dataxcash/hw_ic_k2/docs/K2-BLOCKER-REPORT-aprime-a4-scope-20260929.md

# 卡点报告 · exam A⁴（原令范围）＝ **需「刚性簇平移」，非逐件推导** — #K2-397 §三

- 授权：#K2-397 §三（按原令真实范围重出 A⁴）；本窗**零 exam 跑**（重出＋实测；链跑留待 wiring 后）
- 件：`L2/EXAM_A_QUADRUPLE_PRIME_DERIVATION_v1.json` · 方案件 `…PLAN… :: exam_a4_scope`

## 一、试过什么

1. **逐件（per-part）下移推导**（新加确定性 `direction=(0,1)`；默认 `(1,1)`＝原 SE 不改）：
   `rearrange_probe(l14, rect4=[22.95,32.95,51.5,78.0], 25 成员, direction=(0,1))` ⇒ **22/25 有步**（皆 `(0, +0.5..4.0)`）；
   **U1／D2／U2 无合法步**。
   **为何**：逐件推导把 **U1 排第 1**（焊盘面积最大），此时**其余件都还没动** ⇒ U1 下移就撞进 **J9 一带**（铜/阻焊闸拒）⇒ **"整簇一起下移"永远出不来**。
   ⇒ **逐件族不是原令的真子集对应物**（#K2-397 §二）。
2. **刚性整簇平移**（同一位移给全部 25 成员）：`dy = 1.0 ／ 2.0 ／ 4.0 mm` 三次闸探针 ⇒ **NEW violations 全为 `{}`**，
   且**连基线原有的 `courtyards_overlap×2`／`pth_inside_courtyard×1`／全部 silk 类都被清掉**（移动后 raw classes = `{}`）。

## 二、缺口在哪层 / 结论

- **不是容量、不是判据、不是闸**：是**推导模型选错**——原令是**刚性簇平移**（≈ `block.move_block`／`relocate_block_chain`），
  而此前用的是**逐件独立推导**（`rearrange_probe`）。
- **A⁴ ＝ 刚性下移**：`Δ` 取**满足闸探针的最大刚性 dy**（受原令 y 带 / H1 禁区北缘 −2mm 约束）；实测 **4mm 已经 clean**。

## 三、下一步（一次有界）

1. 注册 **A⁴ 场景**（`rect4`＝x 带向下延长 ＋ 25 成员 ＋ 刚性图）并把链指向它（现链读 `L2/EXAM_A_PRIME_SCENARIO_v1.json`）；
2. wipe-resolve **全链一次跑**；判卷 **C1–C9 ＋ 几何摘要**（**C6 重述＝「新框外 diff=0」**）；
3. 若 **C1>0** ⇒ 有界证书 ＋ 偏离通道（工程层）。

> 说明：本窗**未跑**（wiring ＋ Δ 选定为剩余有界步骤）；**请裁**是否连同 wiring 一并批（一次有界窗）。
- 板面冻结 · 四源 4/4 · 判据表一毫米不改 · 禁 WORKER。
