dataxcash/hw_ic_k2/docs/K2-BLOCKER-REPORT-aprime-triple-prime-c1-7-20260929.md

# 卡点报告 · A‴ 末跑 = **C1 7**（18→7）· 停回方案层 — #K2-393 §四

- 授权：#K2-393 §四（**恰一次** `exam A --run --chain wipe_resolve`，N=1）
- 件：判卷 `L2/EDA_ENG_EXAM_A_TRIPLE_PRIME_ATTEMPT2_VERDICT_v1.json` · 记录 `…_ATTEMPT2_RECORD_v1.json` · 方案件 `L2/A_DOUBLE_PRIME_PLACEMENT_POUR_PLAN_v1.json`

## 一、判卷（九行齐 · 仍只差 C1）

| 行 | 读数 | 判 |
|---|---|---|
| C1 | **7** 未接（R1082 为 18） | ❌ |
| C2 | **133 vs 148** · **`new_classes = []`** | ✅ |
| C3／C4／C5 | 0.0788 ≤ 0.15 ／ 2989 ≥ 2637 ／ diff 1987 | ✅ |
| C6／C7／C8 | **0 ／ 0 ／ 0** | ✅ |
| C9 | 摘要已报 | ✅ |

`gate = PASS` · `run_count = 1/1` · 终板 DRC：`solder_mask_bridge = 0` · `isolated_copper = 0`。

## 二、人类口径三问

1. **信号怎么走**：器件挪位 → 清框内铜 → 框内重接 → 复敷铜 → 孤岛处置 → 板净准入 → 判九行。
2. **挡路的是什么**：**只剩 7 处端点接不上** —— **端点拥塞/无端口网**：端点格**因邻近异网铜被剪枝**（`snap=None`），`P3V3` **无框端口**。
3. **人类方案（下一次一次做 · 确定性 · 禁搜参）**：**端口可达性预检 ＋ 拥塞处确定性开端口**（给该网在框边预留一条干净通道到最近端口）；**无端口网（P3V3）** 属另一具名子案（须在框内另导）。

## 三、具名残余清单（7 · 交监理）

| # | 网 | 端点对 |
|---|---|---|
| 1 | NRST | `C73.1(F.Cu) ↔ U1.10(F.Cu)` |
| 2 | NRST | `track[F.Cu,0.1414] ↔ U1.10(F.Cu)` |
| 3 | PERSTA# | `track[F.Cu,1.9799] ↔ track[In5.Cu,0.2500]` |
| 4 | P3V3_AUX | `track[In2.Cu,0.2000] ↔ track[In5.Cu,0.0707]` |
| 5 | I2C1_SCL | `U1.47(F.Cu) ↔ track[F.Cu,0.8485]` |
| 6 | I2C1_SDA | `track[F.Cu,1.4142] ↔ track[F.Cu,0.1414]` |
| 7 | P3V3 | `C84.1(F.Cu) ↔ blind via F.Cu-In4.Cu [P3V3]` |

（末段路由账册 blocked 5 条：`no-free-goal-node` 3 · `no-free-start-node` 2；另 2 条为同岛 pad 级余项。）

## 四、缺口在哪层（承 §16）

- **已关**（本线已证）：**布局闸**（掩膜损害）· **孤岛处置**（具名 zone 去填充＋他区重铺）· **端口目标**（框切残段当目标）。
- **本层残余**：**端点拥塞／无端口网** —— 属**新一层**（异于上面三类）⇒ 按 #K2-393 §四 **FAIL ⇒ 停 ＋ 当件回方案层**；**禁同因重跑**。
- **已立缺口**（监理 §六）：**`C38`＝端点拥塞/无端口网的确定性补法**；本报告末尾给出 **edge iv** 确定性路径（端口可达性预检 ＋ 拥塞处确定性开端口 ＋ 无端口网子案），**待授权后实施（零考跑）**。

## 五、纪律 / 边界

- 本窗**链跑合计＝1**（恰一次 `1/1`）· `aprime_witness` 冻结维持 · **无新授权而跑＝违规**。
- 板面冻结（板只在 `/tmp`，终板 sha `eafdf07573367d79`）· 四源 4/4 · 判据表一毫米不改 · 禁 WORKER。
- 产物路径机器核（承 `M-ENG-EVIDENCE-PATH`）：件在 `k2/`；派生板显式 `/tmp` ＋ sha ＋ 重导配方。
- 仍待裁：`regen.exam_a_chain` 未定义名 `rp`/`blocked`（既有 · 未修 · 越窗）。
