dataxcash/hw_ic_k2/docs/K2-R922-BLOCKER-REPORT-v3-CONSOLIDATED-AND-RULE-COMPLIANT-WITNESS.md

# R922 ·《卡点报告》v3（**合并版 · 取代 R916 v1 / R920 v2**）· 附「可能免去豁免」的关键发现

日期 2026-09-28 · ENG(ARCHER) · **本回合零执行**（无链跑 · 无重出 · 无工具/参数改动）

## 〇、停止令遵办

- **已停**：本回合**无任何「改参数／改工具／改笼位 → 重跑」**；只写本报告并提交。本回合**未使用** `/tmp/opencode/k2h4`。
- **签名机制**：检测器签名 = **运行目录**（`RUN_SIG_RE=/tmp/opencode/(...)`）⇒ 该签名族**已由 #K2-354 §三.1 裁定「误报·作废」**；本席**按误报处理、照令停手**，并**只交一份合并版报告**（不重复贴 v1/v2，避免自身空转）。

## 一、① 信号怎么走（大白话）

> 右下角两条 PCIe 下行线（`PCIE_DN4_N`／`PCIE_DN5_P`）从**板中间的转接芯片**出发：**中层(In2)竖直下钻** → **底部通道带换 In5、沿板底横着往东跑约 48mm** → **在板右缘附近掉头** → **换回 In2 竖直上爬** → **落到 J2 那排焊盘（y≈59.5／60.3）**；一对两根靠**同伴线上的蛇形**补平长度。

## 二、② 挡路的是什么（大白话 · 两层）

> **第一层（几何）**：H4 安装孔周围 3mm 禁铜，而这两条线**掉头＋上爬的立柱正站在里面**（x=139.48/138.32，须 ≤137.6537）；**正西那条带子已被「上行线」占满**——J2 一排上下行交替，**上行立柱/过孔就插在下行立柱之间的每一格**（共用一张 **0.58mm** x 栅格）。
> **第二层（规则）**：图纸里有一条**在册的 L2 裁定（2026-09-10）**：**落同一排焊盘的立柱必须按通道顺序单向单调排**（当年为**防交叉**而升为准入约束）。
> ⇒ **不是「角上做不出来」，而是「在现有规矩＋现有栅格下做不出来」。**

## 三、③ 人类方案（大白话）—— **且有第三条路（可能免去豁免）**

> **A（改规矩 · 最小）**：**仅为 H4 这个角**申请豁免该单调规矩——**理由硬**：那条规矩**只为「不许交叉」**，而这组立柱**并不交叉**（立柱互相平行且间距 ≥0.55mm；车道互相平行且间距 ≥1.449mm；着陆段各在不同 y 带）。
>
> **B（改框架 · 最贵）**：承认这条带子排不下，**回去重排逃逸架构**（让这两条线根本不走右下角）。
>
> **C（不改规矩 · 本回合新发现 —— 建议先试这条）**：
> 既然**规矩是「按排焊盘族单调」**，那就**照规矩去找解**，而不是去破规矩。已量空闲段里**确实存在一组满足单调的候选**：
> **`DN4_N=135.50 · DN5_P=134.40 · DN6_N=133.00 · DN7_P=132.20`**
> —— 落 x=135.0 那排**严格递减**（`140.64>135.50>134.40>133.00>132.20` ✓）· 两两间距 ≥0.80 ✓ · 其中三根（135.50／134.40／133.00）**已在实测空闲段内**。
> **唯一未决**：`DN7_P=132.20` 落在**本席已量范围（x≥133.0）之外**——**那截条带是否空闲尚未量**（x<133.0 未查）。
> ⇒ **若那截是空的，则无需任何豁免**：照规矩出图即可。
> **本席不预判**：这是**假设 + 一个明确的待量点**，不是结论。

## 四、卡点三问

**试过什么（七法）**：① 6×6 切铜＋C17 → 未连接 3；② 放宽 9×9 → 6；③ 间隙感知挪孔 → 落异网铜皮；④ C22 精确铜皮多边形 → 4mm 内无净位；⑤ R914 **只解下行** → 撞上行（DRC 182 vs 168 · 6 新类含 3 短）；⑥ R918 **上下行联合重解** → 角清·不撞·长度闭合，但**破在册单调规矩** ⇒ 自证 FAIL ⇒ 依 #K2-354 §三.5 闸门①停手；⑦ **本回合（纸面 · 零执行）**：改按「照规矩」求单调解 ⇒ 得候选 C（上表）。

**为何不通**：①②③④ 局部手术（下游症状）；⑤ 漏耦合约束；⑥ 解开了耦合却**破了在册规矩**（本席无权松）；⑦ **差一个未量点**（132.2 处那截条带）。

**缺口在哪层**：**不在施工层**（施工层零自由度）。缺口 = **一次「照规矩的联合重解」**——其唯一未决是 `x∈[132.2,133.0]` 那截条带的占用情况（图纸层事实，非取舍题）。

## 五、请裁（建议顺序 C → A → B）

1. **C（建议先）**：批**新的一次有界窗**，用**规则合规**的候选 C 出图（`重出 → rev-62 → 链跑一次 → 判一次`）；**该窗自己的 DRC 即回答「那截条带空不空」**——空 ⇒ 收口；不空 ⇒ 再议 A/B。**不需要任何豁免。**
2. **A**：若 C 被否，则**仅为 H4 角落豁免该在册单调规矩**（本席已备见证与「不交叉」论证）。
3. **B**：若 A/C 皆否，则回到**框架层逃逸架构重排**。

**裁定前本席不做**：不重出 · 不跑链 · 不动板。

LEGAL-ESCALATION: none
OWNER-ITEMS: 0
