dataxcash/hw_ic_k2/docs/K2-R874-BLOCKER-REPORT-RUN-DRAWING-V3.md

# K2 · 《卡点报告》v3 —— H4 角「拐点前移＋竖升重布」出图（#K2-346 方案窗 · 一次实现后的如实汇报）

> **本件零运行**（一次实现已跑，结果为 FAIL；**按自设铁律停止、不重跑、不改工具再跑**）。

## 一、本轮一次实现（`/tmp/opencode/k347` · 1 次调用）

流水：**父进程镜像 → clip 子进程（pcbnew）→ route 子进程（布线器）→ 判（kicad-cli DRC）**。
**三处失败（后两处为级联）**：

| 号 | 位置 | 症状 |
|---|---|---|
| **F1** | clip 子进程 | `AttributeError: 'SwigPyObject' object has no attribute 'x'`（`t.GetPosition()`）—— `LoadBoard`/`GetTracks`/`GetClass` 皆成功，**逐项代理却是裸 SwigPyObject** |
| F2 | route 子进程 | `'NoneType' object has no attribute 'GetFootprints'` —— clip 崩了**没写出** clipped 板 ⇒ 布线器读到空 |
| F3 | 判 | `final_drc.json` 不存在 —— F2 级联 |

## 二、为何不通（诚实分级）

- **F2/F3 是纯级联**：**对几何零信息**（不能据此说任何「几何不通」）。
- **F1 未定因**：同一环境、几分钟前别的工具能正常读同一块板；此处**在全新子进程、未做任何改板、未导入布线器**的情况下，**逐项代理已是裸对象**。本席**没有**再跑实验去分辨是 (a) 调用顺序/环境 (b) 板文件某个特性 (c) 环境回归 —— **因停止令，不做**。
  ⇒ **R870 把根因归给「同进程导入布线器」是不充分的**（本件无布线器导入也复现）。

## 三、缺口在哪层

| 层 | 判定 |
|---|---|
| 几何层 | **本轮无结论**（F1 不是几何结果） |
| 方案层 | **本轮无结论**（「拐点移到 x=137.555 ＋ 竖升重布」既未证成也未证伪） |
| **工具层（真缺口）** | **本工具链用 pcbnew 的「对象 API」改板，在该环境下脆弱**。而**在册布线器本身不用它改板** —— 它是**把改动写成文本块插进已存文件**。⇒ **改板路径应当文本化**。 |
| 纪律层 | **已遵办**：一次实现 → 停 → 报（无扫参、无同目录第二跑） |

## 四、下一步（**单一新方法** · 事后仅一次跑）

**clip 相改为「文本级」**（彻底把 pcbnew 对象 API 移出改板路径）：
1. 解析板的 s-expression **文本**，定位：被困孔块（x≥137.93 且 y≥73.93）· 其挂接的 **B.Cu 横段块** · 其挂接的 **In5 竖段块**；
2. 把横段的 `(end ...)` 改写到 **x=137.555**；**删除**孔块与竖段块（纯文本）；
3. 随后**布线器（独立进程 · 不改其文件）**桥接两个开口；**DRC 判一次**。
**为何算「不同方法族」**：把 pcbnew 对象 API 从改板路径**整个移除**（与在册布线器出铜的同一手法）。
**前置**：文本解析器先在**副本**上做单元自检（**不触仓内板**），之后**仅一次**跑。

**红线不变**：一轮一目录 · 禁扫参 · FAIL 即回修不呈 · 冻结四源 4/4 · 禁 WORKER · Gerber/下单停线。

OWNER-ITEMS: 0
