dataxcash/hw_ic_k2/docs/K2-R866-BLOCKER-REPORT-H4-CORNER-AND-PLAN.md

# K2 · 《卡点报告》＋ Plan —— H4 右下角安装孔（#K2-345 W2 的第一个真卡点）

> 停止令遵办：**连续错误 3 次**（`poly_hit` arity TypeError ×2 次同因未先诊断 · 前窗 README 声称失实 1 次）⇒ 本席**自我登记、不申辩**；**停止『改参/改工具 → 重跑』**（宪法第八章第 8 条），回 Plan，一次实现。
> 本件为**只读分析件**（零运行 · 零改板）。

## 一、《卡点报告》

### 1. 试过什么（H4 右下角落角 · 四法 ＋ 两次工具错）

| # | 手法 | 机核读数 | 结果 |
|---|---|---|---|
| A | 6×6 角禁区切铜 ＋ C17 v1 重布 | 未连接 **3** · dangling +2/+2 | ✗ |
| B | 加宽 9×9 走廊 ＋ C17 v1 | 未连接 **6**（更差） | ✗ |
| C | 间隙感知挪孔（挂接段过闸 · 0.30 判据 · 4.0 mm × 8 向） | **未连接 0** ✓ 但 间隙 +1／短路 +3／走线交叉 +1 | ✗ |
| D | 同 C ＋ 铜皮入模（bbox） | 两孔皆「4.0 mm 内无净位」 | 穷尽（近似） |
| E | 同 C ＋ **C22 精确铜皮多边形** | 两孔皆「4.0 mm 内无净位」 | **穷尽（精确）** |
| 工具错① | `k2_shift_vias_out_of_keepout_v1.py` 替换静默未命中（同族前科：README 声称失实） | 声称 vs 工件不符 | 已装 post-write 重读闸 |
| 工具错② | `poly_hit()` 调用 arity 错（`x2` 缺省） | TypeError | 已修（**未先读栈即重跑**＝本次连错主因） |

### 2. 为何不通（三法各自的死因）

- **A/B（撕铜重布族）**：两条 `PCIE_DN4_N`/`PCIE_DN5_P` 是 **~48 mm 的整段内层（In5）跑线**，其**末端换层孔**就在角上。沿禁区撕开 ⇒ 剩下的 **48 mm 残段变成孤立长桩**，而「补回」的目标（表层焊盘侧）远在禁区另一侧 ⇒ 布线器只能对**整根长桩**作业，于是乱走（未连接 3→6）。
- **C（局部挪孔族）**：**挪孔必然带动挂接段旋转**。该角的内层**满铺异网铜皮**，任一转角后的段/孔都落在铜皮上 ⇒ 间隙/短路/交叉。挂接段已过闸也救不了（铜皮当时不在模型内）。
- **D/E（把铜皮纳入模型）**：一旦要求「孔与段都不碰任何异网铜皮」，**4.0 mm 包络内无净位**（精确模型亦同）⇒ 局部推挤族**穷尽**。

### 3. 缺口在哪层

| 层 | 判定 |
|---|---|
| **几何层** | **不是无解** —— 有解（下面 Plan 给出） |
| **方案层（真缺口）** | **该角的『腾让』从未在方案层被规划**：扇出把 4 条 DN 跑线 ＋ 换层孔排到右下角时，**没有把「四角安装孔 6×6 禁区」当作布局约束**（与 M-ENG-PLACEMENT-GATE-MISSING 同族：放置源未预留机械角禁区）。所以现在是**用施工层手段去补方案层的欠账**。 |
| **工具层（次缺口）** | 现有重布族是**缺口缝合器**（gap stitcher），**不会重规划整段跑线**（whole-run re-plan）⇒ 一旦切割面把整段切坏就无力。 |
| **纪律层** | 本席**未先读栈即重跑**（工具错②）＝ 本次连错主因 ⇒ 遵办：**先诊断，再动手**。 |

## 二、Plan（人类工程师路径 · 大白话）

### ① 信号怎么走
`U6（重驱芯片）出球 → 芯片扇出（逃逸）→ 下到内层 In5 → 一根 ~48mm 的长跑线一路向右下 → 在右下角用一个换层孔上到表层（F.Cu）→ 接到连接器焊盘`。**两条线（DN4_N / DN5_P）都这样走，且**「换层孔」**恰好落在右下角。**

### ② 挡路的是什么
**右下角不是空地**：那两根长跑线的**换层孔 + 一小段表层线**就住在角上，角的内层还**满铺着别的网的铜皮**（电源/地）。所以：
- 「把孔往旁边挪一点」= 孔一动，接它的线段跟着转，**转到铜皮上就短路**；
- 「把线剪掉重接」= 剪的是**48mm 长跑线**的末端，剩下的残段太远，接不回来。

### ③ 人类方案是什么（大白话）
**不要在角上硬挪这两个孔——把「换层的位置」提前。**
就是：**在长跑线还没进角之前（离角 3~5mm 的直段上）找一个干净点，在那里换层上表层，然后只把短短一段表层线（≤10mm）接到焊盘。** 这样：
- **内层长跑线几乎不动**（只把尾端缩短几毫米，直线，不转弯）；
- **要新画的是短短一截表层线**（短 ⇒ 绕得开铜皮 ⇒ 布线器做得动）；
- 角上彻底清空 ⇒ 安装孔＋6×6 禁区可以精确落角。

**这属于「改换层位置」而不是「挪孔」**——这正是施工层做不动、必须在**方案层改一个参数（换层 x 坐标）**的那种改动。

## 三、一次实现（下一窗 · 单一有界动作 · 禁参数扫）

**实现「跑线尾部重规划（run-tail re-plan）」**（新工具 `k2_reroute_run_tail_v1.py`，**一次执行**）：

1. 对 `PCIE_DN4_N` / `PCIE_DN5_P`：在**其 In5 直段上**（x ∈ [130,136]，禁区外）扫**一个**换层孔位——判据与 C22 同（精确铜皮多边形 ＋ 0.20 净距地板 ＋ 挂接段一并过闸）；
2. 找到后：**只把该点之后的 In5 尾段剪掉**（缩短，不转弯）＋ 把旧孔删除；
3. 用迷宫布线器（精确闸）**只重布那截表层尾线**（目标 = 原焊盘），**≤10 mm**；
4. 复核：DRC ≤168 新增 0 · unconnected 0 · 该两对的对内等长重算（DN 对不属于 8 对 UP_OUT，须另表登记）。

**若步骤 1 仍无净位** ⇒ 按 #K2-343 §三，**再补第二个方法族**（来源端改层/改走廊）＋ **监理独立复算**，方可入「不可行」；**否则只用「法族穷尽」措辞、不进不可行声明**。

**红线**：一次执行；禁扫参；FAIL 即回修不呈；冻结四源 4/4；禁 WORKER；Gerber/下单停线。

OWNER-ITEMS: 0
