dataxcash/hw_ic_k2/docs/K2-R594-GROUPING-GEOMETRISATION-SPEC-G1-G3.md

# K2 · R594（#K2-230 v5 续）—— **分组几何化规则（G1–G3）**：可执行规格（下一窗一次出图）

- 依据：#K2-230（v5 成品式直出）· R593 实测（2/16 通；第 3 线被他线 **2 个过孔格**阻断 ⇒ **须几何化分组**）
- 本件：**规格件**（零构造运行）；下一窗按此**一次描线**。

## G1 尾段专属列窗（互不重叠）
为 16 线指定**互不重叠**的尾段纵取列窗：西组 `[96..113]` 内**逐线一段**（每线 ≥2 列宽，用于"下不去就分段"的阶梯）；东组墙东 `[115..137]` 内**逐线一段**（F3 机核 16 列可用）⇒ **跨线列窗不相交**（构造式，非试参）。

## G2 过孔列集（构造式分离 ≥ VIA_SEP）
每线的过孔**只允许落在其 G1 列窗内**；**相邻线的列窗间距 ≥ 3 格**（3×0.435 ≈ 1.30mm ≥ `VIA_SEP` 0.7mm）⇒ **跨线过孔自动满足净距**（构造式，非试参）。
`col60` 注册换层点仍按在册槽位（其行 `H` 逐线不同 ⇒ 同行不冲突）。

## G3 落 B 端子腿（专属近端子段）
每线的 **B 端子腿**只在其 **G1 列窗**内接近（禁穿越他线列窗）⇒ 消除 R593 的"他线过孔格阻断 B 腿"。

## 验收（下一窗）
`按 G1–G3 出"专属通道表" → 一次描线 → exact_gate（真净距）/gate_vias/端点/≤2 对孔 → 入库报 hash ＋ buildability ＋ 每线"抄自成品何处"对照列`。

## 边界
冻结四源 4/4 MATCH · 在册件/判据/生成器/SPEC/原理图一字未动 · 未派 WORKER · 两仓已提交 · 树净；**P4 未归零 ⇒ 不导 Gerber/不进 P5/不碰下单**。 OWNER-ITEMS: 0

—— ENG（ARCHER）· 承 #K2-230
