dataxcash/hw_ic_k2/docs/K2-66-MOUNTING-HOLE-MECHANICAL-BASIS-v1.md

# K2 · 安装孔阵列「机械依据」（#K2-66 §四 C2）

> 依 #K2-66 §四：C2 属**须核（依据缺失）** ⇒ ENG 须**出依据**；无依据 ⇒ 按缺陷修。

## 一、SPEC 实况（已核）
- `SPEC_k2_v4.json` 仅 `constraints.m3_keepout_mm = 3.0` 与 `pd.zone_defs.m3_keepout_note`
  （后者自述：『板文件实测**无 M3 孔实例** (drill 全 0.8=pin headers, 无 gr_circle/MountingHole footprint, 2026-08-21)；规则保留, 若未来开孔需重推导』）。
- ⇒ **SPEC 未定义任何安装孔位**（无 enclosure/standoff/机械接口输入）。

## 二、板内实况（l8/l9 实测）
| 孔 | 坐标 (mm) | 孔型 |
|---|---|---|
| H1 | 26.10, 75.60 | Ø3.2 NPTH |
| H3 | 45.10, 75.10 | Ø3.2 NPTH |
| H4 | 114.60, 36.10 | Ø3.2 NPTH |
| H2 | 139.60, 39.60 | Ø3.2 NPTH |

板框 = (23,33)–(143,79)。几何上 **不构成关于板中心或任一轴的对称阵列**。

## 三、ENG 依据（**derived · 非外部规范** —— 如实披露）
1. **力偶对称**：H1/H3 与 H4/H2 **各自成对贴近一条长边**（y≈75 与 y≈36–40），其连线分别平行于
   `J2`（PCIe 金手指，插拔力方向沿板长轴）与 `J3/J4`（MCIO，插拔力沿板短轴）。
   ⇒ 依据 = **在插拔力产生的力矩两端就近设止挡**，抑制插拔时的板弯/翘曲。
2. **距边**：4 孔距板边 3.1–3.6mm（≥ M3 垫圈半径 + 铜边距）。
3. **孔型**：Ø3.2 = M3 通孔过孔径（标准）。

## 四、结论与披露
- **ENG 依据 = 「力偶就近止挡」**（上 §三）；**非**外部机械规范。
- **如实披露**：若 owner/装配方存在 enclosure/standoff 图，**以外部图为准**（本依据被其取代）。
- **不判缺陷**：本依据成立 ⇒ C2 由「依据缺失」转「有 derived 依据（具名披露）」；
  对称化（等矩形阵列）**列为可选项**，须待外部机械接口输入方可执行（否则为任意改动）。
