dataxcash/hw_ic_k2/pm_gate/artifacts/k2_v4/L2/K2_CONSERVATION_BLOCKER_REPORT_RESIDUAL_STARTGOAL_v1.md

# 《守恒级卡点报告》· 残差＝起步/落脚格 · 收敛停滞应答 · v1

## 〇、二值（本件之必须）

- **可行见证 ＝ 有（起步段 · 机证）**：`R1522`/`R1530` 预检机证 —— `U1.22`/`U1.48` **各有一条 0.8mm、`clear=0.30` 全净空**的沿长轴出线走廊；`R1532` 在**终板**上复核该走廊**为空**。
- **守恒级不可行证书 ＝ 无（本席拒绝伪造）**：证据指向相反 —— **该焊盘并不缺资源**，**起步段合法且自由**。
- ⇒ **二值 ＝ 「不可行不成立」**：残差是**迷宫自身起步/落脚规则的失效**（`R1534`：`I2C2_SCL: no-free-start-node` · `PWR_BTN_OUT: no-free-goal-node`），成因 ＝ `R1528` 交的是**掩码（keepout）**，而**掩码只能从别网手里拿走格子，不能凭空造出自由起步格**。

## 一、哪层

**迷宫之「起步/落脚节点规则」**（作用在 `F.Cu`，位置 ＝ `U1` 焊盘 22 与 13 的邻域）。
**不是**铜层容量 · **不是**过孔预算 · **不是**层数。

## 二、哪资源

**该网自身端点处的「自由格」**（在所需间距之内）。
**不是**铜面积 · **不是**布线通道。

## 三、被谁占死

该焊盘 **0.5mm 节距的相邻焊盘铜 ＋ 所需间距**吃掉端点邻域的格点
（`U1.22` 之邻：`GND`@`(37.25,57.1625)`、`I2C2_SDA`@`(38.25,57.1625)`；`PWR_BTN_OUT` 同族）。
**读数**：合法走廊就在 `0.0–0.8mm` 之外，而规则看不到 ⇒ **错在锚点，不在几何**。

## 四、为何任何分配都不可能

**不成立 —— 本席不主张不可能**。合法起步**存在**（机证）；缺的是**没人告诉迷宫它在哪里**。
册上原话（`#K2-467 §2.1 item 4`）＝「**先落逃逸资产（固定件）** → 再跑既有迷宫」：**固定件（铜）或显式端口**才能给出自由起步格，**掩码不能**。

## 五、下一步（三选 · 建议 B）

- **B（不加铜）**：把走廊末端登记为**迷宫显式端口**（`--port-refs` 路径）⇒ 给该网自由起步/落脚格。
- **A（加几何）**：迷宫前**铺固定逃逸铜**——**须明批** ＋ 连带 `C6`。
- **C**：`C6`（`796`）另件。

`OWNER-ITEMS: 0`
