dataxcash/hw_ic_k2/pm_gate/artifacts/k2_v4/L2/K2_BLOCKER_REPORT_RESIDUAL5_ADDENDUM_S_v1.md

# 《卡点报告》· 附页 S（连续错误停止令 · 连错 2 次）

> 交监理。**服从停止令**（**已即时停手** · 本轮零动作）。最小篇幅。

## 0. 认领（监理计数**成立**）
- **两次连续错误 ＝ 真实**：均为**本条回执生成脚本自身**的失败 —— 先 `IndentationError`、后 `SyntaxError`，**同一处笔误**（长字符串用「相邻字面量续行」写在**调用内部**，续行不被接受）。
- **归类**：**我的写件工具问题**，**非引擎问题** —— 两次都**没碰 k2 任何文件**、**没写板**、**没跑**；第三次重写成功，且**提交前已被 `json.load` 校验**（这正是捕获方式）。
- **影响**：**对产物零影响**，代价 ＝ 两次空调用。
- **同窗已修的规矩**：长串**改为命名变量＋引用拼装**（不再内联续行）；**凡产出件一律先 `json.load` 校验再提交**。

## 1. 试过什么（本窗实质）
**收敛令要的二值已出（只读）**：以**冻结迷宫当测量仪**（链内参数 ＋ **验收口径 `cv._req≥0.20`**）⇒ **两条残余各有 `mr.solve_edge` 产出、经 `seg_exact`/`via_exact` 放行闸验收的可行见证**（`I2C2_SCL`：F.Cu→In5.Cu→F.Cu ＋ 2 个 F↔In5 孔；`I2C1_SDA`：1 个 F↔B 孔 ＋ 短 B.Cu 段）＋ **手段内不可行证书**（同几何、同参数，域＝**旧整网硬通道带** ⇒ `no-free-goal-node`；域＝整框 ⇒ `OK`）。
**自纠**：首轮探针漏了 `--floor 0.20` ⇒ 首轮「见证」不合格 ⇒ 补齐口径后重探。

## 2. 为何不通
**`C1=2` 未变**，原因已**锁到单一残留**：`R1424` 只软化了**引导半边**，**`--channels` 的硬半边仍在当域** —— 而它就是**饿死 `I2C2_SCL` 的那道墙**；第二条残余**根本不是引擎边**（只在终板出现，由链内**图纸/缝合阶段**造出而未接合）。

## 3. 缺口在哪层
**(a) 引擎手段层**（**最后一个硬域**）· **(b) 图纸层**（`I2C1_SDA` 跨层接点）。**非资源问题**：位置**不被铜、不被面积**占死（见证在验收口径下过闸；框内 ~50× 余量）——**是被「工具自己的硬带」占死**。

## 4. Plan 复述（大白话）
- **① 信号怎么走**：框内每网从焊盘接回 ∂R 端口；**电源走内层平面、总线成组、控制短直连**。
- **② 挡路的是什么**：**没有物理阻挡**。`I2C2_SCL` 那根，工具仍被要求「只许在 **0.96mm 宽**的带里动」——**带里根本没有合法落脚点**，它只好放弃；**围栏一撤，同一根立刻布通**（见证已在手）。`I2C1_SDA` 那处**不是引擎的线**：两个短桩在**不同层**上，**图纸从来没接**。
- **③ 人类方案**：**把最后一道围栏也撤掉**（把分配好的道**当建议**，不再当围栏），然后**考一次**；另一处**在图纸上补那一个跨层接点**（待层归属裁）。

## 5. 「一次实现」清单
1. **本窗已实现** ＝ `R1440`（二值：两处**验收口径下**的可行见证 ＋ 手段内不可行证书 ＋ 附页 R）。
2. **待批（两件）**：(A) **软化最后一个硬域**（旧整网 `--channels` 改作引导或去掉）**＋ 是否附一次新 `N=1`**；(B) **`I2C1_SDA` 之 §16.2 层归属裁** ＋（若准）**一次图纸侧补件**（另出 §16.3 全套）。

LEGAL-ESCALATION: none
OWNER-ITEMS: 0
