dataxcash/hw_ic_k2/pm_gate/artifacts/k2_v4/L2/K2_BLOCKER_REPORT_RESIDUAL5_ADDENDUM_R_v1.md

# 《守恒级卡点报告》· 附页 R（收敛停滞停止令 · **二值已出：可行见证**）

> 交监理。**服从停止令**（本轮仅出件，未改工具/未跑判卷）。**结论：不存在守恒级不可行** —— 两条残余**各有冻结门验证过的具体构造**。

## 0. 二值（本件要出的那个）
**可行见证（witness）**，非不可行证书 ⇒ 详见 `K2_CONSERVATION_BINARY_RESIDUALS_v1.json`。
**自纠（先记）**：首轮探针漏了链内验收口径 `--floor 0.20`（直连迷宫本体＝用登记净空 0.10/0.175）⇒ 首轮「见证」**不合格**；补齐口径后重探，**下列数字全部在 `cv._req≥0.20` 下测得**。

## 1. 可行见证（两条 · 均由 `mr.solve_edge` 产出 ⇒ **`seg_exact`/`via_exact` 放行闸已判过**）
| 残余 | 端点 | 域 | 构造 | 过孔 |
|---|---|---|---|---|
| **`I2C2_SCL`** | ∂R 端口桩 `(51.5,56.6)` ↔ `U1` 焊盘 22 `(37.75,57.1625)` | **整框**（22.95,32.95,51.5,78.0） | F.Cu `(51.45,56.5)→(48.25,56.5)→(48.05,56.7)` ⇒ In5.Cu `→(38.25,56.7)→(37.75,56.2)` ⇒ F.Cu `→(37.75,57.2)` | **2 个 F.Cu↔In5**（`(48.05,56.7)`／`(37.75,56.2)`） |
| **`I2C1_SDA`** | F.Cu 桩 `(51.5,67.455)` ↔ B.Cu 桩 `(49.15,62.505)` | **整框 或 其旧通道带皆可** | F.Cu `(51.45,67.305)→(50.95,66.805)` ⇒ B.Cu 斜梯 `→(49.15,62.505)` | **1 个 F.Cu↔B.Cu**（`(50.95,66.805)`） |

## 2. 手段内不可行证书（**限定**：现行手段）
**`I2C2_SCL` 在「旧**整网硬通道**当域」下不可行**：同一几何、同一参数（`margin 3.0`／`step 0.10`／`floor 0.20`）⇒ 域＝该网旧通道带 `(37.55,56.4,51.5,57.3625)`（**仅 0.96mm 高**）⇒ **`FAIL · no-free-goal-node`**；域＝整框 ⇒ **`OK`**。
⇒ **隔离结论**：**只换域就翻结论**；软引导非因（`penalty 0` 与 `3` 同）。**`R1424` 已软化「引导半边」，但 `--channels` 的「硬半边」仍在当域用** ⇒ 这是 `R1420` 病灶的**最后残余**。

## 3. 四问（收敛令要求的格式）
- **哪层**：**(a) 引擎手段层** —— 最后的**硬域**（`--channels` 旧整网通道带，`I2C2_SCL` 处仅 `0.96mm`）**仍被当域**；**(b) 图纸层** —— `I2C1_SDA` 的配对**根本不是引擎边**（只出现在终板）⇒ 系链内**图纸/缝合阶段**造出而未接合。
- **哪资源**：**(a)** ∂R 端口 `(51.5,56.6)` ↔ `U1.22` 的 **~14mm 局部走线**；**(b)** F.Cu 桩 ↔ B.Cu 桩之间的**一个跨层接点**（1 孔 ＋ 短 B.Cu 段）。
- **被谁占死**：**(a) 不被铜、也不被面积占死**（见证在 `floor 0.20` 下过闸；框内余量 ~50×）——**是被「工具自己的硬带」占死**：资源由**手段本身**占用；**(b) 被冻结图纸占死**（该接点从未画）。
- **为何任何分配都不可能**（**限域**，非全局）：**只要硬带当域**，几何上就没有合法**终点格**（`no-free-goal-node` · 确定性 · 同参可复现）⇒ 该域内**任何分配都不可能**；**放松域则同一几何有解**（见证）⇒ **不可能性是「手段」的属性，不是「卡」的属性**。

## 4. 不存在守恒级不可行的反证
- 站立的守恒计数：**容量 12862 ≫ 需求 257.3 线·毫米（~50×）**（`R1394`／#K2-450 §2.3）。
- **两处见证**在**验收口径**下真实过闸。
⇒ **本板两条残余都不是「无资源」，而是「手段/图纸」未到。**

## 5. 下一步（**待批 · 本席未启动**）
- **A（引擎手段层 · §11）**：**把最后一个硬域也软化** —— `--channels` 旧整网域**改为「也作引导」或干脆去掉**（`R1424` 教训施于最后半边）。见证表明 `I2C2_SCL` 即可布通；**对其余 17 网的影响须由授权跑测**。
- **B（图纸层 · 需监理 §16.2 层归属裁）**：`I2C1_SDA` 补**一个跨层接点**（几何已在见证中给出）⇒ 按 §16.3 出完整件，**不改冻结 SPEC 原件**。

LEGAL-ESCALATION: none
OWNER-ITEMS: 0
