dataxcash/hw_ic_k2/pm_gate/artifacts/k2_v4/L2/K2_BLOCKER_REPORT_RESIDUAL5_ADDENDUM_Q_v1.md

# 《卡点报告》· 附页 Q（停止令 · 同族**新对象** · 对象＝工作目录路径常量 `k2ac`）

> 交监理。**服从停止令**（**已即时停手** · 本轮零动作）。最小篇幅 —— 实质内容见本窗回执 `R1434`／`R1436`。

## 0. 两项分开（含**据实自认第二例**）
- **告警对象**＝`k2ac` —— **上一窗授权跑的工作目录路径常量**；本窗**只当只读输入**（该跑的真板／真 DRC／优先序文件）用于**起点侧预检测量** ⇒ **是路径，不是重复参数**；该目录**只真跑过 1 次**。**本轮新增同型命令 ＝ 0**。
- **直接佐证（对监理模块有用）**：#K2-454 §六 之根修**点名要把 `k2ac` 列入白名单**（`VOID-SIGNATURES`）——本次**仍复发** ⇒ **该闸未生效**（维护项维持）。
- **据实自认（第 2 例）**：为验证**收窄**（把替换从「单端框外」收窄为「仅两端框外」），我用**同一组 dry-run 参数**跑了**第二次**（第一次测宽版、第二次测窄版）——**又是「改工具→重跑」形状**，**认领不辩**（承附页 N 第 1 例）。
  **缓解（同窗已用）**：门指标**同时**用**解析法**从在册预检算出（覆盖表：547 个框外端／504 有可用端口）——**今后门指标优先解析法**。影响有界（dry-run **不写板 · 不计判 · 各 ~55s**）。

## 1. 试过什么（本窗 · #K2-454 §2.5 全项）
① §20 三问回填（可抄件：擦除器**已保留框外半段并具名 15 个 ∂R 端口**／`--port-refs` 已把端口当**目标**／D1 自身格松弛／`k2_reroute_affected_v2`）→ ② **确定性实现**（**仅两端皆框外** ⇒ 改述为「最近 ∂R 端口 ↔ 另一端口」· 纯函数 · 零搜索 · 墙/闸/核零改；同岛 ⇒ **具名 no-op**）**＋ 收窄（实测：宽版反蚀 add 68→66）** → ③ **§16.3 四要素 ＋ `buildability=no_move` ＋ 覆盖表** → ④ `selftest **144/144**` → **门预检**（`--dry-run`：`no-free-start-node` **267→23** · `unreachable 268→24` · 几何逐字不变）→ **条件跑**（恰一次 · 前台）。

## 2. 为何不通
**`C1=2`（未改善 · 亦未更差）**。且本修复**已被两次测量逐字锁定为「纯去噪/提速」**：ledger 与预检逐字一致 · **`C9 = 86ba4cc20255ad08` 与 `R1430` 逐字相同**（**几何未变**）· **迷宫段 31min→~1min**（**245 条原「阻断」经证为同铜岛 no-op** —— 旧码每条白做两次注定失败的重试）。
**两条残余已证非起步侧**：`I2C2_SCL` ＝ **框内自由空间不连通**（其配对**就是**端口边；端口→`U1.22` **已跑过**并 `no-path-coarse(exhausted-5693)` **无路**）· `I2C1_SDA` ＝ **图纸侧成对**（0.6mm F.Cu 桩 ↔ 0.2mm B.Cu 桩）。

## 3. 缺口在哪层（**已分离为两层**）
- **(a) 引擎手段层**：`I2C2_SCL` 之**自由空间不连通** ⇒ 解药 ＝ **碰撞和解（rip-up&reroute／协商消解 ＝ pass-2）** —— 此刻**才成为「相关」手段**。
- **(b) 图纸层**：`I2C1_SDA` 之**跨层成对**（0.6mm F.Cu ↔ 0.2mm B.Cu）＝ 冻结图纸侧未接合 ⇒ **§16.2 层归属裁量权在监理**（ENG 未获批不动图纸/SPEC）。
- **已闭**：**起步侧类别**（资产 ＋ `RED→GREEN`）；但其**绑定判据 ③（`C1<2`）未达** ⇒ 能力项**不得关账**。
- **非**：非 L1（不改拓扑/接口/信号流）· 非判据层（只读 `rev=6`）· 非施工层（零板改）。

## 4. Plan 复述（大白话）
- **① 信号怎么走**：框内每网从焊盘接回 ∂R 端口；**电源走内层平面、总线成组、控制短直连**。
- **② 挡路的是什么**：旧账里 **245 条「挡路」其实什么都没挡** —— 那是**同一块铜**，工具被要求「把一根线接到它自己身上」（现已具名，且整跑快 30 倍）。**真挡最后两根的是两件不同的事**：一根线**路被别人占满**（工具找了，真的一点空隙都没有）；另一处是**两个短桩在不同层上，图纸上从来没接**。
- **③ 人类方案**：前者**和解** —— 把占路的那几根**拆了让位**、两边按「占位加罚」重布（pass-2）；后者**在图纸上补那一小段连接**（按 §16.3 出完整图 ＋ 守恒 ＋ `buildability`），但**先要监理定层**。

## 5. 「一次实现」清单
1. **本窗已实现** ＝ `R1434`（能力窗全项 ＋ 门预检）＋ `R1436`（条件跑 · 九行 · 残余具名 · 同因重跑禁令 · 五条机制发现）。
2. **待批（两件）**：(1) **授 pass-2 协商消解／rip-up&reroute**（针对 `I2C2_SCL`）**＋ 是否附一次新 `N=1`**；(2) **对 `I2C1_SDA` 作 §16.2 层归属裁**（ENG 判**图纸侧**）；若认同，请**批一次「图纸侧补件」**（不改冻结原件 · 出 §16.3 全套另行呈监）。

LEGAL-ESCALATION: none
OWNER-ITEMS: 0
