dataxcash/hw_ic_k2/pm_gate/artifacts/k2_v4/L2/K2_BLOCKER_REPORT_RESIDUAL5_ADDENDUM_P_v1.md

# 《卡点报告》· 附页 P（停止令 · **同对象复燃** · 对象＝路径常量 `k2ab`）

> 交监理。**服从停止令**（**已即时停手** · 本轮零动作）。最小篇幅 —— 实质内容见**附页 N／O** 与本窗**回执 `R1430`**。

## 0. 两项分开（含**据实自陈**）
- **告警对象**＝`k2ab`（**早前授权跑的工作目录路径常量**）—— **与附页 N／O 同一对象**；已由 **#K2-452 §五／#K2-453 §2.3 判 VOID**（路径常量，非重复参数、非重复执行）。
- **本轮新增同型命令 ＝ 0**：本轮**没有任何命令**含该 token（本窗跑用**新**工作目录、只读自身输入）；计数系检测器**重扫同一会话历史**。承前 `k2v`/`k2t`/`k2r` ⇒ `M-SUP-SAME-SIGNATURE-REFIRE-GATE` **仍未接线**。
- **据实自陈**：本窗**确有 1 次路由/考跑** —— 即 **#K2-453 §2.4 授权的唯一一次 `N=1`**（事前申报 · 前台 · `run 1/1` · 配额已耗 · 账目在 `/tmp`）⇒ **属授权跑，非违规**；**零改参重跑 · 零同因重跑**。

## 1. 试过什么（本窗 · 授权跑）
按 #K2-453 **先测已落手段（软引导）**、**不先建 pass-2**：跑授权 `N=1`。链内机证 **`n_guide=48` · `guide_source="joint-per-corridor"`** ⇒ 逐走廊分配**首次以「偏好/代价」身份真跑**（`R1420` 是**硬域**身份 ⇒ 饿死）；**闸未触发**；九行齐。

## 2. 为何不通
**`C1=2`（未改善 · 亦未更差）** ⇒ 残余两条：`I2C2_SCL`（9.3mm F.Cu ↔ `U1` 焊盘 22）· `I2C1_SDA`（0.6mm F.Cu ↔ 0.2mm B.Cu）。**机制已具名**：268 条阻断中 **267 条 `no-free-start-node`**，带内预检显示这些端点 **`reachable_port false`**（连自己网的端口都够不到）⇒ **迷宫在 `maxr=4` 内找不到自由起点格**。且**引导确已生效**（`segs 1152→636` · `vias 57→60` · `len 552.93→576.77mm`）而 **`C1` 不动** ⇒ **「分配/排序」半边不是约束**。

## 3. 缺口在哪层
**引擎手段层 · 具体为「端点起点可达性」**：端点明明压在本网铜上，却拿不到合法**起点格**（D1「端点自身格」松弛 **281 次失败中仅开火 23 次**）⇒ 在册 **`M-ENG-PORT-REACHABILITY-DRAWING`**。**非**图纸层（98 件全锚 · `padless=0`）· **非**施工层（零板改）· **非** L1 · **非**判据层。
**另（监理附请已答）**：`#K2-452` item 3 修复**整跑级 C1 中性已实测**（`exception:KeyError 244→0` 且 **`added 68→68`**）⇒ GND/pour 侧中性**由「未测」变「已测」**。

## 4. Plan 复述（大白话）
- **① 信号怎么走**：框内每网从焊盘接回 ∂R 端口；**电源走内层平面、总线成组、控制短直连**。
- **② 挡路的是什么**：**不是空间、不是图纸、也已证实不是「谁先谁后」** —— 是**最后两条线的端点「根本起不了步」**：工具在它自己的铜上找不到一个能出发的格子，它自己网的端口也帮不上。
- **③ 人类方案**：**让起步成立** —— 端点压在本网铜上就**允许从那里出发**（既有 D1 松弛方向对但只开火 23/281），并把**本网端口**真正用作目标。**大白话：最后两根线不是「不会排」的问题，是「工具出不了发车口」。**

## 5. 「一次实现」清单
1. **本窗已实现** ＝ `R1430`（授权跑 ＋ 九行 ＋ 判卷/记录件 ＋ **同因重跑禁令** ＋ GND 中性实测读数 · `selftest 143/143`）。
2. **待批** ＝ **下一手段指定为「端点起点可达性」**（修/扩既有 D1 松弛 ＋ 端口目标，使 267 条 `no-free-start-node` 能合法起步）**＋ 是否附一次新 `N=1`**（本窗配额已耗）；**并请裁** `M-ENG-POUR-EDGE-KEYERROR` **可否关账**（资产＋回归＋C1 中性已实测）。

LEGAL-ESCALATION: none
OWNER-ITEMS: 0
