dataxcash/hw_ic_k2/pm_gate/artifacts/k2_v4/L2/K2_BLOCKER_REPORT_RESIDUAL5_ADDENDUM_M_v1.md

# 《卡点报告》· 附页 M（停止令 · 对象＝工作目录**路径常量** `k2ab` · 闩锁族）

> 交监理。**服从停止令**（**已即时停手**）。最小篇幅。

## 0. 两项分开
- **告警对象**＝`k2ab` —— **本窗唯一授权跑的工作目录路径常量**；它出现在①提交链里内嵌的启动命令、②存活探针（`ls/pgrep/ps`）、③读账（`s2_ledger`/`s4_drc`）中，**均为路径字符串**，**非重复参数、非重复执行**。该工作目录**只被跑过 1 次**。
- **本族承前多度判 VOID**（`k2v`/`k2t`/`k2r`）⇒ `M-SUP-SAME-SIGNATURE-REFIRE-GATE` **仍未接线** ⇒ 闩锁复燃（维护项维持）。
- **本席认领**：**0 改参重试 · 0 重跑 · 恰 1 次授权考跑**；本窗唯一工具改动 ＝ `R1418`（**已授权**的 `(ii)` 落地）。**停止令到前工作已收官**（跑于 08:52 闭合、`R1420` 已交），此后**只做落件与提交**。

## 1. 试过什么（#K2-450 换手段全程）
`R1396` 联合分配内核 → `R1400` 接线 → `R1402` 首跑（**静默回退 ⇒ 无效**）→ `R1404` 诊断（整网包带 `239.92mm ≫` 走廊 `45.05mm`）→ `R1406` 响亮 `source` 闸 → `R1408`/`R1410` 走廊粒度（RED→GREEN）→ `R1412` 发射器 → `R1414`/`R1416` 只读钉改点 → `R1418` 采纳 `(ii)` 落地 ⇒ **授权 `N=1` 真执行**：链内 `channels_computed **source=joint · n_nets=48**`。

## 2. 为何不通（决定性负结果 · 机制级）
`C1 **2 → 47**`（`added 68 → 20` · `blocked 268 → 316` · 同 336 候选边）。机制：**通道槽 ＝ 0.40mm 高横向干线带**，被当作 `mr.WALL_RECT` —— 而它是**求解域（必须装下该边两端）**，非「偏好车道」（`R1416` 只读钉死）⇒ **0.40mm 高的域装不下 y 向几毫米外的焊盘 ⇒ 构造性无解**（`no-path-coarse(exhausted-1)=47` ＋ `no-free-start-node=22`，基线各仅 1）。
⇒ 「用干线第 k 道」**表达不出来**：迷宫唯一抓手是**域矩形**，**硬域只会禁止，不会偏好**。

## 3. 缺口在哪层
**引擎手段层**（路由器的**分配/排序**载体）。**非**图纸层（98 件全锚 · `padless=0` · DRC 零短路/交叉/净空）· **非**施工层 · **非** L1（守恒证明未被动摇）· **非**判据层（只读 `rev=6`）。
**另点名（非本手段所致 · 三跑恒为 244）**：`exception:KeyError=244`（GND 241）—— `tools/k2_p4_mroute_v1.py:722`，GND 为铺铜网被 `_ctx_no_pour` 滤掉 ⇒ **GND/pour 边整类饿死**；**另**：加宽阶梯在冻结 `margin=0.0` 下退化为 `(0,0,0)`（`R1252`）。

## 4. Plan 复述（大白话）
- **① 信号怎么走**：框内每网从焊盘接回 ∂R 端口；**电源走内层平面**、**总线成组**、**控制短直连**（98 件图纸已如此）。
- **② 挡路的是什么**：**不是空间、不是图纸**，是**路由器「谁先谁后」的分配方式**（逐边顺序服务 ⇒ 最后者饿死）。一切「预先分配答案」都只能借**求解域**表达，**硬域只会禁止**。
- **③ 人类方案**：**先全部画出来，再只拆冲突的那几根**（拆线重布 ＋ 占用惩罚 · 有界迭代）。

## 5. 「一次实现」清单（**待批 · 本窗不启动**）
1. **手段换法（目标不变 · `C1→0`）**：包装层**协商式拥塞消解 / rip-up & reroute**（`M-ENG-ROUTER-REROUTE` ＋ §2.6 教令族）。
2. **随手段同落 fail-closed 闸**：链**拒绝**再把**多槽（逐走廊）**通道喂 `WALL_RECT`（饿死已证）＋ **RED→GREEN 回归**（§22.3）。
3. 可选：修阶梯退化。4. 另案：GND/pour 边 `244×KeyError`。

LEGAL-ESCALATION: none
OWNER-ITEMS: 0
