dataxcash/hw_ic_k2/pm_gate/artifacts/k2_v4/L2/K2_BLOCKER_REPORT_RESIDUAL5_ADDENDUM_L_v1.md

# 《卡点报告》· 附页 L（#K2-451 授权窗回执 · 换手段首份真证据 ＝ 决定性负结果）

> 交监理。**服从** #K2-451 §2.5 硬门（`C1≥2` ⇒ 停 ＋ 具名 ＋ 禁同因重跑 ＋ 携新机制证据请裁）。最小篇幅。
> 本件**不是**停止令回执：若本轮另有 `k2v` 闩锁族告警 ⇒ 承前多度 **VOID**（本窗命令只用工作目录 `k2ab`，非 `k2v`）。

## 0. 两项分开
- **本窗合规**：**零改参重试 · 零自跑**；恰一次**授权** `N=1`（**前台** · `K2_NO_YIELD=1` · `run 1/1`）；板未动（`l14/rev-61` · `fb07d25ac426ff84`）；四源 4/4；`criteria/` 只读 `rev=6`。
- **本窗唯一工具改动** ＝ `R1418`（**#K2-451 §2.4 采纳的 `(ii)`** 落地：迷宫端接受重复网 ＋ 逐（网·走廊）一次调用），**仅此一件**。

## 1. 试过什么（#K2-450 换手段全程 · 据实）
`R1396` 联合分配内核（`sequential` 必饿死／`joint` 不饿死 · RED→GREEN）→ `R1400` 接线 → `R1402` 首跑（**静默回退 ⇒ 无效**）→ `R1404` 诊断（整网包带 `239.92mm ≫` 走廊 `45.05mm` ⇒ 构造性不可行 ＋ 自曝静默回退）→ `R1406` 响亮 `source` 闸 → `R1408`/`R1410` 走廊粒度（8mm 廊 · 0.40 节距 · RED→GREEN）→ `R1412` 逐走廊发射器 → `R1414` 钉改点 → `R1416` **只读更正自家**（通道＝**求解域**，非逐点检查）→ `R1418` **采纳 `(ii)` 落地**。
⇒ 授权 `N=1` 这次**真执行**：链内机证 `channels_computed **source=joint** · n_nets=48`（**非**自报 · 在 `route.chain[7]`）。

## 2. 为何不通（决定性负结果 · 机制级）
| 量 | 基线 `R1392`（18 网 · 整网带） | **本跑**（48 槽 · 逐走廊） |
|---|---|---|
| 候选边 | 336 | 336 |
| **added** | **68** | **20** |
| blocked | 268 | 316 |
| **`C1`** | **2** | **47** |
| 主要死因 | `exception:KeyError` 244 ＋ `no-free-start-node` 23 | 同上 **244** ＋ **`no-path-coarse(exhausted-1)` 47** ＋ `no-free-start-node` 22 |

**机制**：每个「通道槽」是 **0.40mm 高的横向干线带**（例 `GND:26.67,33.35,51.50,33.75` ⇒ `y∈[33.35,33.75]`），而它被当作 `mr.WALL_RECT` 喂进迷宫 —— **`WALL_RECT` 是求解域（必须同时装下该边两个端点的区域），不是「偏好车道」**（`R1416` 已只读钉死）。0.40mm 高的域**装不下 y 向几毫米外的焊盘** ⇒ **构造性无解**，与实测死因完全一致。
⇒ 「用干线第 k 道」这个**意图**，用迷宫唯一暴露的抓手（**域矩形**）**表达不出来**：硬域只会**禁止**，不会**偏好**。
**附带点名（非本手段所致 · 三次跑完全不变）**：`exception:KeyError=244`（其中 GND 241）—— `tools/k2_p4_mroute_v1.py:722`，边端点 uuid 既不在 `ctx.pads/vias/tracks` 内（GND 是**铺铜网**，被 `_ctx_no_pour` 滤掉）⇒ **GND/pour 边整类饿死**之既有引擎缺陷，另案。
**另**：加宽阶梯在本窗**退化** —— `_CH_MARGIN` 冻为 `0.0`（`R1252`）⇒ 阶梯 `(_m,2_m,4_m)` ＝ `(0,0,0)`，**三次同参尝试**（带宽从未加宽，且求解开销三倍 ⇒ 迷宫段 33 分钟）。

## 3. 缺口在哪层
**引擎手段层**（路由器的**分配/排序**载体：谁走哪、按什么次序）。
**非**图纸层（98 件全锚 · `padless=0` · 拼接场 DRC 零短路/交叉/净空）· **非**施工层 · **非** L1（无需改拓扑/接口/球映射 —— #K2-450 §2.3 守恒证明未被动摇：容量 ≫ 需求 ~50×）· **非**判据层（只读 `rev=6`）。

## 4. Plan 复述（大白话）
- **① 信号怎么走**：框内 MCU 簇；**电源走内层平面**、**总线成组**、**控制短直连** —— 98 件图纸已经这么画了。
- **② 挡路的是什么**：**不是空间、不是图纸**；是**路由器「谁先谁后」的分配方式** —— 逐边独立、顺序服务 ⇒ **最后被服务的饿死**（残余轮转）。而所有「预先分配答案」的尝试（整网带／y 分层／逐走廊槽）都只能借**求解域**这个抓手表达，**硬域只会禁止、不会偏好** ⇒ 本次把 2 条残余变成 **47** 条。
- **③ 人类方案**：**先全部画出来，再只拆冲突的那几根** —— 第一遍**不加约束**跑通（已知能到 `added=68`），第二遍**只对冲突边**做**拆线重布 ＋ 占用惩罚**，有界迭代至无冲突（**协商式拥塞消解 / rip-up & reroute**）。参照在册成品范式（成组扇出／共享廊道）。

## 5. 「一次实现」清单（**待批 · 本窗不启动**）
1. **手段换法（目标不变 · `C1→0`）**：包装层**协商式拥塞消解**（pass1 无约束 → pass2 拆冲突边重布 ＋ 拥塞代价 → 有界迭代）；即已登记 `M-ENG-ROUTER-REROUTE` ＋ §2.6 教令族。
2. **随手段同落 fail-closed 闸**：链**拒绝**再把**多槽（逐走廊）**通道喂 `WALL_RECT`（饿死已证 · 不得静默复喂）＋ **RED→GREEN 同类回归**（§22.3）。
3. **可选同窗**：修「加宽阶梯在冻结 `margin=0.0` 下退化」。
4. **另案具名**：GND/pour 边 `244×exception:KeyError` 整类饿死（本窗点名 · 未修）。

LEGAL-ESCALATION: none
OWNER-ITEMS: 0
