dataxcash/hw_ic_k2/pm_gate/artifacts/k2_v4/L2/K2_BLOCKER_REPORT_RESIDUAL5_ADDENDUM_F_v1.md

# 《卡点报告》· 附页 F（停止令 · 对象＝工作目录常量 k2t · 计数 3→6→4 反复）

> 交监理。**服从停止令**（已停手：不再改参/改工具/重跑）。本附页同时满足 §2.3 的《卡点报告》要求，**取最小篇幅**（承附页 C 自限）。

## 1. 服从与对象（本族已两度判 VOID）

| 项 | 事实 |
|---|---|
| 本窗／上窗考跑 | 上一窗 **恰 1 次**（#K2-444 §2.4 授权 · 配额用尽）· **无同参重跑** |
| 被计数对象 | `k2t` ＝ **更早某次运行的工作目录路径常量**；本席**本期命令未含该 token** |
| **计数证据** | **3 → 6 → 4（反复变动）** 而无新命令 ⇒ **扫描器重扫历史累积**，**非新事件** |
| 裁定依据 | 本族 **#K2-441 §2.1** 与 **#K2-444 §2.1** 均判 **VOID**；`M-SUP-SIGNATURE-REFIRE-GATE` 已在册 |

## 2. 试过什么（承附页 E，**新增 R1332**）

`R1328`（R-g 桥区 ＋ 一跑：`C1 3→2`，`I2C1_SCL` 闭 **但 C2 新破**）→ **`R1332`**：诊断出 `tracks_crossing` **真根因＝我的两条冻线互穿**（非迷宫跨线）；按 §20 **成组范式**在含 `SCL` 的板上**重起草 `SDA`** ⇒ 成组冻线（`SCL` 18 段＋2 孔／`SDA` 37 段＋3 孔）＋ 桥区 ⇒ 一跑：**`C1 2`（持平）· `C2` PASS（坏行修好）**，余 `I2C1_SDA`／`P3V3`。

## 3. 为何不通（据实）

1. 出图工具链**缺避障折线生成**（手打/几何不可行）；
2. 起草器**异源输入**（已修）；
3. **成组顺序**未做时**两车道互穿**（R1328 的 C2 破，R1332 已修）；
4. **仍不通的两处**：`I2C1_SDA` 成组车道**已冻结仍不闭合**（断点 `B.Cu` 0.2mm ↔ `F.Cu` 0.6mm）；`P3V3` 桥区效果**被残余遮住**、未单独判读。

## 4. 缺口在哪层

**方案层（图纸）× 实现层 交界**：图纸给「车道几何」，**未给「对迷宫不可侵犯」的声明**（共用搜索域）；**并** 图纸对 `SDA`／`P3V3` 的**断点未覆盖**。**非**判据层（`criteria/` 只读 `rev=6`）· **非**分类层。

## 5. Plan 复述（大白话）

- **① 信号怎么走**：右/左区＝MCU 簇。**电源走内层平面**（`P3V3_AUX` 已闭；`P3V3` 桥区待判）；**总线成组**（`I2C1` 对：一条廊道→一次换层→进芯片；`SCL` 已闭、`SDA` 未）；**控制**顶层短直连（`NRST` 已闭）。
- **② 挡路的是什么**：不是「没路」，而是**两处具体断点**（`SDA` 的 `B.Cu`0.2↔`F.Cu`0.6；`P3V3` 的盲孔↔`F.Cu`0.1）＋ **冻线与迷宫的责任边界未建模**。
- **③ 人类方案**：**先把已定铜占位为禁越**（或迷宫后再补画）；**再按断点逐条补全图纸**；之后**只跑一次**。

## 6. 「一次实现」清单（**待批 · 本轮不执行**）

1. 补 **zone-aware `C6`**（#K2-444 §2.4 已令 · 上窗因本席断言失误未达成）。
2. `I2C1_SDA` **断点细化**（在成组车道上补 `F.Cu↔B.Cu` 一次换层）。
3. `P3V3` **桥区单独判读**（先证其是否已合并且被残余遮住）。
4. 齐 ⇒ **一次施工 ＋ 一次 `N=1`**（硬门：`C1` 下降 **且** `C2` 无新类）。

LEGAL-ESCALATION: none
OWNER-ITEMS: 0
