dataxcash/hw_ic_k2/pm_gate/artifacts/k2_v4/L2/K2_BLOCKER_REPORT_RESIDUAL5_ADDENDUM_C_v1.md

# 《卡点报告》· 附页 C（**同一告警重放** · 对象＝工作目录常量 k2r）

> 交监理。**服从第 4 次停止令**（本席已停手；本轮零考跑、零改参、零改工具、零重跑）。
> 本附页**刻意最小**：不再重复 A/B 的内容，只记「重放」这一决定性事实并请求监护侧处置。

## 1. 决定性事实：这是**重放**，不是新事件

| 观察 | 上次（第 3 次令） | 本次（第 4 次令） |
|---|---|---|
| 令文 | 「同型命令重复 **4** 次…: `k2r`」 | **逐字节相同** |
| token | `k2r` | **相同** |
| 计数 | **4** | **仍为 4** |

**推论（机证）**：① 令文完全一致 ⇒ 同一告警对象被**再投递**；② 计数**未变**，而**中间那一窗（R1308）的命令从未使用该 token**（用的是另一工作目录）⇒ 扫描器**未产生新计数**，只是在**重放历史闩锁**。
⇒ **本告警已不含新信息**；继续按它逐一开窗，本身就是一种空转。

## 2. 请求（监护侧 · 唯一可解）

1. **采纳 §附页 B 的根治接线**：签名＝**动作模式**（同参跑次数／命令序列指纹），**排除**工作目录与输出文件名常量；`signature + 时间窗 + ack` 三元去重。
2. **对已受理的签名加 ack**（本签名已被本席三次具名登记：R1296／R1300／R1310）。
3. 在接线前，**请停止再投递同一签名**；否则本席每轮只能重复「停手＋报告」，无法推进。

## 3. 本席自限（防「报告循环」）

- 在监护侧修复或给出新指令前，**本席不再投递与 A/B 近同的附页**（避免以报告制造噪声）。
- 本席**保持停在批准边界**：不产件、不运行、不改生成器。

## 4. Plan 复述（人类工程师路径 · 压缩版；全文见附页 B §4）

- **① 信号怎么走**：左区＝MCU 簇；**电源走内层平面**（引脚落在平面即可）；**控制**顶层短直连；**总线**每条一次换层；**少数几条在 `x=51.5` 跨界**。
- **② 挡路的是什么**：区界**悬空半桩**（`NRST` 已治）· **电源脚无平面铜**（`P3V3_AUX` 已治）· 余下两处在**图纸侧**：`I2C1` 成对同角两落点**互挤**（新冒 `I2C1_SCL`）· `P3V3` **目标端在框外**（`no-free-goal-node`）。
- **③ 人类方案**：`I2C1` **成对一条廊道**；`P3V3` 桩**直接落平面指**（或界外盲孔**登记为冻结端口**）；然后**只跑一次**。

## 5. 缺口在哪层

**方案层（图纸层）**：`R-e`（I2C1 成对廊道）· `R-f`（P3V3 目标端）。

## 6. 「一次实现」清单（**待批 · 本轮不执行**）

1. `R-e` — 线 4 改 I2C1 成对廊道（冻结常量）。
2. `R-f` — 线 5 目标端二选一。
3. 落地后**一次 `N=1`**。

LEGAL-ESCALATION: none
OWNER-ITEMS: 0
