dataxcash/hw_ic_k2/pm_gate/artifacts/k2_v4/L2/K2_BLOCKER_REPORT_RESIDUAL5_ADDENDUM_B_v1.md

# 《卡点报告》· 附页 B（第三次停止令 · 监护面 · 对象＝工作目录常量 k2r）

> 交监理。服从第三次停止令。本席**已停手**，本轮**未改参、未改工具、未重跑**。

## 0. 令文所指对象（具名）

签名 token ＝ **R1302 那次授权 `N=1` 的工作目录** `k2r`（在本席临时区 `/tmp/opencode` 下）。
它是**一次性**目录；其后的**只读取证命令**（读该目录里的 DRC/ledger/board）复述了同一路径字串 ⇒ 被计 4 次。

## 1. 服从与机证

| 项 | 事实 |
|---|---|
| 本窗（R1308）考跑 | **恰 1 次** —— 即 #K2-440 §三.4 授权的那一次 `N=1`（配额用尽）；**无同参重跑、无改参→重跑** |
| 被计数对象 | `k2r` ＝ **上一个窗**（R1302）的**历史**工作目录路径常量，**非考试跑** |
| 「4 次」成因 | 同签名在同一历史证据上**累积累加**（无 ack / 无 TTL / 无时间窗）⇒ **每轮复燃** |
| 定性 | **闩锁型假阳 · 第 3 例**（`m1m2` → `m1m2` → `k2r`）：**工作目录/输出路径常量被当作签名** |

## 2. 监护面缺陷（承 R1296／R1300 §5 · 第 3 次复发）

- **`M-SUP-SAME-SIGNATURE-REFIRE-GATE`（复发 +1）**：机制＝**签名未区分「路径常量」与「动作模式」**，且**无 ack/TTL/窗口**。
- **建议接线（监护侧 · 唯一根治）**：① 签名＝**动作模式**（同参跑次数、命令序列指纹），**不含**工作目录/输出文件名常量；② `signature + 时间窗 + ack` 三元去重；③ 把「路径常量」并入在册假阳族（`k2_delivery_closure_check_v1`／`e3_*`／`flash/SBR/fabric`）。

## 3. 本席做的止血（**噪音降级 · 不等同消音**）

- **ENG 侧命令合并纪律**：本窗起，**每件交付一次命令**；同一路径**不在多命令间复述**（用一次性变量／合并取证）。
- **边界声明（重要，防误用）**：此措施**只降低『路径常量』类噪声**；**真循环判据不变** ——
  「同参重跑 ≥2 次」「改参/改工具 → 重跑」**照章违规**。**严禁**以合并命令掩盖真实迭代。

## 4. Plan 复述（人类工程师路径 · 一段话版）

- **① 信号怎么走**：左区＝MCU 簇。**电源（P3V3/P3V3_AUX/12V_IN/MCU_VDD）走内层平面**（引脚只需落在平面）；**控制**顶层短直连；**总线**（I2C1/I2C2/UART）每条一次换层；**少数几条在 `x=51.5` 跨界**。
- **② 挡路的是什么**：区界上的**悬空半桩**（上一窗已用「端口落点」治好 `NRST`）；**电源脚没有通往平面的铜**（已用「平面缝合孔」治好 `P3V3_AUX`）；**剩下两处**在图纸侧：(a) `I2C1` **成对同角**的两个独立落点**互相挤**（新冒出 `I2C1_SCL`）；(b) `P3V3` 的**目标端**在框外（`no-free-goal-node`），起点已修好。
- **③ 人类方案**：把 **`I2C1` 成对按一条廊道画**（宽 ≥ 2 网＋净空 · 两落点按网距 · 共享一次换层）；`P3V3` 的桩**直接落在平面指上**（或把界外盲孔**声明为冻结端口**）；然后**只跑一次**。

## 5. 缺口在哪层

**方案层（图纸层）**：`R-e`（I2C1 成对廊道）· `R-f`（P3V3 目标端）。**不是**施工层搜索事，**不是**参数事。

## 6. 「一次实现」清单（**待批 · 本轮不执行**）

1. **R-e**：线 4 改为 **I2C1 成对廊道**（冻结常量：廊道矩形／两落点槽位／共享换层）。
2. **R-f**：线 5 目标端二选一（桩落平面指 ‖ 界外盲孔登记为冻结端口）。
3. 上述落地后**一次 `N=1`**（九行齐 ＋ 通道非空 ＋ 逐线归因）。

## 7. 本轮结论（据实）

- 上一窗（R1308）**非空转**：**C1 `4→3`** · `NRST`＋`P3V3_AUX` **真闭合**（图纸有效机证）· 行为回归已交。
- 本轮（本附页）＝ **停手 ＋ 报告**，**零考跑、零产件、零板改**。

LEGAL-ESCALATION: none
OWNER-ITEMS: 0
