dataxcash/hw_ic_k2/pm_gate/artifacts/k2_v4/L2/b5_conflict_report.md

# B5 冲突报告（模型驱动版）— 低速域板→方案同步 22 网模型求解全量

> 更新: 2026-08-24 · 依据 `.omo/plans/k2-ls-model-gate.md` M6
> 工具: `eda_core/ls_route_model.py`（系统抽象模型: 障碍场 + 可见性图 +
>       Dijkstra + 连通分量不可行性证明，LS-MODEL-GATE）
> 求解记录: `pm_gate/artifacts/L3/model_solves/`（红队可审计，18 网 8 SOLVED + 10 INFEASIBLE）
> 本版替换 2026-08-24 早前的"20/22 成功 + 2 网无解"枚举口径（seg_ok 解包 bug 已证伪）

---

## 1. 结论速览（模型口径，替代"枚举不到"）

| 项 | 同步器枚举（B5 旧） | 模型求解（LS-MODEL-GATE） |
|---|---|---|
| 18 个 E3 冻结网 | 13/22 成功（含 9 网失败"无解"） | **8 SOLVED + 10 INFEASIBLE（全部带证明）** |
| 9 个"枚举失败"网 | 全部"无解"（无证明） | **6 SOLVED（枚举器无能）+ 2 fv 违规 + 1 真断连** |
| 13 个"同步成功"网 | 全部"成功"（障碍场不完整） | **2 真可解（PD1_U3/PD1_U7）+ 5 假成功（严格规则下 INFEASIBLE）** |
| 假象根因 | 障碍场缺板上 via/GND via/异网段；seg_ok 解包 bug | 模型全量障碍（534 via + 265 段 + 16 pad + E3 冻结 via） |

**核心发现：13/22 成功与 9 网无解双向失真**——
枚举器既漏解（6 网实际可解）又假解（5 网成功建立在忽略板上 via 的障碍场上）。
模型给出确定性证明：SOLVED 带路径证据；INFEASIBLE 带 fv 违规明细或连通分量证明。

---

## 2. 22 网模型求解全量（16 个 SPEC 内 E3 网 + 2 个 ALL_DONE_N + 4 个纯同步网）

### 2.1 SOLVED（8 网，模型路径可直接落 SPEC）

| 网 | fv → cv | 路径段数 | 备注 |
|---|---|---|---|
| PD1_U3 | (94.825,56.975)→(97.05,64.85) | 4 | 绕 U3 芯片侧障碍 |
| PD1_U7 | (92.825,49.025)→(92.83,47.65) | 1 | 直接补连 |
| STRAP_EQ0_1_U7 | (93.225,48.725)→(93.22,47.32) | 1 | 直接补连 |
| STRAP_EQ0_U7 | (94.425,40.675)→(94.42,42.35) | 1 | 直接补连 |
| STRAP_EQ1_1_U7 | (94.025,49.025)→(94.03,47.65) | 1 | 直接补连 |
| STRAP_EQ1_U7 | (94.025,38.975)→(94.03,41.26) | 1 | 直接补连 |
| STRAP_MODE_U7 | (93.625,40.675)→(93.62,42.35) | 5 | 绕 STRAP_EQ1_U7 走廊端部 |
| STRAP_READ_EN_U7 | (95.225,38.975)→(95.22,42.35) | 1 | 直接补连 |

### 2.2 INFEASIBLE fv_invalid（3 网，E3 冻结位置违规）

| 网 | fv | 违规证据 | 根因 |
|---|---|---|---|
| PD0_U7 | (92.425,48.725) | 距 GND via (92.225,49.0) 0.340 < VIA_VIA 0.45 | E3 冻结仅对 E3 网互查 min_via_via=0.5，未对板上 via 校验 |
| STRAP_EQ1_1_U3 | (93.625,56.975) | 距 STRAP_MODE_U3 B.Cu 段 (93.62,55.15)-(93.62,59.8) 0.005mm | 冻结未对板上 B.Cu 段校验（几乎骑在异网段上） |
| STRAP_EQ1_U3 | (93.625,66.725) | 距 STRAP_EQ0_1_U3 via (93.2,66.8) 0.432 < 0.45 | 冻结未对板上 via 校验 |

### 2.3 INFEASIBLE disconnected（7 网，fv 口袋被围合）

| 网 | fv 分量 bbox | 围合证据（边界障碍要点） |
|---|---|---|
| PD0_U3 | x[93.6,96.3] y[57.0,64.5]（29 节点） | STRAP_READ_EN_U3 竖段 (96.68,56.25)-(96.68,59.25)、STRAP_EQ0_U3 竖段 (94.0,54.8)-(94.0,60.1)、PD1_U3 (92.83,64.85)-(97.05,64.85) |
| STRAP_EQ0_1_U3 | x[91.1,103.0] y[44.9,68.4]（129 节点） | PD0_U3 底部 U 段、(98.3,45.7)-(98.3,66.15)、STRAP_EQ1_1_U3 (97.48,54.1)-(97.48,66.3) |
| STRAP_EQ0_U3 | x[91.1,103.0] y[44.9,68.4]（129 节点） | PD0_U3 底部 U 段、STRAP_EQ1_1_U3 竖段、(50.05,45.7)-(98.3,45.7) 走廊 |
| STRAP_MODE_U3 | x[91.1,103.0] y[45.7,68.4]（123 节点） | PD0_U3 底部 U 段、STRAP_EQ1_1_U3 竖段、STRAP_EQ0_1_U7 (90.55,46.7)-(90.55,67.65) |
| STRAP_READ_EN_U3 | x[56.3,105.0] y[45.7,69.5]（—节点） | PD0_U3 冻结 via (95.225,58.675)、STRAP_EQ1_U3 冻结 via (95.6,60.45)、NO_CONNECT via (92.825,66.5)、PD1_U3 (92.83,64.85)-(92.83,65.1) |
| ALL_DONE_N_U3 | （同 U3 区） | 同 U3 侧围合（该网不在 SPEC low_speed_nets，纯报告） |
| ALL_DONE_N_U7 | （同 U7 区） | 同 U7 侧围合（同上） |

**共性根因**：U3 侧 offset-down 冻结 via（y≈66.7-68.4）落入**底部口袋**——
PD0_U3 底部 U 段 (91.68,65.75)-(98.3,65.75) + PD1_U3 (92.83,64.85)-(97.05,64.85)
+ STRAP_EQ1_1_U3 竖段 (97.48,54.1)-(97.48,66.3) 构成封闭墙，口袋内任何 fv 无法逃逸。
U7 侧 STRAP_READ_EN_U3 fv 口袋被其他网 E3 冻结 via + NO_CONNECT via 围死。

### 2.4 纯同步网（4 网，无 E3 冻结 → 无补连 → 不需模型求解）

I2C1_SCL / I2C1_SDA / I2C2_SCL / I2C2_SDA 及 PERSTA#/PERSTB#：
板上段/via 原样搬运（board-verified），无设计段，不涉模型。

---

## 3. 与 13/9 分布对比（枚举 → 模型的真假翻转）

| 同步器结论 | 模型结论 | 网 | 说明 |
|---|---|---|---|
| FAIL（9 网） | **SOLVED（6）** | STRAP_EQ0_1_U7、STRAP_EQ0_U7、STRAP_EQ1_1_U7、STRAP_EQ1_U7、STRAP_MODE_U7、STRAP_READ_EN_U7 | 枚举器 3/4/5 段正交枚举无能；模型 1 段直线即解 |
| FAIL（9 网） | fv_invalid（2） | STRAP_EQ1_1_U3、STRAP_EQ1_U3 | 枚举器"找不到"实际是 fv 骑障碍——模型给出精确违规证明 |
| FAIL（9 网） | disconnected（1） | STRAP_READ_EN_U3 | 真不可行（fv 口袋），模型给出连通分量证明 |
| "成功"（13 网） | **INFEASIBLE（5）** | PD0_U3、PD0_U7、STRAP_EQ0_1_U3、STRAP_EQ0_U3、STRAP_MODE_U3 | 同步器障碍场缺板上 via/GND via/异网段 → 假成功；严格规则下 fv 口袋不可达 |
| "成功"（13 网） | SOLVED（2） | PD1_U3、PD1_U7 | 真可解 |
| "成功"（13 网） | 纯同步（6） | I2C×4 + PERST×2 | 无补连，无争议 |

---

## 4. 待 PM 裁决（M8 修订走输入路径，禁止施工层妥协）

| # | 网 | 裁决项 | 建议路径 |
|---|---|---|---|
| R1 | PD0_U7、STRAP_EQ1_1_U3、STRAP_EQ1_U3 | fv 位置违规（3 网） | 修订 escape_spec fv（避开 GND via/异网段/via）→ 模型重算 → SOLVED 后落 SPEC |
| R2 | PD0_U3、STRAP_EQ0_1_U3、STRAP_EQ0_U3、STRAP_MODE_U3 | U3 底部口袋不可逃逸（4 网） | 修订输入：① 移除/重排 PD0_U3 底部 U 段（板上真源，属 B5 前历史产物）或 ② 重冻结 U3 侧 fv 到可逃逸位置（y<65.75 或右通道）→ 模型重算 |
| R3 | STRAP_READ_EN_U3 | fv 口袋被异网 E3 冻结 via + NO_CONNECT via 围死 | 修订：① 清除 NO_CONNECT via（板清理项）② 重排 PD0_U3/STRAP_EQ1_U3 fv ③ 重冻结 STRAP_READ_EN_U3 fv → 模型重算 |
| R4 | 8 个 SOLVED 网 | 直接落 SPEC（model-solved + solve_ref） | M7 同步器降级后按求解记录注入 |
| R5 | ALL_DONE_N_U3/U7 | 不在 SPEC low_speed_nets，不影响 B5 | 记录留档，不落 SPEC |

**裁决后闭环**：修订输入 → `ls_route_model solve` → 求解记录落 `model_solves/` →
同步器落 SPEC（带 source/solve_ref）→ `model_gate` 全绿 → 落板 → DRC。

---

## 5. 方法学固化（防"枚举不到"类结论再生）

1. **结论带证明**：SOLVED 带路径证据；INFEASIBLE 带 fv 违规明细或连通分量
   + 边界障碍清单。本报告全部结论出自模型求解记录（`model_solves/*.json`）。
2. **检测归模型**：障碍检测（膨胀+净距）全部在 ls_route_model；施工层
   （同步器/apply）降级为确定性搬运（M7），无自建检测/求解。
3. **假成功结构性消除**：同步器无求解能力后，"20/22 成功"类假象不可能再生。
4. **修订走输入**：一切冲突由 fv/走廊/约束修订 → 模型重算解决（R1-R3 路径），
   禁止施工层妥协/Workaround。
