dataxcash/hw_ic_k2/pm_gate/artifacts/k2_v4/L2/low_speed_board_spec_diff.md

# 低速域 板↔SPEC 一致性差异报告 (B2)

- board: `strix-halo-ioconvert/revA/pcb/k2_v4.kicad_pcb`（真源=板）
- spec: `strix-halo-ioconvert/revA/pcb/pm_gate/artifacts/L3/SPEC_k2_v4.json`
- 对比网数: 22 / 有差异网: 22

## 汇总

| 维度 | 板上 | SPEC | board_only | spec_only | 层差异 |
|---|---|---|---|---|---|
| segments | 162 | 162 | 92 | 92 | 1 |
| vias | 65 | 98 | 22 | 55 | - |

## 逐网差异

### I2C1_SCL

- segments: match=4 board_only=5 spec_only=6 layer_mismatch=0
  - [board_only] B.Cu (45.250,37.450) → (45.250,60.630)
  - [board_only] B.Cu (45.250,37.450) → (55.900,37.450)
  - [board_only] B.Cu (45.250,37.450) → (133.950,37.450)
  - [board_only] B.Cu (55.900,37.450) → (55.900,64.900)
  - [board_only] B.Cu (133.950,37.450) → (133.950,56.100)
  - [spec_only] B.Cu (45.250,36.200) → (45.250,60.630)
  - [spec_only] B.Cu (51.900,36.200) → (51.900,64.900)
  - [spec_only] B.Cu (51.900,64.900) → (55.900,64.900)
  - [spec_only] B.Cu (133.950,36.200) → (133.950,56.100)
  - [spec_only] In6.Cu (45.250,36.200) → (51.900,36.200)
  - [spec_only] In6.Cu (45.250,36.200) → (133.950,36.200)
- vias: match=3 board_only=0 spec_only=3
  - [spec_only] via (45.250,36.200)
  - [spec_only] via (51.900,36.200)
  - [spec_only] via (133.950,36.200)

### I2C1_SDA

- segments: match=4 board_only=5 spec_only=6 layer_mismatch=0
  - [board_only] B.Cu (45.700,38.500) → (45.700,61.910)
  - [board_only] B.Cu (45.700,38.500) → (54.350,38.500)
  - [board_only] B.Cu (45.700,38.500) → (134.620,38.500)
  - [board_only] B.Cu (54.350,38.500) → (54.350,66.850)
  - [board_only] B.Cu (134.620,38.500) → (134.620,56.100)
  - [spec_only] B.Cu (45.700,36.550) → (45.700,61.910)
  - [spec_only] B.Cu (48.350,36.550) → (48.350,66.850)
  - [spec_only] B.Cu (48.350,66.850) → (54.350,66.850)
  - [spec_only] B.Cu (134.620,36.550) → (134.620,56.100)
  - [spec_only] In6.Cu (45.700,36.550) → (48.350,36.550)
  - [spec_only] In6.Cu (45.700,36.550) → (134.620,36.550)
- vias: match=3 board_only=0 spec_only=3
  - [spec_only] via (45.700,36.550)
  - [spec_only] via (48.350,36.550)
  - [spec_only] via (134.620,36.550)

### I2C2_SCL

- segments: match=3 board_only=3 spec_only=4 layer_mismatch=0
  - [board_only] B.Cu (35.250,54.450) → (35.250,56.000)
  - [board_only] B.Cu (35.250,54.450) → (52.150,54.450)
  - [board_only] B.Cu (52.150,54.450) → (52.150,68.350)
  - [spec_only] B.Cu (35.250,34.000) → (35.250,56.000)
  - [spec_only] B.Cu (38.150,34.000) → (38.150,68.350)
  - [spec_only] B.Cu (38.150,68.350) → (50.150,68.350)
  - [spec_only] In6.Cu (35.250,34.000) → (38.150,34.000)
- vias: match=1 board_only=1 spec_only=3
  - [board_only] via (52.150,68.350)
  - [spec_only] via (35.250,34.000)
  - [spec_only] via (38.150,34.000)
  - [spec_only] via (50.150,68.350)

### I2C2_SDA

- segments: match=3 board_only=3 spec_only=4 layer_mismatch=1
  - [board_only] B.Cu (34.750,54.700) → (34.750,55.650)
  - [board_only] B.Cu (34.750,55.650) → (53.650,55.650)
  - [board_only] B.Cu (53.650,55.650) → (53.650,69.600)
  - [spec_only] B.Cu (34.750,54.700) → (34.750,62.550)
  - [spec_only] B.Cu (54.450,69.600) → (56.450,69.600)
  - [spec_only] B.Cu (56.450,62.550) → (56.450,69.600)
  - [spec_only] In6.Cu (34.750,62.550) → (56.450,62.550)
  - [layer_mismatch] 几何 (34.750,54.700) → (34.750,55.650): 板=['B.Cu', 'F.Cu'] spec=['F.Cu']
- vias: match=1 board_only=1 spec_only=3
  - [board_only] via (53.650,69.600)
  - [spec_only] via (34.750,62.550)
  - [spec_only] via (54.450,69.600)
  - [spec_only] via (56.450,62.550)

### PD0_U3

- segments: match=3 board_only=5 spec_only=3 layer_mismatch=0
  - [board_only] B.Cu (50.050,45.700) → (98.300,45.700)
  - [board_only] B.Cu (91.680,65.750) → (91.680,66.150)
  - [board_only] B.Cu (91.680,65.750) → (98.300,65.750)
  - [board_only] B.Cu (98.300,45.700) → (98.300,66.150)
  - [board_only] F.Cu (95.225,57.200) → (95.225,59.700)
  - [spec_only] B.Cu (50.050,36.900) → (50.050,45.700)
  - [spec_only] B.Cu (92.480,36.900) → (92.480,66.150)
  - [spec_only] In6.Cu (50.050,36.900) → (92.480,36.900)
- vias: match=1 board_only=2 spec_only=3
  - [board_only] via (91.680,66.150)
  - [board_only] via (95.225,57.200)
  - [spec_only] via (50.050,36.900)
  - [spec_only] via (92.480,36.900)
  - [spec_only] via (92.480,66.150)
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
- vias: match=2 board_only=1 spec_only=2
  - [board_only] via (95.225,40.900)
  - [spec_only] via (53.800,35.850)
  - [spec_only] via (95.220,35.850)
- chip_escape: frozen=1 in_spec=0 missing=1
  - [missing] U7.57 pad (95.225,41.700) → via (95.225,38.975)
