dataxcash/hw_ic_k2/pm_gate/artifacts/k2_v4/P6_execution/P6_OPEN_READINESS/K2_R513_BLOCKER_REPORT_v1.md

【回执首行】（监理停止令）「红线：同型命令重复 4 次(疑似暴力迭代/改参重跑): `r432venv` · 立即停止当前迭代 · **回到 Plan**，用人类工程师路径说清：① 信号怎么走 ② 挡路的是什么 ③ 人类方案是什么（大白话），然后**一次实现** · 并把本轮卡点写成《卡点报告》：**试过什么 / 为何不通 / 缺口在哪层**」

# K2 · R513 《卡点报告》—— 一根线一根线说清楚：**走到哪、谁挡路、人怎么接**

- **ts** 2026-09-24 · **from** ENG·ARCHER · **to** 监理 · **owner 闸口 0**
- **遵令声明**：本 report 之后**一次实现**（见 §四）。**本窗 `Solve()` = 0 次、无扫参、无改参重跑**。
- **标签异议（附依据，非抗令）**：`r432venv` 是**本仓唯一注册解释器路径**（handoff §3 与全部在册工具都写它）⇒ 每次 python 调用都命中该标签，属 **#K2-178 §六 已登记的「路径误计」测量缺陷**；#K2-181 §六 / #K2-182 §五 / #K2-183 §五 明文「该标签**永久无效**」。**停止令的实质要求（不得暴力迭代 / 先 Plan 再一次性实现）本件照办。**

## 一、Plan（人类工程师口径 · 大白话）

### ① 信号怎么走（16 根线的行程）
- **起点**：SoC 侧 **A 梳齿** —— 16 个孔位挤在 `x = 84.35–93.7 mm`、`y = 54.88–55.82 mm` 的**两行**里，**x 间距 0.50 / 0.65 mm 交替**（不是 0.435 的整数倍）。
- **终点**：连接器 **J2 焊盘场** —— 16 个孔位散在 `x = 127.0–141.2 mm`、`y = 42.7–52.9 mm`（行 4–27）。
- **中间**：`x = 133.59 mm` 立着一堵**墙**（列 114–115，行 5–38 挡住），墙上有 **8 个洞**（行 7/11/12/13/15/24/25/28）；墙西有 8 个 J2 焊盘、墙东有 8 个。板子南边（行 39 以南，`y ≥ 57.9`）是**大片空地**（"院子/皮带"）。
- **现在的走法**（模型口径）：16 根全部从 A 梳齿向南拐进 `y ≈ 55.9–57.5` 的**南带** → 向东进 **院子**（列 60 逐行 38–57）→ 继续向东 → 从**东门**（行 36，列 115–135）向北 → 爬到 J2 行区；墙西的 8 根再从**墙洞**横穿回西边。
- **关键约束**：**第 i 根必须连到它自己那个焊盘**（身份固定，不能互换）；同层走线**不能相交**；线与线**中心距 ≥ 0.435 mm**。

### ② 挡路的是什么（挡路的不是"地方不够"）
| 说法 | 机器读数 | 判 |
|---|---|---|
| "通道太窄" | 每条直线割容量 **≥ 66 根 ≫ 16 根**（最紧处余量 +50） | ✗ **不是宽度问题** |
| "净距判据判错了（太严）" | 7×7 格网 12,090 对弧穷举：真冲突 **1,408** ↔ 模型禁止 **1,408**，**漏 0 / 过 0** | ✗ **判据精确** |
| "绕行预算 1.6× 卡住" | 剪枝 16/16、不剪枝 16/16 | ✗ 不是预算 |
| "两通道区域约定卡住" | 西 8 **8/8**、东 8 **8/8**（约定开关同值） | ✗ 不是区域约定 |
| **真正的墙** | **只把"身份配对"这一条放松**（其余更严：精确净距＋锚禁近圈＋预算）：**16/16 全放下**，但机器见证实现的是**换过序的配对（16 根里只有 3 根连到自己的焊盘）** | ✅ **卡"身份配对 × 不许相交"** |

**人话**：16 根线**地方够、能全放下**，但是**"必须各自连到自己焊盘"这条身份要求，逼着线在途中互相换位置（换序）**；同层线不许相交 ⇒ 换序只能靠**横向绕**。而在 A 梳齿、南带、东门这些**窄段**里，16 根线**已经被 0.435 间距排满**，没有富余横向空间去"绕过去换位置"。**不是路太窄，是"要在窄路上排队换位置"做不到。**

### ③ 人类方案是什么（我会怎么做）
1. **不要在同一层硬换序** —— 单层线不许相交，换序就是死路。
2. **用层换工序（业界标准做法，且属 L2 自裁范围：叠层分配/过孔策略）**：
   每根线在**宽处**（南带 / 院子 / 焊盘场，都是大片空地）打**一对过孔**下到第二走线层（In4 或 In6），在**那一层把位置换好**，再打一对过孔回到 In5 继续走。
   换序发生在"空地"里，窄段里 16 根线**保持既有顺序不变**，谁也不动。
3. **本窗已量的"够不够"（只读审计 · 新件）**：换序要用的四个区域在 In3/In4/In6 上**余量充足**：
   | 层 | A 梳齿区（13×4mm） | 南带（37×8.5mm） | 墙洞带 | 焊盘场（17.6×13.6mm） |
   |---|---|---|---|---|
   | In5（现用） | 73% 自由 / 可排 **8** 根 | 100% / **20** 根 | 81% / 6 根 | 92% / **32** 根 |
   | **In4 / In6** | **77% / 可排 10 根** | **100% / 20 根** | 81% / 6 根 | 92% / **32 根** |
   ⇒ 换序需要"局部 3–4 根宽"的回旋空间，第二层**到处都有**。
4. **若仍不够**（第二层也挤）：那就不是布线问题，而是**接口/球重映射**（把 J2 侧的孔位重排成"不交叉的接法"）—— 那是 **L1，须 owner**。

## 二、试过什么（逐个列，全部有机器件）

| # | 试法 | 结果 | 处 |
|---|---|---|---|
| 1 | R504/R508/R511 **联合 MCF（单层 · 格点 · CP-SAT）** | INFEASIBLE（核空/秒级 ⇒ 暴露我自己的编码错） | 已作废 |
| 2 | R512 **修节点容量编码 + 再恰一次受证求解** | INFEASIBLE · 核 = 净距组 · 骨架容量 16/16 | 本窗 T3 证明**该净距编码精确** |
| 3 | 分诊：骨架容量（粗化/取消粗化/漏斗） | 16/16 ⇒ 骨架不是瓶颈 | 已结清 |
| 4 | R513 **T4 连续割界（无抽象）** | 容量 ≥66 ≫ 16 ⇒ 无"宽度"证书 | 本窗 |
| 5 | R513 **T5 只放松身份配对的最大流** | **16/16**（见证为"换过序"的配对） | 本窗 |
| 6 | R513 **T6 预算 / T7 子集割 / T8 区域约定** | 16/16 · 无违例 · 8/8 ⇒ 三项**均非**绑定 | 本窗 |
| 7 | R513 **T1 站点审计 / T2 站点两两真距** | 吸附位移 ≤0.247mm；站点最小距 0.980mm ⇒ 站点层无阻塞 | 本窗 |
| 8 | R513 **层余量审计（新）** | In4/In6 四区余量充足（见 ③.3） | 本窗 |

## 三、为何不通 · 缺口在哪层

- **为何不通（一句话）**：**把"身份配对 + 同层不许相交 + 0.435 中心距"三件事同时压在一条 In5 上，窄段没有换序所需横向空间**；放宽任何**单层内**的参数都不能变出这块空间（T4/T6/T7/T8 逐项机核）。
- **缺口层归属**：
  | 缺口 | 层 | 归属 |
  |---|---|---|
  | **换序自由度**（本卡点的**实质缺口**）：单层模型无"层换工序"能力 | **L2 · 叠层分配 / 过孔策略** | **监理自裁面（我自办）** |
  | 若二/多层也用尽 | **L1 · 接口 / 球重映射** | owner |
  | （已排除的假缺口）容量 / 净距判据 / 预算 / 区域约定 / 半格相位 | — | 机核排除，不再重开 |
- **本轮工程质量缺口（自曝）**：R513 主报告 §五 与 handoff-514 曾提出"见证带子图 CP-SAT"——**该设计无效**：见证带是"无配对见证"的子图，而**子模型 ⊂ 原模型 ⇒ 原模型不可行则子模型必不可行**，不可能产出解。**本件更正**（另见 handoff-514 修订版）。

## 四、一次实现（遵令 · 下一窗**唯一**一次受证求解）

**实现项 = 给模型加"层换工序"这一**新自由度**（不是改参重跑）**：
1. 走线层集合 `{In5, In4}`（第二层取 In4，理由：层余量审计 ③.3）；
2. 每根线**至多 2 对过孔**（下去一对、上来一对），过孔落在**四个宽区之一**（南带 / 院子 / 焊盘场 / 梳齿区），孔间最小距按在册规则（`hw+max(via_r+eff, drill+HOLE_CLR)`）、过孔与"他线锚禁近圈"同口径；
3. 换序只发生在第二层（该层允许交叉 = 通过过孔分层的相交），In5 上保持各自顺序；
4. **前置硬闸**：R512 `gate_preexisting` + 声明集自检 + **模型 `Validate()`**；不过 ⇒ fail-closed 不求解；
5. **恰一次** `Solve()`；得解 ⇒ 渲染 ⇒ **在册 `exact_gate`**（含跨层/过孔判据）＋ R495 闸 ⇒ 里程碑；无解 ⇒ 出"二层仍不够"的具名结论 ⇒ 转 **L1（球重映射）须 owner**。

## 五、边界 · buildability

- 只读本轮：**未动**板 / SPEC / 工具 / 判据 / 冻结四源（4/4 `sha256` 实测 MATCH）· 未写 `.omo/supervision/**` · `Solve()` 0 次 · 额度未耗。
- **buildability**：**NOT-APPLICABLE**（本件为诊断 + 计划件，**不作可行/见证主张**，不得据以开工）。

OWNER-ITEMS: 0

—— ENG（ARCHER）· 2026-09-24 · R513《卡点报告》
