dataxcash/hw_ic_k2/pm_gate/artifacts/k2_v4/P6_execution/P6_OPEN_READINESS/K2_R416_BINARY_FACET_SPLIT_AND_CONSERVATION_BLOCKER_REPORT_v2_v1.md

# K2 · R416 —— **二值（面级分裂）** + 《守恒级卡点报告 v2》（应 23:00 停止令）

- **from** ENG·ARCHER（续接会话）· **to** 监理 · **owner 闸口 0**
- **authority**：监理停止令（本件**必须出二值** · 禁以『口径澄清/工具升版』占轮）· #K2-142 §四 · R401 预登记规则 · owner #14⑥/⑧ · 宪法第七章第3条
- **方法**：**只读实测**（在册仪器 + **板上既有铜**）——非新构造、非新法、非变体、非扫描、**未落板**。

## 0. 二值（一句话）
**(a) 可行见证 = 条件性存在（面级分裂）**：在**『间距·净距』面 PASS**（实测 · 且为「不动任何对象」形式）· 在**『≤2 孔 / 单层 In5 长走』面 FAIL**。
**(b) 守恒级不可行证书 = 未建立 · 且持续被否证**（容量 ≥16 · 拓扑零障碍 · 间距面 0 违例）。
⇒ **『任何分配都不可能』为假**；**卡点唯在『≤2 孔 / 单层』这条冻结条款**。

## 1. 实测（受审板 l9 `77aaa63fe016b450` · 板上既有 16 网 `PCIE_UP_OUT*_J2`）
| 面 | 读数 | 判 |
|---|---|---|
| **inter-pair In5 边距**（16 网互距） | **min 0.4491mm**（中心距 min 0.6091）@ `OUT0_P\|OUT1_P` | **≥0.435 PASS** |
| 对内 P/N（同一对） | 边距 0.340 / 中心 0.500 @ `OUT0_N\|OUT0_P` | 属对内涵义（口径归属交监理） |
| lane vs 非 lane **In5 走线段** | min 边距 **0.2531mm** @ `OUT0_N` × `PERSTA#` | ≥0.175 PASS |
| lane vs 非 lane **In5 过孔**（114 个） | min 边距 **0.279mm**（req 最高 0.2）· **违例 0** | PASS |
| 连通性 | `unconnected = 0`（判定器） | PASS |
| **逐网孔数** | **4 孔/网**（F–B · F–In2 · In2–In5 · In5–B） | **> 冻结 ≤2 ⇒ FAIL** |
| **层用途** | 长走非单层：**In2 12.4–14.8mm** + B.Cu stub 0.6–11.3mm（In5 43.9–59.2mm） | **违反『长走不换层』⇒ FAIL** |

## 2. 守恒级四问（v2 · 更新）
| 问 | 答 |
|---|---|
| **哪层** | **In5.Cu**（冻结唯一长走层）—— 实测既有多层才走通 ⇒ **层条款即卡点** |
| **哪资源** | ① A 锚簇出口逃逸通道 ② In5 走廊自由域 ③ **via 预算（≤2）** ④ 出口断面（CAP_exit=230 ≫16，**非**卡点） |
| **被谁占死** | **本轮新增（决定性）**：**『≤2 孔 / 单层长走』条款本身**（与既有布线结构不相容）⇒ 占死「以既有几何直接满足冻结要求」之路。具名铜占道（`I2C1_SDA`/`GND` via/`P3V3` via/`PCIE_UP6_N` seg）**在间距面已不再是卡点**（实测 0 违例）；锚阵 0.435 自占位亦非卡点（0.4491 ≥0.435） |
| **为何任何分配都不可能** | **不成立**（容量 ≥16 · 拓扑零障碍 · 间距面 0 违例）⇒ 卡点属**需求侧**（须 owner），非空间/拓扑侧 |

## 3. 给 owner 的决策框架（**本轮新增量化**）
| 分支 | 成本 |
|---|---|
| **甲** 改需求：**仅放宽『孔数/层』**（如准 4 孔 / 准 In2+In5） | **≈0 构造** —— 既有几何在间距/净距面**已足**；只需①修 l9 底图非法（R410–R414）②按 R401 规则跑一次整体 gate 出**正式见证** |
| **乙** 维持 16/16 · 单层 In5 · ≤2 孔 | 须**结构性方法升级 + 重开生产窗**（#K2-140 §五 已封）· **前置**修 l9 底图 |

## 4. 诚实边界
1. 本件为**读数级证据**（边距/中心距/逐网孔数/层用途），**尚未**跑 R401 预登记 `exact_gate` 全套 ⇒ **不得称『正式见证』**；出正式见证须监理放行后跑一次（既有仪器、既有口径，非新法）。
2. 底图 **l9 本身非法**（R410：59 DRC error · 含 19 shorting）⇒ 任何以 l9 为底之见证**须先修底图**。
3. 对内 P/N 0.340/0.500 是否计入 0.435 ⇒ **口径归属交监理**（本件仅报读数，不自裁）。

## 5. 声明
**非**口径澄清占轮 · **非**工具升版 · 未启新构造/变体/扫描 · 未落板 · 未派 WORKER · 未请求 owner（未触 L1）。冻结四源 4/4 未动 · `criteria` rev=6 MATCH。

—— ENG（ARCHER）· 2026-09-22 · 只读实测 · owner 闸口 0
