dataxcash/hw_ic_k2/pm_gate/artifacts/k2_v4/P6_execution/P6_OPEN_READINESS/K2_R362_UP_OUT_TWO_CHANNEL_ANNULUS_TOPOLOGY_AND_JOINT_SOLVE_SPEC_v1.md

# K2 · R362 · ①-UP —— 自由域 = **双通道（环形拓扑）** ⇒ **存在绕墙 winding 自由度**；联合解**可执行规格**

**件**：`K2_R362_UP_OUT_TWO_CHANNEL_ANNULUS_TOPOLOGY_AND_JOINT_SOLVE_SPEC_v1.json`（约定A **`5cc90a529a9dfd09`**）
**据**：#K2-132 §三 · #K2-133 §三 N1 · 监理自动续推（P4 在阶）· owner #14⑥ · 承 R360/R361
**锚**：冻结四源 **4/4 未动** · `criteria` **rev=6 MATCH** · 受审板 l8 `7a5c89913d6e5d0a` · **owner 闸口 0**

## 〇、结论
自由域实为**两条宽通道 + 两端枢纽**（下/走廊通道 · 上通道 · 西枢纽 x≈104 · 东枢纽 x≈134），**中间障壁 = 自由域之一孔** ⇒ **环形拓扑** ⇒ **存在绕墙 winding 自由度**。这**解释了**为何所有**单调类/巴士类/v67/M1** 构造族都死于西入口；同时说明**联合解原则上存在**（须显式建模该孔）。

## 一、读数
| # | 读数 |
|---|---|
| **F1** | **双通道**：上 `y∈[56.6,64]`（~7.4mm⇒17 lane）· 下/走廊 `y∈[40,55.2]`（~15mm）；西枢纽 x≈104（缝槽带 y=54.88）· 东枢纽 x≈134（P2 门）；障壁 `x∈[104,134]·y∈[55.2,56.6]` = 一孔 |
| **F2** | ⇒ **绕墙 winding 自由度** ⇒ **非**单连通条带/单调 switchbox ⇒ **单调/巴士/v67/M1 族全灭**之拓扑根因 |
| **F3** | A 锚 **P/N 交错**（P=54.88 **恰 = 缝槽标高** · N=55.82 · 每 k 对 x 隔 0.5–0.65mm）⇒ 「西组→P1 · 东组→P2」自然切分**在 A 侧受阻**（P1 下沉东行撞 P2 上抬竖段） |
| **F4** | 试「上通道 + R316 连接器」（`t`/`x_s` 随 a_rank 递减）⇒ `exact_gate` **不过**（互距 15 违例·最小 0.015；净距 12 违例·最小 −0.425，集中于 **A 锚群**）⇒ 直线式指派不足 |

## 二、联合解**可执行规格**（下一实现窗口）
- **决策**：每 lane 之 门户 `{P1,P2}` × 上通道标高 `t_i` × 下潜站 `x_s_i` × 连接器层 `ye_i`（**取代** R316 之独立 ye）。
- **硬约束**：cell 0.03 自由域 · 互距 ≥0.435（两两）· 端点位移 0 · **非交叉**（**须显式编码绕墙 winding：以孔两侧枢纽之穿越序**）· 长度/等长界（R320 skew 222mm 教训）。
- **建议形式**：**有序多商品流 MILP**（栅格 0.03 · 交叉禁止以枢纽穿越序变量编码）。
- **验收**：`exact_gate`（互距0 ∧ 净距0 ∧ 端点0）+ 两 seed + `buildability` ⇒ 二值。
- **可用件**：R316 候选族（已复现 16/16）· R320 门框架 · 本件 F1/F2。

## 三、边界
F1–F3 为**结构性表征**（观测+推断）⇒ **不作 (b) 证书、不作里程碑**（#K2-132 §三.4）。二值 **(a) 未得 · (b) 不成立**。

## 四、复现
```bash
python3 /tmp/opencode/k2r360/twotrack.py   # F4 ⇒ 不过闸
```

## 五、可施工性（宪法十三）
`mode = no_move`：纯只读 · 未搬任何对象 · 未烙板 ⇒ 不动证明成立。「施工队照此图能否直接连」：**不能**（图纸层缺图）。

—— ENG（ARCHER）· 2026-09-22（真实时钟 09:46+0800）· owner 闸口 **0**
