dataxcash/hw_ic_k2/pm_gate/artifacts/k2_v4/P6_execution/P6_OPEN_READINESS/K2_R358_CONSERVATION_BLOCKER_REPORT_v72.md

# K2 · R358 ·《守恒级卡点报告 **v72**》（应监理第 3 次停止令 · 四字段 + 全部刚性判定）

**件**：`K2_R358_CONSERVATION_BLOCKER_REPORT_v72.json`（约定A `2b3cbe459c089d37`）· 只读 · 冻结四源 4/4 未动 · 判据 rev=6 MATCH

## 二值
**(a) 16/16 可行见证：未得** · **(b) 守恒级不可行证书 U<16：不成立**（不新增不可行主张 + 四重反向数测）。

## ① 哪层
**算法/实现能力层** —— 缺『**双通道折返楼梯**之 16 lane 联合几何生成器』。须同时满足四刚性：
㈠ 竖序不变量 ㈡ **折返**（8/16 lane 无 x-单调通路）㈢ **非巴士**（v67 类已证不可行）㈣ **非单点直水平**（M1 类已证不可行）。
⇒ 现存三法族 + v67 类 + M1 类**皆在排除面内** —— 此即 ≈80 轮无二值之因。

## ② 哪资源
| 子资源 | 实测 |
|---|---|
| A 锚带 | 0.940mm 高 · 剃刀边 **0.4386** · 邻锚缝 **0.330<P** |
| **东下潜窗** x∈[135.9,143.05] | 宽 **7.1mm** ↔ 16 lane 需 **6.96mm** ⇒ **仅余 0.14mm** |
| **中层西返通道** y∈[53.0,56.0] | x∈[107,133] **全自由** · 槽容量 **~90** ⇒ **折返唯一走廊** |
| 过孔墙缺口 x≈134 / 南区 | y<43.07 cap 31 · 中段 0.4–1.0mm 多枚 · 南区 y∈[38,55.9] |

## ③ 被谁占死
**未占死**。自网 In5 旧铜 **237 项** no-move 全转可拆；缝合孔 **135 枚** 仅 C-w。封中场竖门/过孔墙/东端汇 ⇒ 断 **0/0/1**。

## ④ 为何任何分配都不可能
**前提不成立 ⇒ (b) 不成立。** 四重反向数测：E4 必经横线槽容量 **≥83≫16** · E3 跨缝 Σ 容量 **148≥16** · E6 封测不断开 · **E7 中层西返通道容量 ~90≫8**。

## 最小缺口（to binary）
**缺一件工程物**：双通道折返楼梯构造器（决策对象 = 下潜窗站序 × 中层西返层 × 落位楼梯站序；编码 ㈠㈡㈢㈣；过 `exact_gate` + `buildability`）。
**为何非本轮**：需 10³–10⁴ 行级几何/指派代码 + 多轮调试，在『一次实现、禁同族变体、禁半途烙板』授权内无法单轮产出。
**最小解封（监理自裁面）**：(甲) 准该构造器**拆多轮同一实现**；或 (乙) 依 #K2-133 N2 **批 C-w** 释放中层通道。

---
—— ENG（ARCHER）· 2026-09-22（真实时钟 09:44+0800）· owner 闸口 **0**
