dataxcash/hw_ic_k2/pm_gate/artifacts/k2_v4/P6_execution/P6_OPEN_READINESS/K2_R356_CONSERVATION_BLOCKER_REPORT_v71.md

# K2 · R356 ·《守恒级卡点报告 **v71**》（应监理停止令 · 四字段 + 三重刚性新证）

**件**：`K2_R356_CONSERVATION_BLOCKER_REPORT_v71.json`（约定A `07558017e5c4e163`）· 只读 · 冻结四源 4/4 未动 · 判据 rev=6 MATCH

## 二值（本件唯一终局）
- **(a) 16/16 可行见证：未得**（+ exact_gate 0 + buildability 仍缺）。
- **(b) 守恒级不可行证书（U<16）：不成立** —— 本件不新增不可行主张；下附三重反向数测。

## ① 哪层
**算法/实现能力层**：缺『**折返感知 × 互距感知**之 16 lane **联合几何生成器**』。

**本会话决定性收窄（相较 v65–v70）**：所需构造须**同时**满足
- ㈠ **竖序不变量**（在飞 lane 之 a_rank 竖序 · 由立管 x 序强制 · 不可选）；
- ㈡ **折返刚性**（**8/16 lane 无 x-单调通路**，且该集合 == B 锚在过孔墙以西之西组 ⇒ 每条西组**必须东行越过自身 B 锚再西返**）；
- ㈢ **禁巴士类**（『定阶巴士 + 单次下潜 + 直水平』**已证结构性不可行** · 反例 6P×6N）。

⇒ 现存三法族（顺序贪心/硬排除 · 最短路候选 MILP · 巴士 waypoint）**皆落在被排除之构造类内** ⇒ 此即 80 轮无二值之直接原因。

## ② 哪资源
| 子资源 | 实测 |
|---|---|
| **A 锚带** x∈[84.35,93.70] × 高 **0.940mm** | 剃刀边 **0.4386mm**（仅高出 P=0.435 **3.6µm**）· 相邻锚保留盘间仅余 **0.330mm < P** |
| **过孔场梯道** x∈[93,108] | 逐行错位 · 关键竖门 x≈104.5 宽 **0.18–0.51mm** ⇒ 直通容量 **1 lane** |
| **东端汇** x≳136.6 | 板边 143.05 内可下潜竖列 ≤ **9** 簇（作参考，**非证书**） |
| **宽区**（上带 y∈[56.5,68] · 南区 y∈[38,55.9]） | **充裕** |

## ③ 被谁占死
**未占死**。no-move 全转可拆**本 16 网自身** In5 旧铜 **237 项**；全局固定缝合孔 **135 枚**（GND 70 · GND_FIXED 32 · P3V3_FIXED 25 · P3V3 8）**仅 C-w**。
**连通性扰动实测**：封过孔场唯一竖门 ⇒ 断 **0** lane · 封过孔墙 x≈134 ⇒ 断 **0** lane · 封东端汇 ⇒ 断 **1** lane ⇒ 自由空间**高度连通**。

## ④ 为何任何分配都不可能
**该前提不成立 ⇒ (b) 不成立。** 三重反向数测：
| 测 | 读数 |
|---|---|
| **E4 横切容量** | 单 lane **必经**之横线 y=c（52.95≤c≤53.9）槽容量 **≥ 83 ≫ 16**（最小 83 @ y=53.70） |
| **E3 跨缝槽容量** | 跨缝 y=54.880 · x∈[93.4,108] **恰 11 离散槽** · **Σ 容量 148 ≥ 16** |
| **E6 连通性扰动** | 三处瓶颈封测**不断开**（0/0/1） |

⇒ 容量 / 连通 / 端点 / 面积**皆非瓶颈**；亦**无**拓扑强制交叉（R349 已自证伪）。卡点纯属 **ENG 实现能力**。

## 最小缺口（to binary）
以『**折返口槽位 × 西返水平层**』为决策对象之 MILP/CP（或等价穷举），**须**显式编码 ㈠竖序不变量 ㈡折返（含阶梯下潜）㈢互距 ≥0.435；随后坐标化 + `exact_gate`（互距0 ∧ 净距0 ∧ 端点0）+ `buildability` 验收；**禁**复用已死构造类。

---
—— ENG（ARCHER）· 2026-09-22（真实时钟 09:20+0800）· 二值 **(a) 未得 · (b) 不成立** · owner 闸口 **0**
