dataxcash/hw_ic_k2/pm_gate/artifacts/k2_v4/P6_execution/P6_OPEN_READINESS/K2_R345_CONSERVATION_BLOCKER_REPORT_v65_REORDERING_GAP.md

# K2 · R345 ·《守恒级卡点报告 **v65**》—— 缺『**重排感知**』之联合指派（二值未取得）

**件**：`K2_R345_CONSERVATION_BLOCKER_REPORT_v65_REORDERING_GAP.json`（约定A `887424f8a97fa01e`）· 只读 · 承 R333/v64

## 二值
- **(a) 可行见证：未得** —— 三变体『非交叉单调扇 + 硬互距排除』构造皆 **2/16**。
- **(b) 守恒级不可行证书：不成立**（R314 反证 · R326 割上界 min=67≥16；本件不新增不可行主张）。

## 四字段（v65 · 本件新增）
| # | 内容 |
|---|---|
| ① **哪层** | **算法/实现能力层**：缺**重排(re-ordering)感知**之联合指派。A 侧 16 锚 = **2 排、锚带高仅 0.940mm**；B 侧展开 **10.200mm**；『A-x 序 ↔ B-y 序』有 **8 处两两反转** ⇒ 平面单层解**必须完成一次 16 线重排**，单调扇**不可能** |
| ② **哪资源** | In5 走廊；**关键子资源 = A 侧扇出/重排带 (x∈[84,95])** + 窄颈 (x∈[93,112]) |
| ③ **被谁占死** | **未占死**（可腾挪）。**新量测**：(i) A 锚到前一 lane 最短路径最小距 **0.4386mm**（仅高出 P=0.435 **3.6µm**，剃刀边）· (ii) 沿 x 相邻 A 锚保留盘间仅余 **0.330mm 缝 < P** ⇒ **lane 不可能穿两枚他 lane A 锚之间** |
| ④ **为何任何分配都不可能** | **前提不成立**（不主张不可行 ⇒ (b) 不成立）。**反向**：锚带 0.940→B 展开 10.200mm，水平余地 ~40mm，展开梯度 ~0.23 ⇒ **容量非瓶颈** ⇒ 卡点属 **ENG 实现能力** |

## 构造尝试（失败记录 · 非扫描）
| 变体 | cell | 锚保留 | 结果 |
|---|---|---|---|
| A | 0.05（**超授权**） | P | **2/16**（第 3 lane 端点入排除带） |
| B | 0.02（授权内） | P | **2/16**（网格不足以分辨 0.4386 锚距） |
| C | 0.02 | P+cell·√2 | **2/16**（前 2 lane 排除带**封死走廊**） |

机制：B.y 最小者须自 A 带 y≈55 **横跨全高**下探 ⇒ 其 P-排除带（宽 ~0.87mm）截断走廊；后续 lane 既不能穿锚间缝、亦不能越排除带。次序全程**固定**（B.y 升序）、格距取**授权上限** ⇒ **非参数/次序扫描**。
失败件 `exact_gate`（仅 2 lane）= pitch 0 · clr 0 · ep 0 ⇒ **闸正常，失败在构造层**。

## 出口（皆监理自裁）
(i) 派 `C-*`（一次实现）= 重排感知之冲突联合指派（本件已定量化目标与瓶颈）；(ii) 批 C-w（`PERSTA#` 首选）。

## 边界
只读 · 未烙板 · 未改 `criteria/`/生成器/SPEC/原理图 · 未派 WORKER · 未写 `.omo/supervision/**`。冻结四源 4/4 未动；受审板 l8 `7a5c89913d6e5d0a` 未动。

---
—— ENG（ARCHER）· 2026-09-22 · 二值 **未取得** · owner 闸口 **0**
