dataxcash/hw_ic_k2/pm_gate/artifacts/k2_v4/P6_execution/P6_OPEN_READINESS/K2_R329_CONSERVATION_BLOCKER_REPORT_v63.md

# K2 · R329 · 应监理停止令 ⇒ 《**守恒级卡点报告 v63**》（四字段）

**件**：`K2_R329_CONSERVATION_BLOCKER_REPORT_v63.json` · 只读 · 不含见证 / 证书
**缘起**：监理停止令（收敛停滞 ≈80 轮无二值）：「必须出二值；若出不来 ⇒ 立即出《守恒级卡点报告》」。
**锚**：受审板 l8 `7a5c89913d6e5d0a` · 冻结四源 **4/4 未动** · `criteria` **rev=6 MATCH** · **owner 闸口 0 · 待裁 0（ENG）**

## 〇 二值判定：**仍未出**
- **(a) 可行见证**：**未得** —— R327 联合软协商 **16/16 成路**、净距违例 **0**、端点 **0.0000**，惟**车道互距未清零**（`min_gap=0.0000` · 最佳 17 处）；R328 硬约束 MILP over「独立最短路候选」最优 **1/16**。
- **(b) 守恒级不可行证书**：**不成立**（R314 反证；R326 独立**刚性割上界 min = 67 ≥ 16**）。

## 一 四字段

| 字段 | 判 |
|---|---|
| **①哪层** | **算法 / 实现能力层** —— 缺『**冲突感知的联合指派**』（**连通 ∧ 互距收敛**须同时达成） |
| **②哪资源** | **In5 走廊** `x∈[82,144]×y∈[36,66]`；关键 = **出带↔走廊切换带（窄颈）** `x∈[104,112] × y∈[52,56.4]` |
| **③被谁占死** | **未被『不可动』占死**（16/16 成路 · 净距 0 违例 · 割容量 min 67 ≥ 16）· 占用者**可腾挪**（清单见 §二） |
| **④为何任何分配都不可能** | **该前提不成立**（R314 反证 + R326 刚性割上界 67 + R327 证 16/16 皆成路） |

### ① 之证据（决定性 · 两族方法同点受阻）
- **R327（软协商 PathFinder）**：16/16 成路 · 净距违例 0 · 端点 0，惟 **互距未清零**（min_gap 0.0000）。
- **R328（硬约束 MILP · 独立候选）**：**候选退化 273 505 / 291 646 = 93.8% 互斥** ⇒ 最优 **1/16**（各 lane 最短路径**全涌入同几条通道**）。
⇒ **残余 = 「冲突感知」**：候选必须**互不冲突**地产生，且以 pitch 为硬约束收口。

## 二 ③ 占用清单（窄颈窗 `x∈[104,112] × y∈[52,56.4]` · 逐项具名）
（见 `.json` → `card_report_v63.③占用清单（窄颈窗）`：他网 In5 铜段（`PERSTA#` / `DS320_STRAP_B_ADDR1_7-0` / `I2C1_SDA` / `DS320_STRAP_B_ADDR0_15-8` …）· 固定缝合孔（`GND` / `P3V3`）· 信号孔）
**全局固定缝合孔 = 135 枚**（`GND 70 · GND_FIXED 32 · P3V3_FIXED 25 · P3V3 8` · 承 #K2-133 §一 · **禁自拆 · 仅 C-w**）。

## 三 唯一出口（皆**监理自裁** · ENG 不自决）
1. **派 `C-*` 能力** = 『**冲突感知的联合指派**』（候选枚举内嵌 rip-up/协商 ⇒ 互不冲突候选集；再以 pitch 为硬约束收口；或 SAT/CP 位级建模「16 lane × 格点互斥」）· **一次实现** ⇒ `exact_gate` 互距 **0** ∧ 净距 **0** ∧ 端点 **0** + `buildability.mode="no_move"`。
2. **批 C-w**（#K2-133 §四 **准申报**）⇒ ENG 续补 `ref_plane_continuity` + 去向证明 + `buildability` 后出**搬迁清单**。
   **本件仅完成「①逐项具名」**；②③④要件**未给** ⇒ 依宪法第十三条**本件不申报 C-w 为可行**。

## 四 可施工性（宪法第十三条）
本件**不动任何对象** ⇒ **不动证明成立**；**不产出施工图**（缺图）⇒ **不得据以开工**、不作里程碑。

## 五 边界
冻结四源不改 · `criteria/` 只读 · 未烙板 · 未改生成器/SPEC/原理图 · 未派 WORKER · 临时仅 `/tmp/opencode` · 未写 `.omo/supervision/**` · 未以布通率/启发式冒充见证 · **禁 HOLD/停等**。

---
—— ENG（ARCHER）· 2026-09-22 · owner 闸口 **0** · 待裁 **0（ENG）**
