dataxcash/hw_ic_k2/pm_gate/artifacts/k2_v4/P6_execution/P6_OPEN_READINESS/K2_R326_BINARY_NOT_OBTAINED_AND_CONSERVATION_BLOCKER_REPORT_v62.md

# K2 · R326 · 应监理停止令 → **二值仍未出**（(a) 未得 · (b) 不成立）· 《**守恒级卡点报告 v62**》

**件**：`K2_R326_BINARY_NOT_OBTAINED_AND_CONSERVATION_BLOCKER_REPORT_v62.py`（只读复算器）+ 同名 `.json`（约定A **`b68a1b86b7e131ad`**）
**缘起**：监理停止令（收敛停滞 ≈80 轮无二值）：「本件必须出二值；若出不来 ⇒ 立即出《守恒级卡点报告》」。
**本件结论**：**二值仍未出** —— **(a) 未得**（最佳合法几何 13/16，且含 `T1_N`=314.23mm 绕行 ⇒ 不作交付见证）· **(b) 不成立**（R314 反证；本件独立刚性割上界 **min=67 ≥ 16** 佐证）。⇒ 依令出**卡点报告 v62**（四字段 · 全部以精确量支撑）。
**锚**：受审板 l8 `7a5c89913d6e5d0a` · 冻结四源 **4/4 未动** · `criteria` **rev=6 MATCH** · **owner 闸口 0 · 待裁 0（ENG）**

---

## 一、《守恒级卡点报告 v62》四字段

| # | 字段 | 判 |
|---|---|---|
| **①** | **哪层** | **算法 / 实现能力层** —— 缺『**折返-绕障型联合构造器**』（**非**判据层 · **非**几何刚性层 · **非**容量层） |
| **②** | **哪资源** | **In5「出带 ↔ 走廊」切换带（窄颈）**：窗 `x∈[93,112] × y∈[44,58]` |
| **③** | **被谁占死** | **未被『不可动』占死** —— 占用者**可腾挪**（详 §二 普查）；**固定件** = 本窗内 `GND×53, P3V3×16`（全局 **135 枚** · 牵 `ref_plane_continuity` · **仅 C-w**） |
| **④** | **为何任何分配都不可能** | **该前提不成立** —— R314 已反证守恒级不可行证书；本件再以**独立刚性割上界**佐证：**上界 min = 67 ≥ 16**。故**不予主张**「任何分配都不可能」。 |

### ①之证据（本件精确读数 · 否证「单水平长走」）
最简精确联合模型（3 段直折线 `(ax,ay)→(ax,y)→(bx,y)→(bx,by)`）：**8/16** 条 lane **候选为 0**（`T0_N, T1_P, T2_N, T3_P, T4_N, T5_P, T6_N, T7_P`）。
机理：这些 lane 之**水平段与 A 竖段均可行**，唯 **B 侧竖段**（`x=bx` · `[by,y]`）须穿越走廊 `y≈55.2–56.2` 之**阻断带** ⇒ **任何单水平长走之解 ≤ 8/16** ⇒ 其余必经**层内折返（jog）** ⇒ **折返-绕障型构造器**为必要能力。

## 二、③之占用普查（窗 `x∈[93,112] × y∈[44,58]` · **逐项具名**）

**他网 In5 铜（段数）**

| net | 段数 |
|---|---|
| `PERSTA#` | 13 |
| `DS320_STRAP_B_ADDR1_7-0` | 11 |
| `I2C1_SDA` | 3 |
| `PCIE_UP7_P` | 1 |
| `PCIE_UP7_N` | 1 |

**固定缝合孔（禁自拆 · 仅 C-w）**：GND×53, P3V3×16
**信号孔（窗内）**：I2C1_SDA×1, PCIE_DN_OUT7_N_MCIO×1, PCIE_UP7_P×1, PCIE_UP7_N×1, DS320_STRAP_B_ADDR1_7-0×2, DS320_STRAP_B_ADDR0_15-8×1
**本网旧铜**：`PCIE_UP_OUT*_J2` 之 In5 旧铜在 **no-move 全转**口径下**可拆**（#K2-133 §三 N1）。

## 三、可选通路（**均需监理动作** · ENG 不自裁）

| 通路 | 状态 | 须补 |
|---|---|---|
| **C-w 搬迁清单**（#K2-133 §四 · **准申报 · 执行待批**） | 本件**仅完成①占用普查**（上表已逐项具名） | ②`ref_plane_continuity` 证明 ③端点/球位不动 ④`buildability` ⑤不动冻结四源 ⇒ **缺则不作数**（宪法第十三条），**本件不申报 C-w 为可行** |
| **`C-*` 能力**（承 #K2-133 (甲)） | **未派** | 派『折返-绕障型联合构造器』**一次实现**（非序贯 · 非参数扫描）⇒ 过 `exact_gate` 之 16/16 + `buildability.mode="no_move"` |

> **为何 80 轮无二值（直答停止令）**：残余卡点 = **实现能力层**，其唯一出口有二 —— **派 `C-*`** 或 **批 C-w**；二者均属监理自裁而非 ENG 可自决。**既有 `13/16 + EX-3`** 之路**不可交付**（其 13 条构造解含 `T1_N`=314.23mm vs `T1_P`=92.20mm ⇒ 等长/SI 不达标）。

## 四、可施工性（宪法第十三条）

本件**不动任何对象**（未烙板 · 未改生成器/SPEC/原理图 · 未改任何网几何）⇒ **不动证明成立**；本件**不产出施工图** ⇒ 全板**图纸层缺图**，**不得据以开工**、不作里程碑。

## 五、边界

冻结四源不改 · `criteria/` 只读 · 未重建/覆盖旧包 · 未派 WORKER · 临时仅 `/tmp/opencode` · 未写 `.omo/supervision/**` · 未以布通率/有界搜索/启发式冒充见证或证书 · **禁 HOLD/停等**。

---
—— ENG（ARCHER）· 2026-09-22 · owner 闸口 **0** · 待裁 **0（ENG）**
