dataxcash/hw_ic_k2/pm_gate/artifacts/k2_v4/P6_execution/P6_OPEN_READINESS/K2_R261B_UP_OUT_HUMAN_PATH_PLAN_AND_BLOCKER_REPORT_v55.md

# K2 · R261B · **②-UP 人话路径（Plan）+ 卡点报告 v55** — 应监理**停止令**（连续错误 2 次 · 禁暴力迭代）

**件**：`K2_R261B_UP_OUT_HUMAN_PATH_PLAN_AND_BLOCKER_REPORT_v55.json`（sha16 **`ecd153e529f36090`** · 约定A）
**依据**：监理停止令（红线·连续错误 2 次）· 宪法第八章第8条（禁暴力迭代）· #K2-132 D1 · #K2-133 N1 · 指令 #14 ⑥
**停止令遵从**：本轮**零『改参数/改工具/改笼位→重跑』迭代**；仅 **1 次规划性实现**（ECO-A 单次构造，非扫描、非重跑）。零烙板 · 零改冻结件 · 未派 WORKER。
**锚**：冻结四源 **4/4 未动** · `criteria` rev=6 MATCH · 受审板 l8 **`7a5c8991`** · errata-3 **`5dc7b82a`** · 口径 **keepout 0.5300**（未改）· 车道互距 ≥0.435

---

## ① 信号怎么走（人话）

16 条 `PCIE_UP_OUT` 差分车道，每条**只准 2 个过孔**：

> U6 球 → F.Cu 短扇出 → **A 侧过孔下到 In5** → In5 长走线 → **B 过孔回 F.Cu** → J2 焊盘

因为只准 2 孔，**A 孔落在哪，In5 车道就从哪开始** —— A 孔的位置基本决定了难度。

## ② 挡路的是什么（人话）

- A 侧 16 个孔排成**两行**：`_P` 行 y=**54.880**（8 枚）· `_N` 行 y=**55.823**（8 枚）。
- 两行**紧贴一条大障碍墙的南沿**（墙 = GND/P3V3 缝合孔场 + 他网 `PERSTA#` In5 带 + 连接器通孔列）；墙北走不通。
- 唯一去路：**先南拐进开阔的南通道（y>56.4）→ 东绕到东通道 → 北上到 B 孔**。
- **卡在『南拐』**：`_P` 行被墙和 `_N` 行夹住。判据口径（keepout 0.5300）下，相邻 `_N` 孔之间只剩 **0.09 / 0.14 mm 的缝（7 条）**，而一条车道要 **0.435 mm** ⇒ **一缝最多 1 条**；两行间的横带又被 `_P`(→55.410) 与 `_N`(55.290→) keepout **重叠封死**，无法在行间向东 ⇒ **`_P` 出口容量 ≈ 8 条 = 需求量，余量为 0**。
- 直白说：**这不是布线器不行，是 A 侧过孔摆错了位置** —— 8 个孔塞进墙脚两行夹缝，等于自设 0.1 mm 级迷宫。

## ③ 人类方案（大白话）

1. **把 A 侧 16 个『我们自己的』过孔挪到墙南开阔地，排成一条整齐的梳子。** 只动**本网**几何（#K2-133 §三 明文授权 · #14 之 L2『过孔策略』自裁面），**不碰他网、不碰球位/连接器焊盘**。
2. **落位一次定死**：单行 **y=57.60**、x=85.60+0.70·k（k=0..15，pitch 0.70 ≥0.435）；实测该带 x 84–112 **连续自由 ≈28 mm**。
3. **扇出**：每个球用一段 F.Cu 短线接到新孔（本网几何重画 = 既有『子步骤 F』），球位不动。
4. **车道用人画的『梳子』，不靠布线器搜**：第 k 条（A.x 序）从新孔先**向南落到自己的水平线** y_k = 58.80+0.435·(16−k)（**最西的孔走最深**），再**向东**→东通道→**向北**→向西接各自 B 孔。此画法**按构造保证互不相交**。
5. **为何这样就通**：梳子规则把『出口换序』变成**显式几何**，不依赖任何搜索；剩余风险仅在 B 侧次序，届时同法一次画完。

## 卡点报告 v55

**试过什么**
| 方法 | 结果 |
|---|---|
| 在册顺序硬避让布线器（20 序枚举） | 最好 **12/16**（合法·0 违规） |
| 本会话独立顺序硬分离布线器 · 洋葱序 4 规范朝向 | By_desc **12** / Ax_desc 11 / Ax_asc 2 / By_asc 1（皆 0 互距违规）⇒ 上限 **12/16** |
| 标准 PathFinder（保留半径=pitch/2 · present+history · 全量 rip-up · 60 轮） | 每轮 **16/16 布通**，末闸 **38 对互距违规**（min 0.0000）⇒ 非见证 |
| **ECO-A**（A 入口孔重排单行 y=57.60）后**单次**构造 | **2/16**（互距 0 违规 · 障碍 0 违规 · 端点 0）⇒ 挪孔有效，但**贪心布线器走不出梳子** |

**为何不通（三层）**
1. **几何层（真因·已量测）**：A 侧 `_P` 孔被墙与 `_N` 孔行夹住——缝 0.09/0.14 mm、行间带被 keepout 重叠封死、东端带约容 1 ⇒ **出口容量 ≈ 需求（余量 0）**。**这是摆件问题，不是求解器问题。**
2. **算法/实现层（次因）**：即便把孔挪到开阔地，**贪心/协商布线器都按最短路走**——第一条车道贴孔行向东，其 0.45 mm 硬膨胀**把其余车道的南向出口整条封死**。**梳子形必须显式给坐标**，靠代价函数搜不出来。
3. **判据层（非堵点）**：判据 rev=6 只读、口径未改；**不为变绿缩口径**。

**缺口在哪层**：核心缺的是『**坐标化线束生成**』（把人画梳子的规则一次落到 x/y 的工件），**非判据、非容量** ⇒ 与在册 `C-B2UP-1` 定义**逐字一致**；本件把其**几何入口（A 侧 `_P` 出口）**量清并给出**唯一可行画法**。

## 一次实现（本轮唯一）

- **ECO-A**：A 侧 16 枚**本网**入口孔一次重排为单行 y=57.60（x=85.60+0.70k），随后**单次**顺序构造。
- 结果：**routed 2/16** · 末闸互距 0 违规（min 0.4528）· 障碍 0 违规 · 端点位移 0。
- **判**：**非见证**（红线：不得以 2/16 充见证）。ECO-A 落位**保留**为下一轮显式梳子构造之输入。
- **buildability = `relocation_listed`**：仅本 16 网之 A 侧过渡孔（sites_phys.json → `a_entry_ecoA_row_v1.json` 16 点）；**他网 0 改动** · **球位/连接器焊盘 0 位移** · 16 段 F.Cu 扇出须按子步骤 F 重画。属 L2『过孔策略』自裁面 + #K2-133 N1『只动本网几何』（**待监理批执行落板**）。

## 下一步（待监理批 · 只做一次）

1. 按 ECO-A 落位表落 A 侧 16 孔（本网几何）。
2. **显式梳子构造**（一次性落坐标，不用搜索）：k=1..16 取 A.x 序 · 水平线 y_k=58.80+0.435·(16−k) · A 孔→(x_k,y_k)→东行→东通道第 s_k 列（『深线用东列』定死）→北行→西行接 B 孔。
3. 一次末闸 `v3.exact_gate` ⇒ 交 **16/16 见证 + buildability.mode="relocation_listed"**；若 B 侧仍冲突 ⇒ 出**单一卡点 + 归属**。

## 边界

冻结四源不改 · `criteria/` 只读 · **未烙板** · 未派 WORKER · 未改生成器/SPEC/原理图 · 临时仅 `/tmp/opencode` · **未以 16/16 布通或 2/16 充见证** · 未以有界搜索冒充证书 · C-w 未申报未执行 · 未新增待裁锚。owner 闸口 = 0。

—— ENG（ARCHER）· 2026-09-22 · 冻结四源 4/4 未动 · 判据 rev=6 MATCH · l8 `7a5c8991`
