dataxcash/hw_ic_k2/pm_gate/artifacts/k2_v4/L4/E3-standard-call-l8-20260922-pf/README.md

# K2 R260 · ②-UP **独立方法实测（协商拥塞束布线器）** · 2026-09-22

**方法**（`k2/tools/k2_p4_b2_in5_pf_lane_router_v1.py`）：PathFinder 型**协商拥塞**——
每轮对 16 网**全部**各求一条最短路（拥塞以费用 present+history 表达）· **本轮内已布道按硬半径硬禁** ·
**固定几何序**（B 锚 y 降序 = 南锚先布之洋葱层序 · **非扫描**）。
与既有 `construct_router.py`（**次序枚举 + 硬避让**，20 序旋扫 · 最好 12/16）**方法不同**。

| 件 | 口径 | routed | 端点位移 | 障碍净距 | **车道互距 (要求 ≥0.435)** |
|---|---|---|---|---|---|
| `wo_pf_sep022_c05_n40.json` | cell 0.05 · 硬禁半径 0.2175 · 40 轮 | **16/16** | 0.0 | 0 viol (min 0.1003) | **18 viol · min 0.0354** |
| `wo_pf_sep044_c05_n40.json` | cell 0.05 · 硬禁半径 0.44 · 40 轮 | **16/16** | 0.0 | 0 viol (min 0.1000) | **31 viol · min 0.0000** |

**判决（如实）**：
- **非见证**：两件**均不满足** ②-UP 之「车道互距 ≥0.435」⇒ **不得**作 (a) 见证或里程碑。
- **决定性事实**：**16/16 全部同时布通**（连接层/拓扑层可达；端点位移 0；对障碍 0 违规）⇒
  **几何上不存在「任何分配都不可能」**（与 `K2_R260_..._CENSUS` 之 F-3/F-4 一致）。
- **残余缺口精确定位**：硬禁半径 0.44（**cell 级**分离已达标）仍出 **0.0000 连续隙** ⇒
  缺口 = **「cell 级分离 ≠ 段级（连续）分离」之收敛实现**（需 cell ≤0.03 或**连续推挤**）。
- **禁**：不得据本件作里程碑；不得据此开工；本件仅为**卡点归因证据**。

---

## 追加（**真硬分离** · 0 违规 · 本轮关键指纹）

把「轮内已布道」由费用罚（1e9）改为**真硬（∞）**后，得到**自证合法**之解（`v3.exact_gate` 复核）：

| 件 | routed | 车道互距 (要求 ≥0.435) | 对障碍 | 端点位移 |
|---|---|---|---|---|
| `wo_pf_hardsep045_c05_n30_legal12of16.json` | **12/16** | **0 viol · min 0.4528 ✅** | 0 viol (0.1003) | 0.0 |
| `wo_pf_hardsep045_adaptivepri_c05_n40_legal12of16.json`（失败网优先重排） | 12/16（或 4/16 交替） | **0 viol · min 0.4528 ✅** | 0 viol | 0.0 |

**合法 12 集 = `{1_N,2_N,3_N,3_P,4_N,4_P,5_N,5_P,6_N,6_P,7_N,7_P}`**；
**被排除 4 集 = `{0_N,0_P,1_P,2_P}`** —— 与既有（次序枚举）顺序布线器 12/16 之**成功集/失败集逐条相同**。

**指纹（决定性）**：
- 两轮「失败网优先」时，**只布通 4**（即 4 集），其余 12 全失败；否则布通 12。⇒ **12 集 ⊻ 4 集**（从不同时），两向皆 **0 违规**。
- ⇒ **两独立方法（顺序硬避让 / 协商拥塞真硬分离）落在同一堵墙上、且墙的位置逐条相同** ⇒ 与 **F-6（A/B 嵌套序 4 组相邻互换）**一致 ⇒ **强候选「守恒级不可行」结构性机制**。
- **但**：本指纹为**启发式实证**，**非严格证书**（自由域为绕墙环带 ⇒ 理论上可借绕行换序）；严格证书需「**束序不变量**」之数学证明或**精确 MILP**。
