dataxcash/hw_ic_k2/pm_gate/artifacts/k2_v4/L6/DELIVERY/README.md

# K2 P5 交付封装 — `k2_v4_8L.l7`（受审板 `c5a7df90aadb66e0`）

| 件 | 说明 |
|---|---|
| `k2_v4_8L.l7_gerber_package.tar.gz` | 完整交付包（= `../jlc_package/`，49 件） |
| `SHA256SUMS.txt` | 逐件 sha256（相对 `L6/`） |
| `../jlc_package/MANIFEST.json` | 机读 MANIFEST（board/pro sha · 命令 · 件表 · DFM 汇总） |
| `../jlc_package/ORDER_NOTES.md` | 制造备注（JLC HDI 通道） |
| `../jlc_package/DISCLOSURE.md` | 具名披露（167 warning / OUT #5 / F-9 / L-1 / P5 新项） |

- DFM 对 JLC HDI 通道：**16 PASS / 1 ACCEPT / 0 FAIL**；N-01：平面层 4/4 `G36>0`；钻孔 749 孔。
- 判据锚 rev=3 · 冻结四源未动 · 打包确定性（固定 mtime/uid/gid ⇒ tar sha 可复现）。
- 下单/报价/交期 = 商务，不在 ENG 范围（#15）。
