dataxcash/hw_ic_k2/docs/K2-BLOCKER-REPORT-aprime-a4-retraction-20260929.md

# 卡点报告（**自我更正 / 撤回**）· A⁴ 刚性下移"过闸"结论**作废** — 承 #K2-398 §二

> **本件为 ENG 主动更正**：`#K2-397/#K2-398` 所依据的「**刚性整簇下移 1/2/4mm 过闸零新增**」= **假结论**。**A⁴ 未跑**。

## 一、错在哪（机理）

- `regen.mech_probe_moves` 在 **gen_v5 失败**时走**早退分支**：`{"gen_exit": rc, "mechanical_violations": {}, "gen_failed": True}`。
- 我上一窗的 dy 扫描**只看了 violations 字典为空**、**没查 `gen_exit`** ⇒ **把「生成失败」读成了「干净通过」**。
- **真值（加 `gen_exit == 0` 门槛后重扫）**：**dy = 0.5…11.0 mm 全部 `GEN_FAIL`** ⇒ **没有任何刚性 dy 合法**。
- **根因机证**：shadow ＋ `edit_placement_at(全部 25 件, [0,+4])` ＋ `gen_v5` ⇒ `rc=1`：
  `❌ 写盘阻断 (fail-fast): [S1 PAD_OVERLAP] C88/1 … 与 J13/2 … 重叠 dx=0.600 dy=0.060 (容差 0.01)`（**真铜重叠**）。

## 二、为什么这很重要（**基座分歧**）

- **闸探的是 shadow/gen 板；考题链跑的是 l14** —— 两块板**布局不一致**（在册：`ECO-K2-0004 §6c`）⇒ **一板的合法动作会被另一板拒**。
- ⇒ **A⁴ 的「可行动作」必须先把基座（gen 板 vs l14）钉死**，否则任何 dy 结论都不成立。

## 三、撤回与保留

| 项 | 处置 |
|---|---|
| R1094「刚性下移过闸」 | **撤回**（作废） |
| R1094 逐件结论（22/25 下移 · U1/D2/U2 无步 · **因 U1 先行试探撞 J9**） | **保留**（该条独立成立） |
| 「逐件族出不了整簇解」诊断 | **保留** |
| **A⁴ 链跑** | **不跑**（#K2-398 §二前提不成立） |

## 四、请裁（三条诚实路线）

- **A**：先钉**评估基座**（闸跑 gen 板 vs 考题跑 l14），给出**基座一致性**结论；
- **B**：若以 **l14** 为基座 ⇒ 需**新的具名仪器**（在 **l14＋位移**上过闸），而非 shadow；
- **C**：原令是「簇**及围邻**下移」而**非必然同一位移** ⇒ 可用**逐件推导 ＋ 连贯播种次序**（先动连接器、后动簇）作在册替代。

- 本窗**零考跑 · 零板改**；板面冻结 · 四源 4/4 · 判据表一毫米不改 · 禁 WORKER。
