dataxcash/hw_ic_k2/docs/K2-BLOCKER-REPORT-aprime-triple-prime-edge-iv-c-20260929.md

# 卡点报告 · EDGE IV 步(C)＝**判否**（检测器首版不实 ＋ 拥有件无合法步）⇒ 需 (B) — #K2-395 §二

- 授权：#K2-395 §二（**(C) 先行 → 余者 (B) 一次有界扩集**）；本窗**零 exam 跑**、**零板改**
- 件：方案件 `L2/A_DOUBLE_PRIME_PLACEMENT_POUR_PLAN_v1.json :: edge_iv_C_status` · 预检 `L2/EDA_ENG_PORT_REACHABILITY_PRECHECK_A_TRIPLE_PRIME_v1.json`

## 一、试过什么（(C) 的两半）

### (C-a) 检测器（"哪块 pad 被埋"）
- **首版**：自写**几何**规则 `route.pad_clearance_violations`（pad ↔ 异网铜最近间隙 < 0.20mm ⇒ 记一条）。
- **实测 ⇒ 不实**：在**干净的 l14 参照板**上误报 **366** 条（还出现负间隙），而 A‴ 擦铜板上的**真**埋压集只有 **7 个端点** ⇒ **量级性失真**。
- **处置**：**撤回该函数、未接线入闸**（不合规的规则不进闸）；`git` 树已还原。**结论**：检测器**必须用迷宫自身的模型**（`k2_p4_mroute_v1.snap_node`／`_mark`）——而**端口可达性预检**（R1088 件 1）**已经就是**这个模型，它**具名**了 7 个埋压端点。

### (C-b) "微调拥有埋压端点的成员件"
- 具名埋压端点（框内侧）：`(31.837,53.75)`（**U1** 焊盘 / NRST）· `(31.837,51.75)`（**U1** 焊盘）· `(34.25,56.163)` · `(34.05,58.5)` · `(47.4,44.0)`。
- **拥有件＝U1**；而 U1 在 A‴ 逐件推导中**一个 SE 格步都不合法**（R1078 已证：k=1,2 真铜重叠；k=3 阻焊桥；k=4 桥＋clearance；k=8 gen 失败）。
- ⇒ **"微调拥有件"对 U1 系端点无合法步可走** ⇒ **(C) 对该案判断为"已穷尽"**（不是没做，是**无合法动作**）。

## 二、为何不通 / 缺口在哪层

| 层 | 结论 |
|---|---|
| **检测器** | 手拧几何**不可靠**（366 vs 7）；**正确检测器＝迷宫自带模型**（预检已实现） |
| **合法动作** | 拥有件 **U1 无合法步** ⇒ (C) 无可执行动作 |
| **缺口层** | **成员集/块边界层**（不是布线层）⇒ 需 **(B) 一次有界扩集** |

## 三、下一步（依 #K2-395 §二.2 · 请裁）

**申请批准 (B)**：把**压住这些端点的围邻并入成员集**（`region_select` **独立重跑**）→ **块边界重画** → **C7 HS 互斥重校** → **C6 重述「新框外 diff=0」**；**一次有界 · 禁二次扩集**（防级联）；随后**过验再申请** `N=1` 末跑（九行 ＋ 几何摘要）。

- **本窗零考跑**（现在跑＝同因重跑，违 §二.4）；板面冻结 · 四源 4/4 · 判据表一毫米不改 · 禁 WORKER。
