dataxcash/hw_ic_k2/docs/K2-BLOCKER-REPORT-aprime-doubleprime-attempt3-20260929.md

# 卡点报告 · exam A″（清空重解）attempt 3 — 授权窗结果 ＋ 归因

- 授权：#K2-387（run 1/1）；链条：`wipe_resolve`；产物目录 `/tmp/opencode/aprime_final_v2`
- 判卷：`L2/EDA_ENG_EXAM_A_DOUBLEPRIME_ATTEMPT3_VERDICT_v1.json` · 记录：`..._ATTEMPT3_RECORD_v1.json`
- 证书：`L2/EDA_ENG_EXAM_A_DOUBLEPRIME_CONSERVATION_CERTIFICATE_v2.json`
- 板面：**零改动**（板只在 `/tmp`）· 冻结四源 **4/4** · 无 Gerber／下单／WORKER

## 一、人类口径三问

1. **信号怎么走**：把这小片器件挪几毫米后，先把它压到的铜**整块清掉**（615 段 ＋ 95 孔），
   再在**划定框内**用标准流程（迷宫 §20 成品）把 22 条网重连，然后复敷铜、判分。
2. **挡路的是什么**：两件事——
   （i）**22 处线头接不上**：迷宫说这些点**找不到空起点／空终点**（`no-free-start-node` 16 · `no-free-goal-node` 6）；
   （ii）**两类违规是「重连的副产物」**：`isolated_copper ×3`（12V_IN 敷铜成了孤岛）＋
   `solder_mask_bridge ×2`（挪位后的 **U1 焊盘 11/12 ↔ J9 焊盘 1 彼此太近，阻焊开窗粘在一起**——**焊盘对焊盘**，不是铜对焊盘）。
3. **人类方案（下次该怎么做，确定性、非搜参）**：
   - **放置层**：挪位时必须保证「被挪的焊盘不落进任何异网焊盘的阻焊间距内」——这条是**几何约束**，排除 `solder_mask_bridge`，任何布线器都办不到；
   - **端口层**：把框边被切开的线头**当「合法端口」直接交给迷宫**（起点／终点就用这些 stub），不要跨块去**重新猜目标点**——排除 `no-free-start/goal-node` 这一类。

## 二、本窗试过什么 / 为何不通 / 缺口在哪层

| 项 | 动作 | 结果 |
|---|---|---|
| (a) 敷铜孤岛重连 | 复铜后检孤岛，每岛就近连回同网最近焊盘（同一迷宫 · 一次） | **检出 3 · 规划 2 · 已应用**，但**终板 DRC 仍报 3 × `isolated_copper`** ⇒ 该类**未动** |
| (b) 阻焊桥预检 | 落板前比「**新铜** vs **异网焊盘**」间距，不足即 `REFUSED` | **未触发**（apply 成功）；终板**仍报 2 × `solder_mask_bridge`**，且实测是**焊盘对焊盘** ⇒ 该守卫**看不见这类几何**（比错了对象） |
| 净效果 | — | C1 **22→22** · C2 类别**不变** · 几何 **141→143** |

**缺口在哪层**：**不在容量**（域内 **93.5%** 空闲，`L2/C1_CAPACITY_READING_v1.json`）、**不在判据**；
在 **① 工具策略层（端口／缝合策略）＋ ② 放置层（挪位后焊盘间距）**。**与 attempt 2 同因** ⇒ 依 **§17.4 换手段（不换目标）**。

## 三、两件自登（本窗、加法式、未占跑次）

1. **实现缺陷（本窗阻塞、已同窗修死）**：孤岛重连分支**从未真正执行过**——首次实跑即
   `NameError: _pcbnew`（同分支 `collections` 亦未导入）。源于旧回归**只做源码字符串检查**、不跑分支。
   ⇒ 已改（模块 import ＋ 内联 `import pcbnew`，**不改方法**），并**新增作用域感知 AST 回归**
   `test_C385_the_island_branch_reads_no_undefined_names`（**改前必红 · 改后绿**）；套件 **75/75**。
   崩溃那次**无产物**（stdout 0 字节）⇒ 依 #K2-377 §四.2 **不计跑次**。
2. **判卷漏行（C36 复发 · fail-closed）**：A″ 链只出 **8 行**（C1–C7／C9），**缺 C8**（成员零越框）。
   因 `C8_members_inside_frame` 只在 **`relocate_block_chain`** 里算，**A″ 链（`wipe_resolve_chain`）没有**；
   C36 的源码字符串测试是在**整份 regen.py** 里找字符串，故在**别的函数**里找到就绿了 ⇒ **同一盲区**。
   ⇒ 依 #K2-383 §三.3／#K2-385 §五.4：**缺行 = 不受理**；本窗 FAIL 即停，**不在窗内再改**，交监理裁。

## 四、独立审计发现（本窗发现，未修，属越窗）

- `tools/eda_eng/regen.py :: exam_a_chain` 读取**未定义名** `rp`(491/494) 与 `blocked`(493/507)——与本窗修掉的是**同一类缺陷**，**既有、非本窗引入**。
- 可达性：考题 A 现走 `relocate_block_chain`，`exam_a_chain` 未被命中；它是考题 B 产品链的回退路径。
- 处置：**本窗不修**（越授权范围 · fail-closed 只报不裁）；建议最小修＝ `blocked = []` ＋ 落板前定义 `rp`（照 `relocate_block_chain` 写法）。

## 五、入口闸事实（非违规，供监理）

CLI 的 `wipe_resolve` 分支**不调用** C34 §20 闸（只有 `c17v1` 分支调用）。#K2-387 未对本链要求闸，
但按 C30 判据「闸须守**实际开跑的那道门**」——**本入口是一道未上闸的门**，如实登记。

## 六、结论（二值）

- **本窗授权跑 = 1/1（有效跑）· 判 **FAIL**；且判卷**缺 C8** ⇒ 依 fail-closed 该收执**不受理**（C36 复发）。
- **同因再 FAIL**（工具策略／放置层）⇒ 触发 **§17.4 换手段**；**无新手段即不再跑**。
