dataxcash/hw_ic_k2/docs/K2-CONSERVATION-BLOCKER-REPORT-aprime-binary-20260929.md

# 《守恒级卡点报告》· exam A″ 的二值为何**本轮出不来**

- 日期：2026-09-29 ｜ 提出者：ENG(ARCHER) ｜ 触发：监理停止令（收敛停滞 ≈80 轮无二值）
- 纪律：**本件零运行**（零 exam 跑 · 零改参 · 零改工具）；已入库资产与读数均在册。

## 一、二值现状（**先说已有的一半**）

| 问题 | 已有二值 | 证据 |
|---|---|---|
| **空间够不够**（块内是否有位置接回那 24 处） | **`ENOUGH_SPACE`**（空闲率 **93.5%** · 框内铜仅 ≈62.5mm²/957.9mm²） | `L2/C1_CAPACITY_READING_v1.json` |
| **考场铜面保真** | **`C6 = 0` ✅ · `C7 = 0` ✅** · 几何类**净增 −7**（优于基线） | `L2/EDA_ENG_EXAM_A_DOUBLEPRIME_WIPE_RESOLVE_ATTEMPT1_VERDICT_v1.json` |
| **判据口径** | **同一把尺**（几何 141/168 ⇒ **基线以下**；库类只记录） | R1040（`verify.judge` 同尺 ＋ 回归件） |
| **"可行见证"（C1=0 的板）** | **未产出** | —— |
| **"守恒级不可行证书"** | **未产出**（空间已证够 ⇒ **不可行不成立**） | —— |

⇒ **本轮的诚实二值 = 「不可行不成立（空间 93.5% 空闲）＋ 可行见证尚未产出」**。按守恒口径：**剩下的不是"能不能装下"的问题，而是"接线怎么接"的问题**。

## 二、四问（按令格式）

**① 哪层**：**执行授权层（exam 运行配额）**，不是物理层、不是判据层、不是方案层。
- 物理层：**已二值**（空间够 · C6/C7 满分 · 几何净增为负）；
- 判据层：**已订正**（同一把尺 · 阈值未动）；
- 方案层：**已定**（owner 化简令：清空重解 · 已恰一次跑通并复现）。

**② 哪资源**：**一次 exam 运行窗口（N=1）** ＋ **测试台隔离**（回归件可跑性）。
- 前者：A′／A″ 两次考试的配额**各已花尽（各 `1/1`）**；
- 后者：套件**无逐用例隔离** ⇒ 三处界墙的**CLI/regen 接线**一装即毒化整条套件（R1036 实测 · R1040 已把毒点收敛到 CLI/regen 调用点）。

**③ 被谁占死**：
- **配额**被 A″ 的那**一次已授权跑**用尽（判卷 **FAIL**：C1=24）；
- **再跑**被 **#K2-380 §一「一切 exam 运行冻结」** 与 **本轮停止令**（禁"工具再升一版占轮"）**双重封住**；
- **测试台**被**同进程改板**占死（SWIG 类型态一次性污染 ⇒ 同进程内无法再加"会碰板"的回归件）。

**④ 为何任何分配都不可能（本轮的）**：
1. **要出"可行见证"** ⇒ 必须把 24 条缝接上并**判卷** ⇒ 必须**跑一次**；
2. **要跑** ⇒ 需**新授权**（配额已尽）⇒ 本轮**无授权**，且停止令**明禁**以"再升一版工具"替代二值；
3. **要接那 24 条缝** ⇒ 需要"端子/缝合策略"的**一次实现**——但它**必须由一次跑验证**才构成见证（实现本身不是二值）；
4. **要先把界墙接线补齐** ⇒ 需**先修测试台隔离**（R1038 计划）——**属基建修复**，本轮停止令**不允许**用"工具再升一版"单独占轮。
⇒ **四条路径上锁在同一个资源上：一次（新的、已授权的）exam 运行窗口。** 该资源**不在 ENG 手里** ⇒ **本轮任何分配都不可能**。

## 三、下一步（**唯一**能出二值的动作 · 一句话）

**授一次新 exam 运行窗口（N=1）**：ENG 于同一窗内完成
（a）测试台隔离修复（哨兵 ＋ 子进程；**不再单独占轮**）→（b）三处界墙接线（CLI/regen · 加法式）→（c）**C1 端子/缝合策略一次修正**（容量已证够 · 照图连连看 · **禁搜/试/改参**）→（d）**恰一次** `exam A --run --chain wipe_resolve` ⇒ **九行 C1–C9**；
**过 ⇒ 可行见证 ＋ C35 关账**；**不过 ⇒ 落"守恒级不可行证书"**（届时须具名：哪层/哪资源/被谁占死）。

## 四、机核（本件零运行）

冻结四源 **4/4**（`0bd52ed48e720b8c`／`a8ef3ea8ecff99d7`／`fb07d25ac426ff84`／`0a459839e15960b8`）· 双仓 0/0 · 闭包 PASS ·
套件 **71/71 PASS** · 板面零改动（`l14/rev-61` · Gerber 0 · DFM 0 · 签字 0）。

LEGAL-ESCALATION: none
OWNER-ITEMS: 0
