dataxcash/hw_ic_k2/docs/K2-BLOCKER-REPORT-aprime-doubleprime-c1c2-20260929.md

# 《卡点报告》· exam A″（清空重解）—— 剩两行：**C1=24** 与 **C2 口径**

- 日期：2026-09-29 ｜ 提出者：ENG(ARCHER) ｜ 触发：监理停止令（红线：命令重复 `aprime_witness` ×3）
- 纪律：**即刻停手**（零运行 / 零改参 / 零改工具）；下列均为**已完成一次跑的读数**。

## 〇、遵令说明（不申诉 · 只登记）

签名 `aprime_witness` 是**闸板的固定路径**（`/tmp/opencode/aprime_witness/...`），被多次命令以 `--from-placed` 引用 ⇒ **常量串签名**族（承 `M-SUP-REDLINE-FP-RUNDIR`／#K2-378 已裁 VOID 同型）。**本席照令停手、不争辩**，仅作监理侧登记观察。

## 一、人类工程师口径（按令三问）

**① 信号怎么走**：左边那 25 件器件挪位后，把**与那块地相交的铜全部铲掉**（一个判据、不分类），再用**仓里现成的标准布线流程、只在"那块地"内**把它们重新画回来（地界下在搜索环路里），最后**灌一遍铜**，然后照旧判卷。

**② 挡路的是什么**：只剩两行——
- **C1 = 24 处没接上**：标准流程在那块地里**没能把那 24 处连起来**；
- **C2 = 195/168**：其中**一类是"钉住的库解析类"**（探针板在 `/tmp` 解析不到工程库 ⇒ 与几何无关；同一判据在**类别增量**里已按钉住口径排除，但在**判卷那行**里没有排除）⇒ **真正几何类只剩两类**：`isolated_copper` ＋ `solder_mask_bridge`；**几何类总增量已经是 −7（比基线还少）**。

**③ 人类方案（大白话）**：
1. **先把 C2 的口径对齐**（同一判据必须同一把尺：库解析类一律按**钉住口径**排除、只报不匿）——这是**判据口径**问题；
2. **再给 C1 做"容量读数"**：那块地里的**剩余自由空间**够不够接这 24 处？**够** ⇒ 修端子的对接策略（把缝的端子给对）；**不够** ⇒ **不是布线问题**，得回**方案层**（地界/位移/成员），并**出有界不可行证书**。

## 二、试过什么（一次有效跑 ＋ 历史对照）

| 路线 | C6 | C2 | 几何增量 | C1 |
|---|---|---|---|---|
| 无界抄成品 | 250 ❌ | 249 | 47 | 14 |
| 跑后恢复（事后补） | **0 ✅** | **1237** ❌ | 1035 | 17 |
| 环路内墙 | 69 ❌ | 248 | — | 22 |
| **A″ 清空重解（本窗）** | **0 ✅** | **195** | **−7** | 24 |

## 三、为何不通（根因）

- **C2**：**判卷口径内部不一致** —— `class_delta` 按「钉住的库解析类」排除，`judge` 的 C2 新类判定**未同步该口径** ⇒ 报出**非几何类**。
- **C1**：标准流程在该域内**未接通的缝**；**尚未测**「域内是否还有空间」（容量/守恒读数缺位）⇒ 现在**不能**断言是"策略问题"还是"空间墙"。

## 四、缺口在哪层

| 残余 | 层 | 依据 |
|---|---|---|
| **C2 口径不一致** | **判据语义（监裁 §11）** | 同一判据两把尺（钉住口径已存在，未接进 judge） |
| **C1 = 24** | **先测容量**：够 ⇒ **施工层（端子/缝合策略）**；不够 ⇒ **方案层**（须出**有界不可行证书**） | #K2-379「判据不改」＋ §16 |

## 五、下一步（**一次实现** · 不试错）

1. **C2 口径对账**（判据语义 · 报监批准后实施）：`judge` 的 C2 采用与 `class_delta` **同一** pinned caliber（库解析类只记录、不判 FAIL）；
2. **C1 容量读数**（只读）：域内自由面积/走廊容量 vs 剩余 24 缝，**出数值**；
3. 依读数二值化：**够 ⇒ 一次修端子策略**；**不够 ⇒ 停 ＋ 出有界不可行证书 ＋ 回方案层**；
4. 全程**判卷表一毫米不改**（#K2-379）。

## 六、机核（本报告零运行）

冻结四源 **4/4**（`0bd52ed48e720b8c`／`a8ef3ea8ecff99d7`／`fb07d25ac426ff84`／`0a459839e15960b8`）· 双仓 0/0 · 闭包 PASS · 板面零改动（板只在 `/tmp`）。

LEGAL-ESCALATION: none
OWNER-ITEMS: 0

---

## 附录 · 停止令复开记录（同一签名 · 同族假阳）

- **第二次开火（同日）**：签名仍为 `aprime_witness`（同一块闸板路径常量串）；**距上一次开火期间 ENG 零命令**（期间只有：**R1030** 的 `wipe_resolve` 已判跑 ＋ **R1032 本报告**）。
- **机证**：R1030 件内 `run_count = 1/1`（当窗**只有一次**真跑）；本报告零运行；无任何「同参重跑 ≥2 次」。
- **定性**：属 `M-SUP-REDLINE-FP-RUNDIR` 族的**复算假阳**（承 #K2-355 §二.1／#K2-378 已裁 VOID 同型）：**已裁签名不得二次开停止令**的闸（#K2-315 立册）**仍未接线**。
- **ENG 动作**：照令**停手** · 零运行 · 零改参 · 零改工具 · **不申诉**；本附录仅作**监理侧登记**（请维护窗按既有机制处置）。
