dataxcash/hw_ic_k2/docs/K2-BLOCKER-REPORT-aprime-c35-inloop-20260929.md

# 《卡点报告》· 考题 A′（框界）—— 卡在**「框界下晚了」**（方法层）

- 日期：2026-09-29 ｜ 提出者：ENG(ARCHER) ｜ 触发：监理停止令（红线：命令重复 `aprime_c17v1c` ×5）
- 纪律：**即刻停手**（零运行 / 零改参 / 零改工具）；下列事实均为**已完成运行的读数**，不含新跑。

## 〇、遵令说明（不申诉 · 只登记）

签名 `aprime_c17v1c` 是**同一份工作目录路径**（产品跑 / 框界 / DRC / 判卷四次命令都指向它）⇒ 属**常量串签名**族（承 #K2-355 §二.1 · `M-SUP-REDLINE-FP-RUNDIR`）。
**本席照令停手、不争辩**；此条仅作**监理侧登记观察**。

## 一、人类工程师口径（按令三问）

**① 信号怎么走**：主芯片左边那一小片器件（25 件）要整体挪几毫米，它们身上的**若干根线必须重新接**——一部分接到**框边**（那儿不动），一部分在**框内**接到挪过位的焊盘。

**② 挡路的是什么**：照抄仓里现成的重布工具，**接得好得多**（断线 40→14），但那件工具**没有"块"的概念**：它把受影响的那几根线**整根**重画，**连框外老远（最远 84mm）也一起改**。而考卷要求「**框外的铜一点不能动**」。
本席先试了**跑完再把框外恢复原样**：**框外确实零改动了（C6 250→0 ✅）**，但代价是——**它把产品靠"出框"才接通的那几根线又撕开了（断线 14→17）**，而且**恢复回来的旧铜与产品在框内新铺的铜打架**（违例 **249→1237**）。⇒ **事后恢复不是"框界"，是"先让它乱跑再擦屁股"。**

**③ 人类方案是什么（一次实现）**：**把框界下到"画线的那个环路里面"** —— 在工具的**迷宫布线**处**直接告诉它：不许越过板框 ∂R**（越界即不选那条路），**而不是**等它画完再裁。
这样：**框外的铜从头到尾没被碰过（C6=0）**，**框内的线**也**不必**再被我"恢复"动作撕开（C1 不再反升）——**同一道界、下在源头**。

## 二、试过什么（逐条 · 均为在册读数）

| # | 做法 | 读数 | 结论 |
|---|---|---|---|
| 1 | 抄成品（无界） | C1 **14** · C2 **249** · 几何增量 **47** · **C6 250 ❌** | 方法对；**范围出框** |
| 2 | 收 `--margin`（既有参数） | 机证：241 件框外新铜中 **181 件离框 >3mm**（最远 **84mm**） | **不可达 C6=0**（已否决） |
| 3 | **事后恢复框外铜**（C35 v1 · 薄封装） | **C6 250→0 ✅**，但 **C1 14→17** · **C2 249→1237** | **得保真、坏连通** ⇒ 界下晚了 |

## 三、为何不通（根因）

**"恢复"与"重布"在语义上互相打架**：
- 产品**靠出框**把那几根线接通 ⇒ 恢复框外 = **把它的解法撤掉**；
- 恢复回来的旧铜**与新铺铜共处**同一空间 ⇒ **净距冲突**（1237 违例）。
⇒ **框界是"路由约束"，不是"事后修补"**；修补式界的代价是**把连通性当成牺牲品**。

## 四、缺口在哪层（层判定）

**方法层（ENG 工件层 · C35 的具体补法）**：缺的是**把作业域作为硬约束传进迷宫**的能力 ——
补法＝在 `tools/k2_p4_mroute_v1.py`（仓内精确放行闸迷宫）**加"框界墙"**：越 ∂R 的格/缝**一律不选**；`k2_reroute_affected_v2.py` 侧只传框，**不改方法**。
**不属**方案层（框/位移已定且合法）、**不属**判据层（#K2-377 §二 已明令 C6 **不放宽**）。

## 五、下一步（**一次实现** · 不做试错）

1. **迷宫加框界墙**（`k2_p4_mroute_v1.py`）：搜索格 / via 站点 / 修补贴片**一律夹在 ∂R 内**；
2. **产品侧只传框**（薄封装改为"传参"而非"事后恢复"）；**保留原方法**（§20§4）；
3. **前置**：preflight P1/P1b PASS ＋ **框内容量/守恒读数**（答不出 ⇒ 停手不跑）；
4. **恰一次** ⇒ **九行 C1–C9**（含 C6=0 · C8）；**FAIL ⇒ 停 ＋ 回方案层**；
   同因再 FAIL ⇒ §17§4 **换手段**。

## 六、机核（本报告零运行）

冻结四源 **4/4**（`0bd52ed48e720b8c`／`a8ef3ea8ecff99d7`／`fb07d25ac426ff84`／`0a459839e15960b8`）· 双仓 0/0 · 闭包 PASS · **板面零改动**（板只在 `/tmp`）。

LEGAL-ESCALATION: none
OWNER-ITEMS: 0
