dataxcash/hw_ic_k2/docs/K2-BLOCKER-REPORT-aprime-method-layer-20260929.md

# 《卡点报告》· 考题 A′（左区域块内重排）—— 卡在**方法层**

- 日期：2026-09-29 ｜ 提出者：ENG(ARCHER) ｜ 触发：监理停止令（红线：命令重复 `aprime_cmd.sh` ×3）
- 纪律：**本报告即刻停手**（零运行 / 零改参 / 零改工具）；下列事实均为**已完成运行的读数**，不含新跑。
- 对象：`EDA_ENG_EXAM_A_PRIME_ATTEMPT{1,2,3}_VERDICT_v1.json` · `ECO-K2-0004`

---

## 〇、遵令说明（不申诉、只登记）

停止令签名为 `aprime_cmd.sh`。该串是**同一份环境变量文件**（`MVS`＝逐件位移表／`MEM`＝成员表）被 3 次链跑命令以 `. /tmp/opencode/aprime_cmd.sh` 形式引用所致 ——
**不是** 3 组不同参数、**不是** 改参重跑（三次运行的差别是：attempt1 首跑 · attempt2 **具名缺陷修正**（端口判据／IU 切分）· attempt3 **新增能力**（有界修复））。
按 **#K2-355 §二.1 / #K2-364** 同族，运行目录/常量串签名属**假阳性族**（`M-SUP-REDLINE-FP-RUNDIR`）。
**但本席照令停手，不作争辩**；此条仅作**监理侧登记观察**，请维护窗按既有 `VOID_ALERT_TAGS` 机制处理。

---

## 一、人类工程师口径（大白话 · 按令三问）

**① 信号怎么走**：左下角那一小片器件（20 件，加框内 5 个邻居＝25 件）要朝东南挪一点（N5 方向）。它们身上的铜（走线/过孔）原来连在板上别处；挪完之后，**这些铜必须重新接起来** —— 一部分连到框边（那里是"固定端口"，不动），一部分在框内重新连到挪过位的焊盘。

**② 挡路的是什么**：挪完之后，**框内的自由空间不够**。具体卡在 4 条网：**GND · NRST · SWCLK_BOOT0 · SWDIO**。
- 3 条是**间隙不够**：真形净距判卷器（正确、保守）算出任何走法都会比 0.175mm 更贴近别的网的铜 ⇒ 拒；
- 1 条是**落点被埋**：要接的那个点本身落在别人的铜里。
- **不是拓扑问题**：把这条边换成"另一对端子"再试（有界修复）**8 次全不中**。

**③ 人类方案是什么（一次实现）**：**别把整块的铜全铲掉重铺**。
人类工程师的做法是：**只剪断"被挪位的器件碰坏的那几段线"**（剪），**没坏的线原封不动**；然后把剪断处的线头**当成孤岛**，用**最短生成树把孤岛接起来**（接），接不上的地方**只在那一小块做有限修补**（补），最后把线**规整化**（规范化）。
—— 这正是**本仓已有的成品**：`tools/k2_reroute_affected_v2.py`（**C17 v1**：`clip → islands → MST stitch → snap → bounded repair → normalise`）。

---

## 二、试过什么（三轮 · 每轮一处**具名**改动）

| 轮 | 改动（具名） | 读数 | 结论 |
|---|---|---|---|
| **A′ attempt 1** | 逐件位移 ＋ **整块铜删除重铺**（C33 首版）· 域＝冻结框 | 18/22 网布通 · C1 断 40 · **C6 diff 1** | 方法可用；保真差 1 件 |
| **A′ attempt 2** | ①**端口判据**改为「∂R **实际线段**上」（原只查无限直线 ⇒ 角外远端被误当端口 ⇒ 布线出框）②切分改 **IU 整数域**（`clip_iu`） | **C6 1 → 0 ✅**；C1 仍 40 | 两处**真缺陷**已修死 |
| **A′ attempt 3** | 新增 **有界修复**（同连通块间取次优端子对，≤8 次） | **repairs = 0**；读数与 attempt 2 逐项相同 | **空结果 = 信息**：堵点不是拓扑 |

## 三、为何不通（根因 · 层判定）

**卡的既不是"方案"（框/位移已定且合法），也不是"参数"（pitch/间隙已按实测取定），而是"M3 的作业方法"**：

1. **方法错配**：现链走的是「**整块铜删除 + 全量重铺**」——attempt 3 一次就删了 **615 段 + 95 孔**，再在框内**从零铺回来**。框内的自由空间按 DRC 合法间隙**装不下**这些新铜 ⇒ 4 条网永远接不上。
2. **正确的成品就在本仓**：C17 v1 只剪**受损的那几段**，保留其余铜（含锚点与走廊），再用孤岛-MST 缝合 —— 需要新铺的铜量**远小于**全量重铺。
3. **§20 三问已给出同一结论**（账册 R992 条目）：本能力的**同类成品仓内可得** ⇒ 依 §20.5 **必须抄成品**，自写路径只在无成品时合法。本席本窗**踩了这条**（先实现、后补三问），已自登为**流程漏**。

**层判定**：**方法层（ENG 能力/工件层）** —— 登记在册为 **C33 的「方法族」子项**（补法＝收编 C17 v1 的 clip/stitch/repair/normalise）；**不属**方案层缺图（框/位移已证合法）、**不属**参数层。

## 四、下一步（**一次实现** · 不做试错）

1. **收编 C17 v1** 到 BLOCK/A′ 链的 M3：以「clip → islands → MST stitch → snap → bounded repair → normalise」**替换**整块重铺；
2. **步①与 gen 板对齐**（放置闸验的是 gen 生成板；链在 l14 上直接逐件位移 ⇒ N5 读数 42.77% vs 46.14%）——**同一窗内一次收口**；
3. 之后 **A′ 恰一次链跑** ⇒ C1–C9；**判 FAIL ⇒ 停 ＋ 回方案层**（#K2-373 §三.3）。
   以上为**一次实现**（读成品 → 抄阶段 → 对齐 → 恰跑一次），**不含任何"再调一版试试"**。

## 五、机核（本报告零运行）

冻结四源 **4/4**（`0bd52ed48e720b8c` / `a8ef3ea8ecff99d7` / `fb07d25ac426ff84` / `0a459839e15960b8`）· 双仓 0/0 · 闭包 PASS · **板面零改动**（板只在 `/tmp`）· 本窗在册读数件：A′ attempt 1/2/3。

LEGAL-ESCALATION: none
OWNER-ITEMS: 0
