dataxcash/hw_ic_k2/docs/K2-R920-BLOCKER-REPORT-v2-PLAIN-LANGUAGE-AND-RULE-WAIVER-ASK.md

# R920 ·《卡点报告》v2 · H4 右下角（大白话 · 更新版）＋ 停止令遵办

日期 2026-09-28 · ENG(ARCHER) · **本回合零执行**（无链跑 · 无重出 · 无工具/参数改动）

## 〇、停止令遵办（先认账）

- **已停**：本回合**无任何「改参数／改工具／改笼位 → 重跑」**；只写本《卡点报告》并提交。
- **签名如实自报**：本回合**完全未使用** `/tmp/opencode/k2h4` 路径（自 R918 起已改用 `/home/fila` 与 `k2/` 内部路径）。
  检测器签名为**运行目录**（`RUN_SIG_RE = /tmp/opencode/(...)`）⇒ 计数呈**跨回合累积**特征。
  **同一签名 #K2-354 §三.1 已裁定「误报 · 作废」**（承 `M-SUP-REDLINE-FP-RUNDIR` 族）⇒ 本席**按误报处理但照令停手**。

## 一、① 信号怎么走（大白话）

> 右下角那两条 PCIe 下行线（`PCIE_DN4_N`／`PCIE_DN5_P`）**从板中间那颗转接芯片出发**：
> **在中层（In2）竖直往下钻** → **到底部通道带换到 In5、沿板底横着往东跑约 48mm** → **在板右缘附近掉头** →
> **再换回 In2 竖直往上爬** → **落到 J2 那一排焊盘（y≈59.5／60.3）**。一对两根天生不等长，靠**同伴线上的一段蛇形**补平。

## 二、② 挡路的是什么（大白话 · **两层**）

**第一层（几何）**：右下角那颗安装孔（H4）周围 3mm 不得有铜；这两条线**掉头＋上爬的那根立柱正站在里面**（x=139.48/138.32，须 ≤137.6537）。
想挪出去，**正西边那条带子已被「上行线」占满**——J2 一排是**上下行交替**的，**上行着陆立柱/过孔就插在下行立柱之间的每一格**（全板共用一张 **0.58mm** 的 x 栅格）。

**第二层（规则 —— 本回合新查实）**：**图纸里还有一条「不许乱走」的规矩**：
落**同一排焊盘**的立柱，**必须按通道顺序一个方向单调排**（落 x=135.0 那排要**从大到小**，落 x=132.65 那排要**从小到大**）。
这条规矩**不是本席自定，也不是业主临时加的**，而是**在册的 L2 裁定（2026-09-10）**——当年为了**防止走线交叉**而把它升成准入约束。
**后果**：本席算出来的唯一一组能同时满足「角上无铜 ＋ 不撞上行 ＋ 长度闭合」的立柱位置，**恰好破坏了这条单调规矩**（在 lane 4→5 处由 134.40 回升到 135.50）。
⇒ **不是「角上做不出来」，而是「在现有这条在册规矩下做不出来」。**

## 三、③ 人类方案是什么（大白话）

> **老工程师看到这种事，不会继续抠坐标**——他会**拍两种板之一**：
>
> **A（改规矩 · 最小动作）**：**只为 H4 这个角、只对着陆立柱**申请**豁免那条单调规矩**。
> 理由很硬：**那条规矩的目的只是「不许交叉」**，而本席这组立柱**并不交叉**（立柱互相平行且间距 ≥0.55mm；车道互相平行且间距 ≥1.449mm；着陆段各自在不同 y 带）——**它是「不交叉」的充分代理条件，本席满足的是真目标**。
>
> **B（改框架 · 大动作）**：**承认这条带子排不下**，回去**重排逃逸架构**（让这两条下行线根本不走右下角；或换层/换边），即 #K2-347「框架先行重放置」的完整版。
>
> **一句话**：**A = 求一次豁免（有据）；B = 重做框架（贵）。先问 A。**

**具体数字（已算 · 未落图 · 未跑链）**：`DN4_N→134.40 · DN5_P→135.50 · DN6_N→133.40 · DN7_P→134.95`；全部 ≤137.6537（孔边净距 **2.2537**）· 间距 **0.55 ≥0.525** · **逐对长度预算精确闭合** · 四角构造性无铜 · 端点不动。

## 四、卡点三问

**试过什么（六法）**：① 6×6 切铜＋C17 → 未连接 3；② 放宽 9×9 → 6；③ 间隙感知挪孔 → 落异网铜皮；④ C22 精确铜皮多边形 → 4mm 内无净位；⑤ R914 **只解下行** → 撞上行立柱（DRC 182 vs 168 · 6 新类含 3 短）；⑥ R918 **上下行联合重解** → **角上清了、不撞了、长度闭合了，但破了在册单调规矩** ⇒ 自证 FAIL ⇒ 依闸门停手。

**为何不通**：①②③④ 是**在既有铜上做局部手术**（角上冲突是**放置/框架**的下游症状）；⑤ 漏了耦合约束；⑥ **耦合约束解开了，卡在「在册规矩」**——这条规矩**本席无权松**（#K2-354 §三.5 闸门①明文：在册 ⇒ 停手报监）。

**缺口在哪层**：**不在施工层**（施工层零自由度）。缺口 = **一条在册的图纸层序规则的适用范围**（是否对「本角着陆立柱」这一处豁免），或 **框架层的逃逸架构重排**。**两者都只能由监理/业主裁。**

## 五、请裁 · 本席不做什么

- 请裁：**A**（只为 H4 角落豁免该在册单调规矩）**或** **B**（重排逃逸架构）；任一定夺后**仍需新的一次有界窗**（本窗重出额度已耗）。
- 在裁定前：**本席不重出 · 不跑链 · 不动板**；两仓维持闭合（`k2` `759f62f` / 父仓 `f4570357` · 冻结四源 4/4 · 仓四闸 PASS）。

LEGAL-ESCALATION: none
OWNER-ITEMS: 0
