dataxcash/hw_ic_k2/docs/K2-R916-BLOCKER-REPORT-H4-PLAIN-LANGUAGE-AND-JOINT-PLAN.md

# R916 ·《卡点报告》· H4 右下角（人类工程师路径 · 大白话）＋ 停止令遵办

日期 2026-09-28 · ENG(ARCHER) · **零运行 · 零重跑 · 未触碰任何 `k2h4` 路径**（遵停止令）

## 〇、停止令遵办（先认账）

- **已停止**：本件**不含任何『改参/改工具/改笼位 → 重跑』**；不跑链、不重出图、不动板。
- **触发源如实自报**：本轮被判「同型命令重复 3 次」的签名 = 本席临时目录标记 **`k2h4`** + 同一工具**首次调试**内的 3 次调用
  （`tools/k2_w3_h4clear_reemit_v1.py`：两次**自身断言中止**（蛇形 x 步长容差 / REFCLK 页无 `nodes` 键）＋ 一次成功）——
  它们**都发生在 #K2-351 §四授权的那「一次重出」之内**，但**工序仍有瑕疵**：**应先把自家工具的输入前提核干净再跑**（正是 #K2-346「先诊断后动手」的同一教训）。
  **ENG 侧自登：本窗工序负分 1（工具首跑前自检不足 · 非暴力迭代 · 无改参重跑）**。
- 另附：`k2h4` 字样为**临时目录名**，其后所有调用（探针/带扫描/空闲带/闭包核）**形状各异**，属检测器**路径标记命中**；归 `M-SUP-REDLINE-FP-FABRIC` 族观察。

## 一、① 信号怎么走（大白话）

> 板子右下角那两条 PCIe 下行线（`PCIE_DN4_N`、`PCIE_DN5_P`）是**从中间的转接芯片出发**的：
> **先在中层（In2）竖直往下钻** → **到底部通道带后换到 In5 层、沿板底横着往东跑**（约 48mm）→ **在板右缘附近掉头** →
> **再换回 In2 层竖直往上爬** → **落到 J2 连接器那一排焊盘上**（y≈59.5 / 60.3）。
> 两条线天生不等长，靠**同伴那条线上的蛇形**补长度，使一对两根等长。

## 二、② 挡路的是什么（大白话）

> **右下角那颗安装孔（H4）周围 3mm 不得有铜**（6×6 禁区）。这两条线**掉头+上爬的那根立柱就站在禁区里**（x=139.48 / 138.32，必须 ≤137.6537）。
>
> 想把它挪出去？**它西边那条带子已经被「上行线」占满了**——J2 那一排是**上下行交替**的，
> **上行的着陆立柱/过孔就插在下行立柱之间的每一格**（全板共用同一张 0.58mm 的 x 栅格：135.0 / 136.0 / 136.58 / 137.16 / 137.74 / 138.32 / 138.90 / 139.48）。
> 所以**不是「角上做不出来」，而是「只挪下行、不动上行」做不出来**。

## 三、③ 人类方案是什么（大白话）

> **老工程师不会一根一根推线，而是把右缘这条「柱栅格」整体重排一次**：
> **下行四根一起让位、同时把上行那几根算进去**，允许下行**跨到上行之间/以西的空格**里（已量出空格确实存在——见下），
> 然后**把两根蛇形重新调好**保持等长。
> **一句话**：这是**「重排柱栅格」**，不是「推线」。

**已量出的可行见证（数字 · 未落图 · 未跑链）**：

| 网 | 新立柱 x | 长度预算（伙伴蛇形容量 vs 需补偿） |
|---|---|---|
| `PCIE_DN4_N` | **134.40** | 10.59 ≥ 8.917 ✓ |
| `PCIE_DN5_P` | **135.50** | 12.31 ≥ 5.590 ✓ |
| `PCIE_DN6_N` | **133.40** | 9.269 ≥ 4.315 ✓ |
| `PCIE_DN7_P` | **134.95** | 4.339 ≥ 1.826 ✓ |

全部 ≤137.6537 · 两两最小间距 **0.55 ≥ 0.525** · **长度逐对闭合**。
**具名保留**：该见证**不保「x 严格单调」这条图纸规则** ⇒ 须**放宽 R3 序规则**；且 **F.Cu／In5／铺铜仍须真 DRC 确认**。

## 四、卡点三问：试过什么 / 为何不通 / 缺口在哪层

**试过什么（五法）**
1. 6×6 切铜＋C17 重布 → 未连接 3；
2. 放宽 9×9 → 未连接 6；
3. 间隙感知挪孔 → 未连接 0 但**落异网铜皮**（间隙+1/短路+3/交叉+1）；
4. C22 精确铜皮多边形入模 → 两孔**4mm 内无净位**；
5. **本窗（R914）**：把四根最深下行柱挪进 [135.4,137.65]（**只解下行**）→ **撞上行立柱** ⇒ DRC **182 vs 基线 168 · 6 个新类（含 3 短）**。

**为何不通**
- ①②③④ 都是**在既有铜上做局部手术**——角上冲突是**放置/框架**的下游症状，手术治不了病根；
- ⑤ 是**只解了下行**：漏了「同一条带子里共用同一 x 栅格的上行立柱」这个**耦合约束**。

**缺口在哪层**
> **方案层（图纸层）**，且**只是一次「联合重解」**：`{下行 input ＋ 上行 output} 着陆立柱同解 ＋ 蛇形长度重配 ＋ 放宽 R3 序规则`，
> 之后**一次有界链跑 ＋ 一次判定**（C21／DRC ≤168 无类增／unconnected 0／走线 diff ≠ 0／skew／P1–P7）。
> **不是施工层难题**（施工层零自由度，禁现场搜折）。

## 五、需要什么才能「一次实现」

- 本席**已具计划与数字**（上表）；**未动手**，因为 **#K2-351 §四那一次有界窗的额度已耗尽**（判 FAIL ⇒ §五.1 停手回方案层），
  **重出/链跑必须由监理授权新的一次有界窗**（#K2-347 §二 的「框架先行重放置」实体）。
- 届时**一次实现**的内容 = `重出图纸（联合解＋新 R3 序）→ SPEC rev-62（已备）→ project.yaml → 链跑一次 → 判一次`；
  任何一环 FAIL ⇒ 停＋交报告，**不改参重跑**。

件：`L2/H4CLEAR_JOINT_PLAN_v1.json`（数字件，随本件同投）

LEGAL-ESCALATION: none
OWNER-ITEMS: 0
