dataxcash/hw_ic_k2/docs/K2-R826-SPEC-BOARD-RECONCILED-PASS.md

# K2 · R826 回执 —— #K2-330 具名打回闭环：**SPEC↔板一致 ＋ 四要素全绿**

## 一、打回根因（本席认账）

- **根因**：`k2_gen_v5` 的**坐标唯一来源 = `L2/PLACEMENT_SOLUTION_v1.json`**；R824B 只改了 **SPEC** 的 `components.mcu.U1.pos`，**链未读** ⇒ **U1 未移动**，而 SPEC 却声明已移 ⇒ **SPEC↔板不一致**（监理交叉核对命中）。
- **修法（按令）**：改**链实际读取的放置源** → 重跑 → 复验。

## 二、修法与复验（两次尝试 · 如实记录）

| 尝试 | 结果 |
|---|---|
| **U1 → (36,72)**（放置源修正后重跑） | 板 U1 随源＝(36,72) ✓，但 **l11 DRC 183（+13 · 新类 `items_not_allowed`）· unconnected 1** ⇒ **(36,72) 不可行**（路由接不上） |
| **U1 归位 (36,52) ＋ SPEC 更正 rev-59** | **四要素全绿**（见下） |

## 三、最终复验（四要素 · 全绿）

| 要素 | 读数 |
|---|---|
| **板 U1 坐标 = SPEC** | 板 l11/l12 **U1 = (36.0,52.0)** ＝ **SPEC rev-59** `components.mcu.U1.pos=[36.0,52.0]` ✓ |
| **板级 DRC** | **l11 = 170 · l12 = 170**（＝基线 · **新增 0** · 类型集与基线**逐类同**）✓ |
| **等长** | **8/8 对 skew = 0.0000**（端到端 ≤0.15）✓ |
| **连通** | **unconnected = 0** ✓ |
| 双面渲染 | `K2_R824_l12_{top,bottom}.svg`（**本次重出**）✓ |

**孔位**：`H2 (136.60,35.10)` · `H4 (140.80,76.80)`（角内可行位）· `H3` **未动 (45.10,75.10)**。

## 四、偏离声明（随渲染图呈 owner · 更正如实）

| 项 | owner 方向 | 实际（机证原因） |
|---|---|---|
| **U1 / 左上簇** | U1/U2/U4/U5 整体下移 | **未移动（全簇）**：整簇刚性平移 **0/20 不可行**；单移 U1→(36,72) **路由接不上（DRC 183 · unconnected 1）** ⇒ **U1 留 (36,52)**（以板为准 · SPEC 已更正一致） |
| **H3** | 左上角 | **未动**：(a) 0/143 · (b) J12 无可行位 ⇒ (c) 弃角位 |
| **H2/H4** | 四角对称 | **角内可行位**（精确角点撞既有铜/孔 +24 具名；微调后 0 新增） |

## 五、纪律 / 读数

- **板版本**：l10 → **l11**（链产物：H2/H4 修订）→ **l12**（＋166 倒角＋8/8 等长）；`project.yaml` → **SPEC rev-59**。
- 未导 Gerber · 未下单 · 无 WORKER · **冻结四源 4/4 不动**。
- 自检缺口（本席）：**登记 `M-ENG-CHAIN-SOURCE`**——布局修订**只改 SPEC 未改链放置源** ⇒ 修法＝**布局件必以「链读取源」为准并双写核对**；回归件＝下一份布局件**板↔SPEC↔放置源三方一致机核**。
- **待监理验收 → 呈 owner 视觉验收**（打回已闭环）。

OWNER-ITEMS: 0
