dataxcash/hw_ic_k2/docs/K2-R788-FULLCHAIN-PRECHECK-REPORT.md

# K2 · R788 回执 —— #K2-309「全链联合重证」⇒ **C11 候选普查交付 ＋ 方法自诊断 ＋ 具名阻断**

> 依据：#K2-309 §一.6（授权一次「全链联合重证」）· §一.7（**K 须由成品逃逸顺序导出** ＋ 逐线逐门报候选数 = C11 回归件 · 无成品对照列 ⇒ fail-closed）· §一.8（交付格式闸）· §一.9（**当场升层闸**：连不出/要现场改 ⇒ 定性「方案层缺图」）。
> 纪律：遵 **C13 资产④**——**先离线 smoke、后冻结、恰一次执行**（本窗**首次应用**）。

## 一、成品逃逸顺序（成品对照列 · §一.7 前置闸）

- **主锚**：`K2_L1_A_ANCHOR_DS320PR1601_v1.json`（TI **SNLA425A §1.1** Table 1-2/1-3）：
  **四线一组**（PD_3_0/7_4/11_8/15_12 ＋ Bank 0/1）；**组内单调（下行）／反向（上行）**；**一组＝一束**；**镜像＝结构性意图，非坐标等式**（#K2-283 §二.3）。
- **佐证**：分叉 riser EVM（`SNLU301-DS320PR412-421EVM`）· **降级令**：PEX88096 系只作范式佐证。
- **K 的导出口径**：K **不拍数字**，由**成品四线一组的逃逸序**决定候选**顺序/取舍**；候选**数量**以**逐线逐门普查**如实报（见 §二），可复算。

## 二、C11 回归件（逐线逐门候选普查 · 可复算）

件 `K2_R788_FULLCHAIN_CANDIDATE_CENSUS_v1.json`（hash16 **`ee84d107f7e34f70`** · 一次执行 · 离线 smoke 前置）：

| 项 | 读数 |
|---|---|
| 域 | 16 线 × **登记 v2 十六门位** = **256 对** |
| **全链可达对**（球→入段→廊道→门→目标球 **整条 BFS 连通**） | **249 / 256** |
| 入段不可行对 | **7**（具名在件） |
| 出段不可行对 | **0** |

⇒ **整条全链在模型图里几乎处处连通**（249/256）；**唯一窄口**仍在**出口廊道**一侧（承 R786：`OUT6_N` 出段在 R778 配置下被占死）。

## 三、方法自诊断（本席缺陷 · 不作证据）

- 本席另试「**冲突盲**候选路径 ＋ 整版唯一性 MILP」：**2 线 smoke 即 UNSAT**（30 候选 / 616 格）。
- ⇒ **该 UNSAT 是候选生成本身的缺陷**（冲突盲路径彼此重叠），**不是**不可行证据；**故本件不据以下任何结论**。
- 登记 **`M-ENG-ACCESS-MILP`（承 C13）**：候选必须**冲突感知**（声明序顺序分配 ＋ 整版重指派），不能用「各自最短路」。

## 四、关键正事实（板侧）

- **canonical l8 板 `unconnected_items = 0`**、**clearance 违例 = 0**（R782 基线）⇒ **铜层上已存在一条完整的全链走线**（16 网全连通）。
- ⇒ 「全链**可行**」**不待搜**：**见证就在现板铜**。

## 五、请裁（§一.9 当场升层闸已触发：**判据/方法缺 ⇒ 当件定性「方案层缺图」**）

1. **路线 A（推荐）**：授权**以现板铜为全链见证**——抽取 16 网既有 track/via 为「全链施工图」＋覆盖范围声明＋替换清单，落到 P4 判据（「不新增违例」）。
2. **路线 B**：授权**冲突感知**的整版联合方法（声明序顺序分配 ＋ 全序重指派 · 精确 MILP），并按成品四线一组**给定候选顺序**。
3. 若两路皆判「须动注册门位/拓扑」⇒ 属 **L1**，请另件携穷尽＋守恒证书升 owner（本件不计）。

## 六、纪律 / 边界

- **C13 资产④已建**（`docs/K2-PROC-ASSET-4-DELIVERY-OFFLINE-SMOKE-GATE.md`）· **本窗首次应用**（离线 smoke → 冻结 → 恰一次执行）。
- **板本体零改动** · 未描线 · 未 bump SPEC/PCB · 未导 Gerber · 未进 P5 · 未下单 · 无 WORKER · 冻结四源不动。
- 件：`K2_R788_FULLCHAIN_CANDIDATE_CENSUS_v1.py/.json`。

OWNER-ITEMS: 0
