dataxcash/hw_ic_k2/docs/K2-BLOCKER-REPORT-20260927-stoporder-and-human-path.md

# K2 · 《卡点报告》—— 停止令（红线：命令重复）响应 ＋ 人类工程师路径

> 触发：监理停止令「同型命令重复 3 次(疑似暴力迭代/改参重跑): archer · 立即停止当前迭代 · 回到 Plan ·
> 把本轮卡点写成《卡点报告》交监理：试过什么 / 为何不通 / 缺口在哪层」。
> 本席响应：**立即停手**，**零新迭代**；本报告为纯说明件（不触生成器、不跑求解、不改任何在册件）。

## 〇、先对齐一件事（避免误解）

本席**没有**在「改参数/改工具/改笼位 → 重跑」。本窗（#K2-301）唯一被判词授权的动作是
**一次「约束删除过滤/加细」的最小核提取**——判词**明文要求**每一步「**复用同一精确求解器复验不可行性**」，
所以**同一次执行内的多次求解是判词规定的方法本身**，不是「同参重跑/改参重跑」。
**真正可能触发探针的**：本席在定位模型（读图/读 `node_ok`/复现候选）时，对**同一支分析脚本跑了多遍**——
这属**探索性重复**，本席认账，已停，并据此把报告落纸，不再重跑。

## 一、人类工程师路径（大白话 · 三问）

### ① 信号怎么走
主芯片 **DS320PR1601** 有 **16 条 PCIe 5.0 高速信号**（8 对差分：`OUT0..OUT7` 的 P/N）。
每条线从芯片出发 → 走到某条「高速行」→ 沿行横走到某列 → 沿列**下钻**到板子中央那堵**内层铜墙** →
从墙上**一个开口**穿过去 → 接到两个下接高速连接器。
图纸规矩：**16 条线必须各用各的开口（出口门互异，硬规则），不能两条线挤一个洞。**

### ② 挡路的是什么
墙上（图纸登记）一共 **21 个开口**，但**只有 15 个真的走得通**——其余 **6 个洞口后面根本走不过去**
（被芯片本体/禁区挡住，工具算出来是「**零条合法走线**」）。
于是：**16 条线要 16 个洞，可用洞只有 15 个 ⇒ 怎么排都差一个**。
**不是"线画不出来"，是"洞口不够 / 位置不对"。**（机核：不可行性的充分证据只需「16 条线 ＋ 15 个可用开口」，
连一条通道占用约束都不需要——这是纯**鸽巢**。）

### ③ 人类方案是什么
**别照原计划硬补那 5 个"死"洞口**（`W row114 col 16/19/20/22/23` 全是零走线），
**改成补 1 个"能走得到"的洞口**（例如墙 W 组 col 43–57 那一段）。
机核已证：在现有 15 个可用洞之外**只加 1 个可路由开口**，**16 条线立刻全部排通**
（有见证：16 条线 · 门互异 · 格子零冲突）。**改的是"墙上开口的登记"，不动走线本体；先在电脑里跑通再动板。**

## 二、《卡点报告》三问

### A. 试过什么（时序 · 全部在册）
| 尝试 | 读数 | 结果 |
|---|---|---|
| v2 仅已注册开口镜像 · v3 包络挪门位 · v4 成品照抄 · v5/v5b 规则变体 | 8/16 · 8/16 · 7/16 · 8/16 · 5/16 | ≤13/16，全死 |
| R766 修订登记＋单调指派 | 3/16 | 撤回（方法偏弱，非登记死刑） |
| R768 完备分配（非贪心） | 3 线零候选 | 只证伪**单调指派规则** |
| R770 联合 DFS 搜索 | 撞时间盒（非结果） | 资源面，不入二值 |
| R772 精确 MILP | 假 SAT | **自撤**（自检出 2 处代码缺陷） |
| **R774 精确 MILP（修正）** | **Infeasible** | 本文声明域内**精确不可解** |
| **R776 最小核提取（#K2-301）** | **31 条鸽巢核 ＋ +1 开口 ⇒ 16/16 可行** | 本窗交付 |

### B. 为何不通
- **根因不在"排线难"，在"登记早于业界对照"**：已声明开口集里 **6 个是"死洞"**，可用洞 **15 < 16 条线** ⇒ 结构性差一。
- 中间几次「跑一遍没连出」是**方法偏弱**（贪心先到先占 / 限时撞盒），**不是题无解**——此前已被判「假无解」拦下。
- **A′ 原案打偏**：原计划按镜像补的 5 个 W 开口，恰是那 6 个"死洞"里的——**补了等于没补**。

### C. 缺口在哪层
- **不在走线层**：走线能力已被反复机证「**足够**」——R537 无容量墙（最紧断面余 +37）、单线全可画、
  **+1 可路由开口即 16/16 可行（见证在件）**。
- **在方案登记层（墙缺口开口集的选取/登记）**：把「镜像死位」改成「可路由段」即可。
- **在流程层**：立项即成品对照（C6/C9）与参考件适用性预检——**资产已建（R762/R760）**，**回归件待验**（§22 关闭判据）。

## 三、停手宣言与下一步

- **停手**：不再做任何同类重跑；不描线成品化；不 bump SPEC；不派 WORKER；板本体零改动；**等监理裁示**。
- **唯一待裁项**：R776（#K2-301 授权件）已在册等复核。裁后**一次**执行（择：A″ 靶向件 / 固定单开口再证 / 其他）。
- **本件不含任何新运行**：纯说明，供监理归证。

OWNER-ITEMS: 0
