dataxcash/hw_ic_k2/docs/K2-CLOSURE-B-frozen-set-proposal.md

# K2 · B 支结题件 —— 「现注册／在册包络／已试参考范式族下，16/16 设计级不可达」（#K2-294 §二 规格 · 零运行）

> 依据：#K2-294 §二「确认。即出结题件。」规格五条（结论定格／证书汇总／改冻结集提案骨架／owner 选项页／停等复核）；#K2-280 §三.B（结题件规格）；#K2-282 §一 owner 直令（设计权威=成功案例）。

## 1. 结论定格

**在「现行冻结的出口注册 ／ 在册 ≤21 列·≤29 行包络 ／ 已试参考范式族（直通式线卡 · 分叉 riser）」之下，K2 的 16/16 施工图 = 设计级不可达。**

## 2. 证书与证据汇总（全部机器可复算 · 按时间序）

| # | 证据 | 读数 | 件／hash16 |
|---|---|---|---|
| 1 | 守恒侧**无容量墙**（156 断面全量） | 最紧断面**容 40 vs 需 3（余 +37）**；`hard_wall_certificate_found=false` | `K2_R537_…` |
| 2 | 单线级 16/16 均可独立画通 | — | `K2_R545_…` / `K2_R533_…` |
| 3 | 六族构造上限 | **13/16**（四硬键绿） | `K2_R652_…` |
| 4 | **相对 13 线基座 UNSAT**（修过滤器后） | `13 固定 + 3 自由` ⇒ `OUT4_N`/`OUT7_P` 存活 **0** | `K2_R708_…` |
| 5 | 单行/±1 修补（49 声明候选） | **49/49 全拒**（被他行在册走廊围死） | `K2_R730_…` `408bd4c0faa1ecb1` |
| 6 | 只用已注册开口（成组镜像 v2） | **8/16** | `K2_R750_…` `d8f4c5cdaa254075` |
| 7 | 注册网格包络内重定（v3 · **包络吃满** max dcol21/drow29） | **8/16** | `K2_R752_…` `de09d89ed32b42cd` |
| 8 | 厂商 A 单调/B 反向（v4） | **7/16** | `K2_R754_…` `2ccd2ca9b9e7a6b3` |
| 9 | flow-through 单调（v5 · 行 H 序） | **8/16** | `K2_R756_…` `19bd51883ac33d8c` |
| 10 | flow-through 单调（v5b · 入口列 d 序） | **5/16** | `K2_R758_…` `942a0cc1a5216d64` |
| 11 | 参考件①**直通式线卡**（DS320PR1601 EVM） | **板型不匹配**（平面内对称扇出 vs 本板跨区下钻） | `K2_L1_A_FANOUT_PARADIGM_RULE_v1.json` · `K2_R758_…` |
| 12 | 参考件②**分叉 riser**（DS320PR412-421 EVM） | 类匹配 ✅ 但**区分性机制（拐角多段换层）被在册孔对预算封死**；扣机制后退化为已试单调序 | `K2_R760_REFERENCE_APPLICABILITY_PRECHECK_v1.json` |

**证据强度分层（必须随件声明）**：
- **已机证**：上述 12 项，含「**无容量级切**」（R537）与「**任何单行/包络内/两件参考范式均不足**」；
- **未证**：**不存在**「现注册下 16/16 不可达」的**守恒级/UNSAT 硬核**——**因为 R537 机证不存在容量级切**，故该硬核在此问题上**不可构造**；
- ⇒ 本结题的强度 = **「声明构型／包络／参考范式族穷尽」＋「无容量级切」**，**不是**「守恒级已证不可行」。**禁止**把本结题表述为守恒级证明。

## 3. 改冻结集提案骨架（**先证后动**）

**提案**：**墙缺口开口集修订**——按分叉范式**成组有序重排**（对称门对：W `7↔28 · 11↔24`；E `115↔135 · 117↔133 · 119↔131 · 125↔125`），**新增 5 处**缺位开口（W rows **23/22/20/16**、E col **123**）以补全镜像对；**物理开口本体变更 = 待 owner 批**。
**守恒核算（复用 R537 方法）**：对修订后开口集重跑 156 断面全量计数，出具 `capacity_upper_bound ≥ demand` 对照表（证明不改出容量墙）。
**预检验证计划（PRECONDITION · 证不过就不动）**：
1. **P-a** 以「修订后注册」为输入，跑 **一次**认证表（域=1 · 零搜索）；
2. **P-b** 全通（附可行见证）⇒ 方**申请落开口修订**；仍阻断 ⇒ **修订不成立、本提案撤回**；
3. **P-c** 全程**不动物理开口**（P-a/P-b 在模型内完成），落开口仅发生在 P-b 通过**并经 owner 批准**之后。

## 4. owner 选项页（一页 · 人话）

| 选项 | 做什么 | 代价／风险 |
|---|---|---|
| **A′ 批墙缺口集修订** | 允许在**已注册网格**上把「每根线从哪个门过墙」重排成**镜像成对**（并补 5 处缺位开口）；我们**先在模型里跑通**才动板 | 动的是**门的登记与开口集**（不改 16/16 需求、接口、连接器、球映射）；可能引入制造/DFM 复检 |
| **B′ 接受不可达结论** | 认定**按现行注册 16/16 画不出**，K2 本阶段结题，转向**改需求／改接口** | 不改板；K2 的「16/16 施工图」目标**不达成**（13/16 可施工图 + 3 条具名缺口） |

**我们的建议**：**A′**（先在模型里证明「补 5 处开口后 16/16 可行」，再动板；若证明不了则撤回，不动板）——因为**地方够（余 +37）**、**单线都画得通**，瓶颈只在**门的登记排布**。

## 5. 停等 ＋ 纪律

**停等监理复核**（复核过 ⇒ 监理另件携证升级 owner · `LEGAL-ESCALATION: frozen-set`）· **禁描线** · **禁 SPEC bump** · **禁 WORKER** · 停线维持（不导 Gerber／不进 P5／不碰下单）· 冻结四源 **4/4 MATCH** · 物理本体**零改动** · 在册件一字未改（本窗仅新增本结题件）。

OWNER-ITEMS: 0
