dataxcash/hw_ic_k2/docs/K2-CONSERVATION-LEVEL-BLOCKER-REPORT.md

# K2 · 《守恒级卡点报告》 —— 承「收敛停滞 ≈80 轮无二值」停止令

> 令：**本件必须出二值（可行见证 ‖ 守恒级不可行证书）；禁再以「口径澄清／工具再升一版」单独占轮；若出不来 ⇒ 立即出《守恒级卡点报告》：哪层 / 哪资源 / 被谁占死 / 为何任何分配都不可能。**

## 〇、二值可得性判定（先答"出得来吗"）

| 二值 | 可得性 | 机核依据 |
|---|---|---|
| **可行见证（SAT）** | **现注册下：不可得** | R732 整版束道（出口门列严格不动 · 成品全序）= **7/16**；R730 声明式整行重定 **49/49 全拒**；R652 六族构造上限 **13/16** ⇒ 现注册下**已穷尽声明构型**，无见证 |
| **守恒级不可行证书（UNSAT）** | **机证不可得（本问题）** | **R537 机证：`hard_wall_certificate_found = false`；全部 156 个格点切 `capacity_upper_bound ≥ demand`** ⇒ **不存在「单切容量墙」** ⇒ **守恒级（切型）证书在本问题上无法由切论证产出**；在册唯一"核"**R668 是单级**（`(L1,113,19)` 鸽笼，905/905 候选对），**非 16 线联合** |
| 结论 | — | **两条都不出得来** ⇒ 按令：**立即出本《守恒级卡点报告》**。**并如实标注：任何"守恒级已证不可行"的声称，与 R537 的机核读数不符。** |

## 一、哪层（Which layer）

- **L1**：出口逃逸带 **row 36, cols 115–135**（row-36 族 8 门所在带） ＋ 各线在该层的**下钻走廊**（cols 114–137）。
- **L0**：**墙缺口接近行**（col-114 族 8 门的接近行 rows 7–28，尤 rows 7/11/12/13/15/19/24/28） ＋ 在 L0 下钻的 8 线的逃逸带（row 36）。
- **跨层**：**孔对格**（换层必须同一格上下两层皆空）——把两层的可用性**耦合**在一起。

## 二、哪资源（Which resource）

**不是面积／不是容量。** R537 对 156 个格点切全量计数：**最紧断面容 40 vs 需 3（余 +37）** ⇒ **若按"格子数"看，地方绰绰有余**。
真正的约束资源是两条**在册硬约束的乘积**：

1. **「注册出口门的可有序到达」**——16 个注册门在 2 层格上的**无交叉可达性**（几何序约束，非容量约束）；
2. **在册孔对预算**——13 线 **≤2 对孔**、3 条放宽线 **≤3 对孔**（#K2-267 γ-1）。⇒ **每线只有 1–2 次换层机会**，**无法用"多换层绕行"来化解交叉**（这正是 R716 实测：`OUT7_P` 需 ≤4 对孔才有路 ⇒ 撞 SI 上限被在册规则否决）。

## 三、被谁占死（Who occupies it · 具名到行到格 · 全部来自在册机核）

| 占用 | 被谁 | 后果 |
|---|---|---|
| **L1 row 36, cols 117–127** | `OUT0_P`（其在册接近段） | 卡死 row-36 族的东向逃逸带 |
| **L1 row 36, cols 128–131** | `OUT7_P` / `OUT6_N` / `OUT2_N` / `OUT3_P` | 同上（逐格） |
| **L0 col 120, rows 29–43** | `OUT0_N`（在册下钻） | **东侧接近的必经列被占** ⇒ `OUT4_P`（门 `119,36`）东侧全堵 |
| **L0 col 117, rows 36–40** | `OUT5_N` | `OUT4_P` 西侧堵 |
| **L0 (118,43)** | `OUT0_N` | 西侧下钻路线堵 |
| **L0 col 122 / col 123** | `OUT5_P` / `OUT2_P` | 更东的下钻列堵 |
| ⇒ 具体两例（R730 49/49 逐候选死因） | — | **`OUT4_P`**：东跨 `(0,(120,36))`、西被 `OUT0_N`/`OUT5_N` 占；**其 `t=eL=0` ⇒ 无第二接近层**；`(1,(119,36))` 属 `OUT0_P`。<br>**`OUT6_P`**：在册下钻列 132 是 cols 112–132 唯一畅通 L1 走廊，但到门 `(115,36)` 的接近段**两层皆堵**；更西的 112–119 在 rows 37–52 被 `OUT0_P/OUT7_P/OUT6_N` 占死。 |

## 四、为何任何分配都不可能（**如实分强度 —— 这是本报告最要紧的一节**）

### 4.1 已**机证**（可复算）
1. **六族构造**上限 **13/16**（R652；四硬键全绿）；
2. **相对 13 线基座 UNSAT**（R708：13 固定 + 3 自由，`OUT4_N`/`OUT7_P` 存活 0）；
3. **整版束道重排（出口门列严格不动 · 成品全序）＝ 7/16**（R732）；
4. **任何"单行重定 / ±1 挪位"的修补在 49 个声明候选中全拒**（R730）；
5. **（关键）守恒级切证书不存在**：R537 `hard_wall_certificate_found=false`（156/156）。

### 4.2 **未证**（必须写明）
**「按现注册，16 线联合分配全域不可行」的守恒级/UNSAT 硬核尚未产出。** 现有最强为 4.1 的"**声明构型穷尽 + 无守恒级切**"。
⇒ 因此本报告**不写「已证不可行」**；**凡把"未证"写成"已证"，与 R537/R732 的在册读数不符。**

### 4.3 结构性解释（为何"穷尽"是可信的直觉，但不等于证明）
16 个注册门在几何上**彼此太近**（row-36 族门间距仅 1–6 列；col-114 族门在相邻行 7/11/12/13/15），而各线的**入口次序**与**门的次序不一致** ⇒ 逃逸段/下钻段**必须互相穿越**；而穿越只能靠换层化解，**换层预算被在册 SI 上限锁死**（4.1-1/3 实测即为该锁死的表现）。**这正是同芯片成品改用「成组镜像出口注册」（按组注册、一组一几何）的原因**——成品从注册层面消除了这种穿越。

## 五、唯一两个出口（与 #K2-280 一致 · 均需 owner）

- **A（推荐）**：**批准东组出口注册成组镜像修订**（L1）⇒ 穿越从注册层面消除 ⇒ 现注册下的"卡点"整体消失 ⇒ 有望出**可行见证**（预计 2~3 窗）。
- **B**：**维持现注册并结题**（设计级不可行）——**结题前须先补硬核**（见 `K2_L1_B_HARDCORE_SPEC_v1.json`：证书优先找切；**若找得到切 ⇒ 硬核到手、本报告即可升级为"守恒级已证"**；若找不到 ⇒ 结题只能按"声明构型穷尽"强度，**须 owner 明确接受该措辞**）。

## 六、本席纪律

未获批**不改注册/SPEC**（L1）· **未描线** · **未导 Gerber／未进 P5／未碰下单** · **未派 WORKER** · 在册件一字未动 · 冻结四源 **4/4 MATCH** · 未触冻结本体。

OWNER-ITEMS: 1
