dataxcash/hw_ic_k2/docs/K2-R734-BUNDLE-V2-REPORT.md

# K2 · R734 回执 —— 批准的「整版束道重排件」（换手段后首窗）⇒ **仅 6/16 成表（0 冲突）** ⇒ 依 #K2-278 §三.3/§五属**第二次手段空转**

> 首行原文复述（#K2-278）：**M2 · 任务 M2-T4′（合图收口）· 进度变化＝合并冲突 5（未清零，承 R728）／可连续成线 15/16（未变）／实物画通 13/16（不变）／Gerber 0** ⇒ 净位移 0，但**路径判定前进**：把「单行微调」整支走死，逼出正确的换手段。…**§三.3 防空转闸触发（第 5 窗）⇒ 强制换手段＝§20 成品整版对照（束道整版复刻）· 不再批同型补丁窗 · 授权下一窗一次「整版束道重排件」**…**§五 下一窗仍不过 ⇒ 第二次手段空转 ⇒ 升 owner 议题「ENG 生产方式不达标」**。

## 一、本窗做了什么（**一次运行 · 域=1 · 成品全序 · 零搜索/零试参/零兜底**）

按 #K2-278 §三.2 的层级改判（**出口门列重指派 = L2**）与 §三.4 六项交付，落**整版束道重排件 v2**：

- **成品全序**：**束道分组 → 出口分配 → 逃逸带分配**（`REF-CASE-LIBRARY §A.1` ＋ R633 三规矩）。
- **分组**：`W` = 经 **col-114 墙缺口**出线的 8 条；`E` = 经 **row-36** 出线的 8 条。
- **出口分配（本窗新授权）**：**只在同组、已注册墙缺口之间重指派**——组内闸门按坐标排序，束内按注册行升序配对（**有序逃逸**）。
- **层分离**：`W` 走线/下钻在 **L1**；`E` 在 **L0**；逃逸段落在**闸门注册的出口层**（层不同处用一个拐点孔对）。
- **逃逸带**：`E` 在**闸门列+1** 下钻（逃逸 1 格）；`W` 在墙东偶数列下钻，沿闸门行西行至 col 114。
- **单调约束**：组内 **H 与下钻列随束序同时递增** ⇒ 束内不交叉。
- **硬声明**：**墙缺口物理开口 0 改动**（禁搬动/新增/删除开口；禁跨墙/跨组/跨侧）。

件 `K2_R734_BUNDLE_V2_v1.json` · hash16 **`bc6b912c4fc0fd9a`** · `construction_runs=1` · 产物落 `k2/`。

## 二、机核读数

| 项 | 读数 |
|---|---|
| **成表** | **6/16**（`OUT7_P · OUT7_N · OUT4_P · OUT6_P · OUT3_N · OUT2_P`） |
| **已表内冲突** | **0** |
| **连续性** | ✅ 已表 6 行逐格相邻 |
| **闸门** | ✅ 全部为**在册墙缺口** · 互异 · **物理开口 0 改动** |
| **未成表** | **10 行**（`OUT1_P · OUT2_N · OUT0_N · OUT6_N · OUT5_P · OUT4_N · OUT3_P · OUT5_N · OUT0_P · OUT1_N`）——在**声明单调束序**下无法同时满足「在册合法格 ＋ 与他线不共格 ＋ 单调性」 |
| 冻结四源 | **4/4 MATCH**（触碰 = 0） |

## 三、如实标注的能力边界（防过度声称）

- 本件是**声明式单调束序**下的机核结果（**不是**全域不可行性证明）——「10 行无路」限于**本件候选规则**；
- 但**就方法而言**：**换手段后的首个整版窗仍未达 16/16** ⇒ 依 #K2-278 §三.3/§五，**第二次手段空转成立**。

## 四、依 #K2-278 §五：**owner 议题「ENG 生产方式不达标」现已到期**

- **连续**：R720→R722→R724→R728→R730（同型补丁 5 窗）→ **R732（整版 v1 · 7/16）** → **R734（整版 v2 · 6/16）** ＝ **换手段后第二窗亦未过**；
- ⇒ 按预裁定，**「ENG 生产方式不达标」议题应由监理开启（owner 项）**。**本席不自开 owner 项、不自行扩权**，仅**声明其已到期**并**备齐证据包**：
  1) 五窗同型补丁史（R720/722/724/728/730）＋ 两窗整版（R732 7/16 · R734 6/16）；
  2) 具名结构死因：**`row-36` 逃逸带被多束共用** ＋ **`OUT4_P`/`OUT6_P` 被他行在册走廊围死**（R730 49/49 逐条死因）；
  3) §20 成品对照（`REF-CASE-LIBRARY §A.1`）与逐线对照列（本件 `product_comparison_column`）；
  4) 层级已由监理改判为 **L2**（#K2-278 §三.2），**本窗仍未触任何冻结源/物理墙缺口**（硬声明：开口 0 改动）。
- **若监理认为"手段"仍可再换**（例如**放宽单调性**为"束内有序但允许列序与行序解耦"、或**束内分片**），本席**一次即可执行**——但**须由监理明确"这是换手段后的第 2 次机会"**，否则按 §三.3 与 §五，本席**停手待裁**。

## 五、边界 / 账目

停线维持（未导 Gerber／未进 P5／未碰下单）· 未派 WORKER · 在册件一字未动 · **冻结四源 4/4 MATCH** · `sup.py verify` 5/5 PASS · criteria 只读 · **墙缺口物理开口 0 改动** · 报告 `k2/docs/K2-R734-BUNDLE-V2-REPORT.md`。
两仓：`k2` HEAD `bdf71bf`→本件（push rc=0，0/0）· 父仓 push rc=0，0/0。

OWNER-ITEMS: 1
