dataxcash/hw_ic_k2/docs/K2-R732-BUNDLE-REASSIGNMENT-REPORT.md

# K2 · R732 回执 —— 批准的 (b)「成组束道整版重排」⇒ **仅 7/16 成表（0 冲突）** ⇒ 属 #K2-277 §三.2 的 **(b) 认证失败**触发条件；本席停手报监

> 首行原文复述（#K2-277）：**M2 · 任务 M2-T4′（整版束道重排）· 进度变化 = 方法换血批准（§三.6 触发）——OUT4_P/OUT6_P 在出口门列不动下 49/49 全拒（机证画不出）· 合并板冲突连 5 窗·同型补丁机证不可达 ⇒ 零散补丁路线证伪，批准 (b) 成组束道整版重排（L2 新窗 · 成品整版对照 · 出口门列不动）；(a) 改出口门列 = 真 L1 · 定性"条件触发未熟"（(b) 失败前不扰 owner）。**

## 一、本窗做了什么（**一次运行 · 域=1 · 束道内有序指派 · 零回溯/零试参/零兜底**）

按成品范式（`REF-CASE-LIBRARY §A.1` ＋ R633 三规矩 ＋ SBR 分组）做**整版束道模板件**并**一次成表**：

- **束道序（声明）**：**最受约束优先** = 按 **(出口行, 出口列)** 排序（先 `col-114` 墙缺口族、后 `row-36` 族）。
- **束道模板（声明）**：`槽位 (cl,(60,H)) → [槽位孔对] → 行 H 走线（层 t，cols 61..Xt）→ 沿列 Xt 下钻（层 t，rows H−1..出口行+1）→ 拐点孔对 (Xt,出口行) → 出口层逃逸段（Xt−1..出口列）→ 在册出口门`；换层**只在扇出处一次**。
- **候选（声明有序）**：层对 (t,cl) ∈ {(0,0),(1,1),(0,1),(1,0)} × 下钻列 Xt（全列扫描） × 行 H（注册行 ±1..21 全扫）；**首个合法者即取**。
- **在册闸**：每格须为该线在该层的**在册合法格**；**每个孔对格须「过孔合法 且 上下两层皆空」**（层对规则）；**不得与他线共格**。
- **硬约束**：**出口门列/层一字不动**。

件 `K2_R732_BUNDLE_REASSIGNMENT_v1.json` · hash16 **`3c68e1ad5ac7d5fe`** · `construction_runs=1` · 产物落 `k2/`。

## 二、机核结果

| 项 | 读数 |
|---|---|
| 成表行数 | **7/16**（`OUT1_P · OUT0_N · OUT6_P · OUT2_P · OUT0_P · OUT3_N · OUT1_N`） |
| 已表内冲突 | **0**（四键 ＋ 层对键在已定集上全绿） |
| 出口门列 | ✅ **一字不动**（16 行均以注册出口门收尾） |
| 连续走法 | ✅ 已表 7 行均逐格相邻（本件加了连续性自检） |
| **未成表** | **9 行**：`OUT3_P · OUT6_N · OUT2_N · OUT5_P · OUT7_P · OUT4_N · OUT5_N · OUT4_P · OUT7_N` —— **在声明候选空间内无任何合法路线**（含最受约束优先时**首位**尝试的 `OUT3_P`） |
| 冻结四源 | **4/4 MATCH**（触碰 = 0） |

## 三、**如实标注的能力边界（重要 · 防过度声称）**

9 行「无路」是**在本次声明的束道候选空间内**的机核结论（层对 4 种 × 全列下钻扫描 × 注册行 ±21 全扫）——**不是全域不可行性证明**。故本件：
- **可确证**：**「声明式整版束道模板（出口门列不动）→ 16/16」在本件候选空间下未达成**（属 #K2-277 §三.2 的「(b) 认证失败 ⇒ 仍 <16/16」）；
- **不可确证**：「整版束道在该出口门列集合下绝对无解」——那需要**更大的候选空间**或**UNSAT 核**。**本席不越权声称不可行**。

## 四、请监理裁

1. **(b) 失败后的两条正路**（依 #K2-277 §三.1/§三.2 结构）：
   - **(b′) 扩束道模板再一窗**：例如**分组子束**（west 组 / east 组各自成束、束内再分片）、或**放宽层对组合**（允许 t 在走线中途再换一次但总额度仍守 SI）——**仍是 L2**；
   - **(a) L1 呈 owner**：按 §三.2 格式（**L1 前提变更请示** ＋ 全套证据：R720→R730 五窗补丁史 ＋ 本件 7/16 ＋ 成品对照），**由监理另件呈报**——但请注意 §三 的**能力边界标注**：本件尚**未**给出"整版无解"的硬核。
2. **本席建议**：先走 **(b′) 分组成束**一窗（成本低、且与成品"**一分组一束道**"更贴合），**再**决定是否 L1 呈 owner——以免用"未证不可行"去惊动 owner。

## 五、边界 / 账目

停线维持（未导 Gerber／未进 P5／未碰下单）· 未派 WORKER · 在册件一字未动 · **冻结四源 4/4 MATCH** · `sup.py verify` 5/5 PASS · criteria 只读 · **无同型补丁回潮**（本件为整版，非逐线）。

OWNER-ITEMS: 0
