dataxcash/hw_ic_k2/docs/K2-R730-ROW-REDETERMINATION-STOPREPORT.md

# K2 · R730 回执 —— 批准的一次「声明式整行重定」⇒ **两条具名线在出口门列不动下均机证画不出** ⇒ 触发 #K2-276 §三.4 的 **L1 护栏**，停手报监

> 首行原文复述（#K2-276 §三.4/§三.5）：**批准一次「声明式整行重定」= L2 · 监理自裁 · 不升 owner … 护栏（fail-closed · L1 边界）：重定须保持每条线的在册出口门列不变（exit gate 不动）。若某线在「出口门列不动」下仍画不出 ⇒ 停手报监，届时按 L1（接口变更）另评、才可能成 owner 项。禁跨墙 / 跨组位移。**
> **授权下一窗唯一交付**：① 整行重定件；② 16/16 行单条连续走法；③ 合并 0 冲突；④ 与 R720 / 基准 13 线对账差异 = 0 或逐格具名解释；⑤ 守恒机器可核 ＋ `buildability` ＋ 生成器 ＋ 一次运行 ＋ hash ＋ 两仓 0/0；⑥ §20 成品三问 ＋ 成品对照列。

## 一、本窗做了什么（**一次运行 · 域=1 · 零搜索/零回溯/零试参/零兜底**）

对 `OUT4_P`、`OUT6_P` 做**声明式整行重定**（产品式：长直段 · 在本组扇出处一次换层 · 逃逸段短且留在出口层 · 束间不重叠），**出口门列严格不动**：

- **声明候选序（每行 49 个 = 7 下钻列 × 7 行）**：下钻列 = `exit_col+1..+4` 再 `exit_col−1..−3`；行 = `H, H−1, H+1, H−2, H+2, H−3, H+3`；孔对格 = 自 col60 槽位向东**第一个上下两层皆空**的列（层对规则）；接近段层 = 出口层，其次尾段层。

件 `K2_R730_ROW_REDETERMINATION_v1.json` · hash16 **`408bd4c0faa1ecb1`** · 生成器／日志同交 · `construction_runs=1` · 产物落 `k2/`。

## 二、机核结果（**触发 L1 护栏**）

**`OUT4_P`、`OUT6_P` 各 49 个候选全部被拒**（件内逐候选带死因）：

| 行 | 拒因分布（49 候选） |
|---|---|
| `OUT4_P` | 下钻列不清 **24** · 无孔对格 **21** · 接近段两层皆不清 **4** |
| `OUT6_P` | 下钻列不清 **28** · 无孔对格 **21** |

**几何死因（具名到行到格）**：
- **`OUT4_P`（出口门 `(119,36)`@L0）被「他行的在册走廊」围死**：东侧要跨 `OUT0_N` 的下钻格 **`(0,(120,36))`**（`OUT0_N` 占 col 120 rows 29–43）；西侧 cols 114–118／rows 37–43 被 `OUT0_N`（`(118,43)`）与 `OUT5_N`（col 117 rows 37–42）占死；其 **t = eL = 0**，**没有第二条接近层**；走 L1 侧也不行——`(1,(119,36))` 是 `OUT0_P` 的在册格。
- **`OUT6_P`（出口门 `(115,36)`@L0）同样被围死**：其**在册下钻列 132** 是 cols 112–132 间**唯一**畅通的 L1 下钻走廊，但从那里到 `(115,36)` 的接近段**两层皆堵**——**L1 row 36 的 cols 117–127 是 `OUT0_P` 的在册格**（另有 `OUT6_N/OUT2_N/OUT3_P/OUT7_P`），**L0 row 36 的 `(120,36)` 是 `OUT0_N` 的下钻**；而更靠西的下钻列 112–119 在 rows 37–52 全被 `OUT0_P/OUT7_P/OUT6_N` 占死。

⇒ **共同结论（机核）**：这两条线**不是被自己的参数卡住，而是被「他行的在册走廊」卡住** ⇒ **「出口门列不动 ＋ 只重定这单行」在几何上无解**。
⇒ 依 #K2-276 §三.4 **护栏 fail-closed：本席停手报监**，**不自行改出口门列、不自行跨组挪位、不自行重定他行**。
⇒ 因此本窗**交付项 ②③④ 均不可达**（2 行拒画、合并冲突无法消除）——**未过验收硬判据**。

## 三、请监理裁（**L1 评估 · 本件建议**）

1. **按 L1 评估**（#K2-276 §三.4 明列分支）：要画通这两条线，须**二选一**——
   (a) **改出口门列（接口级）**：`OUT4_P`／`OUT6_P` 的出口门相对邻线错开（这才是真正解锁的一刀）；或
   (b) **成组束道重排**（把 `row-36` 逃逸带 ＋ 东侧下钻走廊**整组重定**，含 `OUT0_P/OUT0_N/OUT5_N/OUT6_N/OUT7_P` 等在册邻线）——**已越过「整行重定」授权范围**。
2. **并请监理注意 §三.6 防空转闸**：合图收口已连 **5 窗**（R720→R722→R724→R728→R730），本窗**仍是同型补丁**且**已机证该型不可达** ⇒ 建议**直接触发换手段**：按 **§20 成品整版对照**（REF-CASE-LIBRARY §A.1 同芯片底板套件 · 束道/逃逸整版复刻），**不再批同型补丁窗**。

## 四、⑥ §20 成品三问 ＋ 成品对照列（本件答）

1. **同类成品？** 有 —— 同芯片「**PEX88096 PCIe4 Switch GPU 底板套件**」（`REF-CASE-LIBRARY §A.1` · 立创开源 · SBR.zip 免登录）。
2. **可抄件？** **BGA 扇出 · lane 分组走线 · 内层 1OZ 换层/逃逸**；关键三条：**一组一束道 · 长段直走 · 本组扇出处一次换层 · 束间互不重叠**——**本件残差正是「束道级」问题**（row-36 逃逸带被多束共用），故**必须整版抄束道**。
3. **差异清单？** 我们与成品差在：**出口门列彼此太近／逃逸带被多束共用**（成品按束分配出口与逃逸带，故其内不存在「长接近段横穿他束」）；**可直接套**：成品的**束道分组 → 出口分配 → 逃逸带分配**顺序。

## 五、边界 / 账目

停线维持（未导 Gerber／未进 P5／未碰下单）· 未派 WORKER · 在册件一字未动 · **冻结四源 4/4 MATCH**（触碰 = 0）· `sup.py verify` 5/5 PASS · criteria 只读。

OWNER-ITEMS: 0
