dataxcash/hw_ic_k2/docs/K2-R728-DRAWING-COMPLETION-STOPREPORT.md

# K2 · R728 回执 —— 补图三笔已按令实现，**但两项机核事实须如实上报（含判词前提被证伪）** ⇒ 依 #K2-275 §三.3 fail-closed **停手报监**

> 首行原文复述（#K2-275 §三.1）：**补图三笔（一次确定性重发 · 域=1 · 无搜索）：(i) 槽位键改层对感知…（附对照读数：修正前后冲突数变化 21 → N）；(ii) 真冲突修法：OUT3_P/OUT4_P 之一换层点错开 ≥2 格（承 R609 先例）或前后移…二选一以四键全绿者为准；(iii) 每行补两列约定：孔对格 ＋ 接近段层/列——约定来源 = 成品对照（R633 三规矩＋渲染/SBR），禁自造。** §三.3 **fail-closed：重发后仍有真冲突/约定行缺 ⇒ 回图纸层具名补图，禁描线。**

## 一、如实上报的两项机核事实

### 事实 A（**判词 §二.1 的前提被证伪**）：R724 的 21 格**不是**「槽位键不分层对」造成的假阳性

本件按判词要求做了**键对照读数**（件内 `conservation.key_census`）：

| 键口径 | 冲突格数 |
|---|---|
| **(a) 只按格（忽略层）** | **203** |
| **(b) (格, 层) —— 即第四硬键（本席一直用的口径）** | **5** |

⇒ 若真是「键没分层对」，读数应是「粗键多、正确键少」且**21 落在粗键一侧**；实测 **203（粗）→ 5（正确）**，而 **R724 的 21 本来就是在正确键 (b) 之下数出来的**。
**结论**：R724 那 19 格是 **真·同层同格重叠**（`OUT6_P` 的接近段横穿他行 row-36 格），**不是键口径假阳性**。**「修键即可消掉 19 格」的前提不成立**（本席按令仍实现了层对键，并给出对照读数）。

### 事实 B：批准的两种分离手段**都不足以**分离 `OUT3_P`/`OUT4_P` 槽位对

件内 `completions.(ii)_pair_separation.declared_bounded_candidates`（**声明式**有界候选，非试参）：

| 候选 | 结果 |
|---|---|
| `OUT4_P` 换层点沿行**错开**（K2 扫描，含槽位层引线可行性） | **拒**：无「上下两层皆空」的孔对格 |
| `OUT4_P` 行 **H−1** | **拒**：同上 |
| `OUT4_P` 行 **H+1** | **拒**：接近段两层皆不清 |
| `OUT3_P` 换层点沿行错开 | **拒**：同上 |
| `OUT3_P` 行 **H−1** | **拒**：同上 |
| **`OUT3_P` 行 H+1（H 47→48）** | **可行（选中）** |

⇒ **`OUT4_P` 在全部候选下都无法取得孔对格**；即便把 `OUT3_P` 挪到 H=48，`OUT4_P` 仍拒。
**结论**：这对槽位**不能用「错开 ≥2 格 或 前后移」解决**，必须**整行重定**其中一条（其走廊/换层结构变了，已不是「补约定」）。**据令 §三.3，本席停手报监、不自行整行重定。**

## 二、已实现的三笔（本件 · 一次运行 · 域=1）

- **件** `K2_R728_DRAWING_COMPLETION_v1.json` · hash16 **`f645a472eb3d24c2`** · 生成器/日志同交 · `construction_runs=1` · `gerber/p5/order=false` · 产物落 `k2/`。
- **(i) 层对键**：已实现，并给出上述 203 / 5 对照。
- **(ii) 分离**：已按 6 候选声明式扫描（表见上），选中 `OUT3_P H 47→48`。
- **(iii) 两列入表**：每行已带 **`via_cells`（孔对格：同一格上下两层）** ＋ **`approach_layer` / `approach_columns`（接近段层/列）**；接近段层规则 K3（先尾段层、再出口层、皆不清则拒）；另设 **K4 接近段列规则**（**下钻列向出口列方向按声明式有界扫描 ≤24 列**，取首个可行）。**来源 = 成品对照（REF-CASE-LIBRARY §A.1 · PEX88096 底板套件的束道/换层逃逸范式），未自造。**

## 三、残差（fail-closed · 具名）

| 行 | 状态 | 具名原因 |
|---|---|---|
| `OUT4_P` | **拒画** | 见**事实 B**：全部候选下**无孔对格** ⇒ 需**整行重定** |
| `OUT6_P` | **仅靠 K4「下钻列西移」才画得出**，而这会**替换其在册 33 格**（row 53 的 L1 横段 ＋ 132 列下钻）⇒ 属**整行重定**，非「补约定」 | 其下钻列 **Xt=132** 距出口列 **115** 太远，接近段被迫横穿已饱和的 row-36 带 |

⇒ 合并仍 **5 格冲突**、**1 行拒画** ⇒ **未过验收硬判据**。
**本席未自行整行重定这两条线**（§三.3：回图纸层具名补图，禁描线）。

## 四、请监理裁（建议）

1. **扩窗（仍 L2）**：批**一次**「**声明式整行重定**：`OUT4_P`（槽位/换层结构）＋ `OUT6_P`（下钻列西移至出口列附近，使其接近段落进空档）」的确定性重发；判据同 #K2-275 §三.4；
2. **或**：若监理认为「整行重定」已触**在册出口/墙缺口**语义边界 ⇒ 按 **L1** 评估（届时才升 owner）；
3. **或**：另定口径。
> 同时请监理**更正 §二.1 的口径**（19 格非键假阳性，见事实 A），以免后续判词继续按「修键即可」推进。

## 五、边界

停线维持（未导 Gerber／未进 P5／未碰下单）· 未派 WORKER · 在册件一字未动 · **冻结四源 4/4 MATCH**（`0bd52ed48e720b8c` / `a8ef3ea8ecff99d7` / `fb07d25ac426ff84` / `0a459839e15960b8`，触碰 = 0）· `sup.py verify` 5/5 PASS · criteria 只读。

OWNER-ITEMS: 0
