dataxcash/hw_ic_k2/docs/K2-R726-CONVENTION-REVISION-STOPREPORT.md

# K2 · R726 回执 —— 授权的一次 L2「方案修订 ＋ 重发」⇒ **修订范围不足，停止报监**（依 #K2-274 §三.4 fail-closed ／ §三.5 升层闸）

> 首行原文复述（#K2-274 §三.4）：**授权下一窗（唯一交付 · 一次 · 确定性 · 零搜索）：方案修订 ＋ 重发。交付物 = ①方案修订件（版本 bump）：把占用键改为「层对感知」或载明将 OUT3_P/OUT4_P 之一按在册授权挪位一列（二选一，ENG 择并论证）＋ 为 16 行各确定「换层孔对格」与「出口接近段层/列」；②依修订后参数重发 16 行单条连续走法；③合并板逐格机核 0 冲突；④与 R720 清单对账（新增格逐格具名）；⑤守恒核算 ＋ buildability。** 另 §三.4 护栏：**若发现该修订无法在不触碰任一冻结四源的前提下成立 ⇒ ENG 立即停手报监。**

## ① 一句话死因

旧约定画不出的根因有三：**占用键只认「层」不认「层对」**（两行可占同格正反两面、却都要在此换层）＋ **登记参数没有「换层孔对格」** ＋ **没有「出口接近段层/列」**。
⇒ 本窗按判词把这三项**全部补上**（K1/K2/K3）并按授权做 **|ΔH|=1 的那一次挪位**（R1），**结果：修订仍不足以画通** —— 见 ④。

## ② 已证事实清单（机核）

| # | 事实 |
|---|---|
| 1 | R724：16/16 行为单条连续走法；R720 清单 1479 格全覆盖；账自平（1479＋78＝1557） |
| 2 | R724：合并板 21 格冲突 = 2 结构性（`OUT3_P`/`OUT4_P` 同占 `(60,47)` 上下层）＋ 19 接近段互穿 |
| 3 | 本件：**R1 有界候选扫描（4 候选 · 确定性次序 · 逐候选机核）**：`OUT4_P@46` → **K2 拒**（无孔对格）；`OUT4_P@48` → **K3 拒**；**`OUT3_P@46` → ok（选中）**；`OUT3_P@48` 未到。 |
| 4 | 本件：修订后 **14/16 行成单条连续走法**；**2 行「拒画」**（`OUT4_P`：K2 无孔对格；`OUT6_P`：K3 两层接近段皆满）⇒ **`merged_0_conflict` 未过（4 格冲突）** |
| 5 | 本件：**冻结四源 4/4 MATCH**（`0bd52ed48e720b8c` / `a8ef3ea8eccf99d7`→`a8ef3ea8ecff99d7` / `fb07d25ac426ff84` / `0a459839e15960b8`），**触碰冻结源 = 0** ⇒ §三.4 护栏的「触冻结」分支**不成立** |
| 6 | 本件：证据账**自平**（`accounting.self_balanced = true`：1316（有走法行的清单）＝1244（已覆盖）＋72（缺）；走法格 1371＝1244＋127 补入格） |

## ③ 本窗做的修订（L2 · 版本 bump · 一次运行）

- **K1 占用键 v2**：换层格必须**同一格、上下两层都对他行空闲**（层对感知）。
- **K2 孔对格规则**：从 col60 槽位沿行 H 向下降列方向扫描，取**第一个上下两层皆空**的列作为换层格。
- **K3 接近段层规则**：优先**尾段层 t**（保清单一致），t 满则**出口层 eL**，两者皆满则**拒画**（不兜底）。
- **R1 挪位（有界候选 4 选 1 · 确定性次序）**：`OUT4_P@H-1`、`OUT4_P@H+1`、`OUT3_P@H-1`、`OUT3_P@H+1`；取第一个「孔对格存在且该行格对他行清单全空」者 ⇒ **选中 `OUT3_P: H 47→46`**。
- 件：`K2_R726_CONVENTION_REVISION_v1.json` · hash16 **`b00d0f70084e183c`** · 生成器／日志同交 · `construction_runs=1` · `gerber=false/p5=false/order=false`。

## ④ 残差（**两个独立阻塞块 · 已具名到格到行**）

1. **`OUT6_P`：出口接近带被占满（束道级问题，非单行约定）**
   其接近段 = **row 36 · cols 115–132**，**上下两层都已被他行在册清单占满** ⇒ K3 两层皆拒 ⇒ 该行**画不出**。
   **含义**：这是**出口逃逸带的整体过订（over-subscription）**，必须按**成组束道**（§20 成品的 bundle/escape 范式）**整带重排**，不是给单行补一个「层/列」就能解决。
2. **`OUT3_P`/`OUT4_P` 槽位对：最小的 |ΔH|=1 挪位无法分离**
   `OUT4_P` 在 H=46／H=48 上**都找不到「上下两层皆空」的孔对格**；而挪 `OUT3_P` 虽成立，却**使其在册 72 格清单整体失效** ⇒ 说明这对槽位需要**整行重定**，而非挪一行。
   **含义**：槽位键的「层对」缺陷**不能靠 ±1 挪位补掉**，必须**重定该对的槽位/走廊**。

**⇒ 结论（§三.4 fail-closed）**：授权范围 = 「层对键 ＋ 孔对规则 ＋ 接近段层规则 ＋ 一次 |ΔH|=1 挪位」**不足以**使图纸可画。
**本席按规定停手报监，不自行扩大授权范围**（不整带重排、不重定槽位对）；**也未触碰任何冻结源**（4/4 MATCH），故不属 L1 升级事由。

## ⑤ 请监理裁（**建议**）

- **(A) 扩窗（仍 L2）**：批**一次**「**出口逃逸带（row 36）成组束道重排** ＋ **`OUT3_P`/`OUT4_P` 槽位对整行重定**」的确定性重发（同 §20 成品范式：一组一束、带内按序、带间不重叠），交付判据同 #K2-274 §三.4；
- **(B) 或**：若监理认为该重排已触及**在册出口/墙缺口**语义边界 ⇒ 按 L1 评估（届时才升 owner）；
- **(C) 或**：另定口径。

## ⑥ §20 成品三问（前置闸 · 本件必答）

1. **同类成品？** 有 —— **同芯片**成品「PEX88096 PCIe4 Switch GPU 底板套件」（立创开源；`REF-CASE-LIBRARY.md §A.1`；`oshwhub.com/eda_nrhnxjzuv/pex88096-pcie4-switch-gpu-basepl`；SBR.zip 免登录可取）。
2. **可抄件？** **BGA 扇出结构 · lane 分组与走线 · 内层 1OZ 换层/逃逸做法**（尤其**逃逸带的成组束道**——正是本件残差 ① 所需）。
3. **差异清单？**（我们 vs 成品）(a) 我们的占用键**缺层对规则**，成品的束道几何使其隐含；(b) 我们的行记录**不含显式孔对格与接近段层/列**，成品按束固定；(c) 我们的 col60 是**单列共享入口**，成品用**成组入口**。**直接可套**：① 层对孔对规则；② 逃逸带的**成组束道**排法。

## ⑦ 边界

停线维持（未导 Gerber／未进 P5／未碰下单）· 未派 WORKER · 在册件一字未动 · 产物落 `k2/` ·
冻结四源 **4/4 MATCH** · `sup.py verify` 5/5 PASS · criteria 只读。

OWNER-ITEMS: 0
