dataxcash/hw_ic_k2/docs/K2-R724-WALK-REEMISSION-BOUNCE-REPORT.md

# K2 · R724 回执 —— 授权的一次「确定性重发走法」⇒ **16/16 行已能连成单条线，但合并板出 21 格冲突** ⇒ 依第 #K2-273 §三.6 再打回图纸层

> 首行原文复述（#K2-273 §三.5）：**授权下一窗（唯一交付 · 一次 · 确定性 · 零搜索）：重发走法（re-emit single walk）——
> 按 R714 已逐行登记的「在册结构参数」（col60_slot / H / tail_layer / descent_column / Y / east_strip / exit），
> 为 16 行各重发一条「从槽位到出口的单条连续走法」（含槽位过孔配对格与出口接近段），并与 R720 的 16 行占用清单
> 逐格对账；差异逐格具名、收敛至 0。**

## ① 一句话死因（旧图为何不能照画）

登记件把「线」退化成了「**占用格集**」：**① 槽位处缺层配对格**（换层要求同一格上、下两层都在，清单只留一侧）；
**② 连廊道/接近段的层与位置都没定**（接近段本可走层 t 或走出口层 eL，登记参数不含此约定）；
**③ 槽位键 `col60_slots_distinct` 只按 (层,H) 去重、不按「同格层对」去重** ⇒ 两行可声称同一 `(60,H)` 格的**上下两侧**。

## ② 已证事实清单（机核）

| # | 事实 |
|---|---|
| 1 | R722：合并板 **0 冲突**（1479 唯一格）· 与 R720 **逐格一致 16/16** · 端点齐 · 账自平（1479+4=1483） |
| 2 | R722：仅 **5/16** 行可从清单缝成一条线；11 行缺连接格、共 **80** 格（已具名） |
| 3 | **R724（本件）**：模板两处缺陷已定位并修好——**下钻段被写成自下而上**、**接近段 `range(Xt, ee[0]+1)` 漏掉出口列** |
| 4 | **R724**：按 R714 在册参数重发后，**16/16 行均为「槽位→出口」的单条连续走法**（逐格相邻/同格换层，无跳步、无重格） |
| 5 | **R724**：**R720 占用清单 1479 格全部被走法覆盖**（`missing_from_walk = 0`，逐行） |
| 6 | **R724**：为连通必须补入 **78 个连接格**（槽位层配对格 ＋ 出口接近段；**逐格具名**），**未加入交付件**——只入账 |
| 7 | **R724**：补入后合并板出现 **21 格冲突**：**2 格为结构性**（`OUT3_P`/`OUT4_P` 同占 `(60,47)` 的上下两层、而两者都必须在此换层）＋ **19 格为接近段互穿**（`OUT6_P` 的 L1 row-36 接近段横穿 `OUT0_P`/`OUT6_N`/`OUT2_N`/`OUT3_P`/`OUT7_P` 已在册的 row-36 格；`OUT4_P` 的接近段与 `OUT0_N` 的 col-120 下钻相撞；等） |

## ③ 修正后的施工图（本件）

- 件内 `routes` = **16 行单条连续走法**（每行：源、槽位、出口、层、逐格序列）＋ `continuity`（16/16 连续）＋ `conservation`（容量 ≥ 需求）。
- **但合并板未过**：`merged_0_conflict = false`，冲突 21 格已具名到格到行对 ⇒ **不计 PASS**。

## ④ buildability

`relocation_listed`（R720 已挪 `OUT0_P`/`OUT6_N`；**本件不新增挪位**，只把登记路线画出来并补入它们隐去的连接格）。
**若要消掉本件 21 格冲突 ⇒ 必须新增挪位/改槽位 ⇒ 属图纸层修订，非本件可自决。**

## ⑤ 交付件五要件

生成器 `K2_R724_WALKS_16OF16_v1.py` · **一次运行**（`construction_runs=1` · 零搜索/零试参/零兜底）·
`artifact_hash16 = c45f53fff420de2a` · **证据账自平**：`1479（R720 清单去重）＋ 78（清单隐去的连接/接近格）＝ 1557（走法格数，去重前）`
（件内 `accounting` 可复算）· 两仓 push 读数 **0/0**。

## 依 §三.6 的处置（本席不自行补图/改槽位）

- **当件定性：方案层缺图**（本次 = **缺「孔对（换层格）」＋「接近段层/位置」约定**；并命中 **槽位键非层对感知** 的结构缺陷）；
- **打回图纸层**；**禁**在施工层滞留、**禁**现场兜底、**禁**搜索/试参。

## 建议的下一步（需监理另批 · 确定性 · 零搜索）

1. **槽位键改「层对感知」**（或把 `OUT3_P`/`OUT4_P` 之一挪开一列），消掉 2 格结构冲突；
2. **为每行确定「孔对格」与「接近段层/列」**（在册参数现无此两项），消掉 19 格接近段互穿；
3. 重发走法 → 合并 0 冲突 → 与 R720 清单对账（新增格逐格具名）⇒ 方可交 M2 收口。

## 边界

停线维持（未导 Gerber／未进 P5／未碰下单）· 未派 WORKER · 在册件一字未动 · 产物落 `k2/` ·
冻结四源 4/4 MATCH · `sup.py verify` 5/5 PASS · criteria 只读。

OWNER-ITEMS: 0
