dataxcash/hw_ic_k2/docs/K2-R722-REDRAW-BOUNCE-REPORT.md

# K2 · R722 回执 —— 授权的一次 16 线重描 ⇒ **不能完成**（方案层缺图 · 依 #K2-271 §三.6 打回）

> 首行原文复述（#K2-271 §三.6/§六.4）：**授权下一窗（唯一）：一次 16 线重描 ＋ 合并全图碰撞核对（须 0 冲突）
> ——照图连连看，零搜索／零试参／零归因；当场升层闸：重描中任一"连不出／要搜才能定／判据缺"⇒ 当件定性
> 「方案层缺图」立即打回图纸层，禁在施工层滞留半窗。**

## 一、本窗做了什么（零求解／零试参）

读已受审的 **R720** 16 行（层/槽位/孔对/廊道 → 逐线格清单），**照图落线到合并双层板**，只跑在册闸。
件：`K2_R722_REDRAW_MERGED_16OF16_v1.json` · hash16 **`55272009d12dc985`** · 生成器/日志同交 ·
`construction_runs=1` · `gerber_exported=false` · `p5=false` · `order=false`。

## 二、机核读数

| 闸 | 读数 |
|---|---|
| （1）合并全图 **0 冲突** | ✅ 逐格机核：`cells_distinct=1479`，`conflicts=[]`（第四硬键在合并图上成立） |
| （2）与 R720 **逐格一致** | ✅ 16/16 行逐格一致（含分行内无重复） |
| （3）证据账**自平**（#K2-271 §三.5） | ✅ **1479（去重清单）＋ 4（源冻结清单仍携带的自重格，已具名）= 1483 = R720 `cells_raw`** ⇒ 该字段**可由件内数据复算**。4 格：`OUT1_N(0,133,36) · OUT2_P(0,125,36) · OUT3_N(0,131,36) · OUT5_N(0,117,36)` |
| （4）端点齐 | ✅ 每行的 col60 槽位格与出口格（在自身出口层）都在清单内 |
| **（5）连成一条线（连连看）** | ❌ **仅 5/16 行**（`OUT0_P · OUT1_N · OUT4_N · OUT6_N · OUT7_P`）可缝合为从槽位到出口的单条走法 |

## 三、卡点（定性命中 §三.6「连不出」）

**11/16 行无法从自身清单连成一条线**，共缺 **80 格连接格**（本件按确定性 Manhattan 给出**候选补格清单**，
**未加入、未求解、未兜底**；数值为确定性上界，非唯一最小集）：

| 行 | 缺格数 | 系统性缺失（具名样例） |
|---|---|---|
| `OUT2_P` / `OUT3_N` / `OUT5_N` | 1 | **槽位层的"过孔配对格"缺 1**（如 `OUT2_P` 缺 `(0,(60,57))`） |
| `OUT7_N` / `OUT1_P` / `OUT4_P` | 2–3 | 同上（槽位配对格）＋ 出口侧 1–2 格 |
| `OUT0_N` / `OUT5_P` | 6–8 | 槽位配对格 ＋ **出口接近段成排缺格**（如 `OUT0_N` 缺 row-29 的 `(119..114,29)`） |
| `OUT2_N` / `OUT3_P` / `OUT6_P` | 18–19 | 槽位配对格 ＋ 出口接近段 |

**根因（业务口径）**：R652→R714 的"逐格清单"是**分段拼接的占用格集**，**不是一条连续走法**——
**槽位处缺过孔配对格**（层 n 与层 1−n 的同一格要成对才能换层），部分行还缺**出口接近段**。
⇒ 它作为**占用/互斥证据**（0 冲突、四键）成立，**作为"已画通的线"不成立**（与 R714 名"逐格走法"不符）。
登记：**M-ENG-BASE-PROVENANCE-QUALITY（升级：从"复核通过率 10/13"升为"11/16 行不可连"）**。

## 四、依 §三.6 的处置（本席不自行补图）

- **当件定性**：**方案层缺图**（11 行 × 共 80 候选连接格，**已具名到格**）；
- **打回图纸层**；**禁**在施工层滞留、**禁**现场兜底补格、**禁**搜索/试参；
- **建议的下一步（需监理另批一次、确定性、零搜索）**：按**在册结构参数**（`col60_slot / H / tail_layer / descent_column / Y / east_strip / exit`，R714 已逐行登记）**重发每行的单条走法**（含槽位过孔配对格与出口接近段），再与 R720 的 16 行占用清单**逐格对账**；对账差异逐格具名后重交监理。

## 五、边界

停线维持（**未导 Gerber · 未进 P5 · 未碰下单**）· 未派 WORKER · 在册件一字未动 · 冻结四源 4/4 MATCH ·
`sup.py verify` 5/5 PASS · criteria 只读。
两仓：`k2` HEAD 见账目（push 读数 0/0）· 父仓 push 读数 0/0。

OWNER-ITEMS: 0
