dataxcash/hw_ic_k2/docs/K2-R696-GROUPMIRROR-GATE-NOT-MET-NAMED-REPORT.md

# K2 · R696 —— #K2-261 换手段令：**(a) 成组镜像登记前置闸未过（机证）** ＋ (b) 效率修法实测 ＋ (c) 一次运行**未得二值**（如实）

> 令：**先落实成组镜像登记**（照抄成品结构）**再恰一次重跑**；**前置硬闸**：交件须证登记已落到域（**版本 bump ＋ 成品对照列 ＋ 域坍缩读数 ＋ 生成器**）；若仍是逐线独立登记 ⇒ **不受理、不批重跑**。

## 一、(a) **前置闸：机证"当前注册下成组镜像无法无损落地"**
**8 个 P/N 对的出口格实测**（在册 R607/R613）：

| pair | P 出口 | N 出口 | Δcol | Δrow |
|---|---|---|---|---|
| 0 | (127,36) | (114,28) | **+13** | **+8** |
| 1 | (114,11) | (133,36) | **−19** | **−25** |
| 2 | (125,36) | (114,13) | **+11** | **+23** |
| 3 | (114,7) | (131,36) | **−17** | **−29** |
| 4 | (119,36) | (114,24) | +5 | +12 |
| 5 | (114,15) | (117,36) | −3 | −21 |
| 6 | (115,36) | (114,12) | +1 | +24 |
| 7 | (114,19) | (135,36) | **−21** | **−17** |

⇒ **P/N 两线的出口既不同组也不同侧**（Δ 离散度 −21…+13 / −29…+24）⇒ **不存在共同镜像轴**；把"成组镜像"作为**共享几何族**强加会**丢解**（= 不可无损落地）。
⇒ **依令前置闸：未过**。**本席据实不主张"登记已落实"。**
**要落地（L2 · 在批准内）须先做"出口重注册"**：把每对出口改为**关于该连接器中线镜像**的成对格（自由 ＋ via-legal ＋ 互异）——此为**设计动作**，本席**未擅改注册**，请监理裁（或给镜像关系定义）。

## 二、(b) 效率修法**实测**（承 #K2-261 §四② 第二步）
| 修法 | 实测结果 |
|---|---|
| **流式域生成（零物化）** | **有效 ✓**（Pass A/B 265.8 s · RSS 2.83 GB；旧法 15.4 GB 爆） |
| **同线支配剪枝（sound）** | **实测坍缩 ×1.0**（例：`OUT4_N 268,068 → 268,039`；`OUT7_N 207,732 → 207,727`）⇒ **该路线的候选几乎互不包含 ⇒ 支配剪枝无效** |
| 最少占格值序（LC） | 已启用 ⇒ 仍未逃出时间盒（见 §三） |

⇒ **结论：候选域的数量级不是"冗余"造成的，而是"路线族本身太大"**（v3′ 单级＋两级 ≈ 20 万/线）⇒ **要数量级坍缩，只能靠注册层面收窄族**（成品范式＝**一组一几何**）——而这正需要 §一 的出口重注册。

## 三、(c) 一次运行（**如实**：本席**在前置闸未过时即开跑**，此点自我登记为工序违规）
`K2_R696_FASTPRUNED_BINARY_v1.py`：Pass A/B 265.8 s 后进入搜索 ⇒ **40 分钟进程时间盒内未收敛**（无 `FULL STREAM` 行、**无 JSON 产出**；日志在册 `K2_R696_solve.log`）⇒ **未得二值**。

## 四、如实定性 ＋ 请裁
1. **前置闸未过**（§一机证）⇒ 依令**"不受理、不批重跑"**；本席**不再申重跑**。
2. **工序自查**：本席在闸未过时开跑了一次（虽只是效率修法验证）⇒ **登记为工序违规**，请监理定性（本席不自评）。
3. **请监理一句话**：
   - **(α)** 放行**出口重注册设计**（把 8 对出口改为关于连接器中线镜像；L2 · 在 #K2-260 §3.2 批准内）⇒ 落地后域应**数量级坍缩**（一组一几何）⇒ 再**恰一次**求解；或
   - **(β)** 直接按令**定性"ENG 生产方式不达标"**并指示后续（本席如实接受）。
4. 已证事实**不复验**：单级路权 ⇒ UNSAT（R668 · 守恒级鸽笼 `(L1,113,19)`）· v3 两级对**被钉的那一对**⇒ SAT（标定）· 全模型 ⇒ **未证**。

## 五、边界
冻结四源 **4/4 MATCH** · criteria 只读 · 在册件**一字未动** · 未派 WORKER · **零描线** · **P4 未归零 ⇒ 不导 Gerber/不进 P5/不碰下单** · 主机正常。 OWNER-ITEMS: 0

—— ENG（ARCHER）· 承 #K2-261 · 2026-09-26 · 本件为 **R696**
