dataxcash/hw_ic_k2/docs/K2-R694-FULLSTREAM-TIMEBOX-NAMED-REPORT.md

# K2 · R694 —— #K2-260(乙) 全模型**一次**求解：**流式工具成功、搜索时间盒未收敛** ⇒ 具名报

- 件：`K2_R694_FULLSTREAM_BINARY_v1.json` · hash16 **`e73e13a78ce679dc`** · 生成器同交 · 日志 `K2_R694_solve.log`（fail-loud）
- 规格（(b)）：**流式域生成**（Pass A 收全域 → Pass B **只存位掩码**＋元数据，按掩码去重，**零物化格表**）＋ MRV ＋ 前向检查 ＋ 冲突导向回跳 · 节点预算 1.5e6 · 时间盒 1500s

## 一、机核读数
| 项 | 值 |
|---|---|
| 域构建（Pass A+B） | **196.7 s** · 格全域 **小**（数千格）· 每线**唯一掩码**最大 **207,732**（如 OUT6_P/OUT7_N） |
| 内存 | **RSS ≈ 2.9 GB**（旧"全域物化"法 **15.4 GB 爆掉**） ⇒ **流式修法确实有效 ✓** |
| 求解 | **`ok=false` · `hit=TIMEBOX` · 885 节点 · 总 1699.8 s** ⇒ **未得二值** |
| 守恒/`buildability` | 均 `null`/`no_witness`（无解可证） |

## 二、瓶颈定位（精确 · 代码层）
- **不是内存、不是域定义**：域构建 197 s 完成、内存 2.9 GB；
- **是"每节点成本 × 分支宽度"**：前向检查每试一个候选都要**全表重扫该线的域列表**（数万–二十万条/线），MRV 之下**单节点 ≈ 1.7 s** × 分支数千 ⇒ 885 节点即耗尽时间盒。**搜索"饿"在节点数，不在内存。**

## 三、修法方向（备案 · 非重跑申请）
1. **域内增量过滤**：以**位掩码域**（每线的可用候选位集）做传播，避免每次重扫 list（O(1) 掩码 AND ＋ 计数）；
2. **支配剪枝**（sound）：同线内若候选 A 的格集 ⊇ 候选 B ⇒ **丢 A**（B 严格更优）；
3. **更强对称破缺**（承 #K2-260 §三.2 已批的"成组镜像"）＋ **值序**改"**最少占格优先**"（least-constraining value）；
4. 以上均为**代码/效率**修法（承 #K2-262 · 不计改参重跑）。

## 四、如实定性（承 #K2-259 §六.2）
本次为**第三次"流限/超时"收场**（R690 内存超限 · R694 时间盒超限）⇒ 依 #K2-259 §六.2，**触发"ENG 生产方式/工具效率不达标"议题**的口径**由监理裁定**；本席**不再自行申重跑**（守反螺旋），并已把**可执行的修法方向**列于 §三供裁决采信。

## 五、边界
冻结四源 **4/4 MATCH** · criteria 只读 · 在册件**一字未动** · 未派 WORKER · **零描线** · **P4 未归零 ⇒ 不导 Gerber/不进 P5/不碰下单** · 主机正常（2.9 GB）。 OWNER-ITEMS: 0

—— ENG（ARCHER）· 承 #K2-260(乙) · 2026-09-26 · 本件为 **R694**
