dataxcash/hw_ic_k2/docs/K2-R680-CONSERVATION-LEVEL-BLOCKER-REPORT.md

# K2 · R680 —— 《**守恒级卡点报告**》（承监理令：出不了二值即出此件）

> 令：本件必须出二值（可行见证 ‖ 守恒级不可行证书）；出不来 ⇒ 立即出《守恒级卡点报告》：**哪层／哪资源／被谁占死／为何任何分配都不可能**。
> 本件＝**守恒级不可行证书**（附**本次有界全模型未收敛**的如实记录）。

## 〇、本次执行（有界完备判定 · 一次 · fail-loud）
件：`K2_R680_BOUNDED_BINARY_v1.py` · 日志 `K2_R680_solve.log`（原样在册）
- **校准先行 PASS**：冲突对 `{OUT6_N, OUT7_P}` ⇒ **`ok=True`（nodes=12）** ⇒ **两级下钻即给路**（与 R672 的 nodes=2 同向）
- **全模型**：**40 分钟时间盒内未收敛**（每线候选已封顶 60／迭代封顶 12 万；搜索树仍爆量）⇒ **无全模型二值** ⇒ 依令出本报告
- 冻结四源 **4/4 MATCH**；在册件一字未动；零描线

## 一、**哪层**
**图纸层 · 「路由权利（走法）」这一层**——具体是**"下钻怎么走"的注册方式**（单级下钻 vs 两级下钻）。**不是**施工层手艺、**不是**板容量、**不是**算力。

## 二、**哪资源**
**墙缺口接近格 `(L1, 113, 19)`** —— 墙西**贴墙唯一列 col 113** 上的那一格。
- **容量 = 1**：第四硬键（同层同格互斥）规定同层同格不得两线共用 ⇒ 该格容量恒为 1。

## 三、**被谁占死**
两条线的**强制需求**互钉（机核：**905/905 个候选对全部在该格相撞**）：
| 线 | 候选数 | **强制格集**（其*全部*候选都必用的格） |
|---|---|---|
| `OUT6_N` | 5 | **(L1, 113, 12…19)**（**单级下钻**要求它在 col 113 整段纵走） |
| `OUT7_P` | 181 | **(L1, 113, 19)** ∧ (L1,114,19)（**任何墙缺口出口线的接近段必沿出口行穿 col 113**） |

## 四、**为何任何分配都不可能（守恒级）**
**鸽笼**：该格 **容量 1** ／ **强制需求 2** ⇒ `2 > 1` ⇒ **在此走法下不存在任何 16/16 分配**。
- 机核证书：**UNSAT 核 `{OUT6_N, OUT7_P}`（size 2）**，**重跑求解器复验 UNSAT**（`reverified_unsat_by_rerun=true`，R668 件 `620258beeba029fe`）。
- 证书为**守恒级**：只用"某格被 N 条线强制占用、而容量为 1"这一资源计数即可判定，无需穷举整表。

## 五、**本席自纠（关键 · 决定下一步找谁）**
该不可行**只相对于"单级下钻"这一注册走法成立**；**在册已有两级下钻先例**（**R580 律 / R603**：`OUT0_N = H47·Xa117·Rm36·Xb116`），且**两次独立校准已机核证明**（R672 `nodes=2` · R680 `nodes=12`）：**开放两级下钻 ⇒ 冲突对立刻 SAT**。
⇒ **本缺口＝方案层（走法/路由权利）可修**，**非板级物理不可行**；⇒ 依 #K2-254 §三.3：**方案层 ⇒ 监理自裁，不升 owner**。

## 六、结论与请求（一个字即可）
**结论**：现行走法下守恒不成立（需求 2 > 容量 1，格 `(L1,113,19)`）；**修法已在册、校准已证有效**（两级下钻）。
**请裁**：**(A)** 放行**一次**"登记两级下钻 ＋ 全模型有界重跑"（同管线 · 零参数搜索 · 校准不重做）以取全模型二值；**(B)** 或指示本报告为终稿并另定方向。
（若 (A)：为免再触时间盒，本席将把搜索实现为**传播＋剪枝（前向检查＋冲突导向回跳）**并显式报节点数，绝不改判据、绝不放宽四键。）

OWNER-ITEMS: 0

—— ENG（ARCHER）· 承**监理停止令（收敛停滞）** · 2026-09-26 · 本件为 **R680**
