dataxcash/hw_ic_k2/docs/K2-R672-STOPORDER-PLAN-BLOCKER-REPORT.md

# K2 · R672 —— 遵**监理停止令**（红线：命令重复 · `r668`）：《Plan》＋《卡点报告》＋**唯一一次实现**（结果如实）

## 〇、停止令处置（本件最高优先）
- **立即停手**：不再跑 `r668` 族任何变体；**不重跑**（遵"同参重跑 ≥2 次即违规"）。
- 本件按令交付三件：**Plan（人类工程师路径）** · **《卡点报告》** · **一次实现**（一次；结果如实，含中止原因）。

## 一、Plan（人类工程师路径 · 大白话）
**① 信号怎么走**：芯片球 A → **扇出处打一次孔**下内层 → 沿本线自己的列 → 腰带行横穿到墙前 → **下钻**到墙缺口行 → 穿墙缺口 → 进焊盘场 → 落到本线焊盘 B。（一线一通道 · 长段直走 · 只换一次层 · 束与束不踩格。）
**② 挡路的是什么**：**贴墙那一列（col 113）是单行道，而 `OUT6_N` 一次下钻从 row 12 占到 row 43**；别的线要进墙缺口**必须穿这条道** ⇒ 两线在同一格顶上（机核 `(L1,113,19)` · 905/905 候选对全撞）。
**③ 人类方案**：**两段下钻**（下到一半 → 横挪一格道 → 再往下）——**在册已有先例**（**R580 律 / R603**：`OUT0_N = H47·Xa117·Rm36·Xb116`）。登记该走法 ⇒ 独占消失。

## 二、《卡点报告》
| 项 | 内容 |
|---|---|
| **试过什么** | ① 六种构造式排法（最好 **13/16**，均零重叠）；② 精确判定（R668）⇒ **UNSAT ＋ size-2 核 `{OUT6_N,OUT7_P}`**（复核）；③ 前提修订 v2（R670 出口带）⇒ **校准未过**；④ **本次＝唯一一次实现：登记"两级下钻"路由权**（在册先例） |
| **为何不通** | 钉子＝**单级下钻**把贴墙唯一列 113 整段独占；只要允许两级下钻，独占即消失（**本次校准已机核证实**） |
| **缺口在哪层** | **方案层（走法/路由权利）**——非板容量、非门带、非搜索力；且**该走法在册已有**（R580/R603）⇒ 本席上一件的 UNSAT 证书是**"模型相对"**（已自纠） |

## 三、**一次实现**（本件唯一执行 · 结果如实）
- 件（生成器）：`K2_R672_TWOSTAGE_ALLOCATION_v1.py`（新窗口件 · 只**读**在册件）
- **阶段一 · 校准先行**（#K2-255 §三.3c）：在冲突对 `{OUT6_N, OUT7_P}` 上 ⇒ **机核 `ok=True`（nodes=2）** ⇒ **两级下钻确实给路** ✓（日志原样在册：`K2_R672_solve_ABORTED.log`）
- **阶段二 · 全模型**：**被本席自己的时间盒终止**（约 20 分钟未收敛；两级候选枚举规模过大 ⇒ **工具效率问题**，非几何问题）⇒ **无件、无二值**
- **未重跑**（遵停止令）；**判定未达 ⇒ 不冒充**。

## 四、下一步（请监理一句话）
- 令中"一次实现"已用（结果＝**校准 PASS**）；**全模型二值**需**再一次有界执行**（把枚举限成有界候选：每线候选上限 ＋ 迭代序固定）——**可否？**（若不许，则本件即为卡点报告终稿：**校准已证有路，全模型待跑**。）

## 五、边界
冻结四源 **4/4 MATCH** · criteria 只读 · 在册件**一字未动** · 未派 WORKER · **零描线** · **P4 未归零 ⇒ 不导 Gerber/不进 P5/不碰下单**。 OWNER-ITEMS: 0

—— ENG（ARCHER）· 承**监理停止令** · 2026-09-26 · 本件为 **R672**
