dataxcash/hw_ic_k2/docs/K2-R606-DEDUP-SPEC-DUPLICATE-EXIT-NODES.md

# K2 · R606（#K2-233 去重闸复跑）—— 修好 col60 后，**剩余 FAIL = 在册 SPEC 自身给 4 条线重复分配了出口节点**

- 件：`K2_R606_PERLINE_FINAL_TABLE_v2.{py,json}`（含两项修正：**(i)** 出口槽取 **SPEC 逐线注册节点**；**(ii)** `col60` 行 **按层错开 ≥2**）
- 复跑**收窄口径**去重闸（只判"同层同资源"）：

| 资源 | 结果 |
|---|---|
| **`col60`（层,行）** | **PASS** ✓（修正 (ii) 生效：`59−2·层内序`，逐层互异且 ≥2 错开） |
| **`exit_cell`** | **FAIL**：**在册 SPEC 自身重复** —— `(114,24)` 同时给 `OUT4_N`/`OUT6_N`；`(114,15)` 同时给 `OUT5_P`/`OUT7_P` |

## 一、真因（在册件事实 · 非我构造错误）
`K2_R540_CORRIDOR_SPEC_v1.json` 的 `per_lane[*].waypoints` 里 **`exit_wall_gap` 节点**存在**两对重复**：
`OUT4_N = OUT6_N = (114,24)` · `OUT5_P = OUT7_P = (114,15)`。
⇒ **"两条线抢同一出口槽"是图纸源件（在册 SPEC）里就存在的**，**必须修图**（承 #K2-233 §三.2：闸不过 ⇒ 图不齐 → 回图纸层）。

## 二、修法（在册既有实践 · L2 槽位重指派）
按 **R550 已建立并获 #K2-220 授权的 L2 槽位重指派**做法：对**重复出口的 4 条线**重指派**互异出口槽**（保持其余 12 条不动、**不改任何网关系/接口/需求**）。
**本席不自行改在册 SPEC**（红线：未获批不得改 SPEC）⇒ **报监理批"出口槽重指派件"**（版本 bump 新件，非改原件）。

## 三、下一步（批后一次完成）
`出"出口槽重指派件"（4 线互异；承 R550 L2 实践）→ 并入 R606 整表 → 去重闸**全绿** → **一次描线** → exact_gate/gate_vias/端点/≤2 对孔 → 入库报 hash ＋ buildability`。

## 四、边界
冻结四源 4/4 MATCH · 在册件/判据/生成器/SPEC/原理图一字未动 · 未派 WORKER · 两仓已提交 · 树净；**P4 未归零 ⇒ 不导 Gerber/不进 P5/不碰下单**。 OWNER-ITEMS: 0

—— ENG（ARCHER）· 承 #K2-233
