dataxcash/hw_ic_k2/docs/K2-R582-STOPORDER2-PLAN-AND-BLOCKER-REPORT.md

# K2 · 第二次停止令响应 —— **回 Plan 三问 ＋ 卡点报告**（本窗不再重跑）

- 依据：监理停止令（连错 2 次 · 第八章第 8 条）· #K2-225
- 本件动作：**停止迭代（零构造运行）**；交出 Plan 三问 ＋《卡点报告》，具名报监。

## 一、Plan 三问（人类工程师路径 · 大白话）

**① 信号怎么走**：A 焊盘 → 自己口袋 → **自己竖井（列 d）** → 沿**自己腰带行（行 H）**向东 → **col60 断面槽位** → 继续向东到**墙前** → 沿**规则取用的列**逐段下行（段按机核"全幅行"切；某段太长就**对半劈**）→ 到**出口行** → **自墙缺口 / 墙东侧**接近注册出口槽 → pad → **B 焊盘**。

**② 挡路的是什么**：
- **不是**板子没地方（守恒余 **+37**）。
- **(a) 墙**：`col 114` 在**行 36 是墙** ⇒ **东组末段不能从墙西横穿**，必须**自墙东侧**接近 `(exitc,36)`。
- **(b) 一条列下不到底**：西组纵向要下 **30–51 行**，而任何单列**最多连续 24 行** ⇒ 必须**分段（对半劈）**；本窗实测西组末段 **32 行无单列可用 = `NO_COLUMN`**。
- **(c) 我方工具侧（连错 2 次直接原因）**：改规则时**丢掉了上一版已验证的规则**（R582 丢 R580 的"短段二分"）＋ 早前补丁**作用域错** ⇒ 规则**未集中成一份、上场前未先干跑**。

**③ 人类方案（大白话）**：**把三条规矩合成一份再上场**——① 列从"**离出口最近**"开始找；② 某段**下不到底就"对半劈"**（不是试深浅）；③ **东半组自墙东侧下来、西半组自墙前缺口进**。合成后**先在两条已知能走的线上试跑**，通了**再画整张图**。

## 二、《卡点报告》（试过什么 / 为何不通 / 缺口在哪层）

| 窗口 | 试过什么 | 结果 / 为何不通 | 缺口层 |
|---|---|---|---|
| R578 | 单列定尺 | 东 **8/8 PASS**（22=22）；西 **8/8 FAIL**，缺口**恒为 −4 行** | 方案层（尺寸） |
| R579 | 按"全幅行"切段 | 西组**只剩末段 SHORT**（−4） | 方案层（尺寸） |
| R580 | **＋递归二分（规则）** | **16/16 PASS** ✓ | 方案层（定尺完成） |
| R581 | 完整分段（横段＋纵段同定尺） | 下行 PASS；**末段到出口槽 16/16 阻塞** | 方案层（末段未定尺） |
| R582 | 列改按"邻近出口"取用 | 下行 PASS；**但我方丢了二分** ⇒ 西组末段 `NO_COLUMN`（已交 ERRATA 自纠） | **ENG 工具层（规则未合成）** |

**结论**：卡点已收敛为两条**具名**事项——**(a)** 末段（专列→注册出口槽）**尚未定尺**（东组须走墙东侧；西组须保留二分）；**(b)** 三条规则**尚未合成一份、未先干跑**。**不是不可行**（R569 见证在册）⇒ **不出乙**。

## 三、一次实现（合成后 · 禁试参）

`三规则合成（R580 二分 ＋ R582 邻近出口列 ＋ 末段规则接近）→ 重出 16/16 定尺表 → 干跑自检 fails=0（R569 两线）→ 一次融合出图 → exact_gate/gate_vias/端点/≤2 对孔 → 入库报 hash ＋ buildability`；FAIL ⇒ 仍**只准二值**。
**未获放行前不再自行重跑。**

## 四、边界

冻结四源 4/4 MATCH · 在册件/判据/生成器/SPEC/原理图一字未动 · 未派 WORKER · 正式产物非 `/tmp` · 两仓已提交 · 树净；
**P4 未归零 ⇒ 不导 Gerber · 不进 P5 · 不碰下单**。 OWNER-ITEMS: 0

—— ENG（ARCHER）· 2026-09-25 · 遵第二次停止令（回 Plan · 待放行）
