dataxcash/hw_ic_k2/docs/K2-R576-STOPORDER-PLAN-AND-BLOCKER-REPORT.md

# K2 · 监理停止令响应（红线：连错 2 次）—— **回 Plan 三问 ＋ 卡点报告**（本窗不再重跑）

- 依据：监理停止令（连续错误 2 次 · 第八章第 8 条）· #K2-223（融合 · 二值）
- 本件动作：**停止迭代（未再运行任何构造/工具）**；交出 Plan 三问 ＋ 卡点报告，具名报监。

## 一、Plan 三问（人类工程师路径 · 大白话）

**① 信号怎么走**：
A 焊盘（西侧梳齿里的球）→ **自己口袋**里下钻到**自己的竖井**（列 `d`）→ 沿**自己那条腰带行**（行 `H`）一路向东 → 过 **col60 断面槽位**（同一行继续）→ 到**墙前** → 沿**自己的竖列**纵取到**自己那个墙缺口行** → **穿墙缺口** → 到出口槽 → 到 **B 焊盘**。
要害：**中段与尾段共用同一条腰带行 `H`**；**墙只能在各线自己的缺口行穿过**。

**② 挡路的是什么**：
- **不是**板子没地方（守恒余 **+37**；行/列容量都够）。
- **墙带**（col ≈114–119）**在绝大多数行被封**，只有各线自己的缺口行能穿（R571-F5 机核：西组缺口行 = 各自 `exit_row`）。
- **耦合**：中段腰带行必须**同时**满足"口袋→col60 全合法"与"col60→墙前全合法"。
- **东组出口槽都挤在 row 36**（`(114,36)` 是墙）⇒ **一行只能服务一条**；东组须各自分行（墙东 **16 列 120–135** 可用，F3 机核）。
- **我方工具侧**：把"一条行/一条列硬贯通"当唯一写法（四连窗失败）；另有**两处脚本补丁作用域错**（连错 2 次的直接原因）。

**③ 人类方案（大白话）**：
**别指望一条直线走到底。** 让每条线**沿自己那条腰带行向东**，到**自己那个墙缺口**再**拐弯穿过去**——各行、各缺口，互不相抢。
拐弯段**不用直线**，用**"走廊"**（宽一点的路带，锚点间距 ≤20 格、带宽 ±6）：**由已验证的填充器在走廊里自己绕障**（硬预留、单遍、不回溯）；我们只把走廊的**入口 / 拐点 / 出口**标死。这与在册已验证的"入口前缀"同型（`fails=0`）。
**一次实现**：一行作用域修正（守卫移出 H 循环体）→ 一次融合运行 → 廊道填充 → `exact_gate` → 报 hash。

## 二、《卡点报告》（试过什么 / 为何不通 / 缺口在哪层）

| 窗口 | 试过什么 | 为何不通 | 缺口层 |
|---|---|---|---|
| R564 | 前提 v2「北巴士」 | **北带 rows 24–34 在 In5 全封** ⇒ 11 线挤 3 行 = 鸽笼 | **方案层（前提被证伪）** |
| R567 | 前提 v3 S2 + 一次出图 | 我方**过严检查器**（轴对齐规则）误伤在册对角弧 | ENG 工具层 |
| R568 | 修检查器后再出图 | 我方**单位错**（wp 传节点号而非位置号） | ENG 工具层 |
| R569 | 修单位 + 单位闸 | 3 岗+单位闸全 PASS；**2/16 整线画通**；续画时**同层尾段互锁**（前条自由尾段占 318 格） | **方案层（尾段无有序分配）** |
| R570/R571 | 尾段自由带盘点（只读） | F1 **无全程竖列**；F3 墙东 16 列；**缺口行集**机核 | 方案层（信息补全） |
| R572 | 融合：H 与尾段耦合 | 我方**本线自有格阻塞**误判（R541b 类）→ 修正后仍 15/16 无解 | ENG 工具层 + 方案层 |
| R573/R574/R575 | 耦合 + 东组接近行通道 + 西组三段阶梯 + 行软序 | **墙带**（cols 114–119）多数行被封 ⇒ "一条行贯到墙东"不可得 | **方案层（墙带为真正瓶颈）** |
| R576 | **尾段改为"声明廊道"**（锚点 ≤20 格 + 带 ±6） | 首轮 **16/16 廊道生成成功**（方法突破）；补丁把"无解守卫"**误插进 H 循环体** ⇒ 运行作废（连错 2 次的直接原因） | **ENG 工具层（作用域缺陷）** |

**结论**：**方案层缺口已收敛为一条明确写法**（腰带行耦合 + 各自墙缺口 + 廊道填充），**不是不可行**（R569 已证西组代表线尾段可整条画通 190 格/0 孔 ⇒ **不出乙**）；当前拦路的**只剩下 ENG 工具层的一行作用域缺陷**。

## 三、下一步（**遵停止令：本窗不再重跑**）

一行作用域修正（把"无解 ⇒ 报诊断"守卫移出 `H` 循环体）→ **一次**融合运行（廊道锚点吸附 → 三岗/容量 → 一次描线 → `exact_gate`/`gate_vias`/端点/≤2 对孔 → 入库报 hash）；FAIL ⇒ 仍只准二值。
**未获监理放行前不再自行重跑。**

## 四、边界

冻结四源 4/4 MATCH · 在册件/判据/生成器/SPEC/原理图一字未动 · 未派 WORKER · 正式产物非 `/tmp` · 两仓已提交；
**P4 未归零 ⇒ 不导 Gerber · 不进 P5 · 不碰下单**。 OWNER-ITEMS: 0

—— ENG（ARCHER）· 2026-09-25 · 遵停止令
