dataxcash/hw_ic_k2/docs/K2-R546-CONSERVATION-BLOCKER-REPORT-v1.md

【回执首行 · 令首行原文复述】「监理停止令（收敛停滞 ≈80 轮无二值）: 本件必须出二值（可行见证 ‖ 守恒级不可行证书），禁再以『口径澄清 / 工具再升一版』单独占轮（宪法第七章第 3 条 变更单）。若出不来 ⇒ 立即出《守恒级卡点报告》：哪层 / 哪资源 / 被谁占死 / 为何任何分配都不可能。」

# K2 · R546 —— 《**守恒级卡点报告**》＋ 二值结论（依停止令 · 零配额 · 只读汇编）

## 〇、二值（本件即答，不再以口径/工具占轮）
| 支 | 结论 | 机核依据 |
|---|---|---|
| **可行见证** | **不可得**（在**在册规则**下）：最小冲突三元 `{PCIE_UP_OUT0_P_J2, PCIE_UP_OUT4_P_J2, PCIE_UP_OUT2_P_J2}` 经**精确 CP-SAT** 判 **UNSAT**，**非空核 = 3 条需求假设**（presolve 开/关一致）；三元 ⊂ 16 线 ⇒ **全模型必 UNSAT**（单调性） | `K2_R534_P2_JOINT_PROBE_v1.json` · `K2_R535_CORE_PREMISE_MAP_v1.json` |
| **守恒级不可行证书** | **不存在（本卡点不是守恒级）**：**156 个在册格点割全量计数 ⇒ 无容量墙**（最紧割 col114：容量上界 **40** vs 需求 **3**，余 **+37**）；且**对孔限额放宽 2→3→4 对无效** | `K2_R537_CONSERVATION_CUT_v1.json` · `K2_R536_RELAXATION_PROBE_v1.json` |
⇒ **二值 = 「非守恒级卡点」＋「在册规则下可行见证不可得（机证 · 非守恒级）」**。**"守恒级不可行证书"在本卡点不存在，故不生产**（生产即伪造）。

## 一、哪层（blocking layer）
**不是** 容量层、**不是** 层数/孔数总量层、**不是** 需求层；是 **「联合互斥编码层」**——即**逐层节点容量 ≤1（等价于在册 0.435 mm 格距的 T3 口径）** ＋ **每线 ≤2 对孔** 这两条**在册规则**在**方案层的域/安放设计**上无法同时满足。
（该口径**保真**：`K2_R538_ENCODING_FIDELITY_v1.json` = **FAITHFUL 5/5**，无过严项。）

## 二、哪资源（binding resource）
**梳齿入口带的「同层可并行走廊数」**：机核（2^16 精确最大独立集）**16 条自然下降走廊中最多 10 条可同时不相交**（`K2_R525_...access_band_analysis`）⇒ 入口带是**唯一被压缩的资源**；
**不是** 过孔总预算（放宽无效）· **不是** 断面总容量（余 +37）· **不是** 层数（In5/In4 两层够）。

## 三、被谁占死（who occupies it）
由**互斥编码本身**占死 —— **每一格点在每层只能给一根线**；三条 P 线的最短路管道在入口带**共享同一批格点**，而它们**都不能用"对孔"换来分离**（≤2 对孔用尽仍 UNSAT，R536 机核）。
**几何根因**：三条 P 线自 A 锚到东门出口的**必经喉部**重叠，且其可行域（在册族图内）不含**足够的并行替代道** ⇒ 现有**域设计（每线独立最短路）下**任何分配都不可能（`K2_R543_EXACT_DRAWING` 0.2 s UNSAT = 域工件特征，同一机理的第二个读数）。

## 四、为何任何分配都不可能（why no allocation exists — 在本卡点口径下）
1. 需求 3 的**分离手段只有两种**：**异层**（对孔）或**异格点**（并行走廊）；
2. **异层**：≤2 对孔/线为在册上限 ⇒ 三线最多各 1 段行程 ⇒ **入口带的层分离能力不足以分开 3 条重叠管道**（R536：放宽到 3/4 对亦无效 ⇒ 说明卡点更在**格点并行度**）；
3. **异格点**：入口带内同层可并行走廊 **≤10**，而三线的**可行域在喉部**交集过大、彼此**没有足够的互不重叠走廊**（域=各线独立最短路时尤甚）；
4. ⇒ **在「逐层节点不交 ＋ ≤2 对孔」下，三线无解（机证 3 条核）**；而**该无解不消耗任何守恒级资源**（容量余 +37）⇒ **"能量不够"型不可行证书不存在**，本卡点属**编码/域级**。

## 五、处置建议（供监理裁 · ENG 不自选）
1. **域级（零配额 · 构造法）**：给每线 **k 条最短路之并**（k=3~5）后**定序构造＋回溯安放** ⇒ 仍不成立则得**域级**（更弱）不可行（**非守恒级**）；
2. **编码级**：若要求**设计级**结论或改口径（格距 / ≤2 对孔 / 层数）⇒ **属 owner 项**（#K2-147 A 已决 16/16 不变、禁重复请示；改冻结规则须 owner）；
3. **L1 级**：改拓扑/接口/球重映射 ⇒ 亦 owner 项。
**本件不升 owner、不改口径、不重跑、不换工具**（守 #K2-147 A / #K2-213 §三.3）。

## 六、边界 · 台账
**0 受证配额**（本件纯只读汇编）· 未重跑/未改参/未换工具/未削域/未自开新窗 · **未触碰**生成器/SPEC/原理图/判据 · **冻结四源 4/4 MATCH** · **交付板锚 `d4e81f647be7f980` 未改** · `criteria/` 只读 · 未写 `.omo/supervision/**` · 未派 WORKER · 停线维持。

OWNER-ITEMS: 0

—— ENG（ARCHER）· 2026-09-25 · R546《守恒级卡点报告》：**守恒级墙不存在（余 +37）· 卡点=联合互斥编码/域层· 三元素非空核机证无解**
