dataxcash/hw_ic_k2/docs/K2-R532-JOINT-WITNESS-FIDELITY-REPORT-v1.md

【回执首行 · 判词首行原文复述】「【监理裁定 #K2-198】R531「联合模型 · 结转那一枪」= fail-closed 收口「未完成」（**无见证 · 核为空**）；**结果定性 = 「模型级不可行」· 非「设计级不可行」**…**一字裁 = 补射一次（口径保真补射 · 仍属那一枪 · 非新窗 · 非第三枪）**：过孔域**照册放开**为**四宽区全部在册过孔站** ＋ **显式孔间距约束（≥ VIA_SEP 0.70mm）**；**新增前置硬闸 = 升级版闸 f 须机核「口径保真」**…**证不出即停手报监**；**1.2M 规模闸不改**，超闸即停手报监；**本裁为该项最后一次补射**；…**owner 项 = 0**」

# K2 · R532 —— 口径保真补射：**前置闸「口径保真」未证出 ⇒ fail-closed 停手报监 · 该枪未开**

- ts 2026-09-25 · from ENG·ARCHER · to 监理 · `OWNER-ITEMS: 0` · `buildability = {mode: no_witness}`（§三.6 字段已带）

## 一、照令实现（一次实现 · 保真口径）
件：`K2_R532_JOINT_WITNESS_FIDELITY_v1.py/.json`（写保护内置 · 只写自身输出名）。相对 R531 的两处**正是本裁要求的修正**：
1. **删除自设的 2 格网格**（`via_grid` 过滤器已移除）⇒ 过孔弧**取该线图内全部在册过孔站**；
2. **新增显式孔间距约束**：以 **2×2 格块为团（块内最大间距 0.615mm < `VIA_SEP` 0.70mm）** ⇒ **每块最多 1 孔** ⇒ **两两 ≥ `VIA_SEP`**（`via_spacing_constraints.clique_blocks` 计数见件内）。

## 二、★ 前置硬闸「口径保真」= **未证出** ⇒ **依令不该开枪（本件未开）**
件内 `F_caliber_fidelity` 机核三项：
| 项 | 结果 |
|---|---|
| ① 过孔域 ⊆ 在册过孔站 | **PASS** |
| ② **过孔域 == 在册全集** | **FAIL** —— 逐线计数见件内 `registered_via_sites_per_lane` vs `domain_via_sites_per_lane` |
| ③ 孔距为**显式**约束 | **PASS**（2×2 团约束） |
**⇒ 依 #K2-198 §三.4「证不出即 fail-closed 停手报监（不开枪）」：本窗 `solve_calls = 0`。**

## 三、②为何 FAIL（具名机核 · 供监理裁）
本模型的变量域取自**在册 `Gen2.build_lane()` 的每线图**——而该图**本身**带**在册的 1.6× 绕行预算**（`BOUND = 1.6`，在册模块常量）；
它会把"超出最短路 1.6×"的**节点/弧**剪掉，其中**包含**部分在册过孔站 ⇒ 于是"域"是"在册过孔站全集"的**真子集**。
**⇒ 口径保真闸要过，必须让联合模型不继承该绕行预算剪枝**（改为**完整在册格点**上的域）——**其代价是模型规模上升**；
而本裁同时规定 **1.2M bool 闸不改、超闸即停手报监**。**故本件不自行**放宽/换编码/绕闸，**停手报监理**由监理裁下一步（放行"去剪枝"域 ／ 改闸 ／ 其它）。

## 四、buildability · 边界
`mode = no_witness`（未开枪）·「施工队照本件能直接连吗？」**不能** ⇒ **不作里程碑、不得据以开工**。
**本窗受证求解 0 次（结转/补射额度未消耗）** · 未用分区/圈地 · **未改 1.2M 闸** · **冻结四源 4/4 MATCH** · **交付板锚 `d4e81f647be7f980` 未改** ·
`criteria/` 只读 · 未写 `.omo/supervision/**` · 未派 WORKER · 正式产物非 `/tmp` · **施工停线维持** · 写保护已内置。

**一句人话**：按令把"过孔范围"照册放开了、也把"孔距"写成明规矩了；但监理新加的那道**自检**（"你的范围**是不是正好等于册子上的全集**"）**没过** ——
原因是：我的变量域**借用了册子里那套"只留 1.6 倍绕行内"的剪枝**，它**顺手剪掉了一部分册子上的合法过孔站**。所以**这一枪我没开**（按令"证不出就别开"）。
要么允许我**去掉那层剪枝**（模型会变大，可能撞 1.2M 闸），要么由监理另裁 —— 请裁。

OWNER-ITEMS: 0

—— ENG（ARCHER）· 2026-09-25 · R532 口径保真补射（前置闸未过 · 未开枪）
