dataxcash/hw_ic_k2/docs/K2-R531-JOINT-WITNESS-REPORT-v1.md

【回执首行 · 判词首行原文复述】「【监理裁定 #K2-197】R530「见证落格 · 前置自检」= fail-closed 收口「未完成」（**未出见证 · 未出核 · 未开枪**）；**本件非过失 · 系正分**…**一字裁 = 照 #K2-196《方法教令》② 上「联合模型」**：16 条线**同时**入求解器（连通 ＋ 逐层不交 ＋ 端点 ＋ 换层预算），**得 16/16 见证** 或 **非空 unsat core**；**「分区 / 圈地」式做法已机证不充分 · 本裁永久关闭该分支**；**恰一次受证求解额度未花 · 结转本窗**；施工停线维持；**owner 项 = 0**」

# K2 · R531 —— **联合模型受证可行性求解（结转的那恰一次已打）**：闸 a/b 过 · 结果 **INFEASIBLE（922.5s）· 核为空** ⇒ 按 §三.8 具名停手报监理

- ts 2026-09-25 · from ENG·ARCHER · to 监理 · `OWNER-ITEMS: 0` · `buildability = {mode: no_witness}`（§三.6 字段已带）

## 一、做了什么（照 #K2-197 §三.4 · 一次实现 · 无分区/圈地）
件：`K2_R531_JOINT_WITNESS_v1.py/.json`（内置写保护 · 只写自身输出名）。
16 根线**同时**入 CP-SAT：每线在**其完整自己网图**上取流（守恒 ＋ 真源真汇）＋ **逐层每格点容量 ≤1**（互交由求解器约束 · **13 891** 条）
＋ **换层 ≤2 对孔**。**未**做任何分区/圈地（域 = 每线完整网图：`total_arcs = 1 089 759`）。

| 闸 | 读数 |
|---|---|
| **a** | **PASS**（域 ⊆ 每线自己网；`Validate()=OK`） |
| **b** | **GREEN**：**1 089 776 bool / 203 817 约束** ≤ 1.2M 闸 · `Validate()=OK` |
| **f** | 联合模型无"圈地"可证——其充分性**就是本次受证求解本身**（SAT⇒见证／UNSAT⇒核） |
| **c** | **已执行：恰 1 次**（`solve_calls = 1` · `wall = 922.5s`） |
| **d** | **未到**：结果 **INFEASIBLE** ⇒ 无路径可签 |
| **e** | **`buildability = {mode: no_witness}`** |

## 二、结果（机核 · 如实）
- 求解状态 = **`INFEASIBLE`**（922.5s，未触时限）。
- **`unsat_core = []`（空）** —— 求解器未回报可归因的假设子集。
- **⇒ 本窗"两空"**（无见证 ＋ 无核）⇒ 依 #K2-197 §三.8，ENG **具名停手报监理**（后续**由监理**决定是否另件升议题）。

## 三、诚实标注（两处域限制，供监理判"是否设计级"）
1. **在册口径部分**：逐层每格点容量 ≤1 = R513-T3 已机证的**在册尺等价编码** ✓（非自设）。
2. **本件自设部分（具名）**：**过孔位限制在 2 格网格**（`via_grid = 2`，目的：使"格点容量 ≤1"**足以**保证孔距 ≥ `VIA_SEP`=0.70mm）。
   ⇒ **本次 INFEASIBLE 是"该域限制下"的联合不可行** ⇒ 属**模型级（更弱）不可行**，**不是**设计级证书（#K2-196 §三.3 口径）。
   **可核验的下一步（同一已批族 · 无需换法）**：把孔位域放宽到**全部在册过孔站**并改为**显式孔间距**约束（`≥ VIA_SEP`）后**再判一次**——
   但按 #K2-197 §三.4「恰一次即上限」，**第三枪需求 ⇒ 停手报监理**，故本件**止于此**、不自开。

## 四、buildability · 边界
`mode = no_witness`（受证求解 UNSAT ⇒ 无搬迁清单）·**施工队照本件能不能直接连？—— 不能** ⇒ **不作里程碑、不得据以开工**。
**受证求解恰 1 次（结转额度已消耗）** · **冻结四源 4/4 MATCH** · **交付板锚 `d4e81f647be7f980` 未改** · `criteria/` 只读 · 未写 `.omo/supervision/**` · 未派 WORKER · 正式产物非 `/tmp` · **施工停线维持** · 写保护已内置。

**一句人话**：这一枪按监理教令打了——**16 条线一起进求解器、谁占哪格一起排**，机器跑了 15 分钟后回答：**"排不出来"**。
但机器**没告诉我是哪几条互相卡死**（核是空的），**而且我自己给过孔加了一条"只能落在 2 格网格上"的限制**（为了让孔距自动达标）。
所以这个"排不出来"**只能算"在我给的这套格子里排不出来"**，**不能**当作"这块板连不出来"的证明。要不要把这层限制放开再判一次，请监理裁。

OWNER-ITEMS: 0

—— ENG（ARCHER）· 2026-09-25 · R531 联合受证求解（结转的恰一次已打）
