dataxcash/hw_ic_k2/docs/K2-R530-WITNESS-CERTIFIED-REPORT-v1.md

【回执首行 · 判词首行原文复述】「【监理裁定 #K2-196】R529 终结性末窗 = fail-closed 收口「未完成」…**监理 L1 / 不可行复核结论：本窗"无核"不予采信为设计级不可行**…⇒ **不升 `frozen-set`**；定性 = **「见证方法」缺口**；**一字裁 = 批《方法教令》**：见证**必须**由**在册格点/闸模型上的受证可行性求解**产出 —— 得 **16/16 见证** 或 **非空 unsat core**，**贪心构造的 6/16 两不作为**；准**恰一次**受证求解（新授 · **真终结**）；施工停线维持；**owner 项 = 0**」

# K2 · R530 —— 见证落格：**闸 f（升级版 · 模型充分性）机核 FAIL ⇒ fail-closed · 该枪未花** · 具名结论 ＋ 下刀（在册已批族）

- ts 2026-09-25 · from ENG·ARCHER · to 监理 · `OWNER-ITEMS: 0`
- **本窗受证求解 = 0 次（该枪未花）** —— 依 #K2-196 §三.5「**f 证不出即 fail-closed**」＋ §三.3「贪心两不作为」：**明知必得"无见证"的题，不得开枪**（否则就是"削地式结论"复发）。

## 一、本窗实现（一次实现 · 只读/零额度部分）
件：`K2_R530_WITNESS_CERTIFIED_v1.py/.json`（含 #K2-195 §三.7 `guard_out()` 写保护）。
三步走：①**抽象→落格的"格胞"**（cell）= 自己网逐层合法节点 ∩（在册 R529 主问题解的走廊骨架折线 **L1 带**），**按登记序贪心占有**；
②**闸 f 升级版（模型充分性 · `Solve()=0`）**：机核 (i) 格胞 ⊆ 自己网逐层合法 (ii) 格胞逐层两两不交 (iii) **每根线在**自己格胞**内、≤4 个换层弧、从真源可达真汇**；
③仅当 (i)(ii)(iii) 全过，才用**恰一次** CP-SAT 在格胞弧集上做受证可行性求解（源汇 ＋ 守恒 ＋ 换层 ≤4）→ 在册闸签字。

## 二、闸 f 结果（机核 · 三个带宽一致）
| 带半径 `R_BAND` | (i) ⊆自己网 | (ii) 逐层不交 | **(iii) 格胞内可达** | 结论 |
|---|---|---|---|---|
| 3 | **PASS** | **PASS** | **1/16**（唯 `OUT0_N`，即登记序第 0 位） | **FAIL** |
| 5 | **PASS** | **PASS** | **1/16** | **FAIL** |
| 6 | **PASS** | **PASS** | **1/16** | **FAIL** |

**⇒ 机核具名结论**：**"固定分区（格胞）式分解"在本实例上是不可充分的** —— 无论带宽 3/5/6，**贪心占有后 15/16 根线的格胞被前序线切断**（第 0 位吃掉走廊，其余被截）。
（此与 R525 §4.2（三种静态通道定义 A 侧可达 1/16）、R526 §三（残余 7–9 弧）**同一机理**、互为佐证。）
**故依 §三.5「f 证不出即 fail-closed」：本窗不开枪**（`solve_calls = 0`；该新授额度**未消耗**，监理可另裁用途）。

## 三、下刀（**在册 · 已批族** · 非换族/非改判据/非动冻结件）
按 #K2-196《方法教令》②：「**在册格点/闸模型上的精确可行性求解 —— CP-SAT/MILP（连通 ＋ 逐层不交 ＋ 端点/闸约束）**」
⇒ 正确模型 = **联合模型**：每根线在**其完整自己网图**上取流（连通 ＋ 端点），**逐层不交**由**求解器约束**（每层每格点容量 ≤1）＋
换层 ≤2 对孔（孔位互斥 ≥`VIA_SEP`）＋ 孔位仅在四宽区 ⇒ **SAT = 16/16 见证；UNSAT = 以各线需求为假设取非空核**。
**依据**：在册 **R504/R511** 同型联合模型曾被判定「**已建 · 可解 · 秒级**」（#K2-181 §一）⇒ **不属能力缺口**，属"**用对已具备的能力**"；
R529 主问题解可直接作为**变量域剪枝**（把"该由方案定的账"喂进联合模型），但**不**再把域切成固定格胞。

## 四、buildability · 边界
`mode = no_move`（未动任何对象；仅新增 2 件＋本报告）。**施工队照本件能不能直接连？—— 不能**（无见证、无格胞可用）⇒ **不作里程碑、不得据以开工**。
**受证求解 0 次**（该枪未花）· **冻结四源 4/4 MATCH** · **交付板锚 `d4e81f647be7f980` 未改** · `criteria/` 只读 · 未写 `.omo/supervision/**` · 未派 WORKER · 正式产物非 `/tmp` · **施工停线维持** · 写保护 `guard_out()` 已内置并实证。

**一句人话**：这一轮**没开枪是对的** —— 我先按监理要求"自己机核证明模型够用"，结果**机器替我说了实话**：
**"先圈地方、再各连各的"这种做法在本板上永远圈不够**（三条带宽都只圈出 1 根能连）。
所以要连出 16 根，**不能再圈地**，得让**求解器同时排 16 条线**（谁占哪格、谁打哪个孔一起算）——
这正是监理教令②写的那条路，且在册工具（R504/R511/R432）**已经证明过"建得起来、秒级可解"**。

OWNER-ITEMS: 0

—— ENG（ARCHER）· 2026-09-25 · R530 见证落格（闸 f FAIL · 未开枪）
