dataxcash/hw_ic_k2/docs/K2-R529-WOVEN-COMPLETE-REPORT-v1.md

【回执首行 · 判词首行原文复述】「【监理裁定 #K2-195】R528 精化窗 = fail-closed **收口「未完成」**（受证求解恰一次 · `OPTIMAL` 但**无见证：8/16** · 额度已耗 · 非证书非里程碑）；**触发 #K2-194 §三.6 终结条款 ⇒ 监理「生产方式复核」**：定性 = **「一窗只显式化一层决策」的逐层挤牙膏式生产法 = 方案完备性缺口**；**一字裁 = 批** —— 但**不是**再批"再剥一层"，而是**要求「完整内生」**…**＋ 附「决策完备性」机核自检**（证主问题变量集**闭合**）；**准一次（终结性）窗口**…**本窗为 P4 该项最后窗口**；…**owner 项 = 0**」

# K2 · R529 —— **完整内生主问题 ＋ 闸 f 决策完备性自检 ＋ 新授的恰一次受证求解**：闸 a/b/f 全过 · 主问题 **OPTIMAL/SAT** · 仍**无见证（6/16）** ⇒ 按 §三.6 **具名停手报监理**

- ts 2026-09-25 · from ENG·ARCHER · to 监理 · `OWNER-ITEMS: 0`

## 一、闸（含本窗新增 **f**）
| 闸 | 内容 | 结果 |
|---|---|---|
| **a** | 前置只读保真自检（`Solve()=0`）：入口动作/断面槽位均取自在册合法位置 | **PASS** |
| **b** | build-only **0 求解** | **GREEN**：**4 824 bool / 15 811 约束** · `Validate()=OK` · ≤1.2M 闸 |
| **f** | **「决策完备性」自检**（只读 · `Solve()=0` · **主问题变量集闭合**） | **PASS (closed)** |
| **c** | **恰一次**受证求解（新授一次） | **OPTIMAL**（`wall=152.0s`） |
| **d** | 在册闸签字 | **未到**：路由 **6/16** |
| **e** | `buildability` | **`no_move`** |

**闸 f 内容**（件内 `F_decision_completeness`）：①**绑定决策族逐条对表**（时刻表 · 入口动作 · `col33`/`col60`/出口三断面槽位 · 同轴相邻断面 **form C 序关系** · 58 反序层分离 · 焊盘序=几何事实非决策）⇒ **无任何绑定决策留给实施阶段**；
②**位置集机核 ≥2P 间距**（`col33`15 · `col60`10 · 出口西 6/东 11 个位）⇒ 同层同断面必然 claim 相容；③**预解校准**：把**在册 R528 解**投影到本模型 ⇒ **两两 claim 冲突 = 0**。

## 二、主问题解（`OPTIMAL`）：**决策侧已闭合且 SAT**
打捆 `COMB 5 / BELT 6 / WALL 3 / FIELD 1` 根下 In4 · 入口 **5 DIVE ＋ 11 In5** · **三断面槽位全部由方案算出**（例：`OUT3_N: col33→33, col60→54, exit→131`）· form C 约束 296 条全满足。

## 三、★ 终结读数：**堵的不是"少一个变量"，而是"抽象走廊到格点层的可实现性"**
- 路由（**硬执行方案选定的断面槽位链** ＋ 硬声明集预留 ＋ 确定性两遍修复 · **0 次受证求解**）最好 **6/16**。
- **对照**：R528（只内生化入口、其余自由搜索）= **8/16** ⇒ **把槽位也钉死后反而更差**（6 < 8）。
- **⇒ 具名结论（非证书）**：决策完备性缺口**已补**（闸 f PASS）；剩下的绑定是**抽象断面走廊模型 ↔ 在册格点/闸模型的保真落差**——
  断面级的"≥2P 间距 + 序不翻转"**只是必要**，**不蕴含**该 16 条走廊能在**在册格点**上**同时**claim-可实现（≤2 对孔、逐层不交）。
  即：**卡点是"抽象→实现的保真"，不是"再少一个决策变量"**。本窗**无核**。
- **依 §三.6**：**再「无见证」⇒ 具名结论 + 停手报监理；由监理做 L1 / 不可行复核**（无核 ⇒ 监理另件升级议题）。

## 四、§三.7 **写保护**（本窗已落 + 已实证）
两个新件均内置 `guard_out()`：**产出件只允许写自己的声明的输出名**，写向在册件路径**即拒写**。
实证：`--out K2_R526_WOVEN_WITNESS_v1.json` ⇒ `REFUSED (write-protection #K2-195 sec.3.7)`（exit 非零）；写自身输出名正常。

## 五、buildability · 边界
`mode = no_move`（未动任何对象；仅新增 4 件 ＋ 本报告。**施工队照本件能不能直接连？—— 不能**（6/16，无见证）⇒ **不作里程碑、不得据以开工**）。
**受证求解恰 1 次（新授 · 已消耗 `OPTIMAL`）** · 路由件 **0 次受证求解** · **冻结四源 4/4 MATCH** · **交付板锚 `d4e81f647be7f980` 未改** · `criteria/` 只读 · 未写 `.omo/supervision/**` · 未派 WORKER · 正式产物非 `/tmp` · **施工停线维持**。

**一句人话**：这一枪把"该由方案定的账**一次列全**"做到了（并自己机核证明**列全了**：**闸 f PASS**），机器也给出**最优解**；
但**照这张账去连**，**六根通、十根不通**，而**放开让它自由连**反而能连上八根 —— 说明**账本身没漏项，是"账"和"实际格子"之间还差一层保真**（同一层里两条走廊"账上不碰、格子上碰"）。这已不是"再补一个变量"能解的，请监理按 §三.6 做 L1 / 不可行复核。

OWNER-ITEMS: 0

—— ENG（ARCHER）· 2026-09-25 · R529 完整内生（末窗）
