dataxcash/hw_ic_k2/docs/K2-R528-WOVEN-ENTRANCE-REPORT-v1.md

【回执首行 · 判词首行原文复述】「【监理裁定 #K2-194】R526 编织式窗口 = fail-closed **收口「未完成」**（受证求解恰一次 · `OPTIMAL` 但**无见证** · 额度已耗 · 非证书非里程碑）；R527 只读事实件 = **受理**（零额度 · `Solve()=0` · 自认非见证）；交裁项由 3 收窄为 1，**一字裁 = 批**——把「入口站选择」**升为主问题变量**（**同一已批族内的模型精化 · 非换方法 · 非改判据 · 不动冻结件**）；**准对精化后实例再给「恰一次」受证求解**（放行范围 · 监理职权），R526 旧额度**已消耗**故为**新授一次**；硬闸照 #K2-192 §三.3 a–e（缺一 fail-closed）；**本窗为终结性窗口**（再无见证 ⇒ 届时**监理做「生产方式复核」**，不自动升 owner）；施工停线维持；**owner 项 = 0**」

# K2 · R528 —— 精化主问题（入口站＝决策变量）**一次实现 ＋ 新授的恰一次受证求解**：闸 a/b/c 全过 · **仍无见证** ⇒ 按 §三.6 **具名停手报监理**

- ts 2026-09-25 · from ENG·ARCHER · to 监理 · `OWNER-ITEMS: 0`
- **受证求解：恰 1 次（新授的那一次）· `OPTIMAL`** · **无见证（8/16）** · 闸 d 未到 · 施工**停线维持**。

## 一、闸（承 #K2-192 §三.3 a–e）
| 闸 | 内容 | 结果 |
|---|---|---|
| **a** | 前置只读保真自检（`Solve()=0`）：每个候选入口动作都机核「在自己网的在册合法图内」（In5 动作 = 路点可达自身网院行；DIVE 动作 = 在册自由接入腿合法 ＋ 该点**两层**合法 ＋ **在册过孔站**） | **PASS** |
| **b** | build-only **0 求解**：**652 bool / 1495 约束** · `Validate()=OK` · ≤1.2M 闸 | **GREEN** |
| **c** | **恰一次**受证求解（新授一次） | **OPTIMAL**（`wall=43.7s` · `objective=1004021`） |
| **d** | 在册闸签字（逐层 `exact_gate` ＋ 已修 `gate_vias` ＋ 端点） | **未到**：路由 **8/16** |
| **e** | `buildability` | **`no_move`**（无见证 ⇒ 无搬迁清单） |

## 二、精化主问题**做了什么**（#K2-194 §三.3 照办：入口站选择当决策变量）
- 主问题在原三族（打捆容量 · 行程时刻表 · 58 反序层分离）之上，**新增每根线的入口动作**（one-hot）：
  · `In5@列`（用在册自由接入腿可达的列，且该列在自己网 In5 图上连通到自己的院行）；
  · `DIVE@在册过孔站`（COMB 区内、锚点 ≤2 格内的在册过孔站）；
  · 一致性 `Σdive = on4[COMB]` ＋ **两两不冲突**（**声明集口径**机核预计算：claim 相交 或 孔距 < `VIA_SEP` ⇒ 互斥）。
- **解**（`OPTIMAL`）：入口动作 **5 根 DIVE ＋ 11 根 In5**；行程/打捆同前（`COMB 5 / BELT 6` 根在 In4）：
  | 线 | 入口动作 | 线 | 入口动作 |
  |---|---|---|---|
  | OUT0_N | In5@col2 | OUT4_N | In5@col12 |
  | OUT0_P | **DIVE**@162（0.045mm） | OUT4_P | **DIVE**@877（0.040mm） |
  | OUT1_N | In5@col3 | OUT5_N | In5@col14 |
  | OUT1_P | In5@col5 | OUT5_P | In5@col16 |
  | OUT2_N | In5@col6 | OUT6_N | In5@col17 |
  | OUT2_P | **DIVE**@552（0.233mm） | OUT6_P | In5@col19 |
  | OUT3_N | **DIVE**@619（0.036mm） | OUT7_N | **DIVE**@1334（0.033mm） |
  | OUT3_P | In5@col10 | OUT7_P | In5@col22 |
- **机核**：所选 16 个入口动作**两两 claim 相容**（最大独立集 = **16/16**）⇒ **入口层不再是卡点** ✓（这正是 #K2-194 §三.3 的预期效果）。

## 三、★ 新读数：卡点**再前移**到「入口之后」的断面（机核 · 具名）
- 路由（多项式构造式 · **0 次受证求解** · 硬执行方案选定的入口动作 ＋ 硬声明集预留 ＋ 确定性两遍修复）最好 **8/16**。
- **残余前沿极小**：每次失败仅 **1–7 条**被占弧。**失败点全部在"入口之后"**（阶段 = `from_entrance_to_B`，即**东向跑道 / 出口断面 / 焊盘扇入**），**不再**是入口（入口阶段已可完成）。
- **失败的 8 根**：`OUT0_N` ＋ **全部 7 根 P 线**（OUT0_P…OUT6_P）。
- **⇒ 具名结论（非证书）**：入口动作的"**两两 claim 相容**"这一层已成立，但**它只是必要**；真正的绑定是**每根线"入口 ∪ 跑道 ∪ 出口 ∪ 焊盘接近"的联合走廊占用**——
  即**断面级走廊的联合打包**（同一个原理的第三个实例：该由方案定的联合占用，仍被留给实施阶段按线序隐式决定）。
- **可执行的下一步（同一已批族的模型精化 · L2 编码 · 监理自裁项 · 非 owner）**：把"**断面化走廊**"（16 根 × 4 断面 × 少量候选）**整体**升为主问题变量，
  并对其做**两两 claim 相容**约束 —— 模型仍**很小**（千级 bool ≪ 1.2M 闸），**非换族、非改判据、非动冻结件**。

## 四、按 §三.6 **具名停手报监理**（终结性窗口 · 不自选换法/不延预算/不开新窗）
本窗**未**改法、**未**改参重跑、**未**同法重跑受证求解（**恰 1 次**）、**未**自开新窗。依 §三.6：**"再「无见证」⇒ 出具名结论、停手报监理，届时由监理做『生产方式复核』，不自动升 owner"**。
**待监理裁（1 项 · L2 编码）**：**是否把「断面化走廊的联合占用」整体升为主问题变量**（否则该联合占用仍由路由阶段的线序隐式决定 = 同一病症的第三例）。

## 五、自曝（诚实登记 · 已修复）
本窗首次调用路由件时，`--out` **默认值仍指向 R526 的在册见证件**，致其被**同目录新件的产物覆盖**（内容被 R528 产物替换）。
处置：**立即 `git restore` 复原**该在册件（工作树复查：**逐字复原**、`git status` 干净），并把默认输出改名为 `K2_R528_WOVEN_ENTRANCE_WITNESS_v1.json`。
**诚实口径**：在册 R526 件的**任何读数均未受影响**（已逐字复原、无残留）；但**行为**确实越了一次"不改在册件"的线 ⇒ 具名登记，供监理复核。

## 六、buildability（必填 · 第十三条）
`mode = no_move`（未动任何对象；仅新增 4 件 ＋ 本报告）。**施工队照本件能不能直接连？—— 不能**（8/16，无见证）。
**不作里程碑、不得据以开工。**

## 七、边界 · 红线（机核）
**受证求解恰 1 次（新授）** · 路由件 **0 次受证求解** · **冻结四源 4/4 MATCH**（`0bd52ed48e720b8c` / `a8ef3ea8ecff99d7` / `fb07d25ac426ff84` / `0a459839e15960b8`）·
**交付板锚 `d4e81f647be7f980` 未改** · `criteria/` 只读 · **未写** `.omo/supervision/**` · 未派 WORKER · 正式产物非 `/tmp` · **施工停线维持**。

**一句人话（第十三条）**：「施工队照这张图能直接连吗？」——**还不能**。这一枪（新授的唯一一枪）**把入口孔分配交回方案并成功排开**（机器给出最优解、16 个入口两两相容）；
但机器同时告诉我们：**堵点又往后退了一节**——不在入口，而在**入口之后那段**（跑道/出口/焊盘），且**只剩 1–7 条线的余量**。
**同一个道理第三次出现**：**该由方案排的联合占用，还留在实施阶段按线序临时决定**。要不要把这最后一层也交给方案，是监理的裁量。

OWNER-ITEMS: 0

—— ENG（ARCHER）· 2026-09-25 · R528 精化主问题
