dataxcash/hw_ic_k2/docs/K2-R526-WOVEN-WITNESS-REPORT-v1.md

【回执首行 · 判词首行原文复述】「【监理裁定 #K2-193】R525 等裁窗准备件 = **受理**（纯只读 · 零计算 · 额度未耗 · 自认非见证非里程碑）；一字裁 = **批「编织式丙′」开工**（**不改向**）；定性 = **同窗内的实例修正，不是换方法** ⇒ **不新开窗、不新增额度**（已批"恰一次"额度仍未消耗）；另裁两项**口径**（粒度 = 一次实现不得变两次计算；次序 = 由方案算出，写死次序的病实例准予废除）——该口径**不在冻结件内**（本机实证）⇒ 属**口径澄清（监理职权）**，**不改冻结集、不升 owner**；硬闸照 #K2-192 §三.3 a–e（缺一 fail-closed）；**终结条款**（再算不出结论 ⇒ 具名停手报监理，禁自选换法/延预算/自开窗）；施工停线维持；**owner 项 = 0**」

# K2 · R526 —— 编织式丙′ **一次实现 ＋ 恰一次受证求解**：闸 a/b/c 全过 · **未取得见证** ⇒ 按 §三.6 **具名停手报监理**

- ts 2026-09-25 · from ENG·ARCHER · to 监理 · `OWNER-ITEMS: 0`
- **受证额度：本窗已消耗（恰一次 · `OPTIMAL`）** · **无见证** · **未到闸 d/e** · 施工**停线维持**。

## 一、闸逐条（承 #K2-192 §三.3 a–e）
| 闸 | 内容 | 结果 |
|---|---|---|
| **a** | 前置**只读**保真自检（`Solve()=0`）：路由只用**自己网**的在册逐层合法图（逐线逐层机核 ⊆ `_nok`，**PASS**）；节点不交由**硬预留**构造保证 | **PASS** |
| **b** | **build-only = 0 求解**：规模闸 **538 bool ≤ 1.2M** · `Validate() = OK` | **GREEN** |
| **c** | **恰一次**受证求解（主问题） | **OPTIMAL**（`wall=217.3s` · `objective=1004`） |
| **d** | 在册闸签字（逐层 `exact_gate` ＋ `gate_vias` ＋ 端点） | **未到**（无 16/16 布线） |
| **e** | 交件必含 `buildability` | **已给**：`no_move`（无见证 ⇒ 无搬迁清单） |

## 二、做了**一次实现**（#K2-193 §三.3：一次实现不得变两次计算）
| 件（在册目录 `P6_OPEN_READINESS/`） | 性质 |
|---|---|
| `K2_R526_WOVEN_SCHEDULE_v1.py/.json` | **主问题**：打捆（逐站逐层容量）＋ **行程时刻表**（≤1 段 In4）＋ **反序层分离**；build-only → **恰一次**求解 |
| `K2_R526_WOVEN_ROUTE_v1.py/.json` | **子问题**：逐根**段式骨架**布线（多项式 · 构造式 · **0 次受证求解**）＋ 在册闸签字 ＋ 具名诊断 |

**次序内生化（#K2-193 §三.4）**：本窗**未**使用任何"写死次序"规矩；次序由方案**算出** ——
① 主问题按**打捆容量**把 16 根线分配到 GA（In5 下降）/ GB（In4 下降）；
② 路由阶段按**几何间距规则**（同层平行走廊轴线 ≥ **2 格 = 2P = 0.87mm**）与**焊盘序**定槽位；
③ 线序由**方案派生**的确定性族（`sched_in4_first_*` / `ax_*` / `pad_*`，共 6 条）枚举取最优。
（**已废除**旧实例的"声明序 ⇒ 院行单调递增"写死规矩 ✓ 裁②照办。）

## 三、★ 本窗**新读数**：卡点从"时刻表"**移到了"入口带"**（机核 · 具名）
**主问题解 = SAT/OPTIMAL** ⇒ **调度/打包这一层不再是卡点**：
- 打捆：`Σon4[BELT]=6`、`Σon4[COMB]=5`（= 机核容量下界）· 58 对反序**全部层分离** · 10 根线各用 **1 段**行程（≤2 对孔 ✓）。
- 路由（构造式）最好 **5/16**；**残余前沿极小**：仅 **7–9 条**被占用弧（全部 `claim_0`，位置全在 **COMB 区 y≈54.5–55.8 的"入口带"**）。

**机核具名诊断（`access_band_analysis`）**：
| 项 | 读数 |
|---|---|
| 16 根"自然下降走廊"（A 锚 → 院行，沿 A.x）的**声明集冲突边** | **8** |
| **可同时在 In5 离开梳齿口的走廊数（精确最大独立集 · 2^16 暴力）** | **10**（⇒ **≥6 根必须"在入口带内"就下沉到 In4**） |
| 机理 | 同层平行走廊的**节点声明**要求轴线 ≥ **2 格**；而**在册 A 锚 x 间距仅 0.5–1.5 格**；把 16 根重排到 2 格距需 ~32 列，**锚跨只有 ~21.5 列** ⇒ 上界 ~10–11 |
| 附加约束 | 在册**自由接入腿固定在 In5**（锚点处无过孔）⇒ 那 ≥6 根必须"在带内"找到**合法过孔站**下沉，且路径不得穿过已被声明的带内节点 |

**⇒ 具名结论（第十三条口径 · 非设计级证书）**：本板的绑定资源**不是**层/孔计数、**也不是**时刻表，
而是 **梳齿口前 1–2mm 的"入口带"**：**同层只能放下 ~10 条入口走廊**，其余 ~6 条必须在**带内**换到 In4。
主问题已按此分配（COMB 5 根下 In4），但**构造式路由仍做不到**"这 6 根在带内找到合法过孔并穿过"，
残余只差 **7–9 条弧**。

## 四、按 §三.6 **停手报监理**（不自选换法 / 不延预算 / 不开新窗）
- 本窗**未**改法、**未**改参重跑、**未**同法重跑受证求解（**受证求解恰 1 次**）、**未**自开新窗。
- 依 §三.6：**"算不出结论/无见证" ⇒ 出具名结论、停手报监理**；本件即该具名结论。
- **交监理裁决的事项**（皆 **L2/口径** · 监理自裁 · 非 owner 项）：
  1. **入口带作为"打包主问题"的一部分**：是否把**入口过孔的位置**（哪 6 根、各自在带内的哪个合法过孔站）**升为主问题变量**
     （现在它由路由阶段隐式决定 ⇒ 与时刻表解耦 ⇒ 出现 7–9 弧的残余冲突）；
  2. **入口带入 In4 的合法途径口径**：在册 `via_positions` 在 COMB 区内是否存在**每根线可达**的合法过孔站
     （若不达 ⇒ 属**在册模型口径**问题，需监理裁是否放宽"入口腿仅 In5"这一编码）；
  3. **是否要 L1**：若上述两项在册口径下都不可行 ⇒ 才谈设计级约束；本窗**无**非空核，**不**主张设计级不可行。

## 五、buildability（必填 · 第十三条）
`mode = no_move` —— 本窗**未动任何对象**（仅新增 4 件 ＋ 本报告）。**施工队照本件能不能直接连？—— 不能**（无见证）。
**故本件不作里程碑、不得据以开工。** 交付物形态已达"**每线通道图**"的一步（`descent_slots_from_scheme` ＋ 逐线时刻表 ＋ 分段骨架），
但**缺 16/16 的合法连线**，故**不是**可施工通道图。

## 六、边界 · 红线（机核）
**受证求解恰 1 次**（`OPTIMAL`）· 路由件 **0 次受证求解** · **冻结四源 4/4 MATCH**（SPEC `0bd52ed48e720b8c` ·
manifest `a8ef3ea8ecff99d7` · PCB `fb07d25ac426ff84` · rules `0a459839e15960b8`）· **交付板锚 `d4e81f647be7f980` 未改** ·
`criteria/` 只读 · **未写** `.omo/supervision/**` · 未派 WORKER · 未 import 无 `__main__` 保护在册件 · 正式产物非 `/tmp` ·
**施工停线维持**（不导 Gerber、不进 P5、不碰下单）。

**一句人话（第十三条）**：「施工队照这张图能直接连吗？」——**还不能**。这轮把**唯一一次计算**打出去了，
得到的是一条**确定的好消息**：**"谁下二层、什么时候下"这件事本身能排开**（机器给出最优解）；
坏消息是**卡口在更前面**——**梳齿口那 1–2 毫米里，同一层只塞得下约 10 根线**，剩下 6 根必须**在那 1–2 毫米内就换到二层**，
而现在**入口脚只能在顶层**，于是差 **7–9 条弧**堵在那儿。**下一刀该切"入口带"**（把这 6 根的入口过孔位置也交给方案去排），
但这是监理的裁量，**ENG 不自选**，把机器读数交上去。

OWNER-ITEMS: 0

—— ENG（ARCHER）· 2026-09-25 · R526 编织式丙′ 一次实现
