dataxcash/hw_ic_k2/docs/K2-R525-WOVEN-PREP-REPORT-v1.md

【回执首行 · 判词首行原文复述】「【监理裁定 #K2-192】R523 收口 = **「未完成」**（恰一次受证求解 UNKNOWN · 无核）；一字裁 = **批「丙′」（通道化分解）开工**（甲′ 驳 · 乙′ 驳）；丙′ 窗硬闸（保真自检前置 · build-only 0 求解 · 恰一次 · 在册闸签字 · buildability）；施工停线维持；**owner 项 = 0**」

# K2 · R525 —— 丙′ 等裁窗：**只读/零额度准备件（W-1/W-2/W-3）＋ 一条新具名结构读数**

- ts 2026-09-25 · from ENG·ARCHER · to 监理 · `OWNER-ITEMS: 0`
- 本窗**未花受证额度**（`Solve()` 共 **0** 次 · 三件皆机核自证）· **未动任何对象** · 施工**停线维持**。

## 〇、裁定核查（开工第一动作 · 判据先行）
| 判据 | 读数 |
|---|---|
| 最新 `K2-RULING-*.md`（含 `sent/`、`outbox/`） | **#K2-192**（`2026-09-25T01:03`，已入 `sent`/`outbox`，无 #K2-193） |
| 本 handoff | `HANDOFF-K2-525-WOVEN-PRIME-NEXT.md`（`01:15`） |
| **结论** | **无晚于本 handoff 的裁定** ⇒ 走 handoff **§0.1 第 3 支**：`不得空转` ⇒ **只做 §3 只读/零额度准备件（W-1/W-2/W-3）** ＋ 把「待一字裁」交监理**一次**（见 §五） |
| 为何**不**自裁实现编织式 | **#K2-192 §三.4** 明文：「丙′ 若…⇒ 出**具名结论**、**停手报监理**，由**监理再裁**（**不得**自行换法 / 延预算 / 开新窗）」。R524 交的正是具名结论 ⇒ 球在监理。**不自选、不换法、不花额度。** |

## 一、本窗交件（**四件**，全在册目录 `k2/pm_gate/artifacts/k2_v4/P6_execution/P6_OPEN_READINESS/`）
| # | 件 | 性质 | 机核 |
|---|---|---|---|
| W-2 | `K2_R525_INVERSION_ATLAS_v1.py/.json/.svg` | π 反序图谱（可查 ＋ 可视化弧图） | `Solve() 0` · 复现 58 反序 |
| W-1 | `K2_R525_WOVEN_MASTER_BUILDONLY_v1.py/.json` | 编织式主问题**规格 ＋ 规模估算**（coarse 全实例化 ＋ fine 解析估算） | `Validate() OK` · `Solve() 0` · **`--solve` 硬拒** |
| W-3 | `K2_R525_VORONOI_CHANNEL_SKELETON_v1.py/.json` | 逐层 Voronoi 通道骨架（**三种通道定义**对比）＋ 通道**连通性/可达/A 侧可达带**读数 | `A1/A2 PASS` · `Solve() 0` |
| — | 本报告 | 口径/边界/一字裁请求 | — |

## 二、W-2 · 反序图谱（**复现 ＋ 新增可查字段**）
| 项 | 读数（机核） |
|---|---|
| 必需置换 π（梳齿序 A.x → 焊盘序 B.x） | `inversions = 58`（与 R523 §七 换序审计、R524 §C **一致**）· `LIS = 6` · `LDS = 6` |
| 最小**保序组**分解（Dilworth 贪心） | **6 组**（= `LDS`）⇒ 「若有 6 层，谁可同层」已成**可查表** |
| 58 对的**分组构成** | `east/east 20` · `east/west 32` · `west/west 6` |
| 58 对的**轴向共存窗** ∩ 在册四宽区 | **58/58** 都在窗内至少含一个在册宽区（`COMB/BELT/WALL/FIELD`）⇒ **不存在"窗内无孔可打"的对** |
| 逐线字段 | `comb_rank / pad_rank / group_id / A,B 锚坐标(mm) / 落在哪个宽区 / 逐层合法格点数 / 过孔可用格点数` |
| 可视化 | `K2_R525_INVERSION_ATLAS_v1.svg`（双轴弦图 · 16 线 · 按保序组着色 · 58 交叉一眼可数） |

> **口径**：全部字段标 `named_structural_lead`，**不是**设计级证书；`L(π)=6 > 层数 2` 的**朴素引理已被驳**
> （handoff §1）：一根线的 In4 行程**可以跨过**很多 In5 线 ⇒ **顺序行程能实现任意反序**。本件**不**用该引理。

## 三、W-1 · 编织式主问题：规格 ＋ 规模估算（**build-only · 求解被硬拒**）
**规格**（写入件头 docstring ＋ JSON `station_grid`）：
1. **站序**：每根线沿轴向行军把**在册宽区**离散成有序站点。两粒度：**粗** = `COMB(0)<BELT(1)<WALL(2)<FIELD(3)`；
   **细** = 该线在某宽区内**过孔可用格点**去重后按轴向排序。
2. **时刻表变量**：`dn_i`（下孔站）、`up_i`（上孔站）one-hot ＋ `dn 站序 ≤ up 站序` ⇒ **至多一段 In4 行程**
   （在册 `MAX_VIA_PAIRS=2`）；`on4_i[s]` 由 `dn/up` 线性推出。
3. **槽位变量**（在册，同 R524）：院行/门列/墙缝 ＋ all-different ＋ 登记声明序非交叉。
4. **编织约束**：**每一对反序对**必须在其窗内**某一站**被**层分离**：`OR_s [on4_i[s] ≠ on4_j[s]]`（58 对）。
   本编码只是**必要条件**（故写作**松弛**）；其 **UNSAT 的设计级含义须先过 §三.3.a 保真自检**方可主张 —— 本件**不主张**。
5. 目标 `min Σ (up_i 站序 − dn_i 站序)`。

| 规模读数（机核） | 值 |
|---|---|
| **粗**（zone 级 · 全实例化） | **938 bool / 1170 约束** · `Validate() = OK` · **≤ 1.2M 闸** · `Solve() 0` |
| 其中 | 槽位 552 · 时刻表 192 · 编织分离 194 |
| **细**（格点级 · 解析估算） | **≈ 13 899 bool / 15 901 约束**（共享站 150 个；每对反序窗内共享站 `min 86 / avg 105.9 / max 147`） |
| **⇒ 结论** | **规模不是墙**（粗/细都远在 1.2M 闸下）⇒ 卡点是**编码口径**，不是算力 |

**fail-closed 自守**：`--solve` 一律 **REFUSED（exit 2）**，理由随件打印：「woven 变体**尚未获监理一字裁**（#K2-192 §三.4）」。

## 四、W-3 · 逐层 Voronoi 通道骨架（**两条性质 PASS · 但揭出一条具名读数**）
### 4.1 两条要求性质（handoff §3 W-3 指定的机核）——**PASS**
三种通道定义**全部**过 A1/A2：**（V）纯 Voronoi** · **（V∩B3）Voronoi ∩ 3 格带** · **（G）R524 gate-a 的逐字构造**
（`own-eligible ∩ L1 带 · 按登记声明序贪心占有`）：`A1 通道 ⊆ 自己网逐层合法点` **PASS** ·
`A2 各线逐层两两不交` **PASS**（**由构造保证 ＋ 随机例机核**）。
### 4.2 **新具名读数：三种静态通道定义都让 15/16 根线"走不出梳齿口"**
| 通道定义 | In5 单分量 | A 侧可达 **BELT**（仅 In5） | A 侧可达 **BELT**（In5+In4） | A 侧可达 **FIELD** |
|---|---|---|---|---|
| V 纯 Voronoi | 0/16 | **1/16** | **1/16** | 1/16 |
| V∩B3 | 0/16 | **1/16** | **1/16** | 1/16 |
| **G = R524 gate-a 逐字构造** | 0/16 | **1/16** | **1/16** | 1/16 |
> 度量：从**该线通道内 COMB 区（A 锚所在，全部 A 锚 x∈84.35..93.70,y∈54.88..55.82）的点**做 **2 层状态 BFS**
> （换层**仅允许**在在册过孔可用点）；**只报可达宽区集合**，**不出路径、不出见证**。唯一能出 COMB 的是 `PCIE_UP_OUT0_N_J2`（= 登记声明序第 0 位）。
### 4.3 **机读根因：院行单调口径把 16 根线的"下降通道"与"东西向走线"互锁 120/120**
按在册约定（R512 §c / R524 backbone）：第 k 位（A.x 序）的线**在其 A.x 处下降**到院行 `YARD_ROWS[k]`，再**沿该行向东**跑。
下降列保持左右序（平面性所迫）⇒ 第 i 位线的东向走线（列 `col(A_i.x)..60`）必然**穿过**第 j>i 位线的下降列
（`col(A_j.x) > col(A_i.x)`），当且仅当 `r_i ≤ r_j`。机核：

| 院行分配 | 互锁对 |
|---|---|
| **登记方案**（声明序 → **递增**院行，R524 主问题硬约束 `pos_y[oa] ≤ pos_y[ob]−1` 同款） | **120 / 120（全互锁）** |
| **嵌套方案**（声明序 → **递减**院行 · 最左者最深） | **0 / 120** |

**⇒ 具名读数（named structural lead · 第十三条 · 非证书）**：
「**静态先分通道、再各线独立画线**」在**梳齿喇叭口**不成立（三种构造同死）；且**R524 主问题的院行单调递增口径**给出的是
**全互锁**的那一种（嵌套递减给 0 互锁）。这**很可能是**4.2 里 15/16「走不出去」的机读根因。
**边界（不越界）**：这是 **In5 单层平面性**陈述；**In4 行程**（四宽区**皆**可打孔，含 COMB/BELT）能否**洗掉**某一处交叉，
**正是**编织式时刻表要回答的问题 ⇒ 本件**只点名、不下结论**。

## 五、请监理一字裁（**一次** · 不得重复投递）
**「编织式丙′：开工 / 改向」**。
若批「开工」，请顺带裁**两件 L2 口径**（皆属监理自裁 · 非 owner 项）：
1. **站粒度**：粗（zone 级 · 938 bool）／细（格点级 · ≈1.4×10⁴ bool）／或先粗后细；
2. **院行/出口序口径**：是否把 R524 的「声明序 → 递增」改为**嵌套递减**，或**把次序升为变量**（§4.3 机核指向此）。
（ENG **不自选**；批什么做什么。）

---
**buildability（必填 · 第十三条）**：`mode = no_move` —— **本窗未动任何对象**（仅**新增** 7 个件 ＋ 本报告；
板/SPEC/生成器/原理图/判据一字未改）。**施工队照本件能不能直接连？—— 不能**：本窗交的是**图纸层的卡尺与骨架**
（反序图谱、主问题规格/规模、通道骨架与可达读数），**不是**可施工的通道图（无见证 = 无搬迁清单）。
**故本件不作里程碑、不得据以开工。**

**边界 · 红线（机核）**：`Solve()` **0** 次（三件）· 在册 `--solve` **硬拒** · **冻结四源 4/4 MATCH**
（SPEC `0bd52ed48e720b8c` · page manifest `a8ef3ea8ecff99d7` · PCB `fb07d25ac426ff84` · rules `0a459839e15960b8`）·
**交付板锚 `d4e81f647be7f980` 未改** · `criteria/` **只读** · **未写** `.omo/supervision/**` · **未派 WORKER** ·
**未 import** 任何无 `__main__` 保护的在册件（`K2_R523_FORMC_PREMISE_CHECKS_v1` **只读其 JSON**）· 正式产物**非 `/tmp`** ·
**施工停线维持**（P4 该项未归零 ⇒ 不导 Gerber、不进 P5、不碰下单）。

**一句人话（第十三条）**：「施工队照这张图能直接连吗？」——**还不能**。这轮没烧那唯一一次计算，
而是把**下一步要用的三件东西**先做好了，并且**顺手用机器揪出一个更靠前的病**：不是"排不下时刻表"，
而是**连喇叭口都出不来**——按现行"谁排前面谁走上面"的次序规则，16 根线的"下楼通道"和"横向跑道"**互相锁死 120 处**；
把它们**嵌套排**（最左的走最深）就**一处都不锁**。所以**下一刀**该切的可能不是时刻表，而是**次序口径**；
但这是监理的裁量，**ENG 不自选**，只把机器读数交上去。

OWNER-ITEMS: 0

—— ENG（ARCHER）· 2026-09-25 · R525 丙′ 等裁窗准备件
