dataxcash/hw_ic_k2/docs/K2-R523-PRIME-CHANNEL-DECOMPOSITION-SPEC-v1.md

【回执首行 · 令首句原文复述】「#K2-189 既定授权维持：本窗「恰一次受证求解 · 形态C」正在执行 ⇒ 不得打扰；求解返回 SAT/UNSAT 后照 #K2-189 §四 收口。」（#K2-191 §三.2）

# K2 · R523 —— **丙′（通道化分解）就绪规格 ＋ 规模估算**（只读 · 零额度 · 停止令"找活/造活"支）

- 缘起：停止令要**二值**；两支已结清 —— **见证支**：R517 软协商 16/16 布出/**残余冲突 512**、本窗 v1 硬预留 **5/16**、v2 分区结构化 **3/16**、精确 MCF **UNKNOWN ×2**；
  **证书支**：**机证不存在**（T4 全割 ≥66 · T5 配对放松 16/16 最小割 ∅ · 断面 31/22/55/105 最紧余 +6 · 换序审计 58 对反转而宽区容量远超）。
  ⇒ ⇒ 二值只能由**表述变更**给出。本件把该变更做成**可一字开工**的规格（**属监理自裁项 · 宪法第七章第 3 条**，ENG 不自裁）。
- 本件 `Solve()` **0** 次；只读 + 离线估算（用本窗已在盘的 `cross/unique/rank`、`vias`、claim 尺寸）。

## 一、为什么"贪心不行、分解行"（本窗实测的机理）
1. 三种构造法的共同死因：**不为后续根留位**。实测：首根一布就吃掉 In5 **230** 格声明带；分区结构化后每根仍占 In5 ≈140 格 + In4 ≈68 格；
   而**梳齿区只有 13×4mm**（16 条锚脚必须在此扇出）、**东门漏斗只有 22 槽（两层合计）/ 16 根（+6）** ⇒ 必须**打捆**，贪心打不紧。
2. 精确 MCF 会打捆，但**1.18M bool** 的全格点表述在 1500s 内采不到解（两窗一致）。
3. ⇒ 正解 = **把"打捆"交给一个**小规模**主问题（换位账本），把"画线"交给**每根独立**的多项式子问题。

## 二、丙′ 结构（承 form C 的账本语义 · 与在册断面同一口径）
- **断面序**（在册）：`梳齿出口 col33` → `院列 col60` → `墙列 col114` → `门行 row36` → `焊盘行 row30`（同轴相邻断面才比较）。
- **主问题（小）**：对每个断面 S、每根线 i 选一个**槽位** `slot[i][S]`（该断面上的横向格点序）；
  相邻同轴断面 (S,S′) 之间：**序翻转 ⇔ 该区间内 i 或 j 必须打一对孔换层**（= form C 的**被蕴含**约束，R523 已机核）;
  孔位仅四宽区、每根 ≤2 对、孔间距 ≥ VIA_SEP。
- **子问题（各自独立）**：给定 i 的槽序列 ⇒ i 只在自己的"槽—区间"通道内做**单商品最短路**（In5 短段 + In4 中段），互不竞争。
- **复验**：照旧用**独立在册闸**（逐层 `exact_gate` + **已修** `gate_vias` + 端点）⇒ 过闸才算里程碑（缺一 fail-closed）。

## 三、规模估算（离线 · 用本窗在盘数据）
| 项 | 估算 | 对比 |
|---|---|---|
| 主问题 bool | 5 断面 × 16 根 × ≤20 槽 ≈ **1.6×10³** 槽变量 + ≤2×120 换位事件 ⇒ **~3×10³** | 现表述 **1.18×10⁶**（÷~400） |
| 子问题 | 16 × 单层图（每根 ~10³–10⁴ 节点）最短路 | 多项式 · 各 **<0.1–1s** |
| 合计 | **~10s 量级**（可迭代重排） | vs 1500s 触限 |

## 四、保真 · 可施工性（第十三条）
- **保真**：主问题的"翻转必打孔"就是 **form C**（已被机核为**蕴含**）；通道化**只做限制**（子问题各自可行域 ⊆ 原图）⇒ **只得"变弱"**：
  解得 ⇒ **真·合法见证**（可用在册闸直接签字）；解不出 ⇒ 是**通道级**（更弱）的不可行，**不是**设计级证书 ⇒ 仍 fail-closed。
- **可施工性**：每根线拿到**一张通道图**（槽序列 + 换层区间 + 孔位）⇒ 施工队可**照图直接连**（这正是 P4 要的交件形态）。

## 五、请监理裁（一句 · ENG 不自裁）
**「丙′ 开工 / 否」**。批 ⇒ 我下一次会话**一次实现 + 恰一次复验**（主问题小 CP-SAT · 子问题最短路 · 在册闸签字）；
否 ⇒ 二值在本问题类别**不可得**（见证支=构造硬度、证书支=机证不存在），届时需由监理决定是否上报 owner 改**设计级**约束（L1）。

OWNER-ITEMS: 0

—— ENG（ARCHER）· 2026-09-25 · R523 丙′ 就绪规格
