dataxcash/hw_ic_k2/docs/K2-R521-PARITY-SPEC-CORRECTION-v1.md

# K2 · R521 —— P4 该项（UP-16 二值）的**编码保真性收口**：parity 规格**更正**（遵「不越阶段」· 只读机核驱动 · `Solve()` 0 次 · 受证额度 UNSPENT）

- ts 2026-09-24 · from ENG·ARCHER · to 监理 · **阶段**：仍在 **P4**（未越阶段：不碰 P3 图纸 / 不导 Gerber / 不碰打样下单）
- 依据：#K2-189 §四 step 1（**丙 必须与设计同解集**，否则其 UNSAT 不得作设计级结论）· R518（Q3 未决）· **R519（Q3 = 不同解集，机核反例）** · 自动续推阶段门令

## 一、本窗做的事（阶段内、只读、0 求解）

**用 R519 的机核反例反过来审我自己的 R518 规格**，结论：**我 R518/R519 里写的"保真替代式"还不够保真** —— 必须更正。

| 形态 | 是否被在册语义**蕴含** | 依据 |
|---|---|---|
| A）R499 原版：declared order（A 锚 x 序）**无条件单调** | **否** | R519 反例（零过孔、全程 In5、合法，却门列逆序） |
| B）我 R519 提的弱化："**两线都无过孔 ⇒ 保持 declared 序**" | **否**（同样被 R519 反例否掉：该反例**零过孔**且逆序） | R519 反例 |
| **C）唯一被蕴含的形态**：**同一横向轴的相邻断面**之间，**rank 序翻转 ⇒ 该区间内至少一根必须有过孔弧**（rank **由各根在该断面 In5 上的实际横向位置定义**，非 declared 序；**跨不同横向轴的断面之间不得比较**） | **是** | 同层不换序 ⇔ 同层两线相交 ⇔ 声明集相交（被禁）⇒ 翻转必由层改承担 |

⇒ **若照 A/B 实现，就是"我自己把合法解砍掉"**（R519 已证）⇒ 其 UNSAT **不可作证书**；照 C 实现则**同解集**（保真），且仍把「哪根先走 / 在哪换位」交给机器当变量（丙的本意）。

## 二、下一步（具名 · 阶段内）

1. 按 **C 形态**实现 parity 丙（断面按**横向轴分组**：竖向族 = 梳齿出口列 / 院列 / 墙列；横向族 = 门行 / 焊盘行）；
2. `--build-only`：规模闸（≤1.2M bool）＋ `Validate()` ＋ 前置闸 ＋ 声明集自检（**0 求解**）；
3. 绿 ⇒ 跑 **#K2-189 授权的那恰一次**受证求解：解得 ⇒ 渲染 + 在册 `exact_gate` + R495 + `buildability` ⇒ **P4 该项归零**；UNSAT ⇒ 必附**非空核**且各前提逐条非绑定，否则 **fail-closed 停手报监理**；
4. P4 该项归零前：**不导 Gerber、不进 P5、不下单**。

## 三、红线 · 边界 · buildability

本窗**未动任何对象**（仅新增本文档）：红线锚 `d4e81f64…`（交付板 l4）**未改** · 冻结四源 **4/4 MATCH** · 生成器/SPEC/原理图**未改** · `criteria/` **只读** · **未派 WORKER** · 未写 `.omo/supervision/**` · **施工停线维持** · `Solve()` **0** · **受证额度 UNSPENT**。
**buildability**：**NOT-APPLICABLE**（编码保真性更正；不作可行/见证主张，不构成里程碑、不据以开工）。

## 四、一句人话

「施工队照着这张图能不能直接连？」—— **还不能**。今天这一步是**拦住我自己犯的错**：监理批的"保持先后顺序"写法，**连同我上一轮提的"没打过孔就保持顺序"的弱化版**，都被我自己的机器反例证明**会砍掉合法解**（两根本来一深一浅转个弯就换位，**一个过孔都不用**）。所以规格改成**唯一被蕴含的那一条**（同轴的相邻断面之间换序必须由过孔承担），**下一步就按它实现、再算那一次**。

OWNER-ITEMS: 0

—— ENG（ARCHER）· 2026-09-24 · R521
