dataxcash/hw_ic_k2/docs/K2-P2-zeroing-proposal-v1.md

# P2「真源归零」变更建议书 v1（监理放行前置件；**只读分析，未动三源**）

- **依据**：#K2-10 §四（P2 开，首条动作 = 三源对账 E1–E4）+ 红线「**未获批不得改生成器 / SPEC / 原理图**」
- **仪器**：`/tmp/opencode/k2p1/measure_source_reconcile.draft.py` sha256 `adf7707c…9573ac55`（ENG 草案，待 gate 安装）
- **基线**：`/tmp/opencode/k2p1/recon_baseline.json`，**`unbaselined: true`**（归零前一切结果不作合格证据）
- **冻结件**：板 `d4e81f647be7f980…` 未动；SPEC `5f72182a2616392c` 未动；网表 `70448241caa6f04a…` 未动；原理图未动

## 1. 基线（本轮实测，逐项复现计划 §P2）

| 等式 | 实测 | 性质 |
|---|---|---|
| E1 refdes 集合 | 板 **42** / 原理图 **103** / 网表 **55**；板-图 **3**（`C88`,`C89`,`U6`）、图-板 **64** | **源侧**（画面/网表口径） |
| E2 引脚/焊盘集 | **10 件**：`J11`(4/0/0)、`J12`(2/0/0)、`J13`(4/0/0)、`J6`(2/0/0)、`J9`(4/0/0)、`J2`(43/74/74)、`J3`(25/38/38)、`J4`(25/38/38)、`U1`(27/33/33)、`U2`(6/8/8) | **混合**（见 §2） |
| E3 逐引脚网成员 | 489 = 一致 424 / **不一致 15** / **缺焊盘 50** | **板侧为主**（见 §2） |
| E4 生成器可复跑 | **不可跑**：`tools/k2_gen_v5.py` rc=1，`FileNotFoundError: k2/boards/k2_sch.yaml` | **输入路径/schema**（见 §3-2） |

## 2. 归零动作清单（按「源侧 / 板侧」分类 —— 决定能否在 P2 内闭合）

**E1（源侧）**：以真源（L1 拓扑 + datasheet + 厂商球映射）为准对齐 refdes 集合 ——
原理图**删除** 64 个板外 refdes（样例 `C17…C28` 等滞留件），**补入** `C88`/`C89`/`U6`；网表同步（55 → 与板一致）。

**E2（混合，须分型）**
| 型 | refs | 观测 | 归零点 |
|---|---|---|---|
| 板侧（封装实例 0 焊盘） | `J11`,`J12`,`J13`,`J6`,`J9` | 符号 4/2/4/2/4 vs 板 **0** | **板重建（P4）** |
| 源侧（符号脚数 ≠ 封装焊盘数） | `J2`(43/74)、`J3`(25/38)、`J4`(25/38)、`U1`(27/33)、`U2`(6/8) | 连接器/器件含**机械·屏蔽·散热焊盘** | **源侧**（对齐符号引脚表 ↔ 封装焊盘表） |

**E3（板侧为主）**
- **不一致 15**：`U6` 的 `SCL`(B31)、`SDA`(B28)、`PD_11-8`(FJ6)、`PD_15-12`(FF8)、`PD_3-0`(FF33)、`PD_7-4`(FJ31) + straps —— 板上**该球无网**（`bnet=null`）⇒ **板侧未连**（P4）。
- **缺焊盘 50**：`U1` `I2C1_SCL/SDA`(pad 47/48)、`J11` `EC_SCL/EC_SDA`(2/3)、`J6` `PWR_BTN#`(1)、`J9` `TX`(1)… —— 板上**无该焊盘** ⇒ **板侧**（P4）。
> ⇒ **E2 板侧列 + E3 全部**在板重建（P4）前**不可归零**。

## 3. 三项 FINDING（ENG 提出，须监理定口径；均为**计划内部一致性**问题）

### 3-1 FINDING-P2-1 **次序冲突**：E2/E3 含板侧项 ⇒ P2 与 P4 循环
计划 §P2 完工判据要求 E1–E4 全 `= 0`；但 E2 的「板焊盘集」与 E3 的全部计数**只能由板侧修复达成**，而板重建是 **P4**。
⇒ 按字面，**P2 无法在 P4 前完成**（P4 又以 P2 归零为前置）。**请监理明确口径**：
- **(a) 源侧口径（建议）**：P2 判 E2/E3 的**源侧同构**（符号引脚表 ↔ 封装焊盘表 ↔ 网表），板侧列**延至 P4 复判**；
- **(b) 含板侧口径**：则须先放行板修订（P2/P4 次序重排）。

### 3-2 FINDING-P2-2 **E4 阻塞点定位（输入契约已逐条核实）**

生成器 `k2/tools/k2_gen_v5.py`（`ROOT = k2/`）硬编码 3 个「冻结输入」：

| # | 生成器期望路径 | 实际 | 判定 |
|---|---|---|---|
| I1 | `boards/k2_sch.yaml` | `hw/data/k2_sch.yaml` | **缺失**（迁址） |
| I2 | `pm_gate/artifacts/k2_v4/L3/SPEC_k2_v4.json` | 同名件**存在**，但仍是 **6L canonical**（计划 §Z3 明列「layer_plan 还写着 In2 = 唯一内部信号层」）；冻结源为 `SPEC_k2_v4.spec-rev-19.json` | **陈旧/非冻结**（Z3 问题） |
| I3 | `k2_v4.kicad_pcb` | `hw/k2_v4_8L.kicad_pcb`（且交付板为 `.l4`） | **缺失**（迁址） |

⇒ E4 归零 = **2 处输入迁址 + 1 处 SPEC 归零（Z3）+ schema 兼容**；其中「输入迁址」可在不动生成器源码的前提下以路径/副本解决，但**是否以副本迁位仍属改项目输入**，故仍列 R4 请放行；**改生成器源码须单独放行**。

### 3-3 FINDING-P2-3 **E2 严格等式对连接器不可达**
`J2` 符号 43 脚 vs 焊盘 74（`J3`/`J4` 25 vs 38）—— 连接器封装含**机械/屏蔽/散热焊盘**，符号无电气对应。
⇒ 「符号引脚集 **==** 封装焊盘集」为**严格相等**时**永不可达**（非缺陷）。请监理改为**有向口径**：
`电气引脚集 ⊆ 焊盘集` **且** 余量焊盘**逐条登记**（机械/屏蔽/散热），禁静默。

## 4. 请放行项（本件不自行执行）

| # | 放行事项 | 影响面 | 风险/顺序 |
|---|---|---|---|
| R1 | 改**原理图**（删 64 / 补 3 refdes；连接器符号引脚表对齐） | `k2/hw/sch/*.kicad_sch` | 先 R1 后 R2（网表随图） |
| R2 | 改**网表** `k2/hw/data/k2_sch.yaml`（与图同步 55 → 一致；E1/E2 源侧面） | 生成器输入 | 与 R1 同步 |
| R3 | 改 **SPEC**（Z3：canonical 反映 8L，层语义覆盖 In5/In6） | `SPEC_k2_v4.spec-rev-19.json` | 冻结源之一，**须监理显式放行 + 重出 sha** |
| R4 | E4 输入迁位（或放行改生成器） | 生成器输入/工具 | 见 §3-2 |
| R5 | E2/E3 **口径裁定**（§3-1、§3-3） | 判据语义 | **先于** R1–R4 的动作 |

**建议顺序**：R5（定口径）→ R1+R2（源侧同构）→ R3（SPEC 归零）→ R4（E4）→ 复算 E1–E4 → 交监理判。

## 5. 边界与复算

- 本件**只读**：三源、`criteria/`、板、生成器**均未改**；临时件仅 `/tmp/opencode`；未写 `.omo/supervision/**`；未派 WORKER。
- 复算：`python3 /tmp/opencode/k2p1/measure_source_reconcile.draft.py --board k2/hw/k2_v4_8L.l4.kicad_pcb --sch k2/hw/sch --nets k2/hw/data/k2_sch.yaml --json /tmp/opencode/k2p1/recon_baseline.json`
