dataxcash/hw_ic_k2/pm_gate/artifacts/k2_v4/L2/K2_BLOCKER_REPORT_STOPORDER_K2AF_v1.md

# 《卡点报告》· 停止令 Compliance（红线：命令重复 · token `k2af`） · v1

- **依据**：监理停止令（「同型命令重复 3 次（疑似暴力迭代/改参重跑）：`k2af`」＋「立即停止…回到 Plan 说清 ①②③，然后一次实现；并把本轮卡点写成《卡点报告》：**试过什么 / 为何不通 / 缺口在哪层**」）＋ 宪法第八章第 8 条。
- **服从**：**自收令起零运行**（未再跑任何预检/评测命令）· 本件只做「停 ＋ 报告」· 零板写 · 零新考跑。

---

## 一、触发分析：`k2af` ＝ **路径常量假阳（VOID）**

- `k2af` ＝ **工作目录路径常量** `/tmp/opencode/k2af`（缝合参考板 `s1d_stitched.kicad_pcb` 所在目录）。
- 被判「同型」的三次命令 ＝ **只读预检回放**（`R1520` 前提核验 ＋ `#K2-472` 预检重跑），**输入同一块只读板文件** ⇒ 命令体相同**源于同输入**，**不是**改参重跑、不是换工具、不是换笼位。
- 定性：属在册 **`M-SUP-REDLINE-FP-FABRIC`** 族（承 `#K2-433`／`#K2-469`）。
- **姿态**：**服从**（停手 · 不申辩 · 不借「假阳」继续跑）；告警层卡点交监理，**不改任何产物**。

## 二、试过什么（`#K2-472` 授权窗）

1. **修量具**：焊盘**真形胶囊**建模（弃各向同性 `max/2` 圆盘）＋ 逃逸**须离焊盘自身铜皮** ＋ 过孔**逐跨层**入障碍。
2. **预检重跑**（仅未连通端 · 只读 · 有界）：`go=TRUE` · **2/2 资产** · **0 拒** · `0.157s` —— `I2C2_SCL` 与 `I2C1_SDA` 各获一条**沿长轴**的出线走廊。
3. **恰一次新鲜 `N=1`**（`run 1/1` · 九行齐 · `C34` 门 PASS）：**`verdict FAIL`** —— `C1_connectivity unconnected=2`（**未动**）· `C6_outside_copper_unchanged diff=796`（`legacy 2`，**亦红**）。

## 三、为何不通

- **`C1=2` 未动，不是几何不可解**（预检已证两条端各有确定性走廊），而是 **走廊根本没交给布线器**：**逃逸资产 → KEEPOUT 的链侧集成从未落地**（原 item ② 被「过孔分支」插曲取代）。本次 `N=1` 跑的是**登记链**，对逃逸阶段**无判别力**；它只证明「**登记链自身仍 FAIL**」。
- **`C6` 红（越框铜 796）是另一条独立失效**：清域-消解-回填链在框外改了铜；与量具、与逃逸阶段皆无关。
- 依 `#K2-472 §3.5`：`C1≥2` ⇒ **停 ＋ 具名 ＋ 禁同因重跑**；**升 owner 须携守恒级不可行证书（L1）**——本件不带证书 ⇒ **不升 owner**。

## 四、缺口在哪层

| 层 | 内容 |
|---|---|
| **L-a 告警层** | 停止令触发＝**路径常量假阳**（`k2af`） ⇒ 监理面 `M-SUP-REDLINE-FP-FABRIC`，**非** ENG 纪律违规。 |
| **L-b 机制层（真卡点）** | **链侧集成缺失**：逃逸资产**未作为硬 KEEPOUT 交给迷宫**（`R1488` 之 `--keepout` 车辆已在册，只差接线）。 |
| **L-c 交付层** | **`C6` 越框铜泄漏（796）**：链的框外铜不守恒 —— 独立失效，须具名归属或修。 |

**不是**：图纸层缺图（`_v4` 硬保留件齐）· 引擎能力 · 判据层 · L1（尚无不可行证明）。

## 五、人类工程师路径（大白话 · §21）

**① 信号怎么走**：主芯片 `U1` 上两根慢速管理信号（I2C 时钟/数据）要从**细长焊盘**接出去；实测它们**沿焊盘长边**就有一条净空走廊（预检已给出两条具名走廊）。

**② 挡路的是什么**：板上确有地铜与邻脚挡路 —— 但那是**可绕**的；真正让连接始终做不成的是**我们自己的流程**：算出来的走廊**从没交给布线器**，于是布线器照常在原地浇地铜、把口封死（`R1430`→`R1460`→`R1470` 一路证据，现在指向「**集成**」而非「几何」）。另有独立一处：链在框外改了铜（`C6`）。

**③ 人类方案**：(a) 把**两条走廊接进链** —— 在迷宫**铺铜之前**作为**硬禁区（KEEPOUT）**交给布线器（`R1488` 机制已在册 · 零新板面几何）；(b) **另件**具名处置 `C6` 越框铜。

## 六、一次实现（待新授权 · 唯一一项）

1. **链侧接线**：读预检资产 → 以 `--keepout <net>:x0,y0,x1,y1@<layer>` 交迷宫（`R1488` 语义）；**不加板面几何** · **不改** `WALL_RECT`／放行闸／判据表。
2. **链级 `RED→GREEN`**：无保留 ⇒ 拒；接地正确之硬保留 ⇒ 过。
3. `selftest` 全绿 ＋ `closure PASS`；**树上不得留红件**（失败即当窗回退）。
4. 经**新授权**后方可至多**一次新鲜 `N=1`**（fail-closed · 板冻 `l14/rev-61` · 四源 4/4 · 九行齐）。
5. **`C6` 另件**：具名归属（是否由回填/缝合引入）或修，**不与本项混窗**。

## 七、如实申报未落

停止令后**零运行** · 链侧接线**未落** · `C6` **未处置** · 未跑新 `N=1` · 未写板 · 未改生成器。

`OWNER-ITEMS: 0`
