dataxcash/hw_ic_k2/pm_gate/artifacts/k2_v4/L2/K2_BLOCKER_REPORT_VIA_BRANCH_TWO_RED_v1.md

# 《卡点报告》· 过孔逃逸分支 · 两次 RED 当窗回退 · v1

- **窗口**：#K2-470（授权 = 补有界过孔逃逸分支 ＋ `RED→GREEN` ＋ 预检重跑；GO ⇒ 条件一次新鲜 `N=1`）
- **依据**：宪法红线「**连错 2 次停转 Plan 报卡点**」＋ 现行停止令（「不得再『改参数/改工具/改笼位 → 重跑』，回到 Plan，
  用人类工程师路径说清 ①②③，然后一次实现；并把本轮卡点写成《卡点报告》交监理：**试过什么 / 为何不通 / 缺口在哪层**」）
- **产物影响**：**零**（`exam_runs=0` · 零板写 · 零红件留存 · 树与已推绿点**逐字一致** · HEAD 未变 · 闭包 `PASS` · 基线自检 `152/152 OK`）

---

## 一、试过什么（本窗两次）

### 试 #1 —— `R1514`
- **做了什么**：给规划器加**过孔逃逸分支** —— 在**已注册孔类**上取固定半径集的就近过孔，换层后于**目标层**做同一套面内候选
  （这样「靠换层逃生」的焊盘 —— 即 `R1440` 见证的 `U1` 焊盘 22 —— 就不再被报成「无逃逸」）；同时更新回归里的**候选上限**。
- **为何不通**：套件在**上限断言**处转红 —— 我**手算的界写成 `880`**，而**实现公式实为 `1520`**（面内 `560` ＋ 过孔项 `960`）。
  这一个写错的字面量就是唯一失败。
- **处置**：**当窗自动回退**；树与已推绿点逐字一致。

### 试 #2 —— `R1516`
- **做了什么**：重放同一过孔分支；**唯一改动** = 把上限断言改绑到 `m.CANDS_MAX`（不再写死字面量）。
- **为何不通**：这次转红的**不是**上限，而是**另一个**断言 ——
  `tools/eda_eng/tests/test_eda_eng.py:1886` 之 `assertFalse(p["go"])`：
  加了过孔分支后，**红色用例「四面封闭焊盘」不再真封闭** —— 它的**四堵墙全在 `F.Cu`**，而 **`In5.Cu` / `B.Cu` 上什么都没有**，
  于是该焊盘**现在有了过孔逃逸** ⇒ `plan_escapes(...)["go"]` **变 True**，而测试仍要求 False。
  机制：`_leg_clear` 对**异层**障碍直接 `continue`（`olayer != layer: continue`），所以**探到目标层时看不到任何障碍**。
- **处置**：**当窗自动回退**；树与已推绿点逐字一致。

---

## 二、为何不通（根因）

1. **`R1514` 根因**：**手算 vs 实现公式**。上限字面量必须等于**重新推导**出来的公式值，不能猜。
2. **`R1516` 根因**：**规划器新增了一个自由度（换层）后，回归夹具没有跟着长那个维度**。
   「死出口」用例必须**在规划器能到达的每一层上都封死**，否则新动作会让夹具**假逃生**，红色用例就不再是红色。
   （附带纠正：把断言绑到 `m.CANDS_MAX` 是**错的** —— 那会把「owner 界」回归变成**同义反复**，等于没测。）

**一句话**：**给规划器加自由度时，红色夹具（每层封死）与上限字面量（= 重新推导的公式）必须在同一批里一起改。**

## 三、缺口在哪层

- **`ENG` 实现/回归工序层**。
- **不是**方案/图纸层（`_v4` 硬保留机读件已齐）、**不是**引擎能力、**不是**判据层、**不是** L1。
- 两次都是**夹具缺陷**，**不是方法失败**、**不是引擎能力失败**。

---

## 四、人类工程师路径（大白话 · §21）

**① 信号怎么走**：`I2C2_SCL` 要从主芯片 `U1` 的 **22 号焊盘**（约 `(37.75, 57.16)`，顶层）接出去。在**顶层**上，
地铜已经把 2.0mm/0.30 范围内的**四面八方全堵死**了。`R1440` 的见证说明：**这焊盘其实是「往下钻一层」出去的** ——
约 1mm 外打个过孔落 `In5.Cu`，在那层走。

**② 挡路的是什么**：顶层上是**地铜（66 格）＋ 一条 PCIE 网**。但**更深一层**的挡路者是：**我自己的逃逸规划器压根没有
「往下钻」这条候选** —— 于是它把一个**明明有路（且经过闸核验）的焊盘**判成「无逃逸」。预检此前的拒绝，**只证明了
「面内无逃逸」，从未证明「死出口」**（这就是 `R1512`）。

**③ 人类方案**：给规划器补上**标准的那一手 —— 就近过孔换层，再在目标层走一小段**，**有界**；同时把回归里的
「死出口」夹具**在每一层都封死**，免得新动作**假报胜利**。

---

## 五、一次实现清单（供下一授权窗 · 确定性 · 零搜索 · 有界）

1. **规划器**：加**有界过孔分支** = 已注册孔类 × **固定半径集** × 目标层同一套 `8 向 × 20 步` 面内梯。
   **禁 `while`** · 固定迭代上限 · 每端 `≤60s` · 规划 `≤10min` · 外层 `≤50min` · 无后台 · `≤2` 线程 · 用后查 `ps`（owner 红线）。
2. **引据账**：扩展 `K2_ESCAPE_CRITERION_CITATION_LEDGER_v1` 之**过孔参数**（半径集 ＋ 孔类）。
   **待解差异**：#K2-470 §3.3(1) 点名 `F↔In5` / `F↔B`（**两类**），而 `R1514/R1516` 尝试记录 `VIA_PAIRS = 3`（**三组**）；
   落地前必须把**确切集合**锚进引据账。**无引据者**须具名「**维持现值** ＋ 一次性理由」（§20.5）。
3. **上限**：从**实际公式**重新推导 `CANDS_MAX` 并**写死字面量**进 `test_C467`（**不得**绑 `m.CANDS_MAX`）。
4. **`test_C467`**：(a) 红色夹具**在每一可达层封死**；(b) **新增**用例：**面内封死、他层自由 ⇒ 经孔 GO**（**前置过孔的规划器必拒**，
   = `R1440` 型见证）；(c) 上限字面量。
5. **然后**：预检重跑（**仅未连通端**）⇒ **GO** ⇒ **恰一次 `N=1`**；**仍拒之端**才交**附录 A**（§16.3 死出口/搬迁图 或 守恒级证书 `L1`）。

## 六、拟登记能力项（§22 · 待监理认定）

- **`M-ENG-REGRESSION-DIMENSIONALITY`**
  - **根因**：规划器刚获得**新自由度**时，回归夹具没在那个新维度上封死；**重推的界**差点被绑成**同义反复**。
  - **补法**：给规划器加自由度时，**红色夹具**（每层封死）＋ **上限字面量**（= 重推公式）**同一批一起改**。
  - **闭合判据**：资产 ＋ **同类回归 PASS**（**过孔 GO 用例** ＋ **全层封死 RED 用例** ＋ **上限字面量**），
    并承 `M-ENG-PIN-ACCESS-ESCAPE` 之「一次有效 `N=1` 后 `C1<2`」。

## 七、如实申报未落

- 过孔分支**未落** · 预检**未重跑** · `N=1` **未跑** · 附录 A **未产出**。

`OWNER-ITEMS: 0`
