dataxcash/hw_ic_k2/pm_gate/artifacts/k2_v4/L2/K2_BLOCKER_REPORT_RESIDUAL5_ADDENDUM_T_v1.md

# 《卡点报告》· 附页 T（连续错误停止令 · 连错 2 次）

> 交监理。**服从停止令**（**已即时停手**）。最小篇幅。

## 0. 认领（计数**成立** · 同一根因）
- **两次连错 ＝ 同一机械故障**：**补丁锚点与「当前文件内容」不符** ⇒ 批次中途中止 ⇒ 套件**转红 1/1** ⇒ **当窗自动回退**。
  - `R1476`：**链**侧锚点未命中 ⇒ `regen.py` **未被写入**，而包装层与新测试已写 ⇒ 红 ⇒ 回退。
  - `R1480`：**包装层**锚点 `mr._RESV = _RESV` 属**上一窗已回退**之残留 ⇒ 当前文件**无此行** ⇒ 红 ⇒ 回退。
- **根因**：**按记忆打补丁**，**未先读当前锚点区间**（本席自定纪律「先打印锚点、确认唯一命中再写」**未执行**）⇒ **ENG 工序缺陷 · 两次**。
- **影响**：**对产物零影响**（未跑判卷 · 未写板 · **无红件留存** · 树与已推绿点逐字一致 · HEAD 未变）；代价 ＝ **两段时序**。
- **补救（须先落）**：**锚点前置核验闸** —— 每个待改文件：**读原文 → 断言目标串当前存在且唯一 → 才写**；任一断言失败 ⇒ **整批不写（all-or-nothing）**，**树永不停在半改态**。
- **另**：首试之**设计**（软代价 `AVOID`）**另违 #K2-465 §2.4**（须**硬保留**）⇒ **已被 `_v4` 取代 · 不重试**。

## 1. 试过什么
`item ②`（使「带保留」**链可见并被机械执行**）共试两次：① **软代价**（`AVOID` 罚 50）→ 被判**禁用**；② **硬保留**（核心 `KEEPOUT` ＋ 包装 `--keepout` ＋ 链读 `_v4` 记 `band_keepout`）→ **锚点未命中**，**未跑起来**。

## 2. 为何不通
**两次都死在「打补丁」这一步，引擎从未被真正执行** ⇒ **关于硬保留无任何证据**（正/负皆无）。**已证者为**：图纸侧**完整且机读**（`_v4`：`band_rect_mm`／`layer`／`protected_net`／`kept_out_net`／`enforcement=HARD`），**而本席的改动工序不合格**。

## 3. 缺口在哪层
**ENG 工序层（实现/变更落盘工序）**。**非**方案/图纸层（`_v4` 已齐）· **非**引擎能力 · **非**判据层 · **非** L1。补救 ＝ 上述**锚点前置核验闸**（**小而可验的资产** · 非换手段）。

## 4. Plan 复述（大白话）
- **① 信号怎么走**：一根管理线（I2C）要从连接口接进主芯片；**入口在、走法也已验通**。
- **② 挡路的是什么**：**不是图纸、也不是机器的能力** —— 是**本席「怎么改代码」这件事**：两次**凭记忆打补丁**，两次**没打在地方**、当场回退 ⇒ **机器根本没跑起来**。
- **③ 人类方案**：**先看清再动刀**（读准目标行、确认唯一、否则整批不动），把「那个小框**不许用**」作为**硬规矩**接进机器（**不是偏好**），配**自动检查**，**检查全绿**才**正式量一次**。

## 5. 「一次实现」清单
1. **先落**：**锚点前置核验闸**（读＋唯一断言＋整批不写）**＋ 自回归**。
2. **再落**（经该闸 · 一次成批）：核心 `KEEPOUT` 硬掩码 ＋ 包装 `--keepout` ＋ 链读 `_v4` 传参并记 `band_keepout` ＋ **链级 `RED→GREEN`**。
3. **然后**：预检达标 ⇒ **恰一次 `N=1`**（含 `I2C1_SDA` 端到端）；**不过即停手报监**。

LEGAL-ESCALATION: none
OWNER-ITEMS: 0
