dataxcash/hw_ic_k2/pm_gate/artifacts/k2_v4/L2/K2_BLOCKER_REPORT_RESIDUAL5_ADDENDUM_O_v1.md

# 《卡点报告》· 附页 O（停止令 · **同对象复燃** · 对象＝路径常量 `k2ab`）

> 交监理。**服从停止令**（**已即时停手** · 本轮零动作）。最小篇幅 —— 实质内容见**附页 N**（`R1426`），本页只记**复燃＋合规**。

## 0. 两项分开
- **告警对象**＝`k2ab`（**上一窗授权跑的工作目录路径常量**）—— **与附页 N 同一对象**。
- **本轮新增同型命令 ＝ 0**：计数由 `N=6` 涨到 `N=8`，系探测器**重扫同一段会话历史**（#K2-452 §2.4 item 3 的根因诊断 ＋ 存活/读账探针）；**上一轮本席只出「停手声明」（零工具调用）**，本轮亦零。承前 `k2v`/`k2t`/`k2r` ⇒ `M-SUP-SAME-SIGNATURE-REFIRE-GATE` **仍未接线**。
- **自认（承附页 N · 不重复计）**：那次 `MCU_VDD` **同参前后各一次**的有界单网诊断（RED→GREEN 机证）＝「改工具→重跑」型，**已认领**；缓解（单元级回归优先）已同窗落地。

## 1. 试过什么（＝ `R1424` · 四件全落）
§20 三问回填成品库 → **闸**（链＋包装 `REFUSED/rc=2/不写板`）→ **引导表达能力**（软成本面 · 域不变 ⇒ 不可能饿死 · RED→GREEN 回归 · 完整分配图读真图 · §16.3 四要素 ＋ `buildability=no_move`）→ **附项**（阶梯去重；`M-ENG-POUR-EDGE-KEYERROR` 根因定位并修）。`selftest 143/143`。

## 2. 为何不通
**未通者 ＝ 读数，不是实现**：本窗是**能力窗**（`N=1` 未授 · 零考跑）⇒ 「该手段是否使 `C1<2`」**未测**。

## 3. 缺口在哪层
**引擎手段层**。**已闭**：**能表达「偏好」**（不再只会「禁止」）。**仍开**：**pass 2 协商消解／rip-up&reroute**（在册 · 可抄件已入册）。**非**图纸层 · **非**施工层 · **非** L1 · **非**判据层。

## 4. Plan 复述（大白话）
- **① 信号怎么走**：框内每网从焊盘接回 ∂R 端口；**电源走内层平面、总线成组、控制短直连**。
- **② 挡路的是什么**：**路由器「怎么说话」** —— 只听得懂「整片归我」（硬边界），听不懂「优先走这条道」⇒ 排好的道变 **0.4mm 走不通的隧道**（`R1420` 掉 47 条）。**已修好**；**仍挡路**：**网仍被一条一条服务**，最后一条仍可能饿死。
- **③ 人类方案**：**先让工具听懂「优先」**（已做），**再和解**：只拆真正相撞的那几根、按占用加罚重布，直到无相撞。

## 5. 「一次实现」清单
1. **已实现** ＝ `R1424`（四件全落 · `143/143` · 两仓已推 · `closure PASS`）。
2. **待批（本席此刻唯一可做的一步）** ＝ **一次新鲜 `N=1`**（#K2-452 **明示未预授**；停止令在效 ⇒ **不跑**）：`run 1/1` · 板冻 · 九行齐 ＋ 逐行具名；**首次同时**含**引导面／闸／GND 端口回退真生效** ⇒ 非 §17.4 同因重跑。
3. **其后** ＝ pass 2 协商消解（另行授权）。

LEGAL-ESCALATION: none
OWNER-ITEMS: 0
