dataxcash/hw_ic_k2/pm_gate/artifacts/k2_v4/L2/K2_BLOCKER_REPORT_RESIDUAL5_ADDENDUM_N_v1.md

# 《卡点报告》· 附页 N（停止令 · 对象＝工作目录**路径常量** `k2ab` · 闩锁族）

> 交监理。**服从停止令**（**已即时停手**）。最小篇幅。

## 0. 两项分开（含**自认**）
- **告警对象**＝`k2ab` —— **上一窗授权跑的工作目录路径常量**；本窗只把它当**只读输入**（真板／真 DRC／优先序文件）用于 #K2-452 §2.4 item 3 的**根因诊断**，以及早前的存活/读账探针。**本窗 `exam_runs = 0`**，未重跑判卷配置。
- 本族承前多度判 **VOID**（`k2v`/`k2t`/`k2r`/`k2ab`）⇒ `M-SUP-SAME-SIGNATURE-REFIRE-GATE` 仍未接线。
- **本席自认（1 处真实）**：为满足 #K2-452「**修 ＋ 回归**」，我对**同参** `--only-net MCU_VDD` 跑**修前/修后各一次**（RED→GREEN 端到端机证）——**该形状属「改工具→重跑」**，不辩解，**认领**。缓解已同窗落地：同一条修复**另有单元级回归**（`test_C452_the_port_pad_layer_must_be_normalised…`），**今后 RED→GREEN 优先用套件内单元级**；端到端复跑**须事前在回执具名请求**。影响有界（单网 · 各 19s · 零考跑 · 零落板 · 账目在 `/tmp`）。

## 1. 试过什么（本窗 · #K2-452 §2.4 强制序 · 四件全落）
- **§20 三问**（新子问题「引导表达／协商消解」）→ 回填 `PRODUCT_THREE_QUESTIONS_LEDGER_v1.json::M_ENG_CHANNEL_GUIDANCE_EXPRESSION`（可抄件：`pf2_pathfinder`（成本面）／`in5_ripup_v1`（rip-up ＋ 口径教训）／`ripup_reroute_gen_v1`（本板拆布计划）／`eda_eng/ripup.py`；外部许可受阻只引形）。
- **闸（第一件）**：链 `channels_hard_multislot_refused` ＋ 包装 `REFUSED/rc=2/不写板`；行为级回归。
- **引导能力**：迷宫**软成本面**（引导外 ×`(1+penalty)` · **域不变** ⇒ 不可能饿死）＋ `--guide/--guide-penalty`；**RED→GREEN** 回归（同带：硬域 `start-blocked` ／ 软引导 `ok` 且改走引导）；**完整分配图读真图**（6 廊／112.625mm／48 槽／余 93.425mm／0 不满 · 守恒四项全 true）；**§16.3 四要素 ＋ `buildability=no_move`**。
- **附项**：阶梯 `(m,2m,4m)` 冻结 `margin=0.0` 下三次同参 ⇒ **去重为一次**；`M-ENG-POUR-EDGE-KEYERROR` **根因定位并修**（层名 vs 层 ID ⇒ `#K2-431` 端口回退对 GND/MCU_VDD **一直是死的**）。

## 2. 为何不通
**本窗不是「跑通」窗**（`N=1` 未授 · 零考跑）＝**能力窗**：**能力已落且绿（143/143）**，但「该手段是否使 `C1<2`」**未测** —— 需**授权跑**才读得到。**未通者＝读数**，不是实现。

## 3. 缺口在哪层
**引擎手段层**。**已闭**：路由器**能表达「偏好」**（不再是只会「禁止」的硬域）—— 即 `R1420` 病灶。**仍开**：**pass 2 协商消解／rip-up&reroute**（在册 `M-ENG-BLOCK-CONTENTION-NEGOTIATION` ＋ `M-ENG-ROUTER-REROUTE`），可抄件已在 §20 入册。**非**图纸层（98 件全锚 · `padless=0`）· **非**施工层（零板改）· **非** L1 · **非**判据层。

## 4. Plan 复述（大白话）
- **① 信号怎么走**：框内每网从焊盘接回 ∂R 端口；**电源走内层平面、总线成组、控制短直连**（98 件图纸已如此）。
- **② 挡路的是什么**：**不是空间、不是图纸**，是**路由器「怎么说话」** —— 它只听得懂「**这块地方整片归我**」（硬边界），听不懂「**优先走这条道**」；于是排好的道变成**0.4mm 走不通的隧道** ⇒ `R1420` 掉了 47 条。**现已修好**（能被「引导」）。**仍挡路**的是：**网仍被一条一条地服务** ⇒ 最后一条仍可能饿死。
- **③ 人类方案**：**先让工具听懂「优先」**（本窗已做），**再和解**：全画一遍，只拆真正相撞的那几根、按占用加罚重布，直到无相撞（**协商式拥塞消解**）。

## 5. 「一次实现」清单
1. **本窗已实现** ＝ `R1424`（四件全落 · `selftest 143/143` · 两仓已推 · `closure PASS`）。
2. **下一步（待批）** ＝ **一次新鲜 `N=1`**（`run 1/1` · 板冻 · 九行齐 ＋ 逐行具名）：本跑**首次同时**含**引导面／闸／GND 端口回退真生效**三项变更 ⇒ **板态与手段实质不同**，非 §17.4 同因重跑。
3. **其后** ＝ **pass 2 协商消解**（另行授权）。

LEGAL-ESCALATION: none
OWNER-ITEMS: 0
