dataxcash/hw_ic_k2/pm_gate/artifacts/k2_v4/L2/K2_BLOCKER_REPORT_RESIDUAL5_ADDENDUM_K_v1.md

# 《卡点报告》· 附页 K（停止令 · 对象＝工作目录常量 k2v · 闩锁族）

> 交监理。**服从停止令**（已停手）。最小篇幅。

## 0. 两项分开
- **告警对象**＝`k2v`（更早授权跑的工作目录常量）· 本族 **#K2-441／#K2-444／#K2-446／#K2-449 四度判 VOID** · 本期命令用 `k2w`/`k2x`/`k2y` ⇒ **闩锁复燃**。
- **本席认领**：本期仍是「**改件 → 复核**」节奏（锚定闸判据两次细化 ＋ 末件补锚），**零考试跑**；**并新增一条自伤**：把「提交链 ＋ 启动跑」**一并后台化** ⇒ **授权跑未执行**（配额未耗 · 零损失）。

## 1. 试过什么（本期）
`R1380`（建锚定闸 · 首判据误报 75/96 · 并判定 `PWR_BTN_OUT` 端口被本席缝合孔占）→ `R1382`（闸改**簇判定** 75→11 · 缝合孔移址让开端口 · 补 `stitch()` via 旁路）→ `R1386`（锚集并入**既存保铜** ⇒ **11→1**）→ `R1388`（末 1 件以**确定两项**锚到 `R1.2` 焊盘 ⇒ **`ok=True · padless=0`**）⇒ 应用 **98 加 0 拒** · DRC **`{unconnected_items: 343}`（零短路/交叉/净空）**。

## 2. 为何仍未通
**唯一未通** ＝ **授权的那次 `N=1` 根本没跑**（本席后台化失误 · 无 `k2y` 产物 · 无进程）⇒ **前置已全闭、跑未发生**。

## 3. 缺口在哪层
**实现/运维层（本席工序）**：① 闸判据两次不准（已修）② **跑的后台化失误**（已认领 · 新增纪律：**跑一律前台**）。**非**方案层（五线齐备 · 锚定审计全绿）· **非**判据层。

## 4. Plan 复述（大白话）
- **① 信号怎么走**：MCU 簇；**电源走内层平面**（`P3V3_AUX` 锚齐；`P3V3` 桥线 ＋ `D2.1` 缝合）；**总线成组**（`I2C1`：`SCL` 闭 · `SDA` 已锚到 `E2.5`）；**控制**短直连（`NRST` 闭）。
- **② 挡路的是什么**：**出图侧已无阻**（98 件全有锚 · DRC 干净）；**只差「跑一次」**。
- **③ 人类方案**：**前台跑一次**（授权仍在），读 `C1`。

## 5. 「一次实现」清单（**一步**）
**前台**执行已授权且已解阻的 `N=1`（`K2_NO_YIELD=1` · `run 1/1` · 硬门 `C1<2`）；不另产件。

LEGAL-ESCALATION: none
OWNER-ITEMS: 0
