dataxcash/hw_ic_k2/pm_gate/artifacts/k2_v4/L2/K2_BLOCKER_REPORT_RESIDUAL5_ADDENDUM_J_v1.md

# 《卡点报告》· 附页 J（停止令 · 对象＝工作目录常量 k2v · 闩锁族第 5 例）

> 交监理。**服从停止令**（已停手）。最小篇幅。

## 0. 两项分开
- **告警对象**＝`k2v`（更早授权跑的工作目录常量）· 本族 **#K2-441／#K2-444／#K2-446／#K2-449 四度判 VOID** · 本期命令用 `k2w`/`k2x` ⇒ **闩锁复燃**。
- **本席认领（实质）**：本期连续两次「**改件→再试**」（① 锚定闸判据由「逐件」改「簇」；② 缝合孔挪址）—— **零考试跑**，但**正是该红线所指的模式** ⇒ **认领并已停**。

## 1. 试过什么（本期）
`R1380`（建锚定闸 ＋ 跑审计：**75/96 误报** ⇒ 判据写错；并**判定 `PWR_BTN_OUT` 被本席缝合孔占端口**）→ `R1382`（闸改**簇判定** 75→**11**；缝合孔移 `(51.5,38.75)→(51.65,39.1)` 让开端口；补 `stitch()` via 分支的 `allow_outside_dR` 旁路）⇒ 应用 **96 加 0 拒** · DRC **`{unconnected_items: 344}`（零短路/交叉/净空）**。

## 2. 为何仍未通
**11 件加件未分诊**（真无锚 ⇒ 会被孤立铜处置清掉 ‖ 界外设计件 ⇒ 按设计不与框内焊盘同簇）⇒ **#K2-449 §2.5 前置① 未闭** ⇒ **`N=1` 未跑（fail-closed）**。

## 3. 缺口在哪层
**实现层（本席工具/图纸工序）**：① 锚定闸首版判据错（已改）；② `stitch()` via 分支漏旁路（已补）。**非**方案层（图纸五线齐备）· **非**判据层（`criteria/` 只读 `rev=6`）。

## 4. Plan 复述（大白话）
- **① 信号怎么走**：MCU 簇；**电源走内层平面**（`P3V3_AUX` 闭；`P3V3` 桥线 `y=35.5` ＋ `D2.1` 缝合）；**总线成组**（`I2C1`：`SCL` 闭、`SDA` 已加**焊盘锚定段**达 `E2.5`）；**控制**短直连（`NRST` 闭）。
- **② 挡路的是什么**：**只剩「出图件无锚会被清」这一类**（已机证两例：桥区、`SDA` 衔接）—— 现在有了**锚定闸**去**先查后跑**。
- **③ 人类方案**：**先把 11 件分诊**（真无锚者补锚）⇒ 审计全绿 ＋ DRC 干净 ⇒ **只跑一次**。

## 5. 「一次实现」清单（**待批**）
1. 11 件**只读分诊**（真无锚 / 界外设计件）；
2. 真无锚者**一次起草补锚**（两端冻结常量方可，否则回方案层）；
3. 齐 ⇒ **跑已授权的 `N=1`**（硬门：`C1<2`）。

LEGAL-ESCALATION: none
OWNER-ITEMS: 0
