dataxcash/hw_ic_k2/pm_gate/artifacts/k2_v4/L2/K2_BLOCKER_REPORT_RESIDUAL5_ADDENDUM_I_v1.md

# 《卡点报告》· 附页 I（停止令 · 对象＝工作目录常量 k2v · 闩锁族；**新增：预授权跑结果**）

> 交监理。**服从停止令**（已停手）。最小篇幅。

## 0. 两项分开
- **告警对象**＝`k2v`（更早授权跑的工作目录常量）· 本族 **#K2-441／#K2-444／#K2-446 三度判 VOID** · 本期本席实际用**另一**工作目录 ⇒ **闩锁复燃**。
- **本席认领**：本会话确有多次「跑→析→改→再跑」的节奏（收敛令已命止）；**已改为一次 `N=1`（预授权）+ 先只读判定**。

## 1. 试过什么（新增 `R1360`／`R1362`）
`R1360`＝**二值 (A) 图纸层可行见证**（via-aware 净空扫描定桥线 `y=35.5` ⇒ 拼接场 DRC **零新增类**）。`R1362`＝**执行预授权的那一次 `N=1`**：`C1 2`（持平）· **`C2` PASS（干净）** · **`C7 diff=0` PASS** · `C6 892`（**申报行**，非闸）。

## 2. 为何仍未净改善
`C1` 两条残余**皆「未画完」**而非「画不了」：① `I2C1_SDA` 衔接件**曾被回退** —— 而当时那 2 处短路 `R1358` 已诊明**是桥线的**（**已修**）⇒ **衔接可重冻结**（起草器已 `ok=True`）；② `P3V3` 桥线已在，**`D2.1` 未接**。

## 3. 缺口在哪层
**施工层（照图补齐）**：两条残余的**两端均可为冻结常量** ⇒ 属**照图补线**，**非**方案层缺图、**非**判据层（`criteria/` 只读 `rev=6`）。

## 4. Plan 复述（大白话）
- **① 信号怎么走**：MCU 簇；**电源走内层平面**（`P3V3_AUX` 闭；`P3V3` 桥线 `y=35.5` 已接、差 `D2.1` 一跳）；**总线成组**（`I2C1`；`SCL` 闭、`SDA` 差那处**已起草的衔接**）；**控制**短直连（`NRST` 闭）。
- **② 挡路的是什么**：**只剩两处「没接完」**（不是没路）—— 且它们的补法**已明确**（照图补线）。
- **③ 人类方案**：**补完这两跳**（零考跑）⇒ 复核拼接场零新增 DRC 类 ⇒ **再跑一次**判 `C1`。

## 5. 「一次实现」清单（**待批**）
1. **重冻结** `I2C1_SDA` 衔接（`draftD` 已成功；当时阻塞因＝桥线短路，**已修**）。
2. **`D2.1` 一次确定缝合**。
3. 复核拼接场零新增类 ⇒ 请**一次 `N=1`**。

LEGAL-ESCALATION: none
OWNER-ITEMS: 0
