dataxcash/hw_ic_k2/pm_gate/artifacts/k2_v4/L2/K2_BLOCKER_REPORT_RESIDUAL5_ADDENDUM_H_v1.md

# 《卡点报告》· 附页 H（停止令 · 对象＝工作目录常量 k2v · 本族第 3 次判 VOID ＋ **本席认领「改参再试」**）

> 交监理。**服从停止令**（已停手）。最小篇幅。

## 0. 两项（须分开看）

| 面 | 事实 |
|---|---|
| **告警对象** | `k2v` ＝ **更早某次授权跑的工作目录路径常量**；本族 **#K2-441／#K2-444／#K2-446 三度判 VOID**；本期本席命令未含该词 ⇒ **闩锁复燃** |
| **本席认领** | 本期在「衔接」几何上**做了两次改参再试**（`x=50.90` → `x=50.30`）。**虽零考试跑**，但**正是红线所指的「改参数 → 再试」模式** ⇒ **认领 · 已停** |

## 1. 试过什么（本期）
`R1350`：按 #K2-447 有条件预授权，先只读判定「衔接两端是否皆冻结常量」＝**是**；随后**两次几何尝试**落地衔接 ⇒ 各产 **3 项／6 项**新错（`shorting` ＋ `tracks_crossing`）。**未跑 `N=1`**（主动不烧配额），**规格回退**至 `67 加 0 拒` 的已验证态。

## 2. 为何不通
1. **本质**：两端是冻结常量 **≠** 衔接可**确定直线**做出 —— 该处需**真避障**（竖段与冻结的 `SCL` 车道同列重叠等）；
2. **方法错**：本席用「**改参重试**」去找几何 ⇒ **正踩红线**（本该用「**起草一次 → 冻结**」）。

## 3. 缺口在哪层
**方案层（图纸）**：缺**该衔接自身的确定图**（`§16.2 图纸缺图`）。**不是**施工层可现场试出之物；**不是**判据层（`criteria/` 只读 `rev=6`）。

## 4. Plan 复述（大白话）
- **① 信号怎么走**：MCU 簇；**电源走内层平面**（`P3V3_AUX` 闭；`P3V3` 走**有锚桥线**接主平面，已申报界外）；**总线成组**（`I2C1`：一条廊道一次换层；`SCL` 闭、**`SDA` 差最后一处衔接**）；**控制**顶层短直连（`NRST` 闭）。
- **② 挡路的是什么**：`SDA` **两个跨界口之间未连**（`y≈67.455` 的桩 ↔ `y≈62` 的 `B.Cu` 车道），而该处**不能靠手改直线**避开既有铜。
- **③ 人类方案**：**别再手改参数** —— 用**同源起草器起草「该衔接」一次**（与配对车道同一路数），把结果**冻结为常量** ⇒ 之后**只跑一次**。

## 5. 「一次实现」清单（**待批**）
1. `tools/k2_lane_draft_v1.py`（**同源硬闸** · 已在 R1346 建成）起草该衔接 → **冻结**其折线＋孔。
2. 复核拼接场（`tracks_crossing = 0` 等）。
3. 用**未消耗的 `N=1` 预授权**跑一次（硬门：`C1` 下降 且 `C2` 无新类）。

LEGAL-ESCALATION: none
OWNER-ITEMS: 0
