dataxcash/hw_ic_k2/pm_gate/artifacts/k2_v4/L2/K2_BLOCKER_REPORT_RESIDUAL5_ADDENDUM_G_v1.md

# 《卡点报告》· 附页 G（停止令 · 对象＝工作目录常量 k2v · 闩锁族）

> 交监理。**服从停止令**（已停手）。**最小篇幅**（承附页 C 自限）。本族 **#K2-441 §2.1／#K2-444 §2.1 两度判 VOID**。

## 1. 对象与计数
token `k2v` ＝ **上一授权跑的工作目录路径常量**；本席本期命令**未含该词**（本期用另一工作目录）⇒ **闩锁复燃**（`M-SUP-SIGNATURE-REFIRE-GATE`）。

## 2. 试过什么（承附页 F · **新增 R1336／R1338**）
`R1336`：**补做 zone-aware `C6`**（#K2-444 §2.4 令；`wipe_resolve_chain` 单点，并列报 `legacy_diff`）＋ **`R-g` 决定性判读**：桥区**被链的孤立铜处置清掉**（终板 zone 表只有原两个）。`R1338`：`R-g` 改 **机制 D＝有锚的 `In4` P3V3 桥接走线**（起于既有 `F.Cu-In4` 过孔 ⇒ 不会被处置；止于主平面同层同网 ⇒ 焊为一体）；落地器**新增界外显式申报**（`allow_outside_dR` ＋ 结果记 `outside_dR`）⇒ 应用 **67 加 0 拒** · **legacy C6 `diff=1`（改动可见）**。

## 3. 为何不通（据实）
1. 出图工具链缺避障折线生成（手打/几何不可行）；2. 起草器异源输入（已修）；3. 未成组 ⇒ 两车道互穿（R1332 已修）；4. 桥区**未锚** ⇒ 被孤立铜处置清掉（R1338 已修）；5. **仍不通**：`I2C1_SDA` 成组车道**已冻结仍不闭合**（断点 `B.Cu`0.2 ↔ `F.Cu`0.6）。

## 4. 缺口在哪层
**方案层（图纸）× 实现层 交界**：① 图纸给车道几何、**未给「对迷宫不可侵犯」的声明**（共用搜索域）；② 图纸**未覆盖 `SDA` 断点**；③ **链的工序副作用**（孤立铜处置会清掉无锚的新增平面件）需在出图时被考虑。**非**判据层（`criteria/` 只读 `rev=6`）· **非**分类层。

## 5. Plan 复述（大白话）
- **① 信号怎么走**：MCU 簇；**电源走内层平面**（`P3V3_AUX` 已闭；`P3V3` 以**桥线**接入主平面，待判）；**总线成组**（`I2C1`：一条廊道→一次换层→进芯片；`SCL` 已闭、`SDA` 未）；**控制**顶层短直连（`NRST` 已闭）。
- **② 挡路的是什么**：不是「没路」，而是**一处具体断点**（`SDA` 的 `B.Cu`0.2↔`F.Cu`0.6）＋ **责任边界未建模**（冻线 vs 迷宫）。
- **③ 人类方案**：**把已定铜占位为禁越** ⇒ **按断点补全图纸** ⇒ **只跑一次**。

## 6. 「一次实现」清单（**待批**）
1. `I2C1_SDA` **补一次 `F.Cu↔B.Cu` 换层**（在成组车道上）。
2. （可选，为「先占位」）冻线廊道**置为迷宫禁越**。
3. 齐 ⇒ **一次施工 ＋ 一次 `N=1`**（硬门：`C1` 下降 且 `C2` 无新类；`C6` 按**申报后** zone-aware 口径如实判 —— **预计 FAIL**，属 §2.7「申报不隐藏」的正常结果）。

LEGAL-ESCALATION: none
OWNER-ITEMS: 0
