dataxcash/hw_ic_k2/pm_gate/artifacts/k2_v4/L2/K2_BLOCKER_REPORT_RESIDUAL5_ADDENDUM_E_v1.md

# 《卡点报告》· 附页 E（停止令 · 对象＝工作目录常量 k2t · 闩锁族第 4 例）

> 交监理。**服从停止令**（本席已停手：不再改参/改工具/重跑）。
> 本附页同时是 **§2.3 要求的《卡点报告》**（试过什么／为何不通／缺口在哪层）＋ **Plan ①②③**。

## 1. 服从与对象具名

| 项 | 事实 |
|---|---|
| 本窗考跑 | **恰 1 次** —— #K2-443 §三.4 授权的那一次 `N=1`（配额用尽）；**无同参重跑、无改参→重跑** |
| 被计数对象 | `k2t` ＝ **更早某次运行的工作目录路径常量**；本窗命令实际使用**另一**工作目录（`k2u`） |
| 定性 | **闩锁型假阳 · 第 4 例**（`m1m2`→`m1m2`→`k2r`→`k2t`）· **`M-SUP-SIGNATURE-REFIRE-GATE` 复发**（#K2-443 已登记）⇒ 计数在**历史证据**上累加，**每轮复燃** |

## 2. 试过什么（本轮回溯 · 全部在册有号）

`R1316`（R-e/R-f ＋ 一跑 · `C1 3→3` 平盘）→ `R1318/R1320`（R-g/R-h 机检提案）→ `R1322`（**C6/zone 盲区闭合** · 假绿量化 943）→ `R1324`（`lane` 原语 ＋ 焊盘阵实测）→ 几何法画全 **NONE found** → 起草器**参数配错**零产出 → **同源 DRC 起草成功** → `R1326`（**`R-h` 冻线 59 常量**）→ `R1328`（**`R-g` 桥区落地** ＋ §20 三问 ＋ 一跑：**`C1 3→2`**，`I2C1_SCL` 闭合 **但 C2 新破 `tracks_crossing`**）。

## 3. 为何不通（据实三条）

1. **出图工具链缺避障折线生成** ⇒ 手打/几何扫描皆不可行（实测 `NONE found`）；
2. **起草器输入未同源** ⇒ 零产出（已于 R1326 修正为同源 DRC，**起草法即通**）；
3. **（当前卡点）冻线与迷宫铺线交叉** ⇒ 冻线在**迷宫之前**加入，迷宫**不知道它是固定的**，随后跨过它 ⇒ **`tracks_crossing`**（一网闭合、一行新破 ⇒ 非净改善）。

## 4. 缺口在哪层

**方案层（图纸层）× 实现层** 交界处：
- **图纸侧**：冻线只给了「车道几何」，**未给「该车道对迷宫不可侵犯」的声明**；
- **实现侧**：清区场与迷宫域**未做「保留区」建模** —— 二者共用同一搜索域 ⇒ 必然互穿。
（**非**判据层：`criteria/` 只读 `rev=6` 未动；**非**分类层：问题已具名。）

## 5. Plan 复述（人类工程师路径 · 大白话）

- **① 信号怎么走**：左区＝MCU 簇。**电源走内层平面**（引脚落到平面即可 · 现状：`P3V3_AUX` 已闭、`P3V3` 靠桥区待判）；**总线**（`I2C1` 对）**成组一条廊道 → 一次换层 → 进芯片**（现状：`I2C1_SCL` 已闭）；**控制**顶层短直连（`NRST` 已闭）。
- **② 挡路的是什么**：不是「没路」，而是**两条已定好的线（我画的冻线 vs 迷宫自己铺的线）互相踩** —— 因为**谁都不知道对方是固定的**（共用搜索域）。
- **③ 人类方案**：**先占位、再布线** —— 把**冻线所占的廊道**先标成**固定区**（迷宫禁越），或**先让迷宫铺完、再按固定区补画**；两条路都可，**选一条**即可。之后**只跑一次**。

## 6. 「一次实现」清单（**待监择一后执行**）

1. **修 `tracks_crossing`**：(a) 把冻线廊道**置为迷宫禁越** ／ (b) 迷宫后起草 ／ (c) 冻线**并入通道约束**。
2. **补 `I2C1_SDA` 的独立车道**（SCL 已闭 ⇒ 同法可做）。
3. **`P3V3`**：桥区已落地；合并效果待 `C2` 修好后判读。
4. 上述齐 ⇒ **一次施工 ＋ 一次 `N=1`**（九行齐 ＋ 通道非空 ＋ 逐线归因）。

LEGAL-ESCALATION: none
OWNER-ITEMS: 0
