dataxcash/hw_ic_k2/pm_gate/artifacts/k2_v4/L2/K2_BLOCKER_REPORT_RESIDUAL5_ADDENDUM_D_v1.md

# 《卡点报告》· 附页 D（**连续错误 2 次 · 真事件** · 非假阳）

> 交监理。**服从停止令**（本席已停手；本轮零考跑、零改参、零改工具、零重跑）。
> 本附页与 A/B/C 不同：**A/B 是闩锁假阳**，**本附页认领的是本席自己的两次真错误**。

## 1. 试过什么（错在哪一步）

时间窗 R1310（第三次停止令的应答批），**同一条命令**内两步：

| # | 步骤 | 结果 |
|---|---|---|
| 1 | `python3 - <<'PY' …`（**用 `%` 格式化**写附页 B 的 markdown 正文） | **rc=1**：`TypeError: not enough arguments for format string` |
| 2 | `git add … && git commit …`（同批后续） | **rc=128**：`fatal: Unable to create '…/.git/modules/k2/index.lock': File exists.` |

⇒ 触发「**连错 2 次**」红线。**本席认领，无异议。**

## 2. 为何不通（根因）

1. **`%` 格式化与正文冲突**：正文里含**其它 `%` 字符**（模板预设 3 个 `%s`，正文另含 `%`）⇒ 参数不足即崩。**根因＝把「数据」当「格式串」用**。
2. **git 锁**：前一步失败使同一批的 git 时序异常 + 残留 `index.lock` ⇒ 后一步 git 直接拒。**根因＝失败后未先检锁即重试，且把多步串进一条命令**。

## 3. 当场修法（**已生效 · 可复核**）

| 错误 | 修法 | 复核 |
|---|---|---|
| `%` 格式化 | **弃用 `%` 格式化**，改**固定模板 + `.replace(占位, 值)`**（数据不再进格式串） | 重跑即写出文件；`R1310` 附页 B **正常提交并推送** |
| git 锁 | 重试前先 **`pgrep -a git`** 判无进程、确认锁已释放**再**执行；git 步骤**不再与写盘串在同一 `&&` 链** | `git status` 干净、两仓 `0/0` 已推、`closure PASS` |

**损失清点：零。** 未丢件（附页 B 内容完整入库）、未烧任何考跑（该批无 `N=1`）、板未动、四源 4/4。

## 4. 缺口在哪层

**实现/运维层（ENG 自身工序）**，**不是**方案层、不是判据层、不是图纸层：
- 缺口①：**数据 ≠ 格式串**（heredoc 载荷一律走模板替换）。
- 缺口②：**多步命令的失败原子性**（写盘 / git 分离；失败先探锁再重试）。
两条都已固化为本席**工序纪律**（与附页 B 的「一件一命令」合并）。

## 5. Plan 复述（人类工程师路径 · 压缩版；全文见附页 B §4）

- **① 信号怎么走**：左区＝MCU 簇；**电源走内层平面**（引脚落在平面即可）；**控制**顶层短直连；**总线**每条一次换层；**少数几条在 `x=51.5` 跨界**。
- **② 挡路的是什么**：区界**悬空半桩**（`NRST` 已治）· **电源脚无平面铜**（`P3V3_AUX` 已治）· 余下两处在**图纸侧**：`I2C1` 成对同角两落点**互挤**（新冒 `I2C1_SCL`）· `P3V3` **目标端在框外**（`no-free-goal-node`）。
- **③ 人类方案**：`I2C1` **成对一条廊道**（宽 ≥ 2 网＋净空 · 落点按网距 · 共享一次换层）；`P3V3` 桩**直接落平面指**（或界外盲孔**登记为冻结端口**）；然后**只跑一次**。

## 6. 「一次实现」清单（**待批 · 本轮不执行**）

1. `R-e` — 线 4 改 I2C1 成对廊道（冻结常量）。
2. `R-f` — 线 5 目标端二选一。
3. 落地后**一次 `N=1`**（九行齐 ＋ 通道非空 ＋ 逐线归因）。

## 7. 与 A/B/C 的口径区分（防混淆）

- **A/B/C**＝**告警侧**闩锁假阳（同一历史证据重放，无新信息）⇒ 请监护侧按 B §2 接线。
- **本附页 D**＝**ENG 侧**自己的两次真错误 ⇒ 已认领、已修、已固化纪律；**不再复发**。
- 两者**不同源**，请分别入账。

LEGAL-ESCALATION: none
OWNER-ITEMS: 0
