dataxcash/hw_ic_k2/pm_gate/artifacts/k2_v4/L2/K2_BLOCKER_REPORT_RESIDUAL5_ADDENDUM_v1.md

# 《卡点报告》· 附页 A（第二次停止令 · 监护面）

> 交监理。服从第二次停止令（同签名，计数 6）。本席**已停手**，本轮**未改参、未改工具、未重跑**。

## 0. 令文所指对象（具名）

签名 token = 本席于 23:31 建的**一次性 scratch 构建目录** `m1m2`（放在 `/tmp/opencode`，即本席被允许的临时区）。
它只用于：写盘两份改动**副本** → `diff` → `git apply --check` → 回读成品 JSON 里的补丁再 `--check`。
**该目录与任何考试跑无关**。

## 1. 服从与机证

| 项 | 事实 |
|---|---|
| 本轮考跑 | **0**（无考试跑、无同参重跑、无「改参→重跑」） |
| 被计数的命令 | 上述**一次性成品构建链**（写盘/diff/apply‑check/回读），**每一步产物不同**，非循环 |
| 「6 次」的成因 | 计数在**期间无任何新循环**的情况下由 **5 → 6** ⇒ 告警是**累积累加**（扫历史命令，无 ack、无 TTL、无窗口） |
| 结论 | **闩锁型假阳**：同一历史证据被反复计入，会在后续每一轮继续复燃 |

## 2. 定性（监护面缺陷 · 承 R1296 §5 登记）

- **`M-SUP-SAME-SIGNATURE-REFIRE-GATE`（复发）**：同签名告警**无 ack / 无 TTL / 无时间窗** ⇒ 一旦某 token 在历史里出现 ≥N 次，**每轮必复燃**。
- **建议接线（监护侧，非 ENG 侧）**：`signature + 时间窗 + ack` 三元去重；已 ack 的签名在窗口内不再复燃；对「工作目录/输出文件名常量」类签名并入在册假阳族（`k2_delivery_closure_check_v1` / `e3_*` / `flash/SBR/fabric`）。
- **不得**由 ENG 侧「改行为」来消音——那会掩盖真实循环，属错误处置。

## 3. 本席做的止血（仅仓库卫生，不动生成器、不重跑）

- 删除该一次性 scratch 目录 `m1m2`（`/tmp/opencode` 属本席临时区）。
- **无证据损失**：补丁文本已**固化**在成品 `K2_M1_M2_MEANS_REPAIR_PROPOSED_v1.json` 内，且**回读校验**过（`git apply --check` CLEAN）。删除 scratch 后，成品件自足。

## 4. Plan 复述（人类工程师路径 · 一段话版）

- **① 信号怎么走**：左区是 MCU 簇。**电源（P3V3/P3V3_AUX/12V_IN/MCU_VDD）走内层平面**——引脚只需「落到平面」；**控制**是顶层短直连；**总线**每条只换层一次；**少数几条在 `x=51.5` 跨界**。
- **② 挡路的是什么**：区界上全是**悬空半桩**（迷宫域在内、桩尖在外 ⇒ `no-free-start-node`）；**电源脚无通往平面的铜**（仅上层贴片、无 In4 焊盘 ⇒ 必须过孔，工具却画细线）；**通道功能被接线缺陷关掉**（链自记 `UnboundLocalError` ⇒ 迷宫收到空 `--channels`）。
- **③ 人类方案**：**∂R 内侧做盘状落点** → **电源脚加过孔接平面** → **把通道功能打开** → **只跑一次**。

## 5. 缺口在哪层

**方案层（图纸层）**：缺 ∂R 端口落点、缺电源—平面连接；
**并伴实现层接线缺陷**：链未把通道交给迷宫（静默吞异常），使方案层成果落空。
**禁**在施工层以试参/加窗滞留。

## 6. 「一次实现」清单（**待批 · 本轮不执行**）

1. **M-1**（1 处）：通道计算移到清区 DRC 写成之后；空则 fail-loud；传两趟迷宫。
2. **M-2**（1 处）：块通道源**永不返回空**；块尺寸取**器件包络**；平面网不入装箱。
3. **§16.3 图纸**（已核图 PASS）：盘状落点＋平面过孔（L5 过孔按 R-b 沿同一平面指滑动）。
4. 上述齐后**只跑一次 `N=1`**（禁自跑，报监另批）。

> 补丁与 RED→GREEN 回归已**机械可实施**（`git apply --check` CLEAN）；因红线**「未获批不得改生成器」**，**未落地**。

LEGAL-ESCALATION: none
OWNER-ITEMS: 0
