dataxcash/hw_ic_k2/pm_gate/artifacts/k2_v4/L2/K2_BLOCKER_REPORT_RESIDUAL5_v1.md

# 《卡点报告》· K2 左区残余 5 项（ENG/ARCHER · 2026-09-29）

> 交监理。服从本轮停止令（`命令重复 5 次(疑似暴力迭代/改参重跑)`）：**已停手**。
> 如实声明：本窗 **0 考跑**；被标记的重复是**同一副本**上的「写盘 → diff → `git apply --check` → 回读校验」构建链，
> **不是**考试重跑、**不是**改参重跑。照令停止，并登记为本轮闸门假阳（在册族，见 §5）。

## 1. 试过什么（按时间序，全部有号）

| 阶段 | 做法 | 读数 |
|---|---|---|
| #K2-415/#K2-417 | 四堵网并入变更集 · 末跑 | `C1=5`（净底） |
| #K2-419/##K2-429/#K2-430 | 通道分配**入链**（`mr._CHANNELS`） | 2/5 → 3/5 |
| #K2-431 | owner 直令：左区**整片清空重画** | `C1=7`（两跑，同因） |
| #K2-434 | 换手段：K-1 铺铜纳清 / K-2 功能分块 / K-3 多块协动 / K-4 逐块工序 | — |
| #K2-436 | 该手段**唯一一次**端到端跑 | `C1 7→5`，九行齐，FAIL |

**已证伪并弃用的杠杆**（勿再试）：加宽通道（R1244）· 有界阶梯边距（R1248）· reach-纳入（R1250）· **全框无界摆放**（R1254）· 把 GND 当非障碍（B1，致短）· 让位阶段（R1194，致劣）· U1 留守＋保旧线（A⁶，`C2` 破）。
⇒ **通道宽度 / 摆位 / 搜索 都不是成因**（守恒级证书已在册）。

## 2. 为何不通（三条，机证）

1. **边界无落点**：清区把跨界网在 `x=51.5` 切成**悬空半桩**；迷宫域被 `--bound-rect` 限死在内，桩尖界外无格 ⇒ `no-free-start-node`（5 条中 4 条）。
2. **电源脚无平面连接**：`C84.1(P3V3)`、`C90.1(P3V3_AUX)` 是**仅上层贴片焊盘**，且**无任何器件带 In4 焊盘** ⇒ 与自身 `In4` 平面之间**无铜路**，除非加过孔；工具却去画细线。另 `C84.1` 上方 `P3V3` 平面指未覆盖。
3. **通道功能实际未生效**（决定性自曝）：链自记 `channels_compute_failed: UnboundLocalError` ⇒ 迷宫收到**空 `--channels`**；且 `channels_arg_by_block` 自身返回 `''`、`per_block_flow` 无生产调用者 ⇒ **#K2-436 的「四件手段」在执行上只有 K-1**。

## 3. 缺口在哪层

**方案层（图纸层）**，不是施工层：
- 缺 **(i) 区界端口落点**（每条跨界网在 `∂R` 内侧的固定落点）；
- 缺 **(ii) 电源—平面连接**（过孔或平面延伸）；
- 并伴 **(iii) 实现层接线缺陷**：链未把通道交给迷宫（静默吞异常），使方案层成果落空。

**禁止**在施工层以「试参/加窗/再试」滞留（§16）。

## 4. 一次实现（清单 · 待批，本轮不执行）

1. 接线修复（1 处）：通道计算移到清区 DRC 写成**之后**；空则 **fail-loud**；通道传给**两趟**迷宫。
2. 通道源修复（1 处）：块通道源**永不返回空**；块尺寸取**器件包络**而非 DRC 端点散布；平面网不入装箱。
3. 图纸落地（§16.3 四要素件在册）：4 条 `no_move`（端口/平面落点，坐标已冻结）＋ 1 条 `relocation_listed`（`C84.1` 短桩或平面延伸）。
4. 之后**只跑一次** `N=1`（禁自跑，报监另批）。

## 5. 监理面登记（同账）

- `M-SUP-SAME-SIGNATURE-REFIRE-GATE` 复现：本轮 `命令重复 5 次` 命中**构建链**（同一副本的写盘/diff/校验），与「考试重跑」无关 ⇒ **建议在册为假阳族**（与 `k2_delivery_closure_check_v1` / `e3_*` / `flash/SBR/fabric` 同族：**输出文件名/工作目录常量**）。
- 本报告**不含**任何重跑诉求；本轮以「停手＋交报告」收束。

LEGAL-ESCALATION: none
OWNER-ITEMS: 0
