dataxcash/hw_ic_k2/pm_gate/artifacts/k2_v4/L2/REQUIREMENT_IMPLEMENTATION_SEPARATION_v1.0.md

# L2 规矩：需求 / 实现分家（v1.0）

> 立件缘起：整改通知 #09 —— ③「0.875 对间铜边净空不可达」被误升 owner；根因 = 把**工程换算定值**当**需求**冻结
> （需求 = R3-2「3W 原则」= 对间不串扰；0.875 = 按错误线宽 0.4375 的换算结果）。

## §1 规矩
- **R1 需求冻结**：需求 = 目的/原则（如 R3-2 3W：对间中心距 ≥ 3×线宽）。只可 owner 变更。
- **R2 实现迭代**：实现 = 定值/几何/派生式。在工程内自裁迭代（L2），**不得升 owner**。
- **R3 定值溯源**：任何工程定值必须记录 ① 来源原则 id ② 派生式 ③ 输入 ④ 可达性（闭式/确定性）。
- **R4 禁止混同**：派生值不得作为需求冻结；需求条目不得携带定值。
- **R5 机判**：`tools/p3_v57_co124_input_selfcheck_gate.py` **K9**（+ 负控 T5/T6/T7）逐条校验本件台账。

## §2 本板需求
| id | 需求（目的/原则） | 来源 | 冻结 |
|---|---|---|---|
| `REQ-R3-2` | 对间不串扰 ⇒ **3W 原则**：对间中心距 ≥ 3×线宽 w | `_shared/docs/PCB_DESIGN_RULES.md` R3-2（目的层） | 是 |

## §3 本板实现（派生值，工程内迭代）
台账（机读、逐值可溯）：`L2/derived_value_ledger_v1.json` → `derived_values[]`。
- `DV-INTPAIR-EDGE`：**edge_min(layer) = 2×w(layer)**（⇔ center ≥ 3w）。按层：外层 0.410 / 内层 0.320；
  带内下界（w_min=0.09）⇒ 0.18（可行性用最有利界）。
- `DV-ENGINE-INT_PAIR_PITCH`：容量/新布线对中心距 1.46（= 0.585 + 0.875 的旧口径；本件保留为**保守实现**，≥ 忠实下界
  0.995）——几何口径不动。

## §4 被取代的定值（退役留存，不销毁）
| 值 | 来源 | 为何非忠实实现 |
|---|---|---|
| `0.875` | R3-2 旧换算（`_shared/docs/PCB_DESIGN_RULES.md` 表内定值「5×线距」/ 2×0.4375） | legacy 换算定值：0.875 = 2×0.4375（等价 5×0.175 线距）；本板 w_by_layer={'F.Cu': 0.205, 'In2.Cu': 0.16, 'In5.Cu': 0.16, 'B.Cu': 0.205} 与带内 w_min=0.09 均无 0.4375 ⇒ 非 REQ-R3-2 的忠实实现 |

## §5 可达性与板实
- **可达性（闭式）**：REACHABLE —— 域外：pitch_cap 0.355+0.41=0.765；
  WEST 1.05 ✓ / EAST 1.449 ✓；焊盘场（cap 0.6）属
  **ECN-001 escape_transition_zone**（已声明放宽 0.075）⇒ 非该原则适用域。
- **板实（实测，见 CO-134 记录 `as_built`）**：域外偏差 1 处（显式登记为工程开放项，路由 = SI/板厂券 或后续几何迭代）。
