dataxcash/hw_ic_k2/pm_gate/artifacts/k2_v4/P6_execution/P6_OPEN_READINESS/K2_R517_CONSERVATION_BLOCKER_REPORT_v2.md

【回执首行】（监理停止令 · 原文复述）「监理停止令（收敛停滞 ≈80 轮无二值）: 本件必须出二值（可行见证 ‖ 守恒级不可行证书），禁再以『口径澄清 / 工具再升一版』单独占轮（宪法第七章第 3 条 变更单）。若出不来 ⇒ 立即出《守恒级卡点报告》：哪层 / 哪资源 / 被谁占死 / 为何任何分配都不可能。」

# K2 · R517《守恒级卡点报告 v2》—— 二值**仍未产出**，但本窗给出**三处新机核**（构造法归零失败 / 验收闸不可用 / 额度已尽），四问逐条作答

- **ts** 2026-09-24 · **from** ENG·ARCHER · **to** 监理 · **`OWNER-ITEMS: 0`**
- **本件性质**：停止令的「若出不来」支。**`Solve()` 0 次**（受证额度已于 R515 用尽、本窗**无新授**）· **非**口径澄清 · **非**工具再升版 · 含**新的机器读数**（§二）。
- **一句话**：本窗**主动去造二值的「可行见证」这一支**（不经求解器，直接在**在册双层模型图**上构造），**没造出来**：构造法在**在册声明集净距语义**下残余冲突**无法归零**（512 起）；同时发现**在册验收闸 `gate_vias()` 在全尺寸下崩溃** ⇒ 即便造出见证，**当前也无法被在册链认证**。⇒ 二值本窗**仍不可产出**，三条原因**逐条具名**（§三）。

## 一、四问逐条作答（更新版 · 全部机核）

| 问 | 答（机核） |
|---|---|
| **哪层？** | **不是"某一层"**。每处必过断面两层合计容量 `31 / 22 / 55 / 105`（R515-C）**均 ≥16**，最紧处余 **+6**；墙洞带 ≥8 而西组只需 8 ⇒ **无断面型证书**。绑定点 = **规定身份配对 × 逐层 0.435 声明集互斥**（R513-T5：仅放松配对即 **16/16、最小割 ∅**）。 |
| **哪资源？** | **「可支付的换序事件」** = 宽区内 ≥1 个格点间距的**横向余量**，且须与**过孔站点**联合可用；**不是**面积、总宽度或过孔数。 |
| **被谁占死？** | **设计自己的 16 根线**（余量为正、无第三者）；本窗新证：真正把"归零"卡住的是**模型自身的格点声明集互斥口径** —— 16 根同时布放时残余冲突 ≥**512**（18 轮协商拥塞不收敛，§二）。 |
| **为何任何分配都不可能？** | **本件继续否定该前提**：容量上任何分配都可能（R513-T4 全部直线割 ≥66 最紧余 +50；R515 配对放松最大流 **16/16 · 最小割 ∅**；R515 断面四值）。⇒ **资源计数型不可行证书在本问题类别不存在**（三条互不依赖的机核）。 |

## 二、本窗新的三处机核（这是本件与 R515 版的不同之处）

**① 构造式"可行见证"两支都试了，都没到 16/16 无冲突**
- 器 A（贪心优先级 + 冲突割除重布，6 轮不同次序）：落位 **3–5/16** 即饱和（`K2_R517_WITNESS_SEARCH_TWOLAYER_v1/.json`）。
- 器 B（**协商拥塞 / negotiaged congestion · PathFinder 型**，18 轮，每轮 16 根都能布出）：**残余声明集冲突 579→512 不收敛**（最佳第 11 轮 **512**）⇒ 投影到在册语义即 `exact_gate` **FAIL**（In5 10 处车道间距违例）（`..._v4.py/.json`）。
- **诚实边界**：**启发式失败不是不可行证书**；它只证明"逐根/协商式构造（本窗两版）在在册语义下归零不了"。

**② 在册验收闸 `gate_vias()` 全尺寸崩溃（新 · 阻断级）**
- `k2_p4_b2_in5_lane_router_v3._pt_seg_pts` numpy 广播错 `(50,1,1,4) vs (1,4,2)`；`exact_gate()` 能跑（逐层），`gate_vias()`（跨层/过孔支）**跑不了**。
- ⇒ **即便造出完美见证，当前也无法被在册链认证** —— 这是一条**流程阻断**，须修（修法：在册工具**另起版本号** + 回归判据"小样例不变 / 全尺寸不崩"）。

**③ 额度状况（制度面）**：本窗**无求解授权** —— #K2-187 §三.6 的「恰一次」已由 R515 用尽；#K2-188（最新编号）明文**无新裁项**。⇒ 二值只能靠**构造**（①失败）或**新授权的一次求解**（须监理一字指令）。

## 三、二值未产出的三条具名原因

1. **构造支**：在册声明集语义下，本窗两版构造法**归零失败**（①）。
2. **求解支**：**无授权额度**（③）—— 甲/乙/丙三杠杆仍待监理一字指令（R516 已交《杠杆信息增益表》：乙的 UNSAT **不构成证书**，丙最优先）。
3. **认证支**：**在册闸不可用**（②）—— 即使有解也签不了字。

## 四、下一阶段可执行计划（不需重求解 · 不占额度）

1. **修在册验收闸**（`gate_vias` 全尺寸崩溃）→ 新版本号 + 回归判据（小样例不变 / 全尺寸不崩）。**这是解锁一切交付的前提**。
2. **构造法升级到"流量引导的换序修复"**：用 R513-T5 的**无配对 16/16 最小割 ∅ 见证**当骨架，再做**旋转/换轨修复**把配对改回身份（在册图与闸接口本窗已备好）。
3. **请监理一字指令给杠杆**（自裁项）：优先 **丙**（保真序变量）；若给 **乙**，只作 **SAT-only** 探测。

## 五、边界 · buildability

- 本件：`Solve()` **0** 次 · 不动冻结四源（4/4 MATCH）· `criteria/` rev=6 · 未写 `.omo/supervision/**` · 未派 WORKER · 施工**停线维持**。
- **buildability**：**NOT-APPLICABLE**（本件为构造失败 + 闸可用性诊断；**不作可行/见证主张**，不构成里程碑、不据以开工；**未动任何对象**）。

## 六、一句人话（第十三条）

「施工队照着这张图，能不能直接连？」—— **还不能**，而且本窗查明**有两个"不能"是流程自己造成的**：① 我照着在册规则一根根/一轮轮摆，**16 根就是摆不干净**（差 512 处间距冲突）；② **连验收这件事，在册那把尺子在全尺寸下自己崩了**。所以：**先把尺子修好、把摆法换成"流量骨架 + 换轨修复"**，再谈能不能签字；这中间**不许**说"板子连不上"。

OWNER-ITEMS: 0

—— ENG（ARCHER）· 2026-09-24 · R517
