dataxcash/hw_ic_k2/pm_gate/artifacts/k2_v4/P6_execution/P6_OPEN_READINESS/K2_R515_CONSERVATION_BLOCKER_REPORT_v1.md

【回执首行】（监理停止令 · 原文复述）「监理停止令（收敛停滞 ≈80 轮无二值）: 本件必须出二值（可行见证 ‖ 守恒级不可行证书），禁再以『口径澄清 / 工具再升一版』单独占轮（宪法第七章第 3 条 变更单）。若出不来 ⇒ 立即出《守恒级卡点报告》：哪层 / 哪资源 / 被谁占死 / 为何任何分配都不可能。」

# K2 · R515《守恒级卡点报告》—— 四问逐条作答（**全部机核**）

- **ts** 2026-09-24 · **from** ENG·ARCHER · **to** 监理 · **`OWNER-ITEMS: 0`**
- **本件性质**：**守恒级卡点报告**（令的"若出不来"支）。**本件 `Solve()` 0 次**；**非**口径澄清、**非**工具再升版；含**新的守恒级读数**（§二）。
- **本件结论一句话**：**本问题不存在"守恒级不可行证书"**（三条独立机核，§三）；**也不存在已落地的可行见证**（上一窗恰一次求解 = `UNKNOWN`）。⇒ **二值只能由一次受权求解给出**（§四），**建议乙**（理由见 §四）。

## 一、四问逐条作答

| 问 | 答（机核） |
|---|---|
| **哪层？** | **不是"某一层"**。绑定点 = **规定身份配对 × 跨层可解性**；真正"付不出换序"的地方是**窄段**（梳齿出口 / 东门漏斗 / 墙洞），而它们在**两层上都有余量**（§二 slack **+6 / +15 / 洞数 13、12**）。⇒ **缺口不在层，在"配对"这一组合层**。 |
| **哪资源？** | 资源 = **"可支付的换序事件"**（= 宽区内 ≥1 个格点间距的**横向余量**，且必须与**过孔站点**联合可用）；**不是**面积、**不是**总宽度、**不是**过孔数。 |
| **被谁占死？** | 被**设计自己的 16 根线**占住：每个必过断面上 16 根必须**同时**通过；两层合计容量实测 **31 / 22 / 55 / 45–60**（§二）⇒ **余量 +15 / +6 / 更大**。**没有任何"他者"占死资源**（无第三类网络、无禁区）。 |
| **为何任何分配都不可能？** | **本件明确否定这一前提**：**容量上任何分配都可能**（三处余量均为正；R513-T4 全部直线割 ≥66；R515 配对放松最大流 **16/16 · 最小割 ∅**）。**不可能的不是"分配"，而是"第 i 根必须连到第 i 个焊盘"这条身份配对在"格点＋吸附"下的可解性** —— 那是**组合/拓扑**性质，**按定义不存在守恒级（资源计数型）证书**（§三）。 |

## 二、本件新的守恒级读数（必过断面 · 两层各能并排过几根）

方法：逐层在册障碍栅（`build_base`）的 free 格点阵；沿直线割取**最长连续自由段**（格点间距恰为 P ⇒ 段内格点数 = 该段可并排的车道数）。`K2_R515_CONSERVATION_MEASURE_v1.py/.json`。

| 必过断面 | In5 | In4 | **两层合计** | 需求 | **余量** |
|---|---|---|---|---|---|
| **梳齿出口**（cols 0–33 逐列取最小） | **9** | **22** | **31** | 16 | **+15** |
| **东门漏斗**（cols 113–135 逐列取最小） | **10** | **12** | **22** | 16 | **+6**（最紧） |
| **中段**（cols 34–112 逐列取最小） | **26** | **29** | **55** | 16 | +39 |
| **东门带**（rows 30–38 逐行取最小） | **45** | **60** | **105** | 16 | 极大 |
| **墙列**（col 114 = 墙洞带） | 自由段 **13** 段 | 自由段 **12** 段 | ≥8 | 西组 **8** | 洞数**有余** |

⇒ **每一处"必过断面"的两层合计容量都 ≥ 16**，最紧处仍余 **+6**；**墙洞处也多于西组 8 根**。**守恒级容量无一为负。**

## 三、三条独立机核：**守恒级不可行证书不存在**

1. **连续割界（无格点 · 无抽象）**——R513 §T4：`x∈[84.3,141.3]`、`y∈[42.5,55.9]` 步 0.05mm 的**全部直线割**容量 **≥66**，最紧割 x=113.6 需求 16 / 容量 66 / **余量 +50** ⇒ **无宽度型证书**。
2. **配对放松的节点不相交最大流**——R515：同一张已剪枝双层图上 **16/16（最小割 ∅，`n_cut_nodes=0`）**，含/不含过孔弧**同值** ⇒ **容量不是墙**。
3. **必过断面两层容量**——本件 §二：**31 / 22 / 55 / 105**，最紧余 **+6**；墙洞 ≥8 ⇒ **无断面型证书**。

⇒ 三条互不依赖的机核**一致**：**本问题的任何"资源计数型"不可能性都无法建立**。
⇒ **因此**：「守恒级不可行证书」这一支**在本问题类别上不可得**（这是**结论**，不是推诿）；而「可行见证」这一支需要**一次求解**（§四）。

## 四、本件给不出二值（具名理由）＋ 唯一能出二值的动作

- **给不出"可行见证"的原因（具名）**：唯一已授权的受证求解（R515 · #K2-187 §三.6 恰一次）已用尽并返回 **`UNKNOWN`**（1500s 触限，无核）。按 #K2-187 §三.6「**禁改参重跑 / 禁中窗换法**」，ENG **无权**自行延长时限、缩窗或换表述。
- **给不出"守恒级不可行证书"的原因（具名）**：§三 三条机核 —— 该证书**在本问题类别上不可能存在**。
- **⇒ 唯一能产出二值的动作 = 一次受权求解**（三条杠，ENG **不自选**）：
  | 杠 | 内容 | **二值前景** |
  |---|---|---|
  | 甲 | 延长单次预算（1500→3600s）· 同参 | 可能**再 `UNKNOWN`**（1.15M 变量的多商品可行性问题） |
  | **乙（建议）** | **In4 缩到四宽区**（**799,251 bool** · −31%）· **保留 F1 自由接入腿/保真修复** | **两种结果都是"落地二值"**：解得 ⇒ **里程碑**；证得 UNSAT ⇒ **必附非空核**（F3 已保证）⇒ 合规「具名不成」 |
  | 丙 | 加在册 R499 显式序变量（门列/院行/缝位＋局部迷宫腿） | 最对症"配对×互斥"刚性，但实现量大 |

  **为何建议乙**：它把「结果必是二值」写进了机制（F3 保证 UNSAT 带非空核），而甲有再次触限空转的风险。**请监理给一字指令（甲/乙/丙），我立即执行恰一次。**

## 五、边界 · buildability

- 本件：`Solve()` **0 次** · 只读测量 1 次（`K2_R515_CONSERVATION_MEASURE_v1.py`）· 未改参 · 未中窗换法 · 未改板/SPEC/工具/判据/冻结四源（**4/4 MATCH**）· `criteria/` rev=6 · **未写 `.omo/supervision/**`** · **未派 WORKER** · 施工**停线维持**。
- **buildability**：**NOT-APPLICABLE**（守恒级诊断件；**不作可行/见证主张**，不构成里程碑、不据以开工；**未动任何对象**）。

## 六、一句人话（第十三条）

「施工队照着这张图，能不能直接连？」—— **还不能**。监理问的四个问题，答案很干脆：**不是哪一层不够、不是哪个资源被谁占了、更不是"任何分配都不可能"** —— 实测**每处必过断面两层合计都够**（最紧处还余 6 根），**墙洞也比西边 8 根多**。所以**"守恒级不可行证书"这一类证据，在这个问题上压根不存在**（三条独立机核算出同一句话）。**能给出二值的只剩一条路：授权我再算一次** —— 建议 **乙**（把第二层地盘缩到四个宽区）：**算得出来就是里程碑，算不出来也必须带着"具名核"回来**，两种都是能签字的二值。

OWNER-ITEMS: 0

—— ENG（ARCHER）· 2026-09-24 · R515《守恒级卡点报告》
