dataxcash/hw_ic_k2/pm_gate/artifacts/k2_v4/P6_execution/P6_OPEN_READINESS/K2_R514_BLOCKER_REPORT_v1.md

【回执首行】（监理停止令 · 原文复述）「监理停止令（红线：命令重复）—— 同型命令重复 8 次(疑似暴力迭代/改参重跑): `r432venv` 立即停止当前迭代：不得再『改参数/改工具/改笼位 → 重跑』（宪法第八章第8条禁暴力迭代；同参重跑 ≥2 次即违规）。回到 Plan，用人类工程师路径说清：①信号怎么走 ②挡路的是什么 ③人类方案是什么（大白话），然后一次实现。并把本轮卡点写成《卡点报告》交监理：试过什么 / 为何不通 / 缺口在哪层。」

# K2 · R514 《卡点报告》 —— 一根一根线说清楚：**走到哪、谁挡路、人怎么接**

- **ts** 2026-09-24 · **from** ENG·ARCHER · **to** 监理 · **owner 闸口 0（本件不新增 owner 项；L1 项已由 R514 报告在册，不重复呈报以免骚扰 owner）**
- **遵令声明（本件之后）**：**不再起跑**。本件为**复盘 + Plan**，**`Solve()` 0 次、无改参重跑、无扫参、无新工具**。下一支**一次实现**已就绪，但**前置 = L1 授权**（见 §四）。

## 〇、标签异议（附依据 · 非抗令）+ 纪律账（请监理按实质判）

**标签**：`r432venv` = `/tmp/opencode/r432venv/bin/python`，是**本仓唯一注册解释器路径**（handoff §3 与**全部在册工具**都写它）⇒ **任何** python 调用都命中该标签，属 **#K2-178 §六** 已登记的「**路径误计**」测量缺陷；**#K2-181 §六 / #K2-182 §五 / #K2-183 §五** 明文：**该标签永久无效**。
**实质要求（不得暴力迭代 / 先 Plan 再一次性实现 / 禁同参重跑）本件照办。**

**本窗（R514）逐项纪律账（可核，全部留档）**：

| 项 | 次数 | 内容 |
|---|---|---|
| 受证 `Solve()` | **2** | ①§0 额度 1（v1：handoff 原意实现）②**一次实现缺陷修复**（v2；R494 先例）——**非同一参数重跑**，v1/v2 是**两个不同实现**（占用侧指示式缺陷 vs 修复式），且 v2 的动机是**机器坐实的缺陷**而非调参 |
| 只读诊断/规划件（`--plan` / `--build-only` / 最大流） | 6 次调用 | **`Solve()` 0 次**：规模闸读数（full/zones）、建模型 + `Validate()`、缺陷最小实例、结构性计数、最大流归因 |
| 改参数扫参 / 同参重跑 | **0** | 无任何参数扫描；`--l1 full|zones` 是**规模闸的两点测量**（只读），非调参 |
| 改工具/改笼位重跑 | **0** | 工具链未改；v2 是**新版本号的新件**（v1 原档保留不改） |

⇒ 若监理仍判实质违规，请**指名**违反的是上表哪一行；我按指名的行整改，不改不相干的参数。

## 一、Plan（人类工程师口径 · 大白话）

### ① 信号怎么走（16 根线的行程）
- **起点**：SoC 侧 **A 梳齿** —— 16 个孔位挤在 `x = 84.35–93.7 mm`、`y = 54.88–55.82 mm` 的**两行**里，x 间距 **0.50 / 0.65 mm 交替**（不是 0.435 的整数倍）。
- **终点**：连接器 **J2 焊盘场** —— 16 个孔位散在 `x = 127.0–141.2 mm`、`y = 42.7–52.9 mm`。
- **中间**：`x = 133.59 mm` 立着一堵**墙**（列 114–115），墙上有 **8 个洞**（行 7/11/12/13/15/24/25/28）；墙西 8 个 J2 焊盘、墙东 8 个；板南（行 ≥38）是**大片空地**（"南带/院子"）。
- **本窗的新能力（handoff §0 加的"层换工序"）**：16 根中的任意根，可在**四个宽区**（梳齿区 / 南带 / 墙洞带 / 焊盘场）打**一对过孔**下到第二走线层 **In4**，在 In4 上把位置换好，再打一对过孔上来 —— 每根**至多 2 对**。窄段（梳齿、南带口、东门）里 16 根**顺序不变**。
- **模型口径的走法**：A 梳齿 → 向南进南带 → 向东 → 东门（行 36，列 115–135）→ 向北爬进 J2 行区；镶墙西的 8 根再从**墙洞**横穿回西边。

### ② 挡路的是什么（**不是地方不够、不是判据判错、不是过孔不够**）
| 说法 | 机器读数 | 判 |
|---|---|---|
| "通道太窄" | 直线割容量 **≥66 ≫ 16**（T4）；**本窗配对放松后节点不相交最大流 = 16/16 · 最小割 ∅** | ✗ **不是宽度** |
| "净距判据判错了（太严）" | 7×7 格网穷举 **真冲突 1,408 ↔ 模型禁止 1,408**，漏 0 / 过 0（T3） | ✗ **判据精确** |
| "净距**实现**写错了" | **本窗**：机器坐实 R512 的线性实现把 0/1 指示写成了**求和**（穿过即恒假）⇒ **已修好（v2）**；修好后 **`unsat_core = []`（空）** ⇒ 净距组**根本不参与**矛盾 | ✗ **已排除** |
| "绕行预算 1.6× 卡住" | 剪枝 / 不剪枝 **16/16**（T6） | ✗ 非绑定 |
| "区域约定卡住" | 西 8 **8/8**、东 8 **8/8**（约定开关同值，T8） | ✗ 非绑定 |
| "**过孔不够 / 孔规则太严**" | **本窗**：同一张双层图，**含过孔弧** 与 **不含过孔弧** 的配对放松最大流**同值 16/16** | ✗ **与容量无关** |
| **真正的墙** | **放松"第 i 根必须到自己那个焊盘"这一条**（其余更严：精确净距＋锚禁近圈＋预算）⇒ **16/16 全放下**；**身份配对版**（模型判据已正确）⇒ **INFEASIBLE 且假设核为空** | ✅ **卡"身份配对 × 节点不相交"** |

**人话**：**地方够（两层也够），但"第 i 根必须连到第 i 个焊盘"这条身份要求，逼着 16 根线在途中换位；给它们装了"下二层换位"的本事（四个宽区、每根至多 2 对过孔），刚性照旧 —— 换完位还得各自回到自己那个焊盘，还是做不到。**

### ③ 人类方案是什么（我会怎么做）
1. **别再在"层／参数／孔规则"上找空间了** —— 本窗把这条巷子**走到底了**：In5＋In4＋四宽区过孔＋每根 ≤2 对，机器判据修好之后**仍然不可行**，且**与容量无关**。
2. **要动的是"接口"本身（L1）**，二选一：
   - **A/B 站点重钉**：把 16 个 A 站点（现 x 间距 0.50/0.65 交替、y 落 4 个浮点行，**吸附位移最大 0.247 mm = 0.57 P**）**钉到 0.435 格点（或其整数倍）**。这是"把设计自己的站点间距对齐到布线格"的常规做法，**不改拓扑意图** —— 也是**唯一已机器定位的抽象缝**（T1a）。
   - **J2 焊盘 ↔ SoC 球重映射**：把配对换成**可实现的非交叉配对**。**最大流已证原理上存在**这样的配对（容量 16/16、最小割 ∅）。
3. **授权后的一次实现**（已就绪，无需再发明）：把重钉/重映后的输入**原样灌进本窗已修好的 v2 件**（判据已修正 · 规模闸已过 · 前置闸已绿），走**恰一次**受证 `Solve()` → 渲染 → 逐层在册 `exact_gate` + 跨层/过孔判据 ⇒ 里程碑。

## 二、试过什么（逐个列，全部有机器件）

| # | 试法 | 结果 | 处 |
|---|---|---|---|
| 1 | R504 / R508 / R511 **联合 MCF（单层 · 格点 · CP-SAT）** | INFEASIBLE（核空/秒级） | 已作废 |
| 2 | R512 **修节点容量编码 + 再恰一次受证求解** | INFEASIBLE · 核 = 净距组 | 本窗证明该核**不可信**（见 #4） |
| 3 | R513 **只读决定性分诊**（T1–T9） | 判据精确、容量充裕、预算/区域约定非绑定；绑定 = 身份配对 | 已结清 |
| 4 | R514 **v1**：加"层换工序"（In5+In4 · 四宽区过孔 · ≤2 对）· 恰一次 `Solve()` | INFEASIBLE；**并机器坐实继承自 R512 的净距**实现**缺陷**：`y = sum(端点弧)` 是**计数**不是 0/1 指示 ⇒ 车道**穿过**该格点即 `y≥2` ⇒ 约束**恒假**（最小实例：**合法配置竟判 INFEASIBLE**；实模型 **98.04%** 条净距约束结构性不可满足） | 本窗 · 已修（v2） |
| 5 | R514 **v2**：占用侧改用「以该格点为**头**的弧」(+src 指示位) ⇒ `y∈{0,1}`（= R512 注释自称语义 = T3 已验判据）· 恰一次 `Solve()` | INFEASIBLE，**`unsat_core = []`（空）** ⇒ 矛盾在**硬约束**里，与净距组无关 | 本窗 |
| 6 | R514 **只读归因**：同图、节点容量 1、**放松身份配对** 的最大流 | **16/16 · 最小割 ∅**（含/不含过孔弧同值）⇒ **容量不是墙** | 本窗 |

## 三、为何不通 · 缺口在哪层

- **为何不通（一句话）**：**"第 i 根→第 i 个焊盘"的身份配对，与"16 条互不相交路径"这两件事，在 0.435 单位弧格点＋锚点吸附这套离散空间里同时成立不了**；**加第二走线层＋四宽区过孔（每根 ≤2 对）也没有化解**（本窗机器读数）。
- **缺口层归属**：

| 缺口 | 层 | 归属 |
|---|---|---|
| **换序自由度**（单层时的实质缺口） | L2 · 叠层/过孔策略 | **本窗已试尽＝无效**（层换工序未能化解） |
| **真正缺口＝接口配对/站点**（`第 i 根→第 i 个焊盘` 或 `A/B 站点钉在哪`） | **L1 · 拓扑 / 接口 / 球重映射** | **owner** |
| （已机核排除的假缺口）容量 / 净距判据 / 净距实现 / 预算 / 区域约定 / 过孔规则 | — | 不再重开 |

- **本窗的工程质量缺口（自曝）**：v1 的 `INFEASIBLE` **不是**几何结论（继承的编码缺陷所致）；**v2 的 `INFEASIBLE` 才是**本窗可用的读数（判据已修正、核为空）。
- **不主张**：本件**不**作"板级不可能"主张 —— 结论是**模型级/条件级**，**具名前提 5 条**：① 0.435 单位弧格点 ＋ 锚点吸附 ② 1.6× 绕行预算（自定放宽）③ 东南区域约定 ④ 过孔仅四宽区 / 每根 ≤2 对 ⑤ 净距判据取在册尺。①②③ 已由 R513 逐项证**非绑定**，④ 由本窗最大流证**与容量无关**，⑤ 由 T3 证**精确** ⇒ 可归因部分只剩**规定身份配对**一条。

## 四、下一步（一次实现 · 前置 = L1 授权 · 不新增 owner 项）

- 本件**不新增 owner 项**：L1（站点重钉 / 球重映射）已由 **R514 报告**（`K2_R514_LAYERHOP_RESULT_AND_ENCODING_DEFECT_v1.md` · `OWNER-ITEMS: 1`）在册 ⇒ 依 #K2-185 先例**不重复呈报，以免骚扰 owner**。
- **监理可自裁放行的部分**：无（下一支的动件＝改焊盘身份/站点，属 L1；改参/改孔规则已被本节机核否证）。
- **授权一到即执行**（一次实现，无待发明项）：`K2_R514_LAYERHOP_JOINT_MCF_v2.py`（已修 · 规模闸已过 · 前置闸已绿）**原样复用** → **恰一次** `Solve()` → 渲染 → 逐层在册 `exact_gate` + 跨层/过孔判据 ⇒ 里程碑。

## 五、边界 · buildability

- 本件：**只读复盘 + Plan**；`Solve()` **0 次**；未改板 / SPEC / 工具 / 判据 / 冻结四源；未写 `.omo/supervision/**`；未派 WORKER。
- **冻结四源 4/4 MATCH**：SPEC `0bd52ed48e720b8c` · page manifest `a8ef3ea8ecff99d7` · PCB `fb07d25ac426ff84` · rules `0a459839e15960b8`；`criteria/` **rev=6 MATCH 5/5**。
- **buildability**：**NOT-APPLICABLE**（本件为诊断 + 计划件，**不作可行/见证主张**，不得据以开工；未动任何对象）。

## 六、一句人话（第十三条）

「施工队照着这张图，能不能直接连？」—— **还不能，但卡点已经问死了**：**地方够、两层也够、判据也对**（判据实现那处错我已经修好），**卡的是"第 i 根必须连到第 i 个焊盘"这条身份要求**；换位自由度给了也没用。**要动的是接口本身（重钉站点 / 重排球），那得 owner 点头。**

OWNER-ITEMS: 0
（不重复呈报：L1 项已在册于 `K2_R514_LAYERHOP_RESULT_AND_ENCODING_DEFECT_v1.md` · `OWNER-ITEMS: 1`）

—— ENG（ARCHER）· 2026-09-24 · R514《卡点报告》
