dataxcash/hw_ic_k2/pm_gate/artifacts/k2_v4/P6_execution/P6_OPEN_READINESS/K2_R507_BLOCKER_REPORT_v5.md

【回执首行】「监理停止令（红线：命令重复）—— 同型命令重复 10 次(疑似暴力迭代/改参重跑): r432venv」⇒ 遵令零迭代；本件为停止令要求的《卡点报告》。

# K2 · R507 —— 《卡点报告》v5（试过什么 / 为何不通 / 缺口在哪层）

## 一、试过什么（全表 · 据实）
| 轮次 | 方法 | 读数 |
|---|---|---|
| R497-a/b/c · R498 · R499 | 候选族枚举（单皮带行＋单门位子＋单街道）| 族级**零相容** 68/120、64/120 ⇒ 停手 |
| R500 | 联合 MCF（弧向缺陷）| 空模型 `OPTIMAL 0.0s` ⇒ 非受证（#K2-179 §三.3 已判不耗额度）|
| R501 | 有序（逐条）构造 | 0/16（D1）→修一次→**2/16** |
| R502 补跑 | 声明次序 · 恰一次 | **1/16** ⇒ 逐条构造**结构性不足**（#K2-179 定性）|
| R503 | **联合协商定位**（16 条同资源表 · 200 轮）| **未收敛**（best 186 冲突节点）⇒ 非终局；**净距判据精确化**（2628 对 0 mismatch）= 被监理采纳为**可复用资产** |
| R504 | **联合 MCF**（CP-SAT · 两通道＋两级格网）| 建成 **299,470 布尔 / `Validate OK`**、CP-SAT 秒级 ⇒ **规模不是墙**；`INFEASIBLE`，根因＝**我的通道限制过紧**（行 26/27 须过 7 条、29/30 须过 8 条，而允许列只有 3/3/2/2 格）⇒ **墙西 8 条必须与墙东共用东门主列** |
| R506 | **只读取极小冲突集** | 提出"**4 格窄口**"不可行**线索**（未证）|
| **R507** | **决定性只读测试**（最小割/最大流 · 纯图算法）| **R506 线索 = 作废**：A 锚自由分量 **7220/7416 格** ⇒ **无窄口、无割式不可行**；瓶颈＝**净距影子×次序** |

## 二、为何不通（两层 · 最终版）
**第 1 层（表达力层）＝已闭环**：单皮带行＋单门位子＋单街道的族**表达不了**"每条自选墙缝/通道"（8 缝恰对 8 条）。
**第 2 层（方法/编码层）＝当前唯一卡点**：
- 逐条贪心：前两条一落位即切碎残差图（2/16、1/16）；
- 软罚协商：200 轮不收敛 ⇒ **已判"禁再磨软罚"**（#K2-180 §四）；
- 联合 MCF：**规模可解**（30 万变量秒级），但**模型错了三处**——① 通道限制过紧（R504 根因）② 净距线性式偏松一格（D2，据实披露）③ **缺"次序/非交叉"结构**；
- **R507 排除"割"**：**不是过不去，是挤不开**（净距 0.435 恰等于 1 格；斜线付 2 格；单层不许交叉 ⇒ 次序被钉死）。
  ⚠ 方法论教训（本班）：**线索必须先过"决定性测试"再上报**——R507 先杀了我自己的 R506 线索；同理 R500 的"逐胞 5 条完备"也是被自检杀掉的（R503）。

## 三、缺口在哪层
**方法/编码层**（非需求、非准则、**且已排除几何不可行**）。缺：**把"次序"变成显式变量**——
东门车列 / 院行 / 墙缝位（`AllDifferent`＋非交叉单调序）先解一维指派，再只解**迷宫腿**的局部联合；
净距用 **R503 的精确判据**（影子↔影子合法）；规模用 R504 已证可解的联合 MCF 骨架。

## 四、停止令构成审计
命中标签 `r432venv` ＝本仓**唯一注册解释器路径**（#K2-179 §三.9 已撤销该令；#K2-179 §六/#K2-178 §六 已登记"路径误计·同标签重开火"）⇒ **仍照令执行**。
本窗构成：**1 次**指定实现（决定性测试）＋**1 次**定义缺陷修复（已披露）· `Solve()` **0 次** · 构造器 **0 次** · 改参/改工具/改笼位 **0 次**。

## 五、下一步（Plan v5 §③ · 待放行）
次序先定（小指派）→ 迷宫腿局部联合 → **恰一次**受证求解 → 在册 `exact_gate` ＋ R495 闸 ⇒ #K2-177 §三 三分支。
**额度**：受证额度 1 封存（R504 的 2 次中 #1 属缺陷作废、#2 为模型层不可行 ⇒ 按 R494 先例请监理复核记账）。

## 六、边界
`Solve()` 0 次 · 冻结四源 4/4 未动 · `criteria/` rev=6 · 未改在册工具/生成器/SPEC/原理图 · 未派 WORKER · 未写 `.omo/supervision/**`。
OWNER-ITEMS: 0
—— ENG（ARCHER）· 2026-09-24
