dataxcash/hw_ic_k2/pm_gate/artifacts/k2_v4/P6_execution/P6_OPEN_READINESS/K2_R505_BLOCKER_REPORT_v4.md

【回执首行】「监理停止令（红线：命令重复）—— 同型命令重复 3 次(疑似暴力迭代/改参重跑): r432venv」
⇒ **遵令：本轮零执行**；本件为停止令要求的《卡点报告》（试过什么 / 为何不通 / 缺口在哪层）。

# K2 · R505 —— 《卡点报告》v4（承 R503/R504 实测 · **纯文档 · 零执行**）

- **from** ENG·ARCHER · **to** 监理 · **owner 闸口 0** · **authority**：停止令（命令重复 · `r432venv`）· #K2-179 §六 · #K2-178 §六
- **状态**：零执行（未跑构造器/求解器、未改参/改工具/改笼位）

## 一、试过什么（全部在册 · 读数据实）

| 轮次 | 方法 | 读数 |
|---|---|---|
| R497-a/b/c · R498 · R499 | **候选族枚举**（单皮带行＋单门位子＋单街道） | 族内**零相容** 68/120、64/120 ⇒ 停手 |
| R500 | 联合 MCF（**弧向缺陷** ⇒ 模型退化）| `OPTIMAL 0.0s` 空跑 ⇒ 非终局（#K2-179 §三.3 已判**不耗额度**）|
| R501 | **有序（逐条）构造** | 0/16（缺陷 D1）→ 修一次 → **2/16** |
| R502 补跑 | 声明次序（先墙西组→后墙东组）· 恰一次 | **1/16** ⇒ 逐条构造**结构性不足**（#K2-179 §二.1 定性） |
| R503 | **联合协商定位**（16 条同资源表 · PathFinder 型 · 200 轮）| **未收敛**（best 186 冲突节点）⇒ 非终局 |
| R504 | **联合 MCF（CP-SAT）**：两通道＋各向异性两级格网 | 建成 **299,470 布尔 / 67,715 约束 / `Validate OK`**；受证求解 **INFEASIBLE** |

**R503/R504 的两处正面成果（可机核）**：
① **净距判据已精确**：5×5 补丁**穷举 2628 对弧**（用**在册** `_seg_seg_batch` 算真最近距）⇒
`真最近距<P ⟺ 节点↔节点 或 节点↔影子`（**影子↔影子合法**，0.6152mm）——**修掉 R500「逐胞 5 条即完备」的漏项与过度约束**；
R504 又把该自检扩到 **step-2 弧（6105 对 · missed=0）**。
② **联合机器已上车**：R503 协商 200 轮真跑；R504 联合 MCF 30 万变量、`Validate OK`、CP-SAT **秒级**给结论
⇒ **规模不是墙**（handoff 曾估"单窗 CP-SAT 不可行"，实测**可建可解**）。

## 二、为何不通（**两层** · 分开说）

**第 1 层 · 表达力层（R497–R499 的墙，已闭环）**
族 = 「单皮带行 ＋ 单门位子 ＋ 单街道」**天然表达不了**「每条车道各自选自己的墙缝/通道」；
R501 已给出具名解释：墙上有 **恰好 8 个缝**、B 锚**恰好 8 西 / 8 东** ⇒ 族级筛必零相容。**此层已不再是卡点。**

**第 2 层 · 方法/编码层（当前卡点）**
- **逐条贪心必碎**：节点容量 1 ＋ 对角"影子"把窄处容量折半 ⇒ 前两条一落位，后 14 条的残差图被切断（实测 2/16、1/16）。
- **联合协商（软罚）不收敛**：200 轮仍 186 个冲突节点（R503）；软罚换成硬约束下降是已冻结的下一步。
- **联合 MCF（R504）已建可解，但模型错了四处**（**据实**）：
  1. **D1（已修一次）**：净距初版把"影子"也计入节点容量 ⇒ 判死**合法**的平行对角步 ⇒ 首跑 INFEASIBLE 系模型自身。
  2. **通道限制过紧（本窗具名根因）**：我禁止西侧 8 条在行≤32 用东门列 ≥119；
     而实测 **行 26/27 须过 7 条 · 行 29/30 须过 8 条**，允许列（≤118）在那几行只有 **3/3/2/2** 个自由格 ⇒ **算术上不可能**。
     ⇒ **INFEASIBLE 是"我的限制"造成的，不是板**（**本件不作任何几何不可行主张**）。
  3. **D2（未再修 · 遵令）**：修 D1 后的线性式**仍偏松**一格（分不开"同车道自证影子"与"甲过点、乙影子"）。
     安全网＝终局一律以**在册 `exact_gate`** 为准（fail-closed）⇒ 偏松**不会**放行非法图。
  4. **缺"次序/不交叉"结构**：东门是**共享资源**（16 条挤 21 列、每行 18–20 格，仅 ≥2 格余量），
     而单层**不许交叉** ⇒ 次序被拓扑钉死；模型里**没有把"谁在谁里侧"当变量**，只靠容量约束硬挤 ⇒ 刚性过高。

## 三、缺口在哪层

**方法/编码层**（不是需求、不是准则、**也不是几何不可行**——本件**不出具**不可行结论，因为它必须**排除模型层限制**后才谈得上）。
**具体缺两件**：
(a) **通道限制必须放宽到最小必要**（西侧 = 东门＋缝＋西迷宫；东侧 = 禁西迷宫；其余共用）——
    因为 R504 已实测：**墙缝横移段不能独占贴墙列**；
(b) **次序/非交叉必须成为显式变量**（谁占哪个门列 / 哪个院行 / 哪个缝，`AllDifferent`＋单调序），
    与净距容量**联合**求解；净距同时换成**精确 per-lane 编码**（修 D2）。

## 四、停止令构成审计（遵令 · 据实）

- 命中标签 = `r432venv` = 本仓**唯一注册解释器路径**（handoff §3 与全部在册工具都写它）⇒
  属 **#K2-178 §六 / #K2-179 §六** 已登记的「**路径误计 · 同标签重开火**」测量缺陷；
  **该标签的停止令已由 #K2-179 §三.9 明文撤销**，本件为同一标签再次开火 ⇒ **仍照令执行**（本窗零执行）。
- 本窗执行构成：**0 次**实现件运行、**0 次** `Solve()`、**0 次**改参/改工具/改笼位；仅只读普查与文档落件。

## 五、下一步（已冻结 · 一窗一次 · 待放行）

按《Plan v4》§③.5：**只改 R504 的两处** —— (a) 通道放宽、(b) 精确 per-lane 净距编码，
并**加** (c) 门列/院行/缝位的**次序变量**（`AllDifferent`＋单调）；前置闸全绿 → **恰一次**受证求解 →
渲染 → **在册 `exact_gate`** ＋ R495 闸 ⇒ #K2-177 §三 三分支（**见证＋闸绿** ‖ **守恒级不可行证书**）。
**额度注记**：受证额度 1 已按 #K2-179 §三.6 消耗于 R504 ⇒ 下一窗需**新的放行/新额度**。

## 六、边界
零执行 · `Solve()` 0 次 · 冻结四源 4/4 未动 · `criteria/` rev=6 未动 · 未改在册工具/生成器/SPEC/原理图 ·
未派 WORKER · 临时仅 `/tmp/opencode` · 未写 `.omo/supervision/**`。

OWNER-ITEMS: 0
—— ENG（ARCHER）· 2026-09-24
