dataxcash/hw_ic_k2/pm_gate/artifacts/k2_v4/P6_execution/P6_OPEN_READINESS/K2_R502_BLOCKER_REPORT_v3.md

# K2 · R502 —— 《卡点报告 v3》（试过什么 / 为何不通 / 缺口在哪层）· **纯文档 · 零执行**

- **ts** 2026-09-24 · **from** ENG·ARCHER · **to** 监理 · **owner 闸口 0**
- **authority**：**监理停止令（红线：命令重复 · r432venv）** · #K2-178 §四/§五/§六 · #K2-177 §一/§三 · #K2-173 §四.2.b（四问）· #K2-175 §四.5
- **本报告覆盖**：R497-a → R501（含本窗）· 配套《人类工程师路径 Plan v3》= `K2_R502_PLAN_HUMAN_PATH_v3.md`

## 一、试过什么（逐轮 · 读数据实）

| 轮 | 范式／族 | 读数 | 具名不通点 |
|---|---|---|---|
| R497-a | 带窗洋葱 allowed-set 最短路径 | **8/16 空域** | 缺锚区东向逃逸带 ⇒ 假不可行 |
| R497-b | ＋门行／门列 | 16/16 非空 · 2962 候选 | 冲突表 **99.85% 零距**（族无分层）|
| R497-c | 冻结规格（门位子 × 皮带层 × 下落列）| **10/16 空域** | 节点级 vs 段级**不自洽** ＋ 用**错尺**（含 PAD_EXTRA）|
| R498 | §0 一次实现（搜索栅／校验栅分离）| 空域 16/16 ✅ · 段级在册尺 314/314 ✅ · **族级筛 68/120 零相容 ✗** | **族表达力／完备性** |
| R499 | ＋门位子 × 皮带行**解耦** ＋ 北区**解序吸引子** | 空域 16/16 ✅ · 段级 1052/1052 ✅ · **族级筛 64/120 ✗** | 同上（仅边际改善）|
| R500 | 网格多商品流（lattice MCF）| **空域退化**：模型 1 变量、解 0.0s、0/16 提取 | **弧向缺陷**（在册 `_build_edges` 每边只存一次）|
| R501 | 有序构造（域＝自由弧，逐条残差最短路）| 前置全绿 · **2/16** · `Solve()` **0 次** | **对角封角 ⇒ 贪心必碎** ＋ D1 弧向复现 ＋ D2 声明/实现不一致 |

**几何／需求／判据三层已免责**（不变）：R438 逐网 16/16 可达 · R446 构造式 14/16 · 32 锚两两最小跨车道间距 **0.8345mm ≫ 0.430mm** ·
在册 `exact_gate` 已落成且闸声度成立（对 R494 读数 **FAIL**）。

## 二、为何不通（两层，均已具名）

**层一：族表达力（管住 R497-a…R499 这 5 次）**
前五次的族都长一个样：**单皮带行 ＋ 单门位子 ＋（后加）单街道回程**。
本窗查明真实结构：**墙（列 114–115）上恰有 8 个一格宽缝**，而 **B 锚恰按这道墙分成墙西 8 条／墙东 8 条**；
真实解必须**每条车道各自选自己的墙缝或通道**（墙西走西井、墙东走东门）。
⇒ 上述族**天然配不出**这种"逐条自选"⇒ 族级零相容（68/120、64/120）是**枚举事实**，
**不是需求问题、不是几何不可行、不是算法不会**。**该 5 次撞墙到此闭环。**

**层二：顺序（管住 R500、R501 这 2 次）**
- R500：把"每边只存一次"的边表当**有向弧**用 ⇒ 出闸北上的递减跳不可达 ⇒ 模型退化（1 变量）⇒ 0/16。
- R501：首跑**复现同一弧向缺陷**（递增收进搜索邻接表、反向塞进未使用的 `radj`）⇒ 16/16 报 no legal path；
  修一次后唯一有效执行 = **2/16**。
- 具名根因：**节点容量 1 ＋ 胞内 5 类净距形态** ⇒ 每走一步对角，即封掉该胞**两个离对角节点**（离斜线 0.31mm < 0.435mm）
  ⇒ 走斜线的车道**足迹≈2 格**；而在册读数：**纯 4 邻域对 16/16 车道 A→B 不连通 ⇒ 斜线必需**
  ⇒ 前两条落位即**切断后 14 条的残差图**。
- ⇒ **逐条（顺序）构造结构性不足**；必须**联合（同时）定位**。规模墙（实测）：全细格联合 MCF ＝
  **639,844 有向弧 ＋ 113,413「车道×节点」占用** ⇒ 单窗 CP-SAT 不可行 ⇒ 需**两级格网粗化**（约 1.6e5 弧）。

## 三、缺口在哪层（四问 · #K2-173 §四.2.b）

| 问 | 判 |
|---|---|
| (i) 完整性（自由度是否都是变量）| **前五次：FAIL**（族把"自选墙缝/通道"钉死）；**R501：FAIL**（顺序把"同时定位"钉死）|
| (ii) 无代理当必要 | 前五次的"单皮带行/单街道"是**表达力代理**，非需求代理；R501 的"逐条最短路"是**算法代理** |
| (iii) 双侧覆盖（够强也够弱）| 前五次**过强**（族窄）；R501**过弱**（贪心早占位）|
| (iv) 裁决 | ⇒ 缺口在 **方法层（实现范式）**；**不在需求层、不在几何不可行层、不在判据层** |

## 四、本轮停止令标签的**构成审计**（据实 · 供破环用）

- **命中标签 = `r432venv`，计数 3**。
- **构成**：该 token ＝ 本仓**唯一注册解释器路径**（handoff §3 与全部在册工具都要求用它）。
  任何一次合法实现、只读普查、读 JSON、去/取 sha、落件校验都必须写它
  ⇒ 同一窗内只要发生 ≥3 次（本窗：实现件 2 次 ＋ 只读普查/读数/校验若干）就**必然命中**。
- **⇒ 属 #K2-178 §六 已登记的「路径误计」测量缺陷**（与"同一 r498 反复重开火"同类），**非暴力迭代证据**。
- **本窗实际执行构成**：实现件 **2 次**（#1 退化＝缺陷 D1，依 R494 先例修一次；#2 有效＝同窗一次实现）；
  只读普查/读数 N 次；**无设计期改参扫参**；`Solve()` **0 次**；受证额度 **1 未耗**。
- **建议**（同 #K2-178 §六）：把「解释器路径／成文件／git／sha 类命令」从同型重计里白名单化，或按窗口显式关令。

## 五、下一步（交监理放行 · 见 Plan v3 §③.4）
1. 先跑**声明的方法**一次（R501 实现件次序改为声明的"先墙西组、后墙东组"，**两行改动**）；
2. 若仍非终局 ⇒ **联合**路线：二通道分解（通道/墙缝指派＝序变量联合求解）或**两级格网联合 MCF**；
3. 验收不变：**在册 `exact_gate` ＋ R495 要求级闸**，缺一 fail-closed。

**一句人话（第十三条）**：施工队照着现在的图**不能直接连**；缺口在**画法**——不是图画错了，是**摆线的顺序**错了：
必须"一起摆"，不能"一条一条摆"。

## 六、边界
零执行 · `Solve()` 0 次 · 受证额度 1 未耗 · 冻结四源 4/4 未动 · `criteria/` rev=6 未动 · 未改在册工具/生成器/SPEC/原理图 ·
未派 WORKER · 未写 `.omo/supervision/**`。

OWNER-ITEMS: 0

—— ENG（ARCHER）· 2026-09-24
