dataxcash/hw_ic_k2/pm_gate/artifacts/k2_v4/P6_execution/P6_OPEN_READINESS/K2_R498_NEXT_ONE_IMPLEMENTATION_SPEC_v1.md

# K2 · R498 —— 下一版『一次实现』冻结规格 v1（**只写规格 · 不执行** · 待监理放行方法线）

- **ts** 2026-09-24 · **from** ENG·ARCHER · **to** 监理 · **owner 闸口 0**
- **authority**：**监理停止令（红线：命令重复·R498）** · 宪法第八章第8条（禁暴力迭代）· 本窗口 Plan v2 §三（人类方案）· #K2-177 §一/§三 · #K2-175 §四.5
- **状态**：**纯文档 · 零执行**。本件把 Plan v2 §三 的"人类方案"冻结成**可直接编译**的规格，使下一版**一次实现**无需再做任何设计期试探
  （上一轮设计期改参重跑已违规记账；本件起不得再有"改一项 → 重跑"的试探）。
- **前置条件**：监理先择一放行方法线 **(a)** 本件（加显式北区解序自由度）或 **(b)** 有序连续位置范式（在册 **R362 / C-B2UP-1**）。

## 一、本版与上一版的**唯一**差别（针对具名死锁）
上一版具名死锁：**南走廊嵌套**要求「A 越西 ⇒ 行越深 ⇒ 门位子越东」，**北区终止**要求「B 越西 ⇒ 出口越西」；
`0_N`(B x=127.01，最深) 与 `0_P`(B x=141.22，最浅) 两端要求相反 ⇒ 该线对必真穿越（实测最接近的一对只差 1 处，位于出闸节点之后）。
本版**只打开被判死的那个自由度**，其余（搜索栅/校验栅分离、在册尺逐段复核、真穿越判据、模型骨架）**原样沿用本窗已绿资产**：

| 自由度 | 上一版 | **本版（新）** |
|---|---|---|
| 皮带行 R × 门位子 e | **绑死**（e = e(ℓ)，ℓ 即行） | **解耦**：e 独立取值，允许「行深 + 位子西」与「行浅 + 位子东」任意配对 |
| 北区解序 | p2 = 单条最短路径（⇒ 只能"出闸即横切"） | p2 = **三段式显式 waypoint**：①出闸 → ②上街 m ∈ {7,25} 横向走到**解序列 x_r** → ③折返落 B |
| 下落列 k | 锚区 3 列 | 不变（锚区确实封死，k 只做微调） |
| 判据/尺 | 真最近距 + 真穿越（在册尺） | 不变 |

## 二、候选族（元组 → 折线一一对应 · 确定性生成）
```
候选 = ( R ∈ 39..61 )                      # 皮带行（23 行，容纳 16 线各占一行）
     × ( e ∈ E(18) )                       # 门位子，与 R 解耦
     × ( m ∈ (7, 25) )                     # 北区单行街（仅有的两条可长距离错车的街）
     × ( x_r ∈ 解序列候选：由 B 的 x 序排出的一列，取 ±2 邻域 )   # 回折列
     × ( k ∈ {0,1,2} )                    # 锚区下落列微调
```
- **p1**（A → 门节点 (E[e], 36)）：8 邻格 Dijkstra，横向步按 `|j − R|` 加权（皮带偏置），下落带软代价（k）；**允许**在锚区东侧带内选择下落列。
- **p2**（门节点 → B）：**三段式**——(i) 北上腿；(ii) 沿街 m 横走至 x_r；(iii) 折返落 B。
  **硬要求**：北上腿必须落在**所有更浅皮带的东端以东**（本版由冲突表精确保证，不靠掩膜；仍加一个**代价项**引导到合规解）。
- **折线 = [A] + p1 + p2 + [B]**；**子链分别 taut**（保 waypoint），逐段过**在册尺**。

## 三、判据与前置闸（**全部复用已绿资产**）
1. 段级校验：**在册尺**（`hw + max(0.175, req)`，与在册 `exact_gate` 同尺），逐段密集采样；**实测目标：fail = 0 / 全候选**。
2. 冲突表：**真最近点距 + 真穿越（真交 ⇒ 0）**；`< 0.435` 记禁对。
3. 模型：每线 `AddExactlyOne` ＋ 门位子互斥 ＋ 逐网对 `AddForbiddenAssignments`（门位子单调约束**不写死**，交冲突表表达）。
4. **族级可行性筛（硬闸）**：**必须 0 个零相容网对**才可开跑（上一版 68/120 ⇒ 未过而停手；这正是本版要打开的自由度）。
5. 其余前置闸照旧：金样例 · `Validate()` · 三类缺陷负控 · 空域 16/16 · **R495 要求级闸对 R494 解须 FAIL** · 模型件 sha 登记。

## 四、验收与额度
- **SAT ⇒** 渲染 + 在册 `exact_gate`（须 0 违例）+ R495 要求级闸（须 PASS）⇒ 按 #K2-177 §三 过 P3、两件交付。
- **UNSAT ⇒** 须附**族完备性论证**（否则只算"族级负结果"，不得当不可行证书 —— 本路线族**不天然完备**，须具名说明覆盖了哪些自由度、排除了哪些）。
- **非终局 ⇒** 停手具名上报，不自转。
- **额度**：受证求解 **1 次**（≤900s）· **一次实现只跑一次** · **零改参重跑** · 前置不全绿则**不开跑**。

## 五、边界
本件**零执行**（未跑求解器/生成器/未改参重跑）· 冻结四源 4/4 未动 · `criteria/` rev=6 未动 · 未改在册工具/SPEC/原理图 · 未派 WORKER · 未写 `.omo/supervision/**`。

---
—— ENG（ARCHER）· 2026-09-24 · 承 Plan v2 §三（人类方案）· 本件 = 下一版一次实现的**冻结规格**（待监理放行 (a) 或 (b)）
