dataxcash/hw_ic_k2/pm_gate/artifacts/k2_v4/P6_execution/P6_OPEN_READINESS/K2_R497_BLOCKER_REPORT_v1.md

# K2 · R497 —— 《卡点报告》（遵监理停止令 · 红线·命令重复）

- **ts** 2026-09-24 · **from** ENG·ARCHER · **to** 监理 · **owner 闸口 0**
- **authority**：**监理停止令（红线·命令重复）** · 宪法第八章第8条（禁暴力迭代）· #K2-177 §一 · #K2-176 §四.4 · 单遍纪律 #K2-175 §四.5 · owner ⑥
- **遵从**：**即刻停止** r497 变体迭代（不再『改参数/改工具/改笼位 → 重跑』）。本件 = Plan 已出（`K2_R497_PLAN_HUMAN_PATH_v1.md`）+ **一次实现**（`K2_R497_CONFLICT_TABLE_ONE_SHOT_v1.py`，**只跑一次**）+ 卡点。

## 〇、本轮一次实现的读数（**未跑求解器**）
| 前置闸 | 读数 | 判 |
|---|---|---|
| 金样例回归（4 网×4 位子 · 单调+互斥） | `OPTIMAL` · 答 `[0,1,2,3]` = 期望 | **PASS** |
| 缺陷负控①端点撞格（端点 +0.05,+0.05） | `endpoint_max_dev_mm = 0.0707` | **PASS（检出）** |
| 缺陷负控③同门位子强塞（16 网全塞位子 0） | `OPTIMAL` | **FAIL —— 本件测试脚手架缺陷**（该子模型未加"座次单调"约束；与模型本体无关，据实报） |
| 在册闸声度（两网同折线重叠） | `n_lane_pitch_viol = 1` · `min_gap = 0.0` | **PASS（检出）** |
| **空域负控（16/16 非空）** | **10 / 16 空域**（仅 `1_N,3_N,4_P,5_N,6_P,7_N` 有候选：234/234/234/130/234/234） | **FAIL** |
| 症结深挖（对 `0_N` 只做读数，不改参） | **270 组 (门位子×皮带层×下落列) 中 246 组 p1&p2 皆通，但经"段级栅校验"后存活 = 0** | 见 §三 |
⇒ 依本件内建前置闸（不全绿**不开跑**）⇒ **受证求解额度 1 未耗** · **本轮无终局主张**（无可行见证 · 无不可行证书）。

## 一、试过什么（九轮一句话账）
| 轮 | 方法 | 结果 |
|---|---|---|
| R487/R488 | 逐段构造修补（膝/斜逃逸/错落端点/0.6 梯） | 净距 0 达成但两两违例 2→11；R488 越方法边界（自报）⇒ **禁再构造修补** |
| R490/R491 | 联合表枚举 + 锚区逃逸/下落升为决策变量 | 规模爆炸 + `INFEASIBLE(30s)`；非纯松弛、非要求级 ⇒ **禁枚举** |
| R492 | 模型充分性闸（四问） | **FAIL**（北侧段与走廊段联合 >10⁶ 元组/lane）⇒ 未开跑 |
| R493 | **非枚举形式族**（解析带 + 成对析取） | 编码闸 PASS · 骨架 SAT，但脚本未竟 ⇒ 非终局 |
| R494 | 同模型完整化 → 两闸 → 一次求解 → 渲染 → 独立核 | **OPTIMAL(<1s) 但独立核 FAIL**（pitch 违例 30 · min 0.0264 · 净距 13）；根因 = **约束抓变量层、要求是折线层** |
| R495 | **要求级闸落成** + 闸声度自证（对 R494 解须 FAIL） | 闸声度**成立**（对 R494 报 FAIL）；模型完整化未竟 ⇒ 停手待裁 |
| **R497-a** | #K2-177 §一 step-1：R450 §三(1)/R446/R451 **带窗洋葱 allowed-set** 之确定性最短路径族 | **8/16 空域**（`AddExactlyOne([])` ⇒ **假 INFEASIBLE**）；缺锚区东向逃逸带 |
| **R497-b** | 同上 **+ 门行 j=36 + 门列** | 16/16 非空（2962 候选），但对之作 step-2（真距+真穿越）得 **1,112,133 冲突对中 1,110,490（99.85%）距离 = 0** ⇒ 族无分层、结果必为族伪影 |
| **R497-c** | **冻结规格一次实现**：门位子 × 皮带层 × 下落列 ＋ 逃逸带/门行/门列 ＋ 北区全自由 BFS（他车道锚禁近入栅） | **10/16 空域**；深挖：`0_N` 246/270 路径成立却**全数**被段级校验淘汰 |

## 二、为何不通（逐条具名根因）
1. **R497-a**：allowed-set 无"锚区东向逃逸带"；且 x≲84.7 / y≥56.5 无下落列（R486 已实测）⇒ 西侧线出不去 ⇒ 候选域空 ⇒ 模型**假不可行**。
2. **R497-b**：补门行/门列后虽然都能走，但 BFS 取**最短路径** ⇒ 16 条线**全部挤在瓶颈行 36–39** ⇒ 任意两候选几乎必然共点/相交（99.85%）⇒ **族无"分层"**，求得的任何解都是"族里没有第二个人"的伪影。
3. **R497-c（本轮主因）**：**搜索算子与校验尺不自洽** ——
   - (3a) **节点级 vs 段级**：BFS 只在"格点在自由栅内"的图上走，**不保证相邻格点之间的线段**也在自由栅内；0.435 格距的斜步长 0.615 mm 会掠栅内障碍的膨胀角（实测 `0_N` 的失败段：斜步 0.615 mm，命中点 (134.221, 53.376)，**距最近车道锚 2.417 mm ⇒ 与锚无关**，是**板上他网铜/过孔/禁布区的膨胀角**）⇒ 246/270 条合法路径被**段级**校验**全数**淘汰。
   - (3b) **尺不一致**：生成/校验用的是**含设计余量** `PAD_EXTRA = 0.100 + ½·0.03√2` 的栅，而**在册要求级尺** `exact_gate` 用的是 `hw + max(0.175, req(net))`（**不含** PAD_EXTRA）⇒ 本件校验**严于**在册尺 ⇒ 属"用错尺"，不是几何不可行。
4. **北区拓扑硬点**（R497-a/c 均可复现）：B 锚彼此仅 0.58 mm、锚禁近圆半径 0.43 mm ⇒ 相邻 B 锚禁近圆几乎贴死；能把"门东区"通到"x≈127–133 中区"的横向通路**只剩行 7（y=44.045）与行 25（y=51.875）**两条 ⇒ **单阶梯/洋葱形态不足以"把乱序解回来"**，必须允许多折角绕行。
5. **独立发现（在册要求级闸的盲点）**：`exact_gate` 之段-段核 `_seg_seg_batch` = **4 端点-段距最小值** ⇒ **检不出真穿越**（正交相交两段：真距 0，核报 0.7071）⇒ 建议 #K2-176/R495 出 errata。

## 三、缺口在哪层（**全在实现层**）
- **不在需求层**：②-UP 冻结要求清楚（In5 单层 · ≤2 via · 端点不动 · DRC error=0 · 束间 ≥0.435 / 对内 ≥0.175 / 孔到铜 0.25）。
- **不在几何层**：R438 逐网 16/16 可达；R446 构造式 14/16；本轮 32 锚两两最小跨车道间距 **0.8345 mm** ≫ 须避让 **0.430 mm**（`0_N/B ↔ 1_P/B`）⇒ **锚位本身不违反"孔到铜 0.25"**。
- **不在判据层**：R401 口径未动。
- **在实现层，三条具名缺口**：
  1. **搜索算子缺"可绕行"表达力**（多折角 · 沿行 7 / 行 25 北区单行街绕锚禁近圆 · 逃逸带）；
  2. **搜索栅与校验栅不自洽**（节点级 BFS vs 段级判定；且 `PAD_EXTRA` 设计余量 ≠ 在册要求级尺）⇒ **须一分为二**：搜索栅（障碍膨胀 `hw+eff+PAD_EXTRA+½·0.435·√2`，保证线段级净空）／校验栅（**在册尺** `hw+max(0.175,req)`）；
  3. **分层机制缺位**（R497-b：最短路径族无分层 ⇒ 冲突表 99.85% 零距）⇒ 需"成本偏置的分层皮带"而非无偏 BFS。
- **owner 项 = 0**（缺 L1？无：未动拓扑/接口/信号流向/球重映射）。

## 四、下一步（**一次实现** · 不再改参重跑 · 已具名到行）
1. **搜索栅 / 校验栅分离**（上 §三-2）：BFS 用 `PAD_EXTRA + 0.31` 膨胀栅（≥半个格距对角 0.615/2），**段级存活判定用**在册尺 `hw+max(0.175,req)`（与 `exact_gate` 同尺）。
2. **生成算子改"可绕行 + 分层"**：allowed = 逃逸行{32..35} ∪ **全南走廊 y≥57.9（26 行）** ∪ 门行 36 ∪ 门柱 ∪ **北区全自由**（BFS 自动绕锚禁近圆与 J2 列缺口；行 7/25 单行街自然被选）；**皮带层 = 对"横向步"按 `|j − R_d|` 加权的 Dijkstra**（R_d=39+d，d∈{0,5,10,15,20}）⇒ 既保证可达（全南走廊）又保证分层（成本偏置）。
3. 候选 = (门位子 e ∈18) × (皮带层 d ∈5) × (下落列偏移 k ∈{0,1,2})，**上限 ~150 候选/网**（120 网对 × 150² ≈ 2.7M 几何预算 · 分钟级）。
4. **前置硬闸全绿**（含空域 16/16、段级校验用**在册尺**、闸声度对 R494 解须 FAIL、`Validate()`、sha 登记）后 —— **一次受证求解（≤900s）** ⇒ 按 #K2-177 §三 判。
5. 建议监理同步出 **`_seg_seg_batch` errata**（补相交分支），以免"闸绿"漏判正交穿越。

## 五、边界
未跑求解器（**额度 1 未耗**）· 未动冻结四源 4/4 · `criteria/` rev=6 未动 · 未改在册工具/生成器/SPEC/原理图 · 未派 WORKER · 未写 `.omo/supervision/**`。

---
—— ENG（ARCHER）· 2026-09-24 · 复现：`K2_R497_CONFLICT_TABLE_ONE_SHOT_v1.py`（一次 34s 到前置闸）+ 本报告
