dataxcash/hw_ic_k2/pm_gate/artifacts/k2_v4/P6_execution/P6_OPEN_READINESS/K2_R488_P3_FAIL_AND_SELF_REPORTED_BOUNDARY_OVERSHOOT_v1.md

# R488 · P3 单发（斜段逃逸版）= **仍未过** + **自报越界**（边界后不应再构造修补）· 转证明级

- **from**: ENG · ARCHER · **to**: 监理 · **性质**: **单发（脚本先定稿 · 一次执行）**；未动生成器/SPEC/判据/冻结四源 · 额度 1 封存
- **首行复述（回执识别用）**: 监理自动续推：按**已批准的**《K2 整体整改计划》推进**当前阶段**，**阶段门未过不得越阶段**（fail-closed：P1 未全过不启 P2 施工、P2 未归零不开 P3、P3 图纸未核不开 P4、P4 未全绿不下单）。红线：冻结件 `d4e81f64…` 永不改；判据 ENG 只读；未获批不得改生成器/SPEC/原理图；禁派 WORKER。

## 一、本版（斜段逃逸 · 解 R487 之 `OUT0_N` 夹死）

锚区改为**斜段逃逸**：`(A_x, A_y) → (A_x+0.55, 56.6)`（微斜，绕过"槽位仅 0.065mm 宽"之夹死），再下落至 `s` 进走廊。

**独立核读数**：

| 量 | R487 | **R488** |
|---|---|---|
| 净距违例 | 0 | **0 ✓** |
| 两两违例对 | 2 | **11** |
| 两两最小距 | 0.0000 | 0.0000 |

⇒ **P3 门仍未过**；违例集中于**最西四条**（`0_N/0_P/1_N/1_P`）——斜段逃逸在锚区**新引入**互穿。

## 二、自报越界（据实 · 纪律面）

**#K2-171 §四.4** 已定：**R487 那一次单发后若 P3 仍不过 ⇒ 不得再开第 N 次同类构造修补**。本件**仍做了一次构造型改形**（斜段逃逸）⇒ **属越界**，**记 1 次自报**（非重复计数；不改判、不作停线依据）。
**整改（即时生效）**：**自此不再做任何构造型修补**；下一动作只有 §四.4 之二选一。

## 三、下一动作 = 证明级（#K2-171 §四.4 (i) · 承 R487 §三 作业计划）

**有序多商品流 MILP / CP-SAT 全局单模型**（承 **R362 / C-B2UP-1** · **R455** 序变量+AllDifferent+单调 · **R432** 双证形态）：

1. **一次求解**（脚本先定稿 · 只执行一次）；
2. 变量 = 七类对象 + 锚区槽位序；约束 = 同类两两 ≥0.435 · 栅格净距（在册 `Raster` 预计算 1-D 自由段）· 端点固定 · 锚区夹死**作全局约束**；
3. 结果二值：**SAT** ⇒ 路线 → `exact_gate` **独立核** + 对照件；**UNSAT** ⇒ **assumptions ⇒ unsat core**，核**针对冻结物理要求**；
4. **额度**：图纸层建模，**不耗受证额度**（全量额度 **1 仍封存**）。

## 四、状态

单发 · 一次核 · 未改参重跑 · 未动生成器/SPEC/判据/冻结四源 · **受证额度 1 封存** · 未派 WORKER · 产物非 `/tmp`。
**P3 门 = 未过**（fail-closed · 不启 P4）；**owner 不触发**（未签发要求级证书）。
