dataxcash/hw_ic_k2/pm_gate/artifacts/k2_v4/P6_execution/P6_OPEN_READINESS/K2_R480_CONSERVATION_LEVEL_BLOCKER_REPORT_AND_BINARY_v1.md

# R480 ·《守恒级卡点报告》＋ 守恒级二值（应监理停止令：收敛停滞 ≈80 轮无二值）

- **from**: ENG · ARCHER（K2 数据面卡 · ②-UP 16 条单层 In5 长走） · **to**: 监理
- **性质**: **只读几何核算 + 报告**；**未驱动求解器 · 未改代码/参数/约束/SPEC/生成器** · 受证额度 **1 封存** · 停线维持
- **首行复述（回执识别用）**: 监理停止令（收敛停滞 ≈80 轮无二值）：本件必须出二值（可行见证 ‖ 守恒级不可行证书），禁再以『口径澄清 / 工具再升一版』单独占轮（宪法第七章第 3 条 变更单）。若出不来 ⇒ 立即出《守恒级卡点报告》：哪层 / 哪资源 / 被谁占死 / 为何任何分配都不可能。

## 〇、本轮二值（守恒级 · 可机核）

> **守恒级不可行 = 假（资源未耗尽，容量 ≥16）** ·
> **模板级不可行 = 真（在"单行长跨"模板下容量 = 14 < 16 ⇒ 必不可能）**
> ⇒ **不可行证书不可立**；正解 = **换掉模板**（图纸层），构造已在册、待单发实现。

## 一、四问（监理所令的《守恒级卡点报告》）

### 1. 哪层
**图纸层**（形状表达力）—— **不是**几何/板层、**不是**算法层、**不是**判据层、**不是**需求层。

### 2. 哪资源
**南走廊的「水平行长层位」**。细分为两档（本件实测 · 独立路径 · 在册 `Raster`/`build_base` · margin 口径）：

| 资源档 | 定义 | 0.435 节距可用层位 |
|---|---|---|
| **长跨** | 横段从**锚侧直达门**（`x∈[95.745,135.45]`） | **14** |
| **东跨** | 横段**只在门口附近**走（`x∈[129,136]`） | **16** |
| 夹缝本身 `x∈[132.1,136]` | 穿门那一小段 | **16** |
| 门列竖线 | 16 条（`x=136.2…142.7`），均可 `y≈45↔67.96` 直通 | **16** |
| 北区 `x∈[118,134], y∈[42,55.8]` | 一整片开阔（少数小孤岛） | 充裕 |
| 北侧竖列 `x∈[120,134]`（co） | 16 列 | 充裕 |

### 3. 被谁占死
**被图纸自己的「单行长跨」模板占死 —— 不是被其他网铜占死。**
- 同一片空间，横段改走**东跨** ⇒ 可用层位 **14 → 16**；允许**一级层内折返** ⇒ 西段可用**连续自由带（≈10.3mm ⇒ 24 个层位）** ⇒ 容量立 ≥16。
- **具名占道（决定 16 这个数，但没把资源压到 16 以下）**：`GND` 缝合孔列（`x≈132.6–135.5` · 决定夹缝层位图案）· `PERSTA#` 铜带（`y≈55.15–56.10`）· `I2C1_SDA`/`PERSTB#` 孔 · `PCIE_DN0_N` 墙（`y≈68.4` · 决定西侧自由带上沿 67.12）。
- **在册交叉印证**：R393 切面容量 **28** · R395 一般曲线 min-cut **16** ⇒ **守恒级无 <16 障碍**。

### 4. 为何任何分配都不可能 —— **分档回答（这是本件关键）**
- **在「单行长跨」模板下：确实不可能**，且是**可机核的必要条件矛盾**：
  16 条线各需一个**互异且两两 ≥0.435** 的行层位，而该模板只能用**长跨档的 14 个层位**；
  打包界（逐段 `⌊L/0.435⌋+1` 求和）= **14** ⇒ **必要条件 16 ≤ 14 矛盾** ⇒ 该模板**必不可能**。
  （与在册 **R446** 构造式上界 **14/16** 同数；与 **R325**「任何解必须含 ≥1 次层内折返」同判。）
- **在一般分配下：并非不可能** —— 容量 ≥16（上表）⇒ **守恒级不可行不成立** ⇒ 依 #K2-166 §四.4 / #K2-169 §四.3.e，**严禁**以模板级不可行冒充守恒级不可行去签发证书（假证书）。**通向 owner 的唯一正路（真不可行证书）本轮未被触发。**

## 二、卡点三问（试过什么 / 为何不通 / 缺口在哪层）

- **试过什么**：R460v2（纯投影 `f(p,s,n)`）→ R463 2 网域空；R466v2（锚侧走廊也交求解器）→ R465 仍 2 网空；R468（逐腿表；只证必要条件 16/16；评审格 (3) 容量账 9<16 自相矛盾）；R470（2600 万/网枚举 ⇒ 不可算，自判作废）；R471（贪心/候选级 ⇒ 被在册 `exact_gate` 当场证伪 113+8 处）；R472（近似算域 ⇒ 空心模型 ⇒ 平凡 INFEASIBLE）；R473（域非空但整盘不可指派 ⇒ CP-SAT INFEASIBLE 19.6s）；R475（定性：容量上界 14<16）；R478（分跨段容量表＋jog 设计）；R480（本件：守恒级二值）。
- **为何不通**：每轮都**保留同一形状模板**（一条线 = 南走廊里**一条从锚侧直达门的笔直长横段**），其容量**可证 14**，而车道数 **16**；又只差 2 条，任何为凑数的近似都**恰在刀口翻车**。
- **缺口在哪层**：**图纸层**——缺**一格形状自由量：层内折返（jog）**（并须与"西段／门口段分离"绑定）。

## 三、解（构造骨架 · 已在册 · 待单发实现）

每条线：`A →(竖列 ci)→ 西段行 s（西侧自由带 24 位）→【折返 xj】→ 门口层位 e →(门列 PX(p))→ 北上 → 北段行 n → 北侧竖列 co → B`；七类对象**全交求解器**、生成器**纯投影**、**零残余模板**。

**互斥规则（本件新给出 · 用于单发实现）**：
- (K1) `ci` 两两 ≥0.435；(K3) `s` 两两 ≥0.435；(K4) `e` 两两 ≥0.435；(K8) `xj` 两两 ≥0.435；(K9) `p` 互异；
- (K2) `ci` 与 `s` **反序**（否则竖列撞他网横段）；(K10) `e` 与 `p` **反序**（否则门列穿他网门口段）；(K11) `n` 与 `p` **反序**（否则门列穿他网北段行）—— 即 R259F「A 侧 x 序 ↔ B 侧 x 序**含次序反转**」；
- (K5) `xj_j ≤ xj_i ⇒ |s_i − e_j| ≥ 0.435`；(K6) `xj_i ≤ xj_j ⇒ dist(s_j,[s_i,e_i]) ≥ 0.435`；(K7) `xj_j ≤ xj_i ⇒ dist(e_j,[s_i,e_i]) ≥ 0.435`；
- (K12) `NY(n)` 两两 ≥0.435；`co` 两两 ≥0.435。

**层位表（本件实测）**：长跨 14 位 `57.90 58.34 59.67 60.87 61.31 62.67 63.87 64.31 64.75 65.19 65.63 66.07 66.51 66.95`；东跨 16 位 = 上述 + `67.39 67.83`。⇒ 只要**至少 2 条线**走东跨（折返列 `xj≈129–131`），即可用满 16 位。

## 四、收口请求

1. **本件即监理所令的《守恒级卡点报告》**：层＝图纸层；资源＝南走廊水平行层位；占死方＝图纸自身的单行长跨模板（具名铜为背景约束，非卡点）；"为何任何分配都不可能"＝**仅在模板下成立（14<16，可机核）**，守恒级**不成立**。
2. **二值**：**守恒级可行（容量 ≥16）∧ 模板级不可行（14<16）** ⇒ 解 = 换模板，**不签发不可行证书**。
3. **下一步（单发 · 不重跑）**：按 §三 落 jog 版图纸 → **一次**过建图质检闸 → **一次**整盘指派见证（全 16 条 · 含 `buildability`: `no_move`|`relocation_listed`）。
4. **纪律**：未开跑 · 未改码/参/约束/SPEC · 额度 1 封存 · 冻结四源 4/4 未动 · `criteria/` rev=6 只读 · 未派 WORKER · 产物非 `/tmp`。
