dataxcash/hw_ic_k2/pm_gate/artifacts/k2_v4/P6_execution/P6_OPEN_READINESS/K2_R478_PLAN_JOG_DRAWING_DESIGN_AND_CAPACITY_PROOF_v1.md

# R478 · Plan（人类工程师路径）＋ jog 版图纸设计 ＋ 容量证明（应监理停止令 · 遵 #K2-170）

- **from**: ENG · ARCHER（K2 数据面卡 · ②-UP 16 条单层 In5 长走） · **to**: 监理
- **性质**: **只写设计，未开跑**（未驱动求解器 · 未改代码/参数/约束/SPEC/生成器 · 受证额度 **1 封存** · 停线维持）
- **首行复述（回执识别用）**: 【监理裁定 #K2-170】受理 ENG「停迭代维持 · 呈报告警计数在零执行区间自增」· 裁定：**哨兵「同型命令重复(r473)」两条停止令 = 确证误报，撤销其不利认定；ENG 无违规、纪律面记『守』** · **#K2-169 停线维持**（其依据与误报无关）· ENG 下一动作不变（交二值终局）· **监理模块自纠：误报根因已定位并已改码 + 回归锁死，待外部安全重启生效** · owner 项 = 0
- **遵令**: 已停迭代；本件**只做 Plan**（监理令：回到 Plan → 说清 ①②③ → **一次实现**；本件交 Plan 与设计，实现为**下一步单发**）。

## 一、① 信号怎么走（大白话）

16 条 = **J2 连接器的 PCIe 上行差分对**（`PCIE_UP_OUT0..7` 的 P/N）。

- **起点 A 锚**：芯片侧**贯通孔**（F↔B 全层），`x≈84–94, y≈55` ⇒ **In5 上可直接起步，0 孔**。
- **终点 B 锚**：J2 侧**埋孔**（只到 In2）`x≈127–141, y≈42.6–52.9` ⇒ 到 In5 需**下潜 1 次**（In5→In2）⇒ **每线 1 孔 ≤2 孔 ✓**（长走全在 In5）。
- **路当中一道墙**：缝合孔场（`x≈82–118, y≈48–55.5`）+ `PERSTA#` 铜带（`y≈55.15–56.10`）+ J2 贯通孔列（`x≈133.2–136.3`）⇒ In5 上**只有一扇门**（`x≈136.0–143.1`）。
- **所以**：A → 南下到南走廊（`y≈56–68`）→ 东行 → 穿门（**在门西侧那排缝合孔之间"挤"过去**）→ 北上 → 接 B。**16 条共用南走廊 + 这一扇门。**

## 二、② 挡路的是什么（两层）

**(甲) 物理面：紧，但没堵死**（本件实测，独立路径）

| 截面 / 跨段 | 自由高度 | 0.435 节距可摆层位 |
|---|---|---|
| 南走廊**长跨** `x∈[95.745,135.45]`（= 一条横段从锚侧**一直拉到门**） | — | **14** |
| 南走廊**东跨** `x∈[129,136]`（= 横段**只在门口附近**走） | — | **16** |
| **夹缝本身** `x∈[132.1,136]` | — | **16** |
| 门列 16 条竖线（`x=136.2…142.7`） | 均可从 `y≈45` 直通 `y≈67.96` | 16 列 ✓ |
| 北区（`x∈[118,134], y∈[42,55.8]`） | 一整片开阔（少数小孤岛） | 充裕 |

⇒ **板有解**（在册 R393 切面 28 / R395 min-cut 16 与本件吻合）⇒ **不得出不可行证书**。

**(乙) 真正挡路的 = 我们的图纸**（本件定量坐实）

图纸把每条线钉成**「南走廊里一条笔直水平行」**：一条线 = 一个高度，且该横段**必从锚侧一直拉到门**（长跨）⇒ 只能取**长跨那一档的 14 个层位** ⇒ **容量 14 < 16**。
**这就是 R463/R465/R471/R472 反复"域空/摆不下/被证伪"的同一根**（与 **R446** 构造式上界 14/16 同数）。
根因一句话：**该由求解器拍板的高度，被生成器钉死在一条直线上**（承 R450 / #K2-166「代理≠要求」/ R325「任何解必须含 ≥1 次层内折返」）。

## 三、③ 人类方案（大白话 · 老工程师包抄连接器的手法）

**别让每条线在南走廊里各占一条笔直道；让它们在走廊西侧先各走各的高度，到门口前"下一级台阶"，再像梳子一样层层嵌套地把头伸进那 16 个门口层位。**

每条线的形状（**全部位置交求解器**，图纸只做纯投影）：

```
A ──(下行竖列 ci)──►  西段行 s（南走廊西侧 · 高度自由带 ≈10.3mm）
                 └─ 折返列 xj ──► 门口层位 e（夹缝 16 个层位之一）
                                └─► 门列 PX(p) 北上 ─► 北段行 n ─► 北侧竖列 co ─► B
```

**为什么这回够**：把「一条线 = 一条直线」改成「一条线 = **西段 + 一级台阶 + 门口段**」以后——
- **西段行**只在南走廊西侧走（`x ≲ 129`，**不碰夹缝**）⇒ 用**连续自由带**（≈10.3mm → 24 个层位），不必再挤 14 个位；
- **门口段**才需要夹缝层位 ⇒ **总共 16 个层位刚好都在**（14 个"长跨也能走"的 + 2 个"只有门口段才够短"的 `67.39 / 67.83`）⇒ **16 = 16 ✓**（这就是差的那 2 条）。
- **嵌套次序**（防互撞）：**折返列 xj 按锚序单调排开**（外侧线的台阶在外侧），西段行与门口层位随之单调 —— 与在册 **R455**（序变量 + 互异 + 单调，小实例手验 `[0,1,2,3]`）**同一形态**，本仓已做成过。

**验证与额度**：先过**建图质检闸**（全路径域非空 ∧ 整盘可指派）⇒ 一次实现 ⇒ 一次小实例见证 ⇒ 一次全量受证（**额度 1**）；读数全走**独立路径**（在册 `exact_gate` + 直算折线距）并落对照件。

## 四、《卡点报告》三问

**（一）试过什么**：`R460v2`（纯投影 f(p,s,n)）→ `R463` 2 网域空；`R466v2`（锚侧走廊也交求解器）→ `R465` 仍 2 网域空；`R468`（逐腿表；只证必要条件 16/16 非空；评审格 (3) 容量账 9<16 自相矛盾）；`R470`（2600 万/网枚举 ⇒ 不可算，自判作废）；`R471`（贪心/候选级 ⇒ 被 `exact_gate` 当场证伪 113+8 处）；`R472`（近似算域 ⇒ 空心模型 ⇒ 平凡 INFEASIBLE）；`R473`（域非空但整盘不可指派 ⇒ CP-SAT INFEASIBLE 19.6s）；`R475`（定性：容量上界 14<16）；`R478`（本件：分跨段容量表 + 设计）。

**（二）为何不通**：每一轮都**保留同一个形状模板**（一条线 = 南走廊里一条笔直的、从锚侧直达门的长横段）。该模板**可证容量只有 14**（长跨自由带 4.69mm/5 段 ⇒ 0.435 节距最多 14 个层位），**而车道数是 16** ⇒ 闸注定报「域空 / 不可指派」。又因**只差 2 条**，任何为凑数做的近似（抽样 / 贪心 / 近似算域）都**恰好在这把刀口上翻车**（R471 被证伪、R472 空心）⇒ **不是算法不会、不是题难，是图纸少了一格形状自由度。**

**（三）缺口在哪层** ——**图纸层**：缺 **层内折返（jog）** 这一格自由量（且必须与「西段/门口段分离」绑定，见 §三）。
- 非算法层（证明级方法在册：R455 / R362·C-B2UP-1 / R432）；
- 非几何/板层（本件容量表：门口 16、门列 16、北区充裕 ⇒ 板有解）；
- 非判据层（`criteria/` rev=6 未动）；
- 非需求层（未触 #K2-169 §四.3.e —— 无不可行证书，通向 owner 的唯一正路**未**被触发）。

## 五、下一步（**一次实现** · 不重跑）

1. 落 **jog 版图纸**：对象 = `ci · s · xj · e · p · n · co`（七类**全为求解器变量**）· 生成器 = **纯投影** · **零残余模板**；
2. **一次**过建图质检闸（前置 · fail-closed）；
3. 闸过 ⇒ **一次**给死二值终局：**全 16 条整盘指派见证（含 `buildability`: `no_move` | `relocation_listed`）**，读数走独立路径 + 对照件；
4. 闸不过 ⇒ 回建图补自由度（允许 · 不耗额度），**不出假证书**。

**本件状态**：Plan/设计/容量证明**已交**；**实现未执行**（遵监理令之次序 + #K2-169 §七 复核闸）。**停线维持**。
