dataxcash/hw_ic_k2/pm_gate/artifacts/k2_v4/P6_execution/P6_OPEN_READINESS/K2_R476_BLOCKER_REPORT_WHICH_LAYER_v1.md

# R476 ·《卡点报告》（应监理停止令：回到 Plan · 人类工程师路径 · 说清信号/挡路/方案）

- **from**: ENG · ARCHER（K2 数据面卡 · ②-UP 16 条单层 In5 长走）
- **to**: 监理
- **触发**: 监理**停止令（红线：命令重复 · `r473`）** —— 令：**立即停迭代**（禁『改参/换工具/改笼位 → 重跑』）· 回到 Plan 说清 ①②③ · 一次实现 · 并交本《卡点报告》
- **本件性质**: **只写报告**（**未驱动求解器 · 未改代码/参数/约束/SPEC/生成器** · 受证额度 1 **未耗** · 停线维持）
- **首行复述（回执识别用）**: 监理停止令（红线：命令重复）—— 同型命令重复 3 次(疑似暴力迭代/改参重跑): r473

## 〇、遵令与自陈（先认，不辩解）

1. **已停**：本轮起**不再**出现「改动 → 重跑」。`r473` 系**同一只读质检闸**之执行；本 ENG **未**在 `r473` 内改过参数/工具/笼位，亦**未**重跑同一命令 ≥2 次。
2. **但告警性质另记**（承 **#K2-167 §八** 已登记之监理模块缺陷）：`_same_shape_counts` 以 **`/tmp/opencode/<tag>`** 计签名、**未排除只读**，同一 scratch 目录内**多条不同命令**会累加成「同型重复」——`r424`/`r473` 疑属该类。**登记为观察，不据以自辩**；**遵令照办**。

## 一、① 信号怎么走（大白话）

这 16 条线是 **J2 连接器的 PCIe 上行（`PCIE_UP_OUT0..7` 的 P/N，共 16 条）**：

- **起点（A 锚）**：芯片侧，板子中间偏西，`x≈84–94, y≈55`（是贯通孔，铜从表层一直到底层）。
- **终点（B 锚）**：J2 连接器侧，`x≈127–141, y≈43–53`（是埋孔，只通到 In2 层，**不通 In5**）。
- **必须走的层**：冻结要求 = **长走全在 In5 一层**（不换层），**每条线 ≤2 个过孔**，端点不许动。
- **路当中一道「墙」**：缝合孔场（`x≈82–118, y≈48–55.5`）+ `PERSTA#` 铜带（`y≈55.15–56.10`）+ J2 贯通孔列（`x≈133.2–136.3`）连成一片，In5 上**只有一扇门**：`x≈136.0–143.1`（约 7mm 宽）。
- **所以物理上只有一条路**：从 A 出来先往**南**绕到墙下方（南走廊 `y≈56–68`），一直**往东**开到那扇门，**穿过门往北**上到 `y≈43–53`，再往西接到 B。**16 条线全走这一条走廊 + 这一扇门。**

## 二、② 挡路的是什么（两层，必须分清）

**（甲）物理空间（真的紧，但没堵死）**
- 16 条线都要从南走廊**横穿同一段** `x∈[95.745, 135.450]`（每条线的横段都必然盖住这段）。
- 实测：这段上「完全走得通」的高度，在**在册设计余量口径**下只剩 **4.69 mm、且碎成 5 段** ⇒ 按 0.435 节距**最多摆 14 条**；**16 条摆不下**。（若拿掉设计余量，同一段有 6.09 mm ⇒ 能摆 18 条。）
- 到「门」那一段（截面 `x=133.5`）能摆 **17 条 ≥16**；在册 **R393 切面容量 28 / R395 一般曲线 min-cut 16** —— **都 ≥16**。
- **⇒ 板子本身没被判死**；「板上无解」**不成立**。**不得出不可行证书。**

**（乙）真正挡路的是「我们的图纸」（卡点就在这层）**
- 现图纸把每条线钉成**「在南走廊上占一条笔直的水平行」**：一条线 = 一个高度。这个**形状模板**的容量**恰好只有 14**（≤ 需要的 16）——**这就是每轮跑出来「域空 / 摆不下 / 摆下但被核验证伪」的同一个根**。
- 印证：**R446** 当年构造式上界也是 **14/16**（同一个 14）；**R325** 早已登记「**任何解必须含 ≥1 次层内折返（jog）**」。
- 旁证：**板上既有的 16 条** 在**间距/净距面 0 违例**（R416 实测 inter-pair 边距 0.4491 ≥0.435）⇒ **空间是够的**；它们**只是用了 4 个孔 + 换层**，撞在「≤2 孔 / 单层长走」这一条上。**⇒ 差的不是空间、不是算法，是图纸的形状自由度。**

## 三、③ 人类方案（大白话 · 就是老工程师包抄连接器的手法）

**别让每条线在走廊里各占一条笔直道；让它们在宽敞处先各走各的高度，到门口前再「下一级台阶」，像梳子一样层层嵌套穿门。**

具体（每条线，全部位置**交给求解器拍板**，图纸只负责画）：

1. 从 A 锚往下走一小段（**锚侧竖列 `ci`**，每条线不同列）；
2. 在**西边宽敞区**横走一段（**西段行 `s`**，这里高度富余 ≈26 个位）；
3. **下一级台阶**（**折返列 `xj`** + **东段行 `e`**）—— 这就是新加的那一格自由度；
4. 从 `e` 高度往东穿过那扇门（**门位 `p`**，16 个门位刚好够）；
5. 往北上到东侧；
6. 在**北边**横走一段（**北段行 `n`**）；
7. 收进 B 锚（**北侧竖列 `co`**）。

**嵌套次序**（关键，防互相撞）：按 A 锚的左右顺序，**最外面的线用最外面（最南/最北）的位，里面的线用里面的位**，一路单调嵌套 —— 这样线不交叉、间距自然拉开。这与 **R455**（序变量 + 互异 + 单调，小实例手验 `[0,1,2,3]`）是**同一形态**，本仓已做成过。

**为什么这回能成**：把「一条线=一条直线」换成「一条线可以下一级台阶」以后，南走廊**不必**再在一段里塞下 16 个高度 —— 只有**门口**那一处要 16 个位，而门口**正好有 17 个位**（R395 min-cut = 16 与此吻合）。

**验证与额度（不变）**：
- 先过**建图质检闸**（全路径域非空 ∧ 整盘可指派）；**闸不过 ⇒ 回建图**，**禁开跑、禁报不可行**；
- 闸过 ⇒ **一次**实现 → **一次**小实例见证 → **一次**全量受证（**额度 1**）；
- 全部读数走**独立路径**（在册 `exact_gate` + 直算折线距）并落**对照件**；
- **候选级方法（贪心/抽样）只可热启动，不作终局来源**；**禁**删约束换 SAT。

## 四、《卡点报告》三问

**（一）试过什么**
- `R460 v2`：纯投影 `f(p,s,n)` → `R463` 实测 2 网域空；
- `R466 v2`：把锚侧出入走廊也交求解器（6 类对象）→ `R465` 仍 2 网域空；
- `R468`：逐腿表合成 ⇒ 逐段域非空 16/16（**只是必要条件**）；评审格 (3) 容量账自相矛盾（9<16）；
- `R470`：逐网联合元组 5 重嵌套 ≈2600 万/网 ⇒ **规模不可算，自判作废**（未出假结论）；
- `R471`：贪心 max-min（**候选级**）自报 16/16 ⇒ **被在册 `exact_gate` 当场证伪**（束间 113 处 / 净距 8 处）；
- `R472`：逐变量域用**近似测试**算 ⇒ 算空 ⇒ **空心模型** ⇒ 机器平凡 INFEASIBLE；
- `R473`（本轮闸）：逐变量投影域取自逐腿表（**非**近似）⇒ **域非空**，但 5×AllDifferent + 单调 ⇒ **CP-SAT INFEASIBLE 19.6s**；
- `R475`：对上条**定性** ⇒ 该 INFEASIBLE = **残余单走行模板之容量上界 14 < 16**（Hall 失败），**非**物理不可行。

**（二）为何不通**
每一轮都**保留着同一个形状模板**——「南走廊里一条线占一条笔直水平行」。
- 该模板**可证**容量只有 **14**（公共跨段全清高度 4.69mm / 5 段 / 0.435 节距）**< 16**；
- 所以闸**注定**报「域空 / 不可指派」，而**这个信号与板子无关**（板有解：门口 17 ≥16、min-cut 28/16）；
- 又因为它**只差 2 条**，任何为「凑数」做的近似（抽样、贪心、近似算域）都会**刚好在刀口上翻车**（R471 被证伪、R472 空心）——**这不是算法不会，是尺子不对/图纸缺格**。

**（三）缺口在哪层** —— 一句话：

> **缺口在【图纸层】的最后一格自由量：【层内折返（jog）】。**
> - **不在算法层**：证明级方法在册齐备（R455 序变量+互异+单调 / R362·C-B2UP-1 有序多商品流 MILP / R432 CP-SAT+MILP 双证）；
> - **不在几何/板层**：门口容量 17 ≥16 · min-cut 28/16 · 既有 16 条间距面 0 违例 ⇒ **板有解**；
> - **不在判据层**：`criteria/` rev=6 未动；
> - **不在需求层**：既有布线在「≤2 孔 / 单层」以外**全部达标** ⇒ **尚不触 #K2-169 §四.3.e 之 owner 支**。

## 五、本件落点与下一步（停等）

- **本轮**：只交本报告 + `R475` 定性件；**未开跑**、**未改**任何文件（除落件本身）。
- **下一步（一次实现 · 不重跑）**：按 §三 落 **jog 版图纸**（生成器纯投影 · 七类对象全为求解器变量 · 零残余模板）⇒ **一次**过闸 ⇒ **一次**给死二值终局。
- **约束不变**：受证额度 **1 封存** · 停线维持 · 冻结四源 4/4 不动 · `criteria/` 只读 · 正式产物非 `/tmp`。
