dataxcash/hw_ic_k2/pm_gate/artifacts/k2_v4/P6_execution/P6_OPEN_READINESS/K2_R463_SINGLE_SHOT_WINDOW_WITNESS_FAILS_EMPTY_DOMAIN_SPEC_SHAPE_BLOCKED_v1.md

# K2 · R463 —— 单发窗口：实现 ✅ · **见证 ❌（域空）** · 全量未启动

- **ts** 2026-09-24T03:44:31 · **from** ENG·ARCHER · **to** 监理 · **owner 闸口 0**
- **authority**：#K2-162 §四.2/§四.3（单发窗口 · 任一环不过 ⇒ 立即停 + 据实呈报，不得自行补一处再跑）· R460 v2 规格

## 0. 一句话
单发窗口：**① 实现 ✅**（忠实规格：纯投影 `f(seat,layer)` · 无 `col` · 无吸附/兜底/裁剪）**② 小实例见证 ❌ —— 域空**（R6 域过滤后 **16 网中 10 网可用 (seat,layer) 组合 = 0**）⇒ 依 §四.3 **立即停**；**③ 全量受证未启动（额度 1 未耗）**。

## 1. ① 实现（忠实规格）
{
 "faithful": true,
 "notes": "投影 = [(A_x,A_y),(A_x,SY(l)),(PX(s),SY(l)),(PX(s),NY(l)),(B_x,NY(l)),(B_x,B_y)]；PX=135.45+0.435s · SY=57.100+0.435l · NY=54.900−0.435l；无任何自由量/调整量",
 "r6_domain_filtering": "净距**只由域表达**（渲染器零调整）⇒ 逐网枚举 18×24=432 个 (s,l) 组合，按 hw+eff(net)+PAD_EXTRA 对非 lane 障碍做确定性剔除"
}

## 2. ② 见证实况
{
 "result": "FAIL（域空 ⇒ 见证不可解）",
 "domain_sizes": {
  "PCIE_UP_OUT0_N_J2": 0,
  "PCIE_UP_OUT0_P_J2": 0,
  "PCIE_UP_OUT1_N_J2": 29,
  "PCIE_UP_OUT1_P_J2": 0,
  "PCIE_UP_OUT2_N_J2": 0,
  "PCIE_UP_OUT2_P_J2": 0,
  "PCIE_UP_OUT3_N_J2": 18,
  "PCIE_UP_OUT3_P_J2": 0,
  "PCIE_UP_OUT4_N_J2": 0,
  "PCIE_UP_OUT4_P_J2": 0,
  "PCIE_UP_OUT5_N_J2": 29,
  "PCIE_UP_OUT5_P_J2": 0,
  "PCIE_UP_OUT6_N_J2": 0,
  "PCIE_UP_OUT6_P_J2": 0,
  "PCIE_UP_OUT7_N_J2": 24,
  "PCIE_UP_OUT7_P_J2": 0
 },
 "interpretation": "**10/16 网之可容许组合 = 0** ⇒ 该形态在本板上**基本走不通**（投影的固定形状撞墙：长走横段被缝合孔场/连接器列/`PERSTA#` 带挡住，而形状无纵向自由度可绕）",
 "controls_that_did_work": {
  "neg1_seat_shortage": "✅ 拦",
  "neg2_same_seat": "✅ 拦",
  "neg3_same_layer": "✅ 拦",
  "neg4_injected_snapping": "✅ 拦（几何重合被抓）",
  "neg5_shape_violation_constructible": "✅ 拦（geom_min 0.4074 < 0.435）"
 },
 "not_run": "A2 几何分离 / A3 单射 因域空未进入执行"
}

## 3. ③ 全量
**未启动**（见证不过 ⇒ §四.3 硬闸；受证额度 1 未耗）

## 4. 规格层发现
**这是规格层（图纸层）发现，非实现缺陷**：R460 v2 之投影形状**不含纵向自由度**（长走横段被钉在 `SY(l)`/`NY(l)`），而本板之墙（缝合孔场 x≈82–118 y≈48–55.5 · `PERSTA#` 带 y≈55.15–56.10 · J2 通孔列 x≈133.2–136.3）要求长走**必须能在自由带内选行**（承 R260 §六 / R446：A→南通道→东口→北区→B）。⇒ **规格需增一条「长走行由求解器选」的规则**（即把行/列也变成求解器变量并保持纯投影），而非由我自行补一处再跑。

## 5. 停止令遵从
**已立即停**：未重跑、未改参数/工具、未删约束、未启全量；依 §四.3 据实呈报，**不自行修补**。

## 6. 请监理
- ① 请监理就『规格需增「长走行/列由求解器选」之规则』**定性**：属**同一规格补齐窗**（重交 R460 v3 复审）抑或按 #K2-162 §四.3『二次即升级生产方式不达标』处置；
- ② 全量受证额度 1 仍封存未耗（本窗口未触及）。

## 7. 边界
冻结四源 4/4 未动 · criteria/ rev=6 未动 · 未改在册工具/生成器/SPEC 设计/原理图 · 未派 WORKER · 未启全量。

---
—— ENG（ARCHER）· 2026-09-24T03:44 · sha16 `a361f696085a0c73`
