dataxcash/hw_ic_k2/pm_gate/artifacts/k2_v4/P6_execution/P6_OPEN_READINESS/K2_R460_PROJECTION_SPEC_COMPLETE_DESIGN_FOR_REVIEW_v1.md

# K2 · R460 **v2** —— 《投影规格（完整设计）》**已闭合**（重交复审 · 依 #K2-161 §四.3）

- **ts** 2026-09-24T03:12:28 · **from** ENG·ARCHER · **to** 监理 · **owner 闸口 0** · **revision 2**
- **authority**：#K2-161 §四.3（同一个规格补齐窗 · 重交本编号）· #K2-160 · #K2-159 · #K2-158 · R401 口径
- **性质**：只交规格修订（未改代码 · 未跑见证 · 未启全量 · 停线维持）

## 0. 一句话
**R460 规格 v2（已闭合）重交复审**：按 §四.3 补齐四项 —— (a) `col` **删除**（R1 定「首段只竖向」后 (seat,layer) 已完全决定路径）；(b) **口径冲突消除**（R4 明定端点固定、无 Δx）；(c) A_x/B_x 间距改为 **fail-closed 前置断言 P1/P2**（不再以「实测」代保证）；(d) 负控⑤改为**可构造可复现实例**。附 **闭合自检三步**表。**停线维持 · 未改代码 · 未跑见证 · 未启全量。**

## 1. 变量表 + 投影函数（零自由量）
{
 "seat": "每线 1 个：端口位子索引 s_i ∈ {0..17}；其**唯一几何定义**见 R3（穿越列 x = 135.45 + 0.435·s_i）",
 "layer": "每线 1 个：带层索引 l_i ∈ {0..23}；其**唯一几何定义**见 R2（南行 y=57.100+0.435·l_i；北行 y=54.900−0.435·l_i）",
 "col": "**已删除**（依 #K2-161 §四.3.a 之 (ii)）：R1 定为「首段只准竖向」后，路径已由 (s_i, l_i) **完全决定**，`col` 无几何用途 ⇒ 自 §1/§0/A3 一并删除，**不留未决自由量**"
}

**投影函数 f（唯一定义 · 零自由量）**：给定 (s_i, l_i)，路径点列 = [ (A_x, A_y), (A_x, SY(l)), (PX(s), SY(l)), (PX(s), NY(l)), (B_x, NY(l)), (B_x, B_y) ]，其中 PX(s)=135.45+0.435·s，SY(l)=57.100+0.435·l，NY(l)=54.900−0.435·l；**无吸附/兜底/裁剪/合并/候选修剪/障碍绕行/横向调整量**。

## 2. 前置断言（fail-closed）
[
 {
  "id": "P1",
  "assert": "**前置断言（fail-closed）**：相邻 A 锚 x 间距 minΔ_Ax ≥ 0.500mm；不满足 ⇒ **本规格判定不合格**（不得以「实测」叙述代保证）",
  "value_now": "18 处相邻间距实测 0.50–1.00 ⇒ 断言成立（但**规格以断言表述**，非以观测值保证）"
 },
 {
  "id": "P2",
  "assert": "**前置断言（fail-closed）**：相邻 B 锚 x 间距 minΔ_Bx ≥ 0.580mm；不满足 ⇒ 本规格判定不合格",
  "value_now": "16 处相邻间距实测 ≥0.58 ⇒ 断言成立（同样以断言表述）"
 }
]

## 3. 几何规则 R1–R6（每条：规则 / 分离义务 / 可复现断言 / 对应负控）
### R1 首段（出 A 锚）·**只准竖向**
- **规则**：自 (A_x, A_y) **垂直**下潜至南行 y=SY(l_i)，x 恒为 A_x。**禁**在锚点 y 上横移；**无** Δx 调整量。
- **分离义务**：相邻首段竖线距 = |ΔA_x| ≥ 0.500（**由 P1 前置断言保证**）
- **断言**：入口区逐对最小距 ≥0.435mm（仅取首段线段）
- **负控**：强令两线首段同列 ⇒ 必判不合格

### R2 分层渲染（南/北行，同一 l_i）
- **规则**：南行 y=SY(l_i)、北行 y=NY(l_i)，一一对应；**禁吸附/对齐任何网格**。
- **分离义务**：l_i 互异 ⇒ 行距 ≥0.435
- **断言**：渲染行集合两两 ≥0.435
- **负控**：① 同层必不合格；④ 注入吸附 ⇒ 单射断言必抓

### R3 端口穿越段
- **规则**：在南行与北行之间，于 x=PX(s_i) 竖向穿越。
- **分离义务**：s_i 互异 ⇒ 列距 ≥0.435
- **断言**：端口列两两 ≥0.435
- **负控**：② 同座 ⇒ 必判不合格

### R4 横向段与非交叉（洋葱嵌套）· **端点固定**
- **规则**：南行横段**自 x=A_x 至 x=PX(s_i)**；北行横段**自 x=PX(s_i) 至 x=B_x**；**端点固定，无任何 Δx/调整量**（口径唯一）；座/层随 A 锚 x 序**单调**（方向由求解器选 inc/dec）。
- **分离义务**：单调嵌套 ⇒ 任意两线折线两两 ≥0.435（含横段×竖段）
- **断言**：**在册闸** `n_lane_pitch_viol==0`
- **负控**：注入非单调座次 ⇒ 必判不合格

### R5 进出端（B 锚）·**只准竖向**
- **规则**：自北行至 (B_x, NY(l_i)) 后，**垂直**入 B 锚 (B_x, B_y)。
- **分离义务**：相邻出口竖线距 = |ΔB_x| ≥ 0.580（**由 P2 前置断言保证**）
- **断言**：出口区逐对最小距 ≥0.435
- **负控**：强令两线出口同列 ⇒ 必判不合格

### R6 障碍净距（**不进渲染器**）
- **规则**：**渲染器零调整**；障碍（非 lane In5 铜/孔/盘）净距**只由选址域与约束表达**——把投影后不满足净距的 (s_i, l_i) **从域中排除**。
- **分离义务**：净距 ≥ max(0.175, req)（孔到铜 0.25）
- **断言**：**在册闸** `n_clearance_viol==0 ∧ clearance_min_mm ≥ 0`
- **负控**：⑤（**可构造·可复现**）见下

## 4. 断言三证
{
 "A1_可解": "OPTIMAL/FEASIBLE，或正确 INFEASIBLE + 含核不可行证书",
 "A2_几何分离": "任意两线无共用节点 ∧ 线对线最小距 ≥0.435 ∧ 障碍净距 ≥0（在册闸三项全 0 · 全 16 条 · rev=6）",
 "A3_单射/确定性": "**A3 单射/确定性**（`col` 删除后）：不同 (s_i,l_i) ⇒ **不同几何**（几何可反解出 (PX(s), SY(l), NY(l)) ⇒ 单射）；同 (s,l) ⇒ 同一几何；代码路径唯一（纯投影）。"
}

## 5. 负控五件
- ① 座位不足 ⇒ 必不合格
- ② 强制两线同座 ⇒ 必不合格
- ③ 强制两线共用进出走廊列 ⇒ 必不合格
- ④ 注入渲染器越权（吸附/兜底）⇒ 必被 A3 单射断言抓住
- ⑤ 投影形态违约（见上·可构造实例）⇒ 须在**产出前**判不合格

**⑤ 规格级·投影形态违约（可构造·可复现）**：小实例 = 2 线；把其 A 锚设于 **y=55.00 与 55.10**（Δy=0.100<0.435）；**注入形态**：以「首段在锚点 y 横移」（即**违反 R1**的形态）渲染 ⇒ 两条首段横线相距 **0.100** ⇒ **期望**：断言 A2（入口区逐对最小距 ≥0.435）**在产出前**判不合格；若判合格 ⇒ 自检无效，**不得上全量**。（此例为**可构造的具体实例**，非历史引用。）

## 6. **闭合自检三步**（本轮补齐核心）
[
 {
  "step": "(i) 逐一配对（每个量 ⇒ 至少一条规则给出唯一几何定义）",
  "table": [
   {
    "量": "seat (s_i)",
    "定义规则": "R3（穿越列 x=135.45+0.435·s_i）"
   },
   {
    "量": "layer (l_i)",
    "定义规则": "R2（SY/NY 行）"
   },
   {
    "量": "col",
    "处理": "**删除**（无规则 ⇒ 未闭合 ⇒ 依 §四.3.a(ii) 移除）"
   }
  ],
  "result": "变量表**闭合**：{seat, layer} 各有唯一几何定义，无残留量"
 },
 {
  "step": "(ii) 一致性核对（规则间 / 规则与变量表不得口径冲突）",
  "result": "**已消除**：R4 明定「端点固定 · 无 Δx」；§1 不再出现任何调整量 ⇒ 「固定端点」与「横向调整」不再并存"
 },
 {
  "step": "(iii) 前提断言化（输入事实一律 fail-closed 前置断言）",
  "result": "**P1 / P2** 已把 A_x / B_x 相邻间距写成前置断言；**规格内不再出现以「实测」代保证**（「实测」仅作**当前事实附注**，非保证）"
 }
]

## 7. 门（复审 PASS 后）
{
 "序列": "① 本规格经监理**复审 PASS** → ② **一次**实现（忠实规格）→ ③ **一次**小实例见证（A1+A2+A3 + 负控①–⑤全拦）→ ④ **一次**全量受证求解（产物两件 + **可施工性字段**）→ ⑤ 在册闸 rev=6 全条三项全 0",
 "额度": "全量受证额度 = **1**（本件未消耗）",
 "禁": "删约束换 SAT · 以「实测」代保证 · 带「若仍需要」式未决条件进规格 · 先写代码再补规则"
}

## 8. 边界
**只交规格修订**：未改代码 · 未跑见证 · 未启全量 · 未动模型/约束/冻结需求/判据 · 冻结四源 4/4 未动 · `criteria/` rev=6 未动 · 未派 WORKER。

## 9. 请复审
- ① `col` 已删除、(seat,layer) 已完全决定路径 —— 是否接受？
- ② R4「端点固定·无 Δx」是否彻底消除口径冲突？
- ③ P1/P2 前置断言化是否达标？
- ④ 负控⑤（可构造实例）是否达标？
- ⑤ 闭合自检三步表是否覆盖监理所需？

---
—— ENG（ARCHER）· 2026-09-24T03:12 · 重交复审 · sha16 `469079b0add2bf8e`
