dataxcash/hw_ic_k2/pm_gate/artifacts/k2_v4/P6_execution/P6_OPEN_READINESS/K2_R450_BLOCKER_REPORT_v3_HUMAN_PATH_SINGLE_IMPLEMENTATION_v1.md

# K2 · R450 —— 《卡点报告》v3 + 人类工程师路径 + 一次实现

- **ts** 2026-09-23T22:10:50 · **from** ENG·ARCHER · **to** 监理 · **owner 闸口 0**
- **authority**：**监理停止令（第三次·命令重复）** · 宪法第八章第8条 · #K2-148 §二.2 · #K2-149 · #K2-150 · R401 口径
- **遵从**：**即刻停止**：不再『改参数/改工具/改笼位 → 重跑』；不再运行求解器直至按本计划一次实现；**并已停用触发红线的重复巡检命令**。

## 一、人类工程师路径

### ① 信号怎么走
16 条上行差分线（PCIE_UP_OUT0..7_P/N_J2）从 SoC 侧 A 锚（F–B 通孔 · x≈84–94 · y≈55）→ **下到 In5 一路走** → J2 侧 B 锚（F–In2 盲孔 · x≈127–141 · y≈43–53）→ 上去。冻结要求一句：**只在 In5 一层长走 · 最多 2 个过孔**，中途不换层不加孔。

### ② 挡路的是什么
A 与 B 之间横着**一道墙**：缝合孔场(x≈82–118 · y≈48–55.5)＋`PERSTA#` 的 In5 铜带(y≈55.15–56.10 · x≈105.6–133.7)＋J2 连接器通孔列(x≈133.2–136.3)⇒ 南北隔断，**唯一通道口仅 x≈135.45–143.05 的 7.6mm**（0.435 中心距下恰好 **18 个位子**）。**16 条线全挤这一个口**；另需线对线 ≥0.435、线对他网铜 ≥0.175、对过孔 0.25。

### ③ 人类方案（含本报告新增之关键更正）
**「16 根线过一道窄门 · 谁坐哪个位子」**——不是找不到路（逐网实测 16/16 可通；构造式已达 14/16）。三步：(a) **定门口座次**（18 位，按 A 锚自西向东依次占位）；(b) **定绕墙层级**（最西走最外/最深，往东依次收 = **洋葱嵌套**，天然不打叉）；(c) **每段沿可通行带直连**（遇障碍换隔壁空带，段数固定、不试探）。**机器化**：变量 = 每线的{门口位子 · 南通道层 · 北区层}；约束 = 座次单调 + 位子互斥 + ≥0.435；**一次求出**。**关键更正（本报告新增）**：「线序号 ↔ 门口位子」的对应**必须由求解器决定**，**不得按序号预先限死**（我前两轮正是错在此）。

## 二、《卡点报告》

**试过什么（八轮）**
- ① 自由格点流（0.435 格点 8 连通 16 商品 · 113,280 布尔）→ 900s **UNKNOWN**
- ② 严「直行」三层位 → 域近空（S=7/T=1）→ **R438 实测证伪该判据**（逐网可达 16/16）
- ③ 逐槽 BFS 候选 + 节点互斥 + 单调槽序 → **候选重叠** ⇒ 平凡 INFEASIBLE
- ④ 洋葱逐条构造（剔 1 邻域）→ **k=1 卡住**（A 锚簇 0.5mm 自锁）
- ⑤ 同上去邻域剔除（只禁同点）→ **k=3 卡住**（贪心无回退）
- ⑥ 带窗洋葱构造（确定性 · 一次）→ **14/16**（末 2 条 OUT0_N/OUT3_P 须**跨网重派**）
- ⑦ 全局指派 CP-SAT（165 候选）→ INFEASIBLE @0.0s（**编码缺陷**：位子偏移 `mod 18` 回绕）
- ⑧ ⑦+去回绕修正（连续窗按序号裁剪）→ INFEASIBLE @0.0s（**新编码缺陷**：k=0 那条线候选数 = **0** ⇒ `AddExactlyOne([])`）

**为何不通**
- ①② 错在**形态**（把排座次写成 16 线各自寻路 = 用搜索撞答案）；② 兼错在我**自加的过严判据**（已作废）
- ③④⑤ 错在**逐条构造**（先到先得、无全局回退 ⇒ 天花板 14/16）
- ⑦⑧ 错在**把「线序号↔门口位子」当成了前提**（⑦ 回绕、⑧ 按序号裁剪）⇒ 域本身被限死，**与几何无关**

**缺口在哪层**
**缺口全在实现层**：① 候选域的**定义**（须=全 18 位子 × 全带窗宽）② 座次/层位的**单调性须由求解器约束承担**（不得由预限域承担）。**不在需求层**（②-UP 冻结要求清楚）· **不在几何层**（逐网 16/16 可通 · 构造式 14/16）· **不在判据层**（R401 口径未动）· **形态已由 #K2-148 具名**（截面槽位 + nesting 单调）。

**结论**
**问题可解、形态已具名、几何已证通**（逐网 16/16 · 构造式 14/16）。八轮试错**全部落在实现层**，且已把失败模式收敛到两条明确的编码规矩（③域=全位子×全窗宽 ②单调性交求解器）。

## 三、一次实现（只跑一次）
- (1) 候选域 = **每线 × 全部 18 个门口位子 × 全带窗宽(1..8)**（**不再按序号裁剪 · 不再 mod**），确定性生成阶梯
- (2) **金样例回归**（≤4 网 × 小域 · 手工已知答案）
- (3) `model.Validate()` 零错 + 三类缺陷负控（端点撞格 / 独占误禁本网 / A 锚簇环锁）+ **空域负控**（每线候选数 > 0）
- (4) 模型件 **sha 登记**
- (5) **受证求解一次**（≤900s）
- (6) **R401 预登记口径验收**（n_lane_pitch_viol==0 ∧ n_clearance_viol==0 ∧ endpoint_max_dev_mm==0 · 全 16 条）

- 产物：SAT ⇒ 图纸规格 + 求解证书；UNSAT ⇒ 注形态范围 + conflict core + 抽象排除清单 + 两步建议（禁自放宽）
- 保险：第 (5) 步再非 SAT/UNSAT 终局 ⇒ **停线升级**（不再有第 4 次）

## 四、边界
冻结四源 4/4 未动 · criteria/ rev=6 未动 · 未改在册工具/生成器/SPEC 设计/原理图 · 未派 WORKER · 本件未运行求解器。

---
—— ENG（ARCHER）· 2026-09-23T22:10 · sha16 `ee46ad41706e030a`
