dataxcash/hw_ic_k2/pm_gate/artifacts/k2_v4/P6_execution/P6_OPEN_READINESS/K2_R448_BLOCKER_REPORT_v2_HUMAN_PATH_AND_SINGLE_IMPLEMENTATION_v1.md

# K2 · R448 —— 《卡点报告》v2 + 人类工程师路径 Plan + 一次实现

- **ts** 2026-09-23T21:55:31 · **from** ENG·ARCHER · **to** 监理 · **owner 闸口 0**
- **authority**：**监理停止令（第二次·命令重复 3 次）** · 宪法第八章第8条 · #K2-148 §二.2 · #K2-149 · #K2-150 · R401 口径
- **停止令遵从**：**即刻停止**：不再『改参数/改工具/改笼位 → 重跑』；不再运行求解器直至按本计划一次实现。已停。

## 一、人类工程师路径

### ① 信号怎么走
16 条上行差分线（PCIE_UP_OUT0..7_P/N_J2）从 SoC 侧 A 锚（F–B 通孔，x≈84–94、y≈55）出发，要到 J2 侧 B 锚（F–In2 盲孔，x≈127–141、y≈43–53）。冻结要求只一句：**只在 In5 一层上长走、最多 2 个过孔** ⇒ 路径 = **A 孔 → 下 In5 → 沿 In5 一路走 → 到 B 孔 → 上去**，中途不换层不加孔。

### ② 挡路的是什么
A 与 B 之间横着一道墙：①缝合孔场(x≈82–118,y≈48–55.5) ②PERSTA# 的 In5 铜带(y≈55.15–56.10,x≈105.6–133.7) ③J2 连接器通孔列(x≈133.2–136.3)。它把南北隔断，**唯一通道口只有 x≈135.45–143.05 的 7.6mm**（按 0.435 中心距恰好 18 个位子）。**16 条线全挤这一个口**；另需线对线 ≥0.435、线对他网铜 ≥0.175、对过孔 0.25。

### ③ 人类方案
这是**「16 根线过一道窄门、谁坐哪个位子」的排座次**，不是「找不到路」（实测每条单独都通，R438 16/16）。人类做法三步：(a) **先定门口座次**——18 个位子，按各线 A 锚自西向东依次占位，不插队；(b) **再定绕墙层级**——最西那条走最外圈/最深，往东依次往里收（**洋葱嵌套**），线之间天然不打叉；(c) **每段沿可通行带直着连**——遇障碍就换到隔壁空带，段数固定、不试探。机器化：变量只有「每线{门口位子, 南通道层, 北区层}」（百级），约束 = 座次单调 + 位子互斥 + ≥0.435，**一次求出**。

## 二、《卡点报告》

**试过什么**
- ①**自由格点流**（0.435 格点 8 连通 16 商品 · 113,280 布尔）→ 900s **UNKNOWN**（形态错）
- ②**严直行三层位**（南层×门口槽×北层）→ 域近乎空（S=7/T=1）→ **R438 实测证伪该判据**（逐网可达 16/16 · 多段阶梯）
- ③**逐槽 BFS 候选 + 节点互斥 + 单调槽序** → 候选互相重叠 ⇒ 平凡 INFEASIBLE（候选生成错）
- ④**洋葱逐条构造（剔邻域）** → **k=1 卡住**（A 锚簇 0.5mm ⇒ 邻域剔除自锁）
- ⑤**同上·只禁同点** → **k=3 卡住**（顺序贪心无回退）
- ⑥**带窗洋葱构造**（确定性·非 solver）→ **14/16**（末 2 条 OUT0_N/OUT3_P 的出入落在被分配窗之外 ⇒ 须跨网重派）
- ⑦**全局指派 CP-SAT**（165 候选 · 节点互斥 · 座次单调）→ **INFEASIBLE @0.0s**，查系**编码缺陷**：门口位子偏移用 `mod 18` 回绕 ⇒ 单调座次自相矛盾

**为何不通**
- ①② 错在**编码形态**：把「排座次」写成「16 条线各自在几万格点上寻路」= 用搜索撞答案
- ② 更错在**我自加的过严判据**（要求一口气横穿 40mm）——已由同批 R438 证伪并作废
- ③④⑤ 错在**逐条构造**：先到先得占用共享走廊，没有全局回退 ⇒ 天花板 14/16
- ⑦ 错在**实现细节**（模 18 回绕）⇒ 平凡不可行，**与几何无关**

**缺口在哪层**
**缺口全在实现层**（候选族生成 + 全局指派实现），不在需求层（②-UP 冻结要求清楚）、不在几何层（路是通的：逐网 16/16、构造式已达 14/16）、不在判据层（R401 口径未动）。**形态已由 #K2-148 具名**（截面槽位 + nesting 单调），**缺的是把「第 k 条线的第 s 个门口位子」正确映射为一条嵌套阶梯**。

**结论**
**问题可解、形态已具名、几何已证通**（逐网 16/16 · 构造式 14/16）；缺的是**映射与全局指派这两步的正确实现**。前 7 轮试错全在实现层，与需求/几何/判据无关。

## 三、一次实现（只跑一次）
- (1) 候选族**去回绕**生成：第 k 条线之候选位子取**连续窗** `[max(0,k-1), min(len(E)-1,k+1)]`（禁 mod 回绕）；带窗宽 1..8 逐级确定性加宽
- (2) **金样例回归**（≤4 网 × 小域 · 手工已知答案）
- (3) `model.Validate()` 零错 + 三类缺陷负控（端点撞格 / 独占误禁本网 / A 锚簇环锁）
- (4) 模型件 **sha 登记**
- (5) **受证求解一次**（≤900s）
- (6) **R401 预登记口径验收**（n_lane_pitch_viol==0 ∧ n_clearance_viol==0 ∧ endpoint_max_dev_mm==0 · 全 16 条）

- 产物：SAT ⇒ 图纸规格 + 求解证书；UNSAT ⇒ 注形态范围 + conflict core + 抽象排除清单 + 两步建议（禁自放宽）
- 保险：第 (5) 步再非 SAT/UNSAT 终局 ⇒ **停线升级**（不再第 3 次）

## 四、边界
冻结四源 4/4 未动 · criteria/ rev=6 未动 · 未改在册工具/生成器/SPEC 设计/原理图 · 未派 WORKER · 本件未运行求解器。

---
—— ENG（ARCHER）· 2026-09-23T21:55 · 停止令遵从 · sha16 `a66d00c4d31c657f`
