dataxcash/hw_ic_k2/pm_gate/artifacts/k2_v4/P6_execution/P6_OPEN_READINESS/K2_R435_STRUCTURED_CHANNEL_SLOT_ENCODING_SPEC_FOR_DISPOSITION_v1.md

# K2 · R435 —— **结构化编码规格**（截面槽位 + nesting 单调）：生产方式决策支持件（只读 · 不实现不求解）

- **ts** 2026-09-23T18:28:05 · **from** ENG·ARCHER · **to** 监理 · **owner 闸口 0**
- **authority**：**#K2-147 §三**（≥2 次重跑 ⇒ 停线 + **升级「生产方式」议题** = 监理自裁面）· owner #14⑥ · **#K2-146 §一**（问题类别/解的形态）· R401 预登记口径
- **边界**：**未实现 · 未对真实实例建模 · 未运行求解器**（承 R434 自停承诺）· 冻结四源 4/4 未动 · 未改在册工具/判据

## 0. 一句话
把 R434 诊断所指之编码形态写成**可授权的规格**：用 **#K2-146 §一 字面形态**（每网指派 南通道层位 / 东端口槽位 / 北区层位）替代自由格点流 ⇒ 规模 **113,280 布尔 → ≈960 决策变量**，**非交叉由单调约束直接保证**。**是否准用由监理具名**。

## 1. 规格
**决策变量**
- 每网 n：南通道 y 层位 `s_n ∈ S`（S = 南通道自由 y 层位集 · 步距 0.435）
- 每网 n：东端口 x 槽位 `e_n ∈ E`（E = 端口自由 x 槽位集 · 步距 0.435 · 实测 17 槽，R433）
- 每网 n：北区 y 层位 `t_n ∈ T`（T = 北区自由 y 层位集 · 步距 0.435）
- 每网 n：两侧引线走向（A 锚→首槽、末槽→B 锚；**确定性生成**，非决策）

**约束**
- **(i) nesting 单调（非交叉之充分条件)**：按 A 锚 x 升序 ⇒ `s` 序、`e` 序、`t` 序**同向单调**（R260 §六 P-1『最西 A 锚 → 最外/最深通道层』之形式化）
- **(ii) 端口唯一**：`e_n` 两两不同（17 槽 ≥ 16 网）
- **(iii) 束间中心距 ≥ 0.435**：由槽位步距 0.435 + 单调结构**由构造满足**（相邻网差异恰 ≥0.435）
- **(iv) 逐段净距（对非 lane 障碍）**：对每个候选槽位/引线，用**确定性几何预计算**判定是否满足 `hw + eff(net)` 与 `HOLE_CLR`（障碍场 = 非 lane In5 铜/孔/盘 · 与在册闸同口径）；不满足者**从该网之候选域中剔除**
- **(v) 端点位移 0**：折线首末点 = 锚点（引线确定性生成 ⇒ `endpoint_max_dev_mm == 0`）

**目标**：可行即可（可选：最小化总长） · **预期规模**：16 × (|S|+|E|+|T|) ≈ 16 × (27+17+16) ≈ **960 决策变量** ⇒ 小实例（R432 已验 ms 级工具面）
**两产物**（不变）：不变：**图纸规格**（每网 车道/层/过孔数）+ **求解证书**（SAT 模型件 / UNSAT 证明）
**验收**（不变）：不变：R401 预登记口径 `n_lane_pitch_viol==0 ∧ n_clearance_viol==0 ∧ endpoint_max_dev_mm==0`（全 16 条）
**健全性**：结构化形态下『非交叉』由单调约束**保证**（非事后抽样），故 pairwise 面不再依赖搜索；**残余风险 = 引线段**（A/B 侧短引线）—— 须以预计算候选域 + 闸复核双重把关。

## 2. 为何是这个形态
#K2-146 §一 原文即『**每对线分到哪条道/哪层/几个孔的一次性指派**』；R260 §六 P-1 亦已具名『**洋葱层构造**』为所需能力；R433 已实测出 3 组截面槽位（端口 7.60mm⇒17 槽 · 南通道 10.05mm · x=140 竖向 24.0mm）⇒ 规格所需数据**全部在册**。

## 3. 请监理具名之前置（ENG 才可续行）
- **① 生产方式具名（必需）**：监理核准编码形态 = 本文之**结构化（截面槽位 + nesting 单调）**编码（承 #K2-147 §三 之『生产方式』议题）。
- **② 一次性口径（必需）**：明确『新窗口 = 新一次性』，或本次 UNKNOWN 是否计入既有一次（#K2-146 §四#1『一个窗口、一次求解』）。
- **③ 两分支口径（可选）**：结构化编码若判 UNSAT ⇒ 证书即合法交付（#K2-147 §三 已明示）；是否须同时附『UNSAT 之下一步』建议，请监理具名。

## 4. 数据源（在册 · 原始 sha256）
- `R260_census`: 5e5ce7e5f021ab45
- `R401_prereg`: 1300a0d7c1cca174
- `R433_window_record`: 4c92237847bd5fb0
- `R434_outcome`: 2ca87f98a0c1c665
- `model_l8_dump`: None

## 5. 自检
未实现 · 未建模 · 未运行求解器 · **未预判 SAT/UNSAT** · **未自决生产方式**（明列前置）· 未新造判据 · 未改任何仓内件（除本件）。

---
—— ENG（ARCHER）· 2026-09-23T18:28 · 规格件（待具名）· sha16 `85b7667f6f7bfd02`
