dataxcash/hw_ic_k2/pm_gate/artifacts/k2_v4/P6_execution/P6_OPEN_READINESS/K2_R421_UP_OUT_CORRIDOR_LAYER_REGISTRY_CONFLICT_IN2_FROZEN_SPEC_VS_IN5_RULINGS_v1.md

# K2 · R421 —— ②-UP **走廊层在册冲突**：冻结 SPEC（**In2**）vs 监理闸（**In5**）· 逐字要件卡（只读）

- **from** ENG·ARCHER（续接 · 应「按已批准计划推进当前阶段 · fail-closed」）· **to** 监理 · **owner 闸口 0**
- **authority**：监理自动续推 · **owner #14⑦**（口径/权威先交监理）· 宪法第十一条（**冻结集变更 = owner**）
- **性质**：**只读取证**（零计算）。**ENG 不自裁谁为准**、未改任何件。

## 1. 要件卡（逐字出处）
| 条款 | 逐字 | 出处 | 类 |
|---|---|---|---|
| ②-UP 网集 | `PCIE_UP_OUT` 16/16 车道 | #K2-73 §八 · #K2-130 §七 · #K2-132 §七 | 监理裁定 |
| **过孔预算** | **≤2 via** | 同上 + **机判** `k2_layout_quality_check_v1.py` B2（`via_by_net`，匹配 `PCIE_(DN\|UP)_OUT\|PCIE_REFCLK`） | **机判维** |
| **走廊层（监理文本）** | **长走零改层 `F→In5→F`**；#K2-133「先删尽本 16 `PCIE_UP_OUT*` 网自身之 **In5** 旧铜」 | #K2-73/#K2-130/#K2-132/#K2-133 | 监理裁定（**文本**） |
| **走廊层（冻结 SPEC）** | `constraints.j2_escape_topology.rule` = 『2026-08-19 8 层定案: … **UP_OUT 16 网经 In2 单内层走廊 (F→In2→F 单次换层)**, 不再走 B.Cu』；`outer_basis` = 『8 层（LID REV6）：**In2 独立走廊容纳全部 UP_OUT**』 | **冻结 SPEC rev-55 `964101b19015f6d7`** | **冻结源** |
| **走廊层（冻结 SPEC · layer_plan）** | `layer_plan.j2_escape_nets.semantics` = 『… + **PCIE_UP_OUT0-7_J2 (B_PET 带, VIA_IN2->In2 east)**…』；`in2_width_mm = 0.205` | **冻结 SPEC rev-55** | **冻结源** |
| **换层语义（冻结 SPEC · 过孔）** | `vias.high_speed.basis` = 『… 每线 **≤2 过孔 = 单次换层 (F→In2→F)**，每对差分 4 过孔』 | **冻结 SPEC rev-55** | **冻结源** |
| 束间 0.435 | 只管束间；对内归 SPEC 自有配对规则 ≥0.175 + DRC | **#K2-143 §二** | 监理（已钉死） |
| 端点位移 | 端点/球位位移 **0** | #K2-133 §一 · #K2-73 §八 | 监理裁定 |

## 2. 冲突（两处在册文档相反）
- **冻结 SPEC rev-55 = `In2`**（并自称『**8 层定案**』· 宽度 0.205 · F→In2→F）；
- **监理闸文本 = `In5`**（F→In5→F；且 #K2-133 令『删尽本 16 网自身之 **In5** 旧铜』）。
- **SPEC 从未被改为 In5**：全检索 ⇒ `j2_escape_topology` 仅 rev-7 改过 `outer_basis`（CO-73 B.Cu 角色），**保留『In2 独立走廊容纳全部 UP_OUT』**；无任何 rev 卡改 Up 走廊层。
- **机判实际只查什么**：`k2_layout_quality_check_v1.py` B2 **只数 via**（`hs_hist`/`max_via`）——**全文无 In2/In5** ⇒ **『走廊层』条款零机判**。
- **板实况**：l9 逐网 **F→In2→In5→B（4 孔）**（R416/R419），与 SPEC 自述之『既有 U6↔J2 范式 … In2→In5→In5 横贯 …』一致 ⇒ **既非纯 In2 亦非纯 In5**。

## 3. 为何**现在**必须先澄清
1. owner 的『**放宽「孔数/层数」一条**』之语义**取决于本冲突**：以 SPEC 为准 ⇒ 放的是『In2 · F→In2→F』；以监理闸为准 ⇒ 放的是『In5 · F→In5→F』——**对既有布线/搬迁清单含义不同**。
2. 若 **SPEC（In2）** 为准 ⇒ 整条 **In5 车道程序**（R393–R398 容量/拓扑证书、R416 束间实测、以及**为腾空 In5 而做之 v55 搬迁**）其**目标层可能偏靶**（须即时澄清，非事后返工）。
3. 若 **监理闸（In5）** 为准 ⇒ 冻结 SPEC **三处滞后** ⇒ 须 SPEC 版本 bump（**冻结集变更 ⇒ 第十一条 = owner**）。
4. **机判缺口**：走廊层无条件判 ⇒ 无任何在册判据会拦/放。

## 4. 请监理裁（ENG 不自裁）
- **Q1 权威**：②-UP 长走层以**冻结 SPEC（In2 · F→In2→F）**为准，抑或**监理闸文本（In5 · F→In5→F）**？
- **Q2 路径**：Q1=In5 ⇒ 明示 SPEC 三处滞后之处置（版本 bump ⇒ 升 owner / 或判『声明性回填』不属冻结集变更）；Q1=In2 ⇒ 明示本项是否**重开目标层**（届时 In5 程序与 v55 搬迁之定位一并重判）。
- **Q3 覆盖**：走廊层**无条件判** ⇒ 是否登记为**检查覆盖缺口**（比照 C-17；**非新增检查齿**）。

> 本件**零计算 · 只读取证**；未改任何件/判据 · 未烙板 · 未派 WORKER。若 Q2 触发冻结集变更，**请监理依第十一条处理**（不请求 owner 直呈）。

—— ENG（ARCHER）· 2026-09-22 · 只读取证 · owner 闸口 0
