dataxcash/hw_ic_k2/pm_gate/artifacts/k2_v4/P6_execution/P6_OPEN_READINESS/K2_R351_CONSERVATION_BLOCKER_REPORT_v69_CW_RELEASES_ASIDE_SORT_BAND.md

# K2 · R351 ·《守恒级卡点报告 **v69**》—— **C-w 实测释放 A 侧重排带**

**件**：`K2_R351_CONSERVATION_BLOCKER_REPORT_v69_CW_RELEASES_ASIDE_SORT_BAND.json`（约定A `bf65bb4eeab7c891`）· 承 v68

## 实测（同一 `build_base` 之两算：现状 vs 可腾挪族置入 movable）
窗口 x∈[80,105] · cell 0.05：

| y 带 | 现状 | C-w 后 |
|---|---|---|
| 49–50 | 0.174 | 0.451 |
| 50–51 | 0.135 | **0.808** |
| 51–52 | 0.365 | 0.813 |
| 52–53 | 0.299 | 0.826 |
| 53–54 | 0.349 | **1.000** |
| 54–55 | 0.457 | **1.000** |
| **带内均值** | **0.296** | **0.816** |

可腾挪族（板内交集 **18** 网）：I2C1/2_SDA/SCL · PERSTA#/PERSTB# · PWR_BTN_ISO · DS320_STRAP_MODE · DS320_STRAP_{A,B}_ADDR{0,1}_{7-0,15-8} · GND · P3V3。

## 判
**C-w 释放 A 侧重排带**（v67 引理所需之水平重排空间）：**7.5–47 ％ → 45–100 ％（均值 29.6 ％→81.6 ％）** ⇒ **v68『C-*/C-w 非独立』定量证实；C-w 是 C-* 落地之前置**。
（本件**不主张** C-w 后即可布通；仍需 C-* 之重排感知联合指派。）

## 建议（监理自裁）
**(ii) 先行 + (i) 后继**：①批 C-w（`PERSTA#` 首选 · 逐项具名 + `ref_plane_continuity`）②派 C-*（一次实现）⇒ `exact_gate` 互距 0 ∧ 净距 0 ∧ 端点 0 + `buildability`。

## 边界
只读 · 未烙板 · 未改 `criteria/`/生成器/SPEC/原理图 · 未派 WORKER。冻结四源 4/4 未动；受审板 l8 `7a5c89913d6e5d0a` 未动。

---
—— ENG（ARCHER）· 2026-09-22 · 二值 **未取得** · owner 闸口 **0**
