dataxcash/hw_ic_k2/pm_gate/artifacts/k2_v4/P6_execution/P6_OPEN_READINESS/K2_R350_CONSERVATION_BLOCKER_REPORT_v68_ASIDE_SORT_BAND_CONGESTED.md

# K2 · R350 ·《守恒级卡点报告 **v68**》—— A 侧『重排带』实测拥挤（7.5–47 ％）

**件**：`K2_R350_CONSERVATION_BLOCKER_REPORT_v68_ASIDE_SORT_BAND_CONGESTED.json`（约定A `6c689c3d2c9a6b90`）· 承 v67

## 新实测（`bad` 逐带自由率 · x∈[80,105] · cell 0.05）
| y 带 | 自由率 |
|---|---|
| 49.0–49.5 | 0.224 |
| 49.5–50.0 | 0.136 |
| **50.0–50.5** | **0.075** |
| 51.0–51.5 | 0.447 |
| 52.0–52.5 | 0.206 |
| 53.0–53.5 | 0.471 |
| 54.0–54.5 | 0.244 |
| 54.5–55.0 | 0.677 |
| **55.0–56.5** | **0.926–0.944** |

## 判（决定性）
v67 引理要求 **上升序 = 层高降序** ⇒ 各 lane 须先在 A 带内**水平重排**（A 锚 x 序 ≈ B.y 升序，与所需上升序**相反**）。而该重排必用之 **y∈[49,54.5] 带自由率仅 7.5–47 ％**（最窄 **7.5 ％**）—— **被可腾挪之他网铜占据**。
⇒ **C-*（重排感知联合指派）与 C-w（腾挪他网铜）非独立**：v67 规格之 A 带重排**几乎无处落地**；**C-w 正是释放该空间之手段**。

## 卡点 v68
① ENG 能力（互距感知候选生成 + 联合指派）**∧** A 侧重排空间不足 ⇒ 需 C-* **与** C-w **联合**
② 关键资源 = **A 侧重排带 (x∈[80,105]×y∈[49,54.5])**（自由 7.5–47 ％）+ 窄颈；上带 y≥55.5 自由 92–94 ％
③ **被谁占死 = A 侧重排带被他网铜占据（可腾挪 ⇒ 仅 C-w）**；注：与 v66『16/16 单独可路』不矛盾（单 lane 可绕行，16 lane 联合重排需连续宽度）
④ **前提不成立**（(b) 不成立）

## 出口建议
**(i)+(ii) 联合**：批 C-w（`PERSTA#` 首选）释放 A 侧重排带 **+** 派 C-*（一次实现）做重排感知联合指派；单独任一恐不足。

## 边界
只读 · 未烙板 · 未改 `criteria/`/生成器/SPEC/原理图 · 未派 WORKER。冻结四源 4/4 未动；受审板 l8 `7a5c89913d6e5d0a` 未动。

---
—— ENG（ARCHER）· 2026-09-22 · 二值 **未取得** · owner 闸口 **0**
