dataxcash/hw_ic_k2/pm_gate/artifacts/k2_v4/P6_execution/P6_OPEN_READINESS/K2_R346_CONSERVATION_BLOCKER_REPORT_v66_TWO_FAMILIES_STRUCTURAL.md

# K2 · R346 ·《守恒级卡点报告 **v66**》—— 两法族结构性失败 · 二值未取得

**件**：`K2_R346_CONSERVATION_BLOCKER_REPORT_v66_TWO_FAMILIES_STRUCTURAL.json`（约定A `3721381a6b0893c3`）· 承 `K2_R345_..._v65`

**(a) 未得 · (b) 不成立**（不新增不可行主张）。

## 新证据
### 1. 单 lane 可达性（授权 no-move 口径 · 无互斥排除 · cell 0.02）
**16/16 lane 皆可单独成路**（46.59–67.04mm）⇒ **连通性不是瓶颈** ⇒ **C-w 对连通性非必要**（修正 R333『零候选 8/16』= 笼位受限候选模型之数）。

### 2. 法族 1：硬互距排除贪心（次序固定 · 非扫描）
| 次序 | cell | 锚保留 | placed |
|---|---|---|---|
| B.y 升序 | 0.05 | P | 2/16 |
| B.y 升序 | 0.02 | P | 2/16 |
| B.y 升序 | 0.02 | P+cell·√2 | 2/16 |
| A-x 序（束序） | 0.02 | P+cell·√2 | 2/16 |

⇒ 前 2 lane 之 P-排除带**封死走廊**，第 3 lane 不可达。

### 3. 法族 2：多样性感知候选 + 硬互距 MILP（授权形态）
每 lane **32** 候选（『过切线段 x=110 之 y_k』最短路 · y_k 步距 **0.5mm > P**）· 512 binaries · HiGHS：
**conflict pairs 122880 / 130560 = 互斥 94.1 ％ · MILP optimal · placed 1/16**
⇒ **候选退化是结构性的**（同 R328 之 93.8 ％）：最短路型候选在自由空间**瓶颈段必然相汇**。

## 卡点（v66 四字段）
| # | 内容 |
|---|---|
| ① **哪层** | **ENG 实现能力**：缺『**互距感知候选生成 + 联合指派**』。硬排除⇒**死锁**（2/16）；硬 MILP over 最短路候选⇒**退化**（1/16 · 94.1 ％ 互斥）。所需 = 列生成 / 互斥感知枚举 / SAT 位级「16 lane×格点互斥」 |
| ② **哪资源** | In5 走廊之**瓶颈段**（窄颈 x∈[93,112] + A 侧扇出/重排带 x∈[84,95]） |
| ③ **被谁占死** | **未占死**。A 锚到前一 lane 最短路最小距 **0.4386**（仅高出 P **3.6µm**）· 相邻 A 锚保留盘缝 **0.330mm < P** |
| ④ **为何任何分配都不可能** | **前提不成立**（⇒ (b) 不成立）。16/16 单独可路 + 割上界 67≥16 + 展开梯度 ~0.23 ⇒ 容量/连通/端点皆非瓶颈 |

## 出口（皆监理自裁）
(i) 派 `C-*`（一次实现 · 互距感知候选生成 + 联合指派）；(ii) 批 C-w（价值在**释放走廊资源**，非连通性）。

## 边界
只读 · 未烙板 · 未改 `criteria/`/生成器/SPEC/原理图 · 未派 WORKER。冻结四源 4/4 未动；受审板 l8 `7a5c89913d6e5d0a` 未动。

---
—— ENG（ARCHER）· 2026-09-22 · 二值 **未取得** · owner 闸口 **0**
