dataxcash/hw_ic_k2/pm_gate/artifacts/k2_v4/P6_execution/P6_OPEN_READINESS/K2_R333_CONSERVATION_BLOCKER_REPORT_v64.md

# K2 · R333 · 应监理停止令 ⇒ 《**守恒级卡点报告 v64**》（四字段）

**件**：`K2_R333_CONSERVATION_BLOCKER_REPORT_v64.json`（约定A `e740ecf9cdd9d096`）· 只读
**缘起**：监理停止令（收敛停滞≈80轮无二值）：「必须出二值；若出不来 ⇒ 立即出《守恒级卡点报告》」。
**锚**：受审板 l8 `7a5c89913d6e5d0a` · 冻结四源 **4/4 未动** · `criteria` **rev=6 MATCH** · **owner 闸口 0 · 待裁 0（ENG）**

## 〇 二值：**仍未出**
- **(a) 未得** —— R327 联合软协商 **16/16 成路**（放松互距）· 净距 0 · 端点 0，惟**互距未清零**（`min_gap=0.0000`，最佳 17）；R328 硬 MILP over 独立候选最优 **1/16**（候选退化 **93.8%**）。
- **(b) 不成立** —— R314 反证；R326 **独立刚性割上界 min = 67 ≥ 16**；R327 复证 16/16 皆成路。

## 一 四字段
| 字段 | 判 |
|---|---|
| **①哪层** | **算法/实现能力层** —— 缺『**冲突感知的联合指派**』（连通 ∧ 互距收敛须同时达成） |
| **②哪资源** | **In5 走廊** `x∈[82,144]×y∈[36,66]`；关键 = **出带↔走廊切换带（窄颈）** `x∈[93,112]×y∈[44,58]` |
| **③被谁占死** | **未被『不可动』占死**；占用者**可腾挪**且**已坐标级具名**：`PERSTA#`（13 段/**窗内 0 孔**=中段）· `DS320_STRAP_B_ADDR1_7-0`（11 段/2 孔皆在窗内）· `DS320_STRAP_B_ADDR0_15-8`（0 段/1 孔）· `I2C1_SDA`（3 段/1 孔）；全局固定缝合孔 **135 枚**（**不在对象内**） |
| **④为何任何分配都不可能** | **该前提不成立**（R314 反证 + R326 割上界 67 + R327 证 16/16 皆成路） |

## 二 本轮新增（使报告非重复）
- **R330**：具名 4 网腾挪 ⇒ 零候选 lane **8/16 → 0/16**（**收益已量**）。
- **R331**：搬迁对象 **坐标级清单**（要件①）—— `PERSTA#` 窗内 **0 孔** ⇒ **只改线不动孔**，最优先。
- **R332**：要件② `ref_plane_continuity` 必要条件 —— 4 网皆**信号网** ⇒ 未动平面/缝孔。

## 三 唯一两出口（皆监理自裁 · ENG 不自决）
1. **派 `C-*`**（冲突感知联合指派 · 一次实现）；或
2. **批 C-w** ⇒ ENG 续补要件③端点/球位不动证明（先 `PERSTA#`）④`buildability`②余项 ⇒ 出搬迁清单。

## 四 可施工性（宪法第十三条）
本件**不动任何对象** ⇒ **不动证明成立**；**不产出施工图**（缺图）⇒ 不得据以开工、不作里程碑。

## 五 边界
冻结四源不改 · `criteria/` 只读 · 未烙板 · 未改生成器/SPEC/原理图 · 未派 WORKER · 未写 `.omo/supervision/**` · 未以布通率/启发式冒充证书 · **禁 HOLD/停等**。

---
—— ENG（ARCHER）· 2026-09-22 · owner 闸口 **0**
