dataxcash/hw_ic_k2/pm_gate/artifacts/k2_v4/P6_execution/P6_OPEN_READINESS/K2_R321_BINARY_AND_CONSERVATION_CARD_REPORT_v61.md

# K2 · R321 · **二值判定 + 《守恒级卡点报告 v61》**（应停止令）

**件**：`K2_R321_BINARY_AND_CONSERVATION_CARD_REPORT_v61.json`（约定A **`c86c373ec5616f4a`**）
**应**：监理停止令（收敛停滞 ≈80 轮无二值）——「必须出二值 ‖ 立即出卡点报告」
**据**：#K2-132 §四/§七 · #K2-133 §三/§四 · 宪法第十三条 · 第三条
**锚**：冻结四源 **4/4 未动** · `criteria` rev=6 MATCH · 受审板 l8 **`7a5c89913d6e5d0a`** · **owner 闸口 0 · 待裁 0**

---

## 一、二值判定

| 支 | 判 |
|---|---|
| **(a) 可行见证** | **未得完整** —— 最佳 **13/16**（几何层过闸；但含绕行 ⇒ 不构成可交付见证） |
| **(b) 守恒级不可行证书** | **不成立**（R314 反证：`W_max=6 ⇒ U≤14` 系序律伪影；真实几何 `W_max=8 ⇒ U≤16`） |

> **本件不含任何「不可行」结论。**

### 本轮定向协调尝试（在 R320「静态他锚禁入 + 序贯」框架上）

| 序/策略 | 布通 | 失败 |
|---|---|---|
| `all_desc`（A.x 降序） | **13/16** ← 上限 | `T3_N` `T0_P` `T0_N` |
| `Pfirst_desc`（须穿带者优先） | 9/16 | 7 条 N |
| `Nfirst_desc` | 9/16 | 7 条 P |
| `Nlast_asc_Pdesc` | 9/16 | 7 条 N |
| `Pfirst_alt` | 6/16 | 10 条 |
| `预留逃逸走廊`（为 3 条失败者预留并优先布） | 3/16 | 13 条 |

**已布集合全部过 `exact_gate`**：互距违例 **0** · 最小 **0.4383 ≥ 0.435** · 净距违例 **0** · 端点偏差 **0.0000** ⇒ **方法与闸自洽**。
**失败机制**：未布 lane 之 A/B 端点格**均自由**，却**无路径** ⇒ 被既有 lane 之 0.435 封套**切成孤岛**（切割，非端点阻塞）。

## 二、《守恒级卡点报告 v61》四字段

| 字段 | 内容 |
|---|---|
| **① 哪层** | **In5.Cu（E1）· 单层 16 条 `PCIE_UP_OUT` 几何**。分工已明：**连接器侧段**（B 锚 ↔ x=134.6）**已闭合**（R316 · 16/16 过闸）；残余全在 **A 侧锚群出扇段** |
| **② 哪资源** | **A 侧锚群之出线窗口**：16 个 A 锚挤在 `y∈[54.88,55.82]` 之 **0.94mm** 双行带内（N 行 55.82×8 · P 行 54.88×8，**沿 x 交错**，邻锚 0.55–1.20mm）。P 行 8 条须**穿越 N 行**：可穿处 = 7 个内缝（每缝净窗 **1.20−2×0.435 = 0.33mm**，仅容 1 条）+ 东西两端 |
| **③ 被谁占死** | **未被占死**：(i) A 侧逐 lane 连通 **16/16**（R318）(ii) In5 跨切容量 **min 29 ≥ 16**（R318 @x=134）(iii) 走廊 In5 段 337 中他网 88、In5 过孔 198 中缝合孔 135；**237/237 自网阻塞全属自网×自网（他网 0）** ⇒ 自网可拆 |
| **④ 为何任何分配都不可能** | **不成立 —— 不主张任何分配都不可能。** 已排除 **连通型 / 容量型 / 守恒级刚性** 三类。本轮 5 组协调尝试全 ≤13/16 系**序贯类方法之性质**，非几何不可能。真实卡点 = **算法/实现能力层**：缺「A 侧锚群出线之**联合**指派（即刻离行向量 + 穿缝名额 + 分行序号）」+ **长度/等长约束**之求解器（承 #K2-133 (甲) `C-*`） |

## 三、残余两项 + 可施工性

- **残余**：① 未布 **3** 条（A 侧锚群西端出扇）② **长度质量**（`T1_N`=314.23mm vs `T1_P`=92.20mm ⇒ 等长/SI 不达标）
- **可施工性（宪法13）**：「施工队照着这张图能不能直接连？」→ **13 条几何层能**（坐标 + 过闸，但含绕行、**不作交付**）；**全板不能** ⇒ **全板图纸层缺图，不作里程碑、不得开工**。
- **不动证明**：本件不搬任何对象（未烙板 · 未改任何网几何）。

## 四、P4 状态

**P4 未全绿**（R317 verdict = **18/19**，唯一 FAIL `lib_electrical_level` 为判据侧）⇒ **fail-closed 维持：不进 P5、不下单**。

## 五、边界

冻结四源不改 · `criteria/` 只读 · 未烙板 · 未派 WORKER · 未改生成器/SPEC/原理图 · 临时仅 `/tmp/opencode` · 未写 `.omo/supervision/**` · 未以布通率/有界搜索冒充证书。

—— ENG（ARCHER）· 2026-09-22 · k2 `b200761`（本件另提交）· owner 闸口 **0** · 待裁 **0**
