dataxcash/hw_ic_k2/pm_gate/artifacts/k2_v4/P6_execution/P6_OPEN_READINESS/K2_R315_UP_OUT_CONSERVATION_CARD_REPORT_v60_BINARY_NEITHER_AND_R314_CORRECTION.md

# K2 · R315 · ②-UP 二值判定 + 《守恒级卡点报告 v60》

**件**：`K2_R315_UP_OUT_CONSERVATION_CARD_REPORT_v60_BINARY_NEITHER_AND_R314_CORRECTION.json`（约定A **`567ea506a3c143a0`**）
**应**：监理停止令（收敛停滞 ≈82 轮无二值）——「必须出二值 ‖ 立即出卡点报告」
**锚**：冻结四源 **4/4 未动** · `criteria` rev=6 MATCH · 受审板 l8 **`7a5c89913d6e5d0a`** · k2 `b368b7d` · **owner 闸口 0 · 待裁 0**

---

## 一、二值判定（本轮出）

> **二者皆不成立**：**(a) 可行见证 = 未得**（本会话单发构造读数 9/32）；**(b) 守恒级不可行证书 = 已被本会话 R314 反证（不成立）**。

| 支 | 判 | 依据 |
|---|---|---|
| **(a) 可行见证** | **未得** | 单发（1 次 · **未改工具 · 未做参数迭代**）运行 `k2_p4_b2_in5_lane_router_v3.py`（协商式**有界搜索**）⇒ `routed 9/32` · 车道互距违例 **16**（闸读 `lane_pitch_min_gap=0.0000`）· 净距违例 0。**该读数只作负结果记账，不作证书、不作卡点依据**（宪法：禁以有界搜索冒充证书）。 |
| **(b) 守恒级不可行证书** | **不成立** | R314：`W_max=6 ⇒ U≤14` 系复算器额外施加「沿 **A.x 逆序** 严格 ye 阶梯」这一**非几何**序律之产物；**反向即得 8**；真实几何下（带内 ∧ ye≥B.y+δ ∧ 互距≥0.435 ∧ **非交叉** ∧ 锚孔净距）**δ×DIL 六组合全得 `W_max=8 ⇒ U≤16`** ⇒ **16/16 未被排除**。与 **#K2-131 F-4 / #K2-132 (甲)**「容量 ≥16 ⇒ 不得签不可行证书」**一致**。 |

**同步作废**：R309 v59 / R298 v58 之 `W_max`、`U≤14/~13`、`EX-5 强制下限 |EX|≥2`；handoff §7-2（采 b+EX-5）与 §7-3（owner 级动固定件/墙带）**前提消失 ⇒ 无 owner 级事项**。

## 二、《守恒级卡点报告 v60》四字段（应停止令）

| 字段 | 内容 |
|---|---|
| **① 哪层** | **In5.Cu（E1）· 全 16 条 `PCIE_UP_OUT` lane 之单层 In5 几何**：A 锚（x≈84.35–93.70 · y≈54.88–55.82 之 `F.Cu–B.Cu` 通孔）→ In5 长走东行 → 连接器侧接入 → B 锚（`F.Cu–In2` 盲孔） |
| **② 哪资源** | ① **西出缺口行带**（连接器 GND 通孔列 x≈133.2–136.3 与墙带 x∈[105.6,133.7]@y∈[55.15,56.10] 所夹自由行 · 实测 9 带 · 上限 54.47）② **In5 单层长走走廊**（R270 实测自由宽 6.88 ≥ 15×0.435=6.09）③ **连接器侧接入位**（东组 B 锚 x=136.00 … 141.22） |
| **③ 被谁占死** | **未被占死**：(i) 缺口行带对西组 **8/8 全可容**（R314 精确解 + `exact_gate`：互距违例 0 · 最小 0.5050 · 净距违例 0）；(ii) 跨线容量 **≥16**（监理 F-4 独立自算 = 20）；(iii) 走廊 In5 段 337 中他网占 88、In5 过孔 198 中缝合孔 135（#K2-133 实测），**237/237 自网阻塞全属自网×自网（他网 0）**⇒ 自网可拆 |
| **④ 为何任何分配都不可能** | **不成立 —— 本件不主张任何分配都不可能。** R314 + 监理 F-4 双重独立复核：**不存在守恒级/几何刚性不可能性**。真实卡点 = **算法/实现能力层**：缺一个把「A 侧 stub × 下潜竖段」「西组 (c,Y,dx) 列位 × B 锚 jog」「东组连接器侧接入」**联立求解**的构造器（承 #K2-133 (甲) 之层定性 `C-*`） |

## 三、本轮顺带闭合：**西出缺口段（8 条）图纸成立**

8 条 `ye` 显式坐标（`B锚 →(B.x,ye)→(134.6,ye)`）过 `exact_gate`：**互距违例 0（最小 0.5050 ≥ 0.435）· 净距违例 0**。
⇒ 全板剩余缺图收窄为：**A 侧接入段** 与 **连接器侧接入段**（x≥134 → B 锚）。

## 四、可施工性（宪法第十三条）

> 「施工队照着这张图能不能直接连？」
**西组缺口段：能**（坐标已给 · 已过闸）。**全板：不能**（缺 A 侧与连接器侧接入坐标）⇒ **全板图纸层缺图，不作里程碑、不得开工**。
**不动证明**：本件**不搬任何对象**（未烙板 · 未改任何网几何）。

## 五、复现

```bash
AppDir/usr/bin/python3.11 k2/tools/k2_p4_b2_board_in5_model_dump_v1.py k2/hw/k2_v4_8L.l8.kicad_pcb /tmp/opencode/model_l8.json
python3 K2_R313_CERTIFICATE_CHECKER_v59.py /tmp/opencode/model_l8.json                    # 复现 6/5（证书原读数）
python3 K2_R314_WMAX_EXACT_AND_CERTIFICATE_REFUTATION_v1.py /tmp/opencode/model_l8.json /tmp/opencode/r314.json   # 反证：8 ⇒ U≤16
python3 k2/tools/k2_p4_b2_in5_lane_router_v3.py --model /tmp/opencode/model_l8.json --out /tmp/opencode/wo_full16.json   # 单发：9/32（负结果）
```

## 六、边界

冻结四源不改 · `criteria/` 只读 · 未烙板 · 未派 WORKER · 未改生成器/SPEC/原理图 · 临时仅 `/tmp/opencode` · 未写 `.omo/supervision/**` · 未放松 DRC · 未缩口径 · 未以有界搜索冒充证书 · **禁 HOLD/停等结案**。

—— ENG（ARCHER）· 2026-09-22 · k2 `b368b7d` · owner 闸口 **0** · 待裁 **0**
