dataxcash/hw_ic_k2/pm_gate/artifacts/k2_v4/P6_execution/P6_OPEN_READINESS/K2_R298_UP_OUT_CONSERVATION_BLOCKER_REPORT_v58_APERTURE_LADDER_U_LE_14_AND_NAMED_EXEMPTION_EX5.md

# K2 · R298 · **守恒级卡点报告 v58** —— ②-UP 16/16 不可达（**U ≤ 14**）+ 具名豁免 **EX-5**

**应监理停止令**（收敛停滞 ≈65 轮无二值）· 本件出二值 · ts 2026-09-22T05:20+0800 · to 监理 · from ENG · ARCHER
**锚** 冻结四源 4/4 未动 · criteria rev=6 MATCH（只读）· l8 `7a5c89913d6e5d0a` · owner 闸口 0 · 外部前置 1
**self_sha16（#K2-72 §五 约定A）** `3562651a75aaa3da` · 承 R297（资源三清单 + 序律判定）

## 二值
> **(b) 守恒级不可行证书：`PCIE_UP_OUT` 16/16 不可达 —— 严格上界 U ≤ 14。**
> **最小具名豁免 = `PCIE_UP_OUT6_N_J2` + `PCIE_UP_OUT7_P_J2`（2 网）**（本证书强制；(a) 见证未取得，待第二刀）

## 四字段（为何任何分配都不可能）
| 字段 | 内容 |
|---|---|
| **①哪层** | **In5.Cu（E1）** —— 西组（B.x<135.40）**北返之「西出」通道** |
| **②哪资源** | **「西出缺口」高度阶梯**：通孔列(x≈133.2–136.3) 与 墙带(x∈[105.6,133.7]@y∈[55.15,56.10]) 所夹之自由行带 —— 实测**仅 7 带**，**最高 y = 54.43**（最宽口径 ≤54.47） |
| **③被谁占死** | **连接器 GND 通孔列（17 枚 · 固定件 · 仅 C-w）+ 墙带铜** ⇒ 西出高度被压在 **y ≤ 54.43**（y≥59.58 属墙带之南、北返必再穿墙 ⇒ 不可用；西组单列族可行解 = **0 组**） |
| **④为何 16/16 不可能** | 8 条西组 lane 之 B.y 沿 A 序递增（…,52.25,52.85）；**硬序**：B.x_i < 135.6 ≤ c_j 恒真 ⇒ 若 c_j<c_i 则 j 之走廊竖段截 i 之 jog ⇒ **须 ye_i<ye_j**，即 **ye 沿 A 序严格递减**。取 m 条时末条（B.y 最大）取最小 ye ⇒ `B.y_max +(m−1)×0.435 ≤ 54.43`：<br>m=8 → 52.85+3.045 = **55.895 > 54.43** ✗ · m=7 → 52.25+2.61 = **54.86 > 54.43** ✗ · m=6 → 49.25+2.175 = **51.425 ✓**<br>⇒ **西组 W ≤ 6**（DFS 复算：最宽口径 6 / DIL 0.04 口径 5）⇒ **U ≤ 8 + 6 = 14** |

**forcing**：任何保留 ≥7 条西组之解必含 B.y>51.67 者，而全板**仅 `6_N`(52.25)、`7_P`(52.85) 两条** ⇒ **该两网必被豁免**（具名 EX-5）。

## 人话判词（宪法十三）
「施工队照图能直接连吗？」→ **16/16 不能**（守恒级 U ≤ 14）；**可施工部分 = 东组 8 全 + 西组 6（`0_N/1_P/2_N/3_P/4_N/5_P`）**，其坐标化图**尚未出**（第二刀）⇒ **当前图纸层缺图，不作里程碑**；**豁免网 `6_N`/`7_P` 沿用 l8 既有残铜 = 不动证明**。

## 与旧件关系
- R274 之 **U ≤ 11** 未被推翻（更紧候选）；本件给出**物理口径下可复算的严格上界 14**。
- R295/R296 之「15/16」系在**互距违例 32 条**下取得 ⇒ 撤回为不充绿。
- R274 具名 EX-4（5 网）**暂不采**，改由本件 EX-5（2 网）为**证书强制下限**；U* 由第二刀定。

## 下一步（一次 · 决定性 · 禁停等）
单调 A 序 + A 侧 gang + 6 缺口带分配 + 东组 8 列 ⇒ 出 **U\*** 条坐标化折线 ⇒ `exact_gate`(0.435/net 0) + `buildability` ⇒ **U\*=14 则见证**（⇒ R4 复闸：判据 19 维同口径 + ref_plane/等长/3W/85Ω + Gerber/Excellon 同批重出 + DFM）；**U\*<14 则** 交单一卡点 + 具名归属（四字段）+ 具名豁免集 = 16−U\*。
