dataxcash/hw_ic_k2/pm_gate/artifacts/k2_v4/P6_execution/P6_OPEN_READINESS/K2_R289_UP_OUT_BINARY_CERTIFICATE_FINAL_U11_AND_BLOCKER_REPORT_v57.md

# K2 · R289 · ②-UP **二值（终稿）**：16/16 不可达（U ≤ 11）+ 《守恒级卡点报告》v57

**件**：`K2_R289_..._BLOCKER_REPORT_v57.json`（sha16 **`b853a728f658f96b`**）· 应监理停止令

## 0. 二值
**(b) 守恒级不可行证书：`PCIE_UP_OUT` 16/16 不可达（U ≤ 11）** —— 三路互证：
1. **枚举**：拓扑导出列序（单调=A 序）+ 逐事件横截跨越容量（物理 0.53）⇒ 精确枚举 2^16 ⇒ **U_max=11**
2. **构造**：独立的逐事件列分配 ⇒ **11/16**（同数）
3. **实测根因**：零候选 8 条 ≡ **8 条西组网**（细网格 cell 0.005 确认非 alias）

## 1. 《守恒级卡点报告》v57（四字段）
| 问 | 答 |
|---|---|
| **①哪层** | **几何刚性层 — 北区「西出」隔断层**：8 条西组须**西行穿越连接器通孔列（x≈133.2–136.3）**方能达其 B 锚（x 127.01–131.65） |
| **②哪资源** | **北区东西向穿越口（通孔列缺口）× 东通道 gap 列位**（二者联合：gap 列须与该 lane 全高自由且与「西行高度」相容） |
| **③被谁占死** | **未被占死但被固定件限位**：连接器通孔列 **GND 17（固定件·只能 C-w）** + 缝合孔 **135** + 他网 In5 **88 段**；自网 **249 段可 no-move 全转拆** |
| **④为何任何分配都不可能** | 单层不可交叉下，西组 8 条须全部穿越有限宽缺口且各 lane gap 列须全高自由 ⇒ **精确枚举给 U=11**（**至少 5 条无法共存**）；**非**容量型（与顺序无关容量余量 **+11**）· 系**列位/穿越口组合刚性** |

> 人话：**16/16 不能**（U ≤ 11）；**11/16 + 具名豁免 EX-4（5 网）** 为几何刚性口径；可施工性待西组两列路形出图（当前**图纸层缺图**）。

## 2. 唯一剩余动作
**西组 8 条改「两列路形」**（gap 列 → 隔断缺口处西行 → 在 x_B 列北行；l8 实测同构）+ 东组单列 ⇒ **联合 DP**（西组增「西行高度」变量）⇒ `exact_gate`（新装置）⇒ 见证或单一卡点+具名归属。

—— ENG（ARCHER）· 2026-09-22 · k2 `46b0659` · rev=6 MATCH · owner 闸口 0
