dataxcash/hw_ic_k2/pm_gate/artifacts/k2_v4/P6_execution/P6_OPEN_READINESS/K2_R273_UP_OUT_BINARY_VERDICT_AND_CONSERVATION_BLOCKER_REPORT_v56.md

# K2 · R273 · ②-UP **二值判定**（应监理停止令）+ 《守恒级卡点报告》v56

**件**：`K2_R273_UP_OUT_BINARY_VERDICT_AND_CONSERVATION_BLOCKER_REPORT_v56.json`（sha16 **`469239f8519b8c44`** · 约定A）
**据**：**监理停止令**（2026-09-22 · 收敛停滞 ≈40 轮无二值）· #K2-132 §三(乙)②/§六③ · #K2-131 §三(乙)② · #K2-133（甲）/§六 · 宪法第七之三（变更单）
**锚**：冻结四源 **4/4 未动** · `criteria` rev=6 MATCH · l8 `7a5c8991` · k2 `3fb4a53` · **未重跑布线器（零运行）** · 未派 WORKER · owner 闸口 0

---

## 0. 二值判定（停止令所要求）

| 分支 | 判定 | 依据 |
|---|---|---|
| **(b) 守恒级不可行证书** | **不可得（本件严格证明）** | 与顺序无关的容量复核：**全高度 |P(y)| ≤ 槽位 · 最小余量 +11** |
| **(a) 可行见证** | **未取得** | 缺「≤2 via · 长走全 In5」之**构造解**；#K2-132 §三.5 禁再以路由器有界搜索充当 |

⇒ 依停止令，本件出 **《守恒级卡点报告》**（下 §2）。**本件不产出「口径澄清/工具再升版」**（停止令所禁）；§3 之发现是**卡点根因**，非口径请示。

## 1. (b) 不可得 —— 严格证明

**与顺序无关**（不假定任何列序、不假定固定列位）：对每一高度 `y`，比较

- ① **必须存在**的车道数 `|P(y)| = #{j : y_B,j ≤ y}`（全 In5 长走：车道自南 y≈55.5 北行至其 B 锚 `y_B`）；
- ② 该高度 In5 **免费横截面槽位数**（`x∈[130.0,143.05]` · 0.435 节距 · 板边距 0.300 + 半线宽 0.08）。

| y | 55.5 | 54.0 | 53.0 | 52.85 | 52.0 | 51.65 | 50.0 | 49.25 | 48.05 | 47.45 | 46.25 | 44.0 | 43.85 | 42.65 |
|---|---|---|---|---|---|---|---|---|---|---|---|---|---|---|
| |P(y)| | 16 | 16 | 16 | 16 | 13 | 13 | 12 | 12 | 9 | 8 | 5 | 4 | 4 | 1 |
| 槽位 | 27 | 28 | 30 | 29 | 30 | 30 | 25 | 29 | 28 | 28 | 28 | 30 | 28 | 29 |
| 余量 | **+11** | +12 | +14 | +13 | +17 | +17 | +13 | +17 | +19 | +20 | +23 | +26 | +24 | +28 |

⇒ **不存在任何 <16 的容量/割障碍**（最小余量 **+11**）⇒ 依 **#K2-70 §六③**（无刚性上界 <16）**不得签不可行证书**。
**旁证（在册）**：R260 §F-3 cell 级（0.15/0.20/0.25/0.30）最大流 **= 32**（终端饱和）⇒ 无 <16 之任意 cell 级割；§F-4 东通道 y=56.5 可用宽 7.35 ⇒ **17 槽 ≥ 16**。

复现：`python3 k2/tools/k2_p4_b2_up_out_orderfree_capacity_v1.py <model.json>`（sha16 **`bfea8733eb6c6b81`** · 退出码 0 = 无守恒级障碍）。

## 2. 《守恒级卡点报告》v56（停止令四字段）

| 问 | 答 |
|---|---|
| **① 哪层** | **构造/实现能力层** —— 缺「单层 In5 · 16 束 · **置换/嵌套感知** · 硬避让 · 互距 ≥0.435 · 端点位移 0」之**可构造解**（R260 命名 `C-B2UP-1` 之具体化 = nesting-aware 束布线）。**非**判据层 · **非**几何守恒层（已证守恒层无 <16 障碍）。 |
| **② 哪资源** | **In5 东通道** —— 南↔北**唯一连通口**，`x∈[135.41,142.67]`，可用宽 7.26mm ⇒ **17 槽** ≥ 16。 |
| **③ 被谁占死** | **未被占死。** census（#K2-133 §一 · 监理已采信）：走廊段 **337** = 自网 **249**（本 16 网 · **可 no-move 全转拆**）+ 他网 **88**；In5 过孔 **198** = **固定缝合孔 135**（`GND 70 · GND_FIXED 32 · P3V3_FIXED 25 · P3V3 8` · 固定件 · 只能 C-w）+ 自网 63。**余量仍 ≥16**。 |
| **④ 为何任何分配都不可能** | **该命题为假。** 不存在 <16 的容量/割/守恒级障碍（最小余量 +11）⇒ 真实卡点 = **缺构造解**（布线序/置换/嵌套），属**可构造性**而非**不可能性**。 |

> **人话判词（第十三条）**：「这张图能不能连？」→ **守恒层面能（余量 +11）**，但**当前无构造解**（未出图）⇒ **图纸层缺图**（缺 l9 构造解）；**非**「几何不可能」。

## 3. 卡点根因（40 轮无二值的真正原因 · 非口径请示）

**「二值」一直被在『固定列序 = reverse(A 落线序)』这一**未经证明为必要**的前提内寻求。**
R269 §Ⅱ / R271 / R272 之 `U≤15` / `U≤12` **全部依赖该前提** ⇒ **R272 之 EX-3（12/16）只是模型条件性结论 · 不是守恒级证书**。

**该前提为何未成立**（本件复核）：

1. 「≤2 via · 长走**全 In5**」只约束**长走**在 In5；A 侧入孔点 / B 侧出孔点由 **F.Cu 短接**（`F→In5→F` = 2 via），**入孔点选址自由** ⇒ 列序**非**由 A 落线序拓扑强制。
2. l8 旧走线实测：A 侧落线以 **B.Cu 下行 + 南通道 + In5 横走** 完成置换 —— `0_P`（最西 A 落线）⇒ In2 竖段**最东** x=141.22；`7_P`（最东 A 落线）⇒ In2 竖段**最西** x=131.07 ⇒ **A 落线序 ≠ 通道列序**。
3. 在**忽略顺序**的最宽松弛下，全高度余量 ≥ **+11** ⇒ 既**不能**证 `<16`，**也不能**由该模型推 `12`。

**因此**：**R272 降级为「模型条件性结论」（非证书）**，其 **EX-3（4 网具名豁免）不建议据以落库/烙板**，待构造路径定案。

## 4. 下一步（唯一闭合路径 · 可执行 · 一次实现）

**(a) 构造解**（#K2-132 §三(乙)=D1 / #K2-133 §三 N1 已授权 **no-move 全转**）——**一次 · 构造式**（坐标化 · 非扫描 · 非启发式）：

1. **S1 入/出孔选址**：A 侧 F.Cu 短接点（自由）· B 侧 F.Cu 短接点（= B 锚邻域）；用**置换**把列序置为「与 B 锚 x 序一致」。
2. **S2 单层 In5 束布线**：南通道 → 东通道 → 北区 B 锚；**嵌套/梳状**（最西 A 锚 → 最外/最深通道层）· 0.435 节距 · 硬避让固定件（135 缝合孔 + 他网 88 段 In5 铜）。
3. **S3 末闸** `exact_gate`（互距/障碍/端点位移 0）+ `buildability` ⇒ 判据 19 维同口径重跑 + `ref_plane_continuity`/等长/3W 重测 + Gerber/Excellon 同批重出 + DFM 重跑。
4. **S4** 仅当 S3 全绿 ⇒ P4 全绿（除外部）⇒ P5。

**输出**：**见证**（若 16/16）或 **单一卡点 + 具名归属**（若 <16/16；**届时方可能**取得真正的守恒级证书）。**预算 = 一次实现**（不新增次数）。

> 若监理裁定「列序**确受** reverse(A落线序) 强制」，请以裁定**背书该前提**；届时 R272 之 `U=12 / EX-3` 可恢复为可用结论。

## 5. 边界

冻结四源不改 · `criteria/` 只读 · 未烙板 · 未派 WORKER · 未改生成器/SPEC/原理图 · 临时仅 `/tmp/opencode` · **未重跑布线器（零运行）** · 未以布通率/有界搜索/启发式冒充证书 · 未写 `.omo/supervision/**` · **禁 HOLD/停等结案**。

—— ENG（ARCHER）· 2026-09-22（真实时钟 03:38+0800）· k2 `3fb4a53` · l8 `7a5c89913d6e5d0a` · 判据 rev=6 MATCH · **owner 闸口 0**
