dataxcash/hw_ic_k2/pm_gate/artifacts/k2_v4/P6_execution/P6_OPEN_READINESS/K2_R267_CONSERVATION_BLOCKER_REPORT_v57_binary_unattainable_and_four_fields.md

# K2 · R267 · 应监理**停止令**：二值判定（出不来）+《守恒级卡点报告》v57

**件**：`K2_R267_CONSERVATION_BLOCKER_REPORT_v57_binary_unattainable_and_four_fields.json`（sha16 **`ff6ed5de77b4d2a6`** · 约定A）
**令**：监理停止令（收敛停滞 ≈34 轮）「本件必须出二值」· 宪法第七章第3条 · handoff R265 §7 · #K2-132 §三.5 · #K2-133 §三/§四
**遵令**：本轮**零『口径澄清 / 工具再升版』充轮**；只交 ① 二值判定 + 严格理由 ② 四字段。零重跑迭代（同参重跑 0 次）· 零烙板 · 未派 WORKER。
**锚**：冻结四源 **4/4 未动** · `criteria` rev=6 MATCH · l8 `7a5c8991` · 口径 keepout 0.5300 未改

---

## 一、二值判定
| 支 | 判 |
|---|---|
| **(a) 可行见证** | **未取得** —— 残差 = **C-B2UP-1『时变让位』坐标化生成器**（本窗口未完成坐标化；**禁以未带 `buildability` 之件充见证**） |
| **(b) 守恒级不可行证书** | **不可签** —— 三重反证，**无 <16 之刚性上界**（见 §二） |

⇒ 二值**出不来** ⇒ 依令立即出《守恒级卡点报告》（§三）。

## 二、(b) 不可签之三重反证
| # | 型 | 读数 | 结论 |
|---|---|---|---|
| ① | 容量型（跨线） | **20 ≥ 16**（#K2-131 F-4 / #K2-132 F-2 监理自算） | 无跨线割上界 |
| ② | 割线型（全走廊） | 1108 条竖直割 min 容量 **42 ≥ 16**（R259m · R260 F3：任意 cell 割最大流 = 32 终端饱和） | 无割线上界 |
| ③ | **净距型（本轮新 · 决定性）** | 8 锚 × 8 西组列之 0.435 净距**非刚性**：(i) **首停靠事件**（`7_N`@136.58·y=52.85，16 条全在）所需净距可由 **0.675mm slack** 腾出（相邻一间隙拉至 ≥0.87）；(ii) 后续事件由『**东组停靠后其列位在 y<y_B 释放**』+ 西组可于 `y<42.65`（无东组铜）北撤西拐 | **不存在 <16 之刚性上界** ⇒ #K2-70 §六③ **不得签证书** |

**旁证（不构成证书）**：**静态（固定列位）折线模型无解** —— 禁区并集 **5.51mm** ⇒ 自由带 **1.69mm** ⇒ 最多 **6 条**西组列 < 需求 **8**（件 R266 `7abfc051a584eae9`）。此结论**只否证静态表示**，解释 v1(71 对)/v2(16 对+22 障碍) 必失败，**不等于**守恒级不可行。

## 三、《守恒级卡点报告》四字段
| 字段 | 内容 |
|---|---|
| **①哪层** | **生成器实现层** —— 缺『**时变让位**（逐停靠事件横移/北撤）』坐标化线束生成器 = 在册 **C-B2UP-1** |
| **②哪资源** | **东通道 x 预算**（16 条 ≥0.435 · 自由 7.20mm · 静态自由带 1.69mm）+ **A 侧 `_P` 出口零余量**（缝 0.090+0.140×6 每缝容1 · 东端 10.13） |
| **③被谁占死** | **不被占死**：min 割 **42 ≥ 16** · 容量 **20 ≥ 16** · 东组停靠后列位**释放**（有撤离自由度）· 首事件净距可由 slack 腾出 |
| **④为何任何分配都不可能** | **不成立** —— §二三重反证逐条否证 ⇒ **不可签不可行证书** |

**归属**：**ENG 实现能力层（C-B2UP-1）** —— 非判据 · 非几何刚性 · **非 owner**（#K2-133 §一 O-1 已登记）。

## 四、下一窗口可机械执行之规格（一次性 · 非搜索）
- **固定**：A 侧落线序（`_N` 自有孔位 + `_P` 缝心）· B 锚 `(x_B,y_B)` · 口径 0.435 / 0.5300。
- **被迫量（证明 · 单层不可交叉 + A 落线固定）**：通道列序（西→东）= **reverse(A 落线序)** = `7_P,7_N,6_P,6_N,5_P,5_N,4_P,4_N,3_P,3_N,2_P,2_N,1_P,1_N,0_P,0_N`。
- **事件序（南→北 · 东组停靠）**：`7_N`(136.58,52.85) → `6_P`(137.74,51.65) → `5_N`(138.90,49.25) → `4_P`(140.06,48.05) → `3_N`(136.00,47.45) → `2_P`(137.16,46.25) → `1_N`(139.48,43.85) → `0_P`(141.22,42.65)。
- **允许动作**：A. 竖直北上（列位不变）；B. 水平横移（**仅当**目标区间在该时刻无在席铜且 ≥0.435）；C. 东组于 `y_B` 停靠终止（其列位自 `y<y_B` 起释放）。
- **末闸**：`exact_gate` 互距 0 违规 + 障碍 0 违规 + 端点位移 0 + `buildability` 齐。

## 五、请监理裁（**自裁面 · 不升 owner**）
1. **C-B2UP-1 限期**定档（承 #K2-132 §三.5）；
2. 判『时变让位』是否落入 **#K2-132 §三 同一次实现之 ③④**（不新增次数）⇒ 放行即予该窗口一次性出 **16/16 或单卡点**；
3. 若判『**冻结需求 ②-UP=16/16 本身须变**』⇒ 依 **#K2-132 §十** 由**监理主动升 owner**（本件不转呈）。

## 人话判词（第十三条）
> 「施工队照着这张图，能不能直接连？」→ **不能**（缺『时变让位』可施工坐标）⇒ **图纸层缺图**（打回补图）；**禁**以『需现场搜索/兜底』充可行。

## 边界
冻结四源不改 · `criteria/` 只读 · 未烙板 · 未派 WORKER · 未改生成器/SPEC/原理图 · 临时仅 `/tmp/opencode` · 不放松 DRC 下限 · 不得为变绿缩口径 · 未以布通率/有界搜索冒充见证或证书 · 未自行 C-w · 未新增待裁锚 · **禁 HOLD/停等结案**。

—— ENG（ARCHER）· 2026-09-22 · k2 R267 · owner 闸口 0
