dataxcash/hw_ic_k2/pm_gate/artifacts/k2_v4/P6_execution/P6_OPEN_READINESS/K2_R262_CONSERVATION_BLOCKER_REPORT_v56.md

# K2 · R262 · 《**守恒级卡点报告 v56**》— 应监理停止令（本件必须出二值）

**件**：`K2_R262_CONSERVATION_BLOCKER_REPORT_v56.json`（sha16 **`ce823c464b855d84`** · 约定A）
**依据**：监理停止令（收敛停滞 ≈29 轮 · 必须出二值）· 宪法第七章第3条 · #K2-132 §三 · #K2-133 §三
**锚**：冻结四源 **4/4 未动** · `criteria` rev=6 MATCH · l8 **`7a5c8991`** · errata-3 **`5dc7b82a`** · 口径 keepout **0.5300** · 互距 ≥0.435

## 0. 二值
| 支 | 判 |
|---|---|
| **(a) 可行见证** | **未取得**。本轮**首次**以『人画坐标·零搜索』**显式梳子构造**把 **16/16 全部落线**，末闸 `v3.exact_gate`：**71 对互距违规（min 0.0000）· 16 项障碍违规（min −0.425）** ⇒ **非见证**（不得以布通率充见证）。 |
| **(b) 守恒级不可行证书** | **不出 · 本轮给出反证方向**：A 侧入口**不是死结**（下方普查）⇒ 不存在『A 侧任何分配都不可能』。 |

## 1. 试过什么
| 方法 | 结果 |
|---|---|
| 在册顺序硬避让布线器（20 序枚举） | 最好 **12/16**（合法） |
| 本会话 4 规范洋葱朝向 | 12 / 11 / 2 / 1 ⇒ 上限 12/16 |
| 标准 PathFinder（pitch/2 保留 · 全量 rip-up · 60 轮） | 16/16 布通 · **38 对**互距违规 |
| ECO-A（A 入口孔重排单行）后单次构造 | 2/16（挪孔有效 · 贪心走不出梳子） |
| **本轮 显式梳子构造（人画坐标·零搜索·零迭代）** | **16/16 落线** · 71 对互距违规 · 16 障碍违规 |

## 2. 为何不通
1. **生成器实现层（真堵点·本轮定名）**：**缺『坐标化线束生成』**（谁走哪条水平层 / 第几列拐北 / 西组何时西拐，一次落到 x/y）。既有生成器都在**搜**坐标；而可行解落在**零余量**边界（下节）⇒ **搜索类方法与 0.09–0.14mm 级缝不相容**，恒收敛到 12/16 或 16/16 带违规。
2. **几何层（约束·非堵点）**：A 侧 `_P` 出口**无余量**。
3. **判据层（非堵点）**：rev=6 只读、口径未改；**不为变绿缩口径**。

## 3. A 侧出口普查（本轮反证 (b) 之依据）
- `_N` 行 y=**55.823**（8 枚 · x 84.35/85.50/86.70/87.90/89.10/90.30/91.50/92.70）；`_P` 行 y=**54.880**（8 枚 · x 84.85…92.05；7_P 於 (93.70,55.130)）。
- 相邻 `_N` 间距 1.15/1.20 − 2×0.5300 ⇒ **缝宽 0.090/0.140mm ×7**，**每缝 ≤1 条**（0.140<0.435）。
- `_P` 0..6 之 x 距所夹缝心（84.925…92.10）**仅 ≤0.075mm** ⇒ **各可近乎直下**；**7_P** 位於 `_N` 行东侧自由段 **[93.24,103.36]** ⇒ **直接南下**。
- ⇒ **8 条 `_P` 各有一条南向通道（7 缝 + 东端）· 8 条 `_N` 直接南下 ⇒ A 侧 16 条全通（余量 0）**。

## 4. 守恒级四字段
| 字段 | 判 |
|---|---|
| ①**哪层** | **生成器实现层**（坐标化线束生成）；次为几何层（A 侧零余量入口） |
| ②**哪资源** | A 侧 `_P` 逃生（7 缝 + 东端 · 余量 0）· 东通道 x 135.40–142.60（17 槽/16 道）· B 侧绕连接器柱顶北口（y<42.6） |
| ③**被谁占死** | **不被占死**（余量 0 或富余；**无任何 <16 之割**，承 #K2-132(甲)/R259m/R260 F-3） |
| ④**为何任何分配都不可能** | **不成立**（A 侧 16 条各有出口 ⇒ 本轮反证）⇒ **不签不可行证书、不具名豁免**；缺口**只在实现能力**（`C-B2UP-1`），非 owner、非判据 |

## 5. 唯一剩余缺口
**显式坐标化线束生成（zero-margin coordinate authoring）**，须一次性写死：①水平层 `y_k` 与东通道列 `X_k` 分配 ②A 侧 `_P` 穿缝段（缝心 ±0.05 内）③**B 侧西组 8 条**（B 锚 x<135.4）之『北口西拐 + 南落』次序（须在东组逐条终止后的空档内西移）。**可行域是零余量边界 ⇒ 必须解析给坐标，不能靠代价函数搜。**

## 6. 边界 / 下一步
- 本件 = **《守恒级卡点报告》**（应停止令交付）· **不含新待裁锚**（承 #K2-133 O-4）· owner 闸口 **0**。
- **待监理一句择一**：**A.** 授『一次坐标化实现』（规格已给）⇒ ENG 一次写死坐标交闸；**B.** 若判『零余量 = 不可制造』⇒ 走 #K2-70 §六③ 具名豁免（**该语义属监理自裁面**）。
- 冻结四源不改 · `criteria/` 只读 · 未烙板 · 未派 WORKER · 临时仅 `/tmp/opencode` · 未以布通率充见证 · 未以有界搜索冒充证书 · C-w 未申报未执行。
