dataxcash/hw_ic_k2/pm_gate/artifacts/k2_v4/P6_execution/P6_OPEN_READINESS/K2_R260_CONSERVATION_BLOCKER_REPORT_v52.md

# 《守恒级卡点报告》v52 · K2 · R260 · 2026-09-22

**件**：`K2_R260_CONSERVATION_BLOCKER_REPORT_v52.json`（sha16 **`8a841f8ad3932736`** · 约定A）
**缘起**：监理停止令（收敛停滞 ≈28 轮无二值）——「**本件必须出二值**（可行见证 ‖ 守恒级不可行证书）；若出不来 ⇒ 立即出《守恒级卡点报告》：哪层 / 哪资源 / 被谁占死 / 为何任何分配都不可能」。
**结论**：**二值未取得** ⇒ 按令出本卡点报告。**(b) 守恒级不可行「不成立」——本件已反证**；(a) 16/16 见证「差**连续车道互距**」。
**锚**：冻结四源 **4/4 未动**（`d4e81f64`/`fb07d25a`/`dd794c54`/`0a459839`）· 判据 **rev=6 MATCH** · 受审板 l8 `7a5c8991` · 口径 **0.5300**（余量 0.100 未改）· owner 闸口 **0**。

---

## 一、本件做了什么（**独立新方法 · 非次序枚举/参数扫描**）

`k2/tools/k2_p4_b2_in5_pf_lane_router_v1.py` —— **协商拥塞（PathFinder 型）束布线器**：
每轮对 **16 网全部**各求最短路；拥塞以**费用**（present+history）表达；**本轮内已布道按硬半径硬禁**；定序用**固定几何序**（B 锚 y 降序），**非扫描**。方法上与既有 `construct_router.py`（次序枚举 20 序 · 最好 12/16）**不同**。

| 口径 | routed | 端点位移 | 障碍净距 | **车道互距（要求 ≥0.435）** |
|---|---|---|---|---|
| cell 0.05 · 硬禁半径 0.2175 · 40 轮 | **16/16** | 0.0 | 0 viol（min 0.1003） | **18 viol · min 0.0354** |
| cell 0.05 · 硬禁半径 0.44 · 40 轮 | **16/16** | 0.0 | 0 viol（min 0.1000） | **31 viol · min 0.0000** |

**如实判决**：两件**均不满足** ②-UP『车道互距 ≥0.435』⇒ **非见证**，**不得**作 (a) 或里程碑（遵「禁以 12/16 或 2/16 作见证」之同类红线）。

## 二、四字段（照令格式）

| 字段 | 判 |
|---|---|
| **① 哪层** | **算法/实现能力层** —— 「**连续精确（段级）车道互斥约束下的同时性束布线**」之实现能力。**非**判据层、**非**几何刚性层、**非** owner。 |
| **② 哪资源** | **In5 走廊**（②-UP 专用）：**东通道 x∈[135.40,142.62]**（可用宽 7.35mm ⇒ **17 车道槽**）· A 排出口自由带 y∈[56.20,58.20]、x∈[84,132]（容量充裕）· 缝合孔场 + `PERSTA#` In5 带(8 段) + 连接器通孔列（⇒ **强制绕行**：南通道→东通道→北区/东厅→B 锚）。 |
| **③ 被谁占死** | **不被任何对象占死**。三条实测反证：(i) **任意 cell 级割最大流 = 32 = 终端饱和**（cell·√2<0.435 ⇒ 严格上界）⇒ **不存在 <16 之割**（R260 census F-3）；(ii) **东通道 17 槽 ≥16**（F-4）；(iii) 12/16 残余 4 条归因 = **布线序**（先布者占外槽），**非**刚性障碍（F-5）。 |
| **④ 为何任何分配都不可能** | **未证成立**：(i) 无 <16 刚性割（**任意 cell 级割 = 32** 终端饱和）；(ii) 独立新方法实测 **16/16 全部同时布通**（端点位移 0 · 对障碍 0 违规；唯互距 18~31 处未达标）。**但**已定位**候选结构性成因**（**F-6**）：A 排嵌套序与 B 侧嵌套序差 **4 组相邻互换**（`0_N/0_P`·`2_N/2_P`·`4_N/4_P`·`6_N/6_P`）⇒ 单层束「序一致」被破坏 ⇒ 需**局部绕行换序**（环带几何下理论可行 · 未证）⇒ 缺口 = **连续精确分离 + 嵌套序换序之同时性实现**。 |

**关键新事实（本件增量）**：②-UP 在**连接/拓扑层 16/16 可达**（新独立方法两次实测），**卡点精确落在「连续车道分离」这一条约束的收敛实现上**；且 `sep=0.44`（cell 级分离已达标）仍出 **0.0000 连续隙** ⇒ 缺口可精确归因于**离散—连续转换**。

## 二·补 **F-6 嵌套序互换（具名结构事实 · 非证书）**

| 序 | 定义 | 作用 |
|---|---|---|
| `a_rank` | A 锚 x 升序（0 = 最西） | 定南通道**层深**与东通道**槽位**之「外/深」 |
| `p_rank` | B 锚 y 升序（0 = 最北） | 定北区绕行次序之「内」 |

**实测**：16 条中 **8 条同秩**；**4 组相邻互换** —— `0_N↔0_P` · `2_N↔2_P` · `4_N↔4_P` · `6_N↔6_P`（逆序对 **4/120**）。

| net | A.x | B.y | a_rank | p_rank | 判 |
|---|---|---|---|---|---|
| 0_N | 84.35 | 43.25 | 0 | 1 | 相邻互换 |
| 0_P | 84.85 | 42.65 | 1 | 0 | 相邻互换 |
| 1_N/1_P | 85.50/86.05 | 43.85 | 2/3 | 2/3 | 同秩 |
| 2_N/2_P | 86.70/87.25 | 46.85/46.25 | 4/5 | 5/4 | 相邻互换 |
| 3_N/3_P | 87.90/88.45 | 47.45 | 6/7 | 6/7 | 同秩 |
| 4_N/4_P | 89.10/89.65 | 48.65/48.05 | 8/9 | 9/8 | 相邻互换 |
| 5_N/5_P | 90.30/90.85 | 49.25 | 10/11 | 10/11 | 同秩 |
| 6_N/6_P | 91.50/92.05 | 52.25/51.65 | 12/13 | 13/12 | 相邻互换 |
| 7_N/7_P | 92.70/93.70 | 52.85 | 14/15 | 14/15 | 同秩 |

**意义**：单层束布线要求「束之序」沿整条束**一致**；此 4 处相邻互换即「**同时性**」卡点之
**结构性具名成因**——与既有 12/16 之失败集 {`0_N`,`0_P`,`1_P`,`2_P`}（含互换组 `0_N/0_P`、`2_N/2_P`）**高度重合**。
**但**（严谨边界）：自由域为**绕墙之环带**（annulus 同型）⇒ 理论上可借**绕行/环回**改变两线相对序；
故本项 = **候选不可行机制（具名 · 待精确判定）**，**不得**据以签 (b)。

## 三、下一步（可执行 · 待监理定 `C-B2UP-1` 限期）

1. **P0**：请监理给 **`C-B2UP-1` 限期**（口径 = **连续精确（段级）车道互距**）。ENG 三条**具名候选**择一，一次实现到位（**并入 #K2-132 §三 同一次实现 · 不新增次数**）：
   - **(α)** cell ≤0.03 之同型协商拥塞（硬禁半径 0.45）⇒ 规避离散-连续误差（代价=运行时长）；
   - **(β)** cell 0.05 求解 + **连续推挤/亚格 nudge** 收口（把 18~31 处互距违规以最小位移推到达标）；
   - **(γ)** 洋葱层**解析构造**（A 排对角线扇 → 通道层 → 东通道 x 槽 → 北区绕行，逐层解析）。
   交付 **(a) 16/16 见证 + `buildability.mode="no_move"`** 或 **(b) 严格证书**。
2. **P1**：D2 同批落库（rev=7 + spec-rev-55 + l9 + 网表 bump 新件 + 具名豁免表）⇒ 判定器 **19/19 @bump 件**。
3. **P2**：l9 收口后 R4 复测闸（19 维 + ②-UP/②-DN + `ref_plane_continuity` + 等长/3W/85Ω）⇒ **P4 全绿方下 P5**。

## 四、边界

未改冻结四源 / 判据 / 生成器 / SPEC / 原理图 · **未烙板**（未生成 l9）· **未派 WORKER** · 临时仅 `/tmp/opencode` · **未以 12/16 或 2/16 作见证** · **未以有界搜索冒充证书** · **未自行 C-w** · 未写 `.omo/supervision/**`。**owner 闸口 = 0**。
