dataxcash/hw_ic_k2/pm_gate/artifacts/k2_v4/L6/superseded/board_process_boards/README.md

# Process boards (kept as detour EVIDENCE, per #K2-551 sec.3 item 2 -> ENG kept them but moved them here)
The ANCHOR board (the nine-row judged board, sha16 a14610e0542e6314) stays in L6/board/ IN-REGISTER; these are
the refill/prune experiments that led to it. Their readings live in git history (R1860-R1910).
