dataxcash/hw_ic_k2/pm_gate/artifacts/k2_v4/L2/render/l13_top.png

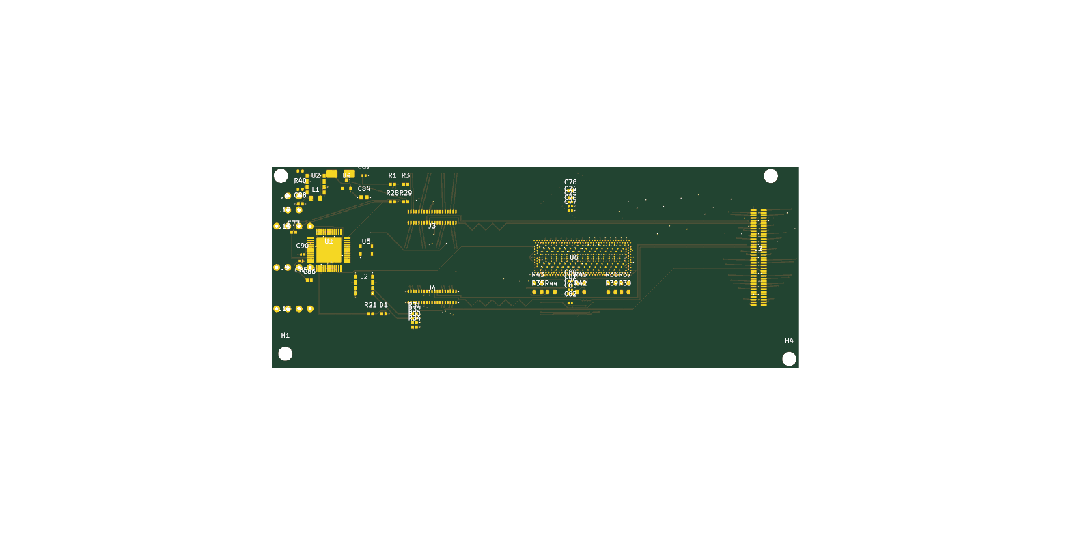
pm_gate/artifacts/k2_v4/L2/render/l13_top.png
