dataxcash/hw_ic_k2/pm_gate/artifacts/k2_v4/L6/evidence_visual/m7t6_bottom.png

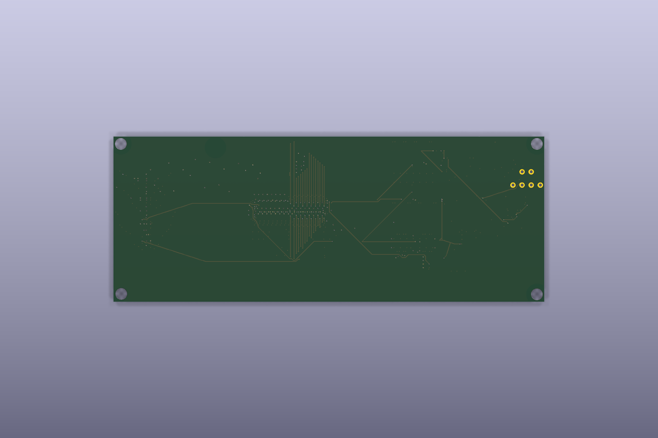
pm_gate/artifacts/k2_v4/L6/evidence_visual/m7t6_bottom.png
