dataxcash/hw_ic_k2/pm_gate/artifacts/k2_v4/L6/evidence_visual/m7t8a_iso.png

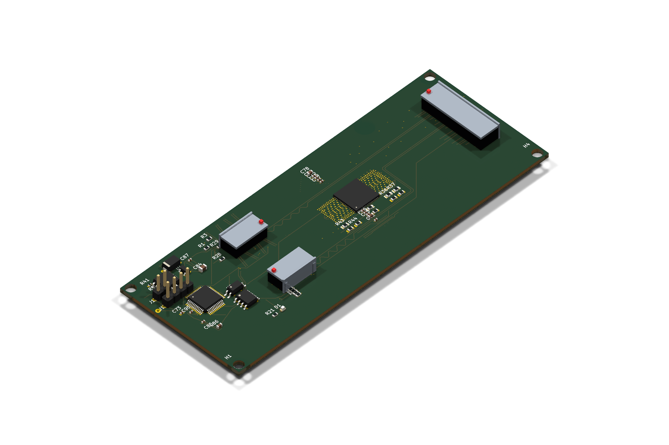
pm_gate/artifacts/k2_v4/L6/evidence_visual/m7t8a_iso.png
