dataxcash/hw_ic_k2/pm_gate/artifacts/k2_v4/P6_execution/P6_OPEN_READINESS/DEFECT_D1_LED_POLARITY_EVIDENCE_20260921_v1.png

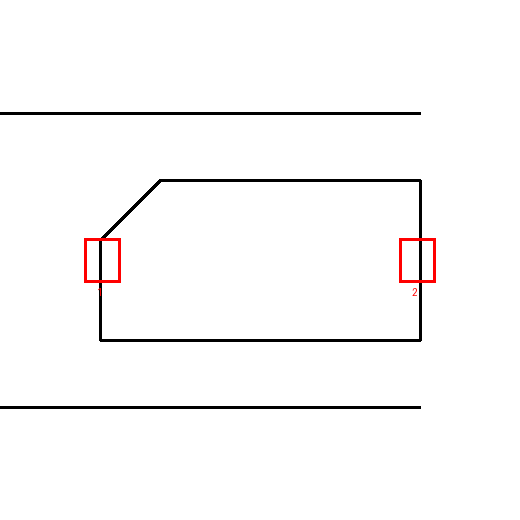
pm_gate/artifacts/k2_v4/P6_execution/P6_OPEN_READINESS/DEFECT_D1_LED_POLARITY_EVIDENCE_20260921_v1.png
