dataxcash/hw_ic_k2/pm_gate/artifacts/k2_v4/P6_execution/P6_OPEN_READINESS/K2_R780_FINAL_ROUTING_DRAWING_v1.png

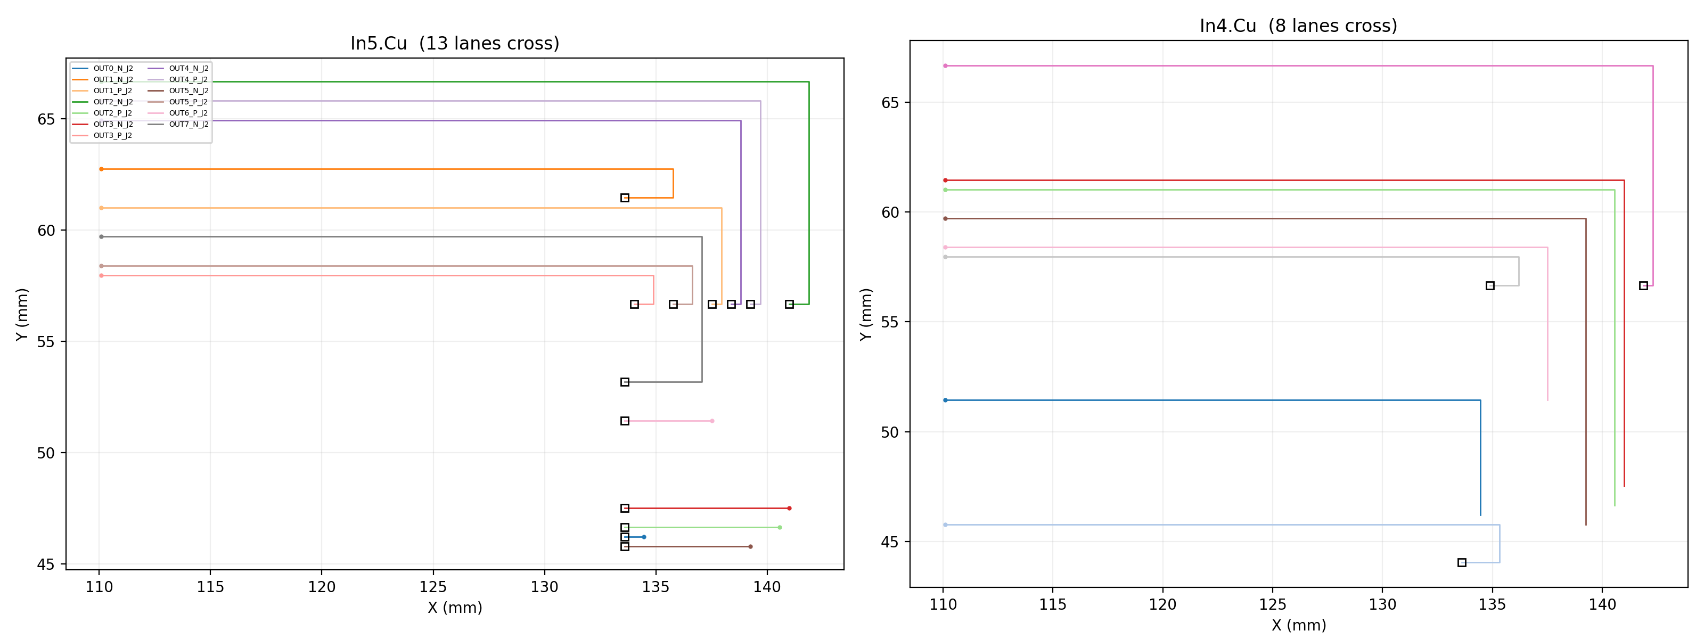
pm_gate/artifacts/k2_v4/P6_execution/P6_OPEN_READINESS/K2_R780_FINAL_ROUTING_DRAWING_v1.png
