dataxcash/hw_ic_k2/pm_gate/artifacts/k2_v4/P6_execution/P6_OPEN_READINESS/P5_V7_TI_SNLS683_P16_THERMAL_20260921_v1.png

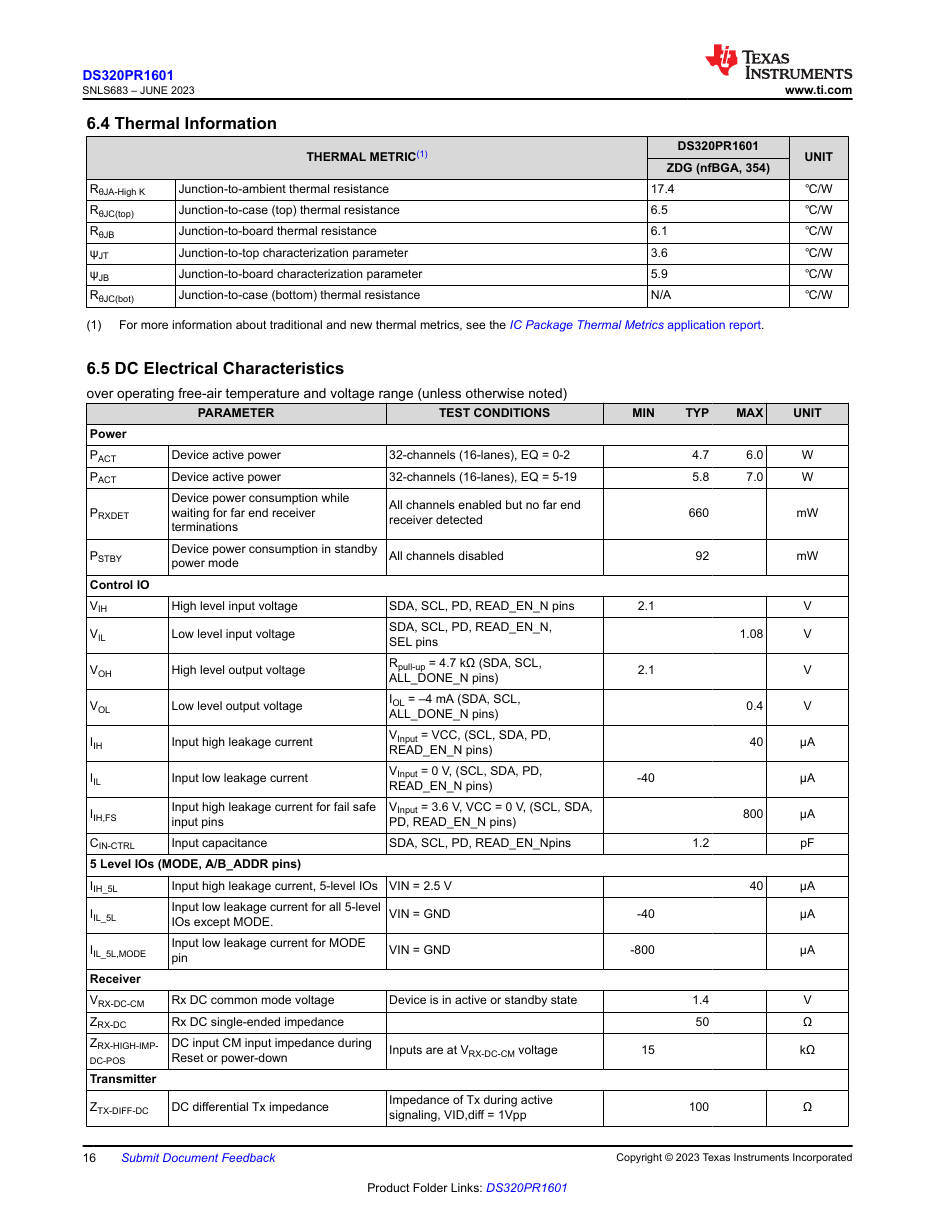
pm_gate/artifacts/k2_v4/P6_execution/P6_OPEN_READINESS/P5_V7_TI_SNLS683_P16_THERMAL_20260921_v1.png
