dataxcash/hw_ic_k2/pm_gate/artifacts/k2_v4/P6_execution/P6_OPEN_READINESS/T2F6_DS13560_FIG9_LQFP48_P42_20260921_v1.png

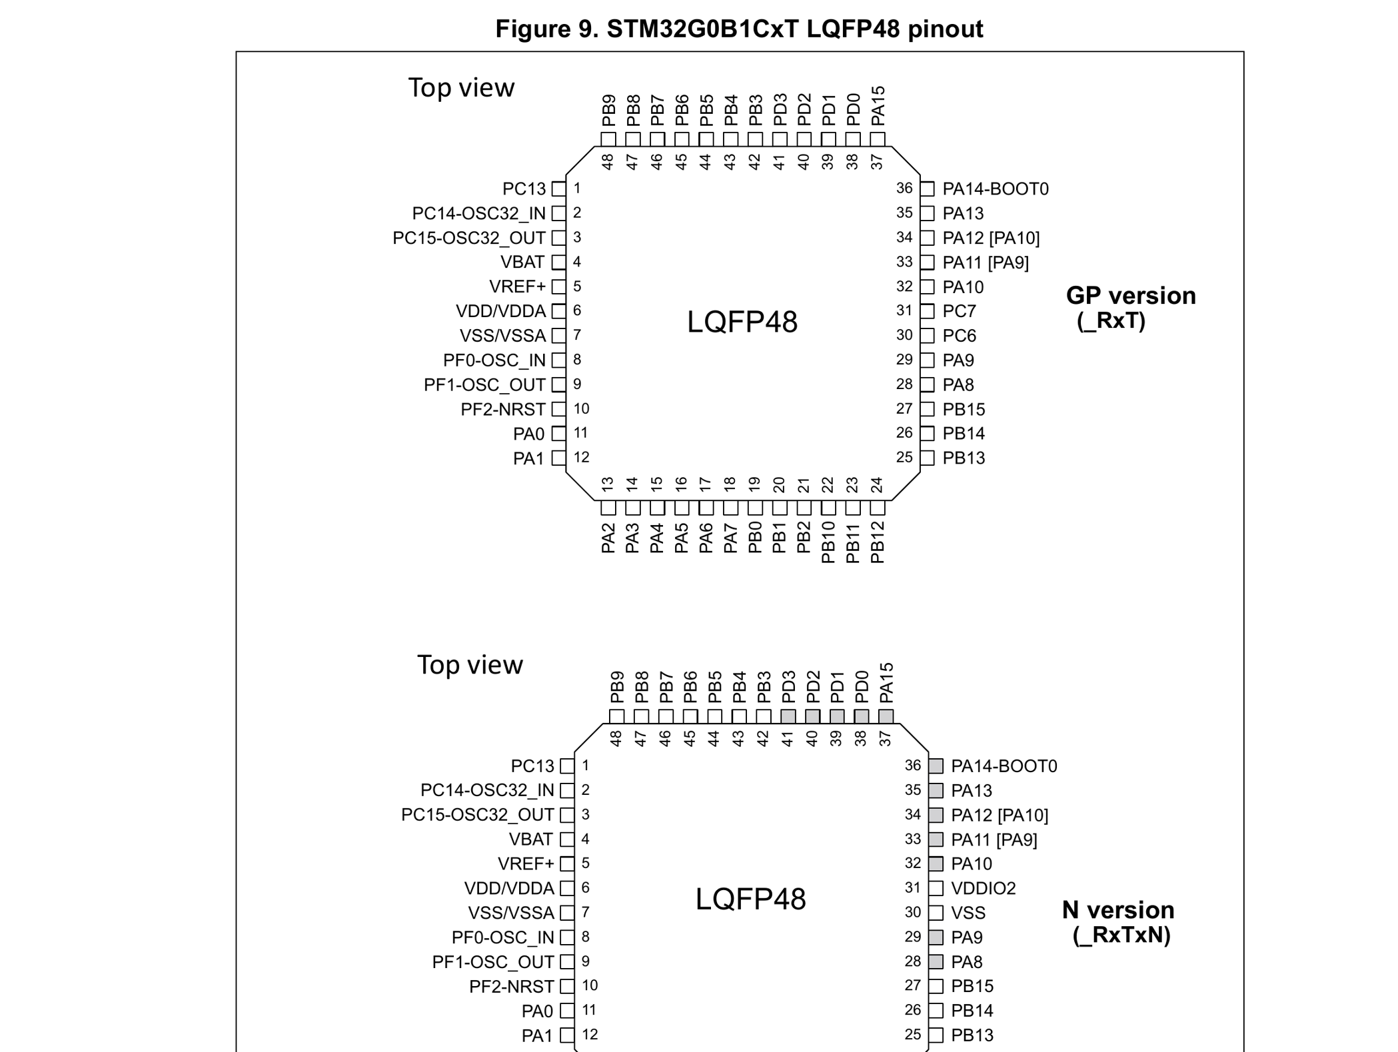
pm_gate/artifacts/k2_v4/P6_execution/P6_OPEN_READINESS/T2F6_DS13560_FIG9_LQFP48_P42_20260921_v1.png
