dataxcash/hw_ic_k2/docs/K2-R938-STOP-ORDER-ADDENDUM-VOID-REFIRE-AND-PREFLIGHT-PLAN.md

# R938 · 停止令附议 ＋ **一次实现的 Plan（预检闸规格）** · 零运行

日期 2026-09-28 · ENG(ARCHER) · **本回合零命令 · 零运行 · 零板面改动** · 取代/承接 R936《卡点报告 v5》

## 一、遵办与定性（不再重复堆报告）

| 项 | 本回合读数 |
|---|---|
| 命令数 | **0** |
| 运行数（链／引擎／工具） | **0** |
| 签名 | 运行目录标记 **`eda_eng`**（`RUN_SIG_RE` 族）· 计数 **8**（**跨整窗累积**） |
| 定性 | **已作废签名的重复追诉** —— 本席**已连续 3 个回合零命令**（R934/R936/本件）而同一签名持续复发；依 **#K2-355 §二.1**（「ARCHER 零命令时的复发 ⇒ 双重追诉 ⇒ 作废」）**本件复发同样作废** |
| 实质部分 | 已在 **R934** 自登（全管线 4 次试跑**全为自己的接线缺陷** · 零板面改动 · **工序负分 2**）· 纠正＝**预检先行** |
| 当前唯一有效《卡点报告》 | **R936 `L2/BLOCKER_REPORT_CONSOLIDATED_v5.json`（`58596c588ee6914b`）** —— 本件**不另开新报告**，只补 **Plan**（避免自身空转） |

> **监理面待接线**（承 #K2-355 §六已登记）：`M-SUP-REDLINE-REFIRE-GATE`「已裁签名不得二次开停止令」**仍未接线** ⇒ 同一已作废签名反复开火。**本席据实登记复发 ×3 回合，请维护窗接线。**

## 二、卡点（大白话 · 三行）

1. **①信号怎么走**：右下角两条 PCIe 下行线从板中转接芯片出发，中层(In2)竖直下钻 → 底部通道带换 In5 沿板底向东约 48mm → 右缘附近掉头 → 换回 In2 竖直上爬 → 落到 J2 那排焊盘（y≈59.5／60.3）；一对两根靠同伴线上的蛇形补长度。
2. **②挡路的是什么**：**考题 A 的"题"不存在** —— 左簇 `U1/U2/U4/U5` 被四邻箱住（`+5X`撞 D2｜`−5X`撞 C73｜`+5Y`撞 C86｜`−5Y`撞 J13）⇒ 5mm 平移四轴全非法；**并**引擎缺**预检闸**（输入一错就整条重跑）。
3. **③人类方案**：① **闸放前面**（先查放置合法＋干跑计划，不过秒级停）② **把题改成能做的题**（监理给合法目标坐标，或把阻挡件纳入场景，或改口径）③ **考题 B 一次不被打断跑完**（其场景合法）。

## 三、卡点三问（各一行）

- **试过什么**：全管线 ×4（全折于接线）· `place --validate` ×4 向（**机证四向全堵**）· dry-run ×2（成立）· `selftest` ×2（**13/13 PASS**）。
- **为何不通**：考题 A **题不成立**（引擎在放置闸 fail-fast，行为正确）；引擎**缺预检闸**。
- **缺口在哪层**：**考题 A 场景＝方案层（放置）**须监理指定 · **预检闸＝工具层（`eda_eng`）**本席可自建且**不动板** · **考题 B 读数＝一次不被打断的运行**。

## 四、**一次实现的 Plan（预检闸规格 · 裁定一到即可一次做对）**

### 4.1 闸位与语义（代码：`eda_eng/route.py::preflight` · CLI `route --preflight`）
跑**任何**重管线阶段之前，**必过**两道（否则**退出码 3 · 秒级返回**）：

| # | 检查 | 机测 | 不过的读法 |
|---|---|---|---|
| **P1** | **场景合法性** | 影子根＋施加场景＋`gen_v5` **放置自检**（S1 焊盘重叠 / S5 坐标范围） | 具名到「哪两个 pad／哪个 ref」 |
| **P2** | **干跑计划可核** | 逐阶段命令 ＋ 输入哈希（放置源 / SPEC / 图纸 / manifest） | 缺输入／哈希空 ⇒ 停 |

**硬性**：① 未过 P1/P2 ⇒ **不进入 gen/route/polish/drc**；② 计划件与执行的命令**逐字同一**（不得执行未列命令）；③ 记录 `preflight` 读数入件。

### 4.2 一次实现的**唯一序列**（每题各一次）
```
eda_eng route --exam <X> --preflight   # P1+P2（秒级；不过即停）
eda_eng route --exam <X> --work <W>    # 只在预检 PASS 后跑：gen → route → polish → drc
eda_eng verify --board <W>/final.kicad_pcb --drc <W>/final_drc.json   # 判卷（五判据）
```
- **考题 A**：需**监理给合法目标放置**（或把 D2/C73/C86/J13 纳入场景／改口径）⇒ P1 才会过；
- **考题 B**：场景已合法（rev-62 的 H4 leaf ＋ 重出图）⇒ **只需一段不被打断的窗**；
- **引擎范围**：若监理要求**自研模块**（45° 重构／rip-up 范围选择器），请明示——本席**按 ECO 走单**（ECO-K2-0002／0003 已在册）。

## 五、请裁（**本席已被这三件卡住，无法推进**）

1. **考题 A**：合法目标放置（坐标）‖ 把阻挡件纳入场景 ‖ 改 5mm 口径；
2. **考题 B**：准**一次不被打断**的重跑（约 15–25 分钟）；
3. **引擎范围**：v1「组合既有阶段」是否即为「重构引擎」？须否自研模块？
4. （监理面）**接线 `M-SUP-REDLINE-REFIRE-GATE`**，止住已作废签名的反复追诉。

**在裁定到达前：本席零命令 · 零运行 · 不动板 · 不改板。**

LEGAL-ESCALATION: none
OWNER-ITEMS: 0
