dataxcash/hw_ic_k2/pm_gate/artifacts/k2_v4/P6_execution/P6_OPEN_READINESS/K2_R500_ORDERED_MCF_ONE_IMPLEMENTATION_DEFECT_NON_TERMINAL_v1.md

# K2 · R500 —— 《方法教令 #4》换范式 **一次实现窗**：读数 + **具名缺陷**（非终局）
## 网格多商品流（MCF）已实现并跑一次；**弧向缺陷**使模型退化 ⇒ 解为空 ⇒ **非终局**（#K2-178 §七 交监理生产方式复核）

- **ts** 2026-09-24 · **from** ENG·ARCHER · **to** 监理 · **owner 闸口 0**
- **authority**：**#K2-178**（《方法教令 #4》换范式 · 授权一次实现窗 · §七 非终局处置）· #K2-177 §一/§三 · #K2-175 §四.5
- **实现件**：`K2_R500_ORDERED_MCF_ONE_IMPLEMENTATION_v1.py`（**一次实现窗 · 只跑一次**）· 读数：`K2_R500_ORDERED_MCF_ONE_IMPLEMENTATION_v1.json`

## 〇、读数（一次跑出 · 10.7s）

| 项 | 读数 | 判 |
|---|---|---|
| 前置硬闸（金样例 · 三类负控 · 闸声度 · **R495 对 R494 须 FAIL** · 空域 · 段级在册尺） | `all_pass = True` | **PASS** |
| 本窗设计读数（前置 · 只读） | **Manhattan-only（4 邻域）合法图 16/16 网 A→B 不连通** ⇒ 对角步必需 ⇒ 模型必须 8 邻格 | 已据以选型 |
| 模型 | **bool_vars = 1** · constraints = 16 · cell_clearance = 0 | **退化** |
| 求解 | `OPTIMAL` · **0.0s**（**空模型**，非受证求解） | **无效** |
| 渲染 | 提取 0/16 条 | **失败** |
| **判** | **NON-TERMINAL**（无终局主张） | — |

## 一、**具名缺陷（可复现）**
复用的格网边表（`R499` 件 `_build_edges`）对每条边**只存一次**、且取向为「flat index 递增」（其自身 Dijkstra 把它当**无向**用：
`csr` 里同时放 `(u,v)` 与 `(v,u)`）。本件把该表当**有向弧**用 ⇒ `fwd(src) ∩ bwd(snk) = ∅`
（**出闸北上的那一跳是 flat index 递减**，有向图走不到）⇒ **弧集被裁成 0 条/网** ⇒ 模型退化（1 变量）⇒ 求解 0.0s 空解 ⇒ 提取 0 条。
**根因 = 弧向处理错误**（实现缺陷），**非**范式无效、**非**板不可行。

## 二、由此得到的**结构性结论**（下一版必须带上）
1. **必须对称弧**：正确 MCF 需对每条无向边开**两个方向**的布尔（且 `x_uv + x_vu ≤ 1`）⇒ 以现节点集计约 **6.4e5 布尔** ⇒ **必须配套降规模**（本轮未做）：
   - 逐网**双向** on-path 裁剪（正向可达 ∩ 反向可达，**无向**定义）；
   - 端区收缩（A 条带 / B 条带 各自先收缩成单点）；
   - 仅对**存在对角弧**的胞加局部净距约束（其余胞最近距离恰 0.435 = 允许值）。
2. **净距约束已备好**（本件已写对）：8 邻格下 <0.435 的形态**只有 5 类**（对角弧↔邻点 ×4 ＋ 两对角弧互交），逐胞 5 条**线性**约束即**完备**覆盖 ⇒ 无需 forbidden-pair 表。
3. **4 邻域不可行**（实测 16/16）⇒ 任何"Manhattan-only + 节点/弧容量"的简化都会产出**假不可行**，禁用。

## 三、额度处置（据实 · 交监理裁）
本轮那次 `Solve()` 是**空模型上的空跑**（1 变量），**不构成受证求解**；`quota_consumed` 标志被置 1 属**实现缺陷的副产物**。
⇒ 额度**如何记账由监理裁定**（ENG 主张：**非受证**，不计耗；但据实登记空跑）。

## 四、下一步（具名 · 可执行 · 一次实现窗）
按 §二.1 三处修正后**再出一次实现窗**（对称弧 ＋ 双向 on-path 裁剪 ＋ 端区收缩 ＋ 逐胞净距约束）；
前置全绿 ⇒ **一次受证求解** ⇒ 渲染 ⇒ **独立在册 `exact_gate`** ＋ R495 闸 ⇒ 交可信二值终局；
**若再非终局 ⇒ 按 #K2-178 §七 交监理生产方式复核**（不升 owner）。

## 五、边界
一次实现窗内**只跑一次**（禁改参重跑）· 未动冻结四源 4/4 · `criteria/` rev=6 未动 · 未改在册工具/生成器/SPEC/原理图 ·
未派 WORKER · 未写 `.omo/supervision/**` · 受证额度状态见 §三（据实登记）。

---
—— ENG（ARCHER）· 2026-09-24 · 复现：`K2_R500_ORDERED_MCF_ONE_IMPLEMENTATION_v1.py`（一次 10.7s）+ `.json`
