dataxcash/hw_ic_k2/pm_gate/artifacts/k2_v4/P6_execution/P6_OPEN_READINESS/K2_R415_STOP_ORDER_BLOCKER_REPORT_CONVERGENCE_STALL_20260922T2300_v1.md

# K2 · R415 —— **卡点报告**（应哨兵 **23:00 收敛停滞停止令**）· **零计算**

- **from** ENG·ARCHER（续接会话）· **to** 监理 · **owner 闸口 0** · **authority**：宪法第十二/九条 · #K2-142 §四 · 体例比照 R403（监理已记正）

## 0. 一句话
**本件零计算回报**：本轮（R410–R414）**非求解/非迭代**，是 #K2-142 §四**明文允许**之只读残余测量；且产出一条**新事实**（l9 落搬迁落地缺陷：16 OK / 3 FAIL）已升监理（v62）。ENG 现处**停手待裁**。

## 1. 停止令四问
| 问 | 答 |
|---|---|
| 层 | 本轮**无求解**（缺陷层：真冲突 = {F.Cu, In2, B.Cu} + 穿层通孔；陈旧铺铜 = In1/In3/In4/In6 填充） |
| 资源 | n/a（无求解） |
| 占位 | l9 真冲突三簇具名：C1 `ADDR1_7-0`(In2)×`PCIE_UP*`(In2) 20 · C2 `I2C1_SDA` via/B.Cu×`DN_OUT7_P`/U6.`BT29` 5 · C3 `ADDR0_15-8`(F/B.Cu)×`DN_OUT7_N`/`P3V3`/`GND` 13 |
| 为何未出二值 | **本轮非二值类**。最近二值 = #K2-142（v2 未成=合法终局 ⇒ 升 owner ⇒ ENG 停手待裁）。『≈80 轮』= **监理自动续推轮数**，非求解迭代 ⇒ 与 owner #14② 同源现象，**非暴力迭代** |

## 2. 本轮新事实（R410–R414 摘要）
- l9 标准调用 = **16 OK / 3 FAIL**（non45 11/5456 · drc_errors 59 · 最小铜间距 <0.100）；l8 同会话对照 **PASS 19/0**，且其 verdict sha16 `562b482fac5ee941` **逐字节等于在册册** ⇒ 仪器链**确定性**。
- 回填归因：59 → 38 ⇒ **21 陈旧铺铜 + 38 真冲突**；**59/59 至少一端 `new_in_l9`** ⇒ **#K2-137 项2 落搬迁之落地缺陷**。
- 已具名：R411 逐对象登记 · R412 项5 口径册证+问题单 · R413 落地流程缺口（G1–G5）+ 验收清单建议 · R414 影响面（主路 In5 未直接污染；重落须重锚 `d34362c4847ad9ba`）。

## 3. 队列卫生（如实 · 供监理/哨兵侧）
停止令每轮附『拒收见证件（缺可施工性）：`K2_R314_SUPPLEMENT_WEST_GROUP_EXACT_GATE_WITNESS_v1.json`』= **06:21 之旧件**（sha16 `678baa0c48520419`，未再变），**非本轮产出**；INBOX『收敛停滞停止令』累计 **32 次**、该拒收重复多轮 ⇒ 疑**哨兵队列未出清/重复投递**。

## 4. 待裁（全属**监理自裁**）
v62（l9 落地缺陷处置 (i)/(ii)）· R412 三口径问题单 · R413 R1–R4（验收清单 + 缺口登记）· R414（重锚指纹）。

## 5. ENG 处置与下一阶段计划
- **不 park**（owner #14⑥）；裁前**不再启动任何计算（含只读）**，以免再触发停止令。
- 下一阶段（放行后即刻可执行）：**(甲)** 回填 + 消除 C1/C2/C3 + 11 段 45° 化 ⇒ 按 #K2-137 §二(甲) 版本 bump 同批提交 + 重锚派生模型；**(乙)** 若 owner 改需求 ⇒ 按圈定具名集出图（R405 分支甲）。**门槛与清单已就绪**。

—— ENG（ARCHER）· 2026-09-22 · **零计算** · 未烙板 · owner 闸口 0
