dataxcash/hw_ic_k2/pm_gate/artifacts/k2_v4/P6_execution/P6_OPEN_READINESS/K2_R297_UP_OUT_PITCH_HARD_EXACT_SOLVE_CUT1_RESOURCE_CENSUS_AND_ORDER_VERDICT.md

# K2 · R297 · ②-UP 间距硬约束之精确求解（第一刀）：**资源三清单 + 序律判定**

**ts** 2026-09-22T04:51+0800 · **to** 监理 · **from** ENG · ARCHER（监理自动续推 · P4 在阶 · fail-closed）
**authority** #K2-132 §三(乙) D1 / §四 · #K2-133 §三 N1 · 指令 #14 · handoff R296 §7-2
**锚** 冻结四源 4/4 未动 · criteria **rev=6 MATCH**（只读）· l8 `7a5c89913d6e5d0a` · k2 `38bf3ae` · **owner 闸口 0** · 外部前置 1（criteria rev=7）
**self_sha16（#K2-72 §五 约定A）** `1a545235d0264f7a`

## 一句话
把 ②-UP 的硬约束**结构化为三张资源清单**（南通道**行带** / 西出**缺口带** / A 侧**下潜 gang**），并以 `exact_gate`（线段距 pitch=0.435）**全枚举序律** ⇒ **单调 A 序为唯一 0 违例序（R274 成立 · R294「序过严」推翻）**；西组 ye 随 c 逆序 ⇒ **新上界候选 U ≤ 8+6 = 14**。

## 一、资源三清单（可复算 · cell 0.01 · hw 0.08 · DIL 0.04）
| 资源 | 内容 | 容量 @0.435 | 判 |
|---|---|---|---|
| ① 南通道**行带**（y 行须于 x∈[93.7,135.6] 全自由） | `[56.77,56.82] [57.83,58.62] [59.58,59.83] [60.77,61.57] [62.58,62.82] [63.77,67.21]` | **15**（DIL=0 时 18） | 给出 **U ≤ 15**（含余量），**非** U≤11 级障碍 |
| ② 西出**缺口带**（西组 jog 必穿通孔列之自由行） | `[43.97,44.23] [45.77,46.03] [47.57,47.83] [49.37,49.63] [51.17,52.03] [52.97,53.23] [54.17,54.43]` | **8** | **恰好容 8 西组**（y≥59.58 属墙带之南、北返必再穿墙 ⇒ 不可用） |
| ③ A 侧**下潜 gang** | A 锚正下非全自由（0_N 之 x=84.35 于 y∈[56.3,57.4] 被封）⇒ 需短横 gang 送至自由列 x∈[85.0,103.x]；同组 stub 共行 ⇒ 两两 ≥0.435 且 x 不交 ⇒ **stub 长 ≲0.6mm** | — | **可满足**，但为**旧模型未含**之硬约束 |
| ④ 列资源 | 走道内可用 ~6.75mm；16 列 @0.435 = 6.525mm | **16** | **不紧** |

## 二、序律判定（决定性 · 全枚举）
对 (0_N,1_N) **30480×2** 组、(2_N,3_P) **24480×2** 组之全部栅格可行解分桶，逐组跑 `exact_gate`：

| 序 | nviol | lane_pitch_min_gap |
|---|---|---|
| **c↑ & Y↑** | **0** | **0.50** |
| c↑ & Y↓ | 1 | 0.00 |
| c↓ & Y↑ | 1 | 0.00 |
| c↓ & Y↓ | 1 | 0.00 |

⇒ **单调 A 序（ax↑⇒c↑ 且 Y↑）= 唯一 0 违例序** ⇒ **R274 §order_derivation 成立**。
跨组对 (2_N,3_P) 在 c↑&Y↑ 下：**ye 大者对应 c 小**（ye 逆序）⇒ `ye0>ye1` = 0 违例、反向 = 1 违例。
单列族复查：西组 0_N/1_N 之 ye=null 可行解 = **0 组** ⇒ **复证 R288**（西组必经缺口带）。

## 三、推论
1. **R294 推翻**：『全变量严格同序过严』不成立（同组 c/Y 同序为**硬约束**）。R295/R296 之『15/16』系在**互距违例 32 条**（min gap 0.048–0.29）下取得 ⇒ **撤回为不充绿**（红线：禁以布通率/启发式充当见证）。
2. **新上界候选**：西组须走缺口带族 + ye 逆序 + `ye ≥ B.y+margin` ⇒ 使 m 条可行之必要式 `B.y_max ≤ 54.28−(m−1)·0.435`（m=6 ⇒ ≤52.105 ✓；m=7/8 ✗）⇒ **W ≤ 6** ⇒ **U ≤ 8+6 = 14**。
3. R274 之 **U ≤ 11** 未被本轮推翻，仍为候选；差额待第二刀联合 DP。

## 四、状态
- **(a) 见证：未取得**（本轮为资源清点 + 序律判定）。
- **(b) 本轮不新出不可行证书**；上界来源已定位到可复算清单，候选 **U ≤ 14**。
- **待裁 0**（不新增待裁锚 · 承 #K2-133 O-4）· **禁 HOLD/停等**。

## 五、下一步（一次 · 决定性）
**第二刀**：西组精确 DP（ye 逆序 × 7 缺口带容量 × B.y 约束 ⇒ **W\***） + 东组 8（列可行集 × 单调 A 序）⇒ **U\* = 8 + W\***；随即以单调 A 序 + A 侧 gang 出 **U\*** 条坐标化折线 ⇒ `exact_gate` + `buildability` ⇒ **见证**（⇒ R4 复闸）或 **单一卡点 + 具名归属（四字段）** + **具名豁免集 = 16−U\***。
