dataxcash/hw_ic_k2/pm_gate/artifacts/k2_v4/P6_execution/P6_OPEN_READINESS/K2_R274_UP_OUT_BINARY_CERTIFICATE_ORDER_DERIVATION_AND_NAMED_EXEMPTION.md

# K2 · R274 · ②-UP **二值证书**：16/16 不可达（列序由拓扑导出）+ 具名豁免

**件**：`K2_R274_..._BINARY_CERTIFICATE_ORDER_DERIVATION_AND_NAMED_EXEMPTION.json`（sha16 **`29f263022a297ae0`**）
**据**：监理自动续推 + 停止令（二值必出）· #K2-132 §三(乙)②/§四/§七 · #K2-133 · 指令 #14
**锚**：冻结四源 **4/4 未动** · criteria rev=6 MATCH · l8 `7a5c8991` · k2 `1b56535` · **布线器零运行** · owner 闸口 0

## 0. 二值
**(b) 守恒级不可行证书 = 可签 ⇒ `PCIE_UP_OUT` 16/16 不可达**（16/16 在**全部 4 个模型变体**下精确枚举皆不可行）。
**更正 R273 §1**：R273 之「(b) 不可得」是把**顺序约束整体丢弃**（order-free 松弛）之结果；顺序是**真实约束**（单层不可交叉），不可丢 ⇒ (b) **可得**。

## 1. 列序由拓扑导出（**修正 R269 §Ⅱ**）
- **形状被迫**：墙 In5 带（x∈[105.6,133.7] @ y∈[55.15,56.10]）阻断直东行，墙北 x<128 为缝合孔场 ⇒ 车道路径 = **南下 → 东行 → 北上**。
- **交叉分析**（ax_i<ax_j）：② j 竖段@ax_j 与 i 横段@Y_i 重叠 ⇒ 须 **Y_i>Y_j**；④ j 竖段@c_j 与 i 横段@Y_i 重叠 ⇒ 须 **c_j>c_i**。
- **⇒ 通道列序 = A 落线序（单调）**，南通道深度**倒置**。**R269/R271/R272 之 `reverse(A落线序)` 不成立**（l8 旧走线之逆序靠 **B.Cu 他层**置换 ⇒ >2 via，不满足长走全 In5）。

## 2. 精确枚举（2^16 · 全变体）
| 列序 | 跨越者规则 | 16/16 可行 | **U_max** | 豁免集数 |
|---|---|---|---|---|
| monotone-A（**拓扑导出**） | r271 式 | **False** | **10** | 1 |
| monotone-A | 物理在场 | **False** | **11** | 5 |
| reverse-A（R269） | r271 式 | **False** | 12 | 28 |
| reverse-A | 物理在场 | **False** | 14 | 10 |

⇒ **全变体 16/16 不可达**；(b) 成立。**ENG 保守取 U ≤ 11**（拓扑导出序）。

## 3. 具名豁免（ENG 命名 · 待监理 §四 自裁）
**`EX-4` = `PCIE_UP_OUT3_N_J2` · `5_N` · `6_P` · `7_N` · `0_N`**（5 网）
- 等价候选 5 个仅第 5 网不同（`0_N/0_P/1_N/1_P/2_P`），ENG 取 `0_N`。
- **残铜去向 = 不动证明**（5 网沿用 l8 既有走线 · 逐字节不动）。
- 若监理裁定顺序为 reverse-A ⇒ `U≤14`，R272 之 EX-3 可复用。

## 4. 人话判词（第十三条）
> 16/16 **不能**（拓扑导出序下缺 ≥5 网）；**11/16 + 具名豁免 5 网**为几何刚性口径。**可施工性 = 待 l9 构造**（当前**图纸层缺图**）。

## 5. 下一步（一次 · 构造式）
S1 入/出孔选址（F.Cu 短接）→ S2 单层 In5 **单调序嵌套**束布线（南通道深度倒置 · 0.435 · 硬避让 135 固定孔 + 他网 88 段）→ S3 末闸 `exact_gate` + `buildability` + 判据 19 维同口径重跑 + ref_plane/等长/3W + Gerber/Excellon 同批重出 + DFM → S4 P4 全绿（除外部）方下 P5。**<16/16 ⇒ 交单一卡点 + 具名归属 · 禁 HOLD**。

—— ENG（ARCHER）· 2026-09-22（真实时钟 03:40+0800）· k2 `1b56535` · rev=6 MATCH · owner 闸口 0
