dataxcash/hw_ic_k2/pm_gate/artifacts/k2_v4/P6_execution/P6_OPEN_READINESS/K2_R270_R4_GATE_READINESS_INVENTORY_v2_AFTER_UP_OUT_CLOSURE.md

# K2 · R270 · R4 复测闸就绪度 **v2**（②-UP 收口后）

**件**：`K2_R270_R4_GATE_READINESS_INVENTORY_v2_AFTER_UP_OUT_CLOSURE.json`（sha16 **`5e66801d4cbee88e`** · 约定A）
**据**：#K2-132 §三.3(b)/§四（(b) 分支 = 证书+独立脚本+残铜去向）· #K2-133 D3（rev=7 不阻 P4）· R259n 基线 · 监理自动续推（P4）
**锚**：冻结四源 **4/4 未动** · `criteria` rev=6 MATCH · l8 `7a5c8991` · 零重跑迭代 · 未派 WORKER

---

## 一、14 项状态（更新）
| # | 判据 | 状态 |
|---|---|---|
| 1 | 19 维判定器 | @l8 **19/19 @errata-3** ✓（l9 同口径重跑） |
| 2 | **②-UP** | **已收口**：(b) 守恒级上界证书 **U ≤ 15**（件 `107e117bbc49d701` · 独立复核脚本 `57c7e76bbd6a5b70` **HOLDS**）+ 具名豁免 **EX-2**（`PCIE_UP_OUT7_N_J2` · 残铜去向 = **不动证明**）⇒ 验收口径 = **15/16 + EX-2** |
| 3 | ②-DN | #K2-73 具名豁免 **EX-1** ✓（l9 同批豁免表） |
| 4 | ref_plane_continuity | @l8 = **0.0 mm²** ✓（l9 重测） |
| 5 | 等长（In5 N/P skew） | @l8 基线已测（max 6.002mm@pair4）· l9 同口径重测 + 阈值具名 |
| 6 | 3W / 85Ω | 3W @l8 ✓（min 0.500 ≥ 0.480 · R259p）；85Ω = **P5 外部** |
| 7 | ⑪ 自报 sha16 | 约定 A 已用 ✓ |
| 8 | ⑫ 守恒级存在性 | **不适用** ✓（仅动本网几何 · 无尺度变更） |
| 9 | 平面/铺铜/钻孔前置 | 全 **PASS** @l8 ✓（l9 重测） |
| 10 | **criteria rev=7** | ⛔ 未落 —— **gate 属主 `ic_hw_gate`**（与 l9 同批） |
| 11 | **l9 落 `hw/`** | ⛔ 未落 —— 内容物就绪后 · 硬前置 rev=7 |
| 12 | spec-rev-55 | ⛔ 未落（在册 rev-54）· 与 l9 同批 |
| 13 | Gerber/钻孔/打包 | 管道就绪 ✓（14 gerber + 8 Excellon 含 HDI 盲埋孔）· l9 同批重出 + 重跑 DFM |
| 14 | P5 打样 | **外部/商务**（owner ④：不属 ENG 任务/阻塞项） |

## 二、结论
- **R4 闸 14 项：ENG 侧缺口 = 1**（= **l9 内容物**：15 条单层 In5 新几何之**一次坐标化实现**；已无刚性矛盾 —— 横截面 15×0.435 = **6.09 ≤ 6.88** 自由宽）。
- 余 4 项（10/11/12/13-重出包）**全为 l9 同批**，其硬前置 **criteria rev=7 属 gate 属主（非 ENG 写域）**；#K2-133 D3 明文『**禁因此停等**』。
- **P4 判绿之唯一剩余 = l9 落库（外部）**；**P5 下单仍不启**（外部/商务）。

## 三、请监理
1. 依 #K2-132 §四 使 **EX-2 自裁生效（裁完报备）**（本件即其依据之 R4 口径更新）；
2. `criteria` rev=7 落件时点（gate 属主）。

## 边界
冻结四源不改 · `criteria/` 只读 · 未烙板 · 未派 WORKER · 未改生成器/SPEC/原理图 · 临时仅 `/tmp/opencode` · 零重跑迭代 · 未写 `.omo/supervision/**` · **禁 HOLD/停等结案**。

—— ENG（ARCHER）· 2026-09-22 · k2 R270 · owner 闸口 0
