dataxcash/hw_ic_k2/pm_gate/artifacts/k2_v4/P6_execution/P6_OPEN_READINESS/K2_R261_UP_OUT_A_ROW_EXIT_CAPACITY_AND_NESTING_ORDER_READING.md

# K2 · R261 · **②-UP · 洋葱序完备性 + A 排 `_P` 出口容量** 读数（P4 在阶 · 一次实现）

**件**：`K2_R261_UP_OUT_A_ROW_EXIT_CAPACITY_AND_NESTING_ORDER_READING.json`（sha16 **`6edb217d35819856`** · 约定A）
**依据**：#K2-132 §三(D1 准：一次·精确·无扫描) · #K2-133 §三(N1 准：no-move 全转) · 指令 #14 ⑥ · 宪法第三条
**锚**：冻结四源 **4/4 未动**（`d4e81f64` / `fb07d25a` / `dd794c54` / `0a459839`）· `criteria` **rev=6 MATCH** · 受审板 l8 **`7a5c8991`** · 授权真源 errata-3 **`5dc7b82a`**
**口径**：物理 keepout **0.5300** · lane_w 0.16 · **车道互距 ≥0.435** · 全转（`is_lane`=仅 16 条 `PCIE_UP_OUT*`，DN_OUT 等硬障碍）
**方法**：只读几何量测 + 3 类独立布线/割线读法 · **零烙板 · 零改件 · 临时仅 `/tmp/opencode`**

---

## 0. 一句话

**(a) 16/16 见证未取得 · (b) 严格证书未取得**；但本轮把卡点**由抽象收窄为具名几何机制 F-3**：
**A 排 `_P` 行（y=54.880 · 8 枚）被夹在墙与 `_N` 行（y=55.823 · 8 枚）keepout 之间 —— 每条 `_P` 车道进入南区必须穿过 `_N` 排，而 `_N` 锚间缝仅 0.090/0.140mm（7 条），每条缝至多容 1 条车道；行间带因 `_P`/`_N` keepout 重叠（55.290–55.410）**不可东行** ⇒ `_P` 出口割可穿越车道数 ≈ **8 = 需求量（余量 0）**。**

## 1. V-1 复核在册 12/16（第三条·独立复核）

独立重跑既有 `k2_p4_b2_in5_pf_lane_router_v1.py`（30 迭代 · cell 0.05 · sep 0.45）一次：
`it0 routed=12`（合法集/被排除集与在册件**逐条相同**）· `it1 routed=4`（=被排除集）· `it2 routed=12` ⇒ **在册 12/16 复现**。

## 2. F-1 洋葱序**完备性**（构造式 · 4 个规范朝向 · 非扫描）

独立实现之硬分离顺序布线器（cell 0.05 · sep 0.45 · 末闸 `v3.exact_gate` @0.435）：

| 次序（洋葱序） | routed | 车道互距违规 | 对障碍违规 | 端点位移 |
|---|---|---|---|---|
| **By_desc**（B 锚 y 降序 · 南锚先布） | **12/16** | 0 | 0 | 0.0 |
| Ax_desc（A.x 降序 · 最东锚先布） | 11/16 | 0 | 0 | 0.0 |
| Ax_asc（A.x 升序 · 最西锚先布） | 2/16 | 0 | 0 | 0.0 |
| By_asc（B 锚 y 升序 · 北锚先布） | 1/16 | 0 | 0 | 0.0 |

⇒ **4 个规范洋葱朝向之上限 = 12/16** ⇒ 12/16 **非**某一具体次序之偶然（与在册『20 序枚举·最好 12/16』一致）。

## 3. F-2 标准 PathFinder（协商拥塞 + 全量 rip-up）

保留半径 = pitch/2 = 0.2175 · cell 0.10 · 60 轮：

- **每轮 16/16 全部同时布通**；最优轮 overuse = 7690（cell 计数）。
- 末闸：**车道互距 min 0.0000 mm · 38 对违规**；对障碍 min 0.1025（0 违规）；端点位移 0。

⇒ **（a）未取得**：连接层可达，但**连续精确车道互距不可同时满足**（红线：不得以 16/16 布通充当见证）。

## 4. F-3 **A 排 `_P` 出口容量**（本轮决定性新事实）

- A 侧 16 锚分行：**`_P` 行 y=54.880**（x 84.85–93.70）· **`_N` 行 y=55.823**（x 84.35–92.70）；南区（南通道）在 y>56.35。
- **每条 `_P` 车道必须先跨 `_N` 行**；`_N` 车道起点已在南区侧。
- 判据口径（keepout 0.5300）下对 `_N` 行做**割线量测**（cell 0.02）：
  - 相邻 `_N` 间距 1.15/1.20mm − 2×0.5300 ⇒ **缝宽 0.090/0.140mm（7 条）**；`0.140 < 0.435` ⇒ **每缝至多 1 条车道**。
  - **行间带被 `_P` 自身 keepout 封**：`_P` keepout 达 y=55.410、`_N` keepout 起于 y=55.290 ⇒ **重叠** ⇒ `_P` 无法在行间带内东行（被切成 ≈0.168mm 缝）。
  - 东端 x≈92.8–103.1（y≈55.3）自由宽 10.3mm，惟进口受 `_P`/`_N` keepout 夹持 ⇒ 约容 **1** 条。

⇒ **`_P` 出口割可穿越车道数 ≈ 7（锚间缝·各 1）+ ≈1（东端带）= 8 = 需求量 ⇒ 余量 0**。
⇒ 与实测吻合：12/16 之被排除集 `{0_N,0_P,1_P,2_P}` 含 **3 条 `_P`**；「失败网优先」时**仅 `_P`（4 集）得布**；R258 亦见「失败恰为 `_P` 网」。

**定性（非证书）**：F-3 = **测量/归因**；本轮**不宣称** U<16。严格证书仍需『**束序不变量（含小孔绕组代价下界）**』或**精确 MILP/CP-SAT**（#K2-131 §三(乙)②）。

## 5. 二值状态 / 下一步（可执行）

- **(a) 16/16 见证：未取得**（3 类方法皆未达 0 违规）。
- **(b) 守恒级严格证书：未取得**；**卡点由抽象收窄为** F-3/F-4 之**具名刚性量（`_P` 出口割）**。
- **N1（严格 (b) · 推荐）**：以 F-3 之割为刚性量，证『`_P` 出口割可穿越车道数 ≤7』（含东端带注入容量 + 行间带不可东行）⇒ 抵 8 条 `_P` 车道 ⇒ **U<16** ⇒ 依 #K2-70 §六③ / #K2-132 §四 **具名豁免 = 监理自裁**；或以此为约束建**精确 MILP**。
- **N2（(a) 构造）**：按『7 缝 + 东端带 1』显式指派 + 每缝单向屏障作**一次构造实现** ⇒ 16/16 + `buildability.mode="no_move"`。
- 二者并入 #K2-132 §三『一次实现、一次交付』（不增次数）；D2 同批落库 ⇒ 判定器 19/19 @bump ⇒ R4 复测闸 ⇒ P4 全绿方下 P5。

## 6. 边界

冻结四源不改 · `criteria/` 只读 · 未烙板 · 未派 WORKER · 未改生成器/SPEC/原理图 · 临时仅 `/tmp/opencode` · 未以 16/16 布通充见证 · 未以有界搜索冒充证书 · C-w 未申报未执行 · **本件为在阶测量/归因（非待裁请求·不新增待裁锚 · 承 #K2-133 O-4）**。owner 闸口 = 0。

—— ENG（ARCHER）· 2026-09-22 · k2 见本轮 commit · 冻结四源 4/4 未动 · 判据 rev=6 MATCH · l8 `7a5c8991`
