dataxcash/hw_ic_k2/docs/02-manufacturing.zh-CN.md

# K2 制造说明

[English](02-manufacturing.md) | **简体中文**

## 叠层（8 层）

| 层 | 内容 |
|---|---|
| `F.Cu` | 高速差分 + 逃逸 + 周边低速 |
| `In1`–`In6` | 内层（信号 / 平面） |
| `B.Cu` | 低速 / 边带 |

## 工艺

| 项 | 值 |
|---|---|
| 差分阻抗 | **85Ω ±10%**（需阻抗控制 + 测试片） |
| 最小线宽 / 线距 | 0.09mm / 0.10mm |
| 板边铜 / 孔环 | 0.30mm / 0.075mm |
| 过孔 | 标准 0.20mm 钻孔 / 0.35mm 外径 |
| 板厂 / 通道 | JLC — **HDI 盲埋孔通道（≥2 阶）** |

## 交付

- **交付板**：`hw/k2_v4_8L.l4.kicad_pcb`
- **交付物**：Gerber 包 = 8 铜层 + 阻焊 / 丝印 / 边框 / job + Excellon 钻孔（含 HDI 盲埋孔）+ 叠层图 + 阻抗表 + MANIFEST（逐文件 sha256）

## 已知处置项（随单披露）

| 项 | 处置 |
|---|---|
| 掩膜桥 `R3.pad2 ↔ PCIE_UP3_N` = 0.0695mm < 0.09mm | L2 已接受（`ACCEPT_L2_WITH_FAB_REVIEW`，随单提交，板厂复核） |
| 阻抗符合性 | 本工程不自行认证；交板厂阻抗控制服务终判 |
