dataxcash/hw_ic_k2/pm_gate/artifacts/k2_v4/L3/buildability.md

# L3 可建造性评审（G3.3 产物）

> 建筑业"可建造性评审"制度：施工图出图**前**由制造方评审，在图纸阶段消灭制造问题。

## 评审范围

- 对象：SPEC_k2_v4.json（施工图约束）+ k2_v4 当前放置状态
- 制造方视角：JLC06161H-3313 6 层板工艺

## 逐项核对（JLC DFM 规则）

| # | 检查项 | SPEC 值 | JLC 极限 | 判定 |
|---|---|---|---|---|
| 1 | 最小线宽 | 0.09（LOW_SPEED 0.15） | 0.09 | ✓ 达标 |
| 2 | 最小线距 | 0.10 | 0.10 | ✓ 达标 |
| 3 | 过孔 drill | 0.20 | 0.20 | ✓ 达标（非极限，良率稳） |
| 4 | 过孔 outer | 0.35 | 0.35 | ✓ 达标 |
| 5 | 孔环 | 0.075 | 0.075 | ✓ 恰好达标（已确认接受） |
| 6 | 板边铜 | ≥0.30 | 0.30 | ✓ 达标 |
| 7 | 高速线宽 | 0.205（PCIe85） | 0.09 | ✓ 远大于极限 |
| 8 | 高速线距 | 0.175（对内） | 0.10 | ✓ 达标 |
| 9 | 对间间距 | 0.875（R3-2 3W 原则） | — | ✓ 达标 |
| 10 | 差分阻抗 | 85Ω±10% | — | ⚠ 需 coupon 实测（打样前） |

## 制造风险项

1. **阻抗 coupon 为硬性前置**：w=0.205/g=0.175 为计算值，板厂 SI9000 实测可能偏移，±10% 容差内接受，超限走 ECN 回 L2
2. 板厚 1.6mm 6 层 + 0.20mm 过孔：纵横比 8:1，JLC 标准工艺内
3. MLCC_0201 贴片密度：37 个 AC 电容 + 低速区器件，贴片产能无问题

## 评审结论

- **PASS**：SPEC 全部制造项达标 JLC06161H，唯一待实测项（阻抗 coupon）已在 prereq_closure.md 登记为打样前强制项
- 无制造违规项需回退 L2

## 版本

- v1.0（2026-08-13）
- v1.1（2026-08-15：对间间距 0.5 → 0.875 同步 R3-2）
