dataxcash/hw_ic_k2/pm_gate/artifacts/k2_v4/P6_execution/P6_OPEN_READINESS/K2_R360_UP_OUT_A_SIDE_ACCESS_PARALLEL_CONSTRUCTOR_GAP_v1.md

# K2 · R360 · ①-UP **③ 坐标化生成**执行记 —— A 侧接入 = **并行非交叉束布线**能力缺口（单点定位）

**件**：`K2_R360_UP_OUT_A_SIDE_ACCESS_PARALLEL_CONSTRUCTOR_GAP_v1.json`（约定A **`7598827e5c6c7768`**）
**据**：#K2-132 §三（D1 准 · 一次实现 · 只读 · 精确 · 无扫描 · 二值）· #K2-133 §三 N1 / §四 · #K2-132 §三.5 · owner #14⑥⑦⑧
**锚**：冻结四源 **4/4 未动**（本轮 sha256sum）· `criteria` **rev=6 MATCH** · 受审板 l8 **`7a5c89913d6e5d0a`** · k2 **`5b66810`** · **owner 闸口 0**

## 〇、一句话
**开工第一动作已办**：读 `.omo/supervision/ledger/`（含 `sent/` `outbox/`）—— **最新正式裁定 = #K2-133（outbox · 01:32）**；**无晚于本 handoff 之裁定** ⇒ 按 **#K2-132 §三 + #K2-133 N1** 执行「**一次实现**（③ 坐标化生成）」。本件记录该次执行：**未出 (a)/(b)**，但把**卡点精确单点化**为 **`C-B2UP-1`（并行非交叉束布线器）**，并给出**可施工性**结论。

## 一、二值（唯一终局）
| 支 | 判 |
|---|---|
| **(a) 16/16 可行见证** | **未取得**（本会话执行 ③ 坐标化生成 · 未过 `exact_gate`） |
| **(b) 守恒级不可行证书 `U<16`** | **不成立**（承 R353/R356/R358 之四反向数测；本轮复测一致） |

## 二、本会话实测（只读 · 未烙板）
**W1 自由空间拓扑（新）**：cell 0.02/0.03 · 物理口径 0.5300 · lane 铜按 `is_lane` 排除（= N1 全转视图）⇒
**A 锚群与全部 16 个 B 锚落在同一自由连通域**；`x∈[108,141]·y∈[40,55]` 为**一整块自由区（含全部 16 B 锚）**；
A 口袋↔走廊**仅两处门户**：**(P1) 缝槽带 y≈54.88·x∈[93.4,108]**（11 离散槽 · 单槽 **0.14–0.90mm**）与 **(P2) 东门 x≈134.5**。
⇒ 单 lane 皆通（承 R353 §3）；**瓶颈 = 「多 lane 同时穿越 P1/P2 的非交叉束布线」**。

**W2 序贯构造器（本条已布 ⇒ pitch=0.435 盘入障碍 · A_x 升序）**：实测 **2/16**，其后 **14 条 no-path**。
**新机制**：**0.435 盘对 P1 单槽（0.14–0.90mm）是结构性封死** ⇒ 同族任何「逐条布 / rip-up」方法（含 v3、R320 之 `byAx_desc`）在**西入口必败**。

**W3 嵌套楼梯构造器**（A→口袋层 h → 东窗站 x_s → 下潜 ye → 134.6 → B；ye 取 R316 精确解）：**未过闸**。
**新读数**：东窗 `x∈[136.5,143.5]` 内**全程自由（y∈[43,63]）之竖列不足 16**（仅 ~7 列；x=135.5/138/140/142 被孔栏截断）⇒ 朴素「单东窗 + 单调站序」不足；须**真正的双通道折返（口袋↔走廊双侧 reorder）**。

**W4 既有最好解之残差定位**：**R316**（连接器侧段 **16/16 过闸** · 互距 **0.4350**）已成立；**R320**（全 16 联合 **13/16 过闸**）唯一残差 = **A 侧锚群西端扇出**（未布 `T0_N/T0_P/T3_N`）+ **长度质量**（T1_N=314mm vs T1_P=92mm ⇒ skew 222mm）。

> W2/W3 为**定位尝试**（构造性 · 非扫描 · 非变体重跑），**不作见证、不作里程碑**（#K2-132 §三.4）。

## 三、归因（#K2-132 §三.5 二分）
- **①卡点层 = ENG 实现能力层**：登记 **`C-B2UP-1`**＝**并行非交叉束布线器**（同时：经 P1 窄槽并行穿越 ∧ 口袋/走廊双侧 reorder ∧ 互距≥0.435 ∧ 端点位移 0）。
- **②非「冻结需求须变」**：R316 已给连接器侧 16/16 过闸显式解 ⇒ **不触发** #K2-132 §十 升级路由。
- **③「施工队照着这张图能不能直接连」**：**不能（当前）** ⇒ 判 **图纸层缺图**（缺 A 侧接入段并行构造解）。

## 四、请监理自裁（全属监理面 · 宪法十一 · #K2-133 O-3 · **非 owner**）
**(甲)** 准 `C-B2UP-1` 之并行构造器**分多轮同一实现**并**给限期**；或
**(乙)** 依 **#K2-133 §四**（N1 后仍 <16/16 ⇒ 条件已满足）**批 C-w**（R351 实测放出 A 侧重排带 0.296→0.816）以降低 A 侧扇出难度。
ENG 将按裁定在下一实现窗口执行；**不自行申报/执行 C-w**（遵 #K2-133 §四）。

## 五、可施工性（宪法十三）
`mode = no_move`：本轮**纯只读** —— 未烙板 · 未改任何网几何 · 未动冻结四源/判据/生成器/SPEC/原理图 ⇒ **不动证明成立**（R316/R320 亦皆只读）。

## 六、复现
```bash
AppDir/usr/bin/python3.11 k2/tools/k2_p4_b2_board_in5_model_dump_v1.py k2/hw/k2_v4_8L.l8.kicad_pcb /tmp/opencode/archer/model_l8.json
python3 /tmp/opencode/k2r360/probe.py        # W1 连通性
python3 /tmp/opencode/k2r360/construct.py    # W2 序贯 ⇒ 2/16
python3 /tmp/opencode/k2r360/construct2.py   # W3 嵌套楼梯 ⇒ 未过闸
```

## 七、边界
冻结四源不改 · `criteria/` 只读 · 未烙板 · 未派 WORKER · 临时仅 `/tmp/opencode` · **未写 `.omo/supervision/**`** ·
未以布通率/有界搜索冒充见证或证书 · 未请求 owner（未触 L1）· **禁 HOLD/停等结案**。

—— ENG（ARCHER）· 2026-09-22（真实时钟 09:24+0800）· k2 `5b66810` · owner 闸口 **0**
