dataxcash/hw_ic_k2/pm_gate/artifacts/k2_v4/P6_execution/P6_OPEN_READINESS/K2_R347_CONSERVATION_BLOCKER_REPORT_v67_FREE_BUS_BAND_AND_CONSTRUCTION_SPEC.md

# K2 · R347 ·《守恒级卡点报告 **v67**》—— 上带自由 93–98 ％ + **C-* 构造规格（巴士 + 双层阶梯）**

**件**：`K2_R347_CONSERVATION_BLOCKER_REPORT_v67_FREE_BUS_BAND_AND_CONSTRUCTION_SPEC.json`（约定A `c123f65e4d089497`）· 承 v66

**(a) 未得 · (b) 不成立**（不新增不可行主张）。

## 新结构性发现（逐 y 带普查 · x∈[84,127]）
| y 带 | 自由率 | 最大全自由横走 |
|---|---|---|
| 36.0–44.5 | 72–83 ％ | 31.7–38.4mm |
| 44.5–48.5 | 78–89 ％ | 32.9–37.9mm |
| 49.0–54.5 | 62–77 ％ | 19.7–26.6mm |
| 54.5–56.0 | 64–82 ％ | 20.5–29.8mm |
| **56.5–58.0** | **93–96 ％** | **42.5–43.0mm** |
| **58.0–66.0** | **94–98 ％** | **42.40–42.50mm** |

**上带 y∈[56.5,66] 自由 93–98 ％ · 横走 42.45mm** ⇒ 足容 **16 lane×0.435 = 6.96mm** 巴士带（y∈[56.9,63.9]）。
**板内核对**：安装孔 (26.1,75.6)/(45.1,75.1)/(114.6,36.1)/(139.6,39.6) ⇒ 板约 x∈[26,140]×y∈[36,76] ⇒ **该带在板内**。
⇒ 自由空间**充裕** ⇒ 卡点**纯为联合指派**（与 16/16 单独可路、割上界 67≥16 一致）。

## C-* 构造规格（本件推导 · 可直接实现）
① 各 lane 升入上带**专属层** y_k = 56.9 + k·0.45（k=0..15 · 互距 0.45 ≥ 0.435）；② 沿巴士右行；③ 依序下落至 B 锚。
**★ordering lemma（必要条件）**：免交叉要求 **上升序 = 层高降序** · **下落序 = 层高升序**；又层 = B.y 序 ⇒ **上升序 = B.y 降序**，而 A 锚 x 序 ≈ **B.y 升序** ⇒ **相反** ⇒ 各 lane **必须先做一次水平预排序**。
⇒ 此即 v65『16 线重排』之**构造化表达 —— 重排由阶梯无交叉必要条件强制产生，非可选项**。
⇒ 前两次失败归因：法族1 无预排序（A 带内封死）；法族2 候选不含层化巴士结构（瓶颈相汇 · 互斥 94.1 ％）。

## 卡点（v67）
① **ENG 实现能力**（规格已给）· ② In5 走廊（**资源充裕**）· ③ **未占死** · ④ **前提不成立**（容量/连通/端点/面积皆非瓶颈）。

## 出口（皆监理自裁）
(i) 派 `C-*`（一次实现 · 照上述规格）；(ii) 批 C-w（价值在释放走廊资源，对连通性非必要）。

## 边界
只读 · 未烙板 · 未改 `criteria/`/生成器/SPEC/原理图 · 未派 WORKER。冻结四源 4/4 未动；受审板 l8 `7a5c89913d6e5d0a` 未动。

---
—— ENG（ARCHER）· 2026-09-22 · 二值 **未取得** · owner 闸口 **0**
