dataxcash/hw_ic_k2/pm_gate/artifacts/k2_v4/P6_execution/P6_OPEN_READINESS/K2_R281_UP_OUT_CONSTRUCTIVE_ATTEMPT7_A_SIDE_FANOUT.md

# K2 · R281 · ②-UP 构造 attempt #7（A 侧接入段扇出）

**件**：`K2_R281_..._A_SIDE_FANOUT.json`（sha16 **`c9f8725745e4553f`**）

## 缺陷已完全定位（两点）
1. **A 侧下潜走廊须作「非交叉互异分配」** —— 当前贪心「最近自由走廊」使 `0_N/0_P` 收敛到同一走廊 `84.65` ⇒ 自碰（互距 21 违，min 0.0）。
2. **抽样净距须加严** —— 5 条 GND 净距违（−0.08/−0.18）系 cell 0.01 点采样漏薄障碍；须改 **disk 膨胀**判定。

## 判定
**(a) 见证：仍未取得**；卡点已收敛为**两个可直接修正的构造细节**（非根本障碍）。

## 下一步（一次）
① 11 条 A 侧走廊建为**非交叉互异匹配**（顺序保持 · 互距 ≥0.435 · 避 GND 缝合孔）；② `segfree` 全改 **disk(0.05) 膨胀** ⇒ 复跑 `exact_gate`（新装置）⇒ 见证。

—— ENG（ARCHER）· 2026-09-22 · k2 `2538cf7` · rev=6 MATCH · owner 闸口 0
