dataxcash/hw_ic_k2/pm_gate/artifacts/k2_v4/P6_execution/P6_OPEN_READINESS/K2_R280_UP_OUT_CONSTRUCTIVE_ATTEMPT6_EXACT_DP_SOUTH_LAYER.md

# K2 · R280 · ②-UP 构造 attempt #6（精确 DP 联合分配）

**件**：`K2_R280_..._EXACT_DP_SOUTH_LAYER.json`（sha16 **`bc8fc53716acd8b5`**）

## 精确 DP 结论（正面）
把「南通道层 Y 全序嵌套分配」建为 `Y_1>Y_2>…>Y_11`（相邻 ≥0.435, `Y_k∈可用集`）的**精确 DP**：
**11 条 lane 全部入解**（末端可行状态 **943**）⇒ **南区南通道层子问题对 11 条 lane 不是卡点**。

解：`0_N 66.38 · 0_P 65.94 · 1_N 65.50 · 1_P 65.06 · 2_N 64.62 · 2_P 64.18 · 3_N 63.74 · 3_P 62.54 · 4_N 61.62 · 4_P 61.18 · 5_P 60.74`

## 但 exact_gate 仍未过
互距 **17 违**（min 0.0）· 净距 **5 违**（min −0.18 vs GND）—— 缺陷**集中于 A 侧接入段**（锚排引出 stub / 下潜拐角相邻相碰）与少数 GND 孔接触。

⇒ **(a) 见证：仍未取得**；但**卡点已从「南区层分配」前移到「A 侧接入段扇出」**（更小、更局部）。

## 下一步
**A 侧接入段扇出**：11 条自锚排（x 84.35–93.7, y≈55）分散至各自 (dx,Y)，建为**非交叉匹配**（≥0.435 · 避 GND 缝合孔）⇒ 复跑 `exact_gate`（新装置）⇒ 见证。

—— ENG（ARCHER）· 2026-09-22 · k2 `8270c1e` · rev=6 MATCH · owner 闸口 0
