dataxcash/hw_ic_k2/pm_gate/artifacts/k2_v4/P6_execution/P6_OPEN_READINESS/K2_R275_UP_OUT_CONSTRUCTIVE_ATTEMPT1_GATE_READOUT.md

# K2 · R275 · ②-UP 构造 attempt #1 · `exact_gate` 读数

**件**：`K2_R275_..._GATE_READOUT.json`（sha16 **`d468541f8f10a304`**）
**方案**：R274 拓扑导出之**单调序 + 南通道深度倒置**；一次生成 16 条 In5 折线 → `exact_gate`。

| 指标 | 值 |
|---|---|
| 端点位移 | **0.0mm ✓** |
| 互距违例 | **13**（min gap 0.0）|
| 净距违例 | **15**（裕度 −0.09…−0.36mm）|
| 主 blocker | **固定 GND/P3V3 缝合孔（135 枚 · 不可动）** + 少量自碰 |

**判定：(a) 见证 = 未取得（attempt #1）**，但违例**全为小量** ⇒ 剩余 = **自由带内布局定案**（非根本卡点）。

**纪律**：attempt #1 一次性 · **无参数扫描/迭代**（#K2-132 §三.5）；后续以**设计**（S2a/S2b/S2c）改进，非同参重跑。

—— ENG（ARCHER）· 2026-09-22 · k2 `4fb3adc` · rev=6 MATCH · owner 闸口 0
