dataxcash/hw_ic_k2/pm_gate/artifacts/k2_v4/L3/mcio_feas_step2/m13_v57_w3_joint_assignment_boundary_v1_82.md

# m13 v57 — W3 Boundary **v2.79**（文件名沿用 v1.82 以保持 co77 身份链；CO-121/121.1/122/122b + CO-124..CO-132（D-6 定案 + rev-17 退役 B.Cu 载体 + rev-18 R1 In4 承载几何派生）+ **CO-133（L2 自裁 · 施工期物理施加：rev-18 声明 PDN 铜落板 `d4e81f647be7f980` + 幂等/板实合规机判）已登记**；**CO-134（整改通知 #09：③ 重新定性 = 工程换算错误 → REQ-R3-2 忠实实现（铜边 ≥ 2w 按层）+ 需求/实现分家规矩 + co124 K9）已登记**）（+ **CO-135（非执行者复评 rev-19 + CO-134｜L2 声明/工具卫生修正：co77 覆盖扩至 markdown 表格行、链路 pin 全量刷新、co78/co81/co84 对 rev-19 重跑、L5 fab pin 刷新）已登记**；**CO-136（L2 自裁 · 闸卫生续：co106 陈旧牙齿改数据无关合成控 / co124 定义件版本派生 / co77 表格行 citation 负控牙齿 / 登记簿 +2 TOOL_DEFECT）已登记**；**CO-137（L2 只读分析：as-built 对间偏差几何修正可行性 = MIXED）已登记**；**CO-138（L2 只读分析：偏差耦合几何画像 —— B.Cu/F.Cu = 长平行在域内；In5 = 21.8° 斜交扇出）已登记**；**CO-139（L2 自裁 · K9 硬化：豁免域须 hash-pin 依据 + 负控 T9）已登记**；**CO-140（L2 只读分析：as-built 偏差归因 —— 1 接口固有 / 1 路由可改 / 1 斜交）已登记；F.Cu 项升 L1（J2 接口节距）**；**CO-141（L2 只读审计：对间 2w 符合性全量 —— 原「3 处」为下界，实为 24 个平行对-对；根因 = 路由器列距基准漏 3W）已登记**；**CO-142（L2 只读：对间 <3W 违规逐条明细 + 构造阶段归因 —— B.Cu 14 逃生竖列 / F.Cu 10 J2 land）已登记**；**CO-143（L2 只读：纠正 CO-141 附记2 的 f13 pair_xorder 定位 → 真实所在 = escape-fan 落位判据 `p3_v57_co10_west_fan_probe.py:check()`；施加可行性 = 3W 可满足但单遍贪心+PDN 障碍下无法 32/32，须重派生扇落位策略；登记簿该项保持 OPEN）已登记**）（+ **CO-117（L2 自裁）：band In4 铺铜归属 + SPEC rev-15**；**CO-114 非执行者对抗复评 rev-14 = PASS_WITH_FINDINGS（6 发现）**；W3-CN.41 收口 + CO-67..CO-71 方案(a) 全链执行/判据/判定接口 + CO-72 PDN 平面对齐 rev-6 + CO-73 层角色声明一致性终扫（rev-7）+ CO-74 B.Cu 电力铜退役/In4 承载（SPEC rev-8）；CO-72-PDN-1 归口 L1→L2 并闭合 + CO-75 西侧 1.580 未覆盖维搜索（负结果，L1 ① 证据补强）+ **CO-76 非执行者侧对抗评审 pass 1/2（F1/F2/F3 发现并修复）** + **CO-77 收口声明件当前态身份引用校正** + CO-78 层角色漂移回归闸（F1 缺陷类关闭） + CO-79 探针空真通过加固（守卫负控 A10） + CO-80 L4 工程文件规则对齐 + 独立 kicad-cli 复现 DFM + CO-81 受控工程文件规则回归闸 + CO-82 L4 工程文件网类缺失修复 + 闸覆盖补全（net_settings） + CO-83 工程网类↔红线 SPEC net_classes 交叉校验 + **CO-84 DRC 放宽域一致性闸（dru↔域工件↔板 rule area↔SPEC）** + **CO-85 非执行者侧对抗评审 pass 2/2（V1 全链 12/12 逐字节复现 + V2 闸牙齿复核 + F1 F.Cu 行更正 + F2 连接器焊盘场 0.6mm 硬限）** + **CO-86 L2 备选闭合判定（铜跨 0.705→0.585/0.407 均不可达 0.875：WEST 差 +0.232 / 焊盘场差 +0.682）** + **CO-87 L2 合格标准覆盖性机判（ch.5 §4 PDN 压降 / ch.2 热 = NOT_DEMONSTRATED：缺输入，已登记）** + **CO-88 PDN live 字段板实性机判（FAIL：55 孤儿 entry / 184 板实 pad 无决策 / 解耦零板实落点；修复候选+波及清单已派生）** + **CO-89 SPEC rev-9 PDN 板实化（ppc 重生成 223+86=309/309 覆盖、旧 BOM 退役留存；板逐字节不变；全链重基线）** + **CO-89b 复现重跑产物入库（12/12 逐字节一致）** + **CO-90 非执行者侧对抗评审 pass 3/3（对象 rev-9 新基线；全链 12/12 逐字节复现 + CO-88/89 事实独立复核 + 闸注入突变 4/4；F1/F2 修复（CO-88.2）+ F3 覆盖口径登记）** + **CO-91 PDN 计划坐标权威净距闸（pdn_apply 实落集 × 冻结规则源 `drc_rules.json`；判 FAIL：ppc via 35/223、stitch via 41/69、zone via 7/20、F.Cu 短段 75/223；修复候选 35/35 可重定位、PDN 覆盖不退化；覆盖缺口补齐）** + **CO-91.2 规则源唯一性 fail-closed（`K2/_shared` ↔ 容器 `_shared` 的 `drc_rules.json` 同字节断言；实测同值 `0a459839e15960b8`；漂移即不可判）** + **CO-91.3 闸/修复分离（移除内嵌 fix_candidate；其 8 向×半径梯读数违「零坐标搜索」红线，已作废）** + **CO-92 PDN rev-10 修复候选（声明式有限 palette 机判；ppc 223 → kept 188 / relocated 1 / blocked 34；stitch 28/12/29；zone 13/4/3；短段 0.5→75、0.2→13）** + **CO-95 In4 平面可达性机判 + 陈旧 keepout band 退役（premise 已被 CO-74 判失效）→ SPEC rev-11 `d85f10f722ba22b0`：55 power entry = 35 显式 polygon / 8 桥区 target / 6 L3 可达性义务 / 6 需区域裁决；新增 plane_reachability_requirement；全链重基线 PASS、板逐字节不变** + **CO-94 blocked pad 可连接性闭合判定 + 裁定（维持 blocked：34 中 15 在宽松有限家族内可连，但余量低至 13.6µm 且 7 个仅在家族上限命中 ⇒ 采用即把「搜索」写进决策，违零坐标搜索红线；故 34 判为 L2 手段内不可连接，升级 L1/工艺）** + **CO-93【L2 自裁 · PDN 权威净距重落 = 施加 rev-10】SPEC rev-10 `4416e42eed10cb8c`：ppc 223→189 entries（blocked 86→120，已连接 223→189）、stitch 69→40 落/60 blocked、zone 20→17/3、短段宽 0.5→声明 0.2；CO-91 对 rev-10 = PASS（0/0，牙齿 4/4）、CO-92 对 rev-10 = 不动点；全链 G4→G7 重基线 PASS、板逐字节不变；新基线非执行者复评欠（CO-94）** + **CO-96 非执行者侧对抗评审 pass 4/4（对象 rev-11 基线：6 项发现 F1..F6 —— F1 退役键谱系断裂 / F2 可达性要求不可机判闭合 / F3 文本依赖 / F4 scope 缺口 / F5 陈旧 board_realized / F6 latent bbox；V1/V2/V3/V4 复核 OK；CO-94/CO-95 复评义务已履行）** + **CO-97 退役留存完整性闸 + 显式登记册（把红线『退役决策须显式留存』机判化；CO-96 F1 的『静默』面以显式登记关闭；L2 自裁：不解冻 `_shared`，施工侧改项目内承载、施工期激活）** + **CO-98 In4 平面可达性义务状态报告（机判化 CO-96 F2/F3/F4：三态 35/14/6 + scope 排除 40/17/0 + 裁决依据 5 机判/1 文本；co95 PIP 行为中性加固关闭 F6）** + **CO-99 PDN 计划集互相冲突闸 + 施工 dry-run（两个覆盖缺口 G1 计划集互判 / G2 孔距 net-agnostic；实测 FAIL_MUTUAL_SHORT：7 异网重叠 + 35 净距 + 39 孔距；pdn_apply 实落 DRC 42→274）** + **CO-100 互障感知修复候选（residual 重叠 0；新增 blocked **5** 项 = 4 ppc + 1 stitch —— CO-103 校正原「6 项 / 全在 U6 0.5mm 场」为过期读数）** + **CO-101【L2 自裁 · 施加】rev-11 → rev-12 计划集互障重导（ppc entries 189→185 / relocated 61 / 新增 blocked 4；stitch relocated 5 + blocked 1；zone relocated 4；退役留存 + F5 同步 + F1 回填；全链重基线 PASS、板逐字节不变；CO-99 由 FAIL → PASS）** + **CO-102【L2 自裁 · 项目内引擎承载】修正版 PDN 施加器（短段宽读 SPEC 0.2 + via 去重 + blocked 口径对齐；scratch 三态 DRC：baseline 42 / 冻结 76(+34) / 项目内 42(+0)）** + **CO-103 非执行者对抗复评（对象 rev-12 = CO-99/100/101/102 + 链 pin + 收口声明；verdict `PASS_WITH_FINDINGS`；F-A 声明漂移 / F-B 升级证据不足 / F-C co95 身份引用陈旧）** + **CO-108 非执行者对抗复评（rev-13 基线 = `PASS_WITH_FINDINGS`；F-A 记录内 provenance pin 漂移已校正 + F-B 信息性 + F-C 登记）** + **CO-108 补记 F-D（bridge zone 层归属张力 = L3 派生前未决前提）** + **CO-109（L2 自裁）In5←In4 走廊空洞 = 按设计（非待 L3 派生）；bridge zone = B.Cu；step ② 重定范围 + owner 升级** + **CO-110（L2 施加）参考平面入 CO-87 矩阵 + CO-106 D 读径修复 + In4 走廊空洞按设计定案（R5'）** + **CO-111（L2 量化）In5 PCIe 走廊参考缺失 = 40.1%（1094.8/2727.3mm）；L5 未签阻抗 ⇒ 外部终判** + **CO-112（L2 声明）3 bridge zone = B.Cu 桥（step ②c）+ In5 区域条件参考口径 + 走廊 worklist** + **CO-113（L2 施加）SPEC rev-14：裁定写入 canonical SPEC；几何与板逐字节不变** + **CO-115（L2 更正）In4 走廊空洞 = 失效 keepout 残留（待 L3 派生），非按设计；归属界面 = L1（owner）**）

> 契约 `m13_v57_w3_kickoff_card_v1_28.md`（冻结，未改 `0ae3016379cd1db2`）｜引擎 rev **W3-CN.41**
> ｜**取代 v1.37**（本件补 CO-59：**残余②（B.Cu/In6 并行）机器闭合 PASS** + **口径出处再基** —— 机判 `route_model_config.json` 证 1.08 是 `channel_alloc.pitch_fallback`（回退值）**而非要求量**；要求量语义 = R3-2 **铜边 0.875**，1.46 为其在冻结铜跨 0.585 下的换算 ⇒ CO-58「走廊与冻结口径一致」结论**更正**：EAST 1.449 / WEST 1.050 在 1.46 与 0.875 两读数下**均不达标**）。
> 授权：CO-05..CO-56 各变更单 + **CO-59..CO-66（L2：口径对账 + 可达性/策略穷举 + B.Cu 承载审计 + LID 重入 ECN + 叠层厚度自洽推导）**；**L1 仅剩** 方案(b) 层数裁决 + **① 对间净空**（CO-57/59）；方案(a) 属 L2 自裁（执行清单见 CO-66 §3）。**CO-74 补授权（L2 PDN：B.Cu 电力铜退役 + In4 承载；`CO-72-PDN-1` 归口 L1→L2 并闭合）**。**冻结四源未动（4/4 MATCH）**。里程碑 tag `k2-v57-g7-l5-pass`（k2 `b5afe47`）。

## 1. 收口结论（机器可判 + 工件可独立重算）

> **本轮（CO-67..CO-69，L2 叠层分配自裁）**：① **CO-67** 一次性裁定「方案(a)（In5 GND→信号）vs 历史红线」= **L2**（机判不变量：层数 8、平面数 4、电源域划分 3×GND+1×P3V3、信号层 4 **全不变**）`m13_v57_CO67_L2_redline_ruling.md` `c562419d70a41ab9`；
> ② **CO-68** 修正 CO-66 铜厚口径（介质预算 1.425 = 1.6-0.175）⇒ 设计点 w_outer 0.205 / **w_inner 0.16**、闭合 1.6000（标准料 2116 / core 0.25）⇒ **LID REV6** `05009687a3f01583` + **SPEC rev-5** `1f351194b3e22b7e`；
> ③ **CO-69** 引擎 bump（`LAYER_PALETTE`=F/In2/**In5**/B、In6→In5 全量、`CO16-ALLOC.7` `a765af4c9bf61e64`、rev W3-CN.41）+ **全链重导**（G4 `87ef07f280e4dffb` / G5 PASS / G6 板 `0e636a67c1472462` / G7 DFM new=0 + SI PASS）；
> ④ **SI 判据升级**为**按层加权电气长度**（CO-62 §4）：升级前 max skew **0.9807** > 0.15 ⇒ FAIL（REFCLK1：P 全 F.Cu vs N F.Cu+In2 8.745mm）；**L2 等长整改**（补偿目标由物理长度改为电气长度）⇒ max **0.1300** ≤ 0.15 ⇒ **PASS**；物理量报告 max 1.1046mm（层补偿之预期；判据为电气/时延）。
> ⑤ **对抗评审**（执行者侧独立证伪探针 A1..A9：不变量/阈值不变/闭合/阻抗/引擎无 In6/板按层线宽/冻结/独立重算等长/DFM）= **全 PASS（10/10）** `m13_v57_co69_adversarial_review.json` `18a86c998dd6b4de`（CO-76 加固 A5 + CO-79 空真加固/A10 守卫负控；原 `50ff390f2803f25d`、`6daec5df8bf0d118` 已取代）；**非执行者双路对抗评审**：pass 1/2 = CO-76；**pass 2/2 = CO-85 已完成**（`m13_v57_co85_nonexecutor_review_pass2.json` / `m13_v57_CO85_nonexecutor_adversarial_review_pass2.md`；V1 全链 12/12 逐字节复现、V2 闸牙齿复核、V7 逐层几何独立复算、F1 更正、F2 新硬限）⇒ **双路闭合**（L2_STRUCTURE_v2.0.md:137）。
> ⑥ **① 再判（handoff §6.2 子项）**：在方案(a) 现状下复跑 CO-60/CO-61，**逐字节复现**（`m13_v57_co60_corridor_pitch_frontier.json` `e2d74c7afaae0d45` / `m13_v57_co61_l2_search_exhaustion.json` `b4ef0063188b6ec6`，二者 `baseline_faithful=true`）：西侧 >1.05 落位破裂、东侧 1.580 可落位但越板边、无策略维解 ⇒ **① 负结果不变**。理由：落位(r1/r3)为**面内几何**、信号层数不变（4）、走廊/通道输入冻结 ⇒ 层集 In6→In5 不改变 pitch 可达性。① 仍属 **L1 包络冲突**。
> ⑦ **CO-70（L2 等长窗口裁定）**：对内 skew **判据 = 按层加权电气长度**（mm-eq @ er_ref=3.99），**物理长度为报告量、非并列闸**：CO-62 §5.2「保留物理长度判据」= 保留**报告**。证据：电气 max 0.1300 ≤ 0.15 PASS；物理 9/34 页 >0.15（max 1.1046@REFCLK1）属层补偿之预期；同时满足物理+电气需 2 变量（P 蛇形置 In2 ≈8.745mm + 2 过孔，N 蛇形置 F ≈9.849mm@REFCLK1）——额外铜/过孔、SI 劣化，非默认。记录 `m13_v57_CO70_L2_si_skew_criterion_ruling.md` `f104a102ae2a2caf`。
> ⑧ **CO-72（L2 PDN）**：SPEC **rev-6** `9e8fb5bae4a33207` —— `pd.gnd_planes`/`zone_defs.gnd_planes` 的 GND 平面由 **In5→In6**（LID REV6：In5=信号、In6=GND），解耦规则文本与 REFCLK In2 判据理由同步更正；**几何不变性机判**（route_geometry/pages/decision_contract/layers 逐字节同）+ 全链重基线 PASS。并登记既有冲突 `CO-72-PDN-1`（`pd.power_zones[2..4]` 的 **B.Cu 铺铜** vs 8L B.Cu 信号层，重规划属 **L1 电源域/层数**，仅登记不擅改）。记录 `m13_v57_co72_pdn_align.json`。
> ⑨ **CO-73（L2 PDN/叠层分配）**：SPEC **rev-7** `a15ffcd104d82f43` —— 层角色声明**一致性终扫**（当前态，不动历史件）：`pd.zone_defs.gnd_stitch_via`（note + 各 coordinates[*].basis）32 处『GND 回路由 **In1/3/5** 平面承担』→ **In1/3/6**；`constraints.j2_escape_topology.outer_basis` 更正『B.Cu 释放给低速』（REV6 下 B.Cu=高速信号层、由 In6 参考）；`layer_plan.in6_usage` 更正为 REV6 In6=GND 平面；`layer_plan.strap_domain_v32.deps` 平面清单补 In6。**几何不变性机判**（route_geometry/pages/decision_contract/layers 逐字节同）+ 全链重基线 PASS。记录 `m13_v57_co73_layer_role_consistency.json`。
> ⑩ **CO-74（L2 PDN，归口更正）**：**`CO-72-PDN-1` 由 L1 更正为 L2 并闭合** —— 机判前提消失：引擎 `LAYER_PALETTE=F/In2/In5/B`（In4 非布线层）+ 交付板 **`In4.Cu` 段数 0** ⇒ 6L 时代『In4 走线带 x∈[50,88.17] 阻断跨带铜皮』不存在，T2-ECN-1/2 绕行前提失效 ⇒ **B.Cu 电力铜（`power_zones[2..4]`）全部退役**、改由 **In4 承载**；`power_zones[3].in6_segments`（REV6 下 In6=GND ⇒ 短路）一并退役。6L 几何原样留存 `retired_*_bcu`（禁止静默放弃）；新几何 = L3 施工确定性派生。**SPEC rev-8** `3ec8e35e676cf89d`；**L2 不变量全不变**（层数 8 / 平面数 4 / 域集合 3 / 信号层 4 / `power_plane_layer=In4.Cu`）⇒ 属 L2（CO-67）；备选 b（增设电源层）/c（B.Cu 信号改层）仍属 L1，未选。**几何不变性机判 + 全链 G4..G7 全 PASS、板逐字节同**。记录 `m13_v57_co74_pdn_bcu_rehost.json` `8e3bbfb0e197cf67` / 链 `m13_v57_co74_chain.json` `51dbb2076bc379e4`（CO-76 F1 后重基；原 `9b1a284d2bb61e67` 已取代） / 卡 `m13_v57_CO74_L2_pdn_bcu_rehost.md` `8c1cec7fb48ad2ab`。
> ⑪ **CO-75（L2 走廊分配/过孔策略 · 负结果）**：补足 CO-60/61 的**未覆盖维** —— 二者 WLO 恒钉 33.70（单旋钮）；WSTEP=1.580 下 lane 块仅跨 11.06mm 而板边可用带高 45.2mm ⇒ WLO 是独立自由度。以**真发射器**扫 `WLO(12) × WSWAP/COLMODE(3) × FANY_J3(5) × HOLE_GAP(3) = 23 组合`，**0 组 32/32 落位**（保真断言：1.05@33.70 = 32/32 PASS）；失败签名恒在芯片输入 via 区 `x∈[84,93]/y∈[50,58]`（`vt_intra`/`pad_via`/`vv_placed`/`vt_placed`，行扫 1.4e4~1.8e4 耗尽）⇒ **球栅逃逸硬限**，与 WLO/fan 旋钮无关。**① 仍维持 L1**（剩余自由度 = 逃逸层重导/球重映射/落列/板框/层数）。记录 `m13_v57_co75_west_pitch_origin_search.json` `c59e9955d344d75f` / 卡 `m13_v57_CO75_L2_west_pitch_origin_search.md`。
> ⑫ **CO-76（非执行者侧对抗评审 pass 1/2，CO-67..CO-75）**：宪法 `L2_STRUCTURE_v2.0.md:137` 要求重开层重过对抗评审，CO-69 仅执行者侧。本会话与 CO-67..73 执行者**非同一会话** ⇒ 具非执行者资格。**发现 3 项并修复**：**F1（中）** 引擎把陈旧层角色 `up=In6.Cu` 写进**生产图纸** `decision_contract.r1_5_layer_rule`（REV6 下 In6=GND，而实现本即 `up->In5.Cu`）⇒ 与 CO-72/73 同类缺陷但落在引擎/图纸；**F2（中）** CO-69 A5 只断言**带引号** `"In6.Cu"`，CO-68 改字面量后恒真 ⇒ 结构上漏检**未加引号**层角色文本（实测 14 处裸 `In6`）；**F3（低）** 10+ 处注释与同行代码矛盾。修复 = 文本类零几何（11 处改 In5；A5 改**裸 token 扫描** + 豁免 `In6->In5` 迁移注）。**机判 11/11 PASS** （C1..C11：层集/图纸字段/板层卫生/探针/引擎输入/①负结果/四源/while-free/阈值/rev-8 PDN）。全链重基线 G4 `22c2a158` / G5 `eac5eee6` / G6 板**逐字节同** `0e636a67` / G7 DFM new=0 + SI 0.1300；delta 精确 = `pages`/`route_geometry` 逐字节同、`decision_contract` 仅一字符串。记录 `m13_v57_co76_nonexecutor_review.json` `cf5b4ec0e880e5d2` / 卡 `m13_v57_CO76_nonexecutor_adversarial_review.md` `32d5868a1a2880b4`。**残余：pass 2/2（另一非执行者）仍欠**。
> ⑬ **CO-77（L2 声明一致性）**：把 CO-76 的判据扫到**收口声明件** —— boundary 中凡以「现行/主件/交付」口径引用的 sha16 必须等于当前实际文件。机判 `tools/p3_v57_co77_closure_declaration_sweep.py`（12 项身份断言）实测 v1.41 **4 项陈旧**：§6-1『现行 L4 板』`cdcb869e9827ec87`（实为 `0e636a67c1472462`）、§1 ⑤ 执行者对抗评审记录 `50ff390f2803f25d`（实为 `6daec5df8bf0d118`）、§1 ⑩ 链记录 `9b1a284d2bb61e67`（实为 `51dbb2076bc379e4`）、§1 CO-69 卡 `d472f16e73a57f3e`（实为 `661ad6c57e0e2418`）；且 v1.41 §1 与 §7 互不一致（同一工件两个 sha）。**本件全部校正并显式标注历史**，扫描 v1.42 = **PASS/0 陈旧**。记录 `m13_v57_co77_closure_declaration_sweep.json` / 卡 `m13_v57_CO77_closure_declaration_sweep.md`。
> ⑭ **CO-78（L2 声明一致性 · 回归闸）**：把 CO-72/73/76 的缺陷类固化为**可重复闸** —— 当前态工件中「平面层当信号层」或「信号层当平面层」的角色声明一律 FAIL（口径：signal=F/In2/In5/B；GND plane=In1/In3/In6；PWR=In4）。范围 = boundary §2 现行输入 + 链输出 + 引擎源码（共 22 件）。结果：**当前态 0 flag（PASS）**；阳性对照（历史 `SPEC_k2_v4_8L_LID1.json`，LID.1 下 In6=信号层）**DETECTED**（`/stackup/In6.Cu` = `"signal (PCIe + escape)"`）⇒ 闸有齿。**自检教训**：首版 walker 只扫字符串*值*，漏掉 `key->value` 编码的角色声明（对照件 0 命中 ⇒ 无齿），修正为同时扫 key 后才成立 —— **无阳性对照的闸不得宣称有效**。⇒ CO-72/73（SPEC）+ CO-76（引擎/图纸）+ CO-78（全范围闸）**关闭 F1 缺陷类**。记录 `m13_v57_co78_layer_role_drift_gate.json` `1599c8f043de58d5` / 卡 `m13_v57_CO78_layer_role_drift_gate.md` `0185363ec8ddf5f7`。
> ⑮ **CO-79（L2 验证质量 · 空真加固）**：把 CO-76 F2/CO-78 的教训（断言只查"它恰好知道的东西" ⇒ 未知输入被静默跳过）系统审计 A1..A9，发现并修 3 处空真路径：**H1 A6** `wmap.get(L); if exp is not None` ⇒ 线宽表外的层被静默跳过；**H2 A8** `sqer()` 未知层静默 `return 2.0`（伪装 er=4.0）且未断言真测到页面；**H3 A2/A4** 无覆盖下限。加固 = 守卫纯函数（`width_coverage_guard`/`map_scope_guard`/`numeric_floor_guard`/`unknown_layer_guard`）同时用于实检与负控；A6 另**显式计数**被跳过的 PCIE 过孔（实测 **252**，原静默）。新增 **A10 守卫负控**：坏输入必被抓到（如 `width_coverage_guard({"F","In6"},WM) → (False,['In6.Cu'])`），好输入必通过 ⇒ 守卫**自带可执行牙齿证明**。套件 **10/10 PASS**。记录 `m13_v57_co69_adversarial_review.json` `18a86c998dd6b4de` / 卡 `m13_v57_CO79_probe_vacuity_hardening.md`。
> ⑯ **CO-80（L2 可审计性）**：`k2_v4_8L.l4.kicad_pro` 是**受控**工件且被 `kicad-cli` 对 L4 板 DRC 时**自动选取**，但其设计规则与工艺意图不一致（`min_track_width` 0.09→**0.2**、`min_via_diameter` 0.35→**0.5**、`min_via_annular_width` 0.075→**0.1**、`min_through_hole_diameter` 0.2→**0.3**、`min_copper_edge_clearance` 0.3→**0.5**、`min_clearance` 0.1→**0.0**；另 4 项 silk/copper/via severity 由 ignore 变 warning）⇒ **最自然的独立命令**报 **880 条违规**（annular_width/drill_out_of_range/track_width/via_diameter 各 199 + copper_edge 11 + silk 警告），审计者会误判板子不合格。**先证伪自己**：在正确 staged（工程=意图件 + `.kicad_dru`）下用外部工具独立重跑并自算多重集差 —— 基线 42 / L4 42、**new=0 / disappeared=0** ⇒ 项目 DFM 判定被外部复现，880 条确系**规则设置产物**。**修复** = 把意图规则/severity 对齐进 `.l4.kicad_pro`（`62132712a65853b0` → `4704dec4dd043c59`，方向为采用意图件既有值，**未放宽任何阈值**）；修复后最自然的命令实测 42/42、new=0。**链不受影响**：板 sha `0e636a67` 不变、DFM `40445f87`/SI `73f9b59e` 逐字节不变、L4 applier 不覆写工程文件。记录 `m13_v57_co80_l4_project_rule_align.json` `d617a4c5e4e4523f` / 卡 `m13_v57_CO80_l4_project_rule_align.md`。
> ⑰ **CO-81（L2 可审计性 · 回归闸）**：把 CO-80 的 F-80-1 固化为闸 —— 每个**受版本控制**的 `*.kicad_pro` 的 DRC 设计规则必须等于**红线规则源** `_shared/eda_core/drc_rules.json`（`manufacturing` + `hole_clearance:min`，7 项，含键映射 `min_via_annular_width↔min_annular_width`），且 `rule_severities` 必须等于 JLC 模板 `tools/k2_jlc_template.kicad_pro`。理由：`kicad-cli` 对 `<board>.kicad_pcb` **自动选取**同名 `.kicad_pro`，规则不符则最自然的独立核查命令大面积误报。结果：**5/5 受控工程文件 PASS**（含模板与 CO-80 修复后的 `.l4.kicad_pro`）；牙齿：负控（`min_track_width=0.2`）抓 1 项、**历史对照 = F-80-1 修复前实测原值 → 抓 6 项失配**，即闸对真实发生过的缺陷状态可复现报警。记录 `m13_v57_co81_project_rules_gate.json` `a9161a86271c068b`（历史·CO-82 补网类后；原 `1f25c6a9db6923f0` 已取代）/ 卡 `m13_v57_CO81_project_rules_gate.md`。
> ⑱ **CO-82（L2 可审计性 · 补闸）**：`k2_v4_8L.l4.kicad_pro` 的 **net_settings 与意图件不一致** —— 仅 `Default` 一个网类、**`netclass_assignments` 为空**（意图件 4 类 + **146 条指派**），且 `Default` 自身偏严（clearance 0.2 vs 0.1、track 0.2 vs 0.09、via 0.6/0.3 vs 0.35/0.2）⇒ 用该受控文件跑 DRC 时 **PCIe85/LOW_SPEED/POWER 语义完全不生效**。**本件同时自认**：CO-81 的闸只覆盖 `design_settings.rules` + `rule_severities`，**未覆盖 `net_settings`**，故这条同类缺陷从闸下漏过 —— 本件一并**补闸**（新增 `netclass_guard`：按网类名逐字段 + 指派全量比对；模板显式豁免网类检查并记录理由）。修复：`.l4.kicad_pro` `4704dec4dd043c59` → **`ce2c2bf0da79a1ff`**（网类 1→4、指派 0→146）。**关键验证**：对齐后用最自然的命令重跑 = 基线 42 / L4 42、**new=0**，即施加完整 netclass 语义后板仍零新增违规 ⇒ 缺陷确系工件层；链不受影响（板 `0e636a67` 逐字节不变、DFM `40445f87`/SI `73f9b59e` 不变）。闸结果 **5/5 PASS**，牙齿：F-80-1 原值抓 6 项、**F-82-1 原状态抓 4 网类键 + 146 指派失配**。记录 `m13_v57_co82_l4_project_netclass_align.json` `0c8745064785ee57` / 闸 `a9161a86271c068b` / 卡 `m13_v57_CO82_project_netclass_gap.md`。
　同时**补强 CO-77 闸**：由「12 项 claim 模式」扩展为**全量 sha16 引用校验**（文中任何 `file` `sha16` 必须等于实际文件，除非显式标注历史或为「before → after」记法）—— 起因是发现 CO-82 卡片 sha 曾被写错而旧闸覆盖不到；v1.47 **65 条引用全数匹配 PASS**，牙齿：v1.46（引用被取代的 CO-81 闸记录）判 **CITATION_MISMATCH**。过程中我首次写该正则时双重转义致其匹配为空、v1.46 反而 PASS（**又一次空真**），已改正并加**非空真下限** `CITE_FLOOR=30`。
> ⑲ **CO-83（L2 可审计性 · 补最后一向）**：工程文件闸此前只比「工程 ↔ 意图工程」，未与**红线条文**交叉校验。本件令工程网类的 DRC 相关字段（`LOW_SPEED.clearance/track_width`、`PCIe85.clearance/track_width/diff_pair_gap/diff_pair_width`、`POWER.clearance/track_width`）必须等于 **SPEC `net_classes`**。结果：**0 失配**（PCIe85 clearance 0.175 / width 0.205 / p_gap 0.175 / p_width 0.205 等全中）。**疑似分歧已排除**：工程 `PCIe85.track_width=0.205`（标量）vs SPEC 内层交付 0.16 —— SPEC `p_width_scope` 已显式声明为设计意图（CO-68 对称叠层 85Ω 闭合），非缺陷。牙齿：**SPEC 侧负控**（篡改 `PCIe85.clearance`→0.2）被抓到 `[0.175, 0.2]`；连同 CO-81/82 的规则/网类负控，工程文件闸现覆盖 4 向（rules↔红线规则源 / severities↔模板 / net_settings↔意图工程 / **net_settings↔红线 SPEC**）。记录 `m13_v57_co81_project_rules_gate.json` `8ef7a02d7f3d2222`（CO-83 时值为 `ebd163058efaad14`，已取代） / 卡 `m13_v57_CO83_netclass_vs_spec_gate.md`。
> ⑳ **CO-84（L2 可审计性 · 放宽域闸）**：`k2_v4_8L.l4.kicad_dru` **放宽**逃逸区净距至 0.075（SPEC ECN-001）；**放宽类规则作用域过宽会掩盖真实违规**，故其必须与授权来源逐项一致。本件四向机判：净距（SPEC `escape_clearance_mm` = 域工件 = dru `min 0.075mm`）、域集合（dru `intersectsArea` = 域工件 `domains[].id` = **板内 4 个 rule area 名**）、层（全 F.Cu）、REFCLK 排除（域工件 `excluded_nets` = dru 条件）、溯源（dru 注释引用 sha256 = 域工件实件）、几何（域工件 `rect_mm` 与板内 zone bbox **逐值一致** tol 1e-6）—— **0 失配**，即放宽范围恰好等于被授权域。牙齿：4 个定点负控各命中 1 项（作用域过宽 / 净距 0.075→0.1 / 丢 REFCLK 排除 / 矩形漂移）。过程中自捕获一次**我自己的比较口径错**（`rect_mm` 序 `[x0,y0,x1,y1]` vs 我构造的 `[minx,maxx,miny,maxy]`）—— 归一后 0 失配，否则会把「一致」误报为「不一致」。记录 `m13_v57_co84_dru_domain_gate.json` `45fe68c41a8e1a4c` / 卡 `m13_v57_CO84_dru_domain_gate.md` `996bee590912e823`。
> ㉑ **CO-85（非执行者侧对抗评审 pass 2/2）**：对象 CO-67..CO-84（含 pass 1 因执行者身份排除的 CO-74/CO-75）。**V1 全链复现**（handoff §9 命令，G4→G7）：**12/12 交付件逐字节一致** —— drawing `22c2a15835857f99`（**CO-89 重基线后已取代**，现 `3d452429bbc934c3`；板/DFM/SI 仍逐字节同）、板 `0e636a67c1472462`、DFM `40445f87be664f31`、SI `73f9b59ed5f6f3ce` 等；**CO-89 已按新基线重跑全链并机判几何不变（板逐字节同）**；非执行者 pass 2/2 对**新基线**的复评仍欠（CO-85 复现基线随 rev-9 失效）；applier 复跑确为落盘重写（mtime 更新）非缓存短路；`git status` 零 tracked 漂移。**V2 闸牙齿**：co77（61/71 引用、floor 30、0 mismatch）/ co78（0 flag + 历史 LID.1 阳性对照 DETECTED）/ co81 / co84（4 定点负控各命中 1）/ co69 A1..A10 全 PASS。**V3 板事实独立直解**：2523 段（In4/In6 = 0）/ 252 via / zone 4 个全为 ESC_ 规则域 ⇒ **铜 zone = 0**。**V4** SPEC rev-8：power_zones=In4.Cu、`bcu_power_copper_policy=PROHIBITED`、`escape_clearance_mm=0.075`、`inter_pair_spacing_mm=0.875` 未放宽。**V5** CO-75 负结果独立复跑（23 探针 / 0 命中，基线 32/32）。**V6** 图纸 lane.y 独立复算：EAST 1.449（铜边 0.744）/ WEST 1.050（0.345）；1.580 重锚 ⇒ EAST y_max 80.284 > 78.5975 ⇒ 越板边 ≥1.687mm。**V7 逐层对间几何独立复算**：In5 0.550/+0.345、In2 0.580/+0.375、B 0.550/+0.345 **复现**；**F.Cu 实测 0.4921/+0.2871（板）/ 0.4627/+0.2577（图纸）**（见 F1/F2 与 §6-6）。**F1（中）**：原 F.Cu 行 1.124/+0.919「达 0.875」**不可由任何口径复现**（含全局/走廊内/长并行/水平等 7 种口径）⇒ 违反层数 **3/4 → 4/4**，文本已更正（零几何/零阈值）。**F2（高，裁决相关）**：J2/J3/J4 **焊盘节距 0.6mm** ⇒ 焊盘场同层对间铜边净空上限 0.6−0.205 = **0.395 < 0.875** ⇒ R3-2 作绝对规则在连接器引脚场**几何不可达**（与走廊轨距无关）。**自我捕获**：S1 via 首计 256≠252（`(vias` 记号误计，改精确块解析）；S2 intra-pair 伪 0.0（未排除同网共享端点）—— 均自捕获。本件零几何/零阈值/零冻结源改动，**不做 L1 裁定**。记录 `m13_v57_co85_nonexecutor_review_pass2.json` / 卡 `m13_v57_CO85_nonexecutor_adversarial_review_pass2.md`。
> ㉒ **CO-86（L2 自裁 · 走廊分配/叠层 SI）**：机判 handoff §6.6 Q1 的「备选」（铜跨 0.705→0.585 使 1.46 给 0.875，原注「L2 但需重定 8L 阻抗」）是否成立。判据闭式：**对间铜边 = 走廊轨距 − 铜跨 ⇒ 需 pitch ≥ span + 0.875**；硬上限全部取自 CO-85 独立实测（WEST 1.050 / 焊盘场 0.600 / EAST 1.449，机判保真断言）。结果 **`n_pass_all_caps = 0`**：span 0.705→需 1.580（WEST 差 +0.530、焊盘场 +0.980）；span 0.585（SPEC p_gap，w 不变）→需 1.460（WEST +0.410、焊盘场 +0.860）；gap 0.175 且重解 w 回 85Ω：外层 span'=0.561→需 1.436（WEST +0.386）、内层 span'=0.407→需 1.282（WEST **+0.232**、焊盘场 **+0.682**）。**焊盘场 0.600 < 0.875 与 span 无关 ⇒ 恒不可达（L1 级硬限）**；牙齿：可行 span 区间 [0.407, 0.705] 以 1µm 网格**全量**验证所需轨距 > WEST 上限（真下界非抽样）+ 3 项保真断言。附加发现：备选非免费 —— gap 0.295→0.175 在 w 不变下 Zdiff 88.4/82.0 → **81.9/74.1Ω**（内层出 85±10% 带）⇒ 须重解 w/叠层 + 券。⇒ **L2 侧无出口**；R3-2 0.875 只能由 L1 或红线口径修订解决。记录 `m13_v57_co86_l2_span_option_closure.json` `d0a59f85b74687d5` / 卡 `m13_v57_CO86_l2_span_option_closure.md` `0d1fd3b33fb802fe`。
> ㉓ **CO-87（L2 自裁 · 合格标准覆盖性）**：按《宪法》ch.5 §4（数学闭合：容量/长度/过孔/**PDN 压降**）与 ch.2（L2 裁判含 **热**）机判覆盖性：**CLOSED 3**（容量 `verdict=FEASIBLE_ALL`/failed=[]；长度 SI skew 0.13 ≤ 0.15；过孔 L4-F True/over=[]/total 252）+ **NOT_DEMONSTRATED 2**（**PDN 压降**、**热**：SPEC rev-8 全字段扫描 **0 命中**，扫描字段 3962）⇒ 显式登记为已知限制（§6-8），**不宣称 PASS、不判 FAIL、不以假设值代填**。牙齿：合成件注入 `load_currents` ⇒ 命中 ≥2（证明 0 命中是真缺）；宪法文本确含 `PDN 压降达标`（证明条款存在）；非空真下限 = 实扫 3962 字段；记录复跑逐字节一致。所需输入清单由 SPEC `power_zones[*].targets` **机器提取**。⇒ 本件不改变 G4..G7 判定，不触 L1；缺的是**数据**（PM/owner 提供），不是拓扑裁决。记录 `m13_v57_co87_l2_acceptance_coverage.json` `46d15557477d164b` / 卡 `m13_v57_CO87_l2_acceptance_coverage.md` `322baa098740b259`。
> ㉔ **CO-88（L2 自裁 · PDN 板实性）**：机判 `pd.zone_defs.power_pad_connect` 与 `pd.decoupling(_via_to_plane)` 的**板实性**（这三者是机读且被 `pdn_apply.py` 消费的铺铜决策）—— 三项全 **FAIL**：**A** 55/173 entries + 2 blocked 引用板上不存在的 ref（35 孤儿：C65-C72/R4-R12/R17-R27/**U3**/**U7**）；**B** 板实 SMD 电源/地 pad **309** 个，现行 SPEC 仅 118 覆盖 + 7 blocked ⇒ **184（60%）静默待定**（违 ch.5 §1）；**C** `pd.decoupling=C67_C68_C72_via_to_plane` 的 **3/3 ref 板上不存在** ⇒ 解耦规则零板实落点，而板实去耦集（C74-C83/C84/C90，见 `components.must_add`）无解耦决策。根因可追溯：红驱动 **U3(DN)+U7(UP) → U6(DS320PR1601, 354 球)** 合并，ppc 冻结基准自述为「101 fp 重建板，U3=DN/U7=UP」，从未板实化。**修复候选已派生**（项目自带确定性发生器 `pad_connect_gen` 对交付板重生成，scratch 即用即删）：entries 173→**223**、blocked 9→**86**、决策总数→**309/309=100%** 覆盖；候选 blocked 中 **U6 占 63/86**（GND 球在 0.5mm 球栅场内落不下 pad→via，属规则允许的显式 blocked；改判为可连接则需器件资料+SI/PI 依据）。**本件只判定+备料、不施加**：施加 = SPEC **rev-9** + 全链重基线，波及 **27 个文件**（引擎 `FROZEN_SHA`/validator/`co69` 探针/`co77` 引用闸(钉 `spec-rev-8`)/`co84`/`co81/83`/L4/L5），会重基线**刚过非执行者评审（CO-85）**的链 ⇒ 按冻结/评审纪律须作**独立变更单 + 重新过对抗评审**（禁 partial pass）。自我捕获：首版以正则数板实 pad 得 127（漏 U6 354 球 BGA 块），改用 pcbnew 真值 309 方得正确分母，否则会把 184 个无决策误报成 9 个（假 PASS）。本件不改 SPEC/板/阈值；不触 L1（3 域/4 平面/8 层不变）。记录 `m13_v57_co88_pdn_board_reality_gate.json` `17719cf7f8e3e702`（CO-88.3；原 `f90d65369cab92dc` 已取代） / 卡 `m13_v57_CO88_pdn_board_reality_gate.md` `50aa8c67d7b10438`。
> ㉕ **CO-89（L2 自裁 · PDN 板实化 / SPEC rev-9）**：施加 CO-88 的修复候选。**SPEC rev-9** `77f5c54df88bb0ca`：① `pd.zone_defs.power_pad_connect` 对**交付板**重生成（entries 173→**223**、blocked 9→**86**、决策 **309/309=100%** 覆盖、**0 孤儿 ref**）；旧 173/9 条（含 55 孤儿 entry + 2 孤儿 blocked）转 `retired_superseded_bom` 留存对账（不销毁可追溯性）；② `pd.decoupling` 由 `C67_C68_C72`（板上不存在）改为**板实按网集合**（P3V3{C74-C84}/MCU_VDD{C85,C86}/12V_IN{C88}/P3V3_AUX{C90}，机器派生），旧串转 `decoupling_legacy_retired`；③ `decoupling_via_to_plane.vias`（旧 C67/C68/C72 坐标）转 `retired_vias_superseded_bom`，改 `targets`=板实去耦集 + `geometry_status=L3_CONSTRUCTION_DERIVED`（坐标留 L3，不臆造）。**不变量机判**：L2 不变量（层数 8 / 平面 4 / 域集合 3 / 信号层 4）全不变，且 `pd` 以外**逐值等于 rev-8**（unexpected=[]）⇒ 属 L2。**全链重基线**：G4 `3d452429bbc934c3`（几何段与旧基线**逐字节同**，唯一 delta=`inputs_sha.spec`）/ G5 PASS frozen=True `7acb3186c3b68848` / G6 PASS viol 0（**板逐字节不变 `0e636a67c1472462`**）/ G7 DFM new=0（`40445f87be664f31` 不变）+ SI 0.1300（`73f9b59ed5f6f3ce` 不变）。**闸态**：co78 `b736a0df7226f155` / co81 `16b262663238a60a` / co84 `b927acbe46ec3007` 均 PASS（已随 rev-9 重扫）；co87 3 CLOSED/2 open 不变（扫描字段 3962→5995）；**co88 由 FAIL → PASS**（A/B/C 全过：0 孤儿 / 223 覆盖 + 86 显式 blocked / 解耦目标全板实）；co69 探针 10/10（`18a86c998dd6b4de` 不变）。**残余（如实）**：① 86 blocked 中 **U6 占 63**（0.5mm 球栅场内 GND 球落不下 pad→via；改判为可连接需器件资料+SI/PI）；② 本次重基线使 CO-85 复现基线失效 ⇒ **新基线非执行者复评欠**；③ PDN 压降/热仍缺输入（CO-87）。记录 `m13_v57_co89_pdn_board_realize_rev9.json` `4f94df5981aaab45`。
> 记录 `m13_v57_CO69_L2_option_a_chain.md` `661ad6c57e0e2418`（原 `d472f16e73a57f3e` 已取代）。**注意**：`CO-60` 候选 `..._v6.json`（`2ebda54c…`）为走廊 1.580 实验件，**未触碰**。
- `verdict = FEASIBLE_ALL`；`gate_status.failed = []`；`certificates = []`；`status` PASS。
- **A-CN 全 PASS**：1d 32/32、1a 0 miss、1b 0、2a/2b 0、3a 72/72、3b/3c 0、4 交叉 0、5a keepout 0、
  5b 页间 True、**5d REFCLK 同层交叉 0（P/N + 页间）**、6 序无关（验证器 3 枚举序 byte-identical）、
  7 重发射 satisfied、8 证书归因 0 unattributed、**9 完整净距 0/0/0（tt/vt/vv）**、method `work 546/546`。
- 规模：**34 页**（32 data 含 3D nodes + 2 refclk）、`route_geometry` **320 段**、页级 via **320**、`same_layer_crossings = 0`。
- REFCLK 2/2：见证 `kind=direct_channel`；图纸内 P/N 残余 skew **0.0**（P 轨等长幂绕补偿 3.5635/1.3635 见 CO-45）；
  板上 SI 实测 max intra-pair skew **0.0031 ≤ 0.15**（34 页全查，含 REFCLK）。
- F-12 原子重发射 `m13_v57_w3_chip_landing_rows.json`（64 行），`authority.main_sha256 == sha256(主件)`。
- **字节可复现（CO-49）**：L4 板 `cdcb869e9827ec87`；构建×3 与全链（构建→L4→L5）×2 均**逐字节一致**（板/construction/validation/fab/dfm/si/G7 记录 共 7 件）。
- **PDN 事实核验（CO-50）**：平面层为**保留层、尚未铺铜**（冻结源与 L4 的铜铺铜 zone 均为 **0**，机器统计）；L4 仅新增 4 个非铜 rule area + tracks ⇒ 无平面铜被改写（原 `planes_present` 断言已改为可机判事实）。
- **DFM 判据强化（CO-51）**：`new` 由「按类型计数差」升级为**多重集差**（键 = type + 参与者 description）⇒ 同类型对调不再被掩盖；并显式机判**基线消失项 = 0**（即验收项「无 <0.075 项消失」），实测 new=0 / disappeared=0。
- **过孔预算闭合（CO-52，宪法第五章第 4 条）**：L4-F 逐网对比 SPEC 显式上限（bandX 4 / bandY 6 / REFCLK 2）⇒ 实测 max 4 / 4 / 2，**全部合规**；`total_vias = 252`（68 网）。
- **⚠ 阻抗几何开放项（CO-53/CO-54）**：交付 34/34 对对内中心 **0.500**（边距 0.295）vs SPEC `diff_pair.p_gap 0.175`；对间最小中心 0.550（SPEC `inter_pair_spacing_mm 0.875`）；SPEC `stackup/impedance` 仍 **6L** 而板为 8L ⇒ 阻抗符合性原判 `NOT_DEMONSTRATED`（CO-55 后见下）。
- **CO-54（本件新增）**：把 CO-53 从单点扩展为**机判漂移清单**（audit `ba87413ae4d8c7b4`）：F2 对间最紧 0.550@In6 长平行带（29.1mm，归因更正）、**F3 SPEC 自身不自洽**（`net_classes` 派生 PITCH 1.46 vs `corridors.tracks_y` 1.20，Δ0.26）、F5 三处“85Ω 基准”互不同（79.9 vs 85.1 vs JLC 官方 prepreg εr）、F6 34 对中 32 对的决定性平行段在 **In2/In6（带状线）**而 SPEC 模型为微带、F7 交付对内 0.5/0.6/0.58 并存；交付步距集合 {0.5,0.55,0.58,0.6,1.2,1.45} 与 SPEC 三项（0.175/0.875/1.2）**无一自洽**。**门判定不变**（零几何/阈值改动）。
- **CO-55（本件新增，L2/SI 自裁）**：由**交付几何反解 8L 叠层要求**（不再索取板厂表）：`d(F.Cu–In1.Cu)=0.1164`（JLC 2116×1）、`d(In5.Cu–In6.Cu)=0.0994`（3313×1）、`b(In1.Cu–In3.Cu)=0.72`（对称 0.36+0.36 core）；余隙按 1.6mm 闭合（机判 delta=0.000）。此叠层下交付各档（gap 0.295/0.395…）落 **82.1–91.2Ω ⇒ 全部 85±10%**（一阶 IPC-2141，datum 85.05 vs 85.1）⇒ **几何零改动、无需 re-open**。回退：若板厂 b<0.582 则 In2 须按 `w*(b)` 重导（表见 CO-55 §4 R2）。**B.Cu 判非阻抗控制层**（参考层为信号层 In6）；In6 下方 B.Cu 不得并行铺铜/走线。**CO-53/CO-54 的输入缺口取消**（改下达要求 + 板厂券终判）。**已由 CO-56 落盘**。
**已由 CO-56 落盘**（见下）。
- **✔ CO-58（本件新增，L2/L3 对账 · 更正 CO-57 表述）**：并排换算四档口径 —— R3-2「0.875」（v1.1 requirement）/ v22 容量口径 1.46（=0.585+0.875）/ **冻结轨距 1.08**（v2.0 硬约束 2「冻结轨距仍 1.08（实际排轨居中值）」+ `mcio_learning_gate.md` §4.2「模板参数（生产过/结构冻结）track_pitch 1.08」）⇒ 铜边 **0.495** / 交付走廊 1.20+0.705 ⇒ 铜边 **0.495**（**与冻结口径同值 ⇒ 走廊不构成对冻结口径的偏离**）/ 交付芯片侧 In6 带 1.05+0.705 ⇒ 铜边 **0.345**（低于冻结 0.15）。⇒ **更正**：CO-57 的「交付违约 R3-2」属表述过当；0.875 在 v2.0 语境是 **capacity 口径**，实排轨距冻结值 = 1.08。**收窄待裁**：**Q1（L1）** R3-2 是 realized 要求还是 capacity 口径（realized ⇒ 需 1.580 全链重导，几何可行 12.64<N16.2/S20.8；capacity ⇒ 仅芯片侧 In6 带需重导至 ≥1.08）；**Q2（L2-ready，待 Q1 定标）** 芯片侧 In6 带重导。见 `m13_v57_CO58_interpair_baseline_reconciliation.md` `267621cdcfae1bbc`。
- **✔ CO-59（本件新增，L2 自裁 · 残余闭合 + 更正 CO-58 基线）**：① **残余② 闭合 PASS** —— L4 板 B.Cu×In6 并行耦合 **0 对**（夹角≤10°/重叠>0.3mm/横向<0.5mm），全板最小并行横向距 **20.3mm**，B.Cu 实体 70 段/32 网/**0 zone**，与 In6 为**垂交**关系 ⇒ CO-55「不得并行」已满足。② **口径再基（机判）**：`route_model_config.json` `71c001125959b24b` 的 `capacity_audit.inter_pair_spacing=1.46` + note「语义 = 0.875 对间铜边净空」为**要求注入点**；**1.08 是 `channel_alloc.pitch_fallback`（回退值）** ⇒ CO-58 以 1.08 为基线的「走廊一致」结论**成立性不足**。③ **交付板级实测**：EAST 对间距 **1.449**（铜边 0.744：vs 1.46 **−0.011** / vs 0.875 **−0.131**）、WEST **1.050**（铜边 0.345：**−0.410 / −0.530**）⇒ **两读数下均不达标**；CO-57 的 0.345 事实保留。④ 四方口径互不自洽（SPEC `tracks_y` 1.20 / SPEC 派生 1.46 / config 1.46 / 文本「口径统一 1.46」/ 模板 1.08）⇒ 收窄为 owner 单一问句：**是否授权走廊对间距 → 1.580**（= 0.705+0.875，歧义无关目标，同时满足 1.20/1.46/0.875；带高 7×1.580+0.705 = 11.765 ≤ N16.2/S20.8）。见 `m13_v57_CO59_L2_residual_closure_and_interpair_target.md` `0fdb19fec39bf110`；附：CO-54 audit 在 rev-4 下已重基线为 `69fcbcdd19025874`（v1.27/CO-58 引用的 `ba87413ae4d8c7b4` 为 rev-3 值，本件更正引用而不改工件）。
- **✔ CO-60（本件新增，L2 走廊分配 · 可达性机判 / 负结果）**：lane 步距为合法 L2 旋钮（重发 ALLOC.5 **逐字节复现** `0bf6cdc203887a48`）。冻结包络内机判：**西侧对间距 >1.05 即落位失败**（余量 <0.05；失败集中于芯片逃逸区 x≈93.2 球栅，`PCIE_UP6/UP7 input`，行扫 15148~15150 耗尽）；**东侧 1.580 可落位 32/32 且放置净距 0 违规**，但全链 **G4/G5/G6 PASS、G7 DFM FAIL new=84（copper_edge_clearance 83）** ⇒ 破板边铜距；**恢复冻结对铜跨 0.585（POL_OFF 0.19）⇒ 0/32 落位**。⇒ R3-2 realized 0.875（⇒ 中心距 1.580）在冻结 L1 包络内**不可达**，两端皆 L1 决策 ⇒ **L1 冲突**，依《LAYOUT_CONSTITUTION》第三章第 2 条升 owner。见 `m13_v57_CO60_L2_corridor_pitch_reachability_and_L1_conflict.md` `71dfd8f7d9dcd96d`。
- **✔ CO-61（本件新增，L2 · 策略维穷举 / 负结果）**：把搜索从"单旋钮"扩到 L2 **策略维**：① 西侧 对间距{1.20,1.46,1.58} × {无/有落列交换} × {colmode pol/默认} **9/9 全部落位失败**（失败点均为芯片逃逸区，行扫 ~15150 耗尽）⇒ 与策略无关，受**球栅逃逸硬限**；② 东侧 1.580 在 4 个走廊平面锚定（EDELTA −0.10/+1.0/+2.0/+3.0）下：3 个可落位但走廊 y_max 80.5~82.6 **越板边可用上限 78.5975**，第 4 个起 J2 侧逃逸落位失败 ⇒ **无可行锚定**（东侧 1.580 需 24.4mm > 可用 22.3mm）。⇒ L2 侧无可再自裁动作，L1 冲突成立。见 `m13_v57_CO61_L2_search_exhaustion_and_L1_conflict.md` `e11ef05202a578c6`。
- **✔ CO-62（本件新增，L2/SI 裁定 · 负结果）**：补核 CO-55/CO-56 残余条款**前半句**（「B.Cu 不得承载阻抗关键网」）。机判：本阶段 **68 条高速网中 32 条**在 B.Cu 上有铜，合计 **290.21mm**，单网最长连续 **17.87mm**；差分对 **P/N 的 B.Cu 长度失配最大 1.443mm**（5 对同值，系统性）。一阶 Zdiff（同 CO-55 模型）：F 88.4 / In2 82.0 / In6 85.5 均落 85±10%，**B.Cu 单参考(In6 信号层, h=0.1836) = 119.1Ω ⇒ 超出带（+34）** ⇒ B.Cu 无法承载 85Ω。二阶：层混合致电气 skew 一阶 0.03~0.16mm 内层等效（悲观档超 0.15mm 预算），现有 SI `skew`（纯物理长度 0.0031）**未覆盖**该机制。⇒ **L2 裁定：维持并强化 CO-55 条款，现交付违反**；整改 = 16 张 dn 带页逃逸/stub 层移出 B.Cu（LID 新修订 + 全链重导 + SI 判据改按层加权）。见 `m13_v57_CO62_L2_Bcu_impedance_carrying_ruling.md` `691ed6991c9957fe`。
- **✔ CO-63（本件新增，L2 → 更正为 L1）**：按 L2 权限直接试做 CO-62 的整改（层分配）：两个 **B.Cu-free** 逃逸层计划均 **FAIL** —— A（dn→In2/up→In6）**18/32 落位 + 1 违规**；B（east→In6/west→In2）**12/32 + 11 违规**（违规均为 F.Cu 段-焊盘 `sp`）。根因：4 信号层中 F.Cu 被 SMD 焊盘占用、In6 为 lane 层（逃逸入 In6 必自交）、In2 已给西侧逃逸 ⇒ **B.Cu 是唯一剩余逃逸资源**，其使用是**承载性**的。⇒ **更正 CO-62 的定层**：该项整改**不能由 L2 完成**，根因是「外层 B.Cu 无邻接平面」这一**包络/拓扑**事实 ⇒ **第二项 L1 冲突**。见 `m13_v57_CO63_L2_Bcu_free_layerplan_infeasible.md` `50f1c0913788044d`。
- **✔ CO-64（本件新增，L2 叠层分配 · ECN）**：依 L2_STRUCTURE_v2.0.md:126「8L 重入 ECN 触发条款」（三条实质条件已由 CO-60/61/63 机判成立）发起 ECN。根因：冻结派生 `total=2*L_signal` + 家族 `F/G/S/G/[P/G]/S/B` **必然**使最外层 B.Cu 无邻近参考平面，而 B.Cu 又是逃逸所需第 4 信号层 ⇒ 自相矛盾。叠加修正规则（每信号层须有参考平面）后重推：**8L 有解但须重排平面位置**（与冻结平面用途红线冲突，属**电源域划分=L1**）；若保留冻结平面用途则最小 **10L**（`F(S)/In1(G)/In2(S)/In3(G)/In4(P3V3)/In5(G)/In6(S)/In7(G)/In8(S)/B(G)`，B.Cu→GND，多 1 层内部信号层，对 ① 亦有利，属**层数裁决=L1**，文档 :136 明文）。⇒ 两项 L1 冲突统一为二选一决策。见 `m13_v57_CO64_L2_LID_reentry_ECN_stackup.md` `02051da11ce89e7f`。
- **✔ CO-65（本件新增，L2 收口 + L1 决策请求）**：①**修正 CO-62 铜厚口径**——B.Cu 按外层 1oz（t=0.035）重算为 **113.0Ω**（CO-62 记 119.1Ω，结论同为超带），且达 85±10% 需 **d(B.Cu–邻平面) ≤ 0.127mm**（现 0.1836）⇒ 仅加参考平面不够，叠层**厚度**亦须重推。②**机助证明 8L 不可兼得**：冻结平面 4 层 + 需 4 信号层恰为 8 层，而 B.Cu 唯一邻层是 In6 ⇒ B 有参考则 In6 必为平面，与 In6∈信号层矛盾；穷举全部 6561 个层序列，满足条件的 8L 解 16 个、**保留冻结平面用途的 0 个**。⇒ 两条整改：(a) 8L 重排平面用途（板厂成本不变，须放宽平面用途红线）/ (b) 8L→10L（保留全部平面用途、多 1 层内部信号层对 ① 亦有利，属层数裁决）。**建议 (b)**。见 `m13_v57_CO65_owner_decision_brief_stackup.md` `f1306a91ce8c98a4`。
- **✔ CO-66（本件新增，L2 叠层分配 · 归口更正）**：**更正 CO-65 §3** —— 方案(a) 层数/平面数/电源域**均不变**（仍 3×GND + 1×P3V3 同网），只改平面**位置与厚度** ⇒ 属 **叠层分配 = L2**（与 `L2_STRUCTURE_v2.0.md:136` 一致）；**仅方案(b) 需 L1（层数裁决）**。并经机判给出 8L 对称叠层（`F(S)/In1(G)/In2(S)/In3(G)/In4(P3V3)/In5(S)/In6(G)/B(S)`）的**厚度自洽解**（10 组可行；例：外层 w=0.205/h=0.1101，内层带状线 w=0.130/b=0.4134，自由余隙 0.553，1.6mm 闭合，各层 85.0Ω）⇒ 代价 = **内层线宽 0.205→0.13~0.19 的几何协同变更**。执行清单（LID REV6 / SPEC rev-5 / 几何重解 / 引擎 bump / G4..G7 / SI 按层加权 / 重新对抗评审）见 CO-66 §3。见 `m13_v57_CO66_L2_option_a_stackup_derive.md` `72ec6c4dbdb4a75c`。
- **⚠ CO-57（本件新增，L1 升级 · owner 待裁）**：L1 冻结强条 R3-2『**对间铜边净空 ≥0.875mm**』（`L1_TOPOLOGY_v1.0.md` 硬约束 3 / `v2.0.md` 硬约束 2「口径统一 = 1.46」，v22 用户裁决）vs 交付实测：走廊轨距 **1.200**（−0.260）、对内铜跨 **0.705**（使 1.46 只给 0.755 净空）、对间最紧铜边 **0.345**（In6 长平行带）。按现行铜跨满足 R3-2 所需中心距 = **1.580mm**（8×1.580 = 12.64 < N16.2/S20.8 ⇒ 几何可行但需全链重导）。三选项：**A** 重开 W3 走廊至 ≥1.580（L1 裁，触及落列/球行派生走廊行）/ **B** 回退铜跨 0.705→0.585 恢复 1.46 口径（L2 可执行但与 CO-10 裁定冲突）/ **C** 正式修订 R3-2 阈值（**L1/owner 明示**）。**本件零几何/阈值改动、不预判**；裁定前**不得声称对间间距合规**。见 `m13_v57_CO57_L1_escalation_interpair_clearance.md` `e99f58e06730daaf`。
- **CO-56（本件新增，L2/SI 自裁 · SPEC ECO rev-4）**：`SPEC_k2_v4.spec-rev-4.json` **`1c4eecb0edf4a446`**（**纯加性**：8L 声明 + `stackup.dielectric_8l` 逐层介质表 + `impedance.per_layer` 分层口径 + `p_gap_semantics=lower_bound`/`inter_pair_spacing_scope`；**所有数值阈值未改**）。同步 bump：引擎 `F.spec`/`FROZEN_SHA`、validator 冻结集、L5 记录 rev **L5-SI.5**。**几何不变性机判**：新图纸 `4e7497daf97cebd1` 与原 `dfa1d7c4a811b0da` 的 `route_geometry`/`pages`/`decision_contract`/`layers`/`method` **逐字节相同**（仅 `inputs_sha`/`frozen_sha_check` 指纹重基线）；**板 `cdcb869e9827ec87` 逐字节不变**。**复跑**：G4 FEASIBLE_ALL、G5 PASS（frozen=True）、G6 PASS（viol 0）、G7 PASS（new=0 / 在册未连 0/68 / skew 0.0031）；**重跑零漂移（不动点）**。PI 项状态 → `DESIGN_CONFORMANT_FIRST_ORDER_PENDING_COUPON`（终判=板厂券）；**残余**：对间串扰复核（0.345 vs 基线 0.875）与 B.Cu 非阻抗控制层声明（见 CO-54 F2/F3）。

> ㉖ **CO-93（L2 自裁 · PDN 权威净距重落 / SPEC rev-10）**：CO-91 判 rev-9 计划坐标违反冻结规则源（via 83/312、短段 75/223）后，**依 LAYOUT_CONSTITUTION 第二章自裁 L2**（via 策略/PDN 承载属 L2，不升 owner）：① 一律按权威口径重落（`required=max(netclass a,b,board_min)` + `min_hole_clearance` + **层语义**，via 亦为障碍、支持盲/埋孔）；② **无合法位者转显式 `blocked`**（**不放宽任何阈值**；旧坐标退役留存 `retired_superseded_clearance_v1`）；③ **不默认采用 via-in-pad**（需工艺能力 + SI/PI 证据）；④ pad→via **短段宽度 0.5 → 声明 0.2mm**（= `min_track_width` 可制造下限），短段不合法则该 pad 亦 blocked（`entries` 语义收紧为「整条连接合法」）；⑤ 候选 palette **声明固定、确定性序、无坐标搜索**（原位 → 4 正交 @(via_r+0.3) → 4 正交 @0.6）。**SPEC rev-10** `4416e42eed10cb8c`：ppc entries **223→189** / blocked **86→120**（决策覆盖仍 **309/309**；**已连接 223→189，−34 如实登记**）、`gnd_stitch_via` 69→**40 落（28 原位+12 移位）/ 60 blocked**、`power_zones[].vias` 20→**17（+4 移位）/ 3 blocked**；`pd` 以外**仅 `spec_version` 变**。**验证**：CO-91 对 rev-10 **PASS（via 246 目标 0 违规、短段 189 目标 0 违规、牙齿 4/4）**；CO-92 对 rev-10 = **不动点**（189/0/0、40/0/0、17/0/0）⇒ 声明策略自洽稳定。**全链重基线**：G4 `FEASIBLE_ALL` `9c099dd7ba0c3478`（几何段逐字节同，delta=`inputs_sha.spec`）/ G5 PASS frozen=True `c6a9e0fd4291a8b3` / L4 construction `3f8aa96b4f39a793` + val `fbe5d7a72c08860`（viol 0）/ G7 fab `4586dd4263d9e9cb` + **DFM new=0（`40445f87be664f31` 不变）** + **SI 0.1300（`73f9b59ed5f6f3ce` 不变）**；**板逐字节 `0e636a67c1472462` 不变**。**闸态（随 rev-10 重扫）**：co78 `3609268f4267053a` / co81 `ecb12c992ae514a3` / co84 `49e0aa218527daac` / co87 `21b740182f4a2869`（3 CLOSED/2 open 不变）/ co88 `679de2b7a23b8885` PASS / co69 10/10（`18a86c998dd6b4de` 不变）。**残余（如实）**：① 已连接 −34（多为 U6 0.5mm 球栅场电源/地球）在冻结 8L 通孔工艺下无合法连接位 ⇒ 保连接数需 via-in-pad（工艺）或 HDI/微孔（**L1：层数/叠层**）；② `_shared` 引擎（容器副本**只读冻结**）未改 ⇒ rev-10 生成器 = k2 决策层工具，引擎通用化 + `gnd_stitch_gen` 障碍集改实际铜 + `pdn_apply` 短段宽度读 SPEC 登记为后续；③ **本次重基线 ⇒ 非执行者复评欠（CO-94）**。记录 `m13_v57_co93_pdn_rev10_derive.json` `663cb40e827984dd` / 卡 `m13_v57_CO93_pdn_rev10_authoritative_clearance.md` `9d9aaab835ba31a9`。

> ㉗ **CO-94（L2 自裁 · PDN 可连接性闭合判定 + 裁定）**：rev-10 把 34 个 pad 转 `blocked`（已连接 223→189）后，L2 必须回答「在 L2 手段内（外部通孔 + F.Cu 短段，**不含** via-in-pad / HDI）这 34 个是否真的不可连接」。以**存在性判定**（宽松有限家族：8 向 × r=0.30…1.80 step 0.05；判据 = CO-91 同一权威检测器，via **且** 短段合法）逐 pad 取最小可行半径：**全部 120 blocked 中 28 可连 / 92 不可；本轮关注的 34 中 15 可连 / 19 不可**。**裁定 = 维持 `blocked`**，三条理由：① 可连位只存在于**未声明的 31 档半径搜索式家族**中（且 **7 个仅在家族上限 1.80mm 命中**）⇒ 采用即把「搜索」写入决策，**违「零坐标搜索 / 一次求解」红线**；② 可连者净距余量低至 **0.0136mm（13.6µm）**、短段余量低至 **0.012mm**，属「规则内、工艺外」贴线解；③ 需 **1.35–1.80mm** 长 F.Cu 短段穿越 0.5/0.6mm 节距球栅场（电感/回流一阶影响，未经 SI9000/券），换 15 pad 不划算。⇒ **34（及 92/120）在 L2 手段内判为不可连接**（`blocked` 为诚实处置，非 PASS）。**升级（L1/工艺）**：U6（0.5mm 节距 354 球）与 J2/J3/J4（0.6mm 节距）的 blocked 电源/地球若须连接，只能靠 **via-in-pad（板厂工艺能力 + SI/PI 证据）** 或 **HDI/微孔（层数·叠层裁决，属 L1）** ⇒ 监理升级人工。记录 `m13_v57_co94_blocked_recoverability.json` `617e0973e6132e46` / 卡 `m13_v57_CO94_blocked_recoverability_ruling.md` `cbfb27c1f0db0fc5`。

> ㉘ **CO-95（L2 自裁 · PDN）In4 平面可达性 + 陈旧 keepout band 退役 / SPEC rev-11**：`power_pad_connect.entries` 的 via 必须落在**本网 In4 铜**上才构成真实连接，而既有闸（CO-88/89/90/91）**只判引用/覆盖/净距**，无闸判**平面可达性**。机判（`co95_in4_reachability`，牙齿 2/2）55 个 power entry：**35 `covered_explicit` / 8 `covered_bridge_target` / 6 `l3_obligation` / 6 `needs_region_ruling`**。**L2 裁定**：① `in4_pcie_keepout_band` 的启用前提（「wp1_escape_nets 在 In4 有 14 段走线」）**已被 CO-74 判定失效**（引擎 palette 无 In4 / 交付板 In4 段数 0 / layer_plan 仅把 In4 声明为 PDN 平面）⇒ **退役**（band 范围 + void 理由留存 `retired_in4_keepout_band_6l`）；② 废止 `P3V3_EAST` 由 band 推导的西界（88.17+0.2），改由**「与异网 In4 铜边 ≥0.2mm」**决定、落点 L3 派生；③ 新增 `plane_reachability_requirement`（via 须被本网 In4 铜覆盖 / 同网连续 / 异网 ≥0.2mm / L3 确定性派生）；④ 登记残余 12 项。**效果**：6 个 U6 P3V3 球（AC17/AC20/AK17/AK20/T17/T20）原被失效 band 排除在 In4 之外 ⇒ 退役后转为 **L3 可达性义务**。**SPEC rev-11** `d85f10f722ba22b0`（`pd` 外仅 `spec_version` 变）。**验证**：G4 `FEASIBLE_ALL` `e0a4dfd7936372f9` / G5 PASS frozen=True `a252ba52d0d05442` / L4 viol 0 `09ed9530f6da65f3` / L5 fab `afe849cfd5228515` + **DFM new=0（不变）** + **SI 0.1300（不变）**；**板逐字节 `0e636a67c1472462` 不变**；闸态 co78 `25f72d58a6a68b06` / co81 `8e7f4108610d4a5d` / co84 `18ffce1d876f53fc` / co87 `f9fd3f87cea224b0` / co88 `4db0a5d796d75f28` 全 PASS、co69 10/10 指纹不变、**CO-91 对 rev-11 PASS（0/0）**、CO-92 对 rev-11 不动点、CO-95 = `OPEN_needs_region_ruling`。**升级（一句话，L1/区域划分）**：6 项 `needs_region_ruling` ⇒ `12V_IN` **无任何 In4 区**（C88.1/U2.4/U2.6，且板上无该网铜）需裁承载；`P3V3_AUX` 西侧 3 pad（C90.1/R1.2/U1.15）所需区域与**西区名义网 MCU_VDD** 冲突需裁归属。记录 `m13_v57_co95_in4_reachability.json` `4525e38330ee599f` / `m13_v57_co95_spec_rev11_band_retire.json` `0ec682d3d15f84d5` / 卡 `m13_v57_CO95_in4_plane_reachability.md` `0bdac108e4563238`。
> ㉙ **CO-96（非执行者侧对抗评审 pass 4/4 · 对象 rev-11）**：独立会话（非 rev-10/rev-11 执行者）对 CO-91/92/93/94/95 + 全链 + 不变量做对抗复核，判 **`REVIEW_DONE_FINDINGS_OPEN`**（基线身份 OK / 牙齿 OK）。**指定三问**：Q1 `plane_reachability_requirement` **不可机判闭合**（几何真覆盖仅 35/55，14 待 L3、6 待 L1；gate 恒不返回 PASS）；Q2 两次重基线间**有 1 处未登记漂移**（F1）+ 1 处陈旧（F5）；Q3 CO-95 分类**完整**（55=35+8+6+6）。**6 项发现**：**F1**（中·谱系/红线邻近）rev-10 重建 ppc 时**静默丢弃** CO-89 的退役留存键 `retired_superseded_bom`（pre-rev-9 冻结 BOM 173/9 + 孤儿 55/2；`p3_v57_co93_pdn_rev10_derive.py` 零引用、变更说明未登记）⇒ 现行谱系断链，数据可由冻结源 + CO-89 记录找回；**F2**（中）可达性要求为「声明可闭合」——8 个 `covered_bridge_target` 命中桥区 `polygon=None`（几何未建）；**F3**（中）`needs_region_ruling` 对 P3V3_AUX 西侧 3 pad 依赖 `why` 自由文本子串（改文本即 L1→L3 静默降级）；**F4**（中）可达性 scope 仅 ppc entries，`gnd_stitch_via` 实落 40 / `power_zones[].vias` 17 无闸；**F5**（低）`board_realized` 仍记 223/86（决策 189/120，未被 pdn_apply 消费）；**F6**（低·潜在）co95 `in_poly` 用 bbox 非真 PIP（现行 polygon 均轴对齐矩形 ⇒ 无实害）。**复核 OK**：V1 rev-9→rev-10→rev-11 `pd` 外**递归深比 0 变更**；V2 分类完整；V3 SPEC stitch blocked schema 与 `pdn_apply` **对齐**（60 跳过/40 施加；§6-16「schema 未对齐」仅指上游 `gnd_stitch_gen`）；V4 gnd_stitch 重复坐标 (133.83,59.1)×2 系**声明共享单孔**（非缺陷）；V5 冻结四源 4/4 MATCH。**只读；不改 SPEC/板/阈值/冻结源/引擎；F1 须 rev-12 变更单闭合。** 记录 `m13_v57_co96_nonexecutor_review_pass4.json` `8b591e5030aca11d` / 卡 `m13_v57_CO96_nonexecutor_review_pass4.md` `56d1a1b421dda943` / 工具 `p3_v57_co96_nonexecutor_review_pass4.py` `4fc740b459624691`。
> ㉚ **CO-97（L2 自裁 · 可审计性）退役留存完整性闸 + 显式登记册（关闭 CO-96 F1 的『静默』面）**：把红线「退役几何/决策必须**显式留存**（不得静默放弃）」固化为**可重复机判闸**——逐版枚举退役留存块（首段含 `retired`）、逐相邻版本求 drop，**任一 drop 必须在登记册显式登记**（键 + `from_rev→to_rev` + reason + recovery），另拒**陈旧登记项**与**不可解析找回指针**；另带牙齿 3/3（未登记 drop 必抓 / 已登记必放行 / 陈旧项必抓，均合成注入）。**L2 自裁**：选 CO-96 F1 的『**或显式登记其移除**』分支，而非为纯溯源字段单独重基线——该键与 `board_realized` **均不被 `pdn_apply` 消费**（无几何/功能影响），重基线会使刚出具的 CO-96 证书失效并新增复评债 ⇒ **不成比例**；「SPEC 内回填」列为可选后续、随下一次构建期 SPEC bump 一并处理。**结果**：退役块 rev-8 5 → rev-9 8 → rev-10 13 → rev-11 15；**drop 恰 1 处**（`power_pad_connect.retired_superseded_bom`，rev-9→rev-10）**已登记 + 3 条找回指针全可解析** ⇒ **verdict PASS**（undeclared 0 / stale 0 / recovery_bad 0）。**附带**：登记册显式记 `board_realized` 为 CO-89 派生记录（非现行决策），消除 CO-96 F5 的误读。**零 SPEC/板/阈值/冻结源/引擎改动**；不重跑链路。**L2 自裁（`_shared` 处置）**：**不解冻冻结副本**；施工侧三项（`gnd_stitch_gen` 障碍集改交付板实际铜 / `pdn_apply` 短段宽度读 SPEC / blocked schema 对齐）**改由项目内引擎承载**，且**仅在 PDN 施工期激活**（当前板逐字节不变、PDN 未施工 ⇒ 非在役缺口）。记录 `m13_v57_co97_retirement_retention_gate.json` `4b1ee8924147a4f4` / 登记册 `m13_v57_retirement_registry.json` `4b13b538ba8e28ce` / 卡 `m13_v57_CO97_retirement_retention_gate.md` `2bc80fbe0c62bfd4` / 工具 `p3_v57_co97_retirement_retention_gate.py` `e9427f0f18087a18`。
> ㉛ **CO-98（L2 自裁 · PDN 可审计性）In4 平面可达性义务状态报告（机判化 CO-96 F2/F3/F4；关闭 F6）**：**F6 修复** —— co95 `in_poly` 由 **bbox 近似**改为**真·射线法 PIP**（工具 `tools/p3_v57_co95_in4_reachability.py` `4d87484ff2f1ecc7`，取代 `a2e16d6e08eef731`）；现行 2 个显式 polygon 均轴对齐矩形 ⇒ **输出逐字节不变**（co95 记录 sha 于该时点为 `61db48a283beeaae`（已取代；现行 = `f1c0c17ee7b379a4`），CO-95/CO-96 该次引用不失效）= **行为中性加固**。**F2/F4 机判化（不改 requirement；改 scope/谓词属 SPEC 变更 = 后续 rev-12）**：新增只读报告闸 co98（**不改 co95 记录字节**），输出 **三态** `geometric_covered` **35** / `declared_pending_l3` **14**（8 桥区 target 声明 + 6 band 退役义务，几何待 L3 派生）/ `ruling_pending_l1` **6**，`machine_closable_today=false`（verdict **永不 PASS**）；**scope 排除** `gnd_stitch_via_realized` **40** / `power_zones_vias` **17** / `decoupling_vias` **0**（本 requirement 只覆盖 ppc 非 GND entry）。**F3 裁决依据分解**：6 项 ruling 中 **5 机判可判**（3× `net_has_no_in4_region`(12V_IN) + 2× `via_inside_other_net_in4_polygon(MCU_VDD:MCU_VDD_WEST)`(P3V3_AUX 西侧 C90.1/U1.15)）、**1 仅文本**（`P3V3_AUX R1.2` @[51.725,37.0]）⇒ 建议改机判谓词并补 R1.2 判据。牙齿 2/2（PIP 拒 bbox 假阳 / 完整性抓计数不符）。**零 SPEC/板/阈值/冻结源改动**；**不改 co95 记录字节**。记录 `m13_v57_co98_reachability_status_report.json` `19c206378ee8fe95` / 卡 `m13_v57_CO98_reachability_status_report.md` `84a609e6f5e54503` / 工具 `p3_v57_co98_reachability_status_report.py` `11bfb844d542df6f`。
> ㉜ **CO-99（L2 自裁 · PDN 施工就绪性）计划集互相冲突闸 + 施工 dry-run（两个覆盖缺口）**：既有 PDN 闸（CO-88/91/92/95/98）与 CO-96 复评**都只判「计划几何 vs 板*已有*铜」** ⇒ 两处盲区：**G1** CO-91 `Scene` 仅由板构造 ⇒ **via-via / stub-via / stub-stub 互相零判**；**G2** 项目规则源 `drc_rules.json` 的 `hole_clearance.same_net_exempt=True` **不含** KiCad 板配置 `min_hole_to_hole=0.25`（net-agnostic）⇒ 同网 stitch 靠太近不可见。⇒ **CO-91 PASS 不蕴含可施工**。本件把工件驱动过真实消费面（`eda_core.pdn_apply` + `kicad-cli pcb drc`，scratch，交付板逐字节不变）：**verdict = `FAIL_MUTUAL_SHORT`** —— SPEC 宽 0.2 ⇒ **7 异网重叠（3 via-via + 4 stub-via）+ 35 净距 + 39 孔距（含 2 同址）**；引擎实落宽 0.5 ⇒ 13 + 127。7 个重叠全在 **U6 0.5mm 球栅场**（如 `P3V3@(84.775,53.5)` vs `GND@(84.574,53.59)`，d=**0.2202 < 0.35**）；2 同址孔 = CO-96 记为『声明共享单孔』的 `(133.83,59.1)`/`[47.0,49.0]`（声明可解释、`pdn_apply` 仍落两 via）。**施工 dry-run**：DRC **42→274（+232）**、未连 348→191（逐类型参考：clearance ~124–131 / shorting_items ~43–47 / hole_to_hole 37 / hole_clearance ~19–22 / holes_co_located 2）。**根因**：① 计划集互避缺失；② 短段宽 0.5 未读 SPEC；③ stitch 互距/去重缺失；④ 规则源缺 `min_hole_to_hole`。**修补未施加**（见 CO-100）。牙齿 2/2。记录 `m13_v57_co99_pdn_mutual_conflict_gate.json` `1d256de815b1ed87` / 卡 `m13_v57_CO99_pdn_mutual_conflict_gate.md` `c47249d3538c1d8c` / 工具 `p3_v57_co99_pdn_mutual_conflict_gate.py` `78762b3d9de90fd4`。
> ㉝ **CO-100（L2 自裁 · PDN）CO-99 互冲的互障感知修复候选 —— rev-12 能否自解？**：用与 CO-92 同一套**声明 palette**（ppc：current → pad 4 正交 @(R+0.3) → @0.6；stitch/zone：current → 原位 4 正交 @0.6）+ **互障 = 板已有铜 + 已接受计划件** + **孔距 net-agnostic ≥0.45**，按**声明固定序**确定性重放（零 while/零搜索）。**结果 = `PARTIAL`**：残余异网重叠 **0**（互冲可清）；ppc kept **124** / relocated **61** / blocked **4**，stitch 34/5/**1**，zone 13/4/0 ⇒ **5 项新增 blocked（4 ppc + 1 stitch）**（**CO-103 校正**：原记 kept 126 / relocated 58 / blocked 5 ⇒「6 项、全在 U6 0.5mm 场」为过期读数；CO-100 记录 tally 重跑**逐字节可复现**）。**裁定**：互冲本身 **L2 可解**。**CO-103（证据链校正）**：4 项 U6 ppc 新增 blocked 的自身 rev-11 位置对板铜**干净**，阻塞全为**同网 GND 相邻 U6 计划孔距互障**（d=0.180–0.403 < 0.45mm），另 1 项为 J2 扇出 GND stitch 同址重孔对 ⇒ 属**同网冗余竞争**，与 CO-94 的 120 项板铜阻塞**不同类**；固定序探针（同 palette/同检测器仅换序）显示 canonical 的 4 项为所试最优、但每对幸存成员随序翻转 ⇒「保连接数须 via-in-pad/HDI」**未被证明**。⇒ rev-12 决策点：`(a)` 显式登记接受 5 blocked（纯 L2）或 `(b)` L2 冗余归并裁定（相邻 GND 球择一/桥接）；**不得**未加证明即升 owner 取裁 HDI（层数）。**本件不施加**。记录 `m13_v57_co100_pdn_mutual_repair_candidate.json` `11e21f3b97bac66b` / 卡 `m13_v57_CO100_pdn_mutual_repair_candidate.md` `ff1c267f74f578dc` / 工具 `p3_v57_co100_pdn_mutual_repair_candidate.py` `341314590ceb154a`。
> ㉞ **CO-101（L2 自裁 · PDN 施加）rev-11 → rev-12 计划集互障重导**：把 CO-100 的候选**施加**为 SPEC rev-12 —— ppc entries **189→185**（kept 124 / **relocated 61** / **新增 blocked 4**；blocked 120→**124**）、`clearance` 按板侧 Scene 重算；stitch **relocated 5 + 新增 blocked 1**（原 60 blocked 保留）；power_zones vias **relocated 4**；rev-11 原坐标显式留存（`retired_superseded_mutual_conflict_v1` / `power_zones_via_retired_mutual_conflict_v1`，禁静默放弃）；**F5** `board_realized` 同步为 rev-12 决策数；**F1** 自 rev-9 回填 `retired_superseded_bom`。**验证**：G4 `FEASIBLE_ALL` `cb955e9af8782d08`（34 页/crossings 0/work 546/546）、G5 PASS frozen=True、L4 viol 0、L5 DFM new=0 + SI 0.1300；**板逐字节 `0e636a67c1472462` 不变**；**CO-99 由 `FAIL_MUTUAL_SHORT` → `PASS`**（重叠/净距/孔距 全 0）；CO-91 PASS、CO-92 `CANDIDATE`、CO-95/98 不变、co88/co97 PASS。**残余（非 PASS）**：引擎 `add_track(width=0.5)` 字面量 + 不去重 ⇒ dry-run 仍 **+34**（rev-11 = +232），属施工侧项目内引擎承载；**5 项新增 blocked（4 ppc + 1 stitch；同网孔距竞争，见 CO-103 F-B）** 需 L2 冗余归并或显式登记接受（**不得**未加证明即称需 via-in-pad/HDI）。**review debt = CO-102**（本件为执行者，不得自评；co96 对 rev-11 的证书随之失效、现按 fail-closed 报 BASELINE_MISMATCH）。零几何搜索（坐标全来自 CO-100 声明 palette 重放）；历史件不改。SPEC rev-12 `1a381b06454dbe2c`；记录 `m13_v57_co101_pdn_rev12_derive.json` `cdeea6a3950f04f6`；卡 `m13_v57_CO101_pdn_rev12_derive.md` `d47eda01e3092114`；工具 `p3_v57_co101_pdn_rev12_derive.py` `977ee54f0ecdb414`。
> ㉟ **CO-102（L2 自裁 · 项目内引擎承载）修正版 PDN 施加器 —— 施工侧闭合**：冻结 `_shared/eda_core/pdn_apply.py`（容器副本只读）有三处施工侧缺陷（① `add_track(..., width=0.5)` 字面量、不读 SPEC `stub_width_mm`；② via 不去重；③ blocked 口径）⇒ rev-12 dry-run 仍 +34。依既定自裁（**`_shared` 不解冻**、施工侧**改由项目内引擎承载**）新增**项目内**施加器：坐标**逐字取自 SPEC**（零搜索），仅修三处（短段宽 = SPEC `0.2`、via 去重 `(net,x,y)`、blocked 口径对齐）。**验证（scratch 三态 DRC，确定性）**：baseline **42** / 冻结引擎 **76（+34）** / 项目内引擎 **42（+0）** ⇒ **rev-12 PDN 施工 DRC-clean**；统计 = zones 5 / vias 241 / tracks 185 / stub_w 0.2 / deduped 0 / 跳 blocked 61。不改冻结副本/SPEC/板/阈值；`gnd_stitch_gen` 生成端缺陷不在在役路径（施工只用 SPEC 坐标）。工具 `p3_v57_co102_pdn_apply_local.py` `945b7ae7942102be`；记录 `m13_v57_co102_pdn_local_apply.json` `44002f7eac6cfa49`；卡 `m13_v57_CO102_pdn_local_apply.md` `1df2be1ef5fc0e64`。

> ㊱ **CO-103（L2 · 非执行者对抗复评）rev-12 新基线（对象 CO-99/100/101/102 + 链 pin + 收口声明）= `PASS_WITH_FINDINGS`**：9 项机判（V1 幂等重导逐字节 / V2 palette 归属+固定序独立重放 / V3 登记完整性 / V4 clearance 与 CO-91 一致 / V5 计划集互判 / V6 CO-102 发射集等价 + 三态 DRC 42 / 76(+34) / 42(+0) / V7 blocked 成因分类 / V8 声明漂移扫描 / V9 链 pin）**全过**，牙齿 7/7；**0 项 pin 漂移**。**发现**：**F-A（中）**声明漂移 —— 原记「6 项新增 blocked（5 ppc + 1 stitch，全在 U6 0.5mm 场）」实为 **5 项（4 ppc + 1 stitch）**，第 5 项在 **J2 扇出** `(133.83,59.1)`；v1.69 已校正。**F-B（高）**4 项 U6 新增 blocked 的自身位置**对板铜干净**、阻塞全为**同网 GND 计划孔距互障**（相邻 U6 GND 计划 via，d=0.180–0.403 < 0.45）⇒「须 via-in-pad/HDI」**缺乏存在性证据**（换序探针 8/13/13 且每对幸存成员翻转）；与 CO-94 板铜类不同。**F-C（中）**收口件 §1 ㉛/§6-20 的 co95 现行身份引用陈旧（`61db48a283beeaae` → 现行 `f1c0c17ee7b379a4`）、CO-96 证书未声明自身失效，且 CO-77 的 `CITE` 抓不到散文式引用；v1.69 已注明已取代。**另记**：同网孔距口径经**合成注入实测**验证（kicad-cli 对同网 GND 孔对报 `hole_to_hole`，0.080 < 0.2495）⇒ CO-99 A4 口径忠实。工具 `p3_v57_co103_rev12_nonexecutor_review.py` `5e3f91d39130b83a` / 记录 `m13_v57_co103_rev12_nonexecutor_review.json` `7f481be259865941` / 卡 `m13_v57_CO103_rev12_nonexecutor_review.md` `6ac046a885508dc6`。

> ㊲ **CO-104（L2 自裁 · 过孔策略/PDN）rev-12 新增 5 项 blocked 的裁定 = `ACCEPT_L2_NO_HDI`**：依 `LAYOUT_CONSTITUTION` 第二章（过孔策略 / PDN 承载 = L2；层数 = L1）对 CO-103 F-B 的 4 项 U6 ppc + 1 项 J2 扇出 stitch 作裁。**三条出路逐条量化**：**A 共享单孔**（两 pad 中心**中点**派生位 + 双短段；零自由度、非搜索）仅 **1/4 对**可行（`FB34~FA32` 可行；其余 3 对的中点正落在 U6 另一球 pad `FF11`/`FF18`/`E11` 上）⇒ 收益 = 1 个 GND 球；**B 改声明固定序**（同 palette、同检测器）canonical **4** vs 13 / 8 / 13 ⇒ canonical 已最优、无免费解；**C 加宽 palette / via-in-pad / HDI** ⇒ 违零坐标搜索红线（CO-93/94 已驳）/ 无工艺 + SI-PI 证据 / 属 L1 且本件已证「须 HDI」不成立。**裁定 = 接受**（与既有 120 项 blocked 同类处理，显式登记不静默），**不升 owner、不重基线、rev-12 不变**；本项**不再构成 L1 问题**（若日后要求「U6 GND 球 100% 独立 via」为硬需求，须走 SPEC 变更 + 全链重基线 + 换会话复评）。**附带加固（CO-103 F-C 收口，fail-closed）**：co96 默认落点改为**重跑件**，显式指向历史证书即**拒绝写入（rc=2）**，除非 `--overwrite-canonical`⇒ 历史证书 `8b591e5030aca11d` 不再会被静默改写；重跑件 `m13_v57_co96_nonexecutor_review_pass4_rerun.json` `636b1ad728f0fa91` 即 CO-96 失效的**机判化声明**（verdict `BASELINE_MISMATCH`，`co95_json` 61db48a283beeaae → f1c0c17ee7b379a4）。工具 `p3_v57_co104_pdn_blocked_ruling.py` `7b2f3ff18e0ede04` / 记录 `m13_v57_co104_pdn_blocked_ruling.json` `7254226692cb8f93` / 卡 `m13_v57_CO104_pdn_blocked_ruling.md` `ed2587023fe05ed6`。
> ㊳ **CO-105（L2 自裁 · PDN 建模）CO-96 F4 落定 = `CLOSE_NO_SCOPE_EXTENSION`**：把 CO-98 的「声明排除」机判化。**V1 语义不可适用**：requirement 判据 =「落于本网 In4 铜」，而 GND 平面层 = `In1/In3/In6`、In4 仅 `P3V3/MCU_VDD/P3V3_AUX` ⇒ 对 **130 GND ppc entry + 40 GND stitch via** 无可判定（≠『未覆盖』）；requirement 对象 = 非 GND ppc entry **55**。**V2 几何待 L3**：17 个 `power_zones[].vias` **17/17** 位于 3 个 bridge zone（`P3V3_BCU_BRIDGE_IN4` 3 / `P3V3_AUX_BCU_BRIDGE_IN4` 8 / `MCU_VDD_BCU_RESISTORS_IN4` 6），其 `polygons=[]`、`geometry_status=L3_CONSTRUCTION_DERIVED` ⇒ 与 CO-98 `declared_pending_l3` 同桶；扩 scope 只并入待派生清单、不新增可判缺陷。**V3** 施工路径对 `gnd_stitch_gen` 的**代码引用 = 0**（散文复盘 1）⇒ 生成端缺陷 latent、不在在役路径。**V4** `R1.2` 判据根因 = 电源域/区域归属 = **L1**（不在本件）。**裁定 = 关闭 F4，不做 scope 扩展**；零 SPEC/板/阈值/冻结源改动、不需重基线、不需新复评。牙齿 2/2（GND 平层不含 In4 而 In4 确被占 / 17 项空几何而存在有几何 zone）。工具 `p3_v57_co105_f4_scope_disposition.py` `f357f81142161e61` / 记录 `m13_v57_co105_f4_scope_disposition.json` `758167e449ba6a07` / 卡 `m13_v57_CO105_f4_scope_disposition.md` `c40b94566b0ba3e9`。
> ㊴ **CO-106（L2 · 合格标准覆盖性补全）参考平面判据 + 参考平面连续性机判 = `INDETERMINATE_REGION_SCOPED`**：ch.2 的 L2 裁判标准含「参考平面」，而 CO-87 记录**自报**的判据集含该词、覆盖矩阵却只有五行（参考平面无决策行/无闸）⇒ 本件补上判据并机判：**A 板框一致性**（声明多边形 = 冻结板框按 `edge_copper_min` 内缩）＋ **B 参考平面连续性**（每条规划走线每点须落在其 `impedance.per_layer[layer].refs` 任一参考层声明铜内；分类 `declared_copper_missing`（GND 整面层缺铜=缺陷）vs `region_scoped_indeterminate`（In4 按电源区裁剪/桥区待派生））＋ **C 板实佐证** ＋ **D 覆盖性补全声明**；牙齿 3/3（合成负控/正控）。**rev-12 判 `FAIL_DECLARED_COPPER_MISSING`**：60 点/36 段（In2 24 + In5 12）；根因 = 3×GND + 2×In4 多边形下边 **70.7 = 33+38−0.3**（旧 38mm 板框）而现行板框 `outline_y [33,79]`（v28 ECO y 38→46mm）⇒ 按自身 basis 应为 **78.7**；后果 = 框内平面外 **8.3mm 带无参考平面**，而施工已用该带（板实 **In5 316 段 + In2 12 段 + 24 via**，PCIe `PCIE_DN2..DN7` 蛇形恰在其中）。修复 = CO-107。工具 `p3_v57_co106_reference_plane_gate.py` `d56a1e51ece54d51` / 记录 `m13_v57_co106_reference_plane_gate.json` `3ad6e35c4bedd72e` / 卡 `m13_v57_CO106_reference_plane_gate.md` `08b46fff2a07e45a`。
> ㊵ **CO-107（L2 自裁 · PDN/平面分配）SPEC rev-13 = 平面随板框对齐（CO-106 FAIL 的施加）**：把 3×GND(In1/In3/In6) + 2×In4(`P3V3_EAST`/`MCU_VDD_WEST`) 多边形下边 **70.7 → 78.7**（与各自 basis「整面铺铜 + 板边内缩 0.3」一致），rev-12 原多边形**退役留存** `pd.zone_defs.retired_superseded_frame_extent_v1`；**只改 polygon 顶点 + `spec_version`**（阈值/网/层角色/坐标集/短段宽/blocked 台账/冻结源未动）。**几何不变性机判**：新图纸 `route_geometry`/`pages`/`landing_rows` 与 rev-12 **逐字节同**（仅 `inputs_sha.spec` 与 `frozen_sha_check` 变）⇒ 板 **`0e636a67c1472462` 逐字节不变**。SPEC rev-13 `7943be727a4f8ef9`；G4 **FEASIBLE_ALL**（34 页/crossings 0/work 546/546）主件 `73c0066df83fa8c2`；G5 PASS frozen=True；G6 PASS viol 0；G7 FAB ok + DFM new=0 + 在册未连 0/68 + SI skew 0.1300；**CO-106 复判 → `INDETERMINATE_REGION_SCOPED`（`declared_copper_missing`=0）**；链 pin 同批前移（引擎 `/FROZEN_SHA`、validator `/prefix`+`FROZEN`、闸默认 spec co78/81/84/91/92/95/98/99/102/104/105/106、co77 正则）。**复评债 = CO-108（须另一会话）**。工具 `p3_v57_co107_spec_rev13_frame_align.py` / 记录 `m13_v57_co107_spec_rev13_frame_align.json` / 卡 `m13_v57_CO107_spec_rev13_frame_align.md`。
> ㊶ **CO-108（L2 · 非执行者对抗复评）rev-13 新基线 = `PASS_WITH_FINDINGS`**：独立（不复用执行者断言）机判六面全 True —— **A** rev-13 vs rev-12 标量差分恰为 10 polygon 顶点 + `spec_version`（无增删键）；**A2** 退役留存 5 项（`old_polygon`=rev-12 逐值 / `new_polygon`=rev-13 逐值 / 无 70.7 未登记 / 无残留）；**B** `route_geometry`/`pages`/`landing_rows` 与 rev-12 **逐字节同** + 板 `0e636a67c1472462` 逐字节不变 + frozen drift=∅；**C** 无工具仍以 rev-12 为现行（仅 CO-103 历史件合法持有 `1a381b06454dbe2c`）、记录内 `inputs.*_record` provenance pin 全数一致；**D** 参考平面独立**点级全量**重算 GND 整面层缺铜 **0**、残余 54 段/1260 点 **100%** 落 L3 桥带 x∈(49.8,88.37)；**E** rev-12 FAIL 独立复现（60 项/36 段；板实 (70.7,79.0] = In5 316 / In2 12 / VIA 24）⇒ CO-107 为真修复；**F** 牙齿 3/3。**发现**：**F-A（low，已校正）** CO-105 记录 provenance pin `inputs.co98_record` 在执行者提交态 `04d0ee1` 为 `267f86b5…`（非当时 co98 `48b5bd29…`、亦非任何已提交版本）⇒ 确定性重跑既有工具（无新代码路径）恢复一致，boundary v1.73 同批更新引用；**F-B（信息性）** CO-106 记录字段实计 (段,参考层) 项数而非采样点数（判据成立性不受影响）；**F-C（low，已声明）** co87 矩阵仍无「参考平面」行（登记册缺口）。**F-D（medium，未决前提）** 3 个 bridge zone `layer=In4.Cu` 但名含 `BCU`、`basis` 明文经 **B.Cu** 桥接（P3V3 明示『In4 走线带不跨』）⇒ CO-106 归 `region_scoped_indeterminate` 的『几何待 L3 派生』前提**未证实且与 basis 冲突**；须在 L3 桥区派生 work order 前先裁 bridge zone 派生层归属（若取 basis 口径则 54 段 In5←In4 为**永久**参考缺失 ⇒ 升级 L2 参考平面/阻抗裁定）。工具 `p3_v57_co108_rev13_nonexecutor_review.py` `a745c2695e92b0e6` / 记录 `m13_v57_co108_rev13_nonexecutor_review.json` `f1ff40a43614a9e8` / 卡 `m13_v57_CO108_rev13_nonexecutor_review.md` `a00d7d89a5106c7d`。
> ㊷ **CO-109（L2 自裁 · 参考平面/PDN）In5←In4 走廊空洞 = 按设计（非「待 L3 派生」）；bridge zone = B.Cu**：触发 = CO-108 F-D。客观证据：3 个 bridge zone（`layer=In4.Cu` 但名含 `BCU`、basis 明文经 B.Cu）声明的 3 条 band 仅覆盖 In5←In4 miss 点 **6.0%**（75/1260），而 In4 走廊 x∈(49.8,88.37) 覆盖 **100.0%**；板 L4 zone 数 0（平面未落）⇒ 无声明走廊 In4 几何可派生。**裁定**：**R1** 3 bridge zone 桥接层 = **B.Cu**（`layer` 字段仅 In4-可达性簿记）；**R2** 走廊空洞 = 按设计（basis 记 PM T2-ECN-1/2『In4 走线带不跨』）；**R3** 桥区几何派生**不能**清除 In5←In4 残余；**R4** ⇒ CO-106 `region_scoped_indeterminate` 前提不成立 —— 该带 In5 实为**仅 In6 参考**、与 declared `symmetric_stripline(refs=[In4,In6])` 不符，应改判『按设计 In4 空洞』并登记 SI 待验项（终判 = SI9000 + 板厂券，不得代填）；**R5（OWNER，停）** 走廊补 In4 铜 = 反转已记录 PM 裁决 ⇒ owner。**step ② 重定范围**：②a 声明修正（L2，新 rev 重基线）/②b 走廊 In5 SI 终判（外部）/②c bridge zone B.Cu 几何声明（L2，**缺 palette**）/②d 换会话复评。工具 `p3_v57_co109_in4_void_l2_ruling.py` `2e35c139476ae016` / 记录 `m13_v57_co109_in4_void_l2_ruling.json` `dd562f526705abef` / 卡 `m13_v57_CO109_in4_void_l2_ruling.md` `583ac243a4cf3428`。
> ㊸ **CO-110（L2 自裁 · 施加）参考平面判据入 CO-87 矩阵 + CO-106 D 读径修复 + In4 走廊空洞按设计定案（R5'）**：触发 = CO-108 F-C/F-D + 本件新发现 **F-E**。**(a) F-C**：CO-87 覆盖矩阵原 5 行、缺 ch.2 判据「**参考平面**」⇒ 补第 4 行（`INDETERMINATE`，证据机取自 CO-106 记录：`declared_copper_missing=0`、残余 `In5←In4` 54 段 = 按设计走廊空洞），新增牙齿 `ch2_criteria_all_have_rows=true`（n_closed=3/n_open=3）。**(b) F-E（新发现）**：CO-106 D 项原读 `co87["inputs"]["matrix"]`，而 CO-87 记录无 `inputs` 键 ⇒ `KeyError` 被吞 ⇒ 覆盖性检查**恒空真**、行缺失从未被校验；已改读 `constitution.ch2_l2_criteria` + 顶层 `matrix`，复跑后 `co87_has_reference_plane_row=true`。**(c) F-D/R5'**：**不开 In4 走廊铜 = 确认 PM T2-ECN-1/2 既有设计（非反转）** ⇒ CO-109 的 OWNER 升级**撤回**；In5 在该带 = **In6-单参考域**，SI 终判 = 外部。**零 SPEC/板/阈值/冻结源改动 ⇒ 不重基线**（先例 CO-105）。工具 `p3_v57_co110_l2_coverage_closure.py` `354aef88cdac7634` / 记录 `m13_v57_co110_l2_coverage_closure.json` `6564e51f6ade544e` / 卡 `m13_v57_CO110_l2_coverage_closure.md` `82d2b176d45d1527`。
> ㊹ **CO-111（L2 自裁 · 参考平面/阻抗）In5 PCIe 走廊参考缺失量化为 40.1%**：触发 = CO-110 关闭 F-D 后仍缺「量」。In4 走廊 x∈(49.8,88.37) 无声明 In4 铜 ⇒ In5 走线在该带的**长度** = **1094.8/2727.3mm = 40.1%**，受影响 **16 网全部为 PCIe 差分对**（`PCIe85`，target_zdiff 85Ω），最差 `PCIE_UP4` **108.7mm/50.5%**。**关键**：L5 SI 记录**只签 intra-pair skew**（`skew_ok=true` max 0.13mm）、**声明**阻抗模型但**无逐线阻抗核验** ⇒ 走廊内 In5 PCIe 阻抗暴露**未被现行 G7 签核覆盖**。**裁定**：Q1 量化如上；Q2 受影响网全为阻抗受控 ⇒ declared `symmetric_stripline(refs=[In4,In6])` 在走廊**不成立**；Q3 该暴露**未验**须显式登记；Q4 终判 = **SI9000 + 板厂阻抗券**（不得代填）；Q5 若超规补救层级 = (a) 走廊补 In4 铜（**OWNER**/PM）/(b) 改线换层（信号流向 ⇒ 或 **L1**）/(c) 走廊段宽-隙补偿（**L2**，须场解）。工具 `p3_v57_co111_in5_pcie_corridor_exposure.py` `c586f2a49742e137` / 记录 `m13_v57_co111_in5_pcie_corridor_exposure.json` `9ae53dbf3cfc48e1` / 卡 `m13_v57_CO111_in5_pcie_corridor_exposure.md` `09fb8d2656b5b27d`。
> ㊺ **CO-112（L2 自裁 · 声明式施加）3 bridge zone = B.Cu 桥（step ②c）+ In5 区域条件参考口径**：按 CO-105 先例（零 SPEC/板改动、不重基线）。**D1** 3 zone（`P3V3_BCU_BRIDGE_IN4` / `P3V3_AUX_BCU_BRIDGE_IN4` / `MCU_VDD_BCU_RESISTORS_IN4`）桥接层 = **B.Cu**，几何带只取自声明源：前两者 band 由 basis 文本正则抽取（1 带 / 2 带），MCU_VDD 取已声明 via palette 的轴对齐 bbox（固定规则，**provisional**）。**D2** 其 targets 经 B.Cu 桥接 ⇒ In4-平面可达性 requirement 对其**语义不适用（N/A）**（镜像 CO-105 V1），`polygons=[]` 不构成缺陷。**D3** In5 **区域条件参考口径**：In4 有铜处 `refs=[In4,In6]`、走廊 x∈(49.8,88.37) 处 **`refs=[In6]` 单参考**（1629.5/1094.8mm）。**D4** 走廊逐网 worklist（16 网，合计 1094.8mm）⇒ SI9000 + 板厂券终判。**非声明**：In5 PCIe 阻抗暴露（CO-111，40.1%）**不因本件减轻**。工具 `p3_v57_co112_bcu_bridge_declaration.py` `4bda33760ad2d196` / 记录 `m13_v57_co112_bcu_bridge_declaration.json` `5f621c3c1003be00` / 卡 `m13_v57_CO112_bcu_bridge_declaration.md` `e36fc9ad1a244425`。
> ㊻ **CO-113（L2 自裁 · 施加）SPEC rev-14 = CO-105/109/110/111/112 裁定写入 canonical SPEC**：**仅新增声明键**（既有标量仅 `spec_version` 变）——① `pd.zone_defs.in4_corridor_void_by_design_v1`（走廊 x∈(49.8,88.37) 按设计无铜 + CO-111 量化）；② 3 个 `L3_CONSTRUCTION_DERIVED` power_zone 增 `bridge_layer="B.Cu"` + `bcu_bridge_bands`（band 只取自声明源：basis 文本 / 已声明 via bbox）；③ `plane_reachability_status.na_scope_v1`（GND entry = CO-105 / bridge targets = CO-112 语义 **N/A**）。新键**无消费者** ⇒ 引擎/L4/L5/各闸读数不变。**几何不变性**：新图纸 `route_geometry`/`pages`/`landing_rows` 与 rev-13 **逐字节同**（`c27d9f5b…`/`2535f330…`/`74234e98…`），板 `0e636a67c1472462` **逐字节不变**；G4 **FEASIBLE_ALL**（主件 `0e74718b1e31dca5`）/ G5 PASS frozen / L4 viol 0 / L5 DFM new=0 + SI 0.1300 / co99 0-0-0-0 / co102 42-76-42 / co106 INDETERMINATE。链 pin 同批前移（引擎/validator/闸默认 spec co78/81/84/91/92/95/98/99/102/104/105/106 + co77 正则）；历史件 co107..co112 仍 pin rev-13。工具 `p3_v57_co113_spec_rev14_declare.py` `4c885825a6cecf60` / 记录 `m13_v57_co113_spec_rev14_declare.json` `261fa00af228be4a` / 卡 `m13_v57_CO113_spec_rev14_declare.md` `29554ef222ec2e79`。
> ㊼ **CO-115（L2 自裁 · 事实更正）In4 走廊空洞 = 失效 keepout 残留（待 L3 派生）**：**更正 CO-109 R2 / CO-110 / CO-113**。机判：`retired_in4_keepout_band_6l.band = x[50.0,88.17]`（CO-95 退役；premise=「铜皮东西两区**禁止跨越此带**，两侧各留 0.2」）；走廊边界 `MCU_VDD_WEST` 东缘 **49.8 = 50.0−0.2**、`P3V3_EAST` 西缘 **88.37 = 88.17+0.2** ⇒ 空洞 = 该退役约束的**两侧 0.2mm 内缩残留**；CO-95 `effect` 明文「退役后 **In4 铜可在原 band 区内按网归属铺设**」⇒ 空洞**属待 L3 派生**（handoff §4-2 原判正确）。**更正后推论**：CO-111 的 In5 PCIe **40.1% 参考缺失可修**（按网归属铺 In4 铜）；rev-14 的 `in4_corridor_void_by_design_v1` 键须 **rev-15** 更正；CO-98 `declared_pending_l3` 语义回到「待派生」。**唯一硬停点（OWNER/L1）**：band x∈(50.0,88.17) 内 In4 铺铜的**区域归属界面**（MCU_VDD/P3V3_AUX/P3V3）——界面未定则无法 L2 唯一确定铺铜几何（不得代填）；即既有 L1 项「P3V3_AUX 西区归属」同族。工具 `p3_v57_co115_corridor_stale_keepout_correction.py` `f5d0007766677616` / 记录 `m13_v57_co115_corridor_stale_keepout_correction.json` `b200828cb797817e` / 卡 `m13_v57_CO115_corridor_stale_keepout_correction.md` `700f4c6d6c226059`。
> ㊽ **CO-114（L2 · **非执行者**对抗复评）SPEC rev-14 新基线 = `PASS_WITH_FINDINGS`（6 发现）**：独立六面机判（A 差分 / B 不变性 / C pin / D CO-115 更正 / E CO-111 复算 / F 新键无消费者）**全 True** + **9 牙齿全触发**。**证实**：rev-14 仅新增声明键（既有标量只 `spec_version` 变）、几何与板**逐字节不变**（rev-13 git blob `73c0066df83fa8c2` → 主件 `0e74718b1e31dca5`）、SPEC pin 全数前移、新键零消费者；CO-115 更正算术成立；CO-111 **40.14%** 独立复算逐位一致。**发现**：F-1（high）rev-14 键 `in4_corridor_void_by_design_v1` 已定性错误（CO-115）⇒ 待 **rev-15**；F-2（medium）co87「参考平面」行证据文本仍含「按设计」；**F-6（medium）4 记录 5 处 `inputs.*_record` provenance pin 因 rev-14 重基线而陈旧**（co98←co95 / co105←co98 / co109←co106 / co110←co106 / co110←co87；CO-108 check C 不变量被打破、CO-77 盲区）；F-3（low）CO-113 `new_keys` 少声明 `bcu_bridge_bands_source`；F-4（low）CO-111「无逐线阻抗核验字段」措辞不精确（SI 实含 `per_layer_impedance`，真缺口=区域无关性）；F-5（info，已由本件 v1.81 更正）。工具 `p3_v57_co114_rev14_nonexecutor_review.py` `6642f8156e349c24` / 记录 `m13_v57_co114_rev14_nonexecutor_review.json` `20adc9fb67e62c63` / 卡 `m13_v57_CO114_rev14_nonexecutor_review.md` `ab0da32774a0714d`。
## 2. 冻结栈与关键输入（现行）
| 项 | 件 | sha16 |
|---|---|---|
| 叠层（L2） | `m13_v57_layer_intent_rev6.json`（**LID REV6 / CO-68**：signal = F/In2/**In5**/B；In1/In3/**In6**=GND，In4=P3V3） | **`05009687a3f01583`** |
| 走廊/见证（L2） | `m13_v57_big_w0r_corridor_model.json`（W0-R，未改） | `80ee9adb78a7e9ad` |
| 通道分配（L2/L3） | `m13_v57_co16_channel_allocation_v9.json`（CO-145：lane 步距 1.07；CO-144 carry + PDN 障碍场） | **`d3cd1e5a312f253a`** |
| 逃逸域（L2/L3） | `m13_v57_co37_escape_domain.json`（CO-37）＝ `.kicad_dru` 引用 `5616a9f873c9b844` | `5616a9f873c9b844` |
| SPEC（红线原件） | `SPEC_k2_v4.json`（未动） | `0bd52ed48e720b8c` |
| SPEC（引擎消费 ECO，**现行**） | `SPEC_k2_v4.spec-rev-19.json`（**CO-132 施加：R1 In4 承载几何（P3V3 桥区多 target + P3V3_AUX J4.A9 + 12V_IN），`fill_priority=1`；MCU_VDD 电阻区 = covered_by_host（CO-131）；stackup In4 文本含 12V_IN；可达性 unresolved 清空**） | **`5f72182a2616392c`** |
| SPEC（引擎消费 ECO，历史） | `SPEC_k2_v4.spec-rev-17.json`（**CO-130 施加：D-6 网类 `12V_IN`→POWER + 退役三 zone 的 B.Cu 载体声明（`bridge_layer` B.Cu→In4.Cu）+ `stackup[In4.Cu]` 文本对齐实际网集；仅声明键；板逐字节不变**） | `9fea9fd20149c736`（已取代） |
| SPEC（引擎消费 ECO，历史） | `SPEC_k2_v4.spec-rev-16.json`（**CO-122b 施加：CO-121【L2 自裁】西区 P3V3_AUX In4 承载 = 追加 `P3V3_AUX_WEST` 单环 zone + 可达性归口更正；前序 CO-117 更正错误键 + 按网归属铺入 band；前序 CO-113**：CO-105/109/110/111/112 裁定写入 canonical SPEC —— In4 走廊空洞**声明**（**CO-115 更正：非按设计**，属失效 keepout 残留、待 L3 派生）+ bridge zone = B.Cu（声明带）+ 可达性 N/A scope；**仅新增声明键**） | `5748828a23161250`（已取代） |
| SPEC（历史 ECO） | `SPEC_k2_v4.spec-rev-13.json`（CO-107 平面对齐；已被 rev-14 取代） | `7943be727a4f8ef9`（已取代） |
| SPEC（历史 ECO） | `SPEC_k2_v4.spec-rev-12.json`（CO-101 互障重导；已被 rev-13 取代） | `1a381b06454dbe2c`（已取代） |
| SPEC（历史 ECO） | `SPEC_k2_v4.spec-rev-3.json`（ECS-001，CO-40；保留未动） | `2d6dbd8bd8d667d7` |
| 规则 | `_shared/eda_core/drc_rules.json` | `0a459839e15960b8` |
| manifest | `m13_v57_s1_page_manifest.json` | `a8ef3ea8ecff99d7` |
| 冻结板（8L 基线） | `k2_v4_8L.kicad_pcb` | `fb07d25ac426ff84` |

## 3. 整链门禁（G4..G7，全部实测）
| 门 | 判定 | 证据（sha16） |
|---|---|---|
| G4/W3 | **PASS（FEASIBLE_ALL）** | 主件 **`60cbd331836e52b7`**（rev **W3-CN.41**；CO-101 重基线：`route_geometry/pages/decision_contract/layers/method/gate_status/verdict` 与 CO-85 基线 `22c2a15835857f99` **逐字节同**，唯一 delta = `inputs_sha.spec`（rev-8→rev-9）与 `frozen_sha_check` 指纹）；landing `da21d0186a9c643c` |
| G5/W4 | **PASS** | `m13_v57_w3_validation.json` `8b385d6c554ac527`（validator v2；G-M1..6 True、A1.2/A1.3/A1.4 True、frozen=True；冻结集含 `spec=77f5c54df88bb0ca`） |
| G6/L4 | **PASS** | 板 **`d4e81f647be7f980`**（68 网/**2523** 图纸段 + PDN 施工 185 短段 = **2708** track / **493** via（252 图纸 + 241 PDN）/ **13** zone（4 逃逸域 + 9 PDN）；track 宽度按层 F/B 0.205、In2/In5 0.16）；construction `305a42a890593552`；`m13_v57_l4_validation.json` `aa666a49e36883c7`（L4-A..**F** True、viol 0） |
| G7/L5 | **PASS** | **（历史快照 · rev L5-SI.6 / L5-DFM.6：本行记 G7 首过时点，非现行 —— 承 CO-235 F-1 口径同步）** fab `6d85160413770fa5`（2523 tracks/252 vias）；si `73f9b59ed5f6f3ce`（rev **L5-SI.6**：**按层加权电气 skew 0.1300 ≤ 0.15**、physical 报告 1.1046、pdn_status=reserved_not_poured）；dfm `40445f87be664f31`（L5-DFM.6：多重集 new=0 / disappeared=0 / 在册 0 未连）；**现行 L5（L5-SI.11 / L5-DFM.8 / L5-FAB.2 / L5-G7.11）之 sha 由 §104 pin 面承载** `m13_v57_l5_si_pi_emc_record.json` `97c867e89fc6df6c` |

**CO-107（rev-13）注**：G4 主件/`inputs_sha` 指纹重基线；`route_geometry`/`pages`/`landing_rows`/`decision_contract`/`layers`/`method`/`gate_status`/`verdict` 与 rev-12 基线 **逐字节同**；板 **`0e636a67c1472462` 逐字节不变**；G5/G6/G7 与 PDN/回归闸重跑读数不变（唯一例外 = CO-106 由 FAIL 转 INDETERMINATE、co77 对象随本 boundary 更新）。

DFM 收敛轨迹（v1.15 之后）：**D1/D2 归零（CO-23；W3-CN.37）→ 73（CO-23）→ 60（CO-37 D3c）→ 54（CO-41）→ 38（CO-43）→ 0（CO-45）**。
L4 板 `kicad-cli` 实跑：仅冻结基线 42 条 lib/silk，**铜层违规 0**（clearance/shorting/solder_mask_bridge/tracks_crossing 全 0）；基线铜违规数 = 0 ⇒ `new_total=0` 等价于「零铜层新增」。

## 4. v1.15 → v1.16 取代沿革（rev 与变更单）
- **W3-CN.27 → .36**（ROOT-16 线）：CO-05..CO-11（O4 落列可行性、安全 hop 拓扑、pair 域 v1.4/1.5、lane 平面）；
  CO-16/CO-18/CO-19/CO-22（东侧重派生、O4 有界幅值闭式蛇形、板内 J3 fan、lane 平面重整）⇒ 全板 **32/32 有效**（W3-CN.34/.35/.36）。
- **W3-CN.37**（CO-23）：板边真带（Edge.Cuts y=33/79、x=143）⇒ D1 copper_edge / D2 hole_to_hole 归零。
- **D3b 收官**（CO-25..CO-36，L2 自裁）：connector 落列器改「land 段长升序」（CO10_LXPRIO=landlen）⇒ CO16-ALLOC.5。
- **D3c**（CO-37）：SPEC 逃逸区规则域 `.kicad_dru`（0.075 + 4 具名 rule area，**显式排除 `PCIE_REFCLK*`**）。
- **L1 更正**（CO-38→CO-39）：D3a 非引脚缺陷，J2 侧 REFCLK 引脚由原理图网表 + SFF-8654 pinout 真源锁定 ⇒ 闸口 CLOSED。
- **W3-CN.39**（CO-40/CO-41）：SPEC-REV-3 ECS-001（J2 外列 N 单次换层 F.Cu→In2→F.Cu，每线 2 via）⇒ DFM 60→54。
- **W3-CN.40**（CO-42..CO-45）：远端带内接入（禁沿 A 排平行）＋ 对内偏移 `{P:0.0,N:-0.5}` ＋ dip 解耦 ＋
  图纸/nodes 一致化 ＋ P 轨等长幂绕 ＋ `A-CN.5d` ⇒ **DFM 38→0、G7 PASS**。

## 5. 覆盖性声明（宪法第五章第 1 条）
管辖对象 = 34 页（32 MCIO lane 页 + 2 REFCLK 页）/ 68 网 / 2 远端连接器（J3/J4）接入；**无「待定/暂不管」对象**。
每对象均有机器可读决策：`pages[*].nodes`（3D）+ `pages[*].vias` + `route_geometry` + `decision_contract`
（corridor_x / 分层链 / max_vias_per_line / pair_rule / REFCLK 层契约）。
**本声明范围 = 高速走廊结构**；《宪法》ch.5 §4「数学闭合」四项之 **PDN 压降** 与 ch.2 L2 裁判标准之 **热**在本项目**无输入/无证据 ⇒ NOT_DEMONSTRATED（缺输入，见 §6-8 与 CO-87）**，不得由本声明读作已闭合。

## 6. 已知限制与豁免（如实声明，不得当作 PASS 依据掩藏）
1. **板字节已可复现（CO-49 解除）**：原 `pcbnew` 保存使 `segment/via/zone` 块的**顺序与 uuid** 每次重建漂移（其余块逐字节稳定）；
   CO-49 在 L4 applier 内做确定性规范化（连续同类 run 内排序 + 由内容派生 uuid5，只碰这三类块）⇒ **构建→L4→L5 全链 7 件逐字节可复现**；
   现行 L4 板 **`d4e81f647be7f980`**（方案(a)/LID REV6 重基线，CO-68/69 起；**CO-133 施工后** = 图纸几何 + PDN 声明铜；施工前 `0e636a67c1472462`）；
   历史（规范化前/方案(a) 前）板 `cdcb869e9827ec87`、`4d36212f6492262b` 等见 git 与 CO-45..CO-48 各 commit；
   **几何内容身份** = 现行 drawing `3d452429bbc934c3`（CO-89 重基线；CO-85 基线 `22c2a15835857f99` 已取代；W3-CN.41；`route_geometry` 与 W3-CN.40 `dfa1d7c4a811b0da` / rev-4 重基线 `4e7497daf97cebd1` 逐字节同，见 CO-56 §2）。
2. **CO-16 层跨不相交豁免**：独立验证器 G-M4 记录 `span_blind_min_mm = 0.163083 < 0.175`、`span_blind_violations = 3`，
   依 CO-18 §1b/§4-2「同层跨不相交 ⇒ 物理净距不适用」豁免；`kicad-cli` 实跑同层净距 0 违规（与该豁免一致）。
3. **DFM `new`：已升级为多重集差（CO-51 解除原限制）** —— 键 = `(type, items[].description)`，并显式报 `disappeared_total`（基线消失，L4=tracks-only ⇒ 须为 0）；
   实测 new=0 / disappeared=0（42 条 lib/silk 基线全部在册）。
4. **未路由网 348 项**（冻结基线 416）：v57 范围为 68 条高速网；其余网不属本阶段（不得据此判 FAIL，也不得声称整板已布完）。
5. **阻抗几何（CO-53→CO-56 已收口：一阶在设计带内，终判=板厂券）**：交付对内中心 0.500（边距 0.295）≠ SPEC `p_gap 0.175`；对间最小 0.550 中心（0.345 边距）vs SPEC `inter_pair_spacing_mm 0.875`；SPEC `stackup/impedance.model` 仍 6L 而板为 8L 且板内无介质叠层定义 ⇒ **阻抗符合性 NOT_DEMONSTRATED**（既非已证合规、也非已证违反）：**CO-55 已取消 (a)**（改为反向下达叠层要求，见上）；余 **(b) SI9000 校验（板厂券已声明）+ SPEC ECO rev-4**（stackup/impedance 分层口径/p_gap 语义）**（c）走廊口径已记录**。**已由 CO-55（下达 8L 叠层要求）+ CO-56（SPEC ECO rev-4 + 复跑）收口**：详见 `m13_v57_CO53_intrapair_geometry_impedance_open.md`、`m13_v57_CO54_spec_delivery_drift_inventory.md` `23d22ea76c0b95ff`、`m13_v57_CO55_layer_aware_impedance_build_ruling.md` `f9c45071c5d9141c`、`m13_v57_CO56_spec_eco_rev4_apply_record.md` `5b8b86ed789b5678`（含 **8L 叠层输入缺口可达性实测**与 Zdiff 重导 harness `tools/p3_v57_si_zdiff_rederive.py`）。
   **CO-47 已把该声明升级为谓词**：L5 记录 `dft.in_scope_unconnected_items == 0`（在册网按 kicad-cli 未连项网名解析）；实测 基线 68/68 在册网未连 → L4 **0/68**。
5. **G5 冻结集已校正（CO-46）**：原独立验证器的 `frozen_sha_check` 只钉 ECO spec + **历史 6L 板**，未覆盖红线 SPEC 原件与 8L 冻结板；
   CO-46 以「只增不减」补入 `spec_orig=0bd52ed4` / `pcb=fb07d25a`（并保留 `pcb_6l=f6273de6`）后 G5 仍 PASS。记录：`m13_v57_CO46_validator_frozen_set_fix.md` `bf7431bc6559ea98`。

6. **⚠ L1 待裁（CO-57 → CO-58 → CO-59 再基）**：R3-2『对间铜边净空 ≥0.875』的**时效/绑定范围**。
   - **口径出处（CO-59 机判）**：要求注入点 = `route_model_config.json` `capacity_audit.inter_pair_spacing=1.46`（note：语义 = 0.875 铜边净空 → 1.46 = 0.585+0.875 的中心距换算）；**1.08 属 `channel_alloc.pitch_fallback`（回退值）**，非要求量。**CO-58 以 1.08 为基线的「走廊与冻结口径一致」结论按 CO-59 更正**（原文保留不改）。
   - **交付实测（板级）**：EAST 对间距 **1.449**（铜边 0.744）/ WEST **1.050**（铜边 0.345）⇒ 在 **1.46 中心距**与 **0.875 铜边**两种读数下**均不达标**（EAST 在中心距口径下差 0.011）。板厂口径四方不自洽（1.20 / 1.46 / 1.08）。
   - **残余②已闭合**：B.Cu 与 In6 无并行耦合（0 对；最小并行横向距 20.3mm；B.Cu zone = 0）⇒ CO-55 的 B.Cu 约束满足。
   - **Q1（L1，单一问句）**：是否授权走廊对间距 → **1.580**（= 交付铜跨 0.705 + 0.875，**歧义无关**，同时满足 1.20/1.46/0.875）？授权 ⇒ L2/L3 重导 + （若需）J2/J3/J4 落列/焊盘场变更（L1）；备选：铜跨回退 0.705→0.585 使 1.46 给 0.875（L2 但需重定 8L 阻抗）——**CO-86 已机判闭合：该 L2 出口不成立**（任一可行铜跨下所需轨距 ≥1.282 均 > WEST 上限 1.050 且 > 焊盘场 0.600；焊盘场 0.600<0.875 与 span 无关 ⇒ L1 级硬限；且备选非免费：gap 0.295→0.175 使 Zdiff 88.4/82.0→81.9/74.1Ω，内层出带）。
   - **CO-70/71 补强证据（逐层实测，L4 construction，方案(a) 现状）**：对间同层最小中心 / 铜边净空 —— `In5.Cu` 0.550 / +0.345（最长并行 55.97mm）、`B.Cu` 0.550 / +0.345（14.22mm）、`In2.Cu` 0.580 / +0.375（20.35mm）、`F.Cu` **0.4921 / +0.2871**（板；witness `PCIE_UP_OUT6_N_J2` vs `PCIE_UP_OUT7_P_J2`；图纸 route_geometry 0.4627 / +0.2577）（**CO-85 F1 更正**：原记 1.124 / +0.919「达 0.875」经 7 种口径复算均不可得，已废）。⇒ **R3-2 0.875 在 4 个信号层中 4 层全部违反**（CO-85 更正：原『3 层』以不可复现的 F.Cu 行为据）；因其同时出现在 In2/In5/B（走廊轨距根因）与 F.Cu（连接器焊盘场根因，见 F2）（4 层全违反，非单一层分配所致），**层分离（channel 重分配）不能作为 L2 解**：根因 = 交付轨距（WEST 1.050 / EAST 1.449）× 对内半边距 0.25 ⇒ 邻线净距 0.345；达 0.875 需中心距 1.580，与冻结 L1 包络（球栅逃逸 / 板边 78.5975）互斥（CO-60/61 复现）。⇒ ① 维持 **L1**。
   - **CO-75 补强证据（本件新增，L2 未覆盖维搜索）**：WLO(12)×WSWAP/COLMODE(3)×FANY_J3(5)×HOLE_GAP(3)=23 组合、WSTEP=1.580 **全 0 命中**（保真 1.05@33.70=32/32）；失败恒在芯片输入 via 区，行扫 1.4e4~1.8e4 耗尽 ⇒ 硬限非旋钮。另注：本件**未**扫逃逸层分配（per-ball 冻结拓扑 ⇒ L2 ECN 级重导）与球栅/落列/板框（L1），故非「L2 全空间」数学完备证明。
   - 裁定前：不得声称对间净空合规、不得放宽 R3-2/冻结口径。G4..G7 现状与判定不因此件改变。**CO-85 追加（裁决相关）**：违反层数更正为 **4/4**；且 **J2/J3/J4 连接器焊盘节距 0.6mm ⇒ 焊盘场同层对间铜边净空上限 0.395mm < 0.875**（F2）⇒ **owner 选项 A（走廊重开至 1.580）单独不能使整板满足 0.875**：须限定 R3-2 口径到走廊/长平行区，或改连接器引脚场（L1）。**CO-86 追加**：L2 侧最后一条出口（对内铜跨回退）已量化排除（`n_pass_all_caps=0`，最小缺额 WEST +0.232 / 焊盘场 +0.682）⇒ L2 六域**无剩余可行变量**；R3-2 0.875 只能由 L1（引脚/球栅/板框）或红线口径修订解决。

7. **✅ `CO-72-PDN-1` 已闭合（CO-74，L2）**：原记 L1 系**归口过高**。前提（6L『In4 走线带阻断跨带铜皮』+ SPEC B.Cu=POWER_POUR）在 LID REV6 下机判失效（引擎层集无 In4；交付板 In4 段数 0）⇒ B.Cu 电力铜退役、改由 In4 承载，层数/平面数/电源域集合/信号层数**全不变** ⇒ L2。**B.Cu 电力铜自此禁止**（`pd.bcu_power_copper_policy=PROHIBITED`）。实体 In4 分区几何 = L3 施工（确定性派生 + DRC 核对），非本闸宣称已建。
8. **⚠ L2 合格标准覆盖缺口（CO-87，机判）**：《宪法》ch.5 §4 数学闭合明文含 **PDN 压降达标**，ch.2 把 **热** 列为 L2 裁判标准；L2 侧闸（CO-63..CO-86）覆盖 容量/长度/过孔/PDN **架构**，但 **PDN 压降** 与 **热** 全仓无输入（SPEC rev-8 全字段扫描 **0 命中**，扫描字段 3962）⇒ 两者状态 = **NOT_DEMONSTRATED（缺输入）**，既非 PASS 亦非 FAIL，**不得当作已闭合**。所需输入（机器提取自 `pd.zone_defs.power_zones[*].targets`）：① 各轨负载电流（U3/U7 redriver、MCU/存储、J3/J4 MCIO A9、去耦/上拉）；② 允许压降预算与采样点；③ In4 铜厚/温度修正 + L3 平面几何；④ 热：器件功耗/环境温度/风速/可接受温升与热阻路径。**属数据/需求输入（非 L1 拓扑裁决）**；禁止以假设值代填（不得伪造 sign-off）。记录 `m13_v57_co87_l2_acceptance_coverage.json` `46d15557477d164b` / 卡 `m13_v57_CO87_l2_acceptance_coverage.md` `322baa098740b259`。

9. **✅ L2 SPEC · PDN 板实性已闭合（CO-88 判定 FAIL → CO-89 施加 rev-9）**：原判据（CO-88）：`pd.zone_defs.power_pad_connect` 有 **55/173** 条引用板上不存在的 ref（35 孤儿，含 **U3/U7** — 红驱动已由 U3+U7 合并为 **U6**（DS320PR1601, 354 球））；板上 **309** 个 SMD 电源/地 pad 中仅 **118 覆盖 + 7 blocked**，**184（60%）静默待定**（违 ch.5 §1）；`pd.decoupling` 指向的 C67/C68/C72 **3/3 不存在** ⇒ 解耦规则零板实落点。**修复候选已派生**（`pad_connect_gen` 对交付板重生成：223 entries + 86 blocked = 309/309 覆盖；blocked 中 U6 占 63/86，为 0.5mm 球栅场内 GND 球无法 pad→via 直连的**显式** blocked），**波及清单 27 件**（含引擎 `FROZEN_SHA`、validator、`co69/77/81/83/84`、L4/L5）。**CO-89 已施加**：SPEC **rev-9**（`77f5c54df88bb0ca`）板实化 —— ppc 重生成 **223 entries + 86 blocked = 309/309 覆盖、0 孤儿**、解耦改板实集合、旧 BOM 转 `retired_*` 留存；**co88 复判 FAIL → PASS**；全链重基线后**板逐字节不变** `0e636a67c1472462`。**残余**：① 86 blocked 中 **U6 占 63**（0.5mm 球栅场内 GND 球无法 pad→via；改判需器件资料+SI/PI）；② **新基线非执行者复评已履行（CO-90 pass 3/3，`897ff5cc371d135d`）**：全链 12/12 逐字节复现（板 `0e636a67c1472462` 不变）、CO-88/89 事实独立复核通过（ppc↔板实 pad 双射 309=309、`pd` 外零变更、旧 BOM 退役 173/9 留存、解耦全板实、CO-89 幂等）、CO-88 闸注入突变 4/4 命中；**F1**（headline 未并入判据 C ⇒ 空解耦态 C=FAIL 而 headline=PASS 的 partial-pass）与 **F2**（teeth 恒真：只查 board_refs、`syn` 死代码）已修复 ⇒ co88 **CO-88.3**（F1/F2 + 续接发现的 **F4**：ripple 建议清单移出哈希体 ⇒ 记录恢复为 (SPEC, 板) 纯函数），记录 `f90d65369cab92dc` → **`bf69909aa64dc494`**（判定仍 PASS）；**F3** 见 §6-10，**F4/F5** 见 §6-11；③ PDN 压降/热仍缺输入（§6-8）。不触 L1。

10. **⚠ PDN 覆盖口径（CO-90 F3，登记不可静默放宽）**：CO-88/CO-89 的「板实 SMD 电源/地 pad **309/309 = 100%**」其分母 = `eda_core.pad_connect_gen.DEFAULT_PWR_NETS`（**内置常量**，非「板全电源网」）。交付板 `.kicad_pro` `netclass_assignments` 的 POWER 类另含 **`PWR_5V_KEY`**（板实落点 `C89.1`，SMD，0 走线；属 SPEC `layer_plan.low_speed_nets`、68 网范围外）⇒ 该 pad 不在分母亦无决策，**声明须限定为「内置网集口径」**。改分母（纳入该网）= SPEC rev-10 + 全链重基线，且「哪些网计入 PDN 覆盖」属**网范围/电源域口径 ⇒ 待 PM/owner**，不得由 L2 静默重定义。另 `pad_connect_gen` docstring 自称「PWR_NETS 从 SPEC constraints/net_classes 推导」而实现只读内置常量（**文实不符**，待共享层变更单）。

11. **✅ 闸可复现性（CO-90 F4）与引用闸牙齿（CO-90 F5）—— 已修复（续接 pane16 复评时发现并机判）**：
    - **F4（中｜可复现性）**：`p3_v57_co88…gate.py` 曾把 `ripple_checklist()`（扫描 `tools/*.py`）嵌入**记录哈希体** ⇒ 记录 sha 随**无关工具文件**增删而变。实测（两次对照）：移走 `p3_v57_co90…review_pass3.py` → `d320c81263733158`；放回 → `b9990766698af315`。
      后果：boundary 引用的 co88 记录 sha 在提交前即已不可复现（且是 CO-90 自身工具造成的）。**修复**：ripple 清单移出记录（记录 = (SPEC, 板) 纯函数）⇒ **CO-88.3**，稳定值 `bf69909aa64dc494`（三次含「移走/放回 CO-90 工具」对照均同值）。
    - **F5（中｜引用闸空真）**：`co77` 的历史豁免是**按整行**判定 ⇒ 「现行值 + 同行括号记录旧值已取代」这类行的**现行值**被一并豁免。实测：co88 记录漂移到 `b9990766…` 后，co77 仍报 `citation_mismatch=[]`（本应报警）。**修复**：豁免改为**按引用**判定（校验紧跟该 sha 之后的标记窗口），记录 revision **CO-77.3**；修复后该漂移被抓（负控）。
    - 边界：仅动闸/记录与声明件引用，**零几何、零阈值、零 SPEC**；F4 修复前后 co88 判定均 PASS（内容更严仍 PASS）。

12. **✅ PDN **计划坐标**净距缺口（CO-91 判 rev-9 FAIL → **CO-93 已施加 rev-10 闭合**；原判留档）**：`pdn_apply.py` 逐字实落 `pd.zone_defs` 的 via/短段坐标，但既有闸（CO-88 板实性 / CO-89 重基线 / CO-90 幂等）**均不判这些坐标的几何净距**。CO-91 以冻结规则源 `drc_rules.json`（netclass clearance + `min_hole_clearance`，语义核已对齐 kicad DRC 430/430 + 106/106）机判：**ppc via 35/223 + stitch via 41/69 + zone via 7/20 + F.Cu 短段(w=0.5) 75/223 违反**。
   - 根因（引擎侧）：① `clear_via_from_obstacles` **把 via 直接跳过**（从不作障碍）⇒ 计划 via 可与既有 via 铜重叠；② 净距用扁平 `0.1/0.05` 而非 netclass 派生 `required`；③ 无 `min_hole_clearance(0.25)` 概念；④ stitch/zone 孔位为更早阶段落盘、其后未随 v57 布线复核（漂移）；⑤ 短段默认 `w=0.5` 在 0.5–0.6mm 节距 ball field 内不可能合法。
   - **性质**：判的是**计划坐标**（交付板 `d4e81f647be7f980`，CO-133 施工后；施工前 `0e636a67c1472462`）；`kicad-cli` 铜层违规 **0**（42 条全为 lib_footprint_*/silk）⇒ **非**「已交付板不合格」。CO-133 已更正其 via-via 孔缘公式（见 §11）。
   - **修复候选（未施加）**：ppc 35 例 **35/35 可重定位、无新增 blocked**（⇒ 修引擎后 PDN 覆盖不退化）；stitch 41 / zone 7 需以当前板**重派生**并留存退役集；短段宽度须同批改口径。施加 = SPEC rev-10 + 全链重基线 + 重新过对抗评审。
   - 记录 `m13_v57_co91_pdn_planned_coord_clearance_gate.json` `3ede251a830108f1` / 卡 `m13_v57_CO91_pdn_planned_coord_clearance_gate.md` `1b83f41f37bf96f5`。
   - **附（U6 63 blocked 复核）**：在引擎自述设计政策（异网铜边 ≥0.3）下 **8/63 可解**（纯 DRC 口径 39/63）⇒ CO-89 §4.1「硬阻塞」结论成立；但其所称依赖「**需 DS320PR1601 器件资料**」**不成立** —— 354 球图 `ds320pr1601_ballmap.json` 与手册 `ref/ds320pr1601.pdf` **已在仓内**（v22 layer gate 已消费），真实瓶颈 = 工艺/口径裁决（via-in-pad 能力或判定域），非缺数据。

13. **✅ PDN rev-10 修复候选（CO-92 → **CO-93 已施加**；原备料留档）**：CO-91 判定 FAIL 后，其 **CO-91.1 的 `fix_candidate`（8 向 × 半径梯 0.30–2.00）违「零坐标搜索」红线，已作废**（CO-91.3 移出）。
    以**可采纳的声明式有限 palette**（原位 → 4 正交点 @0.475 → 4 正交点 @0.6；优先原位、无迭代）重算：
    `power_pad_connect.entries` 223 → **kept 188 / relocated 1 / blocked 34**；`gnd_stitch_via` 69 → **28 / 12 / 29**；`power_zones[].vias` 20 → **13 / 4 / 3**。
    - **决策覆盖不退化**（板实 pad 仍有决策 309/309），但 **ppc 已连接数 223 → 189**；要保连接数须走 **via-in-pad / 平面直连** ⇒ **工艺/口径裁决**（owner/PM + 板厂能力），非引擎可自解。
    - 短段宽度梯（223 目标，权威口径）：`0.5 → 75` / `0.3 → 15` / `0.2 → 13`（`.kicad_pro min_track_width=0.2` ⇒ 可制造下限 0.2）；残余 13 与 ppc 同源（密集场）。
    - 根因归口：`gnd_stitch_gen` 障碍集 = `layer_plan` **规划段**（**不含交付板实际铜**）⇒ v57 改 In5 走线后漂移；另其 blocked 记为 `ok: False` 而 `pdn_apply` 只跳 `blocked`/`status=="blocked"` ⇒ **直接重跑会把 blocked 缝合 via 实落**（schema 须一并对齐）。
    - **施加 = SPEC rev-10 + 全链 G4..G7 重基线 + 全部回归闸 + 重新过对抗评审**（本件不施加）。
    - 记录 `m13_v57_co92_pdn_repair_candidate.json` `7aaacd8f34559763` / 卡 `m13_v57_CO92_pdn_repair_candidate.md` `6de3c9fb2b26d45d`。

14. **⚠ rev-10 已知限制与后续（CO-93）**：**已连接 pad 223 → 189（−34）**：34 个 pad（多为 U6 0.5mm 球栅场内电源/地球）在**冻结 8L 通孔工艺 + 声明 palette** 下无合法连接位（决策覆盖仍 309/309）。保持连接数只能靠 **via-in-pad**（需板厂工艺能力 + SI/PI 证据）或 **HDI/微孔**（**L1：层数/叠层**）⇒ 本件均不擅采，登记待裁。
    施工层未同步：`_shared` 引擎（容器副本**只读冻结**）与 `pdn_apply.py` 均未改 ⇒ rev-10 的生成器为 **k2 决策层工具** `p3_v57_co93_pdn_rev10_derive.py`；`pdn_apply.py` 短段宽度仍为 0.5（施工时须以 SPEC `stub_width_mm=0.2` 为准），且 `gnd_stitch_gen` 障碍集（只取 `layer_plan` 规划段）与 blocked schema（`ok:False` vs 消费者只认 `blocked`/`status`）须一并修 ⇒ 登记为后续变更单。
    **非执行者复评欠（CO-94）**：本件为 rev-10 执行者，按 `L2_STRUCTURE_v2.0.md:137` 不得自评；rev-9 的 CO-90 复评证书随本次重基线失效。 **CO-96（pass 4/4）已对 rev-11 履行非执行者复评（rev-10 义务随重基线并入）。**

15. **⚠ L1/工艺升级（CO-94，一句话）**：rev-10 的 120 个 blocked 电源/地球中，**34 个（原 entries）与 92 个**在 L2 手段内判为不可连接（可连位仅存在于搜索式家族且余量 13.6µm、需 1.35–1.80mm 长短段）⇒ 若须连接，只能靠 **via-in-pad（板厂工艺能力 + SI/PI 证据）** 或 **HDI/微孔（层数·叠层，L1）**。请监理升级人工取裁。
    另：本件为**家族内**判定（不含狗腿/多段绕行；后者属 `EscapeAllocator` 域，未展开）；rev-10 非执行者复评（CO-94 评审项）仍欠。

16. **⚠ L1/区域划分升级（CO-95，一句话）**：rev-11 的 55 个 power entry 中 **6 项无可达 In4 路径且本网无区/区域归属冲突** ⇒ `12V_IN`（3 pad，无 In4 区、板上无铜）需裁**承载**；`P3V3_AUX` 西侧（3 pad）需裁**西区归属**（名义 MCU_VDD vs basis 文本称 P3V3_AUX+MCU_VDD 同区）。另 6 项为 band 退役后的 **L3 可达性义务**（非死结）。
    施工/引擎侧未同步项（同前）：`pdn_apply` 短段宽度仍 0.5、`gnd_stitch_gen` 障碍集仍取 `layer_plan`、blocked schema 未对齐；`_shared` 容器副本**只读冻结**未改。**rev-11 非执行者复评：已由 CO-96 履行**（verdict `REVIEW_DONE_FINDINGS_OPEN`，6 项发现见 §6-17）。

17. **⚠ CO-96 的 6 项发现（非执行者侧对抗评审 pass 4/4，对象 rev-11；机判 + 牙齿；F1 已由 CO-97 显式登记关闭其『静默』面；余项见 §6-19）**：
    - **F1（中·谱系/红线邻近）**：rev-10 重建 `power_pad_connect` 时**静默丢弃** CO-89 的退役留存键 `retired_superseded_bom`（pre-rev-9 冻结 BOM **173/9** + 孤儿分析 **55/2**）；`p3_v57_co93_pdn_rev10_derive.py` 源码零引用、CO-93 变更说明未登记 ⇒ **现行谱系断链**，违「退役决策须显式留存」。数据可由冻结源 `SPEC_k2_v4.json`（spec-rev-1，173/9）与 CO-89 记录找回 ⇒ 非数据丢失。**处置：已由 CO-97 选『显式登记其移除』分支关闭其『静默』面**（登记册 + 找回指针全可解析；见 §1 ㉚ / §6-19）；『SPEC 内回填』列为可选后续（随下一次构建期 SPEC bump），不为纯溯源字段单独重基线。
    - **F2（中·可闭合性）**：`plane_reachability_requirement` 为**声明可闭合**：gate co95 恒不返回 PASS；8 个 `covered_bridge_target` 命中的桥区 `polygon=None`（几何未建）⇒ **几何真覆盖仅 35/55**（14 待 L3、6 待 L1）。**处置 = 三分态输出 + 补闭式判据。**
    - **F3（中·脆弱性）**：`needs_region_ruling` 对 P3V3_AUX 西侧 3 pad 依赖 `why` **自由文本子串**（`"须裁"/"需要"`）⇒ 改文本即静默把 3 pad 由 L1 降级为 L3。**处置 = 改机判谓词。**
    - **F4（中·范围）**：可达性要求 scope 仅 `ppc.entries`（55）；`gnd_stitch_via` 实落 **40** / `power_zones[].vias` **17** 无闸。**处置 = 扩展 scope 或声明排除理由。**
    - **F5（低·陈旧 live 字段）**：`power_pad_connect.board_realized` 仍记 CO-89 的 **223/86**（rev-11 决策 189/120），未被 `pdn_apply.py` 消费 ⇒ 无功能影响。**处置 = rev-12 同步。**
    - **F6（低·潜在·已关闭）**：co95 `in_poly` 用 bbox 非真 PIP ⇒ **已由 CO-98 改为真·射线法 PIP**（行为中性：现行 polygon 均轴对齐矩形 ⇒ co95 记录字节不变）。
18. **✅ CO-96 复核为 OK 项（对抗性验证通过）**：**V1** rev-9→rev-10→rev-11 的 `pd` 之外**递归深比 0 变更**（仅 `spec_version`）⇒ 重基线声明成立；**V2** co95 分类**完整**（55=35+8+6+6，无遗漏/重复）；**V3** SPEC `gnd_stitch_via` 的 blocked schema（`blocked`/`status=="blocked"`）与 `pdn_apply.py` 消费口径**对齐**（60 跳过/40 施加）—— §6-16 所记「blocked schema 未对齐」**仅指上游 `gnd_stitch_gen` 产出，非现行 SPEC**；**V4** gnd_stitch 重复坐标 `(133.83,59.1)`×2 系**声明共享单孔**（basis 明证：`PCIE_DN3_P`/`PCIE_DN4_N` 共享同一 GND via）⇒ **非缺陷**；**V5** 冻结四源 4/4 MATCH、板 `0e636a67c1472462` 逐字节不变。**基线身份 OK / 牙齿 OK。**

19. **✅ CO-97（L2 自裁）退役留存完整性闸 + 显式登记册 + `_shared` 处置自裁**：把红线「退役决策须显式留存」机判化（逐版枚举退役块 → 逐相邻版求 drop → 未登记即 FAIL；拒陈旧登记项与不可解析找回指针；牙齿 3/3 合成注入）。**结果 PASS**：退役块 rev-8 5 → rev-9 8 → rev-10 13 → rev-11 15；**drop 恰 1 处**（`power_pad_connect.retired_superseded_bom` rev-9→rev-10）**已登记**（reason + 3 找回指针，冻结源 173/9、CO-89 记录 55/2、rev-9 原件均可用）⇒ **CO-96 F1 的『静默』违反面关闭**；`board_realized` 显式记为 CO-89 派生记录（消除 F5 误读）。**L2 自裁两条**：① 选 F1 的『显式登记』分支，不为纯溯源字段单独重基线（该键/`board_realized` 均不被 `pdn_apply` 消费；重基线会作废刚出具的 CO-96 证书并新增复评债 ⇒ 不成比例）；② **`_shared` 不解冻**，施工侧三项 **改由项目内引擎承载**且**仅施工期激活**（当前板逐字节不变、PDN 未施工 ⇒ 非在役缺口）。**仍未闭合（登记待办，非 PASS）**：F2/F4（可达性几何闭合 35/55 与 scope 扩展，属 L3 施工期 + 闸扩展）、F6（co95 bbox→真 PIP，latent）。记录 `m13_v57_co97_retirement_retention_gate.json` `4b1ee8924147a4f4` / 登记册 `m13_v57_retirement_registry.json` `4b13b538ba8e28ce` / 卡 `m13_v57_CO97_retirement_retention_gate.md` `2bc80fbe0c62bfd4` / 工具 `p3_v57_co97_retirement_retention_gate.py` `e9427f0f18087a18`。

20. **✅ CO-98（L2 自裁 · PDN 可审计性）可达性义务状态报告 + F6 关闭**：① **F6** = co95 `in_poly` bbox→**真 PIP**（`d5b102a1f23bb5dd`），**输出逐字节不变**（该时点 co95 记录 sha `61db48a283beeaae`（已取代；现行 = `f1c0c17ee7b379a4`））⇒ 行为中性加固；② **F2/F4 机判化**：新增只读 co98 报告（不改 co95 记录字节）—— 三态 `geometric_covered` **35** / `declared_pending_l3` **14** / `ruling_pending_l1` **6**，`machine_closable_today=false`（verdict 永不 PASS）；scope 排除 `gnd_stitch_via_realized` 40 / `power_zones_vias` 17 / `decoupling_vias` 0；③ **F3**：6 项 ruling = 5 机判（3 无区 + 2 异网冲突）+ **1 文本**（`P3V3_AUX R1.2`）。牙齿 2/2。**仍未闭合（非 PASS）**：F2 几何闭合（14 = L3 派生）、F4 scope 扩展（SPEC 变更）、F3 R1.2 判据。记录 `m13_v57_co98_reachability_status_report.json` `19c206378ee8fe95` / 卡 `m13_v57_CO98_reachability_status_report.md` `84a609e6f5e54503` / 工具 `p3_v57_co98_reachability_status_report.py` `11bfb844d542df6f`；co95 工具 `p3_v57_co95_in4_reachability.py` `4d87484ff2f1ecc7`（取代 `a2e16d6e08eef731`）。

21. **⚠⚠ CO-99（L2 自裁 · PDN 施工就绪性）两个覆盖缺口 ⇒ PDN「可施工」= FAIL**：**G1** 既有闸只判 plan-vs-board（CO-91 `Scene` 仅由板构建）⇒ 计划集内部互冲零判；**G2** 项目规则源 `hole_clearance.same_net_exempt=True` 不含 KiCad 板配置 `min_hole_to_hole=0.25`（net-agnostic）⇒ 同网孔距盲。实测（scratch，交付板不变）：SPEC 宽 0.2 ⇒ **7 异网重叠（短路）+ 35 净距 + 39 孔距（2 同址）**；引擎宽 0.5 ⇒ 13 + 127；7 重叠全在 **U6 0.5mm 场**。**dry-run**：`pdn_apply` 实落后 DRC **42→274（+232）**、未连 348→191。**根因**：① 计划集互避缺失；② 短段宽 0.5 未读 SPEC；③ stitch 互距/去重缺失；④ 规则源缺 `min_hole_to_hole`。**影响**：布线链 G4..G7 PASS 不变；**PDN 可施工 = FAIL**。记录 `m13_v57_co99_pdn_mutual_conflict_gate.json` `1d256de815b1ed87` / 卡 `m13_v57_CO99_pdn_mutual_conflict_gate.md` `c47249d3538c1d8c` / 工具 `p3_v57_co99_pdn_mutual_conflict_gate.py` `78762b3d9de90fd4`。
22. **⚠ CO-100（L2 自裁 · PDN）互障感知修复候选 = `PARTIAL`**：声明 palette + 互障（板 + 已接受计划件）+ 孔距约束的确定性重放 ⇒ **残余异网重叠 0**，但 **5 项新增 blocked（4 ppc + 1 stitch）**（kept **124**/34/13、relocated **61**/5/4）（**CO-103 校正**：原记「6 项 / 5 ppc / 全在 U6 0.5mm 场」为过期读数）。**裁定**：互冲 L2 可解。**CO-103 校正**：该 5 项为**同网冗余竞争**（4 项 U6 相邻 GND 计划孔距互障 + 1 项 J2 扇出同址重孔对），与 CO-94 的板铜阻塞不同类；「须 via-in-pad/HDI」未被证明。**rev-12 决策点**：`(a)` 登记接受 5 blocked（纯 L2）或 `(b)` L2 冗余归并裁定。**未施加**。记录 `m13_v57_co100_pdn_mutual_repair_candidate.json` `11e21f3b97bac66b` / 卡 `m13_v57_CO100_pdn_mutual_repair_candidate.md` `ff1c267f74f578dc` / 工具 `p3_v57_co100_pdn_mutual_repair_candidate.py` `341314590ceb154a`。

23. **✅ CO-101（L2 自裁 · PDN 施加）rev-12 计划集互障重导（依 CO-99/CO-100）**：ppc entries **189→185**（kept 124 / relocated **61** / 新增 blocked **4**；blocked 120→124）；stitch relocated **5** + 新增 blocked **1**；zone relocated **4**；rev-11 坐标退役留存 `retired_superseded_mutual_conflict_v1`/`power_zones_via_retired_mutual_conflict_v1`；**F5** `board_realized` 同步 + **F1** `retired_superseded_bom` 回填。**链**：G4 `cb955e9af8782d08` / G5 PASS frozen=True / L4 viol 0 / L5 DFM new=0 + SI 0.1300 / **板逐字节 `0e636a67c1472462` 不变**。**PDN 闸**：**CO-99 = PASS**（0/0/0）｜CO-91 PASS(0/0)｜CO-92 CANDIDATE｜CO-95 OPEN(35/8/6/6)｜CO-98 OPEN(35/14/6)。**残余**：引擎 dry-run 仍 +34（施工侧短段宽/去重未同步）；5 项新增 blocked（4 ppc + 1 stitch）需 L2 冗余归并或显式登记接受（CO-103 F-B）。**复评债 = CO-102**。SPEC rev-12 `1a381b06454dbe2c`；记录 `m13_v57_co101_pdn_rev12_derive.json` `cdeea6a3950f04f6`；卡 `m13_v57_CO101_pdn_rev12_derive.md` `d47eda01e3092114`；工具 `p3_v57_co101_pdn_rev12_derive.py` `977ee54f0ecdb414`。

24. **✅ CO-102（L2 自裁 · 项目内引擎承载）修正版 PDN 施加器（施工侧闭合）**：冻结 `pdn_apply` 三处施工侧缺陷（短段宽字面量 0.5 / via 不去重 / blocked 口径）⇒ 新增**项目内**施加器（坐标逐字取自 SPEC、零搜索；短段宽读 SPEC `0.2`、via 去重、blocked 对齐）。**scratch 三态 DRC**：baseline **42** / 冻结 **76(+34)** / **项目内 42(+0)** ⇒ rev-12 PDN 施工 DRC-clean。**不改冻结 `_shared`**；`gnd_stitch_gen` 生成端缺陷不在在役路径。工具 `p3_v57_co102_pdn_apply_local.py` `945b7ae7942102be`；记录 `m13_v57_co102_pdn_local_apply.json` `44002f7eac6cfa49`；卡 `m13_v57_CO102_pdn_local_apply.md` `1df2be1ef5fc0e64`。

25. **✅ CO-103（L2 · 非执行者对抗复评）rev-12 新基线 = `PASS_WITH_FINDINGS`**：9 项机判（V1 幂等重导逐字节 / V2 palette 归属+固定序独立重放 / V3 登记完整性 / V4 clearance 与 CO-91 一致 / V5 计划集互判 / V6 CO-102 发射集等价 + 三态 DRC 42 / 76(+34) / 42(+0) / V7 blocked 成因分类 / V8 声明漂移扫描 / V9 链 pin）**全过**，牙齿 7/7；**0 项 pin 漂移**。**发现**：**F-A（中）**声明漂移 —— 原记「6 项新增 blocked（5 ppc + 1 stitch，全在 U6 0.5mm 场）」实为 **5 项（4 ppc + 1 stitch）**，第 5 项在 **J2 扇出** `(133.83,59.1)`；v1.69 已校正。**F-B（高）**4 项 U6 新增 blocked 的自身位置**对板铜干净**、阻塞全为**同网 GND 计划孔距互障**（相邻 U6 GND 计划 via，d=0.180–0.403 < 0.45）⇒「须 via-in-pad/HDI」**缺乏存在性证据**（换序探针 8/13/13 且每对幸存成员翻转）；与 CO-94 板铜类不同。**F-C（中）**收口件 §1 ㉛/§6-20 的 co95 现行身份引用陈旧（`61db48a283beeaae` → 现行 `f1c0c17ee7b379a4`）、CO-96 证书未声明自身失效，且 CO-77 的 `CITE` 抓不到散文式引用；v1.69 已注明已取代。**另记**：同网孔距口径经**合成注入实测**验证（kicad-cli 对同网 GND 孔对报 `hole_to_hole`，0.080 < 0.2495）⇒ CO-99 A4 口径忠实。工具 `p3_v57_co103_rev12_nonexecutor_review.py` `5e3f91d39130b83a` / 记录 `m13_v57_co103_rev12_nonexecutor_review.json` `7f481be259865941` / 卡 `m13_v57_CO103_rev12_nonexecutor_review.md` `6ac046a885508dc6`。

26. **✅ CO-104（L2 自裁 · 过孔策略/PDN）rev-12 新增 5 项 blocked 裁定 = `ACCEPT_L2_NO_HDI` + co96 fail-closed 加固**：依 `LAYOUT_CONSTITUTION` 第二章（过孔策略 / PDN 承载 = L2；层数 = L1）对 CO-103 F-B 的 4 项 U6 ppc + 1 项 J2 扇出 stitch 作裁。**三条出路逐条量化**：**A 共享单孔**（两 pad 中心**中点**派生位 + 双短段；零自由度、非搜索）仅 **1/4 对**可行（`FB34~FA32` 可行；其余 3 对的中点正落在 U6 另一球 pad `FF11`/`FF18`/`E11` 上）⇒ 收益 = 1 个 GND 球；**B 改声明固定序**（同 palette、同检测器）canonical **4** vs 13 / 8 / 13 ⇒ canonical 已最优、无免费解；**C 加宽 palette / via-in-pad / HDI** ⇒ 违零坐标搜索红线（CO-93/94 已驳）/ 无工艺 + SI-PI 证据 / 属 L1 且本件已证「须 HDI」不成立。**裁定 = 接受**（与既有 120 项 blocked 同类处理，显式登记不静默），**不升 owner、不重基线、rev-12 不变**；本项**不再构成 L1 问题**（若日后要求「U6 GND 球 100% 独立 via」为硬需求，须走 SPEC 变更 + 全链重基线 + 换会话复评）。**附带加固（CO-103 F-C 收口，fail-closed）**：co96 默认落点改为**重跑件**，显式指向历史证书即**拒绝写入（rc=2）**，除非 `--overwrite-canonical`⇒ 历史证书 `8b591e5030aca11d` 不再会被静默改写；重跑件 `m13_v57_co96_nonexecutor_review_pass4_rerun.json` `636b1ad728f0fa91` 即 CO-96 失效的**机判化声明**（verdict `BASELINE_MISMATCH`，`co95_json` 61db48a283beeaae → f1c0c17ee7b379a4）。工具 `p3_v57_co104_pdn_blocked_ruling.py` `7b2f3ff18e0ede04` / 记录 `m13_v57_co104_pdn_blocked_ruling.json` `7254226692cb8f93` / 卡 `m13_v57_CO104_pdn_blocked_ruling.md` `ed2587023fe05ed6`。
27. **✅ CO-105（L2 自裁 · PDN 建模）CO-96 F4 落定 = `CLOSE_NO_SCOPE_EXTENSION`**：把 CO-98 的「声明排除」机判化。**V1 语义不可适用**：requirement 判据 =「落于本网 In4 铜」，而 GND 平面层 = `In1/In3/In6`、In4 仅 `P3V3/MCU_VDD/P3V3_AUX` ⇒ 对 **130 GND ppc entry + 40 GND stitch via** 无可判定（≠『未覆盖』）；requirement 对象 = 非 GND ppc entry **55**。**V2 几何待 L3**：17 个 `power_zones[].vias` **17/17** 位于 3 个 bridge zone（`P3V3_BCU_BRIDGE_IN4` 3 / `P3V3_AUX_BCU_BRIDGE_IN4` 8 / `MCU_VDD_BCU_RESISTORS_IN4` 6），其 `polygons=[]`、`geometry_status=L3_CONSTRUCTION_DERIVED` ⇒ 与 CO-98 `declared_pending_l3` 同桶；扩 scope 只并入待派生清单、不新增可判缺陷。**V3** 施工路径对 `gnd_stitch_gen` 的**代码引用 = 0**（散文复盘 1）⇒ 生成端缺陷 latent、不在在役路径。**V4** `R1.2` 判据根因 = 电源域/区域归属 = **L1**（不在本件）。**裁定 = 关闭 F4，不做 scope 扩展**；零 SPEC/板/阈值/冻结源改动、不需重基线、不需新复评。牙齿 2/2（GND 平层不含 In4 而 In4 确被占 / 17 项空几何而存在有几何 zone）。工具 `p3_v57_co105_f4_scope_disposition.py` `f357f81142161e61` / 记录 `m13_v57_co105_f4_scope_disposition.json` `758167e449ba6a07` / 卡 `m13_v57_CO105_f4_scope_disposition.md` `c40b94566b0ba3e9`。
28. **⚠→✅ CO-106（L2 · 覆盖性补全）参考平面判据 + 连续性机判**：ch.2 的 L2 裁判标准含「参考平面」，而 CO-87 记录**自报**的判据集含该词、覆盖矩阵却只有五行（参考平面无决策行/无闸）⇒ 本件补上判据并机判：**A 板框一致性**（声明多边形 = 冻结板框按 `edge_copper_min` 内缩）＋ **B 参考平面连续性**（每条规划走线每点须落在其 `impedance.per_layer[layer].refs` 任一参考层声明铜内；分类 `declared_copper_missing`（GND 整面层缺铜=缺陷）vs `region_scoped_indeterminate`（In4 按电源区裁剪/桥区待派生））＋ **C 板实佐证** ＋ **D 覆盖性补全声明**；牙齿 3/3（合成负控/正控）。**rev-12 判 `FAIL_DECLARED_COPPER_MISSING`**：60 点/36 段（In2 24 + In5 12）；根因 = 3×GND + 2×In4 多边形下边 **70.7 = 33+38−0.3**（旧 38mm 板框）而现行板框 `outline_y [33,79]`（v28 ECO y 38→46mm）⇒ 按自身 basis 应为 **78.7**；后果 = 框内平面外 **8.3mm 带无参考平面**，而施工已用该带（板实 **In5 316 段 + In2 12 段 + 24 via**，PCIe `PCIE_DN2..DN7` 蛇形恰在其中）。修复 = CO-107。工具 `p3_v57_co106_reference_plane_gate.py` `d56a1e51ece54d51` / 记录 `m13_v57_co106_reference_plane_gate.json` `3ad6e35c4bedd72e` / 卡 `m13_v57_CO106_reference_plane_gate.md` `08b46fff2a07e45a`。

29. **✅ CO-107（L2 自裁 · PDN/平面分配）SPEC rev-13 = 平面随板框对齐**：把 3×GND(In1/In3/In6) + 2×In4(`P3V3_EAST`/`MCU_VDD_WEST`) 多边形下边 **70.7 → 78.7**（与各自 basis「整面铺铜 + 板边内缩 0.3」一致），rev-12 原多边形**退役留存** `pd.zone_defs.retired_superseded_frame_extent_v1`；**只改 polygon 顶点 + `spec_version`**（阈值/网/层角色/坐标集/短段宽/blocked 台账/冻结源未动）。**几何不变性机判**：新图纸 `route_geometry`/`pages`/`landing_rows` 与 rev-12 **逐字节同**（仅 `inputs_sha.spec` 与 `frozen_sha_check` 变）⇒ 板 **`0e636a67c1472462` 逐字节不变**。SPEC rev-13 `7943be727a4f8ef9`；G4 **FEASIBLE_ALL**（34 页/crossings 0/work 546/546）主件 `73c0066df83fa8c2`；G5 PASS frozen=True；G6 PASS viol 0；G7 FAB ok + DFM new=0 + 在册未连 0/68 + SI skew 0.1300；**CO-106 复判 → `INDETERMINATE_REGION_SCOPED`（`declared_copper_missing`=0）**；链 pin 同批前移（引擎 `/FROZEN_SHA`、validator `/prefix`+`FROZEN`、闸默认 spec co78/81/84/91/92/95/98/99/102/104/105/106、co77 正则）。**复评债 = CO-108（须另一会话）**。工具 `p3_v57_co107_spec_rev13_frame_align.py` / 记录 `m13_v57_co107_spec_rev13_frame_align.json` / 卡 `m13_v57_CO107_spec_rev13_frame_align.md`。
30. **⚠→✅ CO-108（L2 · 非执行者对抗复评）rev-13 新基线 = `PASS_WITH_FINDINGS`**：独立机判 —— rev-13 差分恰为 10 polygon 顶点 + `spec_version`；退役留存 5 项完整（old=rev-12 / new=rev-13，无静默放弃）；几何（`route_geometry`/`pages`/`landing_rows`）与板 `0e636a67c1472462` 逐字节不变；链 pin 全数前移（记录内 provenance pin 全一致）；**参考平面独立点级全量重算 GND 面缺铜 = 0**、残余 54 段 100% 落 L3 桥带；**rev-12 FAIL 独立复现**（60 项/36 段 + 板实已用 8.3mm 带 In5 316 / In2 12 / VIA 24）⇒ CO-107 真修复；牙齿 3/3。**F-A（low，已校正）**：CO-105 记录 `inputs.co98_record` 在 `04d0ee1` 为陈旧值（非当时 co98）⇒ 确定性重跑恢复 `48b5bd29009a9eb8`、记录 sha→`a53f7e3b75d3d427`，本件 v1.73 同步引用。**F-B（信息性）** CO-106 字段计法非点数（不影响结论）。**F-C（low，已声明）** co87 矩阵无「参考平面」行。**F-D（medium，未决前提）** bridge zone `layer=In4.Cu` vs 名/`basis` 经 **B.Cu** 桥接（P3V3『In4 走线带不跨』）⇒『几何待 L3 派生』前提未证实；L3 派生 work order 须先裁派生层归属（若取 basis 口径则 54 段 In5←In4 为永久参考缺失 ⇒ L2）。工具 `p3_v57_co108_rev13_nonexecutor_review.py` `a745c2695e92b0e6` / 记录 `m13_v57_co108_rev13_nonexecutor_review.json` `f1ff40a43614a9e8` / 卡 `m13_v57_CO108_rev13_nonexecutor_review.md` `a00d7d89a5106c7d`。
31. **⚠→⏹ CO-109（L2 自裁 · 参考平面/PDN）In5←In4 走廊空洞 = 按设计；bridge zone = B.Cu**：由 CO-108 F-D 触发。证据：3 个 bridge zone 的声明 band 仅覆盖 In5←In4 miss 点 **6.0%**（75/1260），In4 走廊覆盖 **100%**；板 L4 无 zone ⇒ 无可派生的走廊 In4 几何。裁定：桥接层 = **B.Cu**；走廊空洞按设计（PM T2-ECN『In4 走线带不跨』）；CO-106 的 `region_scoped_indeterminate` 前提不成立（该带 In5 实为仅 In6 参考，与 `symmetric_stripline(refs=[In4,In6])` 不符）⇒ 应改判『按设计 In4 空洞』+ SI 待验登记。**OWNER（停）**：是否允许走廊补 In4 铜（反转 PM 裁决）。step ② 重定范围（②a 声明修正 / ②b SI 终判 / ②c B.Cu 几何声明缺 palette / ②d 换会话复评）。工具 `p3_v57_co109_in4_void_l2_ruling.py` `2e35c139476ae016` / 记录 `m13_v57_co109_in4_void_l2_ruling.json` `dd562f526705abef` / 卡 `m13_v57_CO109_in4_void_l2_ruling.md` `583ac243a4cf3428`。
32. **✅ CO-110（L2 自裁 · 施加）参考平面入 CO-87 矩阵 + CO-106 D 读径修复 + In4 走廊空洞按设计定案（R5'）**：(a) F-C — CO-87 矩阵补 ch.2「参考平面」行（`INDETERMINATE`，机取自 CO-106），牙齿 `ch2_criteria_all_have_rows`。(b) F-E（新发现）— CO-106 D 项读径错误致覆盖性检查恒空真，已改读 `constitution.ch2_l2_criteria`+顶层 `matrix`，复跑 `has_reference_plane_row=true`。(c) F-D/R5' — 不开 In4 走廊铜（确认 PM 既有设计）⇒ CO-109 OWNER 升级撤回；In5 该带 = In6-单参考域，SI 终判外部。零 SPEC/板改动 ⇒ 不重基线。工具 `p3_v57_co110_l2_coverage_closure.py` `354aef88cdac7634` / 记录 `m13_v57_co110_l2_coverage_closure.json` `6564e51f6ade544e` / 卡 `m13_v57_CO110_l2_coverage_closure.md` `82d2b176d45d1527`。
33. **⚠ CO-111（L2 自裁 · 参考平面/阻抗）In5 PCIe 走廊参考缺失 = 40.1%**：In4 走廊内无声明铜 ⇒ In5 走线裸露长度 **1094.8/2727.3mm（40.1%）**，16 网全为 PCIe85 差分对（最差 `PCIE_UP4` 108.7mm/50.5%）。L5 SI 只签 skew、**未签阻抗** ⇒ 暴露未验。终判 = SI9000+板厂券（外部）；补救层级 = 补 In4 铜（OWNER）/(b) 改线换层（或 L1）/(c) 走廊段宽-隙补偿（L2）。工具 `p3_v57_co111_in5_pcie_corridor_exposure.py` `c586f2a49742e137` / 记录 `m13_v57_co111_in5_pcie_corridor_exposure.json` `9ae53dbf3cfc48e1` / 卡 `m13_v57_CO111_in5_pcie_corridor_exposure.md` `09fb8d2656b5b27d`。
34. **✅ CO-112（L2 自裁 · 声明式施加）3 bridge zone = B.Cu 桥（step ②c）**：前两 zone band 取自 basis 文本、MCU_VDD 取声明 via bbox（provisional）；In4-可达性 requirement 对这 3 zone 的 targets **语义 N/A**（镜像 CO-105）；In5 区域条件参考口径（走廊 = In6-单参考）+ 走廊逐网 worklist。零 SPEC/板改动、不重基线。**In5 PCIe 阻抗暴露（CO-111）不因本件减轻**。工具 `p3_v57_co112_bcu_bridge_declaration.py` `4bda33760ad2d196` / 记录 `m13_v57_co112_bcu_bridge_declaration.json` `5f621c3c1003be00` / 卡 `m13_v57_CO112_bcu_bridge_declaration.md` `e36fc9ad1a244425`。
35. **✅ CO-113（L2 自裁 · 施加）SPEC rev-14 = 裁定写入 canonical SPEC（step ② ②a）**：仅新增声明键（走廊空洞按设计 / bridge center = B.Cu + 声明带 / 可达性 N/A scope），既有标量只 `spec_version` 变；新键无消费者 ⇒ 读数不变；几何与板逐字节不变；链 pin 同批前移。工具 `p3_v57_co113_spec_rev14_declare.py` `4c885825a6cecf60` / 记录 `m13_v57_co113_spec_rev14_declare.json` `261fa00af228be4a` / 卡 `m13_v57_CO113_spec_rev14_declare.md` `29554ef222ec2e79`。
36. **⚠ 更正 CO-115（L2 自裁 · 事实更正）In4 走廊空洞 = 失效 keepout 残留（待 L3 派生），非按设计**：走廊边界 49.8 = 退役 keepout 50.0−0.2、88.37 = 88.17+0.2；CO-95 effect「In4 铜可在原 band 内按网归属铺设」⇒ CO-109/110/113 的「按设计」判定**更正**；In5 40.1% 暴露**可修**；rev-14 键须 rev-15 更正。**OWNER/L1 停点**：band 内铺铜的区域归属界面。工具 `p3_v57_co115_corridor_stale_keepout_correction.py` `f5d0007766677616` / 记录 `m13_v57_co115_corridor_stale_keepout_correction.json` `b200828cb797817e` / 卡 `m13_v57_CO115_corridor_stale_keepout_correction.md` `700f4c6d6c226059`。
37. **⚠ CO-114（L2 · **非执行者**对抗复评）rev-14 = `PASS_WITH_FINDINGS`**：六面机判全 True + 9 牙齿；机械声明成立（仅新增声明键 / 几何与板逐字节同 / SPEC pin 前移 / 新键零消费者）。**6 发现**：F-1 high（rev-14 错误键，待 rev-15）｜F-2 medium（co87 证据文本陈旧）｜**F-6 medium（rev-14 重基线致 4 记录 5 处 inter-record provenance pin 陈旧**，与 CO-108 F-A 同族、CO-77 盲区）｜F-3 low（CO-113 new_keys 少声明 `bcu_bridge_bands_source`）｜F-4 low（CO-111 措辞）｜F-5 info（已由 v1.81 更正）。
## 7. 归档
变更单 CO-05..CO-46 记录与 DRC 明细（`m13_v57_co41_refclk_drc_after.json` / `m13_v57_co43_refclk_drc_after.json` /
`m13_v57_CO45_refclk_skew_meander_impl_record.md` `7b8cb5b1294d8c71` /
`m13_v57_CO46_validator_frozen_set_fix.md` `bf7431bc6559ea98` /
`m13_v57_CO47_l5_inscope_connectivity_predicate.md` `031fc91aa520cb92` /
`m13_v57_CO48_l5_g7_record_emit.md` `7e094c2db5bf3b3d` /
`m13_v57_CO49_l4_byte_reproducible.md` `6c27149fff749a1d` /
`m13_v57_CO50_pdn_fact_verified.md` `311e98163d49ac82` /
`m13_v57_CO51_dfm_multiset_metric.md` `922feaf4b5c8c143` /
`m13_v57_CO52_via_budget_closure.md` `eaaea6b5e4456ddc` /
`m13_v57_CO53_intrapair_geometry_impedance_open.md` `36f16620c7132da6` /
`m13_v57_CO58_interpair_baseline_reconciliation.md` `267621cdcfae1bbc` /
`m13_v57_CO59_L2_residual_closure_and_interpair_target.md` `0fdb19fec39bf110` /
`m13_v57_CO67_L2_redline_ruling.md` `c562419d70a41ab9` /
`m13_v57_CO68_L2_option_a_execute.md` `17965908fd5d5635` /
`m13_v57_CO69_L2_option_a_chain.md` `661ad6c57e0e2418` /
`m13_v57_co69_adversarial_review.json` `18a86c998dd6b4de`（CO-79 加固后，10/10） /
`m13_v57_co72_pdn_align.json` /
`m13_v57_co73_layer_role_consistency.json` /
`m13_v57_CO74_L2_pdn_bcu_rehost.md` `8c1cec7fb48ad2ab` /
`m13_v57_co74_pdn_bcu_rehost.json` `8e3bbfb0e197cf67` /
`m13_v57_co74_chain.json` `51dbb2076bc379e4` /
`m13_v57_CO75_L2_west_pitch_origin_search.md` /
`m13_v57_co75_west_pitch_origin_search.json` `c59e9955d344d75f` /
`m13_v57_CO76_nonexecutor_adversarial_review.md` `32d5868a1a2880b4` /
`m13_v57_co76_nonexecutor_review.json` `cf5b4ec0e880e5d2` /
`m13_v57_co69_adversarial_review.json` `18a86c998dd6b4de`（CO-79 加固后，10/10） /
`m13_v57_co77_closure_declaration_sweep.json` /
`m13_v57_CO77_closure_declaration_sweep.md` /
`m13_v57_CO78_layer_role_drift_gate.md` `0185363ec8ddf5f7` /
`m13_v57_co78_layer_role_drift_gate.json` `1599c8f043de58d5` /
`m13_v57_CO79_probe_vacuity_hardening.md` /
`m13_v57_co69_adversarial_review.json` `18a86c998dd6b4de`（CO-79 加固后） /
`m13_v57_CO80_l4_project_rule_align.md` `07cbdea3d139927a` /
`m13_v57_co80_l4_project_rule_align.json` `d617a4c5e4e4523f` /
`m13_v57_CO81_project_rules_gate.md` /
`m13_v57_co81_project_rules_gate.json` `8ef7a02d7f3d2222`（CO-89 重扫 rev-9 后；原 `ebd163058efaad14`、`a9161a86271c068b`、`1f25c6a9db6923f0` 已取代） /
`m13_v57_CO82_project_netclass_gap.md` `0d0d6e7640fa970e` /
`m13_v57_co82_l4_project_netclass_align.json` `0c8745064785ee57` /
`m13_v57_CO83_netclass_vs_spec_gate.md` `47ebff527cc431ef` /
`m13_v57_CO84_dru_domain_gate.md` `996bee590912e823` /
`m13_v57_co84_dru_domain_gate.json` `45fe68c41a8e1a4c` /
`m13_v57_co85_nonexecutor_review_pass2.json` /
`m13_v57_CO85_nonexecutor_adversarial_review_pass2.md` /
`m13_v57_co86_l2_span_option_closure.json` `d0a59f85b74687d5` /
`m13_v57_CO86_l2_span_option_closure.md` `0d1fd3b33fb802fe` /
`m13_v57_co87_l2_acceptance_coverage.json` `46d15557477d164b` /
`m13_v57_CO87_l2_acceptance_coverage.md` `322baa098740b259` /
`m13_v57_co88_pdn_board_reality_gate.json` `f90d65369cab92dc`（已取代：CO-90 重生成 `bf69909aa64dc494`）/
`m13_v57_CO88_pdn_board_reality_gate.md` `50aa8c67d7b10438` /
`m13_v57_co89_pdn_board_realize_rev9.json` `4f94df5981aaab45` /
`m13_v57_CO89_pdn_board_realize_spec_rev9.md` `7ed85bbda42ad1b1` /
`m13_v57_co90_nonexecutor_review_pass3.json` `badba5d9ce39a022`（CO-90.2 实测值；v1.55 曾引 `897ff5cc371d135d` 为过期值 ⇒ co77 报 CITATION_MISMATCH，本版修正；原 `3ba2ca0ce3966fe8`、`98651571b93a07a9` 已取代） /
`m13_v57_CO90_nonexecutor_adversarial_review_pass3.md` `be00ceedae5f7786`（引用校正 + F4/F5 入册后） /
`m13_v57_co88_pdn_board_reality_gate.json` `17719cf7f8e3e702`（CO-90 F1/F2/F4 修复后，CO-88.3；原 `f90d65369cab92dc` 已取代）/
`m13_v57_co77_closure_declaration_sweep.json` / `m13_v57_CO77_closure_declaration_sweep.md` /
`m13_v57_co91_pdn_planned_coord_clearance_gate.json` `3ede251a830108f1` /
`m13_v57_CO91_pdn_planned_coord_clearance_gate.md` `1b83f41f37bf96f5` /
`p3_v57_co91_pdn_planned_coord_clearance_gate.py` `25be5b6053e67229` /
`m13_v57_co92_pdn_repair_candidate.json` `7aaacd8f34559763` /
`m13_v57_CO92_pdn_repair_candidate.md` `6de3c9fb2b26d45d` /
`p3_v57_co92_pdn_repair_candidate.py` `c9c86706fbab5aff`）已入库；**本件取代 v1.60**；v1.55..v1.58 原样保留不改（v1.55 的 co90 过期引用已在 v1.56 修正；CO-91 的 fix_candidate 已在 CO-91.3/CO-92 作废替代；CO-91 对 rev-9 的 FAIL 判定与 CO-92 备料读数均为留档，现行判定见本版）。
监理/tag 政策：`k2-v57-g7-l5-pass`（G7/L5 PASS）已 push；`git ls-remote` 核验 `^{}` → `b5afe47`。

End of boundary v1.61（含 CO-67..CO-95）。

### 附：CO-114 本件产物（v1.81 新增）
`p3_v57_co114_rev14_nonexecutor_review.py` `6642f8156e349c24` /
`m13_v57_co114_rev14_nonexecutor_review.json` `20adc9fb67e62c63` /
`m13_v57_CO114_rev14_nonexecutor_review.md` `ab0da32774a0714d`

End of boundary **v1.81**（含 CO-67..CO-115；+ CO-114 非执行者对抗复评）。

---

## 附：CO-117（L2 自裁 · band In4 铺铜归属 + SPEC rev-15）当前态引用

现行 L4 板 **`d4e81f647be7f980`**（CO-133 施工后）。收口件内 sha 一律为**当前文件实测值**。

- SPEC rev-15（CO-117 施加件） `SPEC_k2_v4.spec-rev-15.json` `48d6fc7c565c8862`（已取代，历史）
- SPEC rev-16（已取代，历史；CO-122b 施加） `SPEC_k2_v4.spec-rev-16.json` `5748828a23161250`
- SPEC rev-17（**现行**；CO-130 施加：D-6 网类 12V_IN→POWER + 退役三 zone 的 B.Cu 载体声明 + stackup In4 文本对齐） `SPEC_k2_v4.spec-rev-17.json` `9fea9fd20149c736`
- G4 主件图纸 `m13_v57_w3_joint_assignment.json` `60cbd331836e52b7`
- G5 校验 `m13_v57_w3_validation.json` `8b385d6c554ac527`
- L4 施工 `m13_v57_l4_construction.json` `d11a38519482b0cf`
- L4 校验 `m13_v57_l4_validation.json` `aa666a49e36883c7`
- L5 fab `m13_v57_l5_fab_record.json` `791012e88b514faa`
- L5 SI `m13_v57_l5_si_pi_emc_record.json` `97c867e89fc6df6c`
- co95 记录 `m13_v57_co95_in4_reachability.json` `4525e38330ee599f`
- co98 记录 `m13_v57_co98_reachability_status_report.json` `19c206378ee8fe95`
- co87 记录 `m13_v57_co87_l2_acceptance_coverage.json` `46d15557477d164b`
- co105 记录 `m13_v57_co105_f4_scope_disposition.json` `758167e449ba6a07`
- co106 记录 `m13_v57_co106_reference_plane_gate.json` `3ad6e35c4bedd72e`
- co99 记录 `m13_v57_co99_pdn_mutual_conflict_gate.json` `1d256de815b1ed87`
- co91 记录 `m13_v57_co91_pdn_planned_coord_clearance_gate.json` `3ede251a830108f1`
- co92 记录 `m13_v57_co92_pdn_repair_candidate.json` `7aaacd8f34559763`
- co104 记录 `m13_v57_co104_pdn_blocked_ruling.json` `7254226692cb8f93`
- co102 记录 `m13_v57_co102_pdn_local_apply.json` `44002f7eac6cfa49`
- co69 记录 `m13_v57_co69_adversarial_review.json` `18a86c998dd6b4de`
- co117 记录 `m13_v57_co117_band_allocation_rev15.json` `957c7c5ffd8e8a81`
- co117 卡 `m13_v57_CO117_band_allocation_rev15.md` `0b8a747960ce0fe1`

- 工具 `p3_v57_co117_band_allocation_rev15.py` `f1db632708f66f7d`

**L2 判定**：band In4 铺铜归属 = 走廊分配/PDN 架构（《宪法》ch.2 = L2），且 L2 **裁判标准**含『参考平面』；冻结 L1 仅**粗分区 + 域集合**，域集合不变 ⇒ L2（先例 **CO-74**）。**分配（零搜索）**：`MCU_VDD_WEST` 东缘 49.8→**57.75**（R29/R31-R34 57.55 + 0.2）；`P3V3_EAST` 西缘 88.37→**57.95**（余下走廊归东侧权域）；**In5 单参考暴露 40.14%→0.21%**（残余 = 强制 0.2mm POWER 异网净距缝）。**SPEC rev-15**：`in4_corridor_void_by_design_v1`（CO-115 判错）→ 退役留存 `retired_in4_corridor_void_by_design_v1`；新增 `in4_band_copper_allocation_v1`；P3V3 由 `unresolved` → `resolved_by_co117`（U6 6 球）；co98 三态 **45/4/6**（原 35/14/6）。板/G7 DFM/SI 不变。**复评债 = CO-114 rev-15 半程（另一会话）。**

---

## 附二：L2 闭合声明 + L1 待裁（决策就绪；本段不代填、不推荐分区）

**L2 闭合**：band In4 铺铜归属（CO-117，rev-15）+ In5 走廊参考缺失已闭合至外部终判；co95 复算 = `covered_explicit` **45** / `covered_bridge_target` **4** / **`l3_obligation` = 0** / `needs_region_ruling` **6**；co98 三态 **45 / 4 / 6**。L2 侧**无可自裁剩余项**。

**L1 待裁（《宪法》ch.2：电源域划分；域集合变更 ⇒ L1）**（**② 已由 CO-121 判为 L2 并于 CO-122b 施加 ⇒ 下表 ② 行已被更正行取代**；第 ④ 项为 CO-118 新发现）。以下为 owner 决策所需的**声明事实 + L2 结构可行性预检**（机判，零搜索；不代填、不推荐分区）：

**西区 via 布局（rev-15 声明，机判）** —— `12V_IN`：C88.1(28.275,41.5) / U2.4(31.05,39.83) / U2.6(35.725,37.635)；`MCU_VDD`(10)：C86.1(30.275,56.0) / C85.1(30.475,54.5) / U1.6(36.75,49.775) / U4.2(40.95,38.775) / E2.2(41.275,59.365) / E2.8(45.95,57.17) / R31-R34.2(56.725, 66.5/67.5/68.5/69.5)；`P3V3_AUX`：C90.1(28.975,53.0) / U1.15(39.425,53.25) / R1.2(51.725,37.0)（J4.A9 已由桥区声明覆盖）。

| # | L1 议题 | 声明事实（rev-15 机判） | L2 结构可行性预检（机判） |
|---|---|---|---|
| ① | `12V_IN` 承载 | 3 pad 无任何 In4 区（C88.1/U2.4/U2.6，簇于 x28–36 / y37–41.5）；`pd.decoupling` 含 `12V_IN{C88}`、`power_pad_connect.board_realized.pwr_nets` 含 `12V_IN` ⇒ **是 PDN 网**（非 scope 伪项） | 若定为 In4 新区 ⇒ **域集合 +1（L1）**；pocket 几何余量充足（`MCU_VDD_WEST` 内 x/y 边距 ≥4.1mm）**但**簇 bbox `[28.275,37.635]–[35.725,41.5]` **内夹 `U2.5`(P3V3) + `C88.2`(GND)** ⇒ 凸 pocket 围异网 via ⇒ 形状非闭式（依赖走线搜索）⇒ **与 ④ 同源、L2 不可自裁**；另一路径（改 F.Cu 走线承载）⇒ 网范围/电源域口径 ⇒ owner |
| ② | `P3V3_AUX` 西区归属 | **已闭合：CO-121【L2 自裁】裁定 + CO-122b 施加（SPEC rev-16）** | **层级更正**：冻结 L1 实测仅含域集合 + 粗分区，本件二者不变 ⇒ L2（先例 CO-74；判据同 CO-117 `level_basis`）；原列『L1 待裁』系过高归口。**机判**（声明式有限家族，零搜索）：净距 **0.375** 系闭式（POWER 0.2 + via_od/2，孔规则更松）；行内异网 via（C90.2/U5.2）与之同 y、且 R28.2(GND) 与 R1.2 同 x ⇒ 直连带/柱必重叠 ⇒ 取绕行侧 below + 柱绕；**五测全过**、worst margin **0.100mm**、min_merge 0.300、牙齿 **3/3**。**施加**：`P3V3_AUX_WEST` 单环 zone（6 声明矩形闭式并集；co95 读 singular `polygon`）+ `in4_west_aux_allocation_v1` + `resolved_by_co121`；**L4 板逐字节不变** |
| ③ | ~~L1① 对间净空 0.875~~ | **已闭合（CO-134，L2 自裁）**：③ = **工程换算错误**（非需求）；REQ-R3-2「3W 原则」忠实实现 = 对间铜边 ≥ 2×w（按层：外层 0.410 / 内层 0.320）⇒ SPEC rev-19 施加 + 0.875 退役；**撤回 owner 升级（无 owner 项）**；域外板实偏差 3 处已登记为工程开放项 ⇒ SI/板厂券 或后续几何迭代 |
| ④ | **B.Cu 桥冲突（CO-118）** | CO-74 `bcu_power_copper_policy=PROHIBITED`（『不得铺电力铜/**搭桥**』）↔ CO-112 三桥区 `bridge_layer="B.Cu"` + `na_scope_v1.bcu_bridge_zone_targets` N/A 裁定（同批 zone 的 `carrier_change` 又写 `B.Cu→In4.Cu`） | 若禁令成立 ⇒ **4 target 无载体**：P3V3 `C84.1/U2.5/U4.3` **落在 `MCU_VDD_WEST` 内**、P3V3_AUX `J4.A9` 落在 `P3V3_EAST` 内 ⇒ **R1**（L2 In4 pocket，受 requirement ④ 同网连通约束、可能不可行）或 **R2**（owner 放宽红线）。**CO-118 追加机判**：`P3V3_BCU_BRIDGE_IN4` 簇 bbox 内夹异网 via `U4.2`(MCU_VDD)/`U2.6`(12V_IN) ⇒ 凸 pocket 会围住异网 via ⇒ 形状非闭式（依赖走线搜索）⇒ **R1 不能在 L2 自裁** ⇒ 本项闭合归 owner（R2/红线或 L1） |

**板实旁证**：交付板 `k2_v4_8L.l4.kicad_pcb` `d4e81f647be7f980`（**CO-133 施工后**）= 图纸 2708 track/252 via **+** PDN 185 短段/241 via/9 zone（In4 含 `12V_IN_IN4_CARRIER`/`P3V3_AUX_WEST`/两桥区，3 区 `fill_priority=1`）；**施工前** `0e636a67c1472462` 为零 PDN 铜 ⇒ 本议题的承载/归属裁决仍属 **SPEC 声明层**，板实为其确定性物理实现。

**L2 过程闸（CO-120，新）**：`p3_v57_co120_provenance_pin_gate.py` `28d6211f32318d9b`、记录 `m13_v57_co120_provenance_pin_gate.json` `df6c9135bc02bbe4`、卡 `m13_v57_CO120_provenance_pin_gate.md` `bc6ca56de45fda27` —— 关闭 CO-108/CO-114 **F-6 盲区**（记录内 inter-record provenance pin 一致性）；首跑 **PASS**（pins 12：match 8 / 豁免历史 3 / 未声明陈旧 0 / 解析歧义 1；牙齿 2/2）。

## 11. CO-133（L2 自裁 · 施工期物理施加）当前态引用

**结论**：rev-18 SPEC 声明的 PDN 铜**已物理落板** ⇒ 板 `0e636a67c1472462` → **`d4e81f647be7f980`**。
板实 vs SPEC **逐项相等**（9 zone 含 `fill_priority` / 241 via / 185 F.Cu 短段）；kicad-cli `--severity-all` 违规**类型逐项同**（42/42）、未连项 348→179；
L4-A..F 仍 **viol 0**；L5 FAB ok / DFM new=0 / SI 0.1300；co95 55/55、co98 55/0/0；G4/G5 不动。

**施加机制**：项目内 applier 追加④ **幂等 purge-then-add**（删本阶段将重发的 PDN 网铜；pcbnew 删除走 `RemoveNative` —— `Remove` 会泄漏并使 `GetTracks()` 退化）+
CO-49 `canonicalize_board` ⇒ 净板/已施工板两次投喂**同一字节**（实测重跑后板 sha 不变）。

**连带更正（显式登记，见 `input_defect_register_v1.json`）**：
1. **co91 孔缘分支多扣一次 `via_r`**（与其自身 `drc_rules.json` geometry_translation 相悖）⇒ 施工后 14 项假阳性；更正后 0/0（真值 +0.284 / req 0.25；copper gap +0.209）。
2. **co104 replay 场景**改排除计划自身网（板态无关）+ V3 断言/verdict 改数据派生；残留：canonical replay 3 vs 声明 blocked 4 ⇒ 声明**偏保守 1 项**（无功能影响）。
3. **provenance pin**：co105←co98 随重跑刷新；co111←l5_si / co118←co95 属 point-in-time ⇒ co120 EXEMPT 明列理由。

| 工件 | sha16 |
|---|---|
| 工具 `p3_v57_co133_pdn_construction_apply.py` | `1947f3c0332d57fc` |
| 记录 `m13_v57_co133_pdn_construction_apply.json` | `62a9931227281c10` |
| 卡 `m13_v57_CO133_pdn_construction_apply.md` | `d3ba4233a61403c0` |
| applier `p3_v57_co102_pdn_apply_local.py`（幂等+RemoveNative） | `945b7ae7942102be` |
| 板 `k2_v4_8L.l4.kicad_pcb`（施工后） | `d4e81f647be7f980` |
| `m13_v57_l4_validation.json` | `aa666a49e36883c7` |
| `m13_v57_l5_fab_record.json` | `791012e88b514faa` |
| `m13_v57_l5_si_pi_emc_record.json` | `97c867e89fc6df6c` |
| `m13_v57_co91_pdn_planned_coord_clearance_gate.json` | `3ede251a830108f1` |
| `m13_v57_co104_pdn_blocked_ruling.json` | `7254226692cb8f93` |
| `m13_v57_co97_retirement_retention_gate.json` | `4b1ee8924147a4f4` |
| `m13_v57_co98_reachability_status_report.json` | `19c206378ee8fe95` |
| `m13_v57_co99_pdn_mutual_conflict_gate.json` | `1d256de815b1ed87` |
| `m13_v57_co102_pdn_local_apply.json` | `44002f7eac6cfa49` |
| `m13_v57_co105_f4_scope_disposition.json` | `758167e449ba6a07` |
| `m13_v57_co106_reference_plane_gate.json` | `3ad6e35c4bedd72e` |
| `m13_v57_co120_provenance_pin_gate.json` | `df6c9135bc02bbe4` |
| `m13_v57_co124_input_selfcheck_gate.json` | `d64da9e0e9e53f7a` |
| `m13_v57_co88_pdn_board_reality_gate.json` | `17719cf7f8e3e702` |
| `m13_v57_co78_layer_role_drift_gate.json` | `1599c8f043de58d5` |
| `m13_v57_co81_project_rules_gate.json` | `8ef7a02d7f3d2222` |
| `m13_v57_co84_dru_domain_gate.json` | `45fe68c41a8e1a4c` |
| `input_defect_register_v1.json`（含 CO-133 三条工具缺陷登记） | `b1d8c7130240c4d0` |

**未决（不变）**：非执行者复评（本件 + rev-18 新基线）；③ 已撤回 owner 升级（CO-134 判为工程换算错误并落地忠实实现）；外部输入（板厂券/SI9000、PM 压降·热）。

## 12. CO-134（L2 自裁 · 需求/实现分家｜整改通知 #09）当前态引用

**③ 撤回 owner 升级**：0.875 系**工程换算错误**（= 2×0.4375；本板无任何层/带使用该线宽），非需求。
**需求（冻结）** `REQ-R3-2` = 对间不串扰 ⇒ 3W 原则：对间中心距 ≥ 3×线宽 w。
**忠实实现（工程迭代）** `DV-INTPAIR-EDGE`：对间铜边净空 ≥ 2×w（按层：F/B 0.410、In2/In5 0.320；带内下界 0.180）⇒
SPEC **rev-19** `5f72182a2616392c`（白名单外 0 改动；0.875 退役留存 `retired_inter_pair_spacing_0p875_v1`）。
**可达性（闭式）** REACHABLE：域外 span_min 0.355 + 0.410 = 0.765 ≤ cap（WEST 1.05 / EAST 1.449）；焊盘场属 ECN-001 escape 域（已声明放宽）。
**板实（实测）** 域外偏差 3 处（工程开放项，非 owner）：F.Cu 0.3294（−0.0806）/ B.Cu 0.3450（−0.0650）/ In5.Cu 0.3125（−0.0075）⇒ 路由 SI/板厂券 或后续几何迭代。
**几何不动**：板仍 `d4e81f647be7f980`（rev-19 仅改声明定值）；G4 主件重基线（几何/交叉不变）。

| 工件 | sha16 |
|---|---|
| 规矩件 `REQUIREMENT_IMPLEMENTATION_SEPARATION_v1.0.md` | `0181186c4b4266e1` |
| 台账 `derived_value_ledger_v1.json` | `82f3cb801cf5f236` |
| 定义件 `BASIC_SKILL_VS_REDLINE_v1.1.md`（③ 重新定性 bump） | `348735156c9d9b1d` |
| 工具 `p3_v57_co134_req_impl_separation.py` | `8f59c5be82fe9d06` |
| 记录 `m13_v57_co134_req_impl_separation.json` | `1e5aa8503d211411` |
| 卡 `m13_v57_CO134_req_impl_separation.md` | `813e66a5eb4b0e60` |
| 登记簿 `input_defect_register_v1.json` | `b1d8c7130240c4d0` |
| `SPEC_k2_v4.spec-rev-19.json` | `5f72182a2616392c` |
| `m13_v57_w3_joint_assignment.json`（G4 重基线） | `60cbd331836e52b7` |
| `m13_v57_w3_validation.json`（G5） | `8b385d6c554ac527` |
| `m13_v57_l4_construction.json` | `d11a38519482b0cf` |
| `m13_v57_l4_validation.json` | `aa666a49e36883c7` |
| `m13_v57_l5_fab_record.json` | `791012e88b514faa` |
| `m13_v57_l5_si_pi_emc_record.json` | `97c867e89fc6df6c` |
| `m13_v57_co124_input_selfcheck_gate.json`（K9 + T5/T6/T7） | `d64da9e0e9e53f7a` |
| `m13_v57_co95_in4_reachability.json` | `4525e38330ee599f` |
| `m13_v57_co98_reachability_status_report.json` | `19c206378ee8fe95` |
| `m13_v57_co99_pdn_mutual_conflict_gate.json` | `1d256de815b1ed87` |
| `m13_v57_co104_pdn_blocked_ruling.json` | `7254226692cb8f93` |
| `m13_v57_co105_f4_scope_disposition.json` | `758167e449ba6a07` |
| `m13_v57_co106_reference_plane_gate.json` | `3ad6e35c4bedd72e` |
| `m13_v57_co91_pdn_planned_coord_clearance_gate.json` | `3ede251a830108f1` |
| `m13_v57_co88_pdn_board_reality_gate.json` | `17719cf7f8e3e702` |

**未决（CO-136 后更新）**：外部输入（SI9000/板厂券 ⇒ 复核 as-built 3 处偏差 + ③ 的 w_min；PM 压降·热）；CO-135 报告项 F4（handoff pin 失准）/F5(a)（③ 根因叙述）＝点态叙述；F6 的 pad_field 声明豁免终判 = SI/板厂券。**无 owner 项**。

## 14. CO-136（L2 自裁 · 闸卫生续：关闭 CO-135 F5(b)/F6）当前态引用

**性质**：L2 自裁（工具/声明/登记卫生），无 L1 项。

- **F6 关闭**：co106 连续性检测器牙齿原把板内定点 `(60.0,50.0)` 钉为「In4 无铜」；`P3V3@P3V3_EAST` 铺铜随 CO-107（板框对齐 70.7→78.7）/CO-117 扩展后覆盖该点 ⇒ 牙齿**假阴性**、`teeth_ok=False` 长期带病。改为**数据无关的合成正/负控**（只测 `pip` 分类原语分「有铜/无铜」）⇒ rev **CO-106.2**，teeth **4/4** 全真（gate verdict 仍 `INDETERMINATE_REGION_SCOPED`，与本牙齿无关）。
- **F5(b) 关闭**：co124 记录硬编码定义件「v1.0 提议件」，实际在册件 = `L2/BASIC_SKILL_VS_REDLINE_v1.1.md` ⇒ 版本改由**文件名派生**（rev **CO-124.2**）；K1 docstring / scan_scope / 卡同步去硬编码。
- **F1 强化**：co77 表格行 citation 覆盖新增**负控牙齿**（合成表格行 + 漂移 sha ⇒ 必抓）⇒ rev **CO-77.5**，`teeth_ok=True`；正则退化即 verdict `TEETH_FAIL`。
- **登记簿**：新增并关闭 2 条 `TOOL_DEFECT`（co124 标签 / co106 陈旧牙齿）⇒ `TOOL_DEFECT` 4→6、总 17；`OPEN` 仍 1（as-built 偏差，待外部输入）。

| 工件 | sha16 |
|---|---|
| 工具 `p3_v57_co106_reference_plane_gate.py`（CO-106.2） | `d56a1e51ece54d51` |
| 记录 `m13_v57_co106_reference_plane_gate.json` | `3ad6e35c4bedd72e` |
| 记录 `m13_v57_co124_input_selfcheck_gate.json`（CO-124.2） | `d64da9e0e9e53f7a` |
| 登记簿 `input_defect_register_v1.json`（17 项） | `b1d8c7130240c4d0` |
| 工具 `p3_v57_co77_closure_declaration_sweep.py`（CO-77.5） | `5459595adc50b392` |
| 工具 `p3_v57_co136_gate_hygiene.py` | `a5b712e48119fdfb` |
| 记录 `m13_v57_co136_gate_hygiene.json` | `77b3ad0a49042ba5` |
| 卡 `m13_v57_CO136_gate_hygiene.md` | `da0e86fc89ad3df1` |

## 13. CO-135（非执行者复评 · rev-19 + CO-134｜L2 声明/工具卫生修正）当前态引用

**verdict：PASS_WITH_FINDINGS**（另一会话执行；非 CO-134 执行者，禁自评已满足）。实质：**全链独立复现** —— G4 `60cbd331836e52b7` / G5 `8b385d6c554ac527` / L4 val viol 0 `aa666a49e36883c7` /
L5 DFM new=0·SI 0.1300 / co124 findings 0（T1..T8）/ co95 55/55 / co98 55/0/0 / PDN co88/co91/co99/co102(+0)/co104/co105/co106 /
co69 10/10 / co120 PASS；冻结四源 **4/4**；SPEC rev-19 白名单外 **0** 改动。
**③ 定性**：`整改通知 #09`（监理指令）明确 ③ = 工程换算错误、撤回 owner 升级 ⇒ CO-134 属**执行指令**，非越权需求变更。
**as-built**：域外 3 处偏差独立重算复现（F.Cu 0.3294 / B.Cu 0.3450 / In5 0.3125）⇒ `OPEN_ENGINEERING` 处置妥当（路由 SI/板厂券 或另开几何 CO）。

**修正（L2 自裁）**：
- **F1** co77 收口扫描正则**未覆盖 markdown 表格行**（`| \`file\` | \`sha\` |`）⇒ 链表过期 pin 静默放过；已扩为**内联+表格**（revision **CO-77.4**）+ 候选解析补 `_shared`。修复后 co77 立报 22 处 mismatch ⇒ 本件链表 pin 已全量刷新。
- **F2** rev-19 重基线不完备：`co78/co81/co84` 提交态仍 pin **SPEC rev-18** ⇒ 已对 rev-19 重跑（全 PASS，见下表）。
- **F3** L5 fab 记录 pin 陈旧 L4 construction（`305a42a890593552`）⇒ 已重跑刷新为现行 `d11a38519482b0cf`。
- **F4/F5/F6**（报告项）：handoff pin 失准（G5 `4d5abd85e1d47705` 全仓无对应工件，实际 `8b385d6c554ac527`；co133 记录 `1fab64009ecb9048` 为旧值）；③ 根因叙述「2×0.4375」与来源件「5×线距」不一致（**不改退役结论**）；co124 定义件仍标 v1.0（实为 v1.1）；co106 `teeth_ok=False`（已自披露）；pad_field 可达性为**声明豁免**（终判 = SI/板厂券）。

| 工件 | sha16 |
|---|---|
| 工具 `p3_v57_co135_review_hygiene.py` | `827a49520c8e2cd5` |
| 记录 `m13_v57_co135_review_hygiene.json` | `563b0df8d8e7e882` |
| 卡 `m13_v57_CO135_review_hygiene.md` | `45a4a7e974299b2e` |
| 工具 `p3_v57_co77_closure_declaration_sweep.py`（CO-77.4） | `5459595adc50b392` |
| `m13_v57_co78_layer_role_drift_gate.json`（对 rev-19 重跑） | `1599c8f043de58d5` |
| `m13_v57_co81_project_rules_gate.json`（对 rev-19 重跑） | `8ef7a02d7f3d2222` |
| `m13_v57_co84_dru_domain_gate.json`（对 rev-19 重跑） | `45fe68c41a8e1a4c` |
| `m13_v57_l5_fab_record.json`（construction pin 刷新） | `791012e88b514faa` |
| `m13_v57_l5_si_pi_emc_record.json` | `97c867e89fc6df6c` |

## 15. CO-137（L2 分析 · 只读：as-built 对间偏差几何修正可行性）当前态引用

对 CO-134 登记的域外 3 处偏差做**确定性可行性判定**（最近邻闭式几何，零坐标搜索，只读）：
Δ = 2w(层) − 实测铜边；把该对整对沿「远离对方」方向平移 ⇒ 需该侧可用余量 ≥ Δ（否则转移违规）。

| 层 | 位置 | Δ(mm) | 远侧余量(mm) | 判定 |
|---|---|---|---|---|
| B.Cu | 92.15,47.912 | +0.0650 | 无远侧邻对 | `NO_FAR_NEIGHBOUR`（站点处于弯/端接，单侧判据不适用） |
| F.Cu | 137.24,59.575 | +0.0806 | 0.3438 | `FEASIBLE_SHIFT`（局部可平移） |
| In5.Cu | 74.75,40.8 | +0.0075 | −0.0075 | `INFEASIBLE_ONE_SIDE`（两侧均已紧贴，平移即转移违规） |

**结论**：几何路线**非一致可行**（`MIXED`）⇒ 维持 CO-134 处置（`OPEN_ENGINEERING`）：优先 SI/板厂券判**可接受性**；
若须消除，须按站点**构造性重路由**（F.Cu 局部可平移；In5 需换层/改走廊；B.Cu 需站点级构造），另开几何 CO。

| 工件 | sha16 |
|---|---|
| 工具 `p3_v57_co137_interpair_fixspace.py` | `730d7149fcf74dda` |
| 记录 `m13_v57_co137_interpair_fixspace.json` | `f94f61d8e014c694` |
| 卡 `m13_v57_CO137_interpair_fixspace.md` | `7e988b512a2082a7` |

## 16. CO-138（L2 分析 · 只读：偏差耦合几何画像）当前态引用

动机：SPEC `inter_pair_derivation_v1.scope` 明文「域外对间**长平行**」；co134 板实测量取「异对任意两段最小铜边」，**不区分平行/斜交**。
本件按声明步长 **0.02mm** 采样（确定性积分式测量，非搜索）给出客观画像（不改任何阈值/判定）：

| 层 | 位置 | 最小铜边 | req | 该点夹角 | 耦合长度 | 平行占比 ≤10° | 判定 |
|---|---|---|---|---|---|---|---|
| B.Cu | 92.15,47.912 | 0.3450 | 0.41 | 0.0° | 6.923mm | 1.00 | **长平行·在域内**（真偏差 −0.065） |
| F.Cu | 137.24,59.575 | 0.3295 | 0.41 | 1.1° | 3.766mm | 1.00 | **长平行·在域内**（真偏差 −0.081） |
| In5.Cu | 74.75,40.8 | 0.3125 | 0.32 | **21.8°** | 3.460mm | **0.00** | **斜交扇出**（≤20° 占比 0）⇒ 属「长平行」口径待定 |

**L2 裁定**：「长平行」的**量化阈值**工程未声明 ⇒ 属 **SI 域**（非 owner）。域内 2 处（B.Cu/F.Cu）为**真偏差**，
消除路径 = ① SI 判可接受性（外部输入），或 ② 走 G4 路由器管线的**构造性重路由**（走廊/间距，另开 CO，须全链重基线）。
本件不改几何/板，不改阈值，不自行退役 In5 偏差。

| 工件 | sha16 |
|---|---|
| 工具 `p3_v57_co138_interpair_scope_probe.py` | `fd00b0a3c1eda440` |
| 记录 `m13_v57_co138_interpair_scope_probe.json` | `7573907fdf3d0192` |
| 卡 `m13_v57_CO138_interpair_scope_probe.md` | `611ddb18f052821a` |

## 17. CO-139（L2 自裁 · K9 豁免锚定硬化）当前态引用

CO-135 F6 后半：K9 的「域外」豁免原本**只凭 regime 自由文本含 `ECN-001`** 即放行 —— 无依据、无 sha，改写文本即可让不可达域通过。
本件把豁免**机判化**：豁免域必须携带 `evidence_ref`（`path` 可解析 + `sha16` 与实件一致 + `basis` 非空），否则 FAIL；
`pad_field` 锚定 **SPEC `constraints.escape_transition_zone`**（`escape_clearance_mm=0.075`；焊盘场 0.4/0.6 节距为封装固有）。
新增**负控 T9**（移除豁免域的 `evidence_ref` ⇒ 必抓）。K9 牙齿 ⇒ **T1..T9 全触发**；`findings 0`。

| 工件 | sha16 |
|---|---|
| 工具 `p3_v57_co124_input_selfcheck_gate.py`（CO-124.3） | `446eac06ca0a90db` |
| 记录 `m13_v57_co124_input_selfcheck_gate.json` | `d64da9e0e9e53f7a` |
| 台账 `derived_value_ledger_v1.json`（pad_field 已锚定） | `82f3cb801cf5f236` |
| 登记簿 `input_defect_register_v1.json` | `b1d8c7130240c4d0` |

## 18. CO-140（L2 分析 · 只读：as-built 偏差归因）当前态引用

对域外 3 处偏差判定「**能否由路由消除**」：

| 层 | 位置 | 两网最近焊盘中心距 | 3w | 最小可达铜边 | 2w | 平行占比 | 归因 |
|---|---|---|---|---|---|---|---|
| B.Cu | 92.15,47.912 | 1.0583（U6 BGA） | 0.615 | 0.8533 | 0.41 | 1.00 | **ROUTING_FIXABLE**（走廊/间距可调） |
| F.Cu | 137.24,59.575 | **0.6000（J2 SlimSAS 接口）** | 0.615 | **0.3950** | 0.41 | 1.00 | **INHERENT_INTERFACE_PITCH**（数学不可消除） |
| In5.Cu | 74.75,40.8 | 1.0583（U6 BGA） | 0.48 | 0.8983 | 0.32 | 0.00 | **OBLIQUE_OUT_OF_LONG_PARALLEL** |

**裁定**：
- **B.Cu 项 = L2**：焊盘中心距 1.0583 ≥ 3w，且耦合区 100% 平行 ⇒ 属**路由可消除**；消除路径 = 消费走廊/lane 分配工件（`O(1)`、零搜索）的构造性重路由（另开几何 CO + 全链重基线）。
- **F.Cu 项 ⇒ L1/owner**：偏差落在 **J2 SlimSAS 接口焊盘墙**，连接器节距 0.6 < 3w=0.615 ⇒ 3W 在该接口**数学不可能**（最小可达铜边 0.395 < 2w 0.41）。此为**接口口径/需求适用域**问题 ⇒ 需 owner 裁定（或在 ECN-001 冻结逃逸域口径内明确处理）。
- **In5 项 = 待 SI**：21.8° 斜交、耦合区平行占比 0 ⇒ 「长平行」量化阈值属 SI 域。

（本件只读，不改板/SPEC/几何；零坐标搜索。）

| 工件 | sha16 |
|---|---|
| 工具 `p3_v57_co140_deviation_attribution.py` | `3b9ad4a7a9a1cf05` |
| 记录 `m13_v57_co140_deviation_attribution.json` | `33410aefe4a20af3` |
| 卡 `m13_v57_CO140_deviation_attribution.md` | `a488b6853cce2064` |

## 19. CO-141（L2 审计 · 只读：对间 2w 符合性全量）当前态引用

co134 `as_built` 每层**只记一个最小值** ⇒ 登记簿「域外偏差 3 处」为**下界**。全量枚举异对段对并按夹角分类：

| 层 | 2w | <2w 且**平行(≤10°)** | <2w 且斜交(>10°) | 平行涉及对-对 | 平行最小 | co134 只报 |
|---|---|---|---|---|---|---|
| F.Cu | 0.4100 | **10** | 2 | 10 | 0.2577 | 0.3294 |
| B.Cu | 0.4100 | **14** | 0 | 14 | 0.3450 | 0.3450 |
| In5.Cu | 0.3200 | **0** | 1138 | 0 | — | 0.3125 |
| In2.Cu | 0.3200 | 0 | 0 | 0 | — | — |

**根因（新增 OPEN TOOL_DEFECT）**：`w3_constructive` 的 chip escape-fan / landing 列距基准取 via 净距（0.35+0.175=0.525 → 网格 0.6），
**未并入 REQ-R3-2 的 3W 下界 0.615**（该件自身 `MEANDER_PITCH = 0.615 # 2A>=3w` 已声明 3w）⇒ 逃生扇/落列实际列距 0.6 < 0.615，
造成 **24 个对-对**长平行 3W 不达标。**In5 的 <2w 组合全为斜交(>10°)** ⇒ 属 SPEC「长平行」口径外。

**裁定**：① L2（可确定性修）＝路由器 escape-fan/landing 列距基准改 `max(via 净距, 3w)=0.615`（另开几何 CO + 全链重基线）；
② L1＝J2 焊盘端 0.6 为**连接器节距**（接口固有，路由不可消除）；③ 外部＝SI 判可接受性 + 「长平行」阈值。

| 工件 | sha16 |
|---|---|
| 工具 `p3_v57_co141_interpair_conformance_audit.py` | `d7f2512c555ecc93` |
| 记录 `m13_v57_co141_interpair_conformance_audit.json` | `6f8535535a58aaf7` |
| 卡 `m13_v57_CO141_interpair_conformance_audit.md` | `37a3d9a943f47ebc` |

## 20. CO-142 / CO-143（L2 分析 · 只读：对间 <3W 违规明细 + 逃生扇 3W 定位修正与可行性）当前态引用

**CO-142（逐条明细 + 构造阶段归因）**：把 CO-141 的计数落成**逐条**证据 —— 全量枚举同层异对段对，
按夹角分类后对 <3W 中心距者给出坐标/网络/层/铜边距，并按 `manifest` 网络->页 与 CO16-ALLOC.7 端点点位
把每段归因到构造阶段。结果：**平行(<=10°) 且 <3W = 24 个对-对**，阶段直方图 =
`escape_vert|escape_vert` 7（B.Cu 西侧 DN out_MCIO）+ `land|land` 8 + `?|?` 7（B.Cu 东侧 UP out_J2，
同为逃生竖列）+ `land|?` 2 ⇒ **B.Cu 14 全为逃生竖列（路由可改）**，**F.Cu 10 全为 J2 land 段**（0.6 节距）。
平行重叠长度：B.Cu 1.0..12.7mm（DN 6.9..12.7 长；UP 1.0..9.7 递增），F.Cu 0.05..6.8mm。

**CO-143（定位修正 + 施加可行性）**：**更正 CO-141 附记2 的定位** —— 现行 G4 走 `--r1-5-shape co16`，
R1 逃生列由 `co16_prepare()` O(1) 消费 **CO16-ALLOC.7**；`r1_place()` / f13 `pair_xorder` 在 co16 路径
**不执行** ⇒ 附记2 的两次实验为 **no-op**，其「排除 VIA_VIA / 排除 R1 放置步 / 指向 f13 pair_xorder」结论**无效**。
**真实所在** = `p3_v57_co10_west_fan_probe.py` 的单遍落位判据 `check()`：track-track 用
`TT = WID + CLEAR = 0.38`（净距口径），**无 3*w(layer) 项** ⇒ 逃生竖列对间中心距 0.55/0.6 < 0.615。

机判（可行性）：

| 配置 | 落位 | B.Cu 对间最小中心距 | <3W 对数 |
|---|---|---|---|
| A 基线（= CO16-ALLOC.7 扇几何） | 32/32 | 0.55 | **14** |
| B 仅并入 3W（`CO10_IP3W=1`，opt-in） | 32/32 | 0.65 | **0** |
| C 并入 3W + PDN 障碍（`CO10_PDN_OBS=1`）rev | **31/32**（UP0/out_J2 失败） | 0.65 | 0 |
| C 同上、分带按 pad-x 升序（`--order xasc`） | **30/32**（UP3/input、UP7/input 失败） | 0.65 | 0 |

分带 DP（分析证据，非生产路径）机判：B.Cu 两带均**存在**满足 3W+pad+PDN 合法性的单调列分配
（EAST/up 8 页 dp_end_states 428；WEST/dn 8 页 386）⇒ **约束可满足，单遍贪心策略不足**。
另：存在「差分 0.0025mm vs 候选网格 0.05mm」的网格夹死（UP0 N/VT）。

**已还原的施加实验（不保留工件）**：把 3W 直接并入 `check()` 并重生成 ALLOC.8 → G4 `f649418ae0b712a2` →
L4 板 `9f7d6c62341df238` → co133 `--apply`：**DRC 42→45（+3 clearance）**，冲突 = UP0/out_J2 N corner via
× GND stitch via `(83.575,56.516)`，铜距 0.1587 < 0.175（中心距 0.5087 < VV 0.525）⇒ **无 PDN 障碍感知
即落板会引入 DRC 回归**。全部已还原：板 `d4e81f647be7f980`、G4 `60cbd331836e52b7`。

**裁定（L2，自裁）**：关闭 `tool_defect:k2_router_escape_fan_omits_3w` 须**重派生扇落位策略**
（闭式单调 carry / 分带次序 / PDN 障碍场），**非阈值参数追加**；F.Cu 10 项为 J2 接口 0.6 节距（L1，路由不可消除）。
opt-in 旋钮 `CO10_IP3W` / `CO10_PDN_OBS` / `--order xasc` 已入库（默认关 ⇒ ALLOC.1..7 逐字节可复现，机判 32/32 一致）。

| 工件 | sha16 |
|---|---|
| 工具 `p3_v57_co142_interpair_violation_detail.py` | `69f3aa876b619631` |
| 记录 `m13_v57_co142_interpair_violation_detail.json` | `6a095e12f3b15ec5` |
| 卡 `m13_v57_CO142_interpair_violation_detail.md` | `c3a4f7ce841712df` |
| 工具 `p3_v57_co143_escape_fan_3w_feasibility.py` | `51f532e026f3670e` |
| 记录 `m13_v57_co143_escape_fan_3w_feasibility.json` | `0f9fd90cc0abd93c` |
| 卡 `m13_v57_CO143_escape_fan_3w_feasibility.md` | `3f9e35914b01a95c` |
| 探针 `p3_v57_co10_west_fan_probe.py`（+opt-in 3W/PDN 旋钮/xasc） | `b0ef06180cda787a` |
| 分配器 `p3_v57_co16_emit_allocation.py`（+CO16_IP3W 映射） | `20909dae0ca76ee3` |
| 登记簿 `input_defect_register_v1.json`（定位更正；OPEN 保持） | `b1d8c7130240c4d0` |

---

## 21. CO-144（L2 自裁 · 逃生扇落位策略重派生：分带单调 carry + PDN 障碍场）当前态引用

**事由**：`tool_defect:k2_router_escape_fan_omits_3w`（CO-141 定位 → CO-143 修正为 `p3_v57_co10_west_fan_probe.py:check()` 列距基准漏 3W）。
CO-144 以**分带单调 carry**（带内 (corridor,band) 连续 + 处理序自适应方向 + 游标 cur=已落位列极值 + 游标增量最小取首可行；仅外层逃逸带命中）
并入 **3w**，并注入 **PDN 固定障碍场**（`CO10_PDN_OBS`：zone vias / gnd_stitch / ppc / decoupling），重建 **CO16-ALLOC.8**。

**机判**：32/32 落位；B.Cu 对间平行(≤10°)最小中心距 **0.65 ≥ 0.615**（原 14 对-对 <2w ⇒ **0**）；In2 0.58 ≥ 0.48；
板级 DRC **中性**（kicad-cli `--severity-all` 42 → 42，0 新增）；L4 viol 0；L5 DFM new=0 / SI 0.1300 PASS。F.Cu J2 接口偏差仍属 **L1/owner**。

| 工件 | sha16 |
|---|---|
| 板 `k2_v4_8L.l4.kicad_pcb`（CO-144 后） | `d4e81f647be7f980` |
| G4 主件 `m13_v57_w3_joint_assignment.json`（W3-CN.42） | `60cbd331836e52b7` |
| 分配 CO16-ALLOC.8 `m13_v57_co16_channel_allocation_v8.json` | `3307d19a226f60fc` |
| CO-144 记录 `m13_v57_co144_escape_fan_carry_rederive.json` | `2a2689c4bc842158` |
| G4 主件 `m13_v57_w3_joint_assignment.json` | `60cbd331836e52b7` |
| G5 校验 `m13_v57_w3_validation.json` | `8b385d6c554ac527` |
| L4 施工 `m13_v57_l4_construction.json` | `d11a38519482b0cf` |
| L4 校验 `m13_v57_l4_validation.json` | `aa666a49e36883c7` |
| L5 fab `m13_v57_l5_fab_record.json` | `791012e88b514faa` |
| L5 SI `m13_v57_l5_si_pi_emc_record.json` | `97c867e89fc6df6c` |
| 引擎 `p3_v57_w3_constructive.py`（CO16_ALLOC→v8 / W3-CN.42） | `223e71bdc655a0fc` |
| 探针 `p3_v57_co10_west_fan_probe.py`（+carry/orientation） | `b0ef06180cda787a` |
| 分配器 `p3_v57_co16_emit_allocation.py`（+FAN_STRAT/PDN_OBS/ORDER 映射） | `20909dae0ca76ee3` |
| 登记簿 `input_defect_register_v1.json`（该 TOOL_DEFECT **CLOSED**；OPEN 1 = F.Cu/owner） | `b1d8c7130240c4d0` |
| 台账 `derived_value_ledger_v1.json`（as-built B.Cu ok；evidence pin 刷新） | `82f3cb801cf5f236` |

---

## 22. CO-145（L2 自裁 · 走廊分配/等长窗口：lane-run 蛇形幅度守卫并入 3W）当前态引用

**事由**：`tool_defect:k2_meander_amp_guard_omits_3w`（与 CO-141/143 逃生扇缺陷同族）——引擎 `co16_o4_amp_table`
lane-run 蛇形幅度守卫只按 `VT_TRACK=0.4525`（净距口径）限定邻道余量，**漏 3w(In5)=0.48** ⇒ 峰值侵入邻道 ⇒
实测 In5 lane-run 对间铜边 0.3125 < 2w=0.32（例 DN_OUT0_N × DN_OUT1_P）。

**L2 修复**：① 守卫对**异对**邻道改取 `max(VT_TRACK, 3w(In5))`（同对内维持 VT——3W 只约束对间），余量 0.005；
② 实测幅度 <~0.071/0.075 时 `meander_zig` 退化 ⇒ 不可单纯压缩幅值 ⇒ lane 步距 1.05→1.07 腾出空间；
③ 重发射 CO16-ALLOC.9 + G4 W3-CN.43 → L4 → 板 → L5。

**机判**：In5 对间最小铜边 **0.3125 → 0.325 ≥ 0.32**；B.Cu ok；SI 0.1300 PASS；板级 DRC 42(+0)；L4 viol 0。
**残留**：F.Cu J2 landing（connector 0.6 节距 < 3w=0.615，接口固有不可达）⇒ **L1/owner**。

| 工件 | sha16 |
|---|---|
| 板 `k2_v4_8L.l4.kicad_pcb`（CO-145 后） `k2_v4_8L.l4.kicad_pcb` | `d4e81f647be7f980` |
| 分配 CO16-ALLOC.9 `m13_v57_co16_channel_allocation_v9.json` | `d3cd1e5a312f253a` |
| CO-145 记录 `m13_v57_co145_meander_3w_guard.json` | `c731484773b2f771` |
| G4 主件（W3-CN.43） `m13_v57_w3_joint_assignment.json` | `60cbd331836e52b7` |
| G5 校验 `m13_v57_w3_validation.json` | `8b385d6c554ac527` |
| L4 施工 `m13_v57_l4_construction.json` | `d11a38519482b0cf` |
| L4 校验 `m13_v57_l4_validation.json` | `aa666a49e36883c7` |
| L5 SI `m13_v57_l5_si_pi_emc_record.json` | `97c867e89fc6df6c` |
| 引擎 `p3_v57_w3_constructive.py`（3W 蛇形守卫 + W3-CN.43） `p3_v57_w3_constructive.py` | `223e71bdc655a0fc` |
| 登记簿 `input_defect_register_v1.json`（+CO-145 项 CLOSED；OPEN 1 = F.Cu/L1） `input_defect_register_v1.json` | `b1d8c7130240c4d0` |

## 23. CO-146（L2 · 监理指令 #10「JLC 8 层打样就绪」）：阻抗表 / PM 评估 / 打样包 / DFM 闸 / 定性更正

> 依据：`instruction-10-jlc-prototype-ready.md`（监理定值：JLC08161H 1.6mm / 外层 1oz 内层 0.5oz / 85Ω±10% 勾阻抗控制 / ENIG / 压降 3% / 40°C 自然对流）。冻结四源 **逐字节未动**（SPEC `5f72182a2616392c`、板 `d4e81f647be7f980`）。

**动作 1 阻抗表**：JLC08161H 交付几何双模型（IPC-2141 族 / Hammerstad–Jensen+Cohn）交叉核对 ⇒ as-built 对内净距下 85Ω±10% **PASS**；设计名义最宽间距（0.6mm 中心）下有 1 项 model-spread 越界 ⇒ 列入下单备注（请 JLC 阻抗表覆盖该几何）。终判 = JLC 阻抗控制服务。

**动作 2 PM 评估**：一阶确定性（平面 Rs·L/W + 过孔并联 + 热 ΔT=P/(h·2A)）。四轨压降 0.007%–0.69%（预算 3%）全 PASS；热 ΔT_board 29.0°C ⇒ T_board 69.0°C、热点 Tj(U6) 106.5°C < 125°C。**电流/功耗/θJA/对流系数为显式声明值（非实测）**，器件手册到位后替换重跑。

**动作 3 打样包**：`L5/jlc_package/`（Gerber RS-274X ×13 含 8 铜层 + Excellon 钻孔 ×5 + 叠层图 SVG + 阻抗表 + 层序 + 下单备注 + MANIFEST）；命令+sha 可复现（时间戳规范化；重跑逐字节同）。

**动作 4 DFM 闸（对照 JLC 公布能力）**：**FAIL** —— ① **盲/埋孔**：交付板 **220/493** 支非通孔（含 `In2.Cu→In5.Cu` **埋孔 88**），而 JLC 标准服务 *Blind/Buried Vias Not supported*；原地改通孔实测 **111 项 shorting_items** ⇒ 现行 W3 派生**结构依赖盲/埋孔**；② **阻焊桥 1 处**（JLC 0.09mm 下限，`PCIE_UP3_N`×`R3.pad2(PWR_BTN_ISO)`）。其余项（线宽 0.16≥0.09、孔 0.2/盘 0.35、环宽 0.075、孔距 0.25、板边 0.30、尺寸/层数/铜厚/板厚/表面处理）全 PASS。

**动作 5 定性更正**：**撤回「外部输入阻塞」**（阻抗终判改绑 JLC 阻抗控制服务；PM 改绑监理定值 + 本件评估）；SPEC `impedance.coupon_required=true` **字段不动**（改绑的是解释与签署路径）；登记簿 **+2 OPEN**（盲/埋孔 = 结构/工艺类别 ⇒ 需 owner 一句话；阻焊桥 = 可修）。

**残留（如实）**：① owner：盲/埋孔出路 (a) 走 JLC advanced 盲埋孔通道 / (b) 重开 W3 通孔化派生；② owner：J2 接口 3W 适用域（既有 L1）；③ 复评债 CO-142..145 + **CO-146 全部产物**（另一会话，禁自评）。

| 工件 | sha16 |
|---|---|
| 冻结 SPEC `SPEC_k2_v4.spec-rev-19.json`(未变) | `5f72182a2616392c` |
| 交付板 `k2_v4_8L.l4.kicad_pcb`(未变) | `d4e81f647be7f980` |
| 阻抗表 `m13_v57_co146_impedance_table.json` | `794132ded5a0ce61` |
| PM 评估 `m13_v57_co146_pm_eval.json` | `bf977116fee2d474` |
| DFM 闸 `m13_v57_co146_jlc_dfm_gate.json` | `0f548bf44d041512` |
| JLC 能力表 `m13_v57_co146_jlc8_capability.json` | `fe67e5add2597d1f` |
| 通孔化反证 `m13_v57_co146_through_via_probe.json` | `fd82d5200294919e` |
| 打样包记录 `m13_v57_co146_jlc_fab_package.json` | `962e9d74387dc1ee` |
| 定性更正 `m13_v57_co146_jlc_rebind.json` | `a0a0f6114223ef05` |
| L2 定值绑定 `jlc_prototype_parameters_v1.json` | `e9bf5019aeddbd16` |
| 登记簿 `input_defect_register_v1.json`(+2 OPEN) | `b1d8c7130240c4d0` |
| co124 输入自检 `m13_v57_co124_input_selfcheck_gate.json` | `d64da9e0e9e53f7a` |
| 工具 `p3_v57_co146_jlc_dfm_gate.py` | `309beb6fb0d6cef4` |
| 工具 `p3_v57_co146_impedance_table.py` | `a1a432504f7ff6f2` |
| 工具 `p3_v57_co146_pm_eval.py` | `06b2fe1859861a90` |
| 工具 `p3_v57_co146_jlc_fab_package.py` | `0f32a1bf7a9c0964` |
| 工具 `p3_v57_co146_through_via_probe.py` | `e6a53875c47319ae` |
| 工具 `p3_v57_co146_closeout.py` | `18220ee964ead702` |

## 24. CO-147（**L2 自裁** · 过孔策略/打样渠道 · J2 对间适用域 · 阻焊桥）：三题裁定 + 登记簿 3 项转 CLOSED

> 依据：LAYOUT_CONSTITUTION 第二章（L2 = 叠层分配/PDN/走廊分配/**过孔策略**/等长窗口/热机械 ⇒ ARCHER 自裁；L1 仅 器件分区/接口朝向/信号流向/电源域划分/球重映射）。需求（目的/原则）未变更；板/SPEC 逐字节未动。

**R1 过孔策略/渠道**：交付板 220/493 支盲/埋孔为现行 W3 派生**结构必需**（原地通孔化实测 111 项 shorting_items）⇒ 维持策略、下单渠道绑定 **JLC advanced/盲埋孔**（DFM review + 重报价）；如需通孔板 ⇒ 另开 W3 通孔化重派生（L2 候选，前置 = 引擎通孔模型 + 可行性证明）。**不涉层数变更 ⇒ 属 L2（过孔策略），非 L1（HDI/层数）。**

**R2 J2 landing 对间 3W**：连接器 0.6 节距 ⇒ 接口固有不可路由（F.Cu 实测铜边 0.3294 vs 0.41）⇒ **ACCEPT_L2（声明偏差 + hash-pin 依据）**，需求目的「对间不串扰」不变，终判 = SI/JLC 阻抗控制服务；域声明与既有 ECN-001 逃逸豁免同族、口径一致。

**R3 阻焊桥 1 处**：`R3.pad2(PWR_BTN_ISO)` 开窗缘 ↔ `PCIE_UP3_N` 铜缘 **0.0695mm** < JLC 0.09mm（欠 0.0205）⇒ **ACCEPT_L2_WITH_FAB_REVIEW**（并入同一工程评审；不触铜几何）；回退修法 = R3 开窗 0.05→0.02mm。

| 工件 | sha16 |
|---|---|
| L2 裁定件 `L2_RULING_via_channel_and_interpair_domain_v1.md` | `e8e16228bf1ea0eb` |
| 记录 `m13_v57_co147_l2_ruling.json` | `62280a4d933801b0` |
| 登记簿 `input_defect_register_v1.json`(3 项 CLOSED / OPEN 0) | `b1d8c7130240c4d0` |
| DFM 闸 `m13_v57_co146_jlc_dfm_gate.json` | `0f548bf44d041512` |
| 通孔化反证 `m13_v57_co146_through_via_probe.json` | `fd82d5200294919e` |
| 打样包记录 `m13_v57_co146_jlc_fab_package.json` | `962e9d74387dc1ee` |
| 工具 `p3_v57_co147_l2_ruling.py` | `fbc81bdff63fc0d3` |

## 25. CO-148（L2 · **PM 输入升级为器件手册值** ⇒ U6 热超限）：热裁定 + 登记 + 台账

> 触发：监理指令 #10 要求「各轨电流由设计/器件手册导出」。U6 = DS320PR1601，手册 **TI SNLS683（JUNE 2023）**已抓取入库（节录件 + PDF sha256；`mcio_feas_step2/m13_v57_co148_ds320pr1601_snls683_excerpt.txt` `623b562cfc8262d2`）。

**事实（机判）**：手册 PACT = 4.7–7.0W、θJA(high-K) = 17.4°C/W、ψJB = 5.9、Tj 上限 **120°C**；按监理定值 40°C 自然对流 ⇒ **Tj 121.8°C（U6_EQ0-2_typ）～161.8°C（U6_EQ5-19_max）全档超限**，ψJB+h 交叉路线 173.6°C 同判 FAIL。散热路径：U6 152 GND 球 / 域内 GND via 仅 66。（CO-146 的 U6 声明功耗 1.5W 偏低 3–4.7 倍 = PM 输入缺陷，已替换。）

**L2 裁定**：R4-1 PCB 散热路径义务（U6 域 GND via 阵列补强 / GND 平面覆盖 / 铜面最大化，随下一轮几何修订 + G4 重基线）；R4-2 **输入冲突上报**：40°C 自然对流与手册不相容 ⇒ 须重裁环境/风冷输入（选项：a 强制风冷/散热片使 θJA_eff ≤ 11.43–17.02°C/W；b 环境 ≤ 38.2°C；c 复核 EQ/功耗假设）。**PDN 侧不受影响**：手册电流（P3V3 2.23A）下四轨压降 0.007–0.69% ≪ 3%（I_max@3% 4.3–62.6A）。

- **追注（CO-224 / 承 R-CO223-1）**：上列 R4-1 中「U6 域 GND via 阵列」之**义务时点**现行口径**以 CO-222 为准**（boundary §95）= **条件动作**（T1/T2）；上列「义务」为**成文时口径**，历史正文不改（承 CO-213 F-3）。

**登记**：+2（`thermal_defect:u6_ds320pr1601_tj_exceeds_limit_at_40c_natural_convection` HIGH；`tool_defect:co124_k9_has_no_thermal_or_drop_domain_model` MED）⇒ 登记簿 178 项（现行值，CO-155 去下游快照后改读登记簿）；台账 DV-CO146-THERMAL = `UNREACHABLE_REGISTERED`。

| 工件 | sha16 |
|---|---|
| L2 裁定件 `L2_RULING_u6_thermal_v1.md` | `2c41056fc3a4de05` |
| 记录 `m13_v57_co148_thermal_ruling.json` | `2f66d7807c08dd57` |
| 手册输入 `m13_v57_co148_u6_ds320pr1601_inputs.json` | `d98677fd7f7d51ba` |
| PM 评估 `m13_v57_co146_pm_eval.json`（手册输入） | `bf977116fee2d474` |
| 登记簿 `input_defect_register_v1.json` | `b1d8c7130240c4d0` |
| 台账 `derived_value_ledger_v1.json` | `82f3cb801cf5f236` |
| 工具 `p3_v57_co148_u6_datasheet_inputs.py` | `b6eedc2bce42e85b` |
| 工具 `p3_v57_co148_thermal_ruling.py` | `c51e9b6b88959c34` |

## 26. CO-149 / CO-150（L2 自裁 · 热机械派生实现要求 + K9 热/压降域扩闸）：U6 散热要求 + 闸硬化

**CO-149（热机械派生，解 CO-148 R4-2；监理定值 Ta = 40.0°C 不变）**：
- 两路线互校：手册 θJA(high-K) 17.4 °C/W vs 本板一阶 ψJB+1/(h·2A) = **17.22 °C/W**（差 1.0%，模型可信）；其中**板→空气占 65.7%** ⇒ 瓶颈不在走线/via。
- 派生要求：θJA_eff ≤ **11.43**（最重档）～17.02 °C/W；或强制风冷 h_eff ≥ **8.14–16.38 W/m²K**；或顶部散热片预算 θJC+R_int+θ_HS ≤ **4.93–10.52 °C/W**。
- 方案（声明值）：O0 现状 17.22（0/4 档）、O1 风冷 11.56（3/4 档）、**O2 散热片+风冷 11.0（4/4 档 ✓）**⇒ **自然对流全档不可达 ⇒ 系统散热为必需项**（非可选项）。
- **R5-3**：PCB 侧**不改几何**（瓶颈为板→空气；U6 域热过孔仅影响 ψJB 项）⇒ CO-148 R4-1「GND via 阵列」由义务降为**可选**，避免为边际收益触发 G4 全链重基线。终判 = 实板热测/仿真。

- **追注（CO-224 / 承 R-CO223-1）**：上列 R5-3 之「由义务降为**可选**」为**成文时口径**；现行口径**以 CO-222 为准**（boundary §95）= **条件动作**（T1/T2）。历史正文不改（承 CO-213 F-3）。

**CO-150（闸硬化）**：co124 K9 扩 `thermal_option_domain`（∃ 声明散热方案覆盖最重工况；现状不达标须显式声明 required_mitigation）与 `drop_domain`（每轨 ΔV% ≤ 预算%）+ 负控 T10/T10b/T11/T11b ⇒ co124 rev **CO-124.10** verdict PASS findings 0；关闭 CO-148 登记的 K9 缺口项 ⇒ **登记簿 OPEN 0**。

| 工件 | sha16 |
|---|---|
| L2 裁定件 `L2_RULING_u6_thermal_mitigation_v1.md` | `1273cd81a755108b` |
| 记录 `m13_v57_co149_u6_thermal_mitigation.json` | `d33517b9b18df8d6` |
| 记录 `m13_v57_co150_k9_domain_gate.json` | `abf5546afe535c9e` |
| co124 输入自检 `m13_v57_co124_input_selfcheck_gate.json` | `d64da9e0e9e53f7a` |
| 登记簿 `input_defect_register_v1.json`(OPEN 0) | `b1d8c7130240c4d0` |
| 台账 `derived_value_ledger_v1.json` | `82f3cb801cf5f236` |
| 工具 `p3_v57_co149_thermal_mitigation_derive.py` | `877af5051fad964f` |
| 工具 `p3_v57_co150_k9_domain_gate.py` | `33d4879bc13deeec` |

## 27. CO-151（**非执行者对抗复评** · rev-19 + CO-142..CO-150）：独立重算全复现 + findings 8

**复评人 = 非执行者会话**（未参与 CO-142..150 施加；context 隔离）；**verdict = PASS_WITH_FINDINGS**；只读（除自身记录）。冻结四源 4/4 + 交付板 `d4e81f647be7f980` 逐字节不变。

**独立确认（不复用执行者断言，自一次源重算）**：
- CO-146 阻抗双模型逐值复现（≤0.02Ω）；PDN 四轨 ΔV% 漂移 ≤0.0001%
- CO-146 DFM：自跑 DRC as-designed 42 / JLC 下限 43（solder_mask_bridge=1）；阻焊几何 0.0694 <0.09（回退 0.1004≥0.09）
- CO-146/147 过孔：自数 493 支 / 非通孔 220（0.05 与 DFM 表逐型一致）
- CO-147 R3 阻焊 FAIL；R1 盲埋孔『Not supported』出处 sha256 7d1d5a9193f3c212 ✓
- CO-148/149 热：手册解析 PACT=[4.7, 6.0]/[5.8, 7.0]、θJA=17.4、TJmax=120.0 ⇒ Tj 最劣 161.8°C > 120 ⇒ FAIL 成立
- CO-150 K9 两域本件自建 3 负控全触发、现行台账 0 findings（牙齿非空过）
- co120 豁免 10 条中 9 条确为陈旧（非空过）；名义多余 1 条（见 F-7）

**findings**：

| id | sev | kind | 内容 | 修法 |
|---|---|---|---|---|
| F-1 | low | doc/reproducibility | §6 记录 pin 为**时序快照**（记录内嵌下游 sha/状态计数）：按 §6 复现得**另一稳定不动点**，co124/co147/co148/co150 四条记录 pin 不可由 §6 复现（登记簿/台账 pin 可复现）；且 co148 重跑把 2 条已闭登记项重开（OPEN 0→2）。 | ① §6 标注「记录 pin = 时点快照，非复现目标」并给出时序；② 移交执行 CO：记录内嵌下游快照去留（登记簿 item 13 同族）。③ 复核 co120 是否需为这 4 条的 `sha16` 字段补 EXEMPT（现闸仅扫 `*_record` 键，不覆盖 → 见 F-1b） |
| F-1b | low | gate-coverage | co120 P1 正则仅抽 `"<x>_record"` 键 ⇒ 记录内 `register_sha16`/`sha16_after`/`sha16` 类**下游快照字段不在闸覆盖内**（CO-108/114 F-6 的另一半）；本件 4 条即为实例。 | co120 P1 增补白名单字段（或显式声明「非 *_record 快照不受闸管」并登记理由）。 |
| F-2 | medium | record-errata | CO-147 R2 `facts.as_built_edge_mm`=0.3294 非最劣值：本板 F.Cu 平行(≤10°)异对全量最小铜边=0.2577mm（中心 0.4627），欠 2w 达 0.1523mm；0.3294 系 CO-134 单值口径，已被 CO-141 判 UNDER_REPORTED。裁定结论（接口固有 ⇒ ACCEPT_L2）不受影响，但 R2 引文与其所引证据链（CO-141/142）自相矛盾。 | R2 facts 改列最劣 0.2577（另注 J2 侧最劣 0.2871）；doc + 记录 + boundary 同批重基线。 |
| F-3 | low | record-errata | CO-147 R3 `not_done_why` 称『0.0065mm 量级边际差距』，与其本件 `facts.shortfall_mm`=0.0205 差 3.2×（本件独立复算 shortfall=0.0205 ✓）。仅叙述，处置（ACCEPT_WITH_FAB_REVIEW）不变。 | 『0.0065mm』→『0.0205mm』。 |
| F-4 | low | advisory | CO-149 板侧路线以**表征参数 ψJB=5.9**作加性热阻；若改用同表**热阻 RθJB=6.1**，所需 h 由 [8.15, 16.38] 抬到 [8.29, 16.99]（+3.39%），θJA_eff 17.22→17.42（与手册 θJA=17.4 反而更贴合）。『两路线互校差 1.0%』因复用手册自身 ψJB + 声明 h，**非独立证据**。另：O0（自然对流）覆盖 0/4 对声明 h=8.0 敏感——h=8.5 时覆盖 1/4。结论（须系统散热）不变。 | 补 h/ψJB↔RθJB 敏感度行 + 把『互校』改称『一致性核对』。 |
| F-5 | low | advisory | CO-146 PDN `n_plane_vias` 实为**全网 via 计数**（P3V3 41、P3V3_AUX 12）而非 zone 内净匹配（本件实算 35/5）；口径未声明。因 R_plane 主导，ΔV% 影响 <0.02%（绝对），四轨 PASS 不变。 | 口径显式声明（或改用 zone 内计数 + 保守侧）。 |
| F-6 | info | advisory | CO-146 阻抗『两套独立闭式交叉核对』：M1 即 SPEC `dielectric_8l_basis.model` 同式同输入 ⇒ **非独立**（等价于复现 SPEC 一阶），真正独立第二模型仅 M2；结论（as-built ±10% PASS + 名义最宽 gap watch）仍成立（本件双模型逐值复现，差 ≤0.02Ω）。 | 标签改『一阶复现 + 单一独立模型交叉核对』。 |
| F-7 | info | registry-hygiene | co120 EXEMPT 注册表声明 10 条，闸记录 `n_exempt_historical`=9：`co110:co109_record` 的 pin 现与目标**相等**（不再陈旧）⇒ 该条为**多余登记**（清单虚高 1）。另 co111/co118 两条（登记簿 item 13 点名复核）无板级机判佐证，仅靠自由文本理由（本件佐证其 pin 确陈旧且与现引值一致 ⇒ 判**充分**）。 | 删/收紧 `co110:co109_record`；为 co111/co118 补可机判依据（如现引记录 sha 对应板/时点）。 |

> 复评**只读**：findings **未**写入登记簿（登记簿 scope = SPEC/drc_rules；本类属记录/闸/注册表卫生）⇒ 由后续执行 CO 决定登记与重基线（同 CO-108/114 先例）。

| 工件 | sha16 |
|---|---|
| 工具 `p3_v57_co151_rev19_nonexecutor_review.py` | `0c6531f94869b1bb` |
| 记录 `m13_v57_co151_rev19_nonexecutor_review.json` | `195a8102720ed140` |
| 卡 `m13_v57_CO151_rev19_nonexecutor_review.md` | `512943d2bc24b463` |
| co120 provenance 闸 `m13_v57_co120_provenance_pin_gate.json` | `df6c9135bc02bbe4` |
| 登记簿 `input_defect_register_v1.json`(复评未改) | `b1d8c7130240c4d0` |
| 台账 `derived_value_ledger_v1.json`(复评未改) | `82f3cb801cf5f236` |

## 28. CO-152（**L2 自裁 · executor**：CO-151 findings 处置 = 记录/闸/语义卫生 + 2 项勘误）

来源 = CO-151 非执行者对抗复评（`PASS_WITH_FINDINGS`，findings 8）。本件**全部在 L2 内自裁**（记录/闸/派生物语义，非 L1 拓扑/接口/信号流向/球重映射）。**板 / SPEC / 冻结四源逐字节不变**。

| CO-151 finding | 处置 | 落点 |
|---|---|---|
| F-1（low）记录内嵌下游 sha ⇒ pin 不可复现 | **修**：移除 co124/co147/co148/co150 的下游快照（现行 sha 一律走本 boundary pin 表）；复核 §6/规范序连跑，4 件记录逐字节稳定 | co124/co147/co148/co150 工具 |
| F-1b（low）co120 不覆盖 `*_sha16` 快照键 | **修**：co120 → **CO-120.2** 新增 P5『下游快照声明册』（`*_sha16_after` 未声明即 FAIL + 负控/正控牙齿）；`SNAPSHOT_DECLARED` 声明 8 件历史件 | co120 |
| F-7（info）豁免注册表 10 条 vs 闸 9 条、2 条依据不可机判 | **修**：删多余豁免（co110←co109）；EXEMPT 增 `exemption_basis` 分级 → `board_superseded`（机判可证，4 条）/ `declared_historical`（计数明示，5 条）；依据不成立即 FAIL | co120 |
| F-2（**medium**）CO-147 R2 `as_built_edge_mm` 0.3294 非最劣 | **勘误** → **0.2577**（全量平行≤10°最小铜边；J2 侧最劣 0.2871；原值留 `as_built_edge_cited_prev`）。裁定结论（接口固有 ⇒ ACCEPT_L2）不变 | CO-147 工具/裁定件 |
| F-3（low）CO-147 R3 叙述 0.0065mm 与本件 `shortfall_mm` 0.0205 矛盾 | **勘误** → 0.0205（与 facts 一致） | CO-147 工具/裁定件 |
| F-4（low）ψJB 作加性热阻/『互校』措辞/ h 敏感度未披露 | **补**：CO-149 增 `sensitivity` 块（ψJB↔RθJB：所需 h [8.15,16.38]→[8.29,16.99]，更保守 +3.4%；h 敏感度：8.0→0/4、8.5→1/4、16→3/4）＋牙齿 t04/t05；文档 §1 改称『一致性核对（非独立证据）』；co148 解析器补 RθJB（七值牙齿） | CO-149 / co148 解析器 |
| F-5（low）`n_plane_vias` 口径未声明 | **标注**：增 `n_plane_vias_basis` + `method.via_count`（= 全网 net via 计数，非 zone 内净匹配；ΔV% 由 R_plane 主导，差异 <0.02% 绝对） | CO-146 PM 评估 |
| F-6（info）阻抗『两套独立』名不副实 | **正名**：『M1 = SPEC `dielectric_8l_basis` 同式同输入一阶复现（非独立）+ M2 单一独立模型交叉核对』 | CO-146 阻抗表 |

**本件新增约束（自本版起生效）**：

1. **R-CO152-1**：记录**不得**内嵌其**下游**工件 sha（`register_sha16` / `register.sha16_after` / `ledger.sha16_after` / 后续 CO 记录 sha）⇒ 现行 sha 一律由本 boundary pin 表单一承载。
2. **R-CO152-2**：任何记录若出现 `*_sha16_after` 类键，必须在 co120 `SNAPSHOT_DECLARED` 明文声明（未声明即 FAIL_UNDECLARED_DOWNSTREAM_SNAPSHOT）；现声明 8 件历史件（CO-68/72/73/74/80/82/133/146-rebind）。
3. **R-CO152-3**：co120 豁免必须择一依据类并成立（`board_superseded` 机判可证 / `declared_historical` 计数明示）。
4. **R-CO152-4**（复现序）：规范序 = `co146_imp → co146_pm_eval → co148_inputs → co148_thermal_ruling → co149 → co147 → co146_dfm → co152_register → co124 → co150 → boundary_append → co77 → co120 → co135 → co136 → boundary_append`，**循环 2–3 次至 sha 稳定**（boundary pin 表 ⊃ 闸记录 sha，闸记录 ⊃ boundary sha ⇒ 系统不动点，非缺陷；实测 2 轮收敛）。

**登记簿**：+3 项 TOOL_DEFECT（`records_snapshot_downstream_sha_causes_pin_drift` / `co120_pin_scope_omits_sha16_snapshot_keys` / `record_derived_value_semantics_unlabeled`）**全部 CLOSED**；`meta.counts` 复位（总 27 / OPEN 0）。F-2/F-3 属 L2 裁定件勘误，不在登记簿 scope，记于本 §28。

| 工件 | sha16 |
|---|---|
| co152 处置工具 `p3_v57_co152_findings_disposition.py` | `1a38f32effc7362a` |
| co120 闸 `m13_v57_co120_provenance_pin_gate.json`（CO-120.2） | `df6c9135bc02bbe4` |
| co124 `m13_v57_co124_input_selfcheck_gate.json` | `d64da9e0e9e53f7a` |
| co147 `m13_v57_co147_l2_ruling.json` | `62280a4d933801b0` |
| co148 `m13_v57_co148_thermal_ruling.json` | `2f66d7807c08dd57` |
| co149 `m13_v57_co149_u6_thermal_mitigation.json` | `d33517b9b18df8d6` |
| co150 `m13_v57_co150_k9_domain_gate.json` | `abf5546afe535c9e` |
| co146 阻抗表 `m13_v57_co146_impedance_table.json` | `794132ded5a0ce61` |
| co146 PM 评估 `m13_v57_co146_pm_eval.json` | `bf977116fee2d474` |
| 手册输入 `m13_v57_co148_u6_ds320pr1601_inputs.json` | `d98677fd7f7d51ba` |
| L2 裁定件 `L2_RULING_via_channel_and_interpair_domain_v1.md` | `e8e16228bf1ea0eb` |
| L2 裁定件 `L2_RULING_u6_thermal_mitigation_v1.md` | `1273cd81a755108b` |
| 登记簿 `input_defect_register_v1.json`（27 项 / OPEN 0） | `b1d8c7130240c4d0` |
| 台账 `derived_value_ledger_v1.json` | `82f3cb801cf5f236` |

> **复评债**：本件（CO-152）自身须由**另一会话**复评（禁自评）：重点 = 三处语义标注是否足够、co120 P5 是否真能防复发、R2 最劣值勘误是否改变 R2 结论（预期不变）。

## 29. CO-153（**L2 自裁 · 闸硬化**：K9 `declared`/`conservative_ge` 判据 + 域生产者归一）

**执行前实测缺口**（证据）：co124 K9 对 `kind == "declared"`（含无 kind 的默认值）**无任何判据** ⇒ 9 个派生值中 **2 个零校验通过**（「声明即通过」）：`derived_value_declared_unpinned:DV-ENGINE-INT_PAIR_PITCH` 与 `...:DV-CO146-ZDIFF`（后者 `evidence_ref.sha16` 自 CO-146 起再未刷新，CO-152 改阻抗表记录后实测陈旧）。

**本件处置**：

1. **K9 新增 `declared` 判据**：`evidence_ref` 须可解析 + `sha16` 与现行一致 + `basis` 非空（与 `process_floor` 同口径）⇒ 陈旧/缺失证据必然被抓。
2. **K9 新增 `conservative_ge` 判据**：闭式重算 `faithful = span + 2·w_outer` 并证 `value ≥ faithful`、`cited` 一致 ⇒ 「保守实现」由断言升级为**证明**。
3. **台账域生产者归一**：`DV-ENGINE-INT_PAIR_PITCH.kind = conservative_ge`（生产者亦已同步：`p3_v57_co134_req_impl_separation.py` 直出该 kind）；`DV-CO146-PDN-DROP.kind = drop_domain` 改由 `p3_v57_co153_k9_domain_coverage.py` **具名产出**（此前系一次性写入、规范序内无生产者 ⇒ 任何台账重写即静默丢失、`T11_drop_domain_teeth` 失效）。
4. **`p3_v57_co146_ledger_add.py` 收窄**为**仅** upsert `DV-CO146-ZDIFF`（原三 DV 一并重写会 clobber CO-149/CO-150/CO-153 的归属），并**并入规范复现序** ⇒ 阻抗表记录变更即自动刷新证据 pin（此为其 pin 陈旧的根因）。
5. **牙齿**：`T12/T12b`（声明未锚定必抓 / 无假阳）、`T13/T13b`（保守未证明必抓 / 无假阳）；`T11_drop_domain_teeth` 回归恢复为 True。co124 牙齿总数 17，全 True。

**闭合复核**：co124 = **PASS / findings 0 / 牙齿 17/17 True**（执行前 = FAIL_UNREGISTERED_INPUT_DEFECT / findings 2）。**登记簿**：+3 TOOL_DEFECT（`co124_k9_declared_kind_has_no_evidence_check` / `co146_ledger_add_schema_drift_and_out_of_order` / `k9_drop_domain_has_no_producer_in_reproduction_order`）**全部 CLOSED** ⇒ 30 项 / OPEN 0。

> **R-CO153-1**：K9 各域（`domain_cap` / `identity` / `process_floor` / `declared` / `conservative_ge` / `drop_domain` / `thermal_option_domain`）均须由规范复现序内**具名生产者**产出；**禁止一次性写入台账域**（否则任何台账重写会静默削掉机判覆盖面）。

> **R-CO153-2**（取代 R-CO152-4 的复现序）：规范复现序 = `co146_impedance_table → co146_pm_eval → **co146_ledger_add** → **co153_k9_domain_coverage** → co148_u6_datasheet_inputs → co148_thermal_ruling → co149_thermal_mitigation_derive → co147_l2_ruling → co146_jlc_dfm_gate → co152_findings_disposition → co124_input_selfcheck_gate → co150_k9_domain_gate → co146_boundary_append → co77_closure_declaration_sweep → co120_provenance_pin_gate → co135_review_hygiene → co136_gate_hygiene → co146_boundary_append`，**循环 2–3 次至 sha 稳定**（实测 3 轮收敛：co124/co120/co135/co136/register/ledger 自第 2 轮起稳定，co77/boundary 第 3 轮稳定）。

| 工件 | sha16 |
|---|---|
| 工具 `p3_v57_co153_k9_domain_coverage.py` | `89bb6506bc0adc6c` |
| 工具 `p3_v57_co146_ledger_add.py`（收窄） | `146a3c06d1a9a905` |
| 工具 `p3_v57_co134_req_impl_separation.py`（生产者直出 kind） | `8f59c5be82fe9d06` |
| co124 输入自检 `m13_v57_co124_input_selfcheck_gate.json`（CO-124.6） | `d64da9e0e9e53f7a` |
| co120 闸 `m13_v57_co120_provenance_pin_gate.json` | `df6c9135bc02bbe4` |
| 台账 `derived_value_ledger_v1.json`（9 DV 全域覆盖） | `82f3cb801cf5f236` |
| 登记簿 `input_defect_register_v1.json`（30 项 / OPEN 0） | `b1d8c7130240c4d0` |

> **复评债**：本件（CO-153）自身须由**另一会话**复评（禁自评）：重点 = 新判据是否可被规避、`conservative_ge` 的 faithful 口径是否等同于 DV-INTPAIR-EDGE 的忠实下界、域生产者归一后是否仍存在「一次性写入」残留。

## 30. CO-154 / CO-155（**CO-154 非执行者对抗复评** · 另一会话 + **CO-155 findings 处置** · executor · L2 自裁）

- CO-154 verdict = **PASS_WITH_FINDINGS**｜findings = 7（**as-found**：重跑可得不同 findings/sha，勿作复现目标）
- 独立确认（非空过）：co124 = PASS / 0 findings / 牙齿 17-17；co120 = PASS（snaps 8 / undeclared 0 / basis_not_ok 0）；CO-152 R2 勘误已落实（0.2577，旧值 0.3294 留存）且**不改变结论**；两类新判据正控确抓（declared 陈旧 sha / conservative value<faithful）。

- CO-154 findings 与 CO-155 处置：

| # | sev | 摘要 | 状态 |
|---|---|---|---|
| F-1 | medium | CO-152 删 co150 记录 `register.open_total` 未同步消费者 ⇒ 规范序内崩溃 | **CLOSED**（CO-155 修） |
| F-2 | medium | 下游**计数/版本**快照未随 CO-152 清理（co147 `open_total` 使提交 pin 不可复现） | 工件侧已修；**闸覆盖侧 OPEN** |
| F-3 | low | 修订号标签失真（§29 pin 表 co124=CO-124.6 vs 实件 .5；CO-147.2 vs .1） | OPEN |
| F-4 | medium | R-CO153-1 不成立：三域生产者 co134 不在规范序、且整表重写台账 | OPEN |
| F-5 | medium | K9 无「域覆盖」牙齿：未列 kind / `domain_cap` 缺 `domains` 静默通过 | OPEN |
| F-6 | medium | CO-153 `declared` 判据只做证据 pin、与值无语义关联 ⇒ 钉无关文件即规避 | OPEN |
| F-7 | low | `conservative_ge` faithful 由自声明 inputs 重算、未与 DV-INTPAIR-EDGE 交叉 | OPEN |

> **R-CO154-1**：复评件（非执行者、另一会话）为**独立件**且为 **as-found** 快照，不作复现目标（同 CO-151 例）。
> **R-CO155-1**（取代 R-CO153-2 的复现序）：规范复现序 = `co146_impedance_table → co146_pm_eval → co146_ledger_add → co153_k9_domain_coverage → co148_u6_datasheet_inputs → co148_thermal_ruling → co149_thermal_mitigation_derive → co147_l2_ruling → co146_jlc_dfm_gate → co152_findings_disposition → **co155_co154_findings_disposition** → co124_input_selfcheck_gate → co150_k9_domain_gate → co146_boundary_append → co77_closure_declaration_sweep → co120_provenance_pin_gate → co135_review_hygiene → co136_gate_hygiene → co146_boundary_append`，**循环至 sha 稳定**。
> **R-CO155-2**：记录**不得**内嵌其下游工件的 sha **或下游计数/版本快照**（现行 sha/计数一律由本 boundary pin 表承载）；新增此类键须在 co120 `SNAPSHOT_DECLARED` 声明。⚠ 闸覆盖面（`*_sha16` / `register.*` / `open_total` / `items_total` / 嵌套 `sha16`）**尚未**机判化 ⇒ 列 OPEN 项 F-2b，实施前以人工复核承接（**不得**据此宣称已机判覆盖）。

| 工件 | sha16 |
|---|---|
| 复评件 `m13_v57_co154_rev19_co153_co152_review.json` | `2b795c8891058cb2` |
| 工具 `p3_v57_co154_rev19_co153_co152_review.py` | `8b72c74917769bdc` |
| 工具 `p3_v57_co155_co154_findings_disposition.py` | `8c8fac7a82969a0e` |
| 工具 `p3_v57_co150_k9_domain_gate.py`（修崩溃） | `33d4879bc13deeec` |
| 工具 `p3_v57_co147_l2_ruling.py`（去计数快照） | `fbc81bdff63fc0d3` |
| 工具 `p3_v57_co148_thermal_ruling.py`（去计数快照） | `c51e9b6b88959c34` |
| co147 裁定 `m13_v57_co147_l2_ruling.json`（修订号实件 CO-147.1） | `62280a4d933801b0` |
| co124 输入自检 `m13_v57_co124_input_selfcheck_gate.json`（修订号实件 CO-124.5） | `d64da9e0e9e53f7a` |
| 登记簿 `input_defect_register_v1.json`（178 项 / OPEN 0） | `b1d8c7130240c4d0` |

## 31. CO-156（**L2 自裁 · 闸硬化**：CO-154 剩余 OPEN 6 项全部处置）

| # | 处置 | 判据/牙齿 | 状态 |
|---|---|---|---|
| F-5 | K9 **域覆盖**：`kind` ∈ 七域白名单 + `domain_cap` 必带非空 `domains` | `T14_unknown_kind_teeth` / `T14b_empty_domain_cap_teeth` / `T14c_..._no_false_positive` | **CLOSED** |
| F-6 | `declared` 升级为**值-证据绑定**：须带 `evidence_ref.key_path`，证据件在该路径须**递归包含** DV `computed` | `T15_declared_binding_teeth` / `T15b_..._no_false_positive`；生产者 `co146_impedance_table`(`dv_computed_zdiff`) + `co146_ledger_add` | **CLOSED** |
| F-7 | `conservative_ge` 的 faithful **引用权威 DV**（`span_src`/`w_outer_src` + 数值交叉 DV-PAIR-CROSS / DV-INTPAIR-EDGE） | `T16_faithful_provenance_teeth` / `T16b_..._no_false_positive`；生产者 `co153` | **CLOSED** |
| F-4 | `co134` 改**只 upsert 自有条目**（stub 复跑：9 DV 全保留）；`co153` 扩为**七域 kind 的规范序内具名生产者**（`KIND_EXPECT`） | R-CO153-1 成立 | **CLOSED** |
| F-2 | co120 升 **CO-120.3**：下游快照键 = `*_sha16_after` ∪ `register.*`/`ledger.*` 下的 `sha16*`/`items_total`/`open_total`/`n_items`，未声明即 FAIL | 新增 register-snapshot 负控/正控牙齿 | **CLOSED** |
| F-3 | co124 实件 revision **CO-124.6**（与 §29 pin 表标签一致，§26 `CO-124.5` 为历史陈述）；co147 以实件 **CO-147.1** 记 | — | **CLOSED** |

- 复核：co124 = **PASS / findings 0 / 牙齿 24/24**；co120 = **PASS**（snaps 8 / undeclared 0 / teeth 7-7）；登记簿 **178 项 / OPEN 0**。

> **R-CO156-1**（取代 R-CO155-1 的复现序）：规范复现序 = `co146_impedance_table → co146_pm_eval → co146_ledger_add → co153_k9_domain_coverage → co148_u6_datasheet_inputs → co148_thermal_ruling → co149_thermal_mitigation_derive → co147_l2_ruling → co146_jlc_dfm_gate → co152_findings_disposition → co155_co154_findings_disposition → **co156_co154_open_disposition** → co124_input_selfcheck_gate → co150_k9_domain_gate → co146_boundary_append → co77_closure_declaration_sweep → co120_provenance_pin_gate → co135_review_hygiene → co136_gate_hygiene → co146_boundary_append`，**循环至 sha 稳定**。
> **R-CO156-2**（取代 R-CO155-2 的闸覆盖缺口项）：下游快照键（sha **与**计数/版本）由 co120 CO-120.3 **机判**；记录不得内嵌下游 sha/计数/版本快照，新增须在 `SNAPSHOT_DECLARED` 声明。
> **R-CO156-3**：单板派生物（computed/domains/几何）的生产者**只准 upsert 自有条目**；禁止对台账/记录做整表重写（先例：co134 整表重写会静默删除他 CO 归属 DV）。

| 工件 | sha16 |
|---|---|
| 工具 `p3_v57_co156_co154_open_disposition.py` | `064ac9a59645a9b7` |
| 工具 `p3_v57_co124_input_selfcheck_gate.py`（CO-124.6 / 牙齿 24） | `446eac06ca0a90db` |
| 工具 `p3_v57_co120_provenance_pin_gate.py`（CO-120.3） | `28d6211f32318d9b` |
| 工具 `p3_v57_co134_req_impl_separation.py`（只 upsert） | `8f59c5be82fe9d06` |
| 工具 `p3_v57_co153_k9_domain_coverage.py`（七域 kind 生产者） | `89bb6506bc0adc6c` |
| 工具 `p3_v57_co146_impedance_table.py`（+dv_computed_zdiff） | `a1a432504f7ff6f2` |
| 工具 `p3_v57_co146_ledger_add.py`（key_path 绑定） | `146a3c06d1a9a905` |
| co124 输入自检 `m13_v57_co124_input_selfcheck_gate.json`（CO-124.6） | `d64da9e0e9e53f7a` |
| co120 闸 `m13_v57_co120_provenance_pin_gate.json`（CO-120.3） | `df6c9135bc02bbe4` |
| co147 裁定 `m13_v57_co147_l2_ruling.json`（CO-147.1 实件） | `62280a4d933801b0` |
| 台账 `derived_value_ledger_v1.json`（9 DV 全域覆盖） | `82f3cb801cf5f236` |
| 登记簿 `input_defect_register_v1.json`（178 项 / OPEN 0） | `b1d8c7130240c4d0` |

## 32. CO-157（**L2 自裁 · 查漏型闸硬化（第 3 轮）**：4 项实测缺口 H-1..H-4 全处置）

| # | 实测缺口（修前） | 处置 | 状态 |
|---|---|---|---|
| H-1 | K9 `process_floor`（`derived_value_evidence_bad`）与 `identity_unparsable` **无负控牙齿**（判据存在但无回归保护） | T17/T17b + **元牙齿** T18（逐 finder id 注入，断言全覆盖）/T18b/T18c ⇒ 牙齿 24→**29** | **CLOSED** |
| H-2 | 判据声明失实：CO-153 称 `declared`「与 process_floor 同口径」，实际后者不验 basis/key_path | co124 注释就地订正（declared **严于** process_floor）+ 本 §32 记录 | **CLOSED** |
| H-3 | co120 `board_superseded` 弱判：任意自由文本（`board="superseded"`）即可成立豁免 | 收严为**板 sha16 格式**（`[0-9a-f]{16}`）且 ≠ 交付板 + 负控/正控牙齿；co120 升 **CO-120.4** | **CLOSED** |
| H-4 | R-CO156-3（禁整表重写台账）**无机判**（仅声明） | co136 增源码守卫 `H4_ledger_upsert_only`（写台账须先读）+ 正负控；co136 升 **CO-136.1** | **CLOSED** |

- 复核：co124 = **PASS / findings 0 / 牙齿 29/29**；co120 = **PASS**（basis_not_ok 0 / teeth 9-9）；co136 = **PASS**；登记簿 **178 项 / OPEN 0**。

> **R-CO157-1**（取代 R-CO156-1 的复现序）：规范复现序 = `co146_impedance_table → co146_pm_eval → co146_ledger_add → co153_k9_domain_coverage → co148_u6_datasheet_inputs → co148_thermal_ruling → co149_thermal_mitigation_derive → co147_l2_ruling → co146_jlc_dfm_gate → co152_findings_disposition → co155_co154_findings_disposition → co156_co154_open_disposition → **co157_gate_hardening_3** → co124_input_selfcheck_gate → co150_k9_domain_gate → co146_boundary_append → co77_closure_declaration_sweep → co120_provenance_pin_gate → co135_review_hygiene → co136_gate_hygiene → co146_boundary_append`，**循环至 sha 稳定**。
> **R-CO157-2**：新增 K9 判据须同时登记进 `K9_FINDER_IDS` 并提供负控（由元牙齿 T18 机判）；`board_superseded` 豁免须给可比对的板 sha16。
> **R-CO157-3**（R-CO156-3 的机判面）：台账写者必须先读台账 —— 由 co136 `H4_ledger_upsert_only` **源码级**把关；⚠ 该守卫为静态启发式（**部分机判**），不替代语义审查；整表重写须在 boundary 显式豁免。

| 工件 | sha16 |
|---|---|
| 工具 `p3_v57_co157_gate_hardening_3.py` | `f532051e46bc7001` |
| 工具 `p3_v57_co124_input_selfcheck_gate.py`（CO-124.7 / 牙齿 29 / T18 元牙齿） | `446eac06ca0a90db` |
| 工具 `p3_v57_co120_provenance_pin_gate.py`（CO-120.4） | `28d6211f32318d9b` |
| 工具 `p3_v57_co136_gate_hygiene.py`（CO-136.1 / H4 源码守卫） | `a5b712e48119fdfb` |
| co124 输入自检 `m13_v57_co124_input_selfcheck_gate.json`（CO-124.7） | `d64da9e0e9e53f7a` |
| co120 闸 `m13_v57_co120_provenance_pin_gate.json`（CO-120.4） | `df6c9135bc02bbe4` |
| co136 闸卫生 `m13_v57_co136_gate_hygiene.json`（CO-136.1） | `77b3ad0a49042ba5` |
| 登记簿 `input_defect_register_v1.json`（178 项 / OPEN 0） | `b1d8c7130240c4d0` |

## 33. CO-158（**L2 自裁 · 交付物完整性**：L5 打样包自足）

- 实测缺口（修前）：`ORDER_NOTES.md` §2 声明「随单提交 … L2 裁定件」，§3/§6 另引 DFM 记录与 U6 热裁定，但 `jlc_package/` 内**均无该等文件**（in-package=False）⇒ 下单时 silent omission；包内阻抗表副本亦为 CO-156 前陈旧件。
- 处置（**CO146-PKG.2**）：新增 `06_rulings/`（3 份 L2 裁定件 + DFM 记录）+ ORDER_NOTES 引用改**包内路径** + 牙齿 `t05_declared_rulings_packaged` / `t06_order_notes_refs_resolve_in_package`；打包工具**并入规范序**。
- 复核：**全 gerber/drill 逐字节未变**（纯增量）；MANIFEST n_files = **40**，teeth = {"t01_idempotent": true, "t05_declared_rulings_packaged": true, "t06_order_notes_refs_resolve_in_package": true, "t07_packaged_rulings_match_sources": true, "t07b_parity_detector_sensitivity": true, "t08_declared_dirs_present": true, "t09_order_notes_binding_params": true, "t09b_binding_param_detector_sensitivity": true, "t10_declared_binding_source_pinned": true, "t10b_binding_source_pin_discriminates": true, "t11_stackup_svg_declared_binding": true, "t11b_stackup_svg_binding_sensitivity": true, "t12_order_notes_record_figures": true, "t12b_record_figure_binding_sensitivity": true, "t12c_impedance_spread_binding_sensitivity": true, "t12d_via_census_binding_sensitivity": true, "t12e_mask_facts_binding_sensitivity": true, "t12f_thermal_figures_binding_sensitivity": true, "t12g_jlc_capability_binding_sensitivity": true, "t12h_drc_rules_edge_binding_sensitivity": true, "t11c_stackup_svg_copper_geometry_binding": true, "t11d_stackup_svg_copper_geometry_sensitivity": true, "t15_impedance_copy_parity": true, "t15b_impedance_copy_parity_sensitivity": true, "t16_layer_sequence_derivation": true, "t16b_layer_sequence_sensitivity": true, "t02_8_copper_gerbers": true, "t03_drill_present": true, "t04_all_hashed": true}；登记簿 **178 项 / OPEN 0**。

**同 CO 另处置 2 项闸卫生**（实测缺陷）：

- **J-2**：co77 的 citation 候选目录**不含 L5 打样包** ⇒ §33 一类引用必被误判 CITATION_MISMATCH（实测 mismatches = `['L5/jlc_package/MANIFEST.json','L5/jlc_package/ORDER_NOTES.md']`，并连带把 co135/co136 判 FAIL）⇒ **CO-77.6** 抽出 `citation_candidates()` 补入 L5 包 + 正控牙齿 `l5_packet_citation_resolvable`；复核 co77 = PASS（mismatches []）。
- **J-3**：**闸退出码不反映 verdict** —— co77（恒 0）/co124/co135/co136 无条件 `return 0` ⇒ shell/CI 复现序无法据 rc 发现 FAIL（实测 co136 FAIL 时 rc 仍 0）⇒ 四件改为 `PASS ⇒ 0 否则 1`（co135：`PASS`/`PASS_WITH_FINDINGS` ⇒ 0；对照 co120/co150/l4/l5 本已正确）。

> **R-CO158-1**（取代 R-CO157-1 的复现序）：规范复现序 = `co146_impedance_table → co146_pm_eval → co146_ledger_add → co153_k9_domain_coverage → co148_u6_datasheet_inputs → co148_thermal_ruling → co149_thermal_mitigation_derive → co147_l2_ruling → co146_jlc_dfm_gate → **co146_jlc_fab_package** → co152_findings_disposition → co155_co154_findings_disposition → co156_co154_open_disposition → co157_gate_hardening_3 → **co158_l5_packet_selfcontained** → co124_input_selfcheck_gate → co150_k9_domain_gate → co146_boundary_append → co77_closure_declaration_sweep → co120_provenance_pin_gate → co135_review_hygiene → co136_gate_hygiene → co146_boundary_append`，**循环至 sha 稳定**。
> **R-CO158-2**：交付物（L5 打样包）内**声明随单提交的附件必须落包内**，且记录内引用须用**包内路径**；新增此类声明由 t05/t06 把关（声明与包内容不一致即 FAIL）。
> **R-CO158-3**：凡规范序内的闸，**退出码必须反映 verdict**（FAIL/不一致 ⇒ 非 0），使复现序可 fail-fast；被 boundary 引用的交付物目录须在 co77 citation 候选目录内。

> **附记（记录卫生·非工件缺陷）**：历次 handoff 称「工作树仅 `_shared` 模式位 dirty」**归因有误** —— 经查 k2 侧 `_shared` 的 dirty 实为 `k2/_shared/knowledge/kb.sqlite3-{wal,shm}`（未跟踪 SQLite 运行时件）；而「模式位」（`eda_core/escape_closure_analysis.py` 100755→100644）在**容器侧 `_shared` 的独立 checkout** 内。二者均属共享子模块边界、非 k2 工件；本件不修改（跨仓/运行时件），仅订正归因以免后续会话误追。

| 工件 | sha16 |
|---|---|
| 工具 `p3_v57_co158_l5_packet_selfcontained.py` | `5f9a909c1dac2505` |
| 工具 `p3_v57_co146_jlc_fab_package.py`（CO146-PKG.2 / 06_rulings + t05/t06） | `0f32a1bf7a9c0964` |
| 工具 `p3_v57_co77_closure_declaration_sweep.py`（CO-77.6 / L5 citation + rc） | `5459595adc50b392` |
| 工具 `p3_v57_co124_input_selfcheck_gate.py`（rc 反映 verdict） | `446eac06ca0a90db` |
| 工具 `p3_v57_co135_review_hygiene.py`（rc） | `827a49520c8e2cd5` |
| 工具 `p3_v57_co136_gate_hygiene.py`（rc） | `a5b712e48119fdfb` |
| 打样包 MANIFEST `L5/jlc_package/MANIFEST.json` | `61ed16118f13611f` |
| 下单备注 `L5/jlc_package/ORDER_NOTES.md` | `baa49660e280b510` |
| 打样包记录 `m13_v57_co146_jlc_fab_package.json` | `962e9d74387dc1ee` |
| 登记簿 `input_defect_register_v1.json`（178 项 / OPEN 0） | `b1d8c7130240c4d0` |

## 34. CO-159 / CO-160（**非执行者对抗复评 CO-156/157/158 + L2 自裁处置**）

- 复评（**CO-159**，as-found 钉在 k2 `c4e951c`；`git show` 重放受评基线 ⇒ 不随后续修复漂移）：**12 findings**（F-1..F-12）——① K9 `declared` 空 `computed` 绕过值-证据绑定；② `conservative_ge` 权威 DV 缺失即跳过交叉校验；③ T18 元牙齿只比电池触发集、源码条件分支 finder 可绕过；④ R-CO156-3「禁整表重写」无机判（H4 只拦未读即写）；⑤ co120 快照键判据依赖嵌套容器；⑥ `board_superseded` 仅格式判（任意 16-hex 成立）；⑦ **co146_jlc_dfm_gate verdict=FAIL 而 rc=0**（违 R-CO158-3）；⑧ 打样包 `06_rulings/` 无来源一致性牙齿；⑨ ORDER_NOTES 目录级声明未覆盖；⑩ co77/co135 候选表已现分歧面无一致性牙齿；⑪ §6 回归块 co78/co81/co84/co95/co98/co106 rc 恒 0；⑫ co135 内嵌 CO-134 时点链 pin + 硬编码 boundary 文件名。
- 处置（**CO-160**，逐项）：co124 牙齿 29→**33**（T15c/T16c/T18d/T18e，升 **CO-124.8**）；co120 升 **CO-120.5**（快照键名面判据 + `SUPERSEDED_BOARDS` 白名单 + 伪造 sha 负控）；co146_jlc_dfm_gate **rc 反映 verdict**（FAIL ⇒ rc=1）；co146_jlc_fab_package 升 **CO146-PKG.3**（`t07` 副本来源一致性 + `t08` 目录级声明）；co135 升 **CO-135.3**（co77 候选表交叉一致性 + 链 pin 由现行记录派生 + boundary 取最新版）；六件回归闸 rc 反映 verdict（CO-78.2/81.2/84.2/95.2/98.2/106.3，co98 按 `baseline_ok and teeth_ok`）。
- 复核：co124 = **PASS / findings 0 / 牙齿 33/33**；co120 = PASS（teeth 12-12）；co77 = PASS（mismatches []）；co135 = PASS_WITH_FINDINGS（候选表一致）；co136 = PASS；DFM 闸 rc=1（FAIL 属预期）；打样包 teeth **9/9**；登记簿 **178 项 / OPEN 0**。

> **R-CO159-1**：K9 `declared` 派生值须带**非空** `computed`（值-证据绑定不得空过）；`conservative_ge` 的权威 DV（`DV-INTPAIR-EDGE` / `DV-PAIR-CROSS`）缺失即 FAIL（不得静默降级）；K9 判据集另由 `T18d` 以**源码**面机判（新增 finder 未登记 `K9_FINDER_IDS` 即 FAIL）。
> **R-CO159-2**：R-CO156-3 的**机判面** = co136 `H4`（写台账须先读台账）+ CO-156 的 co134 stub 复跑证据；「整表重写」的**语义面**无自动判据（已声明，由复评/登记承接）——规则文本不得表述为已机判。
> **R-CO159-3**：下游快照键判据取**键名面**（`*_sha16_after` ∪ `register|ledger[_…]_sha16|items_total|open_total|n_items`），与嵌套位置无关；`board_superseded` 的板 sha16 须在 `SUPERSEDED_BOARDS` 白名单（未登记 16-hex 不成立）。
> **R-CO159-4**：复现序内**所有**闸（含 `co146_jlc_dfm_gate` 与 §6 回归块 co78/co81/co84/co95/co98/co106）退出码须反映 verdict/基线；`co98` 按 `baseline_ok and teeth_ok` 判定（三态报告不因 OPEN 状态返回非 0）。
> **R-CO159-5**（复现序，取代 R-CO158-1）：规范复现序 = `co146_impedance_table → co146_pm_eval → co146_ledger_add → co153_k9_domain_coverage → co148_u6_datasheet_inputs → co148_thermal_ruling → co149_thermal_mitigation_derive → co147_l2_ruling → co146_jlc_dfm_gate → co146_jlc_fab_package → co152_findings_disposition → co155_co154_findings_disposition → co156_co154_open_disposition → co157_gate_hardening_3 → co158_l5_packet_selfcontained → **co159_rev19_co156_co157_co158_review** → **co160_co159_findings_disposition** → co124_input_selfcheck_gate → co150_k9_domain_gate → co146_boundary_append → co77_closure_declaration_sweep → co120_provenance_pin_gate → co135_review_hygiene → co136_gate_hygiene → co78_layer_role_drift_gate → co81_project_rules_gate → co84_dru_domain_gate → co95_in4_reachability → co98_reachability_status_report → co106_reference_plane_gate → co146_boundary_append`，**循环至 sha 稳定**。

| 工件 | sha16 |
|---|---|
| 工具 `p3_v57_co159_rev19_co156_co157_co158_review.py`（as-found 复评） | `9fc2285004a5146f` |
| 记录 `m13_v57_co159_rev19_co156_co157_co158_review.json` | `ca37c1e0a90bff22` |
| 工具 `p3_v57_co160_co159_findings_disposition.py` | `5ba953dc4fdc4ddf` |
| 工具 `p3_v57_co124_input_selfcheck_gate.py`（CO-124.8 / T15c+T16c+T18d+T18e） | `446eac06ca0a90db` |
| 工具 `p3_v57_co120_provenance_pin_gate.py`（CO-120.5 / 键名面 + SUPERSEDED_BOARDS） | `28d6211f32318d9b` |
| 工具 `p3_v57_co135_review_hygiene.py`（CO-135.3 / 候选表交叉一致性 + 链 pin 派生） | `827a49520c8e2cd5` |
| 工具 `p3_v57_co146_jlc_dfm_gate.py`（rc 反映 verdict） | `309beb6fb0d6cef4` |
| 工具 `p3_v57_co146_jlc_fab_package.py`（CO146-PKG.3 / t07+t08） | `0f32a1bf7a9c0964` |
| 登记簿 `input_defect_register_v1.json`（178 项 / OPEN 0） | `b1d8c7130240c4d0` |

## 35. CO-161（**L2 自裁 · 查漏型闸硬化 4**：K9 覆盖完备性 + identity fail-closed）

- 实测缺口（修前，均机判）：**G-1** K9 无「必需 DV 清单」牙齿 —— 台账删 `DV-CO146-THERMAL` / `DV-CO146-PDN-DROP` / `DV-ENGINE-INT_PAIR_PITCH` 任一项时 co124 K9 = 0 findings、co150 `t01` 仍 True（T10/T11 负控用合成注入，不依赖真 DV 存在）⇒ 热/压降/保守实现三域覆盖可被一次 upsert 误删**无声**抹掉；**G-2** `identity` 类 fail-open —— `form` 未识别（如 `q = a + b`）或缺失时无判据命中、静默通过。
- 处置（**CO-161**）：① co124 增 `REQUIRED_DV_IDS`（9 项）与 `derived_value_inventory_missing` 判据 + 负控 T19/T19b；② `co153.KIND_EXPECT` **提为模块级**（必需 DV 清单的单一真值）；③ co150 增 `t03`（两域 kind 断言）/`t04`（co124 `required_dv_ids` == co153 `KIND_EXPECT` 键集）/`t05`（漂移可辨）；④ co124 `identity` 改 **fail-closed**（缺 `form` ⇒ unparsable；未识别 ⇒ 新判据 `derived_value_identity_unhandled_form`，并入 `K9_FINDER_IDS`）+ 负控 T20/T20b。
- 复核：co124 升 **CO-124.9**（牙齿 33→**37/37**，PASS/0 findings）；co150 升 **CO-150.2**（5 牙齿 True，rc=0）；co153 升 **CO-153.2**；登记簿 **178 项 / OPEN 0**。
- 修订号对账：§30 的 CO-150 条与 §34 所记 `CO-124.8` 为各自时点陈述；co124 **现行 = CO-124.9**（本 §35）。

> **R-CO161-1**：K9 **必需 DV 清单**完备性 —— 台账须含全部 9 项必需 DV（`co153.KIND_EXPECT` 键集为**单一真值**）；缺任一项即 `derived_value_inventory_missing` FAIL；co124 的 `required_dv_ids` 须与 co153 `KIND_EXPECT` 逐项一致（co150 `t04`）。
> **R-CO161-2**：`identity` 类派生式 **fail-closed** —— `form` 缺失 ⇒ `derived_value_identity_unparsable`；`form` 未被重算分支识别 ⇒ `derived_value_identity_unhandled_form`（不得静默通过）；新增 identity 形式须同时提供机判重算分支。
> **R-CO161-3**（复现序，取代 R-CO159-5）：规范复现序 = `co146_impedance_table → co146_pm_eval → co146_ledger_add → co153_k9_domain_coverage → co148_u6_datasheet_inputs → co148_thermal_ruling → co149_thermal_mitigation_derive → co147_l2_ruling → co146_jlc_dfm_gate → co146_jlc_fab_package → co152_findings_disposition → co155_co154_findings_disposition → co156_co154_open_disposition → co157_gate_hardening_3 → co158_l5_packet_selfcontained → co159_rev19_co156_co157_co158_review → co160_co159_findings_disposition → **co161_gap_hardening_4** → co124_input_selfcheck_gate → co150_k9_domain_gate → co146_boundary_append → co77_closure_declaration_sweep → co120_provenance_pin_gate → co135_review_hygiene → co136_gate_hygiene → co78_layer_role_drift_gate → co81_project_rules_gate → co84_dru_domain_gate → co95_in4_reachability → co98_reachability_status_report → co106_reference_plane_gate → co146_boundary_append`，**循环至 sha 稳定**。

| 工件 | sha16 |
|---|---|
| 工具 `p3_v57_co161_gap_hardening_4.py` | `0801529a77fdc812` |
| 工具 `p3_v57_co124_input_selfcheck_gate.py`（CO-124.9 / REQUIRED_DV_IDS + identity fail-closed） | `446eac06ca0a90db` |
| 工具 `p3_v57_co153_k9_domain_coverage.py`（CO-153.2 / KIND_EXPECT 模块级） | `89bb6506bc0adc6c` |
| 工具 `p3_v57_co150_k9_domain_gate.py`（CO-150.2 / t03+t04+t05） | `33d4879bc13deeec` |
| 记录 `m13_v57_co124_input_selfcheck_gate.json` | `d64da9e0e9e53f7a` |
| 记录 `m13_v57_co150_k9_domain_gate.json` | `abf5546afe535c9e` |
| 登记簿 `input_defect_register_v1.json`（178 项 / OPEN 0） | `b1d8c7130240c4d0` |

## 36. CO-162（**L2 自裁 · 查漏型闸硬化 5**：verdict 基线约束 + 已声明承载区豁免）

- 实测缺口（修前，均机判）：**G-1** co106 的 verdict 阶梯 `PASS if hard else (... else PASS)` 在 `hard=False ∧ cls_count 空` 时仍判 **PASS** —— 记录自身即 `A_frame_inset_consistency.ok = False`（2 处内缩偏差）而 verdict=PASS；且把 `BASE['spec_current']` 改成伪值（基线 pin 漂移）后仍 verdict=PASS / rc=0（`pin_mismatch` 只记录、不参与判定）⇒ 「基线可复现」与「检查通过」同时失效。**G-2** 桥接承载区（`P3V3_BCU_BRIDGE_IN4` / `P3V3_AUX_BCU_BRIDGE_IN4`，T2-ECN-1/2 PM 裁决的局部承载 pour）被算作内缩偏差却只记录不判定 ⇒ 偏差被静默容忍（既无登记也无 pin，违 CO-139 口径）。
- 处置（**CO-162**）：① 抽纯函数 `verdict_of(checks_ok, teeth_ok, pin_mismatch, cls_count)` —— `pin_mismatch` 非空 ⇒ `BASELINE_MISMATCH`；`teeth_ok=False` ⇒ `FAIL(teeth)`；任一 check 失败 ⇒ `FAIL_DECLARED_COPPER_MISSING` / `INDETERMINATE_REGION_SCOPED` / `FAIL_CHECKS`（**不再回落 PASS**）；增牙齿 `baseline_pin_binding` / `fail_open_closed` / `verdict_positive_control`；② 增 `DECLARED_NON_FULL_PLANE` 注册表 + **冻结 SPEC pin 锚定**（SPEC pin 不成立则豁免自动失效）+ 牙齿 `carrier_exemption_declared_only`。co106 升 **CO-106.4**。
- 复核：真基线 **verdict=PASS / rc=0**（A dev=0、豁免 4 条：2 内岛 + 2 桥接承载、牙齿 8/8）；注入伪 spec pin ⇒ **verdict=BASELINE_MISMATCH / rc=1**。登记簿 **178 项 / OPEN 0**。

> **R-CO162-1**：凡记录内带 `base_pins` 的闸，其 verdict **必须显式消费 pin 漂移**（不等即 `BASELINE_MISMATCH`，非 PASS）；任一 check 失败不得回落 PASS（由 co106 `verdict_of` 纯函数 + 牙齿 `baseline_pin_binding`/`fail_open_closed` 机判）。
> **R-CO162-2**：非整面承载区（桥接/局部 pour）的板框内缩豁免须**登记进注册表**（`DECLARED_NON_FULL_PLANE`）并**锚定冻结源 pin**，豁免逐条入记录；不得静默容忍偏差（违者按 G-2 同族处理）。
> **R-CO162-3**（复现序，取代 R-CO161-3）：规范复现序 = `co146_impedance_table → co146_pm_eval → co146_ledger_add → co153_k9_domain_coverage → co148_u6_datasheet_inputs → co148_thermal_ruling → co149_thermal_mitigation_derive → co147_l2_ruling → co146_jlc_dfm_gate → co146_jlc_fab_package → co152_findings_disposition → co155_co154_findings_disposition → co156_co154_open_disposition → co157_gate_hardening_3 → co158_l5_packet_selfcontained → co159_rev19_co156_co157_co158_review → co160_co159_findings_disposition → co161_gap_hardening_4 → **co162_verdict_binding** → co124_input_selfcheck_gate → co150_k9_domain_gate → co146_boundary_append → co77_closure_declaration_sweep → co120_provenance_pin_gate → co135_review_hygiene → co136_gate_hygiene → co78_layer_role_drift_gate → co81_project_rules_gate → co84_dru_domain_gate → co95_in4_reachability → co98_reachability_status_report → co106_reference_plane_gate → co146_boundary_append`，**循环至 sha 稳定**。

| 工件 | sha16 |
|---|---|
| 工具 `p3_v57_co162_verdict_binding.py` | `03cfd9b937e6b32b` |
| 工具 `p3_v57_co106_reference_plane_gate.py`（CO-106.4 / verdict_of + DECLARED_NON_FULL_PLANE） | `d56a1e51ece54d51` |
| 记录 `m13_v57_co106_reference_plane_gate.json` | `3ad6e35c4bedd72e` |
| 登记簿 `input_defect_register_v1.json`（178 项 / OPEN 0） | `b1d8c7130240c4d0` |

## 37. CO-163（**L2 自裁 · 查漏型闸硬化 6**：下单备注↔声明定值表绑定）

- 实测缺口（修前，均机判）：**G-1** `ORDER_NOTES.md` 的「下单参数」表把 `85Ω 差分 ±10%` / `JLC08161H` / `1.6 mm` / `外层 1oz 内层 0.5oz` / `沉金 ENIG` 写为**字面量**，与 L2 政策件 `jlc_prototype_parameters_v1.json`（监理指令 #10 定值绑定）无绑定、无牙齿 —— 实测把目标阻抗改成 100Ω 后重生成的备注**仍写 85Ω** ⇒ 定值变更会静默产出**客户可见**的陈旧下单备注；**G-2** 该定值表的 `supervisor_instruction.sha16` 声明链从未被核验。
- 处置（**CO-163**）：`p3_v57_co146_jlc_fab_package.py` 升 **CO146-PKG.4** —— 载入声明定值表 + 纯谓词 `binding_params_in_note`/`binding_tokens`；牙齿 `t09_order_notes_binding_params`（备注须逐项命中叠层码/厚度/外内层铜/目标阻抗/容差/表面处理）+ `t09b` 漂移灵敏度 + `t10_declared_binding_source_pinned`（定值表来源 sha16 == 监理指令件 sha16 `35aafe268ff52f89`）+ `t10b` 判据可辨；记录落 `declared_binding`（含 `source_instruction`: path/available/declared_sha16）。
- 复核：打样包 teeth **13/13**（t01..t10b 全 True），订单备注正文与 gerber/drill 逐字节不变；注入定值漂移（100Ω/2.0mm）⇒ t09 立即 FAIL。登记簿 **178 项 / OPEN 0**。

> **R-CO163-1**：客户可见交付物（L5 打样包/下单备注）内的**工程定值**必须与**声明定值表**逐项一致，由 t09/t09b 机判；定值表变更而备注未同步即 FAIL（禁止字面量单向复制导致静默陈旧）。
> **R-CO163-2**：声明定值表的**来源 pin**（`supervisor_instruction.sha16`）必须可核验（t10/t10b）；跨仓来源不可达时 fail-closed 并在记录内显式登记 `available=false`。
> **R-CO163-3**（复现序，取代 R-CO162-3）：规范复现序 = `co146_impedance_table → co146_pm_eval → co146_ledger_add → co153_k9_domain_coverage → co148_u6_datasheet_inputs → co148_thermal_ruling → co149_thermal_mitigation_derive → co147_l2_ruling → co146_jlc_dfm_gate → co146_jlc_fab_package → co152_findings_disposition → co155_co154_findings_disposition → co156_co154_open_disposition → co157_gate_hardening_3 → co158_l5_packet_selfcontained → co159_rev19_co156_co157_co158_review → co160_co159_findings_disposition → co161_gap_hardening_4 → co162_verdict_binding → **co163_binding_to_order_notes** → co124_input_selfcheck_gate → co150_k9_domain_gate → co146_boundary_append → co77_closure_declaration_sweep → co120_provenance_pin_gate → co135_review_hygiene → co136_gate_hygiene → co78_layer_role_drift_gate → co81_project_rules_gate → co84_dru_domain_gate → co95_in4_reachability → co98_reachability_status_report → co106_reference_plane_gate → co146_boundary_append`，**循环至 sha 稳定**。

| 工件 | sha16 |
|---|---|
| 工具 `p3_v57_co163_binding_to_order_notes.py` | `d01c050fb1578c87` |
| 工具 `p3_v57_co146_jlc_fab_package.py`（CO146-PKG.4 / t09+t09b+t10+t10b） | `0f32a1bf7a9c0964` |
| 打样包 MANIFEST `L5/jlc_package/MANIFEST.json` | `61ed16118f13611f` |
| 下单备注 `L5/jlc_package/ORDER_NOTES.md` | `baa49660e280b510` |
| 记录 `m13_v57_co146_jlc_fab_package.json` | `962e9d74387dc1ee` |
| 登记簿 `input_defect_register_v1.json`（178 项 / OPEN 0） | `b1d8c7130240c4d0` |

## 38. CO-164（**L2 自裁 · 收敛判定硬化**：规范复现序 rc 机判执行器）

- 实测事故（CO-163 期间，机判）：`p3_v57_co146_boundary_append.py` 因 §37 文本内 f-string 花括号语法错误**每轮 rc=1 崩溃** ⇒ 第 37 节从未写入、boundary 停在 v2.08、pin 表陈旧（co77 = CITATION_MISMATCH、co135/co136 = FAIL）；而「幂等循环」只看 boundary/记录 sha ⇒ 报 CONVERGED。即 **「以 sha 稳定替代 rc 检查」= 假收敛**；本会话由一个独立 rc 复核发现（自查也据此复现并修复）。
- 处置（**CO-164**）：新增 `p3_v57_co164_order_runner.py`（**不在**规范序内运行，避免自递归；报告落 `.archer_tmp/`，**不被 boundary 引用** ⇒ 不构成下游快照/不动点）：① rc 策略 `EXPECTED_NONZERO = {co146_jlc_dfm_gate}`（verdict=FAIL 属预期），其余任一步非零 ⇒ **立即停机**并报门名/rc/stderr 尾；② **真收敛** = rc 全合规 ∧ 受控 sha 逐轮稳定；③ `--check` 静态体检 t01..t06（步骤存在/可编译/rc 策略/判据灵敏度/稳定性判据/序文本一致）。
- 复核：`--check` **6/6 True**（t06 当场抓到本文档序与执行器 ORDER 的短别名漂移 `co159_rev19_review`，已改为实际步骤名）；端到端负控：把 `co78` 步替换为 rc=3 合成件 ⇒ **abort（rc=1，iterations=1）不报收敛**；登记簿 **178 项 / OPEN 0**。

> **R-CO164-1**：复现序收敛判定**rc 优先** —— 除 `EXPECTED_NONZERO` 白名单（当前仅 `co146_jlc_dfm_gate`，其 verdict=FAIL 属预期）外，任一步 rc≠0 即**立即停机**；**禁止**以「sha 稳定」单独判收敛。
> **R-CO164-2**：规范序**文本**与执行器 `ORDER` 须**有序一致**（由 runner `--check` t06 机判）；新增/变更步骤须同步 runner 与本 boundary。
> **R-CO164-3**（复现序，取代 R-CO163-3；步骤集不变）：规范复现序 = `co146_impedance_table → co146_pm_eval → co146_ledger_add → co153_k9_domain_coverage → co148_u6_datasheet_inputs → co148_thermal_ruling → co149_thermal_mitigation_derive → co147_l2_ruling → co146_jlc_dfm_gate → co146_jlc_fab_package → co152_findings_disposition → co155_co154_findings_disposition → co156_co154_open_disposition → co157_gate_hardening_3 → co158_l5_packet_selfcontained → co159_rev19_co156_co157_co158_review → co160_co159_findings_disposition → co161_gap_hardening_4 → co162_verdict_binding → co163_binding_to_order_notes → co124_input_selfcheck_gate → co150_k9_domain_gate → co146_boundary_append → co77_closure_declaration_sweep → co120_provenance_pin_gate → co135_review_hygiene → co136_gate_hygiene → co78_layer_role_drift_gate → co81_project_rules_gate → co84_dru_domain_gate → co95_in4_reachability → co98_reachability_status_report → co106_reference_plane_gate → co146_boundary_append`，**循环至 sha 稳定**（收敛判定须遵 R-CO164-1：以 rc 为准）。

| 工件 | sha16 |
|---|---|
| 工具 `p3_v57_co164_order_runner.py`（rc 策略 + 真收敛 + `--check` t01..t06） | `db80604b81e805e9` |
| 工具 `p3_v57_co164_disposition.py` | `47356d70e9d684c5` |
| 工具 `p3_v57_co146_boundary_append.py`（§38 + 序文本订正） | `00fa05ab54fdf13c` |
| 登记簿 `input_defect_register_v1.json`（178 项 / OPEN 0） | `b1d8c7130240c4d0` |

## 39. CO-165（**L2 自裁 · 收敛执行器加固**：白名单证据 + 受控 sha 全域）

- 实测缺口（修前，均机判）：**G-1** CO-164 执行器的白名单只按 `rc≠0` 放行 ⇒ 白名单步（当前仅 `co146_jlc_dfm_gate`）的**任何**非零——含崩溃/静默失败——都被当「预期 FAIL」。负控：把 DFM 闸替换为 `raise SystemExit('boom')`（rc=1、stderr 无 traceback）⇒ **旧判据放行**；仅加 Traceback 检测**仍不足**（不打印 traceback 的失败会让盘上**陈旧** FAIL 记录充当 verdict 证据 —— 由本会话自己的端到端负控当场证伪）。**G-2** 受控 sha 仅 7 件（漏 co106/co150/打样包件）⇒ 未受控文件的 2-循环/抖动对收敛判定**不可见**。
- 处置（**CO-165**，执行器升 **CO-164.2**）：白名单项改 `verdict/record/why` 结构化 + 纯判据 `allowlist_decision(step, rc, stderr, verdict, record_fresh)` —— 白名单步须 **rc≠0 ∧ 无 Traceback ∧ 记录由本次执行产出（mtime 新鲜）∧ 记录 verdict == 声明 verdict** 方判 `expected_nonzero`，否则判 `expected_step_returned_zero`/`expected_step_crashed`/`expected_step_record_not_produced`/`expected_step_verdict_mismatch` 并**立即停机**；`watch_paths()` 覆盖 boundary + **全部**记录 + 台账/登记簿 + 打样包 MANIFEST/ORDER_NOTES；`--check` 增 **t07**（四类伪通过负控 + 恒真正控）/ **t08**（受控集覆盖记录类产物）。
- 复核：`--check` **8/8 True**；负控 A（co78 步 rc=3 合成件）⇒ abort(rc=1)；负控 B（DFM 步 `SystemExit('boom')`）⇒ abort class=`expected_step_record_not_produced`；正控：真 DFM 闸（重写记录、verdict=FAIL）判 `expected_nonzero` 且整序 **converged（iterations 2 / rc=0）**。登记簿 **178 项 / OPEN 0**（注：`co148` 登记项在序内为 OPEN、由 `co150` 收口 ⇒ 中途 OPEN 属正常，须以整序收敛后为准）。

> **R-CO165-1**：`EXPECTED_NONZERO` 白名单步须给**双重证据** —— 期望 `verdict` **且** 记录由**本次执行产出**（mtime 新鲜）；`rc≠0` 本身不构成预期 FAIL 的证据（崩溃/静默失败不得被放行）。
> **R-CO165-2**：收敛判定的受控 sha 须覆盖**全部**序内产物（boundary + 全部 `m13_v57_co*.json` + 台账/登记簿 + 打样包件）；新增产物须落入 `watch_paths()`。
> **R-CO165-3**（复现序，步骤集与 R-CO164-3 相同）：规范复现序 = `co146_impedance_table → co146_pm_eval → co146_ledger_add → co153_k9_domain_coverage → co148_u6_datasheet_inputs → co148_thermal_ruling → co149_thermal_mitigation_derive → co147_l2_ruling → co146_jlc_dfm_gate → co146_jlc_fab_package → co152_findings_disposition → co155_co154_findings_disposition → co156_co154_open_disposition → co157_gate_hardening_3 → co158_l5_packet_selfcontained → co159_rev19_co156_co157_co158_review → co160_co159_findings_disposition → co161_gap_hardening_4 → co162_verdict_binding → co163_binding_to_order_notes → co124_input_selfcheck_gate → co150_k9_domain_gate → co146_boundary_append → co77_closure_declaration_sweep → co120_provenance_pin_gate → co135_review_hygiene → co136_gate_hygiene → co78_layer_role_drift_gate → co81_project_rules_gate → co84_dru_domain_gate → co95_in4_reachability → co98_reachability_status_report → co106_reference_plane_gate → co146_boundary_append`，**循环至 sha 稳定**（收敛判定须遵 R-CO164-1 + R-CO165-1/2）。

| 工件 | sha16 |
|---|---|
| 工具 `p3_v57_co164_order_runner.py`（CO-164.2 / `allowlist_decision` + `watch_paths` + t07/t08） | `db80604b81e805e9` |
| 工具 `p3_v57_co165_runner_hardening.py` | `3cb331ff39b0c824` |
| 登记簿 `input_defect_register_v1.json`（178 项 / OPEN 0） | `b1d8c7130240c4d0` |

## 40. CO-166（**非执行者对抗复评**：CO-159..CO-165；as-found @ `e427909`）

- 复评方：context 归零的续接会话（满足 handoff-z39 §5「另一会话，禁自评」）；对象钉在受评基线 commit，`git show` 内存重放 ⇒ 结论**可重放、不随后续修复漂移**。方法：正控 V0..V6 + 负控 P1..P6（内存注入、零落盘、零坐标搜索）。
- 结论：verdict **PASS_WITH_FINDINGS**；findings **6**（F-1..F-6）。独立确认含：冻结四源 4/4、co124 CO-124.9（37 牙齿/0 findings）、co150 CO-150.2（5/5）、co106 CO-106.4（8/8）、co120（12/12）、co77 PASS、co135 CO-135.3、co136 PASS、打样包 CO146-PKG.4（34 件/13 牙齿）、登记簿 65 项/OPEN 0（co159:F-1..F-12 全 CLOSED）、co124 必需 DV 清单 == co153 `KIND_EXPECT`、t10 来源 pin 正控、co146_boundary_append **只读重放逐字节幂等且仅写 boundary**。
- findings 处置见 §41（CO-167）。登记簿 **178 项 / OPEN 0**。

> **R-CO166-1**：复评必须由**另一会话**（context 归零）执行，且对象钉在受评基线 commit（`git show` 重放）⇒ 结论可重放、不随后续修复漂移。
> **R-CO166-2**：负控须为**内存注入**（零落盘/零坐标搜索）；不得以「记录自证」充当独立证据。
> **R-CO166-3**（复现序，取代 R-CO165-3；步骤集新增 co166 复评步）：规范复现序 = `co146_impedance_table → co146_pm_eval → co146_ledger_add → co153_k9_domain_coverage → co148_u6_datasheet_inputs → co148_thermal_ruling → co149_thermal_mitigation_derive → co147_l2_ruling → co146_jlc_dfm_gate → co146_jlc_fab_package → co152_findings_disposition → co155_co154_findings_disposition → co156_co154_open_disposition → co157_gate_hardening_3 → co158_l5_packet_selfcontained → co159_rev19_co156_co157_co158_review → co160_co159_findings_disposition → co161_gap_hardening_4 → co162_verdict_binding → co163_binding_to_order_notes → co166_rev19_co159_co165_review → co124_input_selfcheck_gate → co150_k9_domain_gate → co146_boundary_append → co77_closure_declaration_sweep → co120_provenance_pin_gate → co135_review_hygiene → co136_gate_hygiene → co78_layer_role_drift_gate → co81_project_rules_gate → co84_dru_domain_gate → co95_in4_reachability → co98_reachability_status_report → co106_reference_plane_gate → co146_boundary_append`，**循环至 sha 稳定**（收敛判定须遵 R-CO164-1 + R-CO165-1/2）。

| 工件 | sha16 |
|---|---|
| 工具 `p3_v57_co166_rev19_co159_co165_review.py`（只读复评；对象钉 `e427909`） | `21100cc0ca5d7d21` |
| 记录 `m13_v57_co166_rev19_co159_co165_review.json`（重建） | `a93114a9d57d582a` |
| 卡 `m13_v57_CO166_rev19_co159_co165_review.md`（重建） | `4391594ca4be86c6` |
| 登记簿 `input_defect_register_v1.json`（178 项 / OPEN 0） | `b1d8c7130240c4d0` |

## 41. CO-167（**L2 自裁 · CO-166 findings 处置**：收敛判据加固）

- 实测缺口（CO-166 复评，均机判内存注入）：**F-1**（medium）序解析器取「最后一条含字面量 `规范复现序` 赋值的行」⇒ 更新的 R-COxxx-3 若改措辞即被**回落到更旧序行**，t06 假通过；**F-2**（low）白名单「记录由本次执行产出」用绝对 mtime `≥ t0-1.0` ⇒ 记录 mtime 落在**未来**（时钟回拨/网络盘/异机）时，**崩溃**步仍被判 `expected_nonzero`；**F-3**（low）白名单记录 ⊆ `watch_paths()` 无牙齿；**F-4**（low）t09 无锚子串（`185Ω`/`11.6 mm` 误命中）+ 容差记号被厚度公差满足；**F-5**（low）t09 对措辞敏感（`1.6mm`/`外层1oz`）；**F-6**（low）白名单 expected verdict 允许写成 `PASS`。
- 处置（**CO-167**）：① 序解析器增「末条可解析序行之后仍有其它 `规范复现序` 提及 ⇒ 返回 []」fail-closed（F-1）；② 白名单刷新判据改**变更检测** `record_refreshed(before, after)`（exists / mtime_ns / 内容 sha16，与时钟无关）（F-2）；③ `--check` 增 **t09**（白名单记录 ⊆ 受控集）（F-3）/ **t10**（刷新判据变更检测灵敏度）（F-2）；④ `binding_param_checks` 记号改**有锚正则 + 柔性空白 + 容差须在 zdiff 邻域**（F-4/F-5）；⑤ `allowlist_decision` 与 t07 禁 expected verdict = `PASS`（F-6）。打样包升 **CO146-PKG.5**；执行器升 **CO-167.1**。
- 复核：`--check` **t01..t10 全 True**；`binding_param_checks` 现行备注 7/7、改排版仍 7/7、`185Ω`/`11.6 mm`/容差漂移均不通过；整序 **converged**（rc 策略不变）。登记簿 **178 项 / OPEN 0**。

> **R-CO167-1**：白名单「记录由本次执行产出」一律用**变更检测**（exists/mtime_ns/sha），**禁止**绝对时间比较（未来 mtime 可伪新鲜）。
> **R-CO167-2**：白名单记录须 ⊆ `watch_paths()`；expected `verdict` 不得为 `PASS`。
> **R-CO167-3**（复现序，取代 R-CO166-3）：规范复现序 = `co146_impedance_table → co146_pm_eval → co146_ledger_add → co153_k9_domain_coverage → co148_u6_datasheet_inputs → co148_thermal_ruling → co149_thermal_mitigation_derive → co147_l2_ruling → co146_jlc_dfm_gate → co146_jlc_fab_package → co152_findings_disposition → co155_co154_findings_disposition → co156_co154_open_disposition → co157_gate_hardening_3 → co158_l5_packet_selfcontained → co159_rev19_co156_co157_co158_review → co160_co159_findings_disposition → co161_gap_hardening_4 → co162_verdict_binding → co163_binding_to_order_notes → co166_rev19_co159_co165_review → co167_co166_findings_disposition → co124_input_selfcheck_gate → co150_k9_domain_gate → co146_boundary_append → co77_closure_declaration_sweep → co120_provenance_pin_gate → co135_review_hygiene → co136_gate_hygiene → co78_layer_role_drift_gate → co81_project_rules_gate → co84_dru_domain_gate → co95_in4_reachability → co98_reachability_status_report → co106_reference_plane_gate → co146_boundary_append`，**循环至 sha 稳定**（收敛判定须遵 R-CO164-1 + R-CO165-1/2 + R-CO167-1/2）。

| 工件 | sha16 |
|---|---|
| 工具 `p3_v57_co167_co166_findings_disposition.py` | `7f25190574691959` |
| 工具 `p3_v57_co164_order_runner.py`（CO-167.1 / `record_refreshed` + t09/t10 + 序解析 fail-closed） | `db80604b81e805e9` |
| 工具 `p3_v57_co146_jlc_fab_package.py`（CO146-PKG.5 / t09 有锚正则） | `0f32a1bf7a9c0964` |
| 记录 `m13_v57_co146_jlc_fab_package.json`（重建） | `962e9d74387dc1ee` |
| 登记簿 `input_defect_register_v1.json`（178 项 / OPEN 0） | `b1d8c7130240c4d0` |

## 42. CO-168（**L2 自裁 · 登记簿自洽性硬化**：status 词汇 + counts 复算）

- 实测缺口（修前，均机判）：**G-1** 登记簿 `status` 无词汇机判 —— 任一项 status 改成 `open`/`Closed` 后 co124 仍 PASS / 0 findings，该项**静默落出** `counts` 的 OPEN 计数（未结缺陷被算作已结）⇒ handoff/§ 节引用的「OPEN 0」不可信；**G-2** `meta.counts` 为自述摘要、无闸据 `items` 复算 —— 改 `total=999` / `OPEN=7` 后仍 PASS（该摘要被当权威引用）。
- 处置（**CO-168**）：co124 升 **CO-124.10** —— 增纯函数 `register_consistency(reg)` + 词汇 `REGISTER_STATUSES = (OPEN, CLOSED, PROVED)`：① status 越词汇 ⇒ `status_not_in_vocabulary`；② `meta.counts` 须与据 items 复算的（kind / OPEN / total 三元）**键集与值逐项一致**，否则 `counts_not_rederived_from_items`；任一 ⇒ `FAIL_REGISTER_STALE`（记录落 `register_stale`）。牙齿增 T21 / T21b / T21c（co124 40/40）。
- 复核：真登记簿 `register_stale == []`（178 项 / OPEN 0 复算一致）；注入 status 拼写错 / counts 漂移 ⇒ 分别判 `status_not_in_vocabulary` / `counts_not_rederived_from_items`。

> **R-CO168-1**：登记簿每项 `status` 须 ∈ `REGISTER_STATUSES`；新增状态须先入词汇（禁拼写自由文本）。
> **R-CO168-2**：`meta.counts` 为**派生**字段，须与据 `items` 的复算逐项一致；写登记簿的步骤须在写后重算。
> **R-CO168-3**（复现序，取代 R-CO167-3；步骤集新增 co168）：规范复现序 = `co146_impedance_table → co146_pm_eval → co146_ledger_add → co153_k9_domain_coverage → co148_u6_datasheet_inputs → co148_thermal_ruling → co149_thermal_mitigation_derive → co147_l2_ruling → co146_jlc_dfm_gate → co146_jlc_fab_package → co152_findings_disposition → co155_co154_findings_disposition → co156_co154_open_disposition → co157_gate_hardening_3 → co158_l5_packet_selfcontained → co159_rev19_co156_co157_co158_review → co160_co159_findings_disposition → co161_gap_hardening_4 → co162_verdict_binding → co163_binding_to_order_notes → co166_rev19_co159_co165_review → co167_co166_findings_disposition → co168_register_consistency → co124_input_selfcheck_gate → co150_k9_domain_gate → co146_boundary_append → co77_closure_declaration_sweep → co120_provenance_pin_gate → co135_review_hygiene → co136_gate_hygiene → co78_layer_role_drift_gate → co81_project_rules_gate → co84_dru_domain_gate → co95_in4_reachability → co98_reachability_status_report → co106_reference_plane_gate → co146_boundary_append`，**循环至 sha 稳定**（收敛判定须遵 R-CO164-1 + R-CO165-1/2 + R-CO167-1/2）。

| 工件 | sha16 |
|---|---|
| 工具 `p3_v57_co168_register_consistency.py` | `85505f217fe8c434` |
| 工具 `p3_v57_co124_input_selfcheck_gate.py`（CO-124.10 / `register_consistency` + T21 系列） | `446eac06ca0a90db` |
| 记录 `m13_v57_co124_input_selfcheck_gate.json`（重建） | `d64da9e0e9e53f7a` |
| 登记簿 `input_defect_register_v1.json`（178 项 / OPEN 0） | `b1d8c7130240c4d0` |

## 43. CO-169（**L2 自裁 · 收敛判据硬化**：逐步产物产出证据）

- 实测缺口（机判探针）：CO-165/CO-167 的「记录由本次执行产出」（`record_refreshed` 变更检测）**只作用于白名单步**；其余诸步的契约仅为 `rc == 0`。一个**不崩也不写**的步（早退分支 / 漏写 / 被改成只读检查）会因产物 sha 不变而被「sha 稳定 ⇒ 收敛」**背书**（与 CO-164 假收敛同族，故障类相反：CO-164 = 崩而 sha 不变）。
- 处置（**CO-169**）：执行器升 **CO-169.1** —— 增纯判据 `step_did_work(before, after)`（受控产物集 `watch_paths()` 的 mtime_ns 快照；前进 / 新增 / 删除任一即算做事）与 `zero_rc_class`；运行循环逐步取受控快照，`rc==0` 而**零产物变动** ⇒ 类 `step_wrote_nothing` 并**立即停机**；报告内逐步落 `did_work` 证据；`--check` 增 **t11**。
- 复核：真序 37 步逐步探针 `did_work` **全 True**（每步至少刷写 1 件受控产物）；合成「rc=0 不写」步 ⇒ `step_wrote_nothing` 停机；整序 **converged**。登记簿 **178 项 / OPEN 0**。

> **R-CO169-1**：规范序**每步**须写出至少一个受控产物（`watch_paths()` 覆盖内）；`rc==0` 不构成「做了事」的证据；纯只读步骤须显式登记豁免，不得默认放行。
> **R-CO169-2**：新增步骤须确保其产物在 `watch_paths()` 覆盖内，否则判 `step_wrote_nothing` 停机。
> **R-CO169-3**（复现序，取代 R-CO168-3；步骤集新增 co169）：规范复现序 = `co146_impedance_table → co146_pm_eval → co146_ledger_add → co153_k9_domain_coverage → co148_u6_datasheet_inputs → co148_thermal_ruling → co149_thermal_mitigation_derive → co147_l2_ruling → co146_jlc_dfm_gate → co146_jlc_fab_package → co152_findings_disposition → co155_co154_findings_disposition → co156_co154_open_disposition → co157_gate_hardening_3 → co158_l5_packet_selfcontained → co159_rev19_co156_co157_co158_review → co160_co159_findings_disposition → co161_gap_hardening_4 → co162_verdict_binding → co163_binding_to_order_notes → co166_rev19_co159_co165_review → co167_co166_findings_disposition → co168_register_consistency → co169_step_output_oracle → co124_input_selfcheck_gate → co150_k9_domain_gate → co146_boundary_append → co77_closure_declaration_sweep → co120_provenance_pin_gate → co135_review_hygiene → co136_gate_hygiene → co78_layer_role_drift_gate → co81_project_rules_gate → co84_dru_domain_gate → co95_in4_reachability → co98_reachability_status_report → co106_reference_plane_gate → co146_boundary_append`，**循环至 sha 稳定**（收敛判定须遵 R-CO164-1 + R-CO165-1/2 + R-CO167-1/2 + R-CO169-1/2）。

| 工件 | sha16 |
|---|---|
| 工具 `p3_v57_co169_step_output_oracle.py` | `0cefe789442ba53c` |
| 工具 `p3_v57_co164_order_runner.py`（CO-169.1 / `step_did_work` + t11） | `db80604b81e805e9` |
| 登记簿 `input_defect_register_v1.json`（178 项 / OPEN 0） | `b1d8c7130240c4d0` |

## 44. CO-170（**L2 自裁 · 交付物绑定**：叠层图 ↔ 声明定值表）

- 实测缺口（修前，机判）：**G-1** `stackup_svg(spec)` **只接收 SPEC**，其「外层 1oz / 内层 0.5oz」与铜厚矩形高度为**硬编码字面量**；声明定值表 `jlc_prototype_parameters_v1.json` 改铜厚时叠层图**不跟随**，且当时 13 项牙齿**无一项**读取该图（t09 只绑定 `ORDER_NOTES.md`）。备注 §1/§2 与叠层图**同时**随单提交 ⇒ 制造侧可能按陈旧铜厚施工（与 CO-163 G-1 同族，对象从备注扩到**制造图**）。
- 处置（**CO-170**）：`p3_v57_co146_jlc_fab_package.py` 升 **CO146-PKG.6** —— 抽出 `_tok_match`，新增纯谓词 `stackup_svg_binding_checks(svg_text, binding)`（叠层图须逐项含声明表记号：叠层码 / 成品厚 / 外层铜 / 内层铜）；牙齿 `t11_stackup_svg_declared_binding` + `t11b`（声明铜厚漂移 ⇒ 必判不通过）；记录落 `declared_binding.stackup_svg_checks`。
- 复核：现行声明 **4/4 命中**（打样包牙齿 **15/15**）；声明铜厚改 2oz ⇒ `outer_copper=False`（t11 抓住）；叠层图 sha16 `44370475b258848f` **逐字节不变**。登记簿 **178 项 / OPEN 0**。

> **R-CO170-1**：随单提交的**每一件**制造/工程输入（备注 / 叠层图 / 阻抗表 / 裁定件）内的工程定值，均须与声明定值表（或其 SPEC 来源）机判绑定；新增交付图/表须同步加绑定牙齿。
> **R-CO170-2**：绑定判据一律用 CO-167 的**有锚正则**（数值边界 + 柔性空白），不得裸子串。
> **R-CO170-3**（复现序，取代 R-CO169-3；步骤集新增 co170）：规范复现序 = `co146_impedance_table → co146_pm_eval → co146_ledger_add → co153_k9_domain_coverage → co148_u6_datasheet_inputs → co148_thermal_ruling → co149_thermal_mitigation_derive → co147_l2_ruling → co146_jlc_dfm_gate → co146_jlc_fab_package → co152_findings_disposition → co155_co154_findings_disposition → co156_co154_open_disposition → co157_gate_hardening_3 → co158_l5_packet_selfcontained → co159_rev19_co156_co157_co158_review → co160_co159_findings_disposition → co161_gap_hardening_4 → co162_verdict_binding → co163_binding_to_order_notes → co166_rev19_co159_co165_review → co167_co166_findings_disposition → co168_register_consistency → co169_step_output_oracle → co170_stackup_binding → co124_input_selfcheck_gate → co150_k9_domain_gate → co146_boundary_append → co77_closure_declaration_sweep → co120_provenance_pin_gate → co135_review_hygiene → co136_gate_hygiene → co78_layer_role_drift_gate → co81_project_rules_gate → co84_dru_domain_gate → co95_in4_reachability → co98_reachability_status_report → co106_reference_plane_gate → co146_boundary_append`，**循环至 sha 稳定**（收敛判定须遵 R-CO164-1 + R-CO165-1/2 + R-CO167-1/2 + R-CO169-1/2）。

| 工件 | sha16 |
|---|---|
| 工具 `p3_v57_co170_stackup_binding.py` | `abfa76433aef6d2e` |
| 工具 `p3_v57_co146_jlc_fab_package.py`（CO146-PKG.6 / `stackup_svg_binding_checks` + t11/t11b） | `0f32a1bf7a9c0964` |
| 叠层图 `L5/jlc_package/03_stackup/JLC08161H_stackup.svg` | `44370475b258848f` |
| 记录 `m13_v57_co146_jlc_fab_package.json`（重建） | `962e9d74387dc1ee` |
| 登记簿 `input_defect_register_v1.json`（178 项 / OPEN 0） | `b1d8c7130240c4d0` |

## 45. CO-171（**L2 自裁 · 交付物绑定**：备注内记录派生数字 ↔ 来源记录）

- 实测缺口（修前，机判）：**G-1** `ORDER_NOTES` §5 写死「model-spread 观察值（**+11.6%**）」，该串**不存在于任何记录**（`grep 11.6` 在 L2/L3 记录零命中）；阻抗表记录自身在 s=0.395mm（设计名义最宽间距）M2(HJ)=94.94Ω 对目标 85Ω 即 **+11.69%**，且「模型间 spread」≈4.8% ⇒ 客户可见的阻抗告警数字**无源且已陈旧**，措辞亦失实（CO-163 的 t09 只绑声明定值表 7 记号，不覆盖记录派生值）。**G-2** §7 的 DRC 计数（42 项 / `lib_footprint_*` 41 / silk 1）无牙齿绑定（现态一致，但无护栏）。
- 处置（**CO-171**）：`p3_v57_co146_jlc_fab_package.py` 升 **CO146-PKG.7** —— 新增 `impedance_watch_figure(imp)`（由记录派生 watch 下模型相对目标的最大偏离）与 `order_notes_record_figures(note, imp, dfm)`；**订正备注字面量**（+11.6% → **+11.7%**，措辞订正为「模型偏离观察值（M2(HJ) 相对目标）」+ 补「模型间 spread ≈4.8%」）；牙齿 `t12_order_notes_record_figures` + `t12b`（灵敏度）；记录落 `record_figures`。
- 复核：`record_figures.impedance_watch.dev_pct = 11.69`（F.Cu / M2_HJ_Cohn / 0.395mm）；`record_figures.drc_as_designed_n = 42`；打样包牙齿 **17/17**。登记簿 **178 项 / OPEN 0**。

> **R-CO171-1**：客户可见备注/图中的**记录派生**数字（观察值/计数/边界值）须绑定其来源记录；来源记录变更而备注未同步即 FAIL。
> **R-CO171-2**：订正客户可见数值须同时留下「来源记录 → 数字」的可重算路径（本件：`impedance_watch_figure` / t12）。
> **R-CO171-3**（复现序，取代 R-CO170-3；步骤集新增 co171）：规范复现序 = `co146_impedance_table → co146_pm_eval → co146_ledger_add → co153_k9_domain_coverage → co148_u6_datasheet_inputs → co148_thermal_ruling → co149_thermal_mitigation_derive → co147_l2_ruling → co146_jlc_dfm_gate → co146_jlc_fab_package → co152_findings_disposition → co155_co154_findings_disposition → co156_co154_open_disposition → co157_gate_hardening_3 → co158_l5_packet_selfcontained → co159_rev19_co156_co157_co158_review → co160_co159_findings_disposition → co161_gap_hardening_4 → co162_verdict_binding → co163_binding_to_order_notes → co166_rev19_co159_co165_review → co167_co166_findings_disposition → co168_register_consistency → co169_step_output_oracle → co170_stackup_binding → co171_order_notes_record_figures → co124_input_selfcheck_gate → co150_k9_domain_gate → co146_boundary_append → co77_closure_declaration_sweep → co120_provenance_pin_gate → co135_review_hygiene → co136_gate_hygiene → co78_layer_role_drift_gate → co81_project_rules_gate → co84_dru_domain_gate → co95_in4_reachability → co98_reachability_status_report → co106_reference_plane_gate → co146_boundary_append`，**循环至 sha 稳定**（收敛判定须遵 R-CO164-1 + R-CO165-1/2 + R-CO167-1/2 + R-CO169-1/2）。

| 工件 | sha16 |
|---|---|
| 工具 `p3_v57_co171_order_notes_record_figures.py` | `a48cc84cc3fad741` |
| 工具 `p3_v57_co146_jlc_fab_package.py`（CO146-PKG.7 / `order_notes_record_figures` + t12/t12b） | `0f32a1bf7a9c0964` |
| 下单备注 `L5/jlc_package/ORDER_NOTES.md`（**§5 数值已订正**） | `baa49660e280b510` |
| 记录 `m13_v57_co146_jlc_fab_package.json`（重建） | `962e9d74387dc1ee` |
| 阻抗表 `m13_v57_co146_impedance_table.json`（来源记录） | `794132ded5a0ce61` |
| 登记簿 `input_defect_register_v1.json`（178 项 / OPEN 0） | `b1d8c7130240c4d0` |

## 46. CO-172 / CO-173（**L2 自裁 · 非执行者对抗复评 + 记录派生数字绑定补强**）

- **复评（CO-172，非执行者会话、as-found 钉在 `7bffb75`；`git show` 取源 + 内存注入、零落盘、零坐标搜索）**：对象 = CO-166..CO-171；verdict **PASS_WITH_FINDINGS**（7 findings）。handoff §4.2 指定关注点逐一裁定：
  **F-1**（medium）§5「模型间 spread ≈4.8%」为记录派生数字但**无来源记录串、亦无牙齿**（t12 只绑 dev% +11.7%）⇒ R-CO171-1 在本备注内**仍有未绑定项**（P1：仅改 spread、不动 dev% ⇒ as-found 判据全 True）；
  **F-2**（medium）§2 非通孔过孔**逐 span 分解**（92/88/32/8）硬编码，源 = DFM 记录 `via_type_census` —— **总量绑定 ≠ 分量绑定**（P2）；
  **F-3**（medium）§3 阻焊净距 0.0695 / 欠 0.0205 / 回退 0.0995 / 开窗 0.05→0.02mm 硬编码，源 = CO-147 记录 `mask_measure`（P3）；
  **F-4**（medium）§6 U6 热数字（PACT 4.7–7.0W / θJA 17.4 / Tj 限 120 / 121.8–161.8 / ψJB 路线 173.6 / Ta 40°C）硬编码，源 = CO-148 + CO-149（P4）；
  **F-5**（low）§4 JLC 限值散文与「板规铜-板边 0.30mm」（源 = JLC 能力记录 + **冻结** `drc_rules.manufacturing.min_copper_edge_clearance`）在**备注与 DFM 闸工具两处**均硬编码（P5/P6）；
  **F-6**（medium）叠层图（03_，**随单提交的制造输入**）**铜厚矩形几何**硬编码 `0.035`/`0.0175`mm，t11 只绑**文本**（P7）⇒ 声明铜厚变更时图与声明在**几何上**脱钩、制造侧按图施工；
  **F-7**（low）runner `step_did_work` 快照**单信号 mtime_ns**（P8：值为标量 int）⇒ 粗粒度/网络 FS 同刻重写、mtime 规范化/回写、时钟回拨下**假停机**（fail-closed，不致假通过）；且受控集为**全局集合、非步本地** ⇒ 并发会话写受控件可被误判为「本步做了事」（假通过方向）。　关注点④（`REGISTER_STATUSES` / `counts` 复算键集）裁定 = **不过严**（并集比对 ⇒ 多写/少写键均 fail-closed；as-found 复算逐项一致）。
- **处置（CO-173）**：
  ① `p3_v57_co146_jlc_fab_package.py` 升 **CO146-PKG.8** —— 新增纯谓词 `impedance_spread_pct` / `via_census_figures` / `mask_clearance_figures` / `thermal_figures` 与 capability+rules 派生判据；牙齿 **t12c..t12h**（逐来源负控）与 **t11c/t11d**（叠层图**几何**正控/负控）；`stackup_svg(spec, binding)` 的铜厚矩形高度与标题 oz 改由**声明定值表**派生（1oz=0.035mm 标称；当前 1oz/0.5oz ⇒ 21.00/10.50 px）。
  ② `p3_v57_co146_jlc_dfm_gate.py` 升 **CO146-JLC-DFM.2** —— 「板规铜-板边」值由冻结 `drc_rules` 派生 + 牙齿 **t03**（正控/灵敏度）。
  ③ `p3_v57_co164_order_runner.py` 升 **CO-169.2** —— `_artifact_stamp` 多信号指纹（mtime_ns + ctime_ns + size + 内容 sha16）、`_snap_watched` 返回指纹字典 + 静态齿 **t12**。
  ④ **复核**：打样包牙齿 **25/25**；`ORDER_NOTES.md` 与叠层图**输出逐字节不变**（`baa49660e280b510` / `44370475b258848f`）；DFM 闸 rc=1（预期 FAIL）且 t01..t03 全 True；登记簿 **178 项 / OPEN 0**（+7 TOOL_DEFECT，全 CLOSED）。

> **R-CO172-1**：客户可见交付物内**凡可由记录复算的数字**（含**导出量**：模型间 spread、分量计数、回退净距）一律绑定来源记录并配**负控**；仅绑定总量、或只绑「主」数字，**视为未绑定**。
> **R-CO172-2**：随单提交的**制造输入**不仅**文本**、其**几何**亦须由声明定值派生（或至少具备几何牙齿）；「文本已绑定 ⇒ 视为已绑」不成立。
> **R-CO172-3**：复现序执行器的「做了事」判据快照须为**多信号**（mtime_ns + ctime_ns + size + 内容指纹）；残余（全局受控集、非步本地归因）须**如实登记**，不得以「已硬化」掩盖。
> **R-CO172-4**（复现序，取代 R-CO171-3；步骤集新增 co172/co173）：规范复现序 = `co146_impedance_table → co146_pm_eval → co146_ledger_add → co153_k9_domain_coverage → co148_u6_datasheet_inputs → co148_thermal_ruling → co149_thermal_mitigation_derive → co147_l2_ruling → co146_jlc_dfm_gate → co146_jlc_fab_package → co152_findings_disposition → co155_co154_findings_disposition → co156_co154_open_disposition → co157_gate_hardening_3 → co158_l5_packet_selfcontained → co159_rev19_co156_co157_co158_review → co160_co159_findings_disposition → co161_gap_hardening_4 → co162_verdict_binding → co163_binding_to_order_notes → co166_rev19_co159_co165_review → co167_co166_findings_disposition → co168_register_consistency → co169_step_output_oracle → co170_stackup_binding → co171_order_notes_record_figures → co172_rev19_co166_co171_review → co173_co172_findings_disposition → co124_input_selfcheck_gate → co150_k9_domain_gate → co146_boundary_append → co77_closure_declaration_sweep → co120_provenance_pin_gate → co135_review_hygiene → co136_gate_hygiene → co78_layer_role_drift_gate → co81_project_rules_gate → co84_dru_domain_gate → co95_in4_reachability → co98_reachability_status_report → co106_reference_plane_gate → co146_boundary_append`，**循环至 sha 稳定**（收敛判定须遵 R-CO164-1 + R-CO165-1/2 + R-CO167-1/2 + R-CO169-1/2）。

| 工件 | sha16 |
|---|---|
| 工具 `p3_v57_co172_rev19_co166_co171_review.py`（CO-172.1） | `94410c75a4b0acb2` |
| 工具 `p3_v57_co173_co172_findings_disposition.py` | `039eefbf28ae5d5a` |
| 复评记录 `m13_v57_co172_rev19_co166_co171_review.json` | `e7bca2e46eaac2af` |
| 工具 `p3_v57_co146_jlc_fab_package.py`（CO146-PKG.8 / t12c..t12h + t11c/t11d） | `0f32a1bf7a9c0964` |
| 工具 `p3_v57_co146_jlc_dfm_gate.py`（CO146-JLC-DFM.2 / 板规铜-板边派生 + t03） | `309beb6fb0d6cef4` |
| 工具 `p3_v57_co164_order_runner.py`（CO-169.2 / 多信号快照 + t12；42 步） | `db80604b81e805e9` |
| 下单备注 `L5/jlc_package/ORDER_NOTES.md`（**逐字节不变**） | `baa49660e280b510` |
| 叠层图 `03_stackup/JLC08161H_stackup.svg`（**逐字节不变**） | `44370475b258848f` |
| 打样包记录 `m13_v57_co146_jlc_fab_package.json`（重建 / PKG.8） | `962e9d74387dc1ee` |
| DFM 闸记录 `m13_v57_co146_jlc_dfm_gate.json`（DFM.2） | `0f548bf44d041512` |
| 登记簿 `input_defect_register_v1.json`（178 项 / OPEN 0） | `b1d8c7130240c4d0` |

## 47. CO-174（**L2 自裁 · 复现序归因硬化**）

- **问题（CO-172 F-7 残余）**：`step_did_work` 的受控集是**全局** `watch_paths()` ⇒ 并发/他人写**任一**受控件都会被误判为「本步做了事」（假通过方向）。
- **处置**：`p3_v57_co164_order_runner.py` 升 **CO-169.3** ——
  ① `STEP_ARTIFACTS`：**每步主产物集**（由实测探针逐步跑 ORDER **钉定**，非猜测；42 步无一步为空）；
  ② `_snap_watched(paths)` 参数化；执行循环中 `did_work` 归因**仅限本步声明集**（全局集仅保留给收敛 sha，R-CO165 不变）；
  ③ 报告增 `declared_changed` / `stray_changed`（后者 = 本步窗口内**非声明**受控件的变动证据）；
  ④ 牙齿 **t13**（每步声明完备 + ⊆ 全局受控集）/ **t13b**（步本地负控：非声明件变动不得归因本步）/ **t13c**（共享件残余枚举一致）。
- **残余（如实登记）**：处置类 17 步的唯一主产物是**共享**登记簿（台账另被 4 步共享）⇒ 共享件上的他写仍可误判；已显式枚举于 `SHARED_ARTIFACT_RESIDUAL` 并 t13c 机判（防静默遗忘）；彻底关闭须每步独立标记件（下轮候选）。
- **登记簿**：+2（`co174:G-1/G-2`，全 CLOSED；178 项 / OPEN 0）。

> **R-CO174-1**：复现序执行器的 `did_work` **归因**须**步本地**（仅本步声明的主产物集）；以全局受控集代为背书**不成立**。共享主产物上的他写属**已登记残余**，须**显式枚举**且机判（禁静默遗忘）。
> **R-CO174-2**（复现序，取代 R-CO172-4；步骤集新增 co174）：规范复现序 = `co146_impedance_table → co146_pm_eval → co146_ledger_add → co153_k9_domain_coverage → co148_u6_datasheet_inputs → co148_thermal_ruling → co149_thermal_mitigation_derive → co147_l2_ruling → co146_jlc_dfm_gate → co146_jlc_fab_package → co152_findings_disposition → co155_co154_findings_disposition → co156_co154_open_disposition → co157_gate_hardening_3 → co158_l5_packet_selfcontained → co159_rev19_co156_co157_co158_review → co160_co159_findings_disposition → co161_gap_hardening_4 → co162_verdict_binding → co163_binding_to_order_notes → co166_rev19_co159_co165_review → co167_co166_findings_disposition → co168_register_consistency → co169_step_output_oracle → co170_stackup_binding → co171_order_notes_record_figures → co172_rev19_co166_co171_review → co173_co172_findings_disposition → co174_step_artifact_attribution → co124_input_selfcheck_gate → co150_k9_domain_gate → co146_boundary_append → co77_closure_declaration_sweep → co120_provenance_pin_gate → co135_review_hygiene → co136_gate_hygiene → co78_layer_role_drift_gate → co81_project_rules_gate → co84_dru_domain_gate → co95_in4_reachability → co98_reachability_status_report → co106_reference_plane_gate → co146_boundary_append`，**循环至 sha 稳定**（收敛判定须遵 R-CO164-1 + R-CO165-1/2 + R-CO167-1/2 + R-CO169-1/2 + R-CO174-1）。

| 工件 | sha16 |
|---|---|
| 工具 `p3_v57_co164_order_runner.py`（CO-169.3 / STEP_ARTIFACTS + 步本地归因 / 43 步） | `db80604b81e805e9` |
| 工具 `p3_v57_co174_step_artifact_attribution.py` | `112dd67ac3af0f42` |
| 登记簿 `input_defect_register_v1.json`（178 项 / OPEN 0） | `b1d8c7130240c4d0` |

## 48. CO-175（**L2 自裁 · 交付物绑定补强**）

- **问题（查漏实测）**：交付包内 `04_impedance/impedance_table.{json,md}` 为**随单件**（ORDER_NOTES §1/§2 明列；板厂**据此控阻抗**），却是 `shutil.copy` 来源副本且**无 parity 牙齿**（对照 `06_rulings/*` 有 t07/t07b）⇒ 包被独立提交/手改时与来源脱钩**不可见**；`05_layer_sequence.txt` 由冻结 SPEC 派生，**亦无派生一致性牙齿**。
- **处置**：`p3_v57_co146_jlc_fab_package.py` 升 **CO146-PKG.9** ——
  ① 纯谓词 `copy_parity()`（缺件 fail-closed）+ 牙齿 **t15**（`04_impedance` 两副本与来源**逐字节一致**）/ **t15b**（判据灵敏度：同 True、异 False、缺件 False）；
  ② 牙齿 **t16**（`05_layer_sequence.txt` == `layer_sequence(spec)` **重算**）/ **t16b**（扰动 SPEC stackup 角色 ⇒ 重算必不同）；
  ③ 包记录增 `declared_refs.impedance_copy_parity` 与 `declared_refs.layer_sequence_sha16`。
  ④ **如实说明**：`05_layer_sequence.txt` **不**在 ORDER_NOTES §1/§2 声明为随单件 ⇒ 本项只做**包内自洽**绑定，**不**改变下单提交口径；`ORDER_NOTES.md` **逐字节不变**。
- **登记簿**：+2（`co175:G-1/G-2`，全 CLOSED；178 项 / OPEN 0）。

> **R-CO175-1**：交付包内凡**副本类**件（不限 `06_rulings`）须与来源**逐字节**绑定的**牙齿**；凡**派生类**件须与 来源**重算**一致。缺件一律 fail-closed；仅「在包内」**不成立**。
> **R-CO175-2**（复现序，取代 R-CO174-2；步骤集新增 co175）：规范复现序 = `co146_impedance_table → co146_pm_eval → co146_ledger_add → co153_k9_domain_coverage → co148_u6_datasheet_inputs → co148_thermal_ruling → co149_thermal_mitigation_derive → co147_l2_ruling → co146_jlc_dfm_gate → co146_jlc_fab_package → co152_findings_disposition → co155_co154_findings_disposition → co156_co154_open_disposition → co157_gate_hardening_3 → co158_l5_packet_selfcontained → co159_rev19_co156_co157_co158_review → co160_co159_findings_disposition → co161_gap_hardening_4 → co162_verdict_binding → co163_binding_to_order_notes → co166_rev19_co159_co165_review → co167_co166_findings_disposition → co168_register_consistency → co169_step_output_oracle → co170_stackup_binding → co171_order_notes_record_figures → co172_rev19_co166_co171_review → co173_co172_findings_disposition → co174_step_artifact_attribution → co175_package_parity_binding → co124_input_selfcheck_gate → co150_k9_domain_gate → co146_boundary_append → co77_closure_declaration_sweep → co120_provenance_pin_gate → co135_review_hygiene → co136_gate_hygiene → co78_layer_role_drift_gate → co81_project_rules_gate → co84_dru_domain_gate → co95_in4_reachability → co98_reachability_status_report → co106_reference_plane_gate → co146_boundary_append`，**循环至 sha 稳定**（收敛判定须遵 R-CO164-1 + R-CO165-1/2 + R-CO167-1/2 + R-CO169-1/2 + R-CO174-1 + R-CO175-1）。

| 工件 | sha16 |
|---|---|
| 工具 `p3_v57_co146_jlc_fab_package.py`（CO146-PKG.9 / t15/t15b + t16/t16b；29 牙齿） | `0f32a1bf7a9c0964` |
| 工具 `p3_v57_co175_package_parity_binding.py` | `406d044590c30bd4` |
| 工具 `p3_v57_co164_order_runner.py`（CO-169.3 / 44 步） | `db80604b81e805e9` |
| 包记录 `m13_v57_co146_jlc_fab_package.json`（CO146-PKG.9） | `962e9d74387dc1ee` |
| 下单备注 `L5/jlc_package/ORDER_NOTES.md`（**逐字节不变**） | `baa49660e280b510` |
| 登记簿 `input_defect_register_v1.json`（178 项 / OPEN 0） | `b1d8c7130240c4d0` |

## 49. CO-176（**L2 自裁 · 闸自检强制 + 引证可核验性**）

- **G-1（medium）**：白名单步只核 rc/无 Traceback/记录新鲜/verdict，**不核该步 `teeth`** ⇒ 白名单步（本工程唯一 = `co146_jlc_dfm_gate`）的**自检崩坏被「预期 FAIL」掩盖**、收敛照过（CO-163「自检盲区」同族）。
  **处置**：`p3_v57_co164_order_runner.py` 升 **CO-169.4** —— `EXPECTED_NONZERO.teeth_path` + 纯函数 `teeth_all_true()`（bool / 含 `ok` 的 dict；空/形状不明 ⇒ None fail-closed）+ `record_json_path()`；`allowlist_decision()` 判 **`expected_step_teeth_failed`** ⇒ 停机；静态齿 **t14**。
- **G-2（medium）**：JLC 能力表 `note` 声称「逐条引用原文」，实测**10/24 非原文**（2 条**静默删改**无省略标记）⇒ DFM 判定（记录**随单进包**）的限值依据**不可独立核验**且声明失实（CO-171 同族）。
  **处置**：`p3_v57_co146_jlc_dfm_gate.py` 升 **CO146-JLC-DFM.3** —— 每条增 **`anchor`**（抓取件**原文子串**，24/24 实测命中）+ `capability_citation_checks()` + 牙齿 **t04**（覆盖/非空/逐条原文/实测非原文集==声明集/理由齐备/原文数下限）/ **t05**（灵敏度）；`note` **订正**；`citation` 块（n_verbatim 14/24 + 理由）；capability 记录升 **CO146-CAP.1**。
- **登记簿**：+2（`co176:G-1/G-2`，全 CLOSED；178 项 / OPEN 0）。

> **R-CO176-1**：白名单步的 rc≠0 **只豁免 verdict**、**不豁免自检** —— 该步记录内 `teeth` 须**机判全 True**；不可判（缺字段/形状不明）一律 **fail-closed**。
> **R-CO176-2**：记录内**引证**须逐条绑定来源**原文锚点**（机判）；**非原文**引证须**显式标注**并给理由（禁静默删改/改写）；记录**不得**声称超出实际核验能力的引证口径。
> **R-CO176-3**（复现序，取代 R-CO175-2；步骤集新增 co176）：规范复现序 = `co146_impedance_table → co146_pm_eval → co146_ledger_add → co153_k9_domain_coverage → co148_u6_datasheet_inputs → co148_thermal_ruling → co149_thermal_mitigation_derive → co147_l2_ruling → co146_jlc_dfm_gate → co146_jlc_fab_package → co152_findings_disposition → co155_co154_findings_disposition → co156_co154_open_disposition → co157_gate_hardening_3 → co158_l5_packet_selfcontained → co159_rev19_co156_co157_co158_review → co160_co159_findings_disposition → co161_gap_hardening_4 → co162_verdict_binding → co163_binding_to_order_notes → co166_rev19_co159_co165_review → co167_co166_findings_disposition → co168_register_consistency → co169_step_output_oracle → co170_stackup_binding → co171_order_notes_record_figures → co172_rev19_co166_co171_review → co173_co172_findings_disposition → co174_step_artifact_attribution → co175_package_parity_binding → co176_gate_selfcheck_evidence → co124_input_selfcheck_gate → co150_k9_domain_gate → co146_boundary_append → co77_closure_declaration_sweep → co120_provenance_pin_gate → co135_review_hygiene → co136_gate_hygiene → co78_layer_role_drift_gate → co81_project_rules_gate → co84_dru_domain_gate → co95_in4_reachability → co98_reachability_status_report → co106_reference_plane_gate → co146_boundary_append`，**循环至 sha 稳定**（收敛判定须遵 R-CO164-1 + R-CO165-1/2 + R-CO167-1/2 + R-CO169-1/2 + R-CO174-1 + R-CO175-1 + R-CO176-1/2）。

| 工件 | sha16 |
|---|---|
| 工具 `p3_v57_co164_order_runner.py`（CO-169.4 / 白名单自检强制 + t14；45 步） | `db80604b81e805e9` |
| 工具 `p3_v57_co146_jlc_dfm_gate.py`（CO146-JLC-DFM.3 / 引证锚点 t04/t05） | `309beb6fb0d6cef4` |
| 工具 `p3_v57_co176_gate_selfcheck_evidence.py` | `3110269c1565b493` |
| 能力表 `m13_v57_co146_jlc8_capability.json`（CO146-CAP.1 / 引证锚点） | `fe67e5add2597d1f` |
| DFM 闸记录 `m13_v57_co146_jlc_dfm_gate.json`（DFM.3） | `0f548bf44d041512` |
| 登记簿 `input_defect_register_v1.json`（178 项 / OPEN 0） | `b1d8c7130240c4d0` |

## 50. CO-177（**L2 自裁 · 引证可核验性续**）

- **问题（CO-176 G-2 残余）**：CO-176 只绑**引证 anchor**；能力表的**数值/文本主张**（`value`/`min`/`max`/`allowed`…）仍是**手录** ⇒ 手录值与抓取件脱钩（如 0.09 误录为 0.10）时 anchor 仍命中、**不可检出**（DFM 判定随单进包，其限值依据仍不完全可核验）。
- **处置**：`p3_v57_co146_jlc_dfm_gate.py` 升 **CO146-JLC-DFM.4** ——
  ① `CAPABILITY_VALUE_BIND`：每条 `[(正则, [期望值…])]` 或字面量，**24/24 覆盖、29 个捕获组**；
  ② 纯函数 `_val_eq()`（数值按 float 比较）/ `capability_value_bind_checks()`；
  ③ 牙齿 **t06**（覆盖/非空/字面量存在/正则匹配/捕获组数一致且**逐值相等**/捕获组总数下限 25）/ **t07**（灵敏度：改期望值即判不通过）；
  ④ capability 记录升 **CO146-CAP.2** + `value_bind` 块；人读卡/打印补 T6/T7。
- **登记簿**：+1（`co177:G-1`，CLOSED；178 项 / OPEN 0）。

> **R-CO177-1**：记录内**工程值主张**须**可由来源原文抽取**得到（正则捕获 ↔ 声明值，逐值机判）；仅绑 anchor（引证）**不成立**。绑定为人工编写者须**如实登记**（能力页改版后须人工复核）。
> **R-CO177-2**（复现序，取代 R-CO176-3；步骤集新增 co177）：规范复现序 = `co146_impedance_table → co146_pm_eval → co146_ledger_add → co153_k9_domain_coverage → co148_u6_datasheet_inputs → co148_thermal_ruling → co149_thermal_mitigation_derive → co147_l2_ruling → co146_jlc_dfm_gate → co146_jlc_fab_package → co152_findings_disposition → co155_co154_findings_disposition → co156_co154_open_disposition → co157_gate_hardening_3 → co158_l5_packet_selfcontained → co159_rev19_co156_co157_co158_review → co160_co159_findings_disposition → co161_gap_hardening_4 → co162_verdict_binding → co163_binding_to_order_notes → co166_rev19_co159_co165_review → co167_co166_findings_disposition → co168_register_consistency → co169_step_output_oracle → co170_stackup_binding → co171_order_notes_record_figures → co172_rev19_co166_co171_review → co173_co172_findings_disposition → co174_step_artifact_attribution → co175_package_parity_binding → co176_gate_selfcheck_evidence → co177_capability_value_binding → co124_input_selfcheck_gate → co150_k9_domain_gate → co146_boundary_append → co77_closure_declaration_sweep → co120_provenance_pin_gate → co135_review_hygiene → co136_gate_hygiene → co78_layer_role_drift_gate → co81_project_rules_gate → co84_dru_domain_gate → co95_in4_reachability → co98_reachability_status_report → co106_reference_plane_gate → co146_boundary_append`，**循环至 sha 稳定**（收敛判定须遵 R-CO164-1 + R-CO165-1/2 + R-CO167-1/2 + R-CO169-1/2 + R-CO174-1 + R-CO175-1 + R-CO176-1/2 + R-CO177-1）。

| 工件 | sha16 |
|---|---|
| 工具 `p3_v57_co146_jlc_dfm_gate.py`（CO146-JLC-DFM.4 / 值绑定 t06/t07） | `309beb6fb0d6cef4` |
| 工具 `p3_v57_co177_capability_value_binding.py` | `7a825f76de8503d7` |
| 工具 `p3_v57_co164_order_runner.py`（CO-169.4 / 46 步） | `db80604b81e805e9` |
| 能力表 `m13_v57_co146_jlc8_capability.json`（CO146-CAP.2 / 值绑定） | `fe67e5add2597d1f` |
| DFM 闸记录 `m13_v57_co146_jlc_dfm_gate.json`（DFM.4 / 7 牙齿） | `0f548bf44d041512` |
| 登记簿 `input_defect_register_v1.json`（178 项 / OPEN 0） | `b1d8c7130240c4d0` |

## 51. CO-178（**L2 自裁 · 记录派生数字绑定续**）

- **问题（查漏实测）**：DFM 闸 `_items()` 的逐项判定表内嵌**硬编码派生值** —— 板尺寸下限 `≥3×3mm`/`3.0`、阻抗控制层集 `(4,6,…,20,32)`、最小线宽 `3.5mil`、环宽 `单边 ≥0.075mm`、表面处理 `6 层及以上`、最小过孔孔壁文本 `≥0.15mm` 而**判据实为 ≥0.2mm**（文本 ≠ 强制限）⇒ 能力表（其值已由 CO-177 绑到抓取件）与**判定表文本**脱钩。
- **处置**：`p3_v57_co146_jlc_dfm_gate.py` 升 **CO146-JLC-DFM.5** ——
  ① `_items(m, asd, jlcrun, j=None)` 可注入能力表；硬编码一律由 `JLC8`（+ `MIL_MM`）派生（下限取 `board_min_mm`、层集解析 `impedance_control_layers.value`、mil 由 `MIL_MM` 换算、单边环宽取 `via_annular_note.value/2`、HASL 层数解析 `surface_finish.quote`、孔壁文本明示判定口径）；
  ② `ITEM_DERIVATION_CASES`（**13 情形**）+ 纯函数 `item_limit_derivation_checks()` + 牙齿 **t08**（**成分级**：扰动能力表字段 ⇒ 该项 `jlc_limit` 须**含由扰动值派生的具体成分串**，且**基线不含该串**）。
     **自测加严（如实记录）**：t08 首版仅查「文本是否变化」⇒ **部分硬编码**（把 `3.5mil` 写死而 mm 段仍派生）**可逃逸**（实测发现）；改为成分级断言 + 基线否定后，该回归必被击穿（同一变异复测 ⇒ 停机）。
- **登记簿**：+1（`co178:G-1`，CLOSED；178 项 / OPEN 0）。

> **R-CO178-1**：判定表/备注内的**限值文本**须与**判据同源**且由来源记录**派生**（禁止内嵌硬编码派生值）；派生性须有**扰动证明**（扰动来源 ⇒ 文本必变）。
> **R-CO178-2**（复现序，取代 R-CO177-2；步骤集新增 co178）：规范复现序 = `co146_impedance_table → co146_pm_eval → co146_ledger_add → co153_k9_domain_coverage → co148_u6_datasheet_inputs → co148_thermal_ruling → co149_thermal_mitigation_derive → co147_l2_ruling → co146_jlc_dfm_gate → co146_jlc_fab_package → co152_findings_disposition → co155_co154_findings_disposition → co156_co154_open_disposition → co157_gate_hardening_3 → co158_l5_packet_selfcontained → co159_rev19_co156_co157_co158_review → co160_co159_findings_disposition → co161_gap_hardening_4 → co162_verdict_binding → co163_binding_to_order_notes → co166_rev19_co159_co165_review → co167_co166_findings_disposition → co168_register_consistency → co169_step_output_oracle → co170_stackup_binding → co171_order_notes_record_figures → co172_rev19_co166_co171_review → co173_co172_findings_disposition → co174_step_artifact_attribution → co175_package_parity_binding → co176_gate_selfcheck_evidence → co177_capability_value_binding → co178_drc_item_limit_derivation → co124_input_selfcheck_gate → co150_k9_domain_gate → co146_boundary_append → co77_closure_declaration_sweep → co120_provenance_pin_gate → co135_review_hygiene → co136_gate_hygiene → co78_layer_role_drift_gate → co81_project_rules_gate → co84_dru_domain_gate → co95_in4_reachability → co98_reachability_status_report → co106_reference_plane_gate → co146_boundary_append`，**循环至 sha 稳定**（收敛判定须遵 R-CO164-1 + R-CO165-1/2 + R-CO167-1/2 + R-CO169-1/2 + R-CO174-1 + R-CO175-1 + R-CO176-1/2 + R-CO177-1 + R-CO178-1）。

| 工件 | sha16 |
|---|---|
| 工具 `p3_v57_co146_jlc_dfm_gate.py`（CO146-JLC-DFM.5 / 限值派生 t08） | `309beb6fb0d6cef4` |
| 工具 `p3_v57_co178_drc_item_limit_derivation.py` | `edd00136850f772f` |
| 工具 `p3_v57_co164_order_runner.py`（CO-169.4 / 47 步） | `db80604b81e805e9` |
| DFM 闸记录 `m13_v57_co146_jlc_dfm_gate.json`（DFM.5 / 8 牙齿） | `0f548bf44d041512` |
| 登记簿 `input_defect_register_v1.json`（178 项 / OPEN 0） | `b1d8c7130240c4d0` |

## 52. CO-179（**L2 自裁 · 灵敏度牙齿系统性加严**）

- **G-1（medium）弱判据**：`t07b` 比较**两个不同文件**（`sha256(包内副本) != sha256(ORDER_NOTES.md)`）⇒ 恒真式，**不检验 parity 判据本身**；`t10b` 只证 `sha16(JP) != 声明 pin`（pin 非自身），**不检验 pin 判据**能否拒绝错误 pin。
  **处置**：`p3_v57_co146_jlc_fab_package.py` 升 **CO146-PKG.10** —— parity/pin 判据**函数化**（`packaged_parity_checks()` / `instruction_pin_ok()`），灵敏度牙齿改为**同件近失**证明（来源做「同长单字节翻转」临时件 / pin 做「单 hex 位翻转」）；**变异实测**：把 `copy_parity` 改为恒真 ⇒ **t07b 与 t15b 双双击穿**（rc=1）。
- **G-2（low）不点名**：九处灵敏度牙齿用 `not all(...)`（不点名须翻转项）⇒ 若目标项被写死而扰动偶发翻转他项，旧形仍判通过（CO-178 教训同族）。**处置**：九处改**成分级点名**（t09b→`zdiff`；t11b→`outer_copper`；t11d→`geometry_matches_binding`；t12b→`drc_as_designed_total`；t12c→`impedance_spread_pct`；t12d→`via_census_F.Cu→In2.Cu`；t12e→`mask_gap_mm`；t12f→`thermal_Tj_best_worst`；t12g→`jlc_min_track_width_mil`；t12h→`rule_copper_edge_clearance`，逐项**实测**确认该键翻转）。
- **登记簿**：+2（`co179:G-1/G-2`，全 CLOSED；178 项 / OPEN 0）。

> **R-CO179-1**：凡「灵敏度/负控」牙齿须对**同一被判对象**做**近失扰动**并断言判据**翻转**；禁「比较两个不同对象」「非自身」等恒真式弱判据；判据须**函数化**以便真件与近失共用同一实现。
> **R-CO179-2**：灵敏度牙齿须**点名**须翻转的检查项（成分级）；不得仅用 `not all(...)`。
> **R-CO179-3**（复现序，取代 R-CO178-2；步骤集新增 co179）：规范复现序 = `co146_impedance_table → co146_pm_eval → co146_ledger_add → co153_k9_domain_coverage → co148_u6_datasheet_inputs → co148_thermal_ruling → co149_thermal_mitigation_derive → co147_l2_ruling → co146_jlc_dfm_gate → co146_jlc_fab_package → co152_findings_disposition → co155_co154_findings_disposition → co156_co154_open_disposition → co157_gate_hardening_3 → co158_l5_packet_selfcontained → co159_rev19_co156_co157_co158_review → co160_co159_findings_disposition → co161_gap_hardening_4 → co162_verdict_binding → co163_binding_to_order_notes → co166_rev19_co159_co165_review → co167_co166_findings_disposition → co168_register_consistency → co169_step_output_oracle → co170_stackup_binding → co171_order_notes_record_figures → co172_rev19_co166_co171_review → co173_co172_findings_disposition → co174_step_artifact_attribution → co175_package_parity_binding → co176_gate_selfcheck_evidence → co177_capability_value_binding → co178_drc_item_limit_derivation → co179_sensitivity_teeth_hardening → co124_input_selfcheck_gate → co150_k9_domain_gate → co146_boundary_append → co77_closure_declaration_sweep → co120_provenance_pin_gate → co135_review_hygiene → co136_gate_hygiene → co78_layer_role_drift_gate → co81_project_rules_gate → co84_dru_domain_gate → co95_in4_reachability → co98_reachability_status_report → co106_reference_plane_gate → co146_boundary_append`，**循环至 sha 稳定**（收敛判定须遵 R-CO164-1 + R-CO165-1/2 + R-CO167-1/2 + R-CO169-1/2 + R-CO174-1 + R-CO175-1 + R-CO176-1/2 + R-CO177-1 + R-CO178-1 + R-CO179-1/2）。

| 工件 | sha16 |
|---|---|
| 工具 `p3_v57_co146_jlc_fab_package.py`（CO146-PKG.10 / 近失 + 点名加严；29 牙齿） | `0f32a1bf7a9c0964` |
| 工具 `p3_v57_co179_sensitivity_teeth_hardening.py` | `73876c43bae6ed4f` |
| 工具 `p3_v57_co164_order_runner.py`（CO-169.4 / 48 步） | `db80604b81e805e9` |
| 包记录 `m13_v57_co146_jlc_fab_package.json`（CO146-PKG.10） | `962e9d74387dc1ee` |
| 登记簿 `input_defect_register_v1.json`（178 项 / OPEN 0） | `b1d8c7130240c4d0` |

## 53. CO-180（**L2 自裁 · 牙齿判决完整性**）

- **G-1（medium）**：复现序只对**白名单步**强制记录 `teeth` 全 True（CO-176）；其余**含 `teeth` 的 15+ 步**（impedance_table / pm_eval / co147 / co148 / co124 / co150 / co77 / co120 / co136 / co95 / co98 / co106 / fab 包…）的**自检只记不判** ⇒ 自检崩坏时收敛照过。**处置**：`p3_v57_co164_order_runner.py` 升 **CO-169.5** —— 纯函数 `step_declared_teeth(step)`（自 **CO-174 的 `STEP_ARTIFACTS`** 派生；含 `teeth` 者须全 True，无 ⇒ None，未全 True/形状不明 ⇒ False fail-closed）+ `allowlist_decision()` 非白名单分支 **`step_teeth_failed`** + 静态齿 **t15**（含现状普查）。
- **G-2（medium）**：`co106` —— ① `teeth_ok` 在**前 3 齿**后即结算 ⇒ 其后 4 齿（`baseline_pin_binding` / `fail_open_closed` / `verdict_positive_control` / `carrier_exemption_declared_only`）**记录在案但不参与判决**；② 聚合键 `teeth_ok` **混入 `teeth`**；③ 两项 `checks`（`C_realized_corroboration` / `D_acceptance_matrix_coverage`）`ok` **恒真**（记录冒充判据）。**处置**：**CO-106.5** —— 聚合移至全部齿后、聚合键移出、加不变量齿 `teeth_are_bool_only`、修 `hard` 引用顺序；C/D 标 **`judging: False`** 并自 `checks_ok` 显式排除（**行为不变**：verdict 仍 PASS；键保留以兼容 co110）。
- **G-3（low）**：`co78` 的 `teeth` 为**散文串**（冒充牙齿）⇒ **CO-78.3**：归真齿 dict + 散文移 `teeth_note`。
- **登记簿**：+3（`co180:G-1/G-2/G-3`，全 CLOSED；178 项 / OPEN 0）。

> **R-CO180-1**：记录暴露的自检牙齿**一律参与判决**（不限白名单步）；判据依**声明产物**派生（CO-174），不可判一律 fail-closed。
> **R-CO180-2**：`teeth` 字段须为**布尔牙齿 dict**（散文移 `teeth_note`）；**全部自检须参与本记录判决折算**（禁提前结算/漏折）；判据项与记录项须以 `judging` 标记区分，记录项不得自 `checks_ok` 折算。
> **R-CO180-3**（复现序，取代 R-CO179-3；步骤集新增 co180）：规范复现序 = `co146_impedance_table → co146_pm_eval → co146_ledger_add → co153_k9_domain_coverage → co148_u6_datasheet_inputs → co148_thermal_ruling → co149_thermal_mitigation_derive → co147_l2_ruling → co146_jlc_dfm_gate → co146_jlc_fab_package → co152_findings_disposition → co155_co154_findings_disposition → co156_co154_open_disposition → co157_gate_hardening_3 → co158_l5_packet_selfcontained → co159_rev19_co156_co157_co158_review → co160_co159_findings_disposition → co161_gap_hardening_4 → co162_verdict_binding → co163_binding_to_order_notes → co166_rev19_co159_co165_review → co167_co166_findings_disposition → co168_register_consistency → co169_step_output_oracle → co170_stackup_binding → co171_order_notes_record_figures → co172_rev19_co166_co171_review → co173_co172_findings_disposition → co174_step_artifact_attribution → co175_package_parity_binding → co176_gate_selfcheck_evidence → co177_capability_value_binding → co178_drc_item_limit_derivation → co179_sensitivity_teeth_hardening → co180_teeth_judgment_integrity → co124_input_selfcheck_gate → co150_k9_domain_gate → co146_boundary_append → co77_closure_declaration_sweep → co120_provenance_pin_gate → co135_review_hygiene → co136_gate_hygiene → co78_layer_role_drift_gate → co81_project_rules_gate → co84_dru_domain_gate → co95_in4_reachability → co98_reachability_status_report → co106_reference_plane_gate → co146_boundary_append`，**循环至 sha 稳定**（收敛判定须遵 R-CO164-1 + R-CO165-1/2 + R-CO167-1/2 + R-CO169-1/2 + R-CO174-1 + R-CO175-1 + R-CO176-1/2 + R-CO177-1 + R-CO178-1 + R-CO179-1/2 + R-CO180-1/2）。

| 工件 | sha16 |
|---|---|
| 工具 `p3_v57_co164_order_runner.py`（CO-181.1 / 声明产物牙齿纳入判决 + t15/t16；49 步） | `db80604b81e805e9` |
| 工具 `p3_v57_co106_reference_plane_gate.py`（CO-106.5 / 判决完整性） | `d56a1e51ece54d51` |
| 工具 `p3_v57_co78_layer_role_drift_gate.py`（CO-78.3 / teeth 归真齿 dict） | `b78354dea818848a` |
| 工具 `p3_v57_co180_teeth_judgment_integrity.py` | `9911c54efba46e4a` |
| 登记簿 `input_defect_register_v1.json`（178 项 / OPEN 0） | `b1d8c7130240c4d0` |

## 54. CO-181（**非执行者对抗复评 + L2 自裁处置 · 判决完整性续**）

- **复评方**：context 归零的续接会话（满足 handoff-z46 §5「另一会话，禁自评」）；对象钉 `6bf482d`（`git show` 内存重放，结论不随后续修复漂移）。方法：正控 **V0..V9**（独立重算）+ 负控 **P1..P8**（内存注入、零落盘、零坐标搜索）。verdict **PASS_WITH_FINDINGS**｜findings **5**（F-1..F-5）。
- **F-1（medium）·弱/恒真牙齿**：CO-180 G-1 已将声明齿纳入判决，但被纳入的牙齿有**非判别齿** —— `co146_pm_eval` t01 代数恒真、t02 **字面 `True`**、t03 `bool(非空 dict)` 近恒真（5 齿中 3 齿永不翻转）；`co98` `integrity_detects_miscount` = `(not A) or (not B)`（A/B 互斥）**恒真** ⇒ +1 注入检测未真正实现。**处置**：`co146_pm_eval` 升 **CO148-PM.3**（齿判据**函数化** + 近失负控必翻转）；`co98` 升 **CO-98.3**（判别式 `integrity(rows) and not integrity(rows+1)`）。
- **F-2（medium）·不可判 fail-open**：`step_declared_teeth` 对**不可解析**声明 json 静默跳过 ⇒ None（不判），违 R-CO180-1「不可判一律 fail-closed」。**处置**：runner 升 **CO-181.1** —— 声明 json 缺失/不可解析/非 dict ⇒ **False**。
- **F-3（low）·判据自指**：仅要求「现有齿全 True」无齿集下界 ⇒ **静默删齿/改名**可规避。**处置**：runner 增 **`EXPECTED_TEETH`**（20 件声明齿件的齿名有序集 pin）+ 静态齿 **t16**（覆盖一致 + 内存桩件负控：pin 命中⇒True；齿集漂移/不可解析/`teeth_ok` 冒充⇒False）。
- **F-4（low）·漏扫**：规范序步 `co81`/`co84` 自检以 `teeth_ok` 单标量暴露、无 `teeth` 布尔齿 dict ⇒ 不参与 R-CO180-1 判决（CO-180 G-3 只扫了 co78）。**处置**：`co81` 升 **CO-81.3** / `co84` 升 **CO-84.3**（归真齿 dict，`teeth_ok` 自真齿聚合）；runner 另加「`teeth_ok` 冒充齿 ⇒ False」守卫。
- **F-5（low）·结构性残余**：**固有一轮 pin 滞后**（= 既有 `co180:G-4`）复现 —— 复评方实测：**未变更态**2 轮收敛且 **182/182 件逐字节幂等**；**upstream 记录变更后首轮**在 `co135_review_hygiene` 停机（`unexpected_nonzero`），重跑即收敛（本轮实测：abort → 3 轮收敛）。**如实登记为残余**（消除 = 受控 warm-up 轮 / co135 显式接受滞后 + 齿证明，下轮候选）。
- **登记簿**：+4（`co181:F-1..F-4`，全 CLOSED；178 项 / OPEN 0）。F-5 为既有 `co180:G-4` 残余复现，不重复登记。

> **R-CO181-1**：被纳入判决的牙齿须为**可翻转判据**（函数化 + 近失/负控**必翻转**）；恒真式 / 字面 `True` / 恒 `True` 记录冒充一律视为缺陷（CO-179 R-CO179-1 的**牙齿质量面**）。
> **R-CO181-2**：`step_declared_teeth` 判据**不得自指** —— 齿集须命中 `EXPECTED_TEETH` pin；声明 json 缺失/不可解析/非 dict、或以 `teeth_ok` 冒充齿，一律 **fail-closed**。
> **R-CO181-3**（复现序，取代 R-CO180-3；**步骤集不变 49 步**，co181 为非执行者复评不入执行序）：规范复现序 = `co146_impedance_table → co146_pm_eval → co146_ledger_add → co153_k9_domain_coverage → co148_u6_datasheet_inputs → co148_thermal_ruling → co149_thermal_mitigation_derive → co147_l2_ruling → co146_jlc_dfm_gate → co146_jlc_fab_package → co152_findings_disposition → co155_co154_findings_disposition → co156_co154_open_disposition → co157_gate_hardening_3 → co158_l5_packet_selfcontained → co159_rev19_co156_co157_co158_review → co160_co159_findings_disposition → co161_gap_hardening_4 → co162_verdict_binding → co163_binding_to_order_notes → co166_rev19_co159_co165_review → co167_co166_findings_disposition → co168_register_consistency → co169_step_output_oracle → co170_stackup_binding → co171_order_notes_record_figures → co172_rev19_co166_co171_review → co173_co172_findings_disposition → co174_step_artifact_attribution → co175_package_parity_binding → co176_gate_selfcheck_evidence → co177_capability_value_binding → co178_drc_item_limit_derivation → co179_sensitivity_teeth_hardening → co180_teeth_judgment_integrity → co124_input_selfcheck_gate → co150_k9_domain_gate → co146_boundary_append → co77_closure_declaration_sweep → co120_provenance_pin_gate → co135_review_hygiene → co136_gate_hygiene → co78_layer_role_drift_gate → co81_project_rules_gate → co84_dru_domain_gate → co95_in4_reachability → co98_reachability_status_report → co106_reference_plane_gate → co146_boundary_append`，**循环至 sha 稳定**（收敛判定须遵 R-CO164-1 + R-CO165-1/2 + R-CO167-1/2 + R-CO169-1/2 + R-CO174-1 + R-CO175-1 + R-CO176-1/2 + R-CO177-1 + R-CO178-1 + R-CO179-1/2 + R-CO180-1/2 + R-CO181-1/2）。

| 工件 | sha16 |
|---|---|
| 复评工具 `p3_v57_co181_rev19_co166_co180_review.py`（只读 as-found + 内存注入；V10/P8） | `41611edf97ca93df` |
| 复评记录 `m13_v57_co181_rev19_co166_co180_review.json` | `9a331200b90e84dc` |
| 工具 `p3_v57_co164_order_runner.py`（CO-181.1 / fail-closed + EXPECTED_TEETH pin + t16；49 步） | `db80604b81e805e9` |
| 工具 `p3_v57_co146_pm_eval.py`（CO148-PM.3 / 去恒真齿） | `06b2fe1859861a90` |
| 工具 `p3_v57_co98_reachability_status_report.py`（CO-98.3 / 判别式齿） | `11bfb844d542df6f` |
| 工具 `p3_v57_co81_project_rules_gate.py`（CO-81.3 / 归真齿 dict） | `1c3e3f2eb2dacf6a` |
| 工具 `p3_v57_co84_dru_domain_gate.py`（CO-84.3 / 归真齿 dict） | `90c89c3987b217b6` |
| 登记簿 `input_defect_register_v1.json`（178 项 / OPEN 0） | `b1d8c7130240c4d0` |

## 55. CO-182（**L2 自裁 · 复现序结构重排：消除一轮 pin 滞后**）

- **G-1（medium）·固有一轮 pin 滞后（= 既有 `co180:G-4`）根因机判化**：boundary 由 `co146_boundary_append`（序内 idx 37）刷新，但其后 `co77`/`co120` **仍改写被 boundary 引用的记录**；`co135`（idx 41）读 boundary 时 co120 的 pin 已**瞬时陈旧** ⇒ `V3 citation_scan_clean=False` ⇒ rc=1 ⇒ **首轮停机**（须人工重跑）。复评/复核方**受控瞬态复现**：把 `co120` 记录回滚为 as-found（`8469fb63b19664c0`）⇒ 旧序**迭代 1 即停 `co135` / `unexpected_nonzero`**（与 handoff-z46 开篇「已知特性」一致）。
- **处置（纯重排，不引入容忍、不掩盖）**：在 `co120_provenance_pin_gate` 与 `co135_review_hygiene` 之间**插入** `co146_boundary_append`，使**每个 boundary citation 扫描步紧跟刷新步** —— 序内出现 **50 次**（步集 distinct 不变；`co146_boundary_append` 出现 3 次）；runner 增声明 `BOUNDARY_SCAN_GUARDED`/`BOUNDARY_REFRESH_STEP` + 静态齿 **t17**（受保护步须 i>0 且 `ORDER[i-1]` = 刷新步）。
- **对照实测**：同一瞬态（co120 回滚）下**旧序** abort@co135；**新序**（CO-182.1）**单次调用即收敛**（rc=0；见 R-CO182-2），不再需要「重跑」。
- **登记簿**：+1（`co182:G-1`，CLOSED；178 项 / OPEN 0）。

> **R-CO182-1**：凡**扫描 boundary citation 的步**（`co77`/`co135`）须**紧跟** `co146_boundary_append`；t17 机判。**禁**以「容忍一轮滞后」「放宽扫描判据」代替重排（禁静默让步）。
> **R-CO182-2**（复现序，取代 R-CO181-3；**步集 distinct 不变，序内出现 50 次**）：规范复现序 = `co146_impedance_table → co146_pm_eval → co146_ledger_add → co153_k9_domain_coverage → co148_u6_datasheet_inputs → co148_thermal_ruling → co149_thermal_mitigation_derive → co147_l2_ruling → co146_jlc_dfm_gate → co146_jlc_fab_package → co152_findings_disposition → co155_co154_findings_disposition → co156_co154_open_disposition → co157_gate_hardening_3 → co158_l5_packet_selfcontained → co159_rev19_co156_co157_co158_review → co160_co159_findings_disposition → co161_gap_hardening_4 → co162_verdict_binding → co163_binding_to_order_notes → co166_rev19_co159_co165_review → co167_co166_findings_disposition → co168_register_consistency → co169_step_output_oracle → co170_stackup_binding → co171_order_notes_record_figures → co172_rev19_co166_co171_review → co173_co172_findings_disposition → co174_step_artifact_attribution → co175_package_parity_binding → co176_gate_selfcheck_evidence → co177_capability_value_binding → co178_drc_item_limit_derivation → co179_sensitivity_teeth_hardening → co180_teeth_judgment_integrity → co124_input_selfcheck_gate → co150_k9_domain_gate → co146_boundary_append → co77_closure_declaration_sweep → co120_provenance_pin_gate → co146_boundary_append → co135_review_hygiene → co136_gate_hygiene → co78_layer_role_drift_gate → co81_project_rules_gate → co84_dru_domain_gate → co95_in4_reachability → co98_reachability_status_report → co106_reference_plane_gate → co146_boundary_append`，**循环至 sha 稳定**（收敛判定须遵 R-CO164-1 + R-CO165-1/2 + R-CO167-1/2 + R-CO169-1/2 + R-CO174-1 + R-CO175-1 + R-CO176-1/2 + R-CO177-1 + R-CO178-1 + R-CO179-1/2 + R-CO180-1/2 + R-CO181-1/2 + R-CO182-1）。

| 工件 | sha16 |
|---|---|
| 工具 `p3_v57_co164_order_runner.py`（CO-182.1 / boundary 扫描步紧跟刷新步 + t17；序内 50 次） | `db80604b81e805e9` |
| 登记簿 `input_defect_register_v1.json`（178 项 / OPEN 0） | `b1d8c7130240c4d0` |

## 56. CO-183（**L2 自裁 · 审计机判化 + 残余裁定**）

- **G-1（low）·审计无全域棘轮**：牙齿卫生（常量齿 / 提前结算 / 记录冒充判据）此前仅在 CO-180/CO-181 逐件人审；**新增工具或改齿**可再引入同类病灶而不被发现。**处置**：runner 升 **CO-183.1** —— 纯函数 `teeth_hygiene_scan()`（**AST、只读**）检测 ① 常量齿（值式为纯字面量）② 提前结算（`all/any(teeth…)` 聚合后仍 `teeth[k]=…` 加齿）；静态齿 **t18**（合成正控/负控 + 「聚合的是**他件** teeth」假阳排除 + 现行 **19 工具 / 182 齿 / 0 违规** + 齿数下限 ≥100）。
- **本轮全域机械审计（证据）**：对全部 20 件声明齿件所属 19 个工具做 AST 扫描 ⇒ **0 违规**；并逐件复核「记录冒充判据」：`co124` 的 `"ok": True` 位于**合成负控电池**内（非判据）、`co106` 两项已标 `judging: False` 并从 `checks_ok` 显式排除 ⇒ **无新增病灶**。
- **残余裁定 1（`co174` 共享件归因）·有据延后**：彻底闭合须为 **26 个共享件步**各写**步本地标记件**（改动覆盖每一步的写路径）。threat = **并发写者**误判 `did_work`；现行运行模式为**单写者序**，且残余已由 `SHARED_ARTIFACT_RESIDUAL` + 齿 **t13c** 机判（防静默遗忘）⇒ 收益/回归面不成比例，**裁定延后**；闭合法与规模已勘定在案，**触发条件 = 出现并发写者误判事件**。
- **残余裁定 2（`co177` 值绑定为人工正则）·已足够约束**：绑定式**自带上下文原文**（如 `Min\. Via hole size/diameter (0\.15)mm / 0\.25mm`），并有 t04（锚点须原文子串）+ t06（逐值相等）+ t07（灵敏度）三重判据 ⇒ **静默错值不可达**（声明值必须由原文抽出且等于原文数字）。剩余风险 = 同锚短语在页面多处出现时取**首匹配**，登记为**可接受残余**。
- **登记簿**：+1（`co183:G-1`，CLOSED；178 项 / OPEN 0）。

> **R-CO183-1**：牙齿卫生须**机判化**（t18：常量齿 / 提前结算）；审计判据须**自证**（合成正/负控 + 假阳排除用例），禁以一次性人审代替棘轮。
> **R-CO183-2**：`co174` 共享件归因残余**有据延后**（闭合法 = 26 步步本地标记件；触发 = 并发写者误判事件）；既有 `SHARED_ARTIFACT_RESIDUAL` + t13c 机判不得移除。
> **R-CO183-3**：`co177` 值绑定残余**判定可接受**（绑定式自带上下文 + t04/t06/t07 三重判据 ⇒ 静默错值不可达）；若出现「同锚多处取首匹配」引发的事实偏差，须重开。
> **R-CO183-4**（复现序，取代 R-CO182-2；**步集/序列不变，序内出现 50 次**）：规范复现序 = `co146_impedance_table → co146_pm_eval → co146_ledger_add → co153_k9_domain_coverage → co148_u6_datasheet_inputs → co148_thermal_ruling → co149_thermal_mitigation_derive → co147_l2_ruling → co146_jlc_dfm_gate → co146_jlc_fab_package → co152_findings_disposition → co155_co154_findings_disposition → co156_co154_open_disposition → co157_gate_hardening_3 → co158_l5_packet_selfcontained → co159_rev19_co156_co157_co158_review → co160_co159_findings_disposition → co161_gap_hardening_4 → co162_verdict_binding → co163_binding_to_order_notes → co166_rev19_co159_co165_review → co167_co166_findings_disposition → co168_register_consistency → co169_step_output_oracle → co170_stackup_binding → co171_order_notes_record_figures → co172_rev19_co166_co171_review → co173_co172_findings_disposition → co174_step_artifact_attribution → co175_package_parity_binding → co176_gate_selfcheck_evidence → co177_capability_value_binding → co178_drc_item_limit_derivation → co179_sensitivity_teeth_hardening → co180_teeth_judgment_integrity → co124_input_selfcheck_gate → co150_k9_domain_gate → co146_boundary_append → co77_closure_declaration_sweep → co120_provenance_pin_gate → co146_boundary_append → co135_review_hygiene → co136_gate_hygiene → co78_layer_role_drift_gate → co81_project_rules_gate → co84_dru_domain_gate → co95_in4_reachability → co98_reachability_status_report → co106_reference_plane_gate → co146_boundary_append`，**循环至 sha 稳定**（收敛判定须遵 R-CO164-1 + R-CO165-1/2 + R-CO167-1/2 + R-CO169-1/2 + R-CO174-1 + R-CO175-1 + R-CO176-1/2 + R-CO177-1 + R-CO178-1 + R-CO179-1/2 + R-CO180-1/2 + R-CO181-1/2 + R-CO182-1 + R-CO183-1）。

| 工件 | sha16 |
|---|---|
| 工具 `p3_v57_co164_order_runner.py`（CO-183.1 / 牙齿卫生棘轮 t18；序内 50 次） | `db80604b81e805e9` |
| 登记簿 `input_defect_register_v1.json`（178 项 / OPEN 0） | `b1d8c7130240c4d0` |

## 57. CO-184（**L2 自裁 · 值绑定上下文约束**）

- **G-1（low）·上下文无约束**：`capability_value_bind_checks()` 用 `re.search(pat, page_text)` **全页首匹配** ⇒ 若某条锚短语在抓取件**多处出现**，其值可被绑定到**远处置同值数字**，而 t06（逐值相等）仍过 —— 声明值确实等于「某处」原文数字，但**非该条上下文**（CO-177/`co183:G-3` 残余的具体化）。
- **实测（本件证据）**：现行 24 条锚点在抓取件 `m13_v57_co146_jlc_capability_source.html` 中**均唯一出现**（`anchor_occ=1`），且全部值绑定匹配距锚点 **≤281 字符** ⇒ 现值**无事实偏差**，但判据本身**无上下文约束**。
- **处置**：`p3_v57_co146_jlc_dfm_gate.py` 升 **CO146-JLC-DFM.6** —— `capability_value_bind_checks()` 增 `anchors` 参数与两判据：① **`anchor_localizes_uniquely`**（锚点须在抓取件**唯一**出现，否则 fail-closed）；② **`value_within_anchor_window`**（每条值绑定匹配须落在锚点定位处 **±400 字符**内）；两判据折入 **t06**，并加灵敏度齿 **t07b**（合成正/负控：唯一+邻近⇒True；锚点重复⇒判不唯一；值远置⇒判越窗）。DFM 闸 **9 齿**。
- **结论**：`co183:G-3` 的「人工正则上下文风险」由**机判闭合**（不再依赖人审裁定）。
- **登记簿**：+1（`co184:G-1`，CLOSED；178 项 / OPEN 0）。

> **R-CO184-1**：能力表**值绑定**须**上下文受约束**（锚点唯一定位 + 值在锚点邻域内）；判据须配**合成正/负控**（唯一+邻近 / 重复锚 / 远置值）。禁以「全页首匹配」充当上下文绑定。
> **R-CO184-2**（复现序，取代 R-CO183-4；**步集/序列不变，序内出现 50 次**）：规范复现序 = `co146_impedance_table → co146_pm_eval → co146_ledger_add → co153_k9_domain_coverage → co148_u6_datasheet_inputs → co148_thermal_ruling → co149_thermal_mitigation_derive → co147_l2_ruling → co146_jlc_dfm_gate → co146_jlc_fab_package → co152_findings_disposition → co155_co154_findings_disposition → co156_co154_open_disposition → co157_gate_hardening_3 → co158_l5_packet_selfcontained → co159_rev19_co156_co157_co158_review → co160_co159_findings_disposition → co161_gap_hardening_4 → co162_verdict_binding → co163_binding_to_order_notes → co166_rev19_co159_co165_review → co167_co166_findings_disposition → co168_register_consistency → co169_step_output_oracle → co170_stackup_binding → co171_order_notes_record_figures → co172_rev19_co166_co171_review → co173_co172_findings_disposition → co174_step_artifact_attribution → co175_package_parity_binding → co176_gate_selfcheck_evidence → co177_capability_value_binding → co178_drc_item_limit_derivation → co179_sensitivity_teeth_hardening → co180_teeth_judgment_integrity → co124_input_selfcheck_gate → co150_k9_domain_gate → co146_boundary_append → co77_closure_declaration_sweep → co120_provenance_pin_gate → co146_boundary_append → co135_review_hygiene → co136_gate_hygiene → co78_layer_role_drift_gate → co81_project_rules_gate → co84_dru_domain_gate → co95_in4_reachability → co98_reachability_status_report → co106_reference_plane_gate → co146_boundary_append`，**循环至 sha 稳定**（收敛判定须遵 R-CO164-1 + R-CO165-1/2 + R-CO167-1/2 + R-CO169-1/2 + R-CO174-1 + R-CO175-1 + R-CO176-1/2 + R-CO177-1 + R-CO178-1 + R-CO179-1/2 + R-CO180-1/2 + R-CO181-1/2 + R-CO182-1 + R-CO183-1 + R-CO184-1）。

| 工件 | sha16 |
|---|---|
| 工具 `p3_v57_co146_jlc_dfm_gate.py`（CO146-JLC-DFM.6 / 锚点唯一 + 值邻域 + t07b；9 齿） | `309beb6fb0d6cef4` |
| 工具 `p3_v57_co164_order_runner.py`（CO-183.1 / EXPECTED_TEETH 含 DFM 9 齿；序内 50 次） | `db80604b81e805e9` |
| DFM 闸记录 `m13_v57_co146_jlc_dfm_gate.json`（DFM.6 / 9 齿 / verdict FAIL 预期） | `0f548bf44d041512` |
| 登记簿 `input_defect_register_v1.json`（178 项 / OPEN 0） | `b1d8c7130240c4d0` |

## 58. CO-185（**L2 自裁 · 退出码语义完整性**）

- **G-1（medium）·复评步 rc 不反映 verdict**：`co159`/`co166`/`co172` 三个非执行者复评步**恒 `return 0`**（CO-159 F-11 的「退出码须反映 verdict」只落到闸，漏了复评步）⇒ 其复评结论若为 FAIL / REJECT，规范序仍判**收敛**（假通过方向）。**处置**：三件改 `return 0 if verdict in ("PASS", "PASS_WITH_FINDINGS") else 1`（与 `co135`/`co136` 同口径；现行三件均 PASS_WITH_FINDINGS，行为不变）。
- **G-2（low）·「非 PASS 但 rc==0」类别静默**：`co146_pm_eval` 的热结论 verdict=**FAIL**（U6 热超限，属**已登记结论** co148）而 rc=0 —— 该类别（步自身通过、记录承载已登记缺陷）此前**无显式声明**，审阅者易误判为漏洞，且**新增同类步不会被截**。**处置**：runner 升 **CO-185.1** —— 增 `PASS_VERDICTS`（通过档）+ `DECLARED_NONPASS_OK`（**显式声明**：`why` + `register` + `key_path`）+ 纯判据 `nonpass_decision()` + 运行时停机类 **`undeclared_nonpass_verdict`** + 静态齿 **t19**（白名单/声明集**互斥**、依据齐备、合成正负控、现状全序零未声明）。
- **登记簿**：+2（`co185:G-1`/`co185:G-2`，全 CLOSED；178 项 / OPEN 0）。

> **R-CO185-1**：**复评/结论步**的退出码须反映其 `verdict`（`PASS`/`PASS_WITH_FINDINGS` 为通过档）；禁恒 `return 0`。
> **R-CO185-2**：「**非 PASS 但 rc==0**」须在 `DECLARED_NONPASS_OK` **显式声明**（须给 `why` + 登记依据 `register`）；未声明 ⇒ 停机（`undeclared_nonpass_verdict`）；t19 机判（含合成正负控）。
> **R-CO185-3**（复现序，取代 R-CO184-2；**步集/序列不变，序内出现 50 次**）：规范复现序 = `co146_impedance_table → co146_pm_eval → co146_ledger_add → co153_k9_domain_coverage → co148_u6_datasheet_inputs → co148_thermal_ruling → co149_thermal_mitigation_derive → co147_l2_ruling → co146_jlc_dfm_gate → co146_jlc_fab_package → co152_findings_disposition → co155_co154_findings_disposition → co156_co154_open_disposition → co157_gate_hardening_3 → co158_l5_packet_selfcontained → co159_rev19_co156_co157_co158_review → co160_co159_findings_disposition → co161_gap_hardening_4 → co162_verdict_binding → co163_binding_to_order_notes → co166_rev19_co159_co165_review → co167_co166_findings_disposition → co168_register_consistency → co169_step_output_oracle → co170_stackup_binding → co171_order_notes_record_figures → co172_rev19_co166_co171_review → co173_co172_findings_disposition → co174_step_artifact_attribution → co175_package_parity_binding → co176_gate_selfcheck_evidence → co177_capability_value_binding → co178_drc_item_limit_derivation → co179_sensitivity_teeth_hardening → co180_teeth_judgment_integrity → co124_input_selfcheck_gate → co150_k9_domain_gate → co146_boundary_append → co77_closure_declaration_sweep → co120_provenance_pin_gate → co146_boundary_append → co135_review_hygiene → co136_gate_hygiene → co78_layer_role_drift_gate → co81_project_rules_gate → co84_dru_domain_gate → co95_in4_reachability → co98_reachability_status_report → co106_reference_plane_gate → co146_boundary_append`，**循环至 sha 稳定**（收敛判定须遵 R-CO164-1 + R-CO165-1/2 + R-CO167-1/2 + R-CO169-1/2 + R-CO174-1 + R-CO175-1 + R-CO176-1/2 + R-CO177-1 + R-CO178-1 + R-CO179-1/2 + R-CO180-1/2 + R-CO181-1/2 + R-CO182-1 + R-CO183-1 + R-CO184-1 + R-CO185-1/2）。

| 工件 | sha16 |
|---|---|
| 工具 `p3_v57_co164_order_runner.py`（CO-185.1 / PASS_VERDICTS + DECLARED_NONPASS_OK + nonpass_decision + t19） | `db80604b81e805e9` |
| 工具 `p3_v57_co159_rev19_co156_co157_co158_review.py`（rc↔verdict） | `9fc2285004a5146f` |
| 工具 `p3_v57_co166_rev19_co159_co165_review.py`（rc↔verdict） | `21100cc0ca5d7d21` |
| 工具 `p3_v57_co172_rev19_co166_co171_review.py`（rc↔verdict） | `94410c75a4b0acb2` |
| 登记簿 `input_defect_register_v1.json`（178 项 / OPEN 0） | `b1d8c7130240c4d0` |

## 59. CO-186（**L2 自裁 · 受控集覆盖完备性**）

- **G-1（medium）·受控集漏 md 产物**：R-CO165 要求受控 sha 覆盖**全部产物**，但规范序实际写出的 **13 件 md 卡片**（`impedance_table`/`pm_eval`/`jlc_dfm_gate`/`CO124`/`CO135`/`CO136`/`CO150`/`CO159`/`CO166`/`CO172` 卡 + `L2_RULING_via_channel_and_interpair_domain_v1`/`L2_RULING_u6_thermal_v1`/`L2_RULING_u6_thermal_mitigation_v1`）**不在 `watch_paths()`** ⇒ 既不入收敛 sha、亦无 `did_work` 归因、也不产生 `stray` 证据 ⇒ 某步**静默停写/写坏卡片**仍判「收敛」（假通过方向）。**实测**：全序写出 **14 件 md/txt**，其中仅 boundary 在受控集。
- **处置**：runner 升 **CO-186.1** —— ① 新增 `ORDER_MD_PRODUCTS`（**15 件**：13 新 + boundary + `ORDER_NOTES.md`，由实测 mtime 钉定）；② `watch_paths()` 纳入；③ 各产出步 `STEP_ARTIFACTS` **步本地声明**其 md（`did_work` 归因回到步本地）；④ 静态齿 **t20**（写上下文扫描 `md_write_scan()`：pin 步集 == 扫描步集、名集相等、pin ⊆ 受控集、件存在、步本地声明、合成正负控[写上下文必抽 / 只读引用不误报]）。
- **登记簿**：+1（`co186:G-1`，CLOSED；178 项 / OPEN 0）。

> **R-CO186-1**：规范序各步**写出的全部产物**（含 md 卡片）须入 `watch_paths()` 并**步本地声明**；新增产物须先入 `ORDER_MD_PRODUCTS`（t20 机判），禁「产物在受控集外」。
> **R-CO186-2**（复现序，取代 R-CO185-3；**步集/序列不变，序内出现 50 次**）：规范复现序 = `co146_impedance_table → co146_pm_eval → co146_ledger_add → co153_k9_domain_coverage → co148_u6_datasheet_inputs → co148_thermal_ruling → co149_thermal_mitigation_derive → co147_l2_ruling → co146_jlc_dfm_gate → co146_jlc_fab_package → co152_findings_disposition → co155_co154_findings_disposition → co156_co154_open_disposition → co157_gate_hardening_3 → co158_l5_packet_selfcontained → co159_rev19_co156_co157_co158_review → co160_co159_findings_disposition → co161_gap_hardening_4 → co162_verdict_binding → co163_binding_to_order_notes → co166_rev19_co159_co165_review → co167_co166_findings_disposition → co168_register_consistency → co169_step_output_oracle → co170_stackup_binding → co171_order_notes_record_figures → co172_rev19_co166_co171_review → co173_co172_findings_disposition → co174_step_artifact_attribution → co175_package_parity_binding → co176_gate_selfcheck_evidence → co177_capability_value_binding → co178_drc_item_limit_derivation → co179_sensitivity_teeth_hardening → co180_teeth_judgment_integrity → co124_input_selfcheck_gate → co150_k9_domain_gate → co146_boundary_append → co77_closure_declaration_sweep → co120_provenance_pin_gate → co146_boundary_append → co135_review_hygiene → co136_gate_hygiene → co78_layer_role_drift_gate → co81_project_rules_gate → co84_dru_domain_gate → co95_in4_reachability → co98_reachability_status_report → co106_reference_plane_gate → co146_boundary_append`，**循环至 sha 稳定**（收敛判定须遵 R-CO164-1 + R-CO165-1/2 + R-CO167-1/2 + R-CO169-1/2 + R-CO174-1 + R-CO175-1 + R-CO176-1/2 + R-CO177-1 + R-CO178-1 + R-CO179-1/2 + R-CO180-1/2 + R-CO181-1/2 + R-CO182-1 + R-CO183-1 + R-CO184-1 + R-CO185-1/2 + R-CO186-1）。

| 工件 | sha16 |
|---|---|
| 工具 `p3_v57_co164_order_runner.py`（CO-186.1 / `ORDER_MD_PRODUCTS` + 受控集补全 + t20） | `db80604b81e805e9` |
| 登记簿 `input_defect_register_v1.json`（178 项 / OPEN 0） | `b1d8c7130240c4d0` |

## 60. CO-187（**非执行者对抗复评 CO-181..CO-186 + L2 自裁处置**）

- **复评方**：context 归零的续接会话（满足 handoff-z50 §6「另一会话，禁自评」）；对象钉 `4c581c7`（`git show` 内存重放 ⇒ 结论**不随后续修复漂移**）。方法：正控 **V1..V6**（独立复算）+ 负控 **P1..P6**（内存注入、零落盘、零坐标搜索）。verdict **PASS_WITH_FINDINGS**｜findings **3**（F-1..F-3，全 low）。
- **六件成立（无 medium+）**：V1 齿集 pin + fail-closed（不可解析/漂移/`teeth_ok` 冒充 ⇒ False）；V2 扫描步紧跟刷新步 **且** 刷新步做 **pin 再对齐**（`CITE.sub` + `s16(hit)` ⇒ 单调用收敛机制）；V3 卫生棘轮零违规 + 逐工具齿数 ≥ pin；V4 24 锚点唯一定位、值距 ≤281 字符 ≤ 400 窗口；V5 非 PASS 显式 + 复评步 rc↔verdict；V6 md 产物 ∈ pin ∪ 豁免。
- **F-1（low）·棘轮容器形态漏计**：as-found `teeth_hygiene_scan()` 只认裸 `teeth` 下标/内联 dict ⇒ **别名容器下标**（`tooth[k]=…`；实测 co81 5 齿仅计 2）、`AnnAssign`、`dict(...)`、`.update({...})`、`.setdefault(k,v)`、字面恒真式（`1==1`）**一律漏计**（以这些形态加入常量齿不被 t18 截）。**处置**：runner 升 **CO-187.1** —— 容器形态全覆盖 + t18 **逐工具齿数下限**（`n_teeth ≥ pin` 齿数，漏计即停机）+ 六类形态合成正控。
- **F-2（low）·md 扫描形态漏计**：as-found `md_write_scan()` 仅认 `write_text` ⇒ `open(...,'w')` / `shutil.copy*` 目的 `.md` 产物不在 pin、t20 亦不截（R-CO186-1 静默违反；实测 fab 包 `04_impedance/impedance_table.md` 副本不被旧扫描见）。**处置**：扩至 `write_text`/`write_bytes` + 写模式 `open` + `copy` 目的；新增 `ORDER_MD_PRODUCT_EXEMPT`（显式豁免 + 绑定**实存**补偿牙齿 `t15_impedance_copy_parity`）+ t20 加固。
- **F-3（low）·读取者全集无机判**：`BOUNDARY_SCAN_GUARDED` 为手工枚举 ⇒ 新增读取/扫描 boundary 的步可静默绕开 t17。**处置**：新增 `BOUNDARY_READ_DECLARED`（co146_boundary_append / co166 / co172）+ `boundary_read_scan()` + 静态齿 **t21**（读取者集 == 扫描步 ∪ 声明；互斥；合成正负控）。
- **登记簿**：+3（`co187:F-1..F-3`，全 CLOSED；**178 项 / OPEN 0**）。
- **实测**：`--check` **t01..t21 全 True（23 项）**；注入 co81 别名常量齿 ⇒ t18=False；注入 co124 写模式 open 写入 ⇒ t20=False（负控实测、已还原）。

> **R-CO187-1**：牙齿卫生棘轮须覆盖**全部容器形态**（别名/AnnAssign/dict/update/setdefault/纯字面量表达式），并设**逐工具齿数下限**（漏计即停机，禁「静默少扫」）。
> **R-CO187-2**：md 产物扫描须覆盖**全部写/拷形态**（write_text/write_bytes/写模式 open/copy 目的）；受控集外的 md 产物须入 `ORDER_MD_PRODUCT_EXEMPT` 并**绑定实存补偿牙齿**（t20）。
> **R-CO187-3**：boundary **读取者全集**须机判（t21）：扫描步 ⇒ 紧跟刷新；非扫描步 ⇒ 入 `BOUNDARY_READ_DECLARED`。
> **R-CO187-4**（复现序，取代 R-CO186-2；**步集/序列不变，序内出现 50 次**）：规范复现序 = `co146_impedance_table → co146_pm_eval → co146_ledger_add → co153_k9_domain_coverage → co148_u6_datasheet_inputs → co148_thermal_ruling → co149_thermal_mitigation_derive → co147_l2_ruling → co146_jlc_dfm_gate → co146_jlc_fab_package → co152_findings_disposition → co155_co154_findings_disposition → co156_co154_open_disposition → co157_gate_hardening_3 → co158_l5_packet_selfcontained → co159_rev19_co156_co157_co158_review → co160_co159_findings_disposition → co161_gap_hardening_4 → co162_verdict_binding → co163_binding_to_order_notes → co166_rev19_co159_co165_review → co167_co166_findings_disposition → co168_register_consistency → co169_step_output_oracle → co170_stackup_binding → co171_order_notes_record_figures → co172_rev19_co166_co171_review → co173_co172_findings_disposition → co174_step_artifact_attribution → co175_package_parity_binding → co176_gate_selfcheck_evidence → co177_capability_value_binding → co178_drc_item_limit_derivation → co179_sensitivity_teeth_hardening → co180_teeth_judgment_integrity → co124_input_selfcheck_gate → co150_k9_domain_gate → co146_boundary_append → co77_closure_declaration_sweep → co120_provenance_pin_gate → co146_boundary_append → co135_review_hygiene → co136_gate_hygiene → co78_layer_role_drift_gate → co81_project_rules_gate → co84_dru_domain_gate → co95_in4_reachability → co98_reachability_status_report → co106_reference_plane_gate → co146_boundary_append`，**循环至 sha 稳定**（收敛判定须遵 R-CO164-1 + R-CO165-1/2 + R-CO167-1/2 + R-CO169-1/2 + R-CO174-1 + R-CO175-1 + R-CO176-1/2 + R-CO177-1 + R-CO178-1 + R-CO179-1/2 + R-CO180-1/2 + R-CO181-1/2 + R-CO182-1 + R-CO183-1 + R-CO184-1 + R-CO185-1/2 + R-CO186-1 + R-CO187-1/2/3）。

| 工件 | sha16 |
|---|---|
| 工具 `p3_v57_co164_order_runner.py`（CO-187.1 / t18 齿数下限 + t20 全写形态 + t21 读取者全集） | `db80604b81e805e9` |
| 复评工具 `p3_v57_co187_rev19_co181_co186_review.py` | `c2933e4cc21d1035` |
| 复评记录 `m13_v57_co187_rev19_co181_co186_review.json` | `6643bf07db7ee762` |
| 登记簿 `input_defect_register_v1.json`（178 项 / OPEN 0） | `b1d8c7130240c4d0` |

## 61. CO-188（**L2 自裁 · 越界写 fail-closed：声明↔实现绑定续**）

- **G-1（medium）·越界写只记证据不判**：规范序步骤对**其未声明**的受控件写（= 写他步专属件，或本步**漏声明**）只记入 `stray_changed` 证据、**不参与判决** ⇒ **确定性**越界写（每轮写同内容）**不破 sha 收敛**、且 `did_work` 由本步声明件决定仍 True ⇒ 该件变更**无人归因**、可**静默通过**。这是 CO-174/CO-172 F-7 的**反方向**残余：CO-174 只解决「他步写**本步**件被误判 `did_work`」，未解决「**本步写他步件**无人判」。
- **实测（本件证据）**：现行规范序 run（sha `87223c46e457ed51`）逐轮 `stray_changed` **全空** ⇒ 加 fail-closed 对现基线零冲击；受控注入复现：向首步 `co146_impedance_table` 注入对 `m13_v57_co78_layer_role_drift_gate.json` 的写 ⇒ runner **首步即停** `class=stray_write`（rc=1），已还原。
- **处置**：runner 升 **CO-188.1** —— ① `STRAY_WRITE_ALLOWED`（**显式**例外表，当前为空；新增须 `why`+`paths`，且不得与该步声明件重叠）；② 纯判据 `stray_decision()`；③ 运行时：凡 `stray` 命中例外外之受控件 ⇒ 停机类 **`stray_write`**（对白名单步亦生效）；④ 静态齿 **t22**（合成正负控：空⇒ok / 越界⇒stray_write / 例外内⇒ok / 部分越界⇒stray_write；例外表完备性）。
- **登记簿**：+1（`co188:G-1`，CLOSED；**178 项 / OPEN 0**）。

> **R-CO188-1**：步骤**只可写**其 `STEP_ARTIFACTS` 声明件；对任何**未声明**受控件的写 ⇒ 运行时 `stray_write` 停机（禁「只记 stray 证据」）；例外须入 `STRAY_WRITE_ALLOWED`（显式理由），t22 机判。
> **R-CO188-2**（复现序，取代 R-CO187-4；**步集/序列不变，序内出现 50 次**）：规范复现序 = `co146_impedance_table → co146_pm_eval → co146_ledger_add → co153_k9_domain_coverage → co148_u6_datasheet_inputs → co148_thermal_ruling → co149_thermal_mitigation_derive → co147_l2_ruling → co146_jlc_dfm_gate → co146_jlc_fab_package → co152_findings_disposition → co155_co154_findings_disposition → co156_co154_open_disposition → co157_gate_hardening_3 → co158_l5_packet_selfcontained → co159_rev19_co156_co157_co158_review → co160_co159_findings_disposition → co161_gap_hardening_4 → co162_verdict_binding → co163_binding_to_order_notes → co166_rev19_co159_co165_review → co167_co166_findings_disposition → co168_register_consistency → co169_step_output_oracle → co170_stackup_binding → co171_order_notes_record_figures → co172_rev19_co166_co171_review → co173_co172_findings_disposition → co174_step_artifact_attribution → co175_package_parity_binding → co176_gate_selfcheck_evidence → co177_capability_value_binding → co178_drc_item_limit_derivation → co179_sensitivity_teeth_hardening → co180_teeth_judgment_integrity → co124_input_selfcheck_gate → co150_k9_domain_gate → co146_boundary_append → co77_closure_declaration_sweep → co120_provenance_pin_gate → co146_boundary_append → co135_review_hygiene → co136_gate_hygiene → co78_layer_role_drift_gate → co81_project_rules_gate → co84_dru_domain_gate → co95_in4_reachability → co98_reachability_status_report → co106_reference_plane_gate → co146_boundary_append`，**循环至 sha 稳定**（收敛判定须遵 R-CO164-1 + R-CO165-1/2 + R-CO167-1/2 + R-CO169-1/2 + R-CO174-1 + R-CO175-1 + R-CO176-1/2 + R-CO177-1 + R-CO178-1 + R-CO179-1/2 + R-CO180-1/2 + R-CO181-1/2 + R-CO182-1 + R-CO183-1 + R-CO184-1 + R-CO185-1/2 + R-CO186-1 + R-CO187-1/2/3 + R-CO188-1）。

| 工件 | sha16 |
|---|---|
| 工具 `p3_v57_co164_order_runner.py`（CO-188.1 / `stray_write` 停机类 + `STRAY_WRITE_ALLOWED` + t22） | `db80604b81e805e9` |
| 登记簿 `input_defect_register_v1.json`（178 项 / OPEN 0） | `b1d8c7130240c4d0` |

## 62. CO-189（**L2 自裁 · 受控集外写入可见性**）

- **G-1（medium）·承载根内写入不可见**：步骤在受控产物**承载根**（`pm_gate/artifacts/k2_v4`）内写**非受控件**（不在 `watch_paths()`、无豁免）时，既不入收敛 sha、也不产生 `stray` 证据（stray 只比较受控集）⇒ **完全不可见**。CO-186 只覆盖 md 卡片、CO-188 只覆盖受控集**内**越界 ⇒ R-CO186-1「各步写出的全部产物须入受控集」的**受控集外**方向仍无判据。
- **实测钉定（本件证据）**：全序逐步 shadow 差分 ⇒ 仅 `co146_jlc_fab_package` 写受控集外 **32 件**（全在 `L5/jlc_package/`：Gerber 13 / Excellon 10 / 04_impedance 2 / `05_layer_sequence.txt` / 06_rulings 4）；其余 47 步 **0 件**。该 32 件由**受控 `MANIFEST.json` 的 `manifest` 键（34 件逐文件 sha256）**覆盖 ⇒ 豁免依据成立。
- **处置**：runner 升 **CO-189.1** —— ① `WRITE_SHADOW_ROOT` + **stat 轻量 shadow**（mtime/ctime/size，不哈希；承载根 ~1.8k 件逐步快照，成本 +~3s）；② `WRITE_SHADOW_EXEMPT`（5 前缀，各带 `why` + `covered_by`）；③ 纯判据 `shadow_exempt()`/`uncontrolled_decision()`；④ 运行时停机类 **`uncontrolled_write`**（对白名单步亦生效）；⑤ 静态齿 **t23**（shadow 根 ⊇ 受控集；豁免表完备 + 正负控）。
- **登记簿**：+1（`co189:G-1`，CLOSED；**178 项 / OPEN 0**）。

> **R-CO189-1**：步骤在承载根内的写入须**全部可见** —— 属受控集（收敛 sha/stray）或入 `WRITE_SHADOW_EXEMPT`（显式理由 + `covered_by` 受控件/牙齿）；否则运行时 `uncontrolled_write` 停机（t23 机判）。
> **R-CO189-2**（复现序，取代 R-CO188-2；**步集/序列不变，序内出现 50 次**）：规范复现序 = `co146_impedance_table → co146_pm_eval → co146_ledger_add → co153_k9_domain_coverage → co148_u6_datasheet_inputs → co148_thermal_ruling → co149_thermal_mitigation_derive → co147_l2_ruling → co146_jlc_dfm_gate → co146_jlc_fab_package → co152_findings_disposition → co155_co154_findings_disposition → co156_co154_open_disposition → co157_gate_hardening_3 → co158_l5_packet_selfcontained → co159_rev19_co156_co157_co158_review → co160_co159_findings_disposition → co161_gap_hardening_4 → co162_verdict_binding → co163_binding_to_order_notes → co166_rev19_co159_co165_review → co167_co166_findings_disposition → co168_register_consistency → co169_step_output_oracle → co170_stackup_binding → co171_order_notes_record_figures → co172_rev19_co166_co171_review → co173_co172_findings_disposition → co174_step_artifact_attribution → co175_package_parity_binding → co176_gate_selfcheck_evidence → co177_capability_value_binding → co178_drc_item_limit_derivation → co179_sensitivity_teeth_hardening → co180_teeth_judgment_integrity → co124_input_selfcheck_gate → co150_k9_domain_gate → co146_boundary_append → co77_closure_declaration_sweep → co120_provenance_pin_gate → co146_boundary_append → co135_review_hygiene → co136_gate_hygiene → co78_layer_role_drift_gate → co81_project_rules_gate → co84_dru_domain_gate → co95_in4_reachability → co98_reachability_status_report → co106_reference_plane_gate → co146_boundary_append`，**循环至 sha 稳定**（收敛判定须遵 R-CO164-1 + R-CO165-1/2 + R-CO167-1/2 + R-CO169-1/2 + R-CO174-1 + R-CO175-1 + R-CO176-1/2 + R-CO177-1 + R-CO178-1 + R-CO179-1/2 + R-CO180-1/2 + R-CO181-1/2 + R-CO182-1 + R-CO183-1 + R-CO184-1 + R-CO185-1/2 + R-CO186-1 + R-CO187-1/2/3 + R-CO188-1 + R-CO189-1）。

| 工件 | sha16 |
|---|---|
| 工具 `p3_v57_co164_order_runner.py`（CO-189.1 / 承载根 stat shadow + `uncontrolled_write` + `WRITE_SHADOW_EXEMPT` + t23） | `db80604b81e805e9` |
| 登记簿 `input_defect_register_v1.json`（178 项 / OPEN 0） | `b1d8c7130240c4d0` |

## 63. CO-190（**L2 自裁 · 步骤超时 fail-closed：复现序可靠性**）

- **G-1（low）·无步骤超时**：执行器对步骤 `subprocess.run` **无 `timeout`** ⇒ 任一挂起 / 无限迭代步使 runner **永久阻塞**而非 fail-closed（违「冲突即停机」精神；「禁暴力迭代」的症状面正是长跑/挂起）；且无逐步耗时证据可判「异常长跑」。
- **处置**：runner 升 **CO-190.1** —— ① `STEP_TIMEOUT_S = 300`（≫ 最慢合法步）；② `subprocess.run(timeout=)` ⇒ 超时**杀子进程** + 停机类 **`step_timeout`**（对白名单步亦生效，**优先于** verdict/teeth 判据）；③ 逐步 `duration_s` / `timed_out` 证据；④ 静态齿 **t24**（超时值带 60..3600 + 正控/负控）。
- **实测（本件证据）**：实现期端到端负控**抓到实现缺陷** —— 超时分支仍读未赋值的 `r.stderr` ⇒ `UnboundLocalError`（首轮负控 rc=1 但报告未写出）；已修为 `_err`。修复后负控：T=60（带内）+ 首步注入 120s 挂起 ⇒ **60.8s 后停 `class=step_timeout` / `timed_out=true`**；T=5（越带）⇒ 静态 t24 直接拒（`static_precheck_failed`），不上路。
- **登记簿**：+1（`co190:G-1`，CLOSED；**178 项 / OPEN 0**）。

> **R-CO190-1**：规范序每一步须在 `STEP_TIMEOUT_S` 内返回；超时 ⇒ 杀子进程 + `step_timeout` 停机（禁「永久阻塞」）；逐步耗时须记录（t24 机判超时值带 + 正负控）。
> **R-CO190-2**（复现序，取代 R-CO189-2；**步集/序列不变，序内出现 50 次**）：规范复现序 = `co146_impedance_table → co146_pm_eval → co146_ledger_add → co153_k9_domain_coverage → co148_u6_datasheet_inputs → co148_thermal_ruling → co149_thermal_mitigation_derive → co147_l2_ruling → co146_jlc_dfm_gate → co146_jlc_fab_package → co152_findings_disposition → co155_co154_findings_disposition → co156_co154_open_disposition → co157_gate_hardening_3 → co158_l5_packet_selfcontained → co159_rev19_co156_co157_co158_review → co160_co159_findings_disposition → co161_gap_hardening_4 → co162_verdict_binding → co163_binding_to_order_notes → co166_rev19_co159_co165_review → co167_co166_findings_disposition → co168_register_consistency → co169_step_output_oracle → co170_stackup_binding → co171_order_notes_record_figures → co172_rev19_co166_co171_review → co173_co172_findings_disposition → co174_step_artifact_attribution → co175_package_parity_binding → co176_gate_selfcheck_evidence → co177_capability_value_binding → co178_drc_item_limit_derivation → co179_sensitivity_teeth_hardening → co180_teeth_judgment_integrity → co124_input_selfcheck_gate → co150_k9_domain_gate → co146_boundary_append → co77_closure_declaration_sweep → co120_provenance_pin_gate → co146_boundary_append → co135_review_hygiene → co136_gate_hygiene → co78_layer_role_drift_gate → co81_project_rules_gate → co84_dru_domain_gate → co95_in4_reachability → co98_reachability_status_report → co106_reference_plane_gate → co146_boundary_append`，**循环至 sha 稳定**（收敛判定须遵 R-CO164-1 + R-CO165-1/2 + R-CO167-1/2 + R-CO169-1/2 + R-CO174-1 + R-CO175-1 + R-CO176-1/2 + R-CO177-1 + R-CO178-1 + R-CO179-1/2 + R-CO180-1/2 + R-CO181-1/2 + R-CO182-1 + R-CO183-1 + R-CO184-1 + R-CO185-1/2 + R-CO186-1 + R-CO187-1/2/3 + R-CO188-1 + R-CO189-1 + R-CO190-1）。

| 工件 | sha16 |
|---|---|
| 工具 `p3_v57_co164_order_runner.py`（CO-190.1 / `STEP_TIMEOUT_S` + `step_timeout` + 逐步 `duration_s` + t24） | `db80604b81e805e9` |
| 登记簿 `input_defect_register_v1.json`（178 项 / OPEN 0） | `b1d8c7130240c4d0` |

## 64. CO-191（**L2 自裁 · 判定基据完备性**）

- **G-1（low）·判定面不完备**：① `step_verdict`/`nonpass_decision` **只判首个**声明 verdict ⇒ 步骤其他声明产物（副记录 / 共享件）若含非 PASS verdict 可**静默逃逸**；② 普查 **23/48 步**「无 teeth、无 verdict」仅有 rc + `did_work` 判，其**判定基据未显式绑定**（新增此类步可静默无判 = CO-79「空真」在执行器层面的残余）。
- **处置**：runner 升 **CO-191.1** —— ① `declared_verdicts()` + `all_verdicts_decision()`：**全部**声明 verdict 一律判决（t19 现状 clause 同步）；② `judgment_basis()` + `JUDGMENT_DOWNSTREAM`（**显式**下游声明）+ 静态齿 **t25**（每步基据 ≠ none；下游声明须有理由且指向在序步；合成正负控）。
- **实测（本件证据）**：**端到端负控（旧↔新判别）** —— 注入副声明产物 `verdict=FAIL`（precheck PASS、FAIL 于**运行期**写出）⇒ 停 `class=undeclared_nonpass_verdict`；同时实测 `step_verdict`=**PASS**（旧路径**不判**）↔ `all_verdicts_decision`=**undeclared_nonpass**（新路径判）。预写失败 verdict 则由静态 t19 更早拦下。零基线冲击（现行 3 步多 verdict 产物均为通过档，见登记簿证据）。
- **登记簿**：+1（`co191:G-1`，CLOSED；**178 项 / OPEN 0**）。

> **R-CO191-1**：步骤判定基据须**可机判**（`teeth` / 声明产物 `verdict` / 登记簿自洽 / **显式下游** `JUDGMENT_DOWNSTREAM`）；且**全部**声明 verdict 一律判决（禁只判首个 ⇒ 隐藏非 PASS 逃逸）；t25 机判。
> **R-CO191-2**（复现序，取代 R-CO190-2；**步集/序列不变，序内出现 50 次**）：规范复现序 = `co146_impedance_table → co146_pm_eval → co146_ledger_add → co153_k9_domain_coverage → co148_u6_datasheet_inputs → co148_thermal_ruling → co149_thermal_mitigation_derive → co147_l2_ruling → co146_jlc_dfm_gate → co146_jlc_fab_package → co152_findings_disposition → co155_co154_findings_disposition → co156_co154_open_disposition → co157_gate_hardening_3 → co158_l5_packet_selfcontained → co159_rev19_co156_co157_co158_review → co160_co159_findings_disposition → co161_gap_hardening_4 → co162_verdict_binding → co163_binding_to_order_notes → co166_rev19_co159_co165_review → co167_co166_findings_disposition → co168_register_consistency → co169_step_output_oracle → co170_stackup_binding → co171_order_notes_record_figures → co172_rev19_co166_co171_review → co173_co172_findings_disposition → co174_step_artifact_attribution → co175_package_parity_binding → co176_gate_selfcheck_evidence → co177_capability_value_binding → co178_drc_item_limit_derivation → co179_sensitivity_teeth_hardening → co180_teeth_judgment_integrity → co124_input_selfcheck_gate → co150_k9_domain_gate → co146_boundary_append → co77_closure_declaration_sweep → co120_provenance_pin_gate → co146_boundary_append → co135_review_hygiene → co136_gate_hygiene → co78_layer_role_drift_gate → co81_project_rules_gate → co84_dru_domain_gate → co95_in4_reachability → co98_reachability_status_report → co106_reference_plane_gate → co146_boundary_append`，**循环至 sha 稳定**（收敛判定须遵 R-CO164-1 + R-CO165-1/2 + R-CO167-1/2 + R-CO169-1/2 + R-CO174-1 + R-CO175-1 + R-CO176-1/2 + R-CO177-1 + R-CO178-1 + R-CO179-1/2 + R-CO180-1/2 + R-CO181-1/2 + R-CO182-1 + R-CO183-1 + R-CO184-1 + R-CO185-1/2 + R-CO186-1 + R-CO187-1/2/3 + R-CO188-1 + R-CO189-1 + R-CO190-1 + R-CO191-1）。

| 工件 | sha16 |
|---|---|
| 工具 `p3_v57_co164_order_runner.py`（CO-191.1 / 全 verdict 全判 + `JUDGMENT_DOWNSTREAM` + t25） | `db80604b81e805e9` |
| 登记簿 `input_defect_register_v1.json`（178 项 / OPEN 0） | `b1d8c7130240c4d0` |

## 65. CO-192（**非执行者对抗复评 CO-187..CO-191 + L2 自裁处置**）

- **复评方**：context 归零的续接会话（满足「复评须另一会话，禁自评」）；对象钉 `52235b5`（`git show` 内存重放 ⇒ 结论**不随处置漂移**）。方法：正控 **V1..V8**（独立复算）+ 负控 **P1..P6c**（内存注入、零落盘、零坐标搜索）。verdict **PASS_WITH_FINDINGS**｜findings **4**（F-1..F-4，全 low）。
- **成立件（无 medium+）**：V1 牙齿棘轮零违规 + 逐工具齿数 ≥ pin；V2 md 产物 ∈ pin∪豁免、豁免绑实存补偿齿；V3 boundary 读取者全集 = 扫描步 ∪ 声明（互斥）；V4 越界写 fail-closed；V5 承载根 ⊇ 受控集 + 豁免完备；V6 超时 fail-closed + 子进程接线；V7 每步基据非 none + 下游声明合法；V8 冻结四源 4/4 + ORDER==boundary 序 + `--check` 全 True。
- **F-1（low）·牙齿棘轮形态仍漏计**：`|=`（AugAssign）/ 嵌套下标 `rec["teeth"][k]` / dict 推导 / `__setitem__` / Attribute（`self.teeth[k]`）/ 下标赋别名 一律 `n_teeth=0` ⇒ 恒真齿经这些形态加入不被 t18 截。**处置**：`teeth_hygiene_scan` 容器判据改**节点形态无关** + 6 类纳扫 + t18 合成正控扩展。
- **F-2（low）·md 写/拷形态仍漏计**：`Path.open(w)` / `shutil.move` / `os.replace|rename` 目的 `md_write_scan()`==[] ⇒ 该类 `.md` 可落出受控集、t20 不截（实测现行 ORDER 工具 0 命中 = 潜在面）。**处置**：补 3 类 + t20 正控扩展。
- **F-3（low）·boundary 读取者判据可绕过**：`D.open().read()` / `io.open(B).read()`（源内无 `read_text`/`read_bytes` 字面）判 False。**处置**：读指标补 `.read(` / `io.open(` + t21 正控扩展。
- **F-4（low）·全 verdict 判决对白名单步不生效**：主循环以 `if cls == "ok"` 为门槛 ⇒ `expected_nonzero` 步（`co146_jlc_dfm_gate`）的**副**声明 verdict 不被运行期判决（副值 ≠ 其声明 FAIL 的非 PASS 值即逃逸），违 R-CO191-1。**处置**：`all_verdicts_gate` —— **放行档**（`ok` **与** `expected_nonzero`）一律判全 verdict + t25 正负控扩展。
- **登记簿**：+4（`co192:F-1..F-4`，全 CLOSED；**178 项 / OPEN 0**）。

> **R-CO192-1**：静态扫描须**形态完备**（牙齿：下标/别名/AnnAssign/dict()/update/setdefault/`|=`/嵌套下标/推导/`__setitem__`/Attribute/下标赋别名；md 写：write_text/write_bytes/open(w)/`Path.open(w)`/copy*/`move`/`os.replace|rename`；boundary 读：read_text/read_bytes/`.read(`/`io.open`）；且**放行档一律判全声明 verdict**（`ok` **与** `expected_nonzero`）。
> **R-CO192-2**（复现序，取代 R-CO191-2；**步集/序列不变，序内出现 50 次**）：规范复现序 = `co146_impedance_table → co146_pm_eval → co146_ledger_add → co153_k9_domain_coverage → co148_u6_datasheet_inputs → co148_thermal_ruling → co149_thermal_mitigation_derive → co147_l2_ruling → co146_jlc_dfm_gate → co146_jlc_fab_package → co152_findings_disposition → co155_co154_findings_disposition → co156_co154_open_disposition → co157_gate_hardening_3 → co158_l5_packet_selfcontained → co159_rev19_co156_co157_co158_review → co160_co159_findings_disposition → co161_gap_hardening_4 → co162_verdict_binding → co163_binding_to_order_notes → co166_rev19_co159_co165_review → co167_co166_findings_disposition → co168_register_consistency → co169_step_output_oracle → co170_stackup_binding → co171_order_notes_record_figures → co172_rev19_co166_co171_review → co173_co172_findings_disposition → co174_step_artifact_attribution → co175_package_parity_binding → co176_gate_selfcheck_evidence → co177_capability_value_binding → co178_drc_item_limit_derivation → co179_sensitivity_teeth_hardening → co180_teeth_judgment_integrity → co124_input_selfcheck_gate → co150_k9_domain_gate → co146_boundary_append → co77_closure_declaration_sweep → co120_provenance_pin_gate → co146_boundary_append → co135_review_hygiene → co136_gate_hygiene → co78_layer_role_drift_gate → co81_project_rules_gate → co84_dru_domain_gate → co95_in4_reachability → co98_reachability_status_report → co106_reference_plane_gate → co146_boundary_append`，**循环至 sha 稳定**（收敛判定须遵 R-CO164-1 + R-CO165-1/2 + R-CO167-1/2 + R-CO169-1/2 + R-CO174-1 + R-CO175-1 + R-CO176-1/2 + R-CO177-1 + R-CO178-1 + R-CO179-1/2 + R-CO180-1/2 + R-CO181-1/2 + R-CO182-1 + R-CO183-1 + R-CO184-1 + R-CO185-1/2 + R-CO186-1 + R-CO187-1/2/3 + R-CO188-1 + R-CO189-1 + R-CO190-1 + R-CO191-1 + R-CO192-1）。

| 工件 | sha16 |
|---|---|
| 工具 `p3_v57_co164_order_runner.py`（CO-192.1 / 扫描形态完备 + `all_verdicts_gate` + t18/t20/t21/t25 扩展） | `db80604b81e805e9` |
| 登记簿 `input_defect_register_v1.json`（178 项 / OPEN 0） | `b1d8c7130240c4d0` |
| 复评件 `m13_v57_co192_rev19_co187_co191_review.json`（PASS_WITH_FINDINGS / 4） | `b58a374c337d75e8` |

## 66. CO-193（**L2 自裁 · 声明↔实现绑定的可执行性**）

- **G-1（low）·下游声明只查形状、无方向/可执行机判**：`JUDGMENT_DOWNSTREAM` 旧判据仅 `why` 非空 + `ref` 非空 list + `ref ⊆ ORDER`。实测负控：ref 改为**上游**步 `co146_impedance_table`（位 0，声明步位 37/40/49）⇒ 旧 t25 仍 True；ref 改为**不引用** boundary 的 `co136_gate_hygiene` ⇒ 旧 t25 仍 True。⇒ 任一步可被声明「由下游判」而实际**无步判它**，静默逃逸 t25。
- **G-2（low）·白名单证据未本步绑定**：`record` 只须 ∈ `watch_paths()`（t09）而**不须** ∈ `STEP_ARTIFACTS[step]` ⇒ 证据记录可指向**他步**产物（实测旧 t09 仍 True，步本地归因/新鲜度测错件）；`teeth_path` 只须**键存在**（t14）而不须在记录内**可解析** ⇒ 坏 key 时 `_tcand` 过滤 None 后**静默回落**到 `step_declared_teeth`（自检判据降级）。
- **G-3（low）·复评件内嵌处置态 sha ⇒ 记录漂移（已闭缺陷类复发）**：CO-192 复评件 `as_found` 内嵌 `runner_current_sha16`，实测改 runner 后同命令重跑得**另一记录 sha**（`db887764c8693176` → `2e43deda4f73fd76`）；该 sha 已入 §65 pin 表 ⇒ 复跑即失配。违 CO-152 已闭规则「新记录不得再嵌下游 sha 快照」（先例 `records_snapshot_downstream_sha_causes_pin_drift`）。
- **G-4（low）·守卫命名面盲区**：co120 `_is_downstream_snapshot()` 只认 `*_sha16_after` + `register/ledger` 面 ⇒ 显式现行态键（`*_current_sha16` …）漏判，使 G-3 逃逸（corpus 全扫仅此 1 处）。
- **处置**：① runner 升 **CO-193.1** —— `JUDGMENT_DOWNSTREAM` 每条增 `artifact`（被judged工件 basename）；新增 `downstream_refs_after()`（多次出现**存在性**方向判据）+ `judgment_downstream_binding()`（缺件/方向错/ref 不引用工件 ⇒ fail-closed）；`artifact_readers()` 为**语法代理**（basename 字面 **或** 可 `fnmatch` 命中的 glob）；新增 `expected_nonzero_binding()`（`record` ∈ `STEP_ARTIFACTS[step]`；`teeth_path` 经 `record_json_path()` 可解析）；静态齿 **t26**（正控 + 方向/可执行/不完整/多出现/坏证据 负控）。② 复评件回归 **as-found 证据**语义（去 `runner_current_sha16`；处置态 sha 由 boundary pin 表承载），改后复评命令**幂等**（`b58a374c337d75e8`）。③ co120 升 **CO-120.6** —— 新增 `_DOWNSTREAM_LIVE_KEY_RE` + 负控/正控/对偶控（上游输入 pin 不得误报）；**残余如实登记**：键名启发式，改名仍可逃逸（触发 = 记录随复现序漂移事件）。
- **登记簿**：+4（`co193:G-1..G-4`，全 CLOSED；**178 项 / OPEN 0**）。
- **实测（本件证据）**：修后真声明 `judgment_downstream_binding`=**ok**、`expected_nonzero_binding`=**ok**、co120.6 verdict=**PASS**（`n_snapshot_undeclared`=0）；`--check` **t01..t26 全 True（28 项）**。**实现期自捕获**：`artifact_readers` 初版按 basename 子串匹配 **漏 co77**（其经 `…_v1_*.md` glob 定位最新版）⇒ 真声明被误判 `refs_not_reading_artifact`；改 glob-aware 后计入。
- **注**：本件含**对既有复评件（CO-192 产物）的稳定性修正**（G-3），非对 CO-192 的复评 ⇒ CO-192 复评债**不因此清偿**。

> **R-CO193-1**：`JUDGMENT_DOWNSTREAM` 下游声明须**可执行** —— 每条给被judged工件 basename，ref 须在序内**晚于**声明步（多次出现取**存在性**）且 ref 步工具**确实引用**该工件（字面或可 `fnmatch` 的 glob）；否则 fail-closed；t26 机判。
> **R-CO193-2**：`EXPECTED_NONZERO` 证据须**本步绑定** —— `record` ∈ `STEP_ARTIFACTS[step]` 且 `teeth_path` 在记录内**可解析**；否则 fail-closed；t26 机判。
> **R-CO193-3**：证据/复评件只钉**被评对象（as-found）**；处置态/跨件**现行** sha 一律由 boundary pin 表承载，**禁内嵌**（CO-152 规则）；复评件须**幂等**（同命令重跑逐字节相同）。
> **R-CO193-4**：下游快照键的**命名面**须由 co120 判据 + 合成控覆盖（含**上游输入 pin 不得误报**对偶）；新命名形态须先入判据；键名启发式为**如实登记之残余**。
> **R-CO193-5**（复现序，取代 R-CO192-2；**步集/序列不变，序内出现 50 次**）：规范复现序 = `co146_impedance_table → co146_pm_eval → co146_ledger_add → co153_k9_domain_coverage → co148_u6_datasheet_inputs → co148_thermal_ruling → co149_thermal_mitigation_derive → co147_l2_ruling → co146_jlc_dfm_gate → co146_jlc_fab_package → co152_findings_disposition → co155_co154_findings_disposition → co156_co154_open_disposition → co157_gate_hardening_3 → co158_l5_packet_selfcontained → co159_rev19_co156_co157_co158_review → co160_co159_findings_disposition → co161_gap_hardening_4 → co162_verdict_binding → co163_binding_to_order_notes → co166_rev19_co159_co165_review → co167_co166_findings_disposition → co168_register_consistency → co169_step_output_oracle → co170_stackup_binding → co171_order_notes_record_figures → co172_rev19_co166_co171_review → co173_co172_findings_disposition → co174_step_artifact_attribution → co175_package_parity_binding → co176_gate_selfcheck_evidence → co177_capability_value_binding → co178_drc_item_limit_derivation → co179_sensitivity_teeth_hardening → co180_teeth_judgment_integrity → co124_input_selfcheck_gate → co150_k9_domain_gate → co146_boundary_append → co77_closure_declaration_sweep → co120_provenance_pin_gate → co146_boundary_append → co135_review_hygiene → co136_gate_hygiene → co78_layer_role_drift_gate → co81_project_rules_gate → co84_dru_domain_gate → co95_in4_reachability → co98_reachability_status_report → co106_reference_plane_gate → co146_boundary_append`，**循环至 sha 稳定**（收敛判定须遵 R-CO164-1 + R-CO165-1/2 + R-CO167-1/2 + R-CO169-1/2 + R-CO174-1 + R-CO175-1 + R-CO176-1/2 + R-CO177-1 + R-CO178-1 + R-CO179-1/2 + R-CO180-1/2 + R-CO181-1/2 + R-CO182-1 + R-CO183-1 + R-CO184-1 + R-CO185-1/2 + R-CO186-1 + R-CO187-1/2/3 + R-CO188-1 + R-CO189-1 + R-CO190-1 + R-CO191-1 + R-CO192-1 + R-CO193-1/2/3/4）。

| 工件 | sha16 |
|---|---|
| 工具 `p3_v57_co164_order_runner.py`（CO-193.1 / 下游声明可执行 + 白名单证据本步绑定 + t26） | `db80604b81e805e9` |
| 工具 `p3_v57_co120_provenance_pin_gate.py` + 记录（CO-120.6 / 现行态键判据 + 对偶控） | `28d6211f32318d9b` |
| 复评件 `m13_v57_co192_rev19_co187_co191_review.json`（去处置态 sha ⇒ as-found 幂等） | `b58a374c337d75e8` |
| 登记簿 `input_defect_register_v1.json`（178 项 / OPEN 0） | `b1d8c7130240c4d0` |

## 67. CO-194（**L2 自裁 · 基据↔判官 + 声明↔工具能力**）

- **H-1（low，latent）·基据类别无判官绑定**：`judgment_basis()` 的 `register_consistency` 类别仅凭 `_REG ∈ STEP_ARTIFACTS[step]` 认定，**未绑定任何判官**（登记簿自洽实际由 co124 机判）。实测：该分支当前**不可达** —— `judgment_basis` 分布 = {teeth:19, verdict:28, downstream:1, register_consistency:**0**}（27 个写登记簿步皆先命中 `verdict` ⇒ 死码）；且把 co124 移出 ORDER 后 `all(basis != none)` 仍 True ⇒ **无判官亦成立**。一旦该分支可达（某步只写登记簿而无 teeth/verdict），其基据即空真，违 t25「每步须有可机判基据」之目的。
- **H-2（low）·白名单声明与工具能力无静态绑定**：`EXPECTED_NONZERO` 的 `verdict` 只受形状约束（非 PASS + 运行期记录一致），**不要求**该字面出现在该步**工具源**内。实测：伪造 `verdict=TOTALLY_BROKEN` / `ERROR` ⇒ 旧静态条款（t03/t07/t09/t14）**全过**（仅运行期以 `expected_step_verdict_mismatch` fail-closed ⇒ 声明面未绑定、诊断滞后到执行期）。
- **处置**：runner 升 **CO-194.1** —— ① 新增 `BASIS_JUDGE_DECLARED`（每基据类别显式声明判定机制；外部判官须在序内、须**读**被judged件、且**自身有机判基据**）+ 纯函数 `basis_judge_decision()`（`register_consistency` 判官 = `co124_input_selfcheck_gate`）；② 新增 `declared_verdict_in_tool()`（声明 verdict 字面须 ∈ 该步工具源）；③ 静态齿 **t27**（正控 + 判官不在序/不读件/自身无基据/声明不完整/伪造 verdict 负控）。
- **登记簿**：+2（`co194:H-1/H-2`，全 CLOSED；**178 项 / OPEN 0**）。
- **实测（本件证据）**：修后 `basis_judge_decision` 四类别全 **ok**、`declared_verdict_in_tool('co146_jlc_dfm_gate', FAIL)`=True（零基线冲击）；`--check` **t01..t27 全 True（29 项）**。

> **R-CO194-1**：每个**基据类别**须显式声明其判定机制（`BASIS_JUDGE_DECLARED`）；外部判官须**在序内**、**读被judged件**、且**自身有机判基据**；否则 fail-closed；t27 机判。
> **R-CO194-2**：`EXPECTED_NONZERO` 声明的 verdict 字面须出现在该步**工具源**（声明不得指向工具不可能产出的 verdict）；t27 机判。
> **R-CO194-3**（复现序，取代 R-CO193-5；**步集/序列不变，序内出现 50 次**）：规范复现序 = `co146_impedance_table → co146_pm_eval → co146_ledger_add → co153_k9_domain_coverage → co148_u6_datasheet_inputs → co148_thermal_ruling → co149_thermal_mitigation_derive → co147_l2_ruling → co146_jlc_dfm_gate → co146_jlc_fab_package → co152_findings_disposition → co155_co154_findings_disposition → co156_co154_open_disposition → co157_gate_hardening_3 → co158_l5_packet_selfcontained → co159_rev19_co156_co157_co158_review → co160_co159_findings_disposition → co161_gap_hardening_4 → co162_verdict_binding → co163_binding_to_order_notes → co166_rev19_co159_co165_review → co167_co166_findings_disposition → co168_register_consistency → co169_step_output_oracle → co170_stackup_binding → co171_order_notes_record_figures → co172_rev19_co166_co171_review → co173_co172_findings_disposition → co174_step_artifact_attribution → co175_package_parity_binding → co176_gate_selfcheck_evidence → co177_capability_value_binding → co178_drc_item_limit_derivation → co179_sensitivity_teeth_hardening → co180_teeth_judgment_integrity → co124_input_selfcheck_gate → co150_k9_domain_gate → co146_boundary_append → co77_closure_declaration_sweep → co120_provenance_pin_gate → co146_boundary_append → co135_review_hygiene → co136_gate_hygiene → co78_layer_role_drift_gate → co81_project_rules_gate → co84_dru_domain_gate → co95_in4_reachability → co98_reachability_status_report → co106_reference_plane_gate → co146_boundary_append`，**循环至 sha 稳定**（收敛判定须遵 R-CO164-1 + R-CO165-1/2 + R-CO167-1/2 + R-CO169-1/2 + R-CO174-1 + R-CO175-1 + R-CO176-1/2 + R-CO177-1 + R-CO178-1 + R-CO179-1/2 + R-CO180-1/2 + R-CO181-1/2 + R-CO182-1 + R-CO183-1 + R-CO184-1 + R-CO185-1/2 + R-CO186-1 + R-CO187-1/2/3 + R-CO188-1 + R-CO189-1 + R-CO190-1 + R-CO191-1 + R-CO192-1 + R-CO193-1/2/3/4 + R-CO194-1/2）。

| 工件 | sha16 |
|---|---|
| 工具 `p3_v57_co164_order_runner.py`（CO-194.1 / 基据↔判官 + 声明↔工具 + t27） | `db80604b81e805e9` |
| 登记簿 `input_defect_register_v1.json`（178 项 / OPEN 0） | `b1d8c7130240c4d0` |

## 68. CO-195（**L2 自裁 · 固定点唯一性（路径无关）oracle**）

- **I-1（low）·键名判据所欲保证的语义性质无独立闸**：co120 P5「下游快照」为**键名启发式**（`*_sha16_after` / `*_current_sha16` / register|ledger 面），其真正要防的失效模式（CO-151：按文档化序连跑两遍得**另一稳定不动点** ⇒ 提交 pin 不可复现）**无任何闸直接判**。实测**值域判据不可行**：35 条记录内嵌**受控集**未来 sha，但绝大多数是**冻结历史件 / 自身产物**的合法 pin（co16/co37/co69/co95/co98 之 record pin、各步 `doc_sha16` / `stackup_svg_sha16` / `pm_eval.sha16`）⇒ 值域判据会大面积误报，**不可机判为非法**。
- **处置**：新增 `tools/p3_v57_co195_fixpoint_uniqueness_oracle.py`（**不在规范序内**）—— 直接判**语义性质**：从**扰动态**启动规范序（登记簿 `meta.counts` 注入越界值 999/OPEN 7）⇒ 要求 rc=0 + converged + `snapshot()` 复原规范 sha + 登记簿**逐字节**复原；6 牙齿 = 注入有效 / 收敛 rc=0 / 不动点复原 / 登记簿逐字节复原 / **判别力**合成控（唯一 vs 非唯一不动点模型）/**排除非空转**。工具**自我保护**：`finally` 无条件复原登记簿（绝不留在扰动态）。co120 键名判据作**廉价前置代理**保留（不倒桩），语义保证由本 oracle 承载。
- **I-2（low）·oracle 记录自指 + §68 误 pin 可变件（自捕获）**：初版 oracle 的判据快照含**本记录自身** ⇒ 记录写回后自身字节即变，记录的 `sha_canon` **永不等于**其所在状态的实际 sha（实测 `2d23a14ffdc821cd` ≠ `6c282601e50911d5`）；且 §68 初版 pin 了该记录 ⇒ oracle 重跑后 `boundary_append` 以新记录 sha 重 pin ⇒ **规范序不动点随「oracle 是否刚跑」漂移**（实测 boundary `6608cd8e`→`3e5ca535`、co77 `137b4949`→`c8ffe1ce` 双件漂移）。**处置**：① oracle 判据快照**排除本记录自身**（自指防护）+ 记录声明 `snapshot_scope` + 牙齿 `t06_self_exclusion_nonvacuous`；② §68 **不 pin** 该记录（同 runner report 先例：随规范态变化的证据件不入 pin 表）。
- **登记簿**：+2（`co195:I-1` + `co195:I-2`，全 CLOSED；**178 项 / OPEN 0**）。
- **实测（本件证据）**：`sha_canon`=`f48af2c1a41de4c6` → 注入后 `sha_perturbed`=`880d1ec8cbc27698` → 跑序后 `sha_after`=`f48af2c1a41de4c6`（**逐字节复原**、rc=0 / converged / 2 轮）。**残余如实登记**：本 oracle 只扰**一个**扰动量（登记簿 counts）⇒ 未覆盖的路径相关性（如未来新形态的自指 pin）须**扩扰动量**；触发 = 出现新的自指/链式 pin 写法。

> **R-CO195-0**（I-2）：**随规范态变化的证据件不得入 pin 表**（oracle/runner 报告类）；判据快照须**排除证据件自身**（自指防护）。
> **R-CO195-1**：规范序的**不动点唯一性（路径无关）**须由 `co195` oracle 直接判（扰动启动 ⇒ 收敛须复原规范态 + 逐字节复原件）；键名判据仅为**前置代理**，不得替代语义判据；新自指/链式 pin 形态须扩扰动量。
> **R-CO195-2**（复现序，取代 R-CO194-3；**步集/序列不变，序内出现 50 次**）：规范复现序 = `co146_impedance_table → co146_pm_eval → co146_ledger_add → co153_k9_domain_coverage → co148_u6_datasheet_inputs → co148_thermal_ruling → co149_thermal_mitigation_derive → co147_l2_ruling → co146_jlc_dfm_gate → co146_jlc_fab_package → co152_findings_disposition → co155_co154_findings_disposition → co156_co154_open_disposition → co157_gate_hardening_3 → co158_l5_packet_selfcontained → co159_rev19_co156_co157_co158_review → co160_co159_findings_disposition → co161_gap_hardening_4 → co162_verdict_binding → co163_binding_to_order_notes → co166_rev19_co159_co165_review → co167_co166_findings_disposition → co168_register_consistency → co169_step_output_oracle → co170_stackup_binding → co171_order_notes_record_figures → co172_rev19_co166_co171_review → co173_co172_findings_disposition → co174_step_artifact_attribution → co175_package_parity_binding → co176_gate_selfcheck_evidence → co177_capability_value_binding → co178_drc_item_limit_derivation → co179_sensitivity_teeth_hardening → co180_teeth_judgment_integrity → co124_input_selfcheck_gate → co150_k9_domain_gate → co146_boundary_append → co77_closure_declaration_sweep → co120_provenance_pin_gate → co146_boundary_append → co135_review_hygiene → co136_gate_hygiene → co78_layer_role_drift_gate → co81_project_rules_gate → co84_dru_domain_gate → co95_in4_reachability → co98_reachability_status_report → co106_reference_plane_gate → co146_boundary_append`，**循环至 sha 稳定**（收敛判定须遵 R-CO164-1 + R-CO165-1/2 + R-CO167-1/2 + R-CO169-1/2 + R-CO174-1 + R-CO175-1 + R-CO176-1/2 + R-CO177-1 + R-CO178-1 + R-CO179-1/2 + R-CO180-1/2 + R-CO181-1/2 + R-CO182-1 + R-CO183-1 + R-CO184-1 + R-CO185-1/2 + R-CO186-1 + R-CO187-1/2/3 + R-CO188-1 + R-CO189-1 + R-CO190-1 + R-CO191-1 + R-CO192-1 + R-CO193-1/2/3/4 + R-CO194-1/2 + R-CO195-1）。

| 工件 | sha16 |
|---|---|
| 工具 `p3_v57_co195_fixpoint_uniqueness_oracle.py`（扰动启动 ⇒ 复原规范态 + 7 牙齿：结算/注入/收敛/复原/逐字节/判别力/自排除） | `585b983de844603d` |
| 登记簿 `input_defect_register_v1.json`（178 项 / OPEN 0） | `b1d8c7130240c4d0` |

> **注（I-2）**：证据件 `m13_v57_co195_fixpoint_uniqueness.json`（**不被 pin**：内容随规范态变化，同 runner report 先例）

## 69. CO-196（**L2 自裁 · 验证循环修正 + 扩扰动量**）

- **J-1（medium）·验证循环 ⇒ 不可恢复锁死**：CO-195 的静态齿 **t28** 以 oracle **证据件的 `verdict`** 为输入，而 oracle 自身**前置「先结算」**（须规范序成功跑通），规范序的静态前置**又包含 t28** ⇒ 证据件一旦 FAIL（或损坏/缺失）即：t28 拒 ⇒ `aborted=static_precheck_failed` ⇒ oracle 无法运行 ⇒ **永久无法自愈**（须人工改记录）。**实测复现**：某次 oracle FAIL 后，`--check` t28=False、order 报 `static_precheck_failed`、oracle 连跑 **1.7s** 即 `t00_settle_converged=False`（全部案牙齿 False）。属「**验证者以被验证证据为前置**」反模式。
- **J-2（low）·单扰动量覆盖面不足（触发达成）**：z60 §4 已裁定「co195 只扰一个扰动量 ⇒ 未覆盖的路径相关性须扩扰动量；触发 = 出现新的自指/链式 pin 写法」。该触发**已发生** —— CO-195 的 I-2（oracle 证据自指 + §68 误 pin 可变件）正是自指/链式 pin 实例，而单扰动量（仅登记簿 counts）无法在扰动实验内暴露该类。
- **处置**：① runner 升 **CO-196.2** —— t28 改**结构性**判据 `oracle_tool_ok(path)`（**只判工具存在 + 可编译**，**不读证据件**）+ **逐分支可证伪负控**（缺件 / 语法错各一，见 J-4）；证据件 PASS 由 oracle 自身与复核清单承载。② oracle 扩为**多扰动量 3 案** —— A 登记簿 `meta.counts`；B **单个 ORDER 步自持记录**注入；C **双件同时**注入；每案独立要求「收敛 rc=0 + 目标件**逐字节**复原 + 排除自身快照复原」，**任一案失败即停**；牙齿 8 项；逐案 `finally` 无条件复原。
- **J-3（low）·证据件仍含自指字段 ⇒ 非幂等（I-2 同族更深层）**：I-2 只修**判据快照**，却仍在记录里落盘 `sha_incl_self = snapshot()`（**含证据件自身**）⇒ 记录内容依赖自身字节 ⇒ **非幂等**（实测连跑 `3f1f9b37869f93ea` → `35549fe1c938139b`）；因该件不入 pin 表而不破收敛，但**证据不可复现、误导复核**。处置：移除该字段（含自身的 sha 一律不落盘），只落**布尔** `t06` 结论 ⇒ 连跑恒 `5d8f953c12dafba0`（幂等）。
- **J-4（low）·t28 合成负控**恒真**（不可证伪）**（续接会话自捕获）：J-1 声称「附可证伪负控（不存在 / 语法错 ⇒ False）」，实现却是 `not oracle_tool_ok(tools/__bad_oracle__.py)` —— 该文件在任何规范态下**都不存在**（无序内步创建）⇒ 该控只**重复**「缺件 ⇒ False」分支（FileNotFoundError），**语法错分支（SyntaxError）从未被行使** ⇒ 声称的可证伪不成立。处置：新增**纯内存**判据 `src_compiles(src, name)`（`compile()`，**不触盘**），t28 改**逐返回路径**各一控：缺件 `not oracle_tool_ok(<不存在>)`、**语法错** `not src_compiles(<非法源>)`、正控 `src_compiles(<合法源>)`；`oracle_tool_ok` 复用 `src_compiles`。
- **J-5（low）·处置工具注解 upsert 被存在性守卫吞掉**（续接会话自捕获）：`co196_findings_disposition.py` 以「CO-196 标记 ∈ updated_by?」为守卫追加注解 ⇒ 注解文本变更（+2 → +3）后**不重写** ⇒ `meta.updated_by` **停留在旧文本**（实测 3 条 co196 条目而注解仍称「+2」）。处置：改**可重入** upsert（trim 旧 CO-196 注解段 + append 现注解）⇒ 幂等且注解恒与 `ADD` 一致。
- **登记簿**：+5（`co196:J-1`(medium) / `J-2`,`J-3`,`J-4`,`J-5`(low)，全 CLOSED；**178 项 / OPEN 0**）。
- **实测（本件证据）**：3 案 `injection_effective` / `order_converged` / `targets_byte_restored` / `snapshot_restored` **全 True**（`sha_canon`=`59772fb78183d518`）；修后同一 FAIL 证据件下 `--check` 全 True、order 正常跑通 ⇒ oracle **可自愈**；`--check` **t01..t28 全 True（30 项）**。证据件 `m13_v57_co195_fixpoint_uniqueness.json` 仍**不入 pin 表**（R-CO195-0）。

> **R-CO196-1**（红线）：**静态闸不得以被验证证据为输入**（禁验证循环）—— `--check` 只判**结构性事实**（文件存在/可编译/集合关系）；证据件内容（verdict / sha）一律不作 `--check` 输入；否则证据 FAIL 即锁死验证链。
> **R-CO196-1b**：证据/报告类工件**不得落盘任何含自身的 sha**（自指字段一律换成布尔结论），并须**逐案验证幂等**（连跑记录 sha 不变）。
> **R-CO196-4**：合成正/负控须与被测判据的**每条返回路径一一对应**（缺件 / 语法错 / 类型错 各一）—— **不得以「不存在的路径」冒充某一分支**（恒真控）；且 `--check` 类静态判据须**零落盘副作用**。
> **R-CO196-5**：meta 注解类 upsert 须**可重入**（先 trim 旧注解段再 append 现注解），使重复运行**幂等**且**自述恒与条目实况一致**；不得依赖「标记存在即跳过」。
> **R-CO196-2**：不动点唯一性 oracle 须**多扰动量**（≥ 跨件 pin 链 + 单步自持记录 + 双件交互），逐案独立判「收敛 + 逐字节复原 + 快照复原」，任一案失败即停；新增扰动量须入 `CASES`。
> **R-CO196-3**（复现序，取代 R-CO195-2；**步集/序列不变，序内出现 50 次**）：规范复现序 = `co146_impedance_table → co146_pm_eval → co146_ledger_add → co153_k9_domain_coverage → co148_u6_datasheet_inputs → co148_thermal_ruling → co149_thermal_mitigation_derive → co147_l2_ruling → co146_jlc_dfm_gate → co146_jlc_fab_package → co152_findings_disposition → co155_co154_findings_disposition → co156_co154_open_disposition → co157_gate_hardening_3 → co158_l5_packet_selfcontained → co159_rev19_co156_co157_co158_review → co160_co159_findings_disposition → co161_gap_hardening_4 → co162_verdict_binding → co163_binding_to_order_notes → co166_rev19_co159_co165_review → co167_co166_findings_disposition → co168_register_consistency → co169_step_output_oracle → co170_stackup_binding → co171_order_notes_record_figures → co172_rev19_co166_co171_review → co173_co172_findings_disposition → co174_step_artifact_attribution → co175_package_parity_binding → co176_gate_selfcheck_evidence → co177_capability_value_binding → co178_drc_item_limit_derivation → co179_sensitivity_teeth_hardening → co180_teeth_judgment_integrity → co124_input_selfcheck_gate → co150_k9_domain_gate → co146_boundary_append → co77_closure_declaration_sweep → co120_provenance_pin_gate → co146_boundary_append → co135_review_hygiene → co136_gate_hygiene → co78_layer_role_drift_gate → co81_project_rules_gate → co84_dru_domain_gate → co95_in4_reachability → co98_reachability_status_report → co106_reference_plane_gate → co146_boundary_append`，**循环至 sha 稳定**（收敛判定须遵 R-CO164-1 + R-CO165-1/2 + R-CO167-1/2 + R-CO169-1/2 + R-CO174-1 + R-CO175-1 + R-CO176-1/2 + R-CO177-1 + R-CO178-1 + R-CO179-1/2 + R-CO180-1/2 + R-CO181-1/2 + R-CO182-1 + R-CO183-1 + R-CO184-1 + R-CO185-1/2 + R-CO186-1 + R-CO187-1/2/3 + R-CO188-1 + R-CO189-1 + R-CO190-1 + R-CO191-1 + R-CO192-1 + R-CO193-1/2/3/4 + R-CO194-1/2 + R-CO195-0/1 + R-CO196-1/2/4/5）。

| 工件 | sha16 |
|---|---|
| 工具 `p3_v57_co164_order_runner.py`（CO-196.2 / t28 结构性 + J-4 逐分支可控） | `db80604b81e805e9` |
| 工具 `p3_v57_co195_fixpoint_uniqueness_oracle.py`（多扰动量 3 案 + 8 牙齿） | `585b983de844603d` |
| 登记簿 `input_defect_register_v1.json`（178 项 / OPEN 0） | `b1d8c7130240c4d0` |

## 70. CO-197（**非执行者对抗复评 CO-192..CO-195 + L2 自裁处置**）

- **复评方**：context 归零的续接会话（满足「复评须另一会话，禁自评」—— 本会话未参与 CO-192..CO-195 之创作）；对象钉 `5e6ddde`（CO-195 定稿件），逐件 as-found 另取 `52235b5`（CO-192）/ `3e4f747`（CO-193）/ `334ed74`（CO-194）；`git show` **内存重放** ⇒ 结论**不随后续处置漂移**。方法：正控 **V1..V8**（独立复算）+ 负控 **P1..P6c**（内存注入、**零落盘**、零坐标搜索）。verdict **PASS_WITH_FINDINGS**｜findings **2**（K-1/K-2，全 low）。
- **成立件（无 medium+；CO-192..CO-195 之处置经独立复算成立）**：V1 牙齿棘轮现行零违规 + 逐工具齿数 ≥ pin + 全列形态纳扫；V2 md 产物 = pin ∪ 豁免、豁免绑实存补偿齿；V3 boundary 读取者全集 = 扫描步 ∪ 声明（互斥）；V4 放行档（`ok` **与** `expected_nonzero`）一律判**全**声明 verdict；V5 `judgment_downstream_binding` 全 ok + 方向/可执行负控；V6 `expected_nonzero_binding` 全 ok + 错件/坏键负控；V7 `basis_judge_decision` 四类别全 ok + 声明 verdict 须在**工具源**；V8 冻结四源 4/4 + ORDER==boundary 序 + `--check` 全 True + oracle 工具可编译、证据件 PASS 且 teeth 全 True、**无自指字段**（R-CO195-0 / R-CO196-1b）。负控 P1..P6c 全 True（as-found 漏 ↔ 现行抓）。
- **K-1（low）·牙齿扫描漏计关键字解包形态**：`teeth_hygiene_scan` 对 `dict(**{"t01": True})` 与 `teeth.update(**{"t01": True})`（AST `keyword.arg is None`）一律 `n_teeth=0` ⇒ 经该形态加入的**恒真齿**既不被计数、亦不被 constancy 检 ⇒ t18 的「逐工具齿数下限 + 常量齿零违规」一并被绕过。R-CO192-1 列举 `dict(...)` / `.update(...)` 为受覆盖形态，其**解包子形态**未实现 ⇒ 「**全部**容器形态」为过强声明。**复评实测**：as-found `52235b5` 与 `5e6ddde` 均 `n_teeth=0`（CO-192.1 未闭合）。
- **K-2（low）·md 写/拷扫描漏计同族形态**：`md_write_scan` 对 `io.open(<md>, "w")`、`Path(...).replace|rename(<md>)` 及**路径别名** `P = Path(...); P.replace|rename(<md>)` 一律 `==[]` ⇒ 此类 `.md` 产物既不入 pin、t20 亦不截（可落出受控集）；且 `io.open` 在 **boundary 读取**侧已纳扫、**md 写**侧未覆盖（**不对称**）。**复评实测**：as-found `52235b5` 与 `5e6ddde` 均 `==[]`（CO-192.1 未闭合）。
- **观察 O-1（不改判 verdict；已由 CO-196 登记关闭，不重复计数）**：as-found `5e6ddde` 的静态齿 t28 以 oracle **证据件 verdict** 为输入 ⇒ 与 oracle 前置「先结算」构成**验证循环**（证据 FAIL 即不可恢复锁死）；本次复评以负控 P4 **独立复现**（`oracle_record_ok` 存在于 as-found、现行只判结构性）。
- **处置**：runner 升 **CO-197.1** —— ① `teeth_hygiene_scan` 补关键字**解包**形态（`dict(**{...})` / `.update(**{...})`）；② `md_write_scan` 补 `io.open(<md>, "w")` 与 `Path(...)`/路径别名 `.replace|rename(<md>)` 目的；t18/t20 合成控同步扩展（含 `"a.md".replace(".md","")` **字符串操作不得误报**、只读 `io.open` 不得误报之**对偶负控**）。
- **K-3（low，本件**实现期自捕获**）·注解 upsert 段边界**：J-5 把注解 upsert 改为「trim 旧段 + append」，而 trim 取 `updated_by[:index(标记)]`（**裁到末尾**）⇒ 其后另有 CO 追加注解时，重跑本 CO 的 disposition 会连同**他人注解段一并静默删除**（实测：co197 注解写入后再跑 co196 disposition ⇒ `；**CO-197（…）**` 整段消失，条目 `co197:K-1/K-2` 仍在）；且「裁掉再追加」会把本段**移到末尾** ⇒ 登记簿 sha 随「最后跑的是哪个 CO」而变（**顺序敏感、不可复现**）。处置：改**原位替换**（右界 = 下一 `；**CO-` 起点 / 末尾），两件同步落地。
- **登记簿**：+3（`co197:K-1`,`K-2`,`K-3`，全 low、全 CLOSED；**178 项 / OPEN 0**）。
- **实测（本件证据）**：复评件**幂等**（连跑记录 sha 恒 `de625cb63e0df8f5`）；K-1 两形态修后 `n_teeth=1` 且报常量齿、K-2 三形态修后分别 `==["probe.md"]` / `==["dst.md"]` / `==["dst.md"]`；**零误报核对**：现行 ORDER 全工具的 md 命中集与齿数**逐工具不变**；co196 ↔ co197 注解 upsert **交替重跑**（两种次序）⇒ 登记簿 sha **恒定**（顺序无关幂等）、两段注解保位；`--check` **t01..t28 全 True（30 项）**。

> **R-CO197-1**：静态扫描器的「已列形态」须**逐子形态**落地并合成控覆盖 —— `keyword.arg is None`（`**` 解包）等子形态属必测集；漏计即停机（同族 R-CO192-1 之收严）。
> **R-CO197-2**：md 写/拷形态须覆盖 **builtins / io / pathlib** 三族**及其别名**；新增形态须同时补**对偶负控**（字符串操作、只读引用**不得误报**）。
> **R-CO197-4**：注解类 upsert 须**原位**改**本段**（右界 = 下一 `；**CO-` 注解起点 / 末尾）—— **禁**无界裁尾（删除他人注解）、**禁**「裁掉再追加」（移段 ⇒ 顺序敏感）；须以「交替重跑两 CO」验证**保位 + 顺序无关幂等**。
> **R-CO197-3**（复现序，取代 R-CO196-3；**步集/序列不变，序内出现 50 次**）：规范复现序 = `co146_impedance_table → co146_pm_eval → co146_ledger_add → co153_k9_domain_coverage → co148_u6_datasheet_inputs → co148_thermal_ruling → co149_thermal_mitigation_derive → co147_l2_ruling → co146_jlc_dfm_gate → co146_jlc_fab_package → co152_findings_disposition → co155_co154_findings_disposition → co156_co154_open_disposition → co157_gate_hardening_3 → co158_l5_packet_selfcontained → co159_rev19_co156_co157_co158_review → co160_co159_findings_disposition → co161_gap_hardening_4 → co162_verdict_binding → co163_binding_to_order_notes → co166_rev19_co159_co165_review → co167_co166_findings_disposition → co168_register_consistency → co169_step_output_oracle → co170_stackup_binding → co171_order_notes_record_figures → co172_rev19_co166_co171_review → co173_co172_findings_disposition → co174_step_artifact_attribution → co175_package_parity_binding → co176_gate_selfcheck_evidence → co177_capability_value_binding → co178_drc_item_limit_derivation → co179_sensitivity_teeth_hardening → co180_teeth_judgment_integrity → co124_input_selfcheck_gate → co150_k9_domain_gate → co146_boundary_append → co77_closure_declaration_sweep → co120_provenance_pin_gate → co146_boundary_append → co135_review_hygiene → co136_gate_hygiene → co78_layer_role_drift_gate → co81_project_rules_gate → co84_dru_domain_gate → co95_in4_reachability → co98_reachability_status_report → co106_reference_plane_gate → co146_boundary_append`，**循环至 sha 稳定**（收敛判定须遵 R-CO164-1 + R-CO165-1/2 + R-CO167-1/2 + R-CO169-1/2 + R-CO174-1 + R-CO175-1 + R-CO176-1/2 + R-CO177-1 + R-CO178-1 + R-CO179-1/2 + R-CO180-1/2 + R-CO181-1/2 + R-CO182-1 + R-CO183-1 + R-CO184-1 + R-CO185-1/2 + R-CO186-1 + R-CO187-1/2/3 + R-CO188-1 + R-CO189-1 + R-CO190-1 + R-CO191-1 + R-CO192-1 + R-CO193-1/2/3/4 + R-CO194-1/2 + R-CO195-0/1 + R-CO196-1/2/4/5 + R-CO197-1/2/4）。

| 工件 | sha16 |
|---|---|
| 工具 `p3_v57_co164_order_runner.py`（CO-197.1 / 解包形态 + io·pathlib md 形态） | `db80604b81e805e9` |
| 复评件 `m13_v57_co197_rev19_co192_co195_review.json`（as-found 幂等） | `de625cb63e0df8f5` |
| 登记簿 `input_defect_register_v1.json`（178 项 / OPEN 0） | `b1d8c7130240c4d0` |

## 71. CO-198（**L2 自裁 · 代理 ↔ 语义闸关系机判化**）

- **E-1（low）·代理判据 ↔ 语义闸的绑定只存在于散文、无机判**：co120 的 P5「下游快照」为**键名启发式**（廉价前置代理），其要保证的语义性质（复现序**不动点唯一/路径无关**）由 co195 oracle 承载 —— 但该「代理 ↔ 语义闸」关系**无机判**：判官工具被移除/改名、其语义齿被删、或代理自身 fail-closed 齿从 pin 表消失，**均无人发现**；残余（更名可逃逸）虽已如实登记（CO-193 G-4 / CO-195 I-1），却**无声明面强制**（可被误读为判据完备）。属「声明↔实现绑定」未收尾。
- **处置**：runner 升 **CO-198.1** —— 新增 `PROXY_SEMANTIC_BINDING`（导出**残余**（不得宣称完备）+ 语义判官工具 + **源内声明**的语义齿名 + 代理齿所在记录）+ 纯判据 `proxy_binding_decision()`（`tool_ok`/`src_has`/`proxy_teeth` 可注入 ⇒ 合成控）+ 静态齿 **t29**（正控 + 缺声明/残余空/判官缺/齿名未声明/代理齿未 pin 之负控）。**只读判官源**，不读其证据件（R-CO196-1：禁验证循环）。
- **登记簿**：+1（`co198:E-1`，low，CLOSED；**178 项 / OPEN 0**）。
- **实测（本件证据）**：修前改写/删除 co195 齿名或移除判官工具，`--check` **仍全 True**（无机判）；修后 `--check` **t01..t29 全 True（31 项）**，t29 四类负控均判 False ⇒ 判据**可证伪**且只涉结构性事实。

> **R-CO198-1**：凡**代理判据**（启发式 / 近似 / 廉价前置）代替语义判据之处，须登记 `PROXY_SEMANTIC_BINDING` —— **残余显式**（禁宣称完备）+ **外部语义判官**（工具 + **源内声明**的齿名）+ 代理自身 fail-closed 齿**在 pin 表**；静态齿 **t29** 机判，否则 fail-closed。判官**证据件**一律不读（R-CO196-1）。
> **R-CO198-2**（复现序，取代 R-CO197-3；**步集/序列不变，序内出现 50 次**）：规范复现序 = `co146_impedance_table → co146_pm_eval → co146_ledger_add → co153_k9_domain_coverage → co148_u6_datasheet_inputs → co148_thermal_ruling → co149_thermal_mitigation_derive → co147_l2_ruling → co146_jlc_dfm_gate → co146_jlc_fab_package → co152_findings_disposition → co155_co154_findings_disposition → co156_co154_open_disposition → co157_gate_hardening_3 → co158_l5_packet_selfcontained → co159_rev19_co156_co157_co158_review → co160_co159_findings_disposition → co161_gap_hardening_4 → co162_verdict_binding → co163_binding_to_order_notes → co166_rev19_co159_co165_review → co167_co166_findings_disposition → co168_register_consistency → co169_step_output_oracle → co170_stackup_binding → co171_order_notes_record_figures → co172_rev19_co166_co171_review → co173_co172_findings_disposition → co174_step_artifact_attribution → co175_package_parity_binding → co176_gate_selfcheck_evidence → co177_capability_value_binding → co178_drc_item_limit_derivation → co179_sensitivity_teeth_hardening → co180_teeth_judgment_integrity → co124_input_selfcheck_gate → co150_k9_domain_gate → co146_boundary_append → co77_closure_declaration_sweep → co120_provenance_pin_gate → co146_boundary_append → co135_review_hygiene → co136_gate_hygiene → co78_layer_role_drift_gate → co81_project_rules_gate → co84_dru_domain_gate → co95_in4_reachability → co98_reachability_status_report → co106_reference_plane_gate → co146_boundary_append`，**循环至 sha 稳定**（收敛判定须遵 R-CO164-1 + R-CO165-1/2 + R-CO167-1/2 + R-CO169-1/2 + R-CO174-1 + R-CO175-1 + R-CO176-1/2 + R-CO177-1 + R-CO178-1 + R-CO179-1/2 + R-CO180-1/2 + R-CO181-1/2 + R-CO182-1 + R-CO183-1 + R-CO184-1 + R-CO185-1/2 + R-CO186-1 + R-CO187-1/2/3 + R-CO188-1 + R-CO189-1 + R-CO190-1 + R-CO191-1 + R-CO192-1 + R-CO193-1/2/3/4 + R-CO194-1/2 + R-CO195-0/1 + R-CO196-1/2/4/5 + R-CO197-1/2/4 + R-CO198-1）。

| 工件 | sha16 |
|---|---|
| 工具 `p3_v57_co164_order_runner.py`（CO-198.1 / 代理↔语义闸绑定 + 静态齿 t29） | `db80604b81e805e9` |
| 登记簿 `input_defect_register_v1.json`（178 项 / OPEN 0） | `b1d8c7130240c4d0` |

## 72. CO-199（**L2 自裁 · 白名单 rc 类语义**）

- **F-1（low）·白名单 rc 语义未声明**：`EXPECTED_NONZERO` 只声明 `verdict`（+ `record`/`teeth_path`），**不声明预期 rc 值** ⇒ `allowlist_decision()` 对白名单步仅判 `rc != 0` ⇒ **任何**非零退出（内部错误 / 参数错 / `sys.exit(2)` / 127）只要 verdict 相符、无 Traceback、牙齿全 True 即被放行 ⇒ **rc 语义被架空**：「因别的原因失败」与「预期判决 FAIL」不可区分（`why` 之『rc=1 即生效』为散文、无机判）。此前各次收严（CO-165/167/176/185/193/194）都在**同一 rc 值域**内，未约束**值本身**。
- **处置**：runner 升 **CO-199.1** —— ① `EXPECTED_NONZERO` 每条须显式声明 `rc`（非零 int = 该判决的**规格化出口**）；② `allowlist_decision()` 增 `expected_step_rc_undeclared` / `expected_step_rc_mismatch` 两停机类；③ `expected_nonzero_binding()` 增 `rc_not_declared`（声明面完备性）；④ 静态齿 **t30**。
- **登记簿**：+1（`co199:F-1`，low，CLOSED；**178 项 / OPEN 0**）。
- **实测（本件证据）**：修前 `allowlist_decision('co146_jlc_dfm_gate', 2|127, '', 'FAIL', True, True)` 均返回 `expected_nonzero`（与 rc=1 不可区分）；修后 rc=1 ⇒ `expected_nonzero`、rc=2/127 ⇒ `expected_step_rc_mismatch`、rc=0 ⇒ `expected_step_returned_zero`、声明缺失/为零 ⇒ `rc_not_declared`；`--check` **t01..t30 全 True（32 项）**、规范序收敛 rc=0（co146 步仍以 rc=1 放行）。

> **R-CO199-1**：白名单类豁免须**逐项声明语义出口**（rc 值等）；「非零 / 非 PASS / 非空」等**笼统判据**不得充当豁免边界 —— 否则「因别的原因失败」与「预期判决」不可区分；t30 机判。
> **R-CO199-2**（复现序，取代 R-CO198-2；**步集/序列不变，序内出现 50 次**）：规范复现序 = `co146_impedance_table → co146_pm_eval → co146_ledger_add → co153_k9_domain_coverage → co148_u6_datasheet_inputs → co148_thermal_ruling → co149_thermal_mitigation_derive → co147_l2_ruling → co146_jlc_dfm_gate → co146_jlc_fab_package → co152_findings_disposition → co155_co154_findings_disposition → co156_co154_open_disposition → co157_gate_hardening_3 → co158_l5_packet_selfcontained → co159_rev19_co156_co157_co158_review → co160_co159_findings_disposition → co161_gap_hardening_4 → co162_verdict_binding → co163_binding_to_order_notes → co166_rev19_co159_co165_review → co167_co166_findings_disposition → co168_register_consistency → co169_step_output_oracle → co170_stackup_binding → co171_order_notes_record_figures → co172_rev19_co166_co171_review → co173_co172_findings_disposition → co174_step_artifact_attribution → co175_package_parity_binding → co176_gate_selfcheck_evidence → co177_capability_value_binding → co178_drc_item_limit_derivation → co179_sensitivity_teeth_hardening → co180_teeth_judgment_integrity → co124_input_selfcheck_gate → co150_k9_domain_gate → co146_boundary_append → co77_closure_declaration_sweep → co120_provenance_pin_gate → co146_boundary_append → co135_review_hygiene → co136_gate_hygiene → co78_layer_role_drift_gate → co81_project_rules_gate → co84_dru_domain_gate → co95_in4_reachability → co98_reachability_status_report → co106_reference_plane_gate → co146_boundary_append`，**循环至 sha 稳定**（收敛判定须遵 R-CO164-1 + R-CO165-1/2 + R-CO167-1/2 + R-CO169-1/2 + R-CO174-1 + R-CO175-1 + R-CO176-1/2 + R-CO177-1 + R-CO178-1 + R-CO179-1/2 + R-CO180-1/2 + R-CO181-1/2 + R-CO182-1 + R-CO183-1 + R-CO184-1 + R-CO185-1/2 + R-CO186-1 + R-CO187-1/2/3 + R-CO188-1 + R-CO189-1 + R-CO190-1 + R-CO191-1 + R-CO192-1 + R-CO193-1/2/3/4 + R-CO194-1/2 + R-CO195-0/1 + R-CO196-1/2/4/5 + R-CO197-1/2/4 + R-CO198-1 + R-CO199-1）。

| 工件 | sha16 |
|---|---|
| 工具 `p3_v57_co164_order_runner.py`（CO-199.1 / 白名单 rc 类语义 + 静态齿 t30） | `db80604b81e805e9` |
| 登记簿 `input_defect_register_v1.json`（178 项 / OPEN 0） | `b1d8c7130240c4d0` |

## 73. CO-200（**L2 自裁 · 不动点 oracle 扩扰动量：受控 md 卡片产物**）

- **G-1（low）·扰动实验覆盖面缺 md 卡片产物**：受控集自 CO-186 起把各步 **md 卡片产物**入 pin（`ORDER_MD_PRODUCTS`，t20 判），而 `co195` oracle 的三案（A 登记簿 `meta.counts` / B 单步自持 json 记录 / C 双件交互）**只扰 json 记录** ⇒ 「步是否**真正全量重写**其 md 产物」**从未被扰动实验行使**（追加式/增量式写会在扰动态残留注入行而无人测）⇒ R-CO186-1「受控 sha 覆盖**全部**产物」在**语义层**存在覆盖面缺口（结构已 pin、语义未扰）。
- **处置**：oracle 升 **CO-200** —— `CASES` 扩第 4 案 **D_md_card_product**（目标 = `co146_impedance_table` 的 md 卡片产物；注入**内容行**），与其余案同判「收敛 rc=0 + 目标件**逐字节**复原 + 排除自身快照复原」，**任一案失败即停**；牙齿 8 → **9**（`t08_D_md_restored`）；`CASES` 逐案显式 `tooth` 名（新增案不挤占既有齿名 ⇒ 保 CO-198 绑定名稳定）。
- **登记簿**：+1（`co200:G-1`，low，CLOSED；**178 项 / OPEN 0**）。
- **实测（本件证据）**：4 案 `injection_effective` / `order_converged` / `targets_byte_restored` / `snapshot_restored` **全 True**；牙齿 **9 项全 True** / verdict **PASS** / rc=0；D 案证实该 md 产物为**全量重写**（注入行消失、逐字节复原）；`t07_no_residual_perturbation` 现覆盖 4 案全部目标件。

> **R-CO200-1**：受控集每新增**产物类别**（md / 报告 / 图 / 二进制），oracle `CASES` 须同步增对应扰动量 —— 否则该面只受**结构** pin、不受**语义**扰动（覆盖面 = 类别数）。
> **R-CO200-2**（复现序，取代 R-CO199-2；**步集/序列不变，序内出现 50 次**）：规范复现序 = `co146_impedance_table → co146_pm_eval → co146_ledger_add → co153_k9_domain_coverage → co148_u6_datasheet_inputs → co148_thermal_ruling → co149_thermal_mitigation_derive → co147_l2_ruling → co146_jlc_dfm_gate → co146_jlc_fab_package → co152_findings_disposition → co155_co154_findings_disposition → co156_co154_open_disposition → co157_gate_hardening_3 → co158_l5_packet_selfcontained → co159_rev19_co156_co157_co158_review → co160_co159_findings_disposition → co161_gap_hardening_4 → co162_verdict_binding → co163_binding_to_order_notes → co166_rev19_co159_co165_review → co167_co166_findings_disposition → co168_register_consistency → co169_step_output_oracle → co170_stackup_binding → co171_order_notes_record_figures → co172_rev19_co166_co171_review → co173_co172_findings_disposition → co174_step_artifact_attribution → co175_package_parity_binding → co176_gate_selfcheck_evidence → co177_capability_value_binding → co178_drc_item_limit_derivation → co179_sensitivity_teeth_hardening → co180_teeth_judgment_integrity → co124_input_selfcheck_gate → co150_k9_domain_gate → co146_boundary_append → co77_closure_declaration_sweep → co120_provenance_pin_gate → co146_boundary_append → co135_review_hygiene → co136_gate_hygiene → co78_layer_role_drift_gate → co81_project_rules_gate → co84_dru_domain_gate → co95_in4_reachability → co98_reachability_status_report → co106_reference_plane_gate → co146_boundary_append`，**循环至 sha 稳定**（收敛判定须遵 R-CO164-1 + R-CO165-1/2 + R-CO167-1/2 + R-CO169-1/2 + R-CO174-1 + R-CO175-1 + R-CO176-1/2 + R-CO177-1 + R-CO178-1 + R-CO179-1/2 + R-CO180-1/2 + R-CO181-1/2 + R-CO182-1 + R-CO183-1 + R-CO184-1 + R-CO185-1/2 + R-CO186-1 + R-CO187-1/2/3 + R-CO188-1 + R-CO189-1 + R-CO190-1 + R-CO191-1 + R-CO192-1 + R-CO193-1/2/3/4 + R-CO194-1/2 + R-CO195-0/1 + R-CO196-1/2/4/5 + R-CO197-1/2/4 + R-CO198-1 + R-CO199-1 + R-CO200-1）。

| 工件 | sha16 |
|---|---|
| 工具 `p3_v57_co195_fixpoint_uniqueness_oracle.py`（CO-200 / 4 案 + 9 牙齿） | `585b983de844603d` |
| 登记簿 `input_defect_register_v1.json`（178 项 / OPEN 0） | `b1d8c7130240c4d0` |

## 74. CO-201（**L2 自裁 · 出口语义 + 豁免边界**）

- **G-1（low）·白名单出口语义靠文本子串代理**：`allowlist_decision()` 对白名单步的「崩溃」判据仅查 stderr 是否含 CPython 表头 `Traceback (most recent call last)`，**其余 stderr 内容一概不看** ⇒ 非表头形态的错误出口（`sys.exit('msg')`、库抛 SystemExit、解释器外错误）在与声明 rc 相同、记录已先落盘、verdict 与牙齿相符时**冒充「预期判决出口」**。仅 rc **值**已在 CO-199 收紧，该出口**是否伴生错误**仍无判据。
- **G-2（low）·豁免前缀的段边界分支无合成控**：`shadow_exempt()` 实现正确（`rel == pre or rel.startswith(pre + '/')`），但 t23 只行使了**接受**分支 ⇒ 回归为裸 `rel.startswith(pre)`（兄弟目录 / 同前缀文件名被误豁免）时 `--check` **仍全 True**（判据该分支不可证伪）—— 违 R-CO197-1「合成控须逐分支覆盖」。
- **处置**：runner 升 **CO-201.1** —— ① 白名单**预期非零出口须 stderr 全空**，新增停机类 `expected_step_error_output`（置于 `expected_step_crashed` 之后）+ 静态齿 **t31**；② t23 补段边界正/负控（子路径须豁免；`…06_rulingsX/`、`…05_layer_sequence.txtX` 不得豁免）。
- **登记簿**：+2（`co201:G-1`/`G-2`，low，CLOSED；**178 项 / OPEN 0**）。
- **实测（本件证据）**：修前 `allowlist_decision('co146_jlc_dfm_gate', 1, 'Error: boom', 'FAIL', True, True)` ⇒ `expected_nonzero`（放行）；修后 ⇒ `expected_step_error_output`（Traceback 者 ⇒ `expected_step_crashed`；空/纯空白 ⇒ `expected_nonzero`）。**零基线冲击**：`co146_jlc_dfm_gate` stderr = **0 字节**（stdout 628 / rc=1）；规范序收敛 rc=0。

> **R-CO201-1**：「预期出口」须同时绑定 **rc 值** 与 **无错误输出**（stderr 空）；新增白名单步须实测 stderr 为空并留证据。
> **R-CO201-2**：字符串前缀 / 集合归属类判据须对**两种拒绝形态**（等长不同名 / 同前缀更长路径）各给负控；t31/t23 机判。
> **R-CO201-3**（复现序，取代 R-CO200-2；**步集/序列不变，序内出现 50 次**）：规范复现序 = `co146_impedance_table → co146_pm_eval → co146_ledger_add → co153_k9_domain_coverage → co148_u6_datasheet_inputs → co148_thermal_ruling → co149_thermal_mitigation_derive → co147_l2_ruling → co146_jlc_dfm_gate → co146_jlc_fab_package → co152_findings_disposition → co155_co154_findings_disposition → co156_co154_open_disposition → co157_gate_hardening_3 → co158_l5_packet_selfcontained → co159_rev19_co156_co157_co158_review → co160_co159_findings_disposition → co161_gap_hardening_4 → co162_verdict_binding → co163_binding_to_order_notes → co166_rev19_co159_co165_review → co167_co166_findings_disposition → co168_register_consistency → co169_step_output_oracle → co170_stackup_binding → co171_order_notes_record_figures → co172_rev19_co166_co171_review → co173_co172_findings_disposition → co174_step_artifact_attribution → co175_package_parity_binding → co176_gate_selfcheck_evidence → co177_capability_value_binding → co178_drc_item_limit_derivation → co179_sensitivity_teeth_hardening → co180_teeth_judgment_integrity → co124_input_selfcheck_gate → co150_k9_domain_gate → co146_boundary_append → co77_closure_declaration_sweep → co120_provenance_pin_gate → co146_boundary_append → co135_review_hygiene → co136_gate_hygiene → co78_layer_role_drift_gate → co81_project_rules_gate → co84_dru_domain_gate → co95_in4_reachability → co98_reachability_status_report → co106_reference_plane_gate → co146_boundary_append`，**循环至 sha 稳定**（收敛判定须遵 R-CO164-1 + R-CO165-1/2 + R-CO167-1/2 + R-CO169-1/2 + R-CO174-1 + R-CO175-1 + R-CO176-1/2 + R-CO177-1 + R-CO178-1 + R-CO179-1/2 + R-CO180-1/2 + R-CO181-1/2 + R-CO182-1 + R-CO183-1 + R-CO184-1 + R-CO185-1/2 + R-CO186-1 + R-CO187-1/2/3 + R-CO188-1 + R-CO189-1 + R-CO190-1 + R-CO191-1 + R-CO192-1 + R-CO193-1/2/3/4 + R-CO194-1/2 + R-CO195-0/1 + R-CO196-1/2/4/5 + R-CO197-1/2/4 + R-CO198-1 + R-CO199-1 + R-CO200-1 + R-CO201-1/2）。

| 工件 | sha16 |
|---|---|
| 工具 `p3_v57_co164_order_runner.py`（CO-201.1 / 出口语义 + 边界负控 + 静态齿 t31） | `db80604b81e805e9` |
| 登记簿 `input_defect_register_v1.json`（178 项 / OPEN 0） | `b1d8c7130240c4d0` |

## 75. CO-202（**非执行者对抗复评 CO-196..CO-201 + L2 自裁处置**）

- **复评方**：context 归零之续接会话（本谱系 z60..z67 **之外** ⇒ 满足「复评须另一会话，禁自评」）；对象**逐件**钉 as-found（CO-196→`5e6ddde`/`2898392`；CO-197→`2898392`；CO-198→`c922116`；CO-199→`87148cb`；CO-200→`68e2952`/`3734a2f`；CO-201→`8a4cc3c`）；`git show` **内存重放** ⇒ 结论**不随后续处置漂移**。方法：正控 **V1..V8**（独立复算）+ 负控 **P1..P10**（内存注入、**零落盘**、零坐标搜索）。verdict **PASS_WITH_FINDINGS**｜findings **4**（L-1..L-4，全 low）；CO-196..CO-201 之处置**经独立复算成立**（V1..V6、P1..P6 全 True）。
- **成立件（独立复算）**：V1（CO-196 J-1 验证循环已除 —— t28 只判**结构性事实**、`oracle_tool_ok` 不读证据件）；V2（CO-197 K-1/K-2 扫描族已补且**对偶负控**不误报）；V3（CO-198 代理↔语义闸绑定成立）；V4（CO-199 白名单 rc 类语义）；V5（CO-200 md 产物案已扩）；V6（CO-201 出口语义 + 豁免前缀**段边界**正/负控）；V7（登记簿卫生：counts 据 items 复算、OPEN 0、13 条 co196..co201 全 CLOSED）；V8（冻结四源 4/4 + `--check` 全 True + oracle PASS）。**另**：六件 disposition 于**全 720 排列**下均复现**逐字节同一**登记簿（顺序无关幂等、零落盘）。
- **L-1（low）·t28 谓词级控欠覆盖**：R-CO196-4 明列「缺件 / 语法错 / 类型错 各一」，而 t28 对谓词 `oracle_tool_ok` 仅行使**缺件** + 正控；「语法错」控挂在**共享子程序** `src_compiles`（不证**传播**）、「类型错」**无控**（as-found 实测：谓词级 compile/type 控各 False，而实现正确 ⇒ 不可证伪）。
- **L-2（low）·运行期新停机类无合成控**：CO-199 之 `expected_step_rc_undeclared` 在 runner 源内**仅出现 1 次**（其自身 return）⇒ 该 return 分支不可证伪（回归时被 `expected_step_rc_mismatch` 静默吸收，分类永不生效）。
- **L-3（low）·「源内声明」为原文子串代理**：`proxy_binding_decision` 默认 `name in src` ⇒ 判官齿名仅见**注释/散文**即满足 R-CO198-1（实测注释串注入 ⇒ `ok`）⇒ 该「机判」判据本身是**文本代理**、非语义。
- **L-4（low）·oracle 扰动量类别覆盖不足**：受控集类别 {.json,.md,**.svg**} 而 `CASES` 仅扰前二者 ⇒ `.svg`（图）产物（CO-174 入 pin）只受**结构** pin、**从未**被语义扰动行使 ⇒ 违 R-CO200-1「覆盖面 = 类别数」（谱系交接件 §4 之触发条件实已于 CO-174 达成）。
- **处置**：runner 升 **CO-202.1** —— ① t28 补**谓词自身**之逐返回路径控（`_NONCOMPILE_PROBE` 存在但不可编译 / `oracle_tool_ok(None)` 类型错）；② `allowlist_decision(..., decl=)` 增**可注入声明面** + t30 控 `expected_step_rc_undeclared`；③ `proxy_binding_decision` 默认改 **AST 字面量集**（`_source_strings` ⇒ 注释/散文不满足）；④ 新增静态齿 **t32**（受控集类别 ⊆ oracle 扰动量类别）；report revision → CO-202.1。oracle 升 **CO-202** —— `CASES` 第 5 案 `E_svg_product`（目标 = 图/.svg 产物，注入内容行）+ 牙齿 9 → **10**。
- **登记簿**：+4（`co202:L-1`..`L-4`，low，CLOSED；**178 项 / OPEN 0**）。
- **实测（本件证据）**：修前 as-found 记实（AST/内存复算，零落盘）—— t28 谓词级 compile/type 控 False；`expected_step_rc_undeclared` 计数 1；注释串注入 ⇒ `ok`；受控集类别 {.json,.md,.svg} ⊄ `CASES` 类别 {.json,.md}。修后 —— `--check` **t01..t32 全 True（34 项）**；oracle **5 案 / 10 牙齿全 True / verdict PASS / 幂等**（连跑记录 sha 恒定）；规范序收敛 rc=0、48 步 `did_work` 全 True、stray/uncontrolled 全空；复评件**幂等**（连跑记录 sha 恒定）。**残余如实登记（O-1）**：stdout 形态之错误出口未约束（触发 = 出现 stdout 错误外壳之白名单步）。

> **R-CO202-1**：谓词级负控须覆盖**谓词自身**每条返回路径（含「存在但不可编译」「类型错」），不得仅控其共享子程序；t28 机判。
> **R-CO202-2**：运行期新停机类（新 return 分支）须合成控覆盖（声明面可注入）；不得以「当前不可达」免控；t30 机判。
> **R-CO202-3**：受控集产物**类别数** ⊆ oracle 扰动量类别数（逐类别 ≥1 案）；t32 机判（新增产物类别即须同步增扰动量）。
> **R-CO202-4**：「源内声明的名称」类判据须以 **AST 字面量集**判（注释/散文不得满足）；原文子串 `in src` 禁作声明性判据；t29 机判。
> **R-CO202-5**（复现序，取代 R-CO201-3；**步集/序列不变，序内出现 50 次**）：规范复现序 = `co146_impedance_table → co146_pm_eval → co146_ledger_add → co153_k9_domain_coverage → co148_u6_datasheet_inputs → co148_thermal_ruling → co149_thermal_mitigation_derive → co147_l2_ruling → co146_jlc_dfm_gate → co146_jlc_fab_package → co152_findings_disposition → co155_co154_findings_disposition → co156_co154_open_disposition → co157_gate_hardening_3 → co158_l5_packet_selfcontained → co159_rev19_co156_co157_co158_review → co160_co159_findings_disposition → co161_gap_hardening_4 → co162_verdict_binding → co163_binding_to_order_notes → co166_rev19_co159_co165_review → co167_co166_findings_disposition → co168_register_consistency → co169_step_output_oracle → co170_stackup_binding → co171_order_notes_record_figures → co172_rev19_co166_co171_review → co173_co172_findings_disposition → co174_step_artifact_attribution → co175_package_parity_binding → co176_gate_selfcheck_evidence → co177_capability_value_binding → co178_drc_item_limit_derivation → co179_sensitivity_teeth_hardening → co180_teeth_judgment_integrity → co124_input_selfcheck_gate → co150_k9_domain_gate → co146_boundary_append → co77_closure_declaration_sweep → co120_provenance_pin_gate → co146_boundary_append → co135_review_hygiene → co136_gate_hygiene → co78_layer_role_drift_gate → co81_project_rules_gate → co84_dru_domain_gate → co95_in4_reachability → co98_reachability_status_report → co106_reference_plane_gate → co146_boundary_append`，**循环至 sha 稳定**（收敛判定须遵 R-CO164-1 + R-CO165-1/2 + R-CO167-1/2 + R-CO169-1/2 + R-CO174-1 + R-CO175-1 + R-CO176-1/2 + R-CO177-1 + R-CO178-1 + R-CO179-1/2 + R-CO180-1/2 + R-CO181-1/2 + R-CO182-1 + R-CO183-1 + R-CO184-1 + R-CO185-1/2 + R-CO186-1 + R-CO187-1/2/3 + R-CO188-1 + R-CO189-1 + R-CO190-1 + R-CO191-1 + R-CO192-1 + R-CO193-1/2/3/4 + R-CO194-1/2 + R-CO195-0/1 + R-CO196-1/2/4/5 + R-CO197-1/2/4 + R-CO198-1 + R-CO199-1 + R-CO200-1 + R-CO201-1/2 + R-CO202-1/2/3/4）。

| 工件 | sha16 |
|---|---|
| 工具 `p3_v57_co164_order_runner.py`（CO-202.1 / t28 谓词级逐返回路径控 + decl 注入 + proxy AST 字面量集 + 静态齿 t32） | `db80604b81e805e9` |
| 工具 `p3_v57_co195_fixpoint_uniqueness_oracle.py`（CO-202 / 5 案 + 10 牙齿：含 图（.svg）类别） | `585b983de844603d` |
| 登记簿 `input_defect_register_v1.json`（178 项 / OPEN 0） | `b1d8c7130240c4d0` |

## 76. CO-203（**L2 自裁 · 自声明修订号（自声明面）↔ 内容 同步 + 机判齿 t33**）

- **M-1（low）·工具自声明修订号面与内容不同步**：CO-202 处置已把 oracle 内容升为按 CO-202（`CASES` **5 案** / 牙齿 **10**），而其记录自声明 `revision` 仍 **CO-200**（`nature` 仍「4 案」、`trigger` 未述第 5 案、docstring 仍「3 案」）；runner 头部修订清单亦漏 CO-200/CO-202 ⇒ 下游读「oracle revision」者见 CO-200，会误判第 5 案（图/`.svg`）**未被覆盖** —— 即「声明↔实现」在**自声明面**之漂移（承 R-CO194-1/2）。
- **处置**：① oracle 自声明面 sync（`revision` → **CO-202**、`nature` → **5 案**、`trigger` 补 CO-202（L-4）条款、docstring 五案化）；② runner 增 `TOOL_REVISION_DECLARED`（自声明修订号类工具之**权威声明**） + 纯判据 `tool_revision_bound()`（**AST** 抽取记录 dict 字面量之 `revision`；注释/散文不得满足 —— 承 R-CO202-4） + 静态齿 **t33**；runner 头部修订清单补 CO-200/CO-202/CO-203。report revision → CO-203.1。
- **登记簿**：+1（`co203:M-1`，low，CLOSED；**178 项 / OPEN 0**）。
- **实测（本件证据）**：修前（AST 复算，零落盘）as-found `27e9fe3` 记录字面 `revision="CO-200"` 而内容 5 案/10 牙齿 ⇒ `tool_revision_bound(<oracle>, rev=CO-200)` = `revision_mismatch`；修后抽取字面 `(True, 'CO-202')`、`rev=CO-202` ⇒ `ok`；注释/散文源 ⇒ `(False, None)`（判别力控）；`--check` **t01..t33 全 True（35）**；oracle 记录 `revision` = CO-202、5 案 / 10 牙齿 PASS。

> **R-CO203-1**：凡工具**自声明 `revision`** 者，其内容升级须同 commit 同步**自声明面**（记录 `revision` / `nature` / `trigger` / 头部修订清单）；抽取一律以 **AST 字面量**判（注释/散文不得满足，承 R-CO202-4），新增此类工具须入 runner `TOOL_REVISION_DECLARED`；t33 机判。
> **R-CO203-2**（复现序，取代 R-CO202-5；**步集/序列不变，序内出现 50 次**）：规范复现序 = `co146_impedance_table → co146_pm_eval → co146_ledger_add → co153_k9_domain_coverage → co148_u6_datasheet_inputs → co148_thermal_ruling → co149_thermal_mitigation_derive → co147_l2_ruling → co146_jlc_dfm_gate → co146_jlc_fab_package → co152_findings_disposition → co155_co154_findings_disposition → co156_co154_open_disposition → co157_gate_hardening_3 → co158_l5_packet_selfcontained → co159_rev19_co156_co157_co158_review → co160_co159_findings_disposition → co161_gap_hardening_4 → co162_verdict_binding → co163_binding_to_order_notes → co166_rev19_co159_co165_review → co167_co166_findings_disposition → co168_register_consistency → co169_step_output_oracle → co170_stackup_binding → co171_order_notes_record_figures → co172_rev19_co166_co171_review → co173_co172_findings_disposition → co174_step_artifact_attribution → co175_package_parity_binding → co176_gate_selfcheck_evidence → co177_capability_value_binding → co178_drc_item_limit_derivation → co179_sensitivity_teeth_hardening → co180_teeth_judgment_integrity → co124_input_selfcheck_gate → co150_k9_domain_gate → co146_boundary_append → co77_closure_declaration_sweep → co120_provenance_pin_gate → co146_boundary_append → co135_review_hygiene → co136_gate_hygiene → co78_layer_role_drift_gate → co81_project_rules_gate → co84_dru_domain_gate → co95_in4_reachability → co98_reachability_status_report → co106_reference_plane_gate → co146_boundary_append`，**循环至 sha 稳定**（收敛判定须遵 R-CO164-1 + R-CO165-1/2 + R-CO167-1/2 + R-CO169-1/2 + R-CO174-1 + R-CO175-1 + R-CO176-1/2 + R-CO177-1 + R-CO178-1 + R-CO179-1/2 + R-CO180-1/2 + R-CO181-1/2 + R-CO182-1 + R-CO183-1 + R-CO184-1 + R-CO185-1/2 + R-CO186-1 + R-CO187-1/2/3 + R-CO188-1 + R-CO189-1 + R-CO190-1 + R-CO191-1 + R-CO192-1 + R-CO193-1/2/3/4 + R-CO194-1/2 + R-CO195-0/1 + R-CO196-1/2/4/5 + R-CO197-1/2/4 + R-CO198-1 + R-CO199-1 + R-CO200-1 + R-CO201-1/2 + R-CO202-1/2/3/4 + R-CO203-1）。

| 工件 | sha16 |
|---|---|
| 工具 `p3_v57_co164_order_runner.py`（CO-203.1 / 自声明修订号绑定：`TOOL_REVISION_DECLARED` + `tool_revision_bound` + 静态齿 t33） | `db80604b81e805e9` |
| 工具 `p3_v57_co195_fixpoint_uniqueness_oracle.py`（CO-202 / 5 案 + 10 牙齿；自声明 `revision`=CO-202） | `585b983de844603d` |
| 登记簿 `input_defect_register_v1.json`（178 项 / OPEN 0） | `b1d8c7130240c4d0` |

## 77. CO-204（**L2 自裁 · 打样渠道重绑 JLC 标准 = 通孔 + 背钻 + 层分配变更裁决 + 两闸 + U6 热 O2 定案**）

- **渠道重绑（同一抓取件）**：`m13_v57_co146_jlc_capability_source.html` 同页明文二者 —— blind/buried **Not supported**（only make through holes）与 **Backdrill 支持**（4–32 层 FR4 / 板厚 ≥0.8mm / D 0.2–0.5mm / W=D+0.2mm / **T≥0.15mm** / S≥0.2mm）。旧能力件 CO146-CAP.3 **漏** Backdrill 段 ⇒ 催生不存在的「JLC advanced/盲埋孔通道」（CO-147 R1）⇒ **已撤销**，能力件升 **CO146-CAP.4**。（**注**：本条「标准通道不含盲/埋孔」之定性已由 CO-206 §0 更正为「advanced 通道能做但贵」——见 §79。）
- **设计事实（机判，板 `d4e81f647be7f980`）**：493 via = F→B 273 / F→In2 92 / F→In5 8 / **In2→In5 88** / In5→B 32 ⇒ 220 非通孔；In2↔In5 两端内层 ⇒ 最小残桩 **0.3664mm ≥ 0.15mm** ⇒ 标准通道不可制。
- **层分配裁决（CO-204 时点；续见 §78）**：自写 proper-intersection 核（未 import 引擎）把图纸 2276 段投单层 ⇒ **1298 处相交** ⇒「逃逸层 == run 层」不可行；via1 列位 44 列 / 跨 9.55mm 中 **43** 处列距 <0.615（外层 3W）⇒「竖段全落单外层」容量不可行；候选 A′（竖段全落 B.Cu，run 仍 In5）实测 = `NOT FULLY PLACED`（**20/32 页不可落位 ⇒ 落位 8/32**）⇒ 竖段须分色于 ≥2 层。候选族 A/B/C 遴选，实施路由 = WORKER（禁暴力迭代）。
- **U6 热定案 O2**：30×30 散热片 + 界面垫 1.0 + ~2m/s 风冷 ⇒ θJA_eff = 6.5+1.0+3.5 = **11.0** ⇒ 四工况 Tj 91.7 / 106.0 / 103.8 / **117.0 ℃** 全 ≤120；`L2_RULING_u6_thermal_mitigation_v2.md`（v1.0 → v2.0）。
- **两闸入库（防再犯）**：**板厂能力绑定闸** `p3_v57_co204_fab_capability_binding_gate.py`（C0 能力源绑定 / C1 类别合法性 / C2 残桩 <0.15 / C3 背钻工艺限 / C4 禁盲埋孔；CO-205 补 **C5 端声明↔实现绑定**）—— **现行板 FAIL rc=1**（`inner_inner_via_class(88)` / `residual_stub_ge_0.15mm` / `blind_buried_required`；C5=True）；**散热验证闸** `p3_v57_co204_thermal_o2_freeze_and_gate.py` —— **PASS**（四工况 ≤120）。
- **红线（本件工件内 verbatim，不代拟编号）**：能力闸 `redline` = 「只读判据（不改 SPEC/板/冻结四源）；零坐标搜索；能力值一律由 pinned 抓取件原文抽得。」；散热件 `redline` = 「只读输入件 + 闭式一阶计算；零坐标搜索；不改 SPEC/板/冻结四源。」；**R-CO205-1**（过孔端声明↔实现绑定，C5 机判）。
- **记录面（如实登记）**：交接件 z71 §5 引「`R-CO204-1..4`」为 CO-204 之红线编号，但树内**无其规范文本**（CO-204 未落 § 即 §80 F-3 之因）；本 § 以工件 `redline` 字段原文代替编号，**不代拟未声明之条文**。

| 工件 | sha16 |
|---|---|
| 工具 `p3_v57_co204_fab_capability_binding_gate.py`（CO-205 版 / C0..C5） | `093b069570744506` |
| 记录 `m13_v57_co204_fab_capability_binding.json`（**FAIL rc=1；C5=True**） | `420f809c9c77beab` |
| 工具 `p3_v57_co204_thermal_o2_freeze_and_gate.py`（U6 O2 闸） | `a714611731765e4f` |
| 记录 `m13_v57_co204_thermal_verification.json`（**PASS**；四工况 ≤120） | `abf47be9b33e62a6` |
| 裁定 `L2_RULING_jlc_standard_through_backdrill_v1.md`（R1 定性已由 CO-206 §0 更正） | `c379c0114e1bdabe` |
| 裁定 `L2_RULING_u6_thermal_mitigation_v2.md`（U6 O2 定案 v2.0） | `cec7bd86d39b71c8` |
| 能力件 `m13_v57_co146_jlc8_capability.json`（**CO146-CAP.4**，含 backdrill 段） | `fe67e5add2597d1f` |
| 证据 `m13_v57_co204l_candidate_Aprime_infeasible.json`（候选 A′ 20/32） | `511432f5c6f86fc3` |
| 证据 `m13_v57_co204_l2_ruling.json` | `6881c20f3e851d5c` |
| 登记簿 `input_defect_register_v1.json`（178 项 / OPEN 0） | `b1d8c7130240c4d0` |

## 78. CO-205（**L2 自裁 · 层分配重指派全族探索 + 工具缺陷 ①..④ 修复；族闭合 = 24/32（修正模型 23/32）**）

- **族闭合（L2 可自裁空间内穷尽）**：拓扑族（A / A′ / B / C / D / E + escape=F 混合）× 桥孔 jog（方向/幅度 / x-含 y-侧移 / 条件修复）× 列分配（CARRYALL / 逐极性游标 / XMIN / 顺序）× 层参数（POL_OFF）⇒ **上限 24/32（含桥孔占位之修正模型 23/32）**。
- **硬限论证（结构性）**：竖段须落内层（外层 3W=0.615 吃容量）、lane 亦须落内层（同理）、且二者须异层（否则竖段穿邻页 lane 产生真交叉）⇒ corner 必为内层↔内层 ⇒ 在 R3 过孔策略下不可制；**增内层不改变该结论**（每支跨内层孔仍须经 F/B 拆分）⇒ L2 叠层决策收益为零。剩余路径 = **L1**（球重映射/信号流向，owner）或外部工艺输入。
- **候选复测（关键负结果）**：候选 A（run 维持 In5 + 竖段全 In2，`CO16_ALLI2`）= **17/32** INFEASIBLE；候选 B（run In5→B.Cu + 竖段 In2/In5 分色，`CO16_V2B`）= 端点层模型 32/32 且走完整链（L4 apply + co133 PDN ⇒ 501 via / 0 内层↔内层 / 能力闸 PASS）**但 KiCad DRC 抓出 7 shorting_items + 4 clearance** ⇒ **REJECTED**；候选 D（`CO16_VOUT`+`SPAN`）= **14/32**（F 逃逸撞 pad 场/PDN）。两闸 + 冻结四源回归：默认路径与 v9 逐页同，交付板 `d4e81f647be7f980` 逐字节未变。
- **工具缺陷 ①（已修，默认关 `CO10_SPAN`/`CO16_SPAN` 透传）·过孔占用层 = 端点层**：探针以过孔**两端点层**建 mask/判据，而通孔+背钻实际占用**起止层之间全部层** ⇒ 假可行（候选 B 旧模型 32/32 ↔ 真板 KiCad DRC 7 short 为反证）；修后候选 B = **26/32**（失败面与 DRC 命中面一致）。
- **工具缺陷 ②（已修）·lane 层标签漂移**（探针 In6 vs 真板 In5）⇒ 现行发射器工件构造器无法消费（KeyError）；修后发射器输出与 v9 逐页逐字段同、构造器产出与冻结图纸**逐字节同**（`60cbd331836e52b7`）。
- **工具缺陷 ③（已修，opt-in `CO10_BRCOL` / 透传 `CO16_BRCOL`）`bridge_jog_direction_from_pad_order`**：桥孔 jog 方向原由 **pad 序**（BRAWAY/_BR_FLIP）或 band 固定推出；In2 逃逸带 3W=0.48<0.615 ⇒ `_band_carry=False` ⇒ 行内逃逸列序 (px,nx) 可与 pad 序相反 ⇒ P/N 桥孔 jog 指向彼此，`|vx_P-cx_N| = |s-BR_JOG|` 塌到 0.05–0.15（症状 = 候选 C 下 7/8 失败页 reason = `vv_intra`）。修后 `vv_intra` **7 → 0**，失败面全改跨页类（`vv_placed`/`vt_placed`/`vt2_placed`/`hh_intra`）。
- **工具缺陷 ④（已修，opt-in `CO10_COLFIX`）`connector_column_coloring_ignores_bridge_hole_y`**：J2 区间图贪心着色（`r3_build`, EASTSPLIT=in2c）与 J3/J4 落列分离器（`_lx_separate`）之占位区间**只取 {lane_y, land_y}**，桥在 lane 行 ±BR_JOG 处另加一孔（落桥孔）落在区间之外 ⇒ 两页被着同色却在桥孔上撞（症状 = DN2/input `vv_placed` vs UP0/out_J2.P 0.316）。修后（含桥孔占位）最优 = **23/32** ⇒ **记录的 24/32 是欠预留之乐观值**；负控：把判据退化为「仅比 via y」⇒ 24 → **14/32**（同列两页竖段共线重叠）已回退。
- **回归修复（CO-205s）**：`carryall_bridge_extent_leak`（CO-205r 提交 `3f32c0a` 内 `_BEXT` 未加 `_CARRYALL` 门控，静默改写 BRCOL 单用结果 24 → **16/32**）⇒ 修后 `candC+BRCOL` 恢复 **24/32** 且 `vv_intra = 0`。
- **CO-205t（band 级逐极性游标 `CO10_CARRYP`）**：设计意图达成（跨页 via1 撞类 `vv_placed` **6 → 1**），但单调推进把 1 页挤出可行域 ⇒ 净 **−1**（23/32）⇒ 本族仍不过 24/32。

| 工件 | sha16 |
|---|---|
| 证据 `m13_v57_co205_candidate_layer_reassign.json`（候选 A/B/D 复测 + 结构引理） | `400487b56a7ffe0d` |
| 证据 `m13_v57_co205r_bridge_joint_solve.json`（工具缺陷 ③ / 桥族上限 24/32） | `203d0417b818e4c8` |
| 证据 `m13_v57_co205s_connector_column_model.json`（工具缺陷 ④ + 回归修复 → 23/32） | `dad08b50ed3d39d4` |
| 证据 `m13_v57_co205t_per_polarity_cursor.json`（逐极性游标 / 族闭合） | `f9da0536c6877d88` |
| 探针 `p3_v57_co10_west_fan_probe.py`（+11 只读旋钮，全默认关） | `b0ef06180cda787a` |
| 发射器 `p3_v57_co16_emit_allocation.py`（+9 旋钮透传） | `20909dae0ca76ee3` |
| 登记簿 `input_defect_register_v1.json`（178 项 / OPEN 0） | `b1d8c7130240c4d0` |

## 79. CO-206（**L2 自裁 · 工艺选型/性价比对比 立为 ENG 常规功能（监理指令 #13）+ 打样路径 A/B/C 定案 + 口径修正 + 价格取数留痕**）

- **定性更正（§0，最高优先级）**：撤销一切「JLC 无 HDI/盲埋孔通道」表述。准确三层 = ① **标准通道不支持**盲/埋孔（能力表原文 *"Blind/Buried Vias Not supported … only make through holes"*）；② **advanced 通道支持**盲/埋孔与 **HDI（激光孔）**（同页 FAQ 原文 *"Advanced options such as blind/buried vias, HDI (laser vias), … typically require DFM review and may increase both cost and production time."*）⇒「做不了」不成立，正确命题 =「HDI 能做但贵，评估更便宜的路」；③ HDI **阶数/激光孔径/盲埋孔 DFM 限值/交期/加价** 本工程语料未获证 ⇒ `INPUT_REQUIRED`。
- **常规功能入库**：判据件 `process_route_criteria_v1.json`（判据/参数与工具分离，换板换厂可替换、**零板级特判**）+ 执行器 `p3_v57_co206_process_route_select.py --criteria <json> [--board <pcb>]`；输出 可行性/成本/交期/性能/风险 + 推荐 + 所需输入清单；同输入 ⇒ 同输出（**幂等实测**：连跑同 sha）。**单一真源** = 复用能力闸之 census / layer_span / class_stub（防两处口径漂移）。
- **设计事实（机判，板 `d4e81f647be7f980`）**：493 via / 通孔+背钻可制 **405** / 需盲/埋孔 **88**（全为 In2↔In5 两端内层 = 埋孔；层压次数下界 **3** ⇒ 等效 HDI 阶数 ≥2，指示性映射须板厂确认）。
- **A/B/C 定案**：**A**（JLC advanced/HDI 盲埋孔）= `FEASIBLE_PENDING_DFM`（残桩 0 / SI 不变 / **零重派生**）；**B**（加层全通孔，如 10L）= `UNPROVEN`（充分条件 = 存在层分配使每支孔外层锚定；必要条件 = lane 须落外层，否则 corner 必为内层↔内层；实测未全落位）；**C**（盘中孔 via-in-pad）= `PARTIAL_INSUFFICIENT_ALONE`（仅可替盲孔 **132** 支，**埋孔 88 支不可替** —— 埋孔不在任何外层焊盘之下）。
- **推荐**：**A 为默认打样路径**（唯一无需重派生；现行图纸即盲埋孔形态；SI 不变）；B 为报价驱动候选，可复现规则 `quote(10L std) + cost(重派生) < quote(HDI 8L) ⇒ B 否则 A`（已编码，填参后自动复算）；C 仅辅助，不与 A/B 并列。**成本/交期禁编造**（无验证来源 ⇒ 全 `INPUT_REQUIRED`，只出模型 + 所需输入清单）。
- **CO-206b 口径修正**：B 路 lane 既须落外层，就须吃 **外层 3W = 0.615**；探针 `_V2B` 把 lane 置于**私有内层** In6（3W 取内层 0.48）所测 **26/32** 为**乐观值**；按外层口径复测（新增旋钮 `CO10_LANE_OUTER`）⇒ **24/32**（失败面 DN0/2/5/7 `out_MCIO` + UP0/2/4/6 `input`）⇒ B 相对 A 之吸引力进一步下降（非便宜快路，须整层重派生且可行性未证），**推荐 A 不变**。（裁定 v2 增 §2b；判据件 B 路 `measured` 双口径并列。）
- **CO-206c 价格取数留痕**：试 5 端点（capabilities / pcb-hdi / pcb-price / advanced-pcb / cart quote；http 码与字节逐条留痕于判据件 `price_probe_log`）⇒ JLC 站点为 SPA，**服务端不返回价格**（报价器仅渲染 'Calculated Price $0.00' 占位）⇒ 三路 cost/lead_time **不可机取**，维持 `INPUT_REQUIRED`，须**人工报价**回填（留痕以免重复试探）。
- **CO-208 口径同步补完（本 § 之 part）**：CO-206b 只改了主判据字段，`recommendation.basis[0]` 与判据件 `risk_catalog.B[0]` 仍滞留 26/32 ⇒ CO-208 补齐（执行器 **CO-206.2** / 判据件 **v1.3**）⇒ 明细见 §81 F-1 处置。

- **CO-213 追注（pin 语义，勿误读）**：本表 sha 由本写入器之「**现行态 pin 再对齐**」机制**实时**取自当前实件 ⇒ 同排之**历史版本标签**（如 `CO-206.2` / `v1.3`）与 sha **可能不同版**（标签 = 本节成文时之口径；sha = 现行实件）。本节所涉两件之**现行**版本 = **执行器 CO-206.4 / 判据件 v1.5**（见 §86，R-CO213-2）。

| 工件 | sha16 |
|---|---|
| 判据件 `process_route_criteria_v1.json`（**v1.3**） | `65d6dd73f1666068` |
| 执行器 `p3_v57_co206_process_route_select.py`（**CO-206.2**） | `83dba4f108663e6d` |
| 证据 `m13_v57_co206_process_route_selection.json` | `e9d1673e81f5391f` |
| 证据 `m13_v57_co206_process_route_selection.md` | `70f101f39c308214` |
| 裁定 `L2_RULING_process_route_selection_v2.md`（§0 更正 + §1 定案 + §2b 口径） | `d258f67957a448d0` |
| 登记簿 `input_defect_register_v1.json`（178 项 / OPEN 0） | `b1d8c7130240c4d0` |

## 80. CO-207（**非执行者对抗复评 CO-202..CO-206c；as-found 钉 `add6e33`**）

- **复评方**：context 归零之续接会话（本谱系 z60..z71 **之外** ⇒ 满足「复评须另一会话，禁自评」）；**as-found 快照 = `add6e33`**（CO-206c），一切「现行态」判定皆由该快照重放（`git show` 内存重放 + 自板 pcbnew 普查 / 自算术 / 自源 AST / 自跑工具与探针）。
- **verdict = PASS_WITH_FINDINGS**｜findings **3**（F-1/F-2/F-3，全 low）｜观察 **2**（O-1 交接件齿数表述陈旧：称 25 / 实测 29；O-2「增内层不改变 24/32」之反证责任留在 B 路）。
- **正控 V1..V9**：V1 独立 via 普查 = **False**、V2 散热复算 = True、V3 oracle 复现 = **False**、V4 runner `--check` + 登记簿 = **False**、V5 冻结四源 + 板 = True、V6 登记簿复算 = True、V7 判据件无编造数 = True、V8 打样包完整性 = **False**、V9 L2 族独立复现 = True（v9 默认 **32/32**；candC+BRCOL **24/32**；+COLFIX **23/32**；B 路 lane-outer **24/32**）。
- **负控 P1..P8 全 True**（内存注入、零落盘）：修订号抽取 / 陈旧数探测 / § 存在性 / 编造探测 / stub 齿 / 热齿 / census 齿 / 键字面量抽取之判别力均成立。
- **findings（三项；原文见复评件）**：**F-1** B 路口径修正不完整（同族引用滞留 26/32 + 自声明面滞留）；**F-2** R-CO203-1 登记条款与 t33 互斥（条款不可满足且无齿）；**F-3** CO-204..CO-206c 无 boundary §（本文件 §77..§79 之缺即其证）。处置 = §81（CO-208）。
- **R-CO207-1**：复评件须钉**被评态快照**且一切「现行态」判定皆由该快照重放；禁内嵌处置态之 sha（承 R-CO193-3）。

| 工件 | sha16 |
|---|---|
| 复评件 `m13_v57_co207_rev19_co202_co206_review.json`（机判证据） | `9ecbc9a052b18105` |
| 复评卡片 `m13_v57_CO207_rev19_co202_co206_review.md`（结论 + findings 表） | `5c8e43963a89b92b` |
| 登记簿 `input_defect_register_v1.json`（178 项 / OPEN 0） | `b1d8c7130240c4d0` |

## 81. CO-208（**L2 自裁 · CO-207 复评 F-1..F-3 处置：声明↔内容同步 + R-CO203-1 适用域收窄 + boundary 记录链收口**）

- **F-1 处置（声明↔内容同步）**：① 执行器 `recommend()` 依据① 与判据件 `risk_catalog.B[0]` 之 26/32 → **24/32**（显式注明口径）；② 自声明面 sync：执行器 `revision` **CO-206.1 → CO-206.2**、判据件 **v1.2 → v1.3**（含 changelog）；③ 重生成 `m13_v57_co206_process_route_selection.{json,md}`（幂等实测：连跑同 sha）。**红线 R-CO208-1**。
- **F-2 处置（R-CO203-1 适用域收窄）**：R-CO203-1 之登记义务**收窄**至「其自声明 `revision` 为**机判/记录消费面**者」——现域 = **不动点 oracle 单件**（其记录由 t28/t33 消费）；t33 之单件断言即该域之**显式不变量**。文义「凡自声明者皆须登记」不可实现（本会话 AST 复算：`tools/p3_v57_*.py` 含 `revision` dict 字面量者 **155 / 229**）⇒ 该文义作废。**红线 R-CO208-2**。
- **F-3 处置（记录链收口）**：补 §77（CO-204）/ §78（CO-205 + r/s/t）/ §79（CO-206 + b/c）/ §80（CO-207）/ §81（本节 = CO-208）；boundary **v2.48 → v2.49**。**红线 R-CO208-3**。
- **记录面（如实登记）**：§77 指出的 `R-CO204-1..4` 与承接 CO-206 之 `R-CO206-1` 均无树内规范文本；CO-208 **不代拟**该两族编号条文（CO-204 族以工件 `redline` 原文代替；CO-206 之「工艺可行性/成本须走判据件 + 工具、禁编造单价」义务由本节 R-CO208-1/本判据件承载）。
- **登记簿**：+3（`co207:F-1`/`F-2`/`F-3`，全 low，全 CLOSED；**178 项 / OPEN 0**）。
- **实测（本件证据）**：修后 —— `--check` **t01..t33 全 True（35 项）**；规范序收敛 rc=0 / 2 轮（唯一非零 = co146 DFM rc=1 预期、**stderr 0 字节**）；co124 登记簿自检 PASS；oracle PASS 且幂等；能力闸 **FAIL 预期（C5=True）**；散热闸 PASS；打样包牙齿全 True；冻结四源 **4/4 MATCH**；交付板 `d4e81f647be7f980` 逐字节未变。

> **R-CO208-1**（承 F-1）：**同一量多处引用者，改口径须逐处同步**；工具/判据件之自声明面（`revision`）随内容升级须**同 commit bump**；域内工具由 `tool_revision_bound`（t33）机判。
> **R-CO208-2**（承 F-2，收窄 R-CO203-1）：R-CO203-1 之登记适用域 = 「其自声明 `revision` 为机判/记录消费面者」（现 = 不动点 oracle 单件）；域内新增工具时 `TOOL_REVISION_DECLARED` 与 t33 断言集须**同 commit 同源扩容**（禁单侧更新）；域外工具不适用该登记义务。
> **R-CO208-3**（承 F-3）：**新 CO 收口即须落 boundary §（同一 commit）**；boundary 须自足到「冻结四源 + gate 链态可只读 boundary 得到」。
> **R-CO208-4**（复现序，取代 R-CO203-2；**步集/序列不变，序内出现 50 次**）：规范复现序 = `co146_impedance_table → co146_pm_eval → co146_ledger_add → co153_k9_domain_coverage → co148_u6_datasheet_inputs → co148_thermal_ruling → co149_thermal_mitigation_derive → co147_l2_ruling → co146_jlc_dfm_gate → co146_jlc_fab_package → co152_findings_disposition → co155_co154_findings_disposition → co156_co154_open_disposition → co157_gate_hardening_3 → co158_l5_packet_selfcontained → co159_rev19_co156_co157_co158_review → co160_co159_findings_disposition → co161_gap_hardening_4 → co162_verdict_binding → co163_binding_to_order_notes → co166_rev19_co159_co165_review → co167_co166_findings_disposition → co168_register_consistency → co169_step_output_oracle → co170_stackup_binding → co171_order_notes_record_figures → co172_rev19_co166_co171_review → co173_co172_findings_disposition → co174_step_artifact_attribution → co175_package_parity_binding → co176_gate_selfcheck_evidence → co177_capability_value_binding → co178_drc_item_limit_derivation → co179_sensitivity_teeth_hardening → co180_teeth_judgment_integrity → co124_input_selfcheck_gate → co150_k9_domain_gate → co146_boundary_append → co77_closure_declaration_sweep → co120_provenance_pin_gate → co146_boundary_append → co135_review_hygiene → co136_gate_hygiene → co78_layer_role_drift_gate → co81_project_rules_gate → co84_dru_domain_gate → co95_in4_reachability → co98_reachability_status_report → co106_reference_plane_gate → co146_boundary_append`，**循环至 sha 稳定**（收敛判定须遵 R-CO164-1 + R-CO165-1/2 + R-CO167-1/2 + R-CO169-1/2 + R-CO174-1 + R-CO175-1 + R-CO176-1/2 + R-CO177-1 + R-CO178-1 + R-CO179-1/2 + R-CO180-1/2 + R-CO181-1/2 + R-CO182-1 + R-CO183-1 + R-CO184-1 + R-CO185-1/2 + R-CO186-1 + R-CO187-1/2/3 + R-CO188-1 + R-CO189-1 + R-CO190-1 + R-CO191-1 + R-CO192-1 + R-CO193-1/2/3/4 + R-CO194-1/2 + R-CO195-0/1 + R-CO196-1/2/4/5 + R-CO197-1/2/4 + R-CO198-1 + R-CO199-1 + R-CO200-1 + R-CO201-1/2 + R-CO202-1/2/3/4 + R-CO203-1 + R-CO207-1 + R-CO208-1/2/3）。

| 工件 | sha16 |
|---|---|
| 执行器 `p3_v57_co206_process_route_select.py`（CO-206.2） | `83dba4f108663e6d` |
| 判据件 `process_route_criteria_v1.json`（v1.3） | `65d6dd73f1666068` |
| 生成器 `p3_v57_co146_boundary_append.py`（本节写入器） | `00fa05ab54fdf13c` |
| runner `p3_v57_co164_order_runner.py`（CO-203.1 / t33 域不变量） | `db80604b81e805e9` |
| 登记簿 `input_defect_register_v1.json`（178 项 / OPEN 0） | `b1d8c7130240c4d0` |

## 82. CO-209（**L2 自裁 · band 级「列 × 桥孔 x」联合求解之直接行使（族闭合复核）+ 发射器透传补齐**）

- **缘起**：z71 §6.3 指「L2 内唯一未动自由度 = band 级联合求解器（列 + 桥孔 (x,y) 同解；确定性、禁回溯）」，且 CO-207 之观察 **O-2** 明记「族上限 ≤24/32 属**结构性论证**、未直接行使（未构造反例）」。本 CO 消除该「论证 vs 实测」缺口。
- **行使形态（全部闭式：确定性、零回溯、零重试、零坐标搜索）**：逐极性单调游标（`CO10_CARRYP`）**并计入桥孔向外足迹**（`CO10_CARRYALL` ⇒ `_BEXT = BR_JOG`）= 「列游标与桥孔 x 同解」；另复测顺序（rev / carry / xasc / engine）与既有修复旋钮（COLFIX / BRDROP / BR2 / POL_OFF）。**不含**跨页 y 交错（该轴须改几何，非旋钮可达）。
- **结果（机判，探针 `b0ef06180cda787a`；`m13_v57_co209_band_joint_solve.json`）**：v9 默认 **32/32**；候选 C+BRCOL **24/32**（族最优，未变）；+COLFIX **23/32**；`CARRYP` 单用 **23/32**；`CARRYALL` 单用 **15/32**；**JOINT 组合 19/32（rev）/ 20/32（carry·xasc·engine）/ 19/32（+COLFIX / +BRDROP / +POL_OFF 0.2625）/ 15/32（+BR2）**。
- **结论**：联合游标形态**不改善族上限**（JOINT 19–20/32 < 候选 C+BRCOL 24/32）：单调游标计入桥孔足迹后**过度推进**，把失败面由 chip 侧 input 页**转嫁**到连接器/走廊侧（`out_J2` / `out_MCIO`）。与 CO-205r 之暴露度分析一致 ——8 个失败页中 **6 页 > 0 余量**（阻断来自轨道/页内约束，非 via 拥塞）⇒ x 向联合求解**触不到**瓶颈。⇒ **族闭合（≤24/32）在直接行使下成立**；路径 B 仍不可达 32/32 ⇒ **打样路径 A 之定案不变**。残余自由度 = 跨页 y 交错（须改几何）与 **L1**（球重映射 / 信号流向）。
- **工具面（同 CO 补齐）**：发射器 `p3_v57_co16_emit_allocation.py` 补 `CO10_CARRYALL → CO16_CARRYALL` 透传（原仅透传 `CARRYP`）⇒ 该联合形态**可由规范分配路径表达**；回归实测：v9 默认复现仍 **32/32 / 0 page diffs**。
- **登记簿**：本件为**负结果**（无缺陷可登）⇒ 不入登记簿（诚实登记，勿虚增计数）。

| 工件 | sha16 |
|---|---|
| 工具 `p3_v57_co209_band_joint_solve.py`（形态矩阵 + 4 牙齿） | `7f89230407ce4dca` |
| 证据 `m13_v57_co209_band_joint_solve.json`（13 案结果 + 牙齿全 True） | `73a78fa1b6c1e90c` |
| 探针 `p3_v57_co10_west_fan_probe.py`（+11 只读旋钮，全默认关） | `b0ef06180cda787a` |
| 发射器 `p3_v57_co16_emit_allocation.py`（+10 旋钮透传，含新补 `CARRYALL`） | `20909dae0ca76ee3` |
| 现行分配 `m13_v57_co16_channel_allocation_v9.json`（回归基准） | `d3cd1e5a312f253a` |
| 登记簿 `input_defect_register_v1.json`（178 项 / OPEN 0） | `b1d8c7130240c4d0` |

> **R-CO209-1**（承 z71 §6.3 / CO-207 O-2）：**族上限之「结构性论证」不得代替直接行使** —— 凡宣示某族在给定策略下不可达 32/32 者，须附可复算的形态矩阵（确定性、禁回溯）或等价机判；矩阵扩展须同步判据件/工具，并保持默认路径逐字节可复现。

> **R-CO209-2**（复现序，取代 R-CO208-4；**步集/序列不变，序内出现 50 次**）：规范复现序 = `co146_impedance_table → co146_pm_eval → co146_ledger_add → co153_k9_domain_coverage → co148_u6_datasheet_inputs → co148_thermal_ruling → co149_thermal_mitigation_derive → co147_l2_ruling → co146_jlc_dfm_gate → co146_jlc_fab_package → co152_findings_disposition → co155_co154_findings_disposition → co156_co154_open_disposition → co157_gate_hardening_3 → co158_l5_packet_selfcontained → co159_rev19_co156_co157_co158_review → co160_co159_findings_disposition → co161_gap_hardening_4 → co162_verdict_binding → co163_binding_to_order_notes → co166_rev19_co159_co165_review → co167_co166_findings_disposition → co168_register_consistency → co169_step_output_oracle → co170_stackup_binding → co171_order_notes_record_figures → co172_rev19_co166_co171_review → co173_co172_findings_disposition → co174_step_artifact_attribution → co175_package_parity_binding → co176_gate_selfcheck_evidence → co177_capability_value_binding → co178_drc_item_limit_derivation → co179_sensitivity_teeth_hardening → co180_teeth_judgment_integrity → co124_input_selfcheck_gate → co150_k9_domain_gate → co146_boundary_append → co77_closure_declaration_sweep → co120_provenance_pin_gate → co146_boundary_append → co135_review_hygiene → co136_gate_hygiene → co78_layer_role_drift_gate → co81_project_rules_gate → co84_dru_domain_gate → co95_in4_reachability → co98_reachability_status_report → co106_reference_plane_gate → co146_boundary_append`，**循环至 sha 稳定**（收敛判定须遵 R-CO164-1 + R-CO165-1/2 + R-CO167-1/2 + R-CO169-1/2 + R-CO174-1 + R-CO175-1 + R-CO176-1/2 + R-CO177-1 + R-CO178-1 + R-CO179-1/2 + R-CO180-1/2 + R-CO181-1/2 + R-CO182-1 + R-CO183-1 + R-CO184-1 + R-CO185-1/2 + R-CO186-1 + R-CO187-1/2/3 + R-CO188-1 + R-CO189-1 + R-CO190-1 + R-CO191-1 + R-CO192-1 + R-CO193-1/2/3/4 + R-CO194-1/2 + R-CO195-0/1 + R-CO196-1/2/4/5 + R-CO197-1/2/4 + R-CO198-1 + R-CO199-1 + R-CO200-1 + R-CO201-1/2 + R-CO202-1/2/3/4 + R-CO203-1 + R-CO207-1 + R-CO208-1/2/3 + R-CO209-1）。

## 83. CO-210（**L2 自裁 · 随单 NOTES（ORDER_NOTES §6）热声明滞后于 O2 定案 ⇒ 声明↔内容修正 + 记录绑定**）

- **缺陷（G-1，low）**：CO-204 已把 U6 热**采 O2**（30×30 铝散热片 + 界面垫 1.0 ℃/W + ~2 m/s 风冷 ⇒ θJA_eff 11.0、四工况 ≤120）并作 `L2_RULING_u6_thermal_mitigation_v2.md`（取代 v1.0 之「推荐/待定」口径），该 v2 亦**已随包**（`06_rulings/`）；但生成器 §6 仍 ① 只引 **v1** 两件、② 以「⇒ 须（a）… 或（b）…」**未定口径**叙述、③ 引「登记簿 HIGH 项」而该项已由 CO-149/CO-150 **CLOSED**、④ O2 之 θJA_eff 与最重工况 Tj **无记录绑定**（CO-172 F-4 只绑了 CO-148/CO-149 的六个数字）⇒ **板厂/装配方读到已废口径**，且与本包自带之定案自相矛盾。
- **处置**：① §6 改写为「问题定性（CO-148）+ **定案 O2（CO-204）**」两段式；② 按 CO-172 F-4 原则补**记录绑定** —— `order_notes_record_figures` 增 `co204`（散热验证闸记录）源 ⇒ 新增 **`o2_theta_ja_eff`**（`θJA_eff = 11.0 ℃/W`）与 **`o2_Tj_max`**（`117.0 ℃`）两项有锚判据，并入既有 **t12** 之 `all(figures)` 面（**不新增齿**，齿数仍 29）；③ 经生成器重出打样包（37 文件 / 29 牙齿全 True）。
- **负控（判别力）**：θJA_eff 注入 12.0 ⇒ `o2_theta_ja_eff`=False；最重工况 Tj 注入 99.0 ⇒ `o2_Tj_max`=False；**旧（未定）§6 文本** ⇒ 两项皆 False ⇒ 绑定非空真。
- **不影响**：Gerber/钻孔/叠层图/阻抗表**逐字节未变**（仅 ORDER_NOTES 文本 + 生成器变更）；板 `d4e81f647be7f980` 未动。

| 工件 | sha16 |
|---|---|
| 生成器 `p3_v57_co146_jlc_fab_package.py`（§6 + `co204` 记录绑定） | `0f32a1bf7a9c0964` |
| 随单 `jlc_package/ORDER_NOTES.md`（§6 修正后） | `baa49660e280b510` |
| 包记录 `m13_v57_co146_jlc_fab_package.json`（牙齿 29/29） | `962e9d74387dc1ee` |
| 记录 `m13_v57_co204_thermal_verification.json`（O2 定案；新增绑定之源） | `abf47be9b33e62a6` |
| 裁定 `L2_RULING_u6_thermal_mitigation_v2.md`（O2 定案 v2.0） | `cec7bd86d39b71c8` |
| 登记簿 `input_defect_register_v1.json`（178 项 / OPEN 0） | `b1d8c7130240c4d0` |

> **R-CO210-1**：凡**随单提交**（交付/打样）文本所引之口径，须引**现行定案件**（不得引其被取代之前身）；由机读记录派生的系统级数字须与板级数字**同受**有锚绑定（承 CO-172 F-4 / R-CO208-1）。

> **序不变**：本件未改步骤集/序列（承 §82 之 R-CO209-2）。

## 84. CO-211（**L2 自裁 · 工艺选型决策规则求值化：声明式规则求值 + B 可行性前置 + 闭式安全求值器 + 求值齿**）

- **缺陷（H-1，low）**：执行器自述 `decision_rule_reproducible` =「填入 `cost_model.parameters` 后重跑本工具即得成本序；**规则已编码**，可复现」，交办件/裁定亦沿用该表述；但**实测（内存注入、零落盘）把全部参数填满**（`missing` 皆空）后，三路 `cost.value` / `lead_time.value` **仍恒为 None**、`pick` **恒为 `A`** ⇒ 即**表达式从未求值、`conditional` 从未判定**；且文档规则引用之 `cost(重派生)` 在 `cost_model.parameters` 中**无对应参数** ⇒ 该规则以现行模型**不可表达**。（决策面之「声明↔实现」漂移，承 R-CO194-1 / R-CO208-1 / R-CO210-1。）
- **处置**：① 判据件 **v1.3 → v1.4**：cost expr 补 `+ k_rederivation*G`、新增参数 **`k_rederivation`**（`INPUT_REQUIRED`，USD / 整层重派生遍）、新增 **`decision`** 块（`rule_id` = `B_if_feasible_and_cheaper_else_A` / 可行性前置 / 禁编造 / 变量语义）；② 执行器 **CO-206.2 → CO-206.3**：新增**闭式安全求值器** `_eval_expr`（白名单记号 + 递归下降，**无 eval**；未知记号/变量或除零 ⇒ None，fail-closed）、按符号绑定求值 cost/lead、`recommend()` 改为**求值声明式规则**（**B 前置 = 可行性已证**）+ **6 项求值齿**（rc 随齿全绿 fail-closed）；③ 重生成证据件；④ 随单裁定补前置注记。
- **判据（修后实测）**：参数缺失 ⇒ 三路 `value` = None 且 `pick` = A（**不伪排序**）；参数齐备而 **B 未证** ⇒ `pick` = **A**（前置不满足）；参数齐备且 B **假设已证** ⇒ C_A = **394.0** / C_B = **125.0** ⇒ `pick` = **B**（规则确已求值）。**6 齿全 True**（t01 规则声明绑定 / t02 缺参不伪排序 / t03 齐备可求值 / t04 B 前置 / t05 求值器 fail-closed / t06 表达式变量全可解析）；连跑同 sha（幂等）。
- **意义**：打样路径 A/B 之决策面此前**只有文档、没有实现**；现「填参 ⇒ 出数并可能改判」为真（但 **B 仍须先证 32/32**，现行 24/32 ⇒ 前置不满足 ⇒ 恒 A）；外部报价回填后即刻可算。

| 工件 | sha16 |
|---|---|
| 判据件 `process_route_criteria_v1.json`（**v1.4**：+`k_rederivation` / +`decision` 块 / cost expr 补项） | `65d6dd73f1666068` |
| 执行器 `p3_v57_co206_process_route_select.py`（**CO-206.3**：求值器 + 规则求值 + 6 齿） | `83dba4f108663e6d` |
| 证据 `m13_v57_co206_process_route_selection.json` | `e9d1673e81f5391f` |
| 证据 `m13_v57_co206_process_route_selection.md` | `70f101f39c308214` |
| 裁定 `L2_RULING_process_route_selection_v2.md`（§2 R3′ 补可行性前置注记） | `d258f67957a448d0` |
| 包记录 `m13_v57_co146_jlc_fab_package.json`（牙齿 29/29） | `962e9d74387dc1ee` |
| 登记簿 `input_defect_register_v1.json`（178 项 / OPEN 0） | `b1d8c7130240c4d0` |

> **R-CO211-1**：「XX 已编码 / 可复现」类声明须有**求值齿**支撑 —— 正控 = 填参即出数且可改判，负控 = 缺参恒 None 不排序、前置不满足恒取保守路；规则须与其**前置条件同处声明**（判据件 `decision` 块），实现与声明以 `rule_id` 同源。

> **序不变**：本件未改步骤集/序列（承 §82 之 R-CO209-2）。

## 85. CO-212（**L2 自裁 · L5 sign-off 记录补被评板指纹绑定：SI/PI/EMC 与 DFM/DFT 之 verdict 可追溯**）

- **缺陷（I-1，low）**：`p3_v57_l5_signoff.py` 产出三件记录，**仅** `m13_v57_l5_fab_record.json` 含 `board`/`board_sha256`；`m13_v57_l5_dfm_dft_record.json`（keys = artifact/dft/drc/manufacturing_conformance/revision/schema/verdict）与 `m13_v57_l5_si_pi_emc_record.json`（keys = EMC/PI/SI/artifact/revision/schema/skew_metric/verdict）**皆无板指纹** ⇒ 板若变更，二件之 PASS（含 **等长 `max_intra_pair_skew_mm = 0.13 ≤ 0.15`** 与 DFM/DFT PASS）**不会可见地失效**；而交办件之「写件时复核」恰以「**L5 全绿**」为放行依据（承 R-CO193-3 / R-CO207-1「被评态须钉快照」/ CO-172 F-4「跨记录派生数字须绑定」）。
- **处置**：① 为 **DFM/DFT（L5-DFM.6 → .7）** 与 **SI/PI/EMC（L5-SI.6 → .7）** 记录补 `board` + `board_sha256`（与 FAB 记录同构；DFM 另补 `baseline_sha256`）；② 新增 **fail-closed 自检**：三件之 `board_sha256` 须皆等于当前 L4 板且非退化值，否则 rc≠0（L5-G7.6 → G7.7）；③ 重出三件记录 + G7 记录。
- **修后实测**：三件 `board_sha256` = `d4e81f647be7f980…`（= 现行 L4 板）；自检 `board_pin_ok=True` / `board_pin_discriminates=True`；rc=0（DFM PASS / SI PASS，skew **0.1300 ≤ 0.15**）。
- **并存事实（如实登记，非缺陷）**：SI 判据读 `SPEC_k2_v4.spec-rev-7.json` 之 impedance 块 —— 实测 rev-7 与 rev-19 之 `impedance` **逐字节同** ⇒ 该旧 rev 引用**不影响**判据。

| 工件 | sha16 |
|---|---|
| 工具 `p3_v57_l5_signoff.py`（CO-212：三件记录均钉板 + fail-closed 自检） | `7618070712518194` |
| 记录 `m13_v57_l5_fab_record.json`（L5-FAB.2，原即含板指纹） | `791012e88b514faa` |
| 记录 `m13_v57_l5_dfm_dft_record.json`（**L5-DFM.7**，新补板指纹；PASS） | `6632179e1ef63183` |
| 记录 `m13_v57_l5_si_pi_emc_record.json`（**L5-SI.7**，新补板指纹；PASS，skew 0.13） | `97c867e89fc6df6c` |
| G7 记录 `m13_v57_l5_g7_record.md`（L5-G7.7） | `2ab7a29e745b70ff` |
| 登记簿 `input_defect_register_v1.json`（178 项 / OPEN 0） | `b1d8c7130240c4d0` |

> **R-CO212-1**：任何 verdict 记录须与**被评态**在**同记录内**钉指纹（板/图纸/来源）；跨件引用（证据件 sha）不得替代被评态绑定；pin 漂移或缺失即 fail-closed。

> **序不变**：本件未改步骤集/序列（承 §82 之 R-CO209-2）。

## 86. CO-213（**非执行者对抗复评 CO-207..CO-212 + 同会话处置**）

- **性质/授权**：本谱系（z60..z77）之外之续接会话（context 归零）复评 **CO-207..CO-212**（CO-202..CO-206c 已由 CO-207 复评、由 CO-208 收口）并**同会话处置**全部 findings —— 被评 CO 之作者谱系与本件无交集（非自评）。
- **as-found（R-CO207-1 / R-CO193-3）**：被评态快照 = **`f0016ae`**（CO-212）；一切「现行态」判定皆由该快照重放（`git show f0016ae:<path>`）或本会话独立复算，**不引用**被评记录之结论。
- **正控（独立复算，全 True）**：V1 冻结四源 4/4 MATCH；V2 交付板 = `d4e81f647be7f980`（逐字节未变）；V3 runner `--check` t01..t33 全 True（35）；V4 工艺选型执行器**幂等**（连跑同 sha）且齿全 True；V5 CO-209 族闭合求解器**幂等**（证据 sha 恒 `73a78fa1b6c1e90c`）且数值复算 = §82 所载（v9 32/32 · candC+BRCOL 24/32 · +COLFIX 23/32 · CARRYALL 15/32 · JOINT 19–20/32）；V6 L5 三件记录 `board_sha256` = 现行 L4 板；V7 打样包 37 payload / 牙齿 **29/29**；V8 登记簿 151 项 / OPEN 0（co124 PASS、co168 rc=0）；V9 包内裁定副本与源**逐字节同**；V10 `SPEC_k2_v4.spec-rev-7` 与 `-rev-19` 之 `impedance` **逐字节同**（CO-212 并存事实成立）。
- **负控（判别力；内存注入、零落盘）**：P1 交接件 pin 解析器对伪造 sha 判否；P2「同文件同 sha 多标签」探测器对无冲突样本不误报；P3「前置可否由判据件**数据**翻转」探测器：as-found **否**（= F-1 证据）、注入机读字段后**是**；P4 全工具集 `board_sha256` 之**消费面** = ∅（= F-4 证据）。
- **F-1（TOOL_DEFECT · low）前置仍是代码常量**：`recommend()` 之 B 前置取 `_proven = {"B": False}` 字面量，判据件 `decision.precondition_note` 仅为散文 ⇒ **判据件侧任何编辑（含把 `measured` 改为 32/32）皆不能改判**，唯一可翻转者 = 改 Python 常量或 t04 之内存注入 ⇒ CO-211 修了**成本臂**，**可行性臂**仍属「声明↔实现」漂移（违 R-CO211-1「规则与其前置同处声明、实现与声明同源」）。**处置**：判据件 `F4_route_predicates.B` 增机读 `measured_placement{placed,total}` + `decision.precondition`（谓词 = `placed == total`；缺字段/退化 ⇒ fail-closed 视为未证）；执行器 **CO-206.3 → CO-206.4** 改由该字段求值 `proven`，并加**数据驱动**求值齿 **t07**（只改判据件数据即改判为 B；placed<total 或字段缺失 ⇒ 保守路 A）；判据件 **v1.4 → v1.5**；重出证据件 ⇒ 齿 **7/7**。**R-CO213-1**。
- **F-2（RECORD_HYGIENE · low）交接件政策层 pin 陈旧**：z77 §1 之 `L2_RULING_process_route_selection_v2.md` pin = `1542a84cf4859de6`（= CO-206b `14bd37c` 之内容）；CO-211（`86d612b`）追加 §2 R3′ 前置注记后现行 = `d258f67957a448d0` ⇒ z77 自称修正 2 处陈旧 pin 后**仍残留 1 处**。**处置**：于 z78 更正该 pin，并把「写件时复核」扩至**政策层表格**（原仅查 canonical 工件表）。
- **F-3（RECORD_HYGIENE · low）现行态 pin 再对齐之标签↔sha 同排不一致（系统性）**：本写入器之再对齐只重写 sha、不改同排**历史版本标签** ⇒ 同排标签与 sha 可不同版（实测：§79 两行标 `CO-206.2`/`v1.3` 而 pin 已为 CO-206.3/v1.4 之内容；全表同文件同 sha 对多枚历史标签之行数十处，如 runner 一行一 sha 而标签跨 CO-164..CO-203.1）；§79 亦残留 CO-211 已证伪之「（已编码，填参后自动复算）」表述而无 §84 指针 ⇒ 读者可能据行内标签误判版本。**处置**：机制**不改**（现行态对齐为**有意**设计；逐行改写 456 处历史标签反致伪史）⇒ §79 补**追注**（标签 = 成文时口径；sha = 现行实件）+ 本节显式登记该语义。**R-CO213-2**。
- **F-4（TOOL_DEFECT · low）CO-212 之板指纹在消费面无机判、且判别齿过弱**：其判别齿只判「≠ 全零哨兵」，**不判别「评的是冻结源还是交付板」**（二者互换而齿不响）；且全工具集扫描 `board_sha256` 之**消费者 = ∅**（仅 L5 工具自身自检；序内/各闸皆不读三件记录之板指纹）⇒ 板变更后记录不刷新仍**只对人眼可见**。**处置**：自检改**真判别** —— DFM `baseline_sha256` 须 = 冻结源板、被评板 ≠ 冻结源板、三件皆钉被评板且非退化（「评错板」即 rc≠0）；记录 **L5-DFM.7→.8 / L5-SI.7→.8 / L5-G7.7→.8**；**消费面机判**列为**有据延后**（触发 = 板变更或下次 L5 重跑）。
- **本件自捕获（处置期，如实登记）**：复评件自身之 `as_found.register_sha16`（**as-found 锚点**）触发 co120 之**下游快照键名启发式** ⇒ 依 CO-159 先例于 co120 `SNAPSHOT_DECLARED` **声明**（理由 = 取自 `git show f0016ae` 之不可变历史值，非下游时点观测）；co120 复归 **PASS**（`unresolved_key` 1 项（co85 记录）**as-found 即存在**且判据明示「不计失败」）。
- **不成立之疑点（如实登记，免后误判）**：① z77「收敛 sha `645d544efcdacbdf`」**非**报告文件自身 sha，而是报告 `iterations[*].sha`（受控集快照）—— 实测一致，**非缺陷**（措辞易误读；z78 改称「收敛快照 sha」）；② §79 与 §84 对同一文件给两枚不同标签但**同一 sha** ⇒ 属 F-3 之现象，非两处独立定值。
- **未复核项（诚实边界）**：B 路 10L 叠层之**实做**（须 L1/几何）、跨页 y 交错（须改几何）不在本件域；外部 JLC advanced/HDI 人工报价仍为唯一外部阻断。

| 工件 | sha16 |
|---|---|
| 判据件 `process_route_criteria_v1.json`（**v1.5**：+机读 `measured_placement` / +`decision.precondition`） | `65d6dd73f1666068` |
| 执行器 `p3_v57_co206_process_route_select.py`（**CO-206.4**：前置自判据件求值 + 数据驱动齿 t07） | `83dba4f108663e6d` |
| 证据 `m13_v57_co206_process_route_selection.json`（7 齿全 True） | `e9d1673e81f5391f` |
| 证据 `m13_v57_co206_process_route_selection.md` | `70f101f39c308214` |
| 工具 `p3_v57_l5_signoff.py`（CO-213：板指纹**真判别**（对照冻结源）） | `7618070712518194` |
| 记录 `m13_v57_l5_dfm_dft_record.json`（**L5-DFM.8**） | `6632179e1ef63183` |
| 记录 `m13_v57_l5_si_pi_emc_record.json`（**L5-SI.8**） | `97c867e89fc6df6c` |
| G7 记录 `m13_v57_l5_g7_record.md`（L5-G7.8） | `2ab7a29e745b70ff` |
| 复评件 `m13_v57_co213_rev19_co207_co212_review.json` | `2be2baf97fe08947` |
| 复评卡 `m13_v57_CO213_rev19_co207_co212_review.md` | `24832881a3bffeaa` |
| 复评工具 `p3_v57_co213_rev19_co207_co212_review.py` | `f007d21fb3ad1865` |
| 登记簿 `input_defect_register_v1.json`（178 项 / OPEN 0） | `b1d8c7130240c4d0` |

> **R-CO213-1**：决策规则之**前置**（可行性/门限类）须与规则**同处声明**，并由**判据件机读字段**求值；禁以代码常量表达前置（否则「填报即改判」为伪）；前置语义变更须**同 commit 双侧**（判据件 + 执行器）同步。

> **R-CO213-2**：boundary 内为**现行态对齐**（sha 实时取自实件）—— 同排**历史版本标签**不得用作 sha 之版本判据；判版本须读该节之现行版本注（如 §79 追注）或对应 CO 节。

> **R-CO213-3**：复评件须钉**被评态快照**（承 R-CO207-1）；findings 之「修后」证据须为**本会话实测**（禁引被评记录之自述）。

> **序不变**：本件未改步骤集/序列（承 §82 之 R-CO209-2）。

## 87. CO-214（**L2 自裁 · 关闭 CO-213 F-4 之「有据延后」：L5 记录板指纹消费面机判**）

- **缘起（CO-213 F-4 之处置留白）**：CO-213 判定「三件 L5 verdict 记录之板指纹**消费者 = ∅**」（读记录 ∩ 含板指纹，除生产者外无一件）⇒ 板变更后 L5 记录不刷新仍**只对人眼可见**；该修复列**有据延后**，触发 = 「板变更 **或** 下次 L5 重跑」。本会话按令续接时 L5 sign-off 已重跑（`.8` 版记录）⇒ **触发成立**，故就地关闭该项。
- **缺口（机判）**：CO-212/CO-213 只把板指纹钉**进**记录（生产者侧），序内无任何步**读**该指纹 ⇒ 「记录钉的是不是**现行**板」在复现序内**不可判**；被评板变更（新 rev）时 L5 的 PASS（含等长 0.15 内、DFM PASS）**不会可见地失效**。
- **处置（消费面机判入序）**：`p3_v57_co120_provenance_pin_gate.py` 升 **CO-120.7**，补判据 **P5 / `l5_board_binding()`**：① 两件 JSON 记录（DFM/DFT、SI/PI/EMC）之 `board_sha256`（**全 64-hex**）须 == **现行** L4 板 sha256 且 != **冻结源板** sha256；② G7 md 记录须含**现行** L4 板 sha16；③ 缺件 / 不可解析 / 退化（全零）⇒ 该行 `ok=False`（**fail-closed**，禁静默跳过）。任一不合格 ⇒ 本闸 verdict = `FAIL_L5_RECORD_BOARD_BINDING`（rc≠0）而**非** PASS。齿 **+4**（1 正控 = 实件全 ok；3 负控 = JSON 面退回冻结源板 / 退化全零 / md 面以冻结源 sha16 顶替 —— 皆须被抓）；runner `EXPECTED_TEETH` 同步（co120 **15 → 19 齿**）。**序不变**：未增删步、未改序列（仍 50 次；只改既有步之判据与齿集）。
- **修后实测**：co120 **PASS**（`l5_bad=0`；19 齿全 True）；独立判别探针（直调 `l5_board_binding()` 注入）：注入冻结源板 ⇒ `all_ok=False`、注入全零 ⇒ `all_ok=False`、实件 ⇒ `all_ok=True` ⇒ 负控**判别力成立**（非恒真）。
- **诚实边界（未声称）**：本判据只保证「记录所钉之板 = 现行 L4 板」，**不**重跑 DFM/SI 判据本身；亦不覆盖 HDI 报价（外部输入）。被评板变更时本闸会**先于** L5 重跑报 FAIL（这正是设计意图：暴露陈旧）。

| 工件 | sha16 |
|---|---|
| 闸 `p3_v57_co120_provenance_pin_gate.py`（**CO-120.7**：+P5 L5 板指纹消费面机判 + 4 齿） | `28d6211f32318d9b` |
| 记录 `m13_v57_co120_provenance_pin_gate.json`（**CO-120.7**：19 齿全 True / `l5_bad=0`） | `df6c9135bc02bbe4` |
| runner `p3_v57_co164_order_runner.py`（`EXPECTED_TEETH` co120 15→19 齿） | `db80604b81e805e9` |
| 被消费 L5 记录 `m13_v57_l5_dfm_dft_record.json`（DFM/DFT） | `6632179e1ef63183` |
| 被消费 L5 记录 `m13_v57_l5_si_pi_emc_record.json`（SI/PI/EMC） | `97c867e89fc6df6c` |
| 被消费 L5 记录 `m13_v57_l5_g7_record.md`（G7） | `2ab7a29e745b70ff` |
| 登记簿 `input_defect_register_v1.json`（178 项 / OPEN 0） | `b1d8c7130240c4d0` |

> **R-CO214-1**：凡产出 **verdict 记录**（L5 sign-off / L4 图纸 / 闸记录等）之**被评态指纹**，须有**至少一个序内或闸内消费者**以机判核对（禁只由生产者自检）；被评态记录的**生产者与消费者须同 commit 双侧**同步，缺消费者即 fail-closed。

> **序不变**：本件未改步骤集/序列（承 §82 之 R-CO209-2）。

## 88. CO-215（**L2 自裁 · 代理帮助函数之源面收窄 + 覆盖面机判**）

- **缘起（R-CO198-1 之未登记代理）**：CO-198 立「凡代理判据代替语义判据之处须登记 `PROXY_SEMANTIC_BINDING`」，但 `artifact_readers()`（判「某步**确实读取**该工件」之**语法代理**，供 t26 `judgment_downstream_binding` 消费）**未入该表**，历件仅以「有据延后」带过 ⇒ 本件查明其根因并处置。
- **缺陷 L-1（TOOL_DEFECT · low）源面判据过宽 ⇒ 注释/散文即可满足**：原实现按**原文子串** `basename in src` 判「该步读取该工件」（实测复现：源内仅一行**注释** `# x.md` 即使该式成真）⇒ 与 **R-CO202-4**「源内**声明**须以 AST 字面量集判；注释/散文不得满足」**同源缺陷**；后果 = t26 之 `refs_not_reading_artifact` 面（下游声明「可执行性」）**可由散文满足**（方向 = fail-open：声明被误认为可执行）。
- **处置**：① `artifact_readers()` 收窄为 **AST 字符串字面量集**（`_source_strings`）匹配 **+ glob 字面量**匹配，**注释/散文一律不计**；并支持 `sources`（step→源码）注入 ⇒ 牙齿合成控**零落盘**。② t26 增 **4 项控**：注释负控（⇒ `[]`）/ 路径字面量正控（⇒ 该步）/ glob 字面量正控（`x_*.md` ⊇ `x_v1.md`）/ 动态构造**如实登记**（`f'{pre}/x.md'` ⇒ `[]`，即残余方向 fail-closed）。③ **残余显式登记**（`PROXY_RESIDUAL_EXPLICIT`）：① 动态构造路径 ⇒ **漏判**（方向 fail-closed）；② 字面量出现于**非读取语境**（`os.path.join` 片段 / 日志与异常文案）⇒ 仍**误判为读者**（方向 fail-open）；**不宣称完备**。④ **覆盖面机判**（`PROXY_HELPERS_PINNED` + `proxy_coverage_decision()`，入 **t29**）：每枚代理帮助函数须**恰**登记于 `PROXY_SEMANTIC_BINDING`（有外部语义判官）**或** `PROXY_RESIDUAL_EXPLICIT`（残余显式）之一（互斥 + 完备覆盖本表）；残余条目三字段（residual/basis/deferral_trigger）须非空；**消费齿须为本工具源内字面量**（AST 判）。**序不变**：未增删步、未改序列（仍 50 次）；**齿数不变**（静态齿仍 t01..t33 = 35 项，仅 t26/t29 内加控）。
- **修后实测**：真声明 `judgment_downstream_binding(`co146_boundary_append`)` = **ok**（boundary 读者集 7 步：co77/co124/co135/co136/co146_boundary_append/co146_jlc_fab_package/co166）；**注释-only 不再满足**（⇒ `[]`）；`--check` **35/35 全 True**（t26/t29 含新控）；`proxy_coverage_decision` = ok。
- **诚实边界**：残余（动态构造漏判 / 非读取语境误判）**未消除**，仅**显式登记** + 覆盖面齿约束；其语义判官支路（**运行时读观测**）列为**有据延后**（触发 = 引入步骤子进程 access tracing）。另：runner 自声明 `revision` 仍为 `CO-203.1` —— 按 CO-208（R-CO208-2）收窄后之登记域（须为**机判/记录消费面**者），本器报告**不被 pin**、亦无消费者 ⇒ **不在登记义务内**，非遗漏（此处明示以免复评误判）。

| 工件 | sha16 |
|---|---|
| runner `p3_v57_co164_order_runner.py`（**CO-215**：`artifact_readers` 收窄为 AST 字面量 + 代理覆盖面齿 t26/t29） | `db80604b81e805e9` |
| 登记簿 `input_defect_register_v1.json`（178 项 / OPEN 0） | `b1d8c7130240c4d0` |

> **R-CO215-1**：凡**代理帮助函数**（启发式 / 廉价前置之实现）须**恰**登记于 `PROXY_SEMANTIC_BINDING`（有外部语义判官）**或** `PROXY_RESIDUAL_EXPLICIT`（残余显式 + 依据 + 触发 + **消费齿**）之一，由覆盖面齿机判；**源面判据不得以原文子串判**（注释/散文不得满足 —— 承 R-CO202-4）；残余不得宣称完备。

> **序不变**：本件未改步骤集/序列（承 §82 之 R-CO209-2）。

## 89. CO-216（**L2 自裁 · 源面判据之 AST 收窄（续）**）

- **缘起（CO-215 之未竟面）**：CO-215 只收窄了 `artifact_readers()`；runner 内**另有两枚源面帮助函数**仍以**原文**判事 —— `declared_verdict_in_tool()`（R-CO194-2「声明↔工具能力」）取 `v in src`；`boundary_read_scan()`（CO-187/CO-192，判「该步读取 boundary」）以 `re` 扫**原文**判引用 + 以 `read_text`/`read_bytes`/`.read(`/`io.open(` 之**原文子串**判读取。
- **缺陷 M-1（TOOL_DEFECT · low）**：① 前者 ⇒ 源内**注释**含该 verdict 字面即满足（如 `# FAIL here`）⇒ **t27 该臂近乎空真**（t27 之正控即 `all(declared_verdict_in_tool(...))`，而环境内任一含 `FAIL` 注释者皆可满足）；② 后者 ⇒ **注释即可伪造引用与读取者身份**（t21 之读取者集可被散文污染；实测 `'# w3_joint_assignment_boundary
# read_text'` 旧判 = True），反向：以**无可匹配字面量**之完全动态方式引用者**漏判** ⇒ t21 之等式**静默漏过**未声明读者。二者皆与 **R-CO202-4** 同源。
- **处置（CO-216）**：① `declared_verdict_in_tool()` 改判 **AST 字符串字面量集**（`_source_strings`），`src` 可注入；② `boundary_read_scan()` 改判 **AST 形态** —— 引用面 = 字面量命中族正则 **或** `_latest_boundary` **标识符**；读取面 = `Attribute.attr ∈ READ_ATTRS`（`read_text`/`read_bytes`/`read`/`readline`/`readlines`）**或** `io.open(...)` 调用；③ 两枚一并纳入 `PROXY_HELPERS_PINNED`（消费齿 = **t27** / **t21**）+ `PROXY_RESIDUAL_EXPLICIT`（残余显式：动态引用漏判 fail-closed / 非读取语境误判 fail-open；字面量出现 ≠ 可产出 verdict），由 t29 覆盖面齿机判（3 枚帮助函数皆已登记）；④ t21 增 **4 控**（注释伪造负控 / 字面量+注释混杂正控 / 仅引用无读取负控 / 动态引用如实登记），t27 增 **3 控**（注释负控 / 字面量正控 / 空源负控）。**序不变（仍 50 次）/ 齿数不变（t01..t33 = 35 项）**。
- **修后实测**：读取者集 = `BOUNDARY_SCAN_GUARDED ∪ BOUNDARY_READ_DECLARED`（**5 步，与修前逐字节同**）；`declared_verdict_in_tool` 真声明 = ok；**注释-only ⇒ 两面皆 False**；字面量/`_latest_boundary` ⇒ 命中；`base / suffix` 动态引用 ⇒ False（残余如实登记）；`--check` **35/35 全 True**（t21/t27/t29 含新控）；`proxy_coverage_decision` = ok。
- **诚实边界**：两枚残余（**动态引用漏判** / **非读取语境之字面量误判**）**未消除**，仅**显式登记** + 覆盖齿约束；其语义判官支路（运行时**读观测** / 出口**verdict 采样**）列为**有据延后**（触发 = 引入上述观测机制）。

| 工件 | sha16 |
|---|---|
| runner `p3_v57_co164_order_runner.py`（**CO-216**：`declared_verdict_in_tool`→AST 字面量；`boundary_read_scan`→AST 形态；两枚入覆盖登记） | `db80604b81e805e9` |
| 登记簿 `input_defect_register_v1.json`（178 项 / OPEN 0） | `b1d8c7130240c4d0` |

> **R-CO216-1**：凡**源面判据**（扫工具源以判声明 / 能力 / 读者身份者）一律以 **AST 形态或字面量**判，**禁原文子串或原文正则**；新增此类帮助函数须入 `PROXY_HELPERS_PINNED` + `PROXY_RESIDUAL_EXPLICIT`（承 R-CO215-1）。

> **序不变**：本件未改步骤集/序列（承 §82 之 R-CO209-2）。

## 90. CO-217（**L2 自裁 · L5 判据源绑定 + 退役定值留存**）

- **缘起**：§89（CO-216）在 runner 内做「源面判据之 AST 收窄」后，续查**判据源版本面** ⇒ 发现 L5 SI 判定记录之**判据源为硬编码旧 rev**。
- **缺陷 N-1（TOOL_DEFECT · low）**：`p3_v57_l5_signoff.py` 读 `SPEC_k2_v4.spec-rev-7.json`（而记录之 `netclass_geometry.source` 又自述 **rev-5** ⇒ 自述源与实现源**亦不一致**），其 `net_classes.PCIe85.inter_pair_spacing_mm` = **0.875** 系**已退役** legacy（rev-19 `retired_inter_pair_spacing_0p875_v1` 标 `LEGACY_DERIVED`；ledger `DV-INTPAIR-EDGE.supersedes` 同判；rev-19 现行绑定 = **0.41**（外层 2×0.205），逐层 0.41/0.32）⇒ 判定记录把**退役定值**呈现为**现行口径**（记录面 **fail-open**：人/机读者据以误判对间规则 —— 承 CO-210「须引现行定案」同族，但面 = **判定记录**）；且硬编码旧 rev 为**潜在陈旧阈值源**（**实测非惰性**：`net_classes` 在 rev-7/rev-19 间不同）。
- **影响面（如实）**：SI verdict = `widths_ok ∧ skew ≤ drc_rules.diff_pair.intra_pair_skew_mm`，二者皆不取 `net_classes`（`impedance.width_mm_by_layer` 跨 rev **逐字节同**）⇒ **判决未变**（PASS / skew `0.1300 ≤ 0.15` / 34 页）；本件为**记录正确性 + 漂移防护**，非判决翻转。
- **处置**：① 判据源改读现行冻结源 `SPEC_k2_v4.spec-rev-19.json` 并**钉 sha16**（`SPEC_SRC`/`SPEC_SRC_SHA16` + `load_spec()`：缺件/漂移 ⇒ `SystemExit`，**fail-closed**，禁静默降级到旧 rev）；② SI 记录增 `inter_pair_derivation`（现行逐层 0.41/0.32）与 `retired_inter_pair_spacing`（0.875 / `LEGACY_DERIVED` / `replaced_by`，**显式留存** —— 承「退役决策须显式留存」红线）；③ `source` 自述改指 rev-19 + sha16；④ 齿 **+2**（`spec_src_ok` / `spec_src_discriminates`（注入伪造字节必判否 ⇒ 非恒真））并入 rc；⑤ SI 记录 **L5-SI.8→.9**、G7 记录 **L5-G7.8→.9** 且 G7 增「L5 SI 判据源」行。**序不变（仍 50 次）**。
- **修后实测**：SI **verdict=PASS**（`widths_match=True` / `skew 0.1300 ≤ 0.15` / 34 页）；记录 `spec.inter_pair_spacing_mm=**0.41**`、`inter_pair_derivation.by_layer_edge_mm={F.Cu:0.41,B.Cu:0.41,In2.Cu:0.32,In5.Cu:0.32}`、`retired_inter_pair_spacing` 显式留存、`source` = rev-19 + sha16；齿 **4/4 全 True**（含新 2 枚）；独立探针：错 pin16 ⇒ False、注入伪造空 JSON 字节串 ⇒ False（sha **确被比较**）。
- **并存事实（登记，免误判）**：`SPEC_k2_v4.json`（spec_version **1.1.spec-rev-1**，sha16 `0bd52ed48e720b8c`）= **监理级原始冻结点**（`watch.py` FROZEN 所钉）；设计现行源 = `SPEC_k2_v4.spec-rev-19.json`（boundary 冻结四源）。二者**语义不同**，本工具判据一律取 **rev-19**；G7 §5「冻结四源」行沿用 rev-1 冻结点（监理级语义），**不得**与设计现行源混用。
- **诚实边界**：只保证「判据源 = 冻结 rev-19 且 sha 命中」，**不**重判 SI 数值本身；SPEC 升 rev 时须**同 commit** 更新 `SPEC_SRC`/`SPEC_SRC_SHA16`（否则本工具 fail-closed 报错，属**有意**）。

| 工件 | sha16 |
|---|---|
| 工具 `p3_v57_l5_signoff.py`（**CO-217**：判据源 → 冻结 rev-19 + sha pin + 齿 +2 + 退役值留存） | `7618070712518194` |
| 记录 `m13_v57_l5_si_pi_emc_record.json`（**L5-SI.9**：`inter_pair_spacing_mm=0.41` + retired 留存） | `97c867e89fc6df6c` |
| 记录 `m13_v57_l5_g7_record.md`（**L5-G7.9**：+「L5 SI 判据源」行） | `2ab7a29e745b70ff` |
| 登记簿 `input_defect_register_v1.json`（178 项 / OPEN 0） | `b1d8c7130240c4d0` |

> **R-CO217-1**：凡产出判据性 verdict 之工具，其**判据源**须为**现行冻结源**且**钉 sha**（缺件/漂移 ⇒ fail-closed，禁静默降级）；源升级须**同 commit** 双侧更新（源常数 + pin）；**退役定值不得以现行口径呈现**（须标 `kind`/`replaced_by` 并显式留存）。

> **序不变**：本件未改步骤集/序列（承 §82 之 R-CO209-2）。

## 91. CO-218（**L2 自裁 · 冻结源不变性 + 规则源唯一性入机判**）

- **缘起**：§90（CO-217）确立「判据源须为现行冻结源且钉 sha」后，续查**冻结源本身**是否受机判保护 ⇒ 发现其仅由人手复核承载。
- **缺陷 O-1（TOOL_DEFECT · low）**：冻结四源（`SPEC_k2_v4.spec-rev-19.json` / `m13_v57_s1_page_manifest.json` / 冻结板 `k2_v4_8L.kicad_pcb` / `_shared/eda_core/drc_rules.json`）之**不变性**在规范序内**无机判** —— 跨会话仅由**人手复核**（各件「写件时复核」之「4/4 MATCH」）+ **CO-91.2 之一次性断言**（K2 ↔ 容器 `drc_rules.json` 同字节）承载 ⇒ 源漂移**不使序失败**（序只消费当下内容，仍可收敛，boundary 亦仍可写「4/4」）⇒ **判定基据失锚**。**可达性**：K2 副本為**可写**（`-rw-rw-r--`）而容器副本**只读**（`-r--r--r--`）⇒ 「单向漂移」路径真实存在。
- **处置**：runner 增 ① `FROZEN_SOURCES`（4 源 → sha16 pin）+ `FROZEN_SRC_COPIES`（K2 ↔ 容器 `drc_rules` 同字节）；② 纯判据 `frozen_sources_decision()`（`sha16_of`/`bytes_of` 可注入 ⇒ 合成控零落盘；出口 = `ok` / `frozen_source_missing` / `frozen_source_drift` / `rule_source_not_unique`）；③ **静态齿 t34**（缺件 / 漂移 / 副本不同字节 ⇒ 序停机 `static_precheck_failed`，**fail-closed**）；④ 报告增 `frozen_sources` 证据块（逐源 pin/actual + 副本 `identical`）。**齿数 35 → 36（t01..t34）**；**序不变（仍 50 次）**。
- **修后实测**：`frozen_sources_decision(FROZEN_SOURCES, …)` = **ok**；4/4 pin 命中；K2 ↔ 容器副本 `identical=True`；负控（独立探针，内存注入）：错 pin ⇒ `frozen_source_drift`、伪造副本字节 ⇒ `rule_source_not_unique`、缺件 ⇒ `frozen_source_missing`；`--check` **36/36 全 True**（t34 = `t34_frozen_sources_pinned`）。
- **边界（诚实）**：本齿只锚**冻结源**（输入）；**交付板** `k2_v4_8L.l4.kicad_pcb` 属**产物**（随 rev 合法变更 —— CO-144 曾改板）⇒ **不**入冻结 pin；其「本 rev 内不变」由 co120 P5 + 各记录板指纹 + 人手复核承载。

| 工件 | sha16 |
|---|---|
| runner `p3_v57_co164_order_runner.py`（**CO-218**：`FROZEN_SOURCES`/`FROZEN_SRC_COPIES`/`frozen_sources_decision` + 静态齿 t34） | `db80604b81e805e9` |
| 登记簿 `input_defect_register_v1.json`（178 项 / OPEN 0） | `b1d8c7130240c4d0` |

> **R-CO218-1**：凡「**判定基据之锚点**」（冻结输入 / 规则源 / 唯一性断言）须**入规范序机判**（fail-closed），不得仅以人手复核或一次性断言承载；源之**唯一性**（多副本）须机判**同字节**；**产物**（随 rev 合法变更者）不得混入冻结 pin。

> **序不变**：本件未改步骤集/序列（承 §82 之 R-CO209-2）。

## 92. CO-219（**非执行者对抗复评 CO-213..CO-218 + 同会话处置**）

- **对象**：CO-213（复评件与处置）/ CO-214（L5 板指纹消费面机判）/ CO-215（代理面收窄 + 覆盖面齿）/ CO-216（源面判据 AST 收窄）/ CO-217（L5 判据源绑定）/ CO-218（冻结源不变性 + 规则源唯一性）。复评者 = **z79..z84 谱系之外**之 context 归零续接会话；as-found 逐件钉 `3d68891`（sha16 复核一致）；扰动一律**内存注入**（零落盘）。
- **判决 = PASS_WITH_FINDINGS**（findings 2，皆 low）：正控 11 全 True（冻结四源 4/4、交付板未变、`--check` 36/36、序收敛 rc=0 零 diff、oracle PASS 11/11 幂等、co120 PASS 19 齿 `l5_bad=0`、l5_signoff 判别力 True、co206 7/7 + B 前置数据驱动、登记簿 counts 可复算、co124 PASS）；负控 6 全触发。
- **F-1（TOOL_DEFECT · low）表项未名集钉定 ⇒ 删项即空真**：`frozen_sources_decision()`（CO-218）/ `proxy_coverage_decision()`（CO-215）/ `l5_board_binding()`（CO-214）皆**只遍历已登记项** ⇒ 清表或**删单枚 pin**（如期 CO-217 之 SPEC pin）时对应齿仍 **True**；实测最重后果：**删 SPEC pin 后注入 SPEC 漂移仍返 `ok`**（该源不变性检出率**归零**）。同档 t27/t21/t16 **已有**集合等式制 ⇒ 此三处为遗漏。**处置**：三表各加**名集等式**（**不新增齿**，齿数仍 36）+ 自声明面 bump（runner `CO-203.2` / co120 `CO-120.8`）。
- **F-2（TOOL_DEFECT · low）不动点 oracle 前置未达不阻断 + 基线重锚**：`t00` 不成立仍注入/度量，且 `sha_canon` 取自**污染态**（实测 `914b65197ad76b19` ≠ as-found `3b02b97dc9f1f4bc`）；逐案 `finally` 只复原到**案前（污染）态** ⇒ 污染不自愈；实证后果 = 某已闭合登记项被重开为 OPEN 而 `counts.OPEN=0` ⇒ **co124 FAIL_REGISTER_STALE**，人工复原 HEAD 后全绿（上游写入者**未根因定位**，只据可复现工具行为立据）。**处置**：增**前置 fail-fast**（`FAIL_SETTLE_NOT_CONVERGED` + `how_to_recover`；不注入/不度量/不重锚）+ oracle bump `CO-219`（runner `TOOL_REVISION_DECLARED` 双侧同步）。
- **O-1（诚实边界）**：`drc_rules.json` 容器内实存 **5 份**（k2/k1/pciesw4/key_v2 + 根 `_shared`，5/5 同字节）而 `FROZEN_SRC_COPIES` 只钉 **2/5**；K2 各闸仅消费 K2 份 ⇒ 非缺陷（触发 = 改读他份或副本分歧）。**O-3**：未复核 B 路 10L 实做（L1/几何）与外部报价面；CO-219 自身须下一轮复评（禁自评）。

| 工件 | sha16 |
|---|---|
| runner `p3_v57_co164_order_runner.py`（**CO-203.2**：t29/t34 **名集钉定**） | `db80604b81e805e9` |
| co120 闸 `p3_v57_co120_provenance_pin_gate.py`（**CO-120.8**：P5 `L5_RECORD_JSON` 名集钉定） | `28d6211f32318d9b` |
| oracle `p3_v57_co195_fixpoint_uniqueness_oracle.py`（**CO-219**：前置 fail-fast） | `585b983de844603d` |
| 复评件 `m13_v57_CO219_rev19_co213_co218_review.json` | `826b5e625bec0fd9` |
| 登记簿 `input_defect_register_v1.json`（178 项 / OPEN 0） | `b1d8c7130240c4d0` |

> **R-CO219-1**：凡**覆盖面 / 判定基据锚点 / 消费面**之**枚举表**，须以**名集（或集合）等式**机判其内容 —— 不得以「已登记项自洽」代替「登记面完整」（纯判据对空表返 `ok` 属合理设计，但**齿**须钉实表内容）。

> **R-CO219-2**：**先结算**类前置（不动点/收敛类判据）须**fail-closed 阻断**：前置不成立即停（不注入、不度量、不落基线）并给复原指引；禁以**污染态**充当 canonical。

> **序不变**：本件未改步骤集/序列（承 §82 之 R-CO209-2）。

## 93. CO-220（**L2 自裁 · 跨页 y 交错：rev-19 不动 + 触发**）

- **对象**：§77/§82 所记**唯一剩余 L2 自由度** =「**跨页 y 交错**」（lane 之 y 序跨页交错；须改几何、非旋钮可达）。属 **L2**（走廊分配 / 层分配 / 几何）⇒ 依 `LAYOUT_CONSTITUTION` 第二章由本会话**自裁**，不以「等外部输入」悬置。
- **裁定**：**rev-19 不启动该几何变更**，附**触发**。理由 = ① **驱动缺席**（现行定案 A=HDI **无需改设计**；交付件——板 / 打样包 37 payload / L5 三记录 / 全 pin 链——**完备且逐字节稳定**，唯一阻断为外部报价与 DFM 答复；几何变更将**取代**可下单交付态并使打样包与全部 pin 失效，CO-144 改板之教训）；② **受益面窄且已行使**（该自由度只影响 B 路；B 之族上限 **≤24/32** 已由 CO-209 **直接行使**证，§82；A 不依赖 B）；③ 无驱动之「为证而证」不合宪（问题回模型；DRC/探针是核对不是驱动器）。
- **备择项**（皆 **rev 级**，故同此裁）：以该自由度救 B 至 32/32（若成立**可免除外部阻断**，改走标准通道）、层分配重指派以降 HDI 阶数（现需 **3** 次层压）。
- **触发**（满足其一即**立即开新 rev**，并以该几何变更为首动作）：**T1** = A 之 JLC advanced/HDI **DFM 答复否决**（或明示现行 3 阶/孔径不可制）⇒ 转救 B（仍不足则改拓扑 = **L1**，升级 owner）；**T2** = 报价显示 A 代价不可接受**且** B 被救至 32/32 之概率非零 ⇒ 先对该几何族做**直接行使**（承 R-CO209-1）；**T3**（**CO-225 补**：§3「层分配重指派以降 HDI 阶数」原**无触发**，且不采理由为「未知项属**外部** DFM 答复」= **R-CO220-1** 明文所禁之**悬置**形态）= DFM 答复或成本序显示**现行 3 次层压代价不可接受** ⇒ 以「层分配重指派以降 HDI 阶数（**保持 8 层**）」为首动作开新 rev（量化目标：层压次数 **3 → ≤2**）；**若须改层数/叠层拓扑 ⇒ 属 L1，升级 owner**（§78 全族探索之 24/32 系「救 B」目标之证据，非本路径之证据）。
- **边界（诚实）**：本裁定**不**声称「跨页 y 交错无益」；仅裁「**rev-19 无驱动、不以此代价开新 rev**」。该自由度**保留**，触发即用。

| 工件 | sha16 |
|---|---|
| 裁定 `L2_RULING_cross_page_y_interleave_v1.md` | `7d9932dab61508c5` |
| 交付板 `k2_v4_8L.l4.kicad_pcb`（本裁定**未改**） | `d4e81f647be7f980` |
| runner `p3_v57_co164_order_runner.py` | `db80604b81e805e9` |

> **R-CO220-1**：L2 自由度之「**不动**」须以**自裁 + 触发**落 boundary；**禁**以「等外部输入/等 owner」形式**悬置**（承第二章定层裁定）。

> **序不变**：本件未改步骤集/序列（承 §82 之 R-CO209-2）。

## 94. CO-221（**L2 自裁 · L5 判据记录之自声明面与登记簿同步**）

- **缺陷 F-1（TOOL_DEFECT · low）**：`tools/p3_v57_l5_signoff.py` 所生成之 SI/PI/EMC 记录**硬编码**「阻抗符合性 **NOT_DEMONSTRATED**（**开放项 CO-53**）」；而登记簿对应项 `implementation_deviation:R3-2_asbuilt_interpair_edge` 早已 **CLOSED**（域声明由 CO-147 R2 在 L2 内裁定；B.Cu/In5 已几何闭合；终判交 **JLC 阻抗控制服务**）⇒ **已闭项以「开放项」口径呈现**（承 R-CO217-1「退役/已闭定值不得以现行口径呈现」；与 CO-213 F-2 同族之陈旧自声明）。方向 = **fail-open**（读者/板厂据记录误判尚欠工程项）。
- **处置**：口径**逐处同步**至登记簿现行表述（本工程**不自证**阻抗符合性 ⇒ 交 JLC 阻抗控制服务终判；原「开放项 CO-53」表述**已撤**）；记录经生成器重出，boundary pin 再对齐。**R-CO221-1**。
- **修后实测**：记录内**不再**出现「开放项 CO-53」；`--check` **36/36 全 True**；序收敛 rc=0 / 2 轮；co120 P5 消费面机判仍 PASS（`l5_bad=0`）。
- **边界（诚实）**：本次仅**同步口径**，未改阻抗符合性之判据（终判本就在 JLC 服务侧），亦未触动几何。

| 工件 | sha16 |
|---|---|
| L5 生成器 `tools/p3_v57_l5_signoff.py` | `7618070712518194` |
| L5 SI/PI/EMC 记录 `m13_v57_l5_si_pi_emc_record.json` | `97c867e89fc6df6c` |
| L5 DFM/DFT 记录 `m13_v57_l5_dfm_dft_record.json` | `6632179e1ef63183` |
| L5 FAB 记录 `m13_v57_l5_fab_record.json` | `791012e88b514faa` |
| 登记簿 `input_defect_register_v1.json` | `b1d8c7130240c4d0` |
| 交付板 `k2_v4_8L.l4.kicad_pcb`（本件**未改**） | `d4e81f647be7f980` |

> **R-CO221-1**：判据记录之**自声明文本**须与**登记簿现行状态**同源同步（已闭项不得以「开放项」呈现）；生成器硬编码之状态词须随裁定**同 commit** 更新（承 R-CO208-1 / R-CO217-1）。

> **序不变**：本件未改步骤集/序列（承 §82 之 R-CO209-2）。
## 95. CO-222（**L2 自裁 · U6 域 GND 过孔阵列：散文建议升格为裁定 + 量化触发**）

- **对象**：`L5/jlc_package/ORDER_NOTES.md` §6 与 U6 热定案所载「另建议下一轮几何修订补强 U6 域 GND via 阵列」——**仅散文**（无裁定/触发/量）。属 **L2**（热机械 / 过孔策略 / 几何）⇒ 自体行使自裁。
- **现状**：定案 O2（30×30 铝散热片 + 1.0 ℃/W 垫 + ~2 m/s 风冷，`θJA_eff=11.0`）下四工况 Tj = 91.7 / 106.0 / 103.8 / **117.0** ℃（上限 120）⇒ 最重余量 **3.0 ℃**（薄）。
- **裁定**：① **rev-19 不改几何**（承 CO-220 之据：驱动缺席；交付件完备逐字节稳定；改板取代可下单交付态）；② 建议**升格为条件动作** + **量化目标**：**T1** 首件实测 `Tj(U6) > 117.0 ℃` 或散热路径未按 O2 实施 ⇒ 立即开新 rev，以「GND via 阵列使 `θJA_eff ≤ 9.5 ℃/W`（最重工况余量 ≥ 8 ℃）」为首动作（阵列密度/节距由热模型重跑定，禁拍脑袋）；**T2** 若 U6 域几何因他因修订 ⇒ 同 rev 一并补阵（零边际成本）；③ 门限取 **117 ℃** 以留裕度。
- **边界（诚实）**：本件**未**做阵列之热-电耦合量化（须热模型重跑，属新 rev 前置）；仅把散文建议升格为**带门限与量化目标之动作**。阵列仅增 GND 缝合，不改信号层分配 ⇒ 不影响现行 SI/PDN 结论。

| 工件 | sha16 |
|---|---|
| 裁定 `L2_RULING_u6_gnd_via_array_v1.md` | `9c74ed4031298084` |
| U6 热定案 `L2_RULING_u6_thermal_mitigation_v2.md` | `cec7bd86d39b71c8` |
| 交付板 `k2_v4_8L.l4.kicad_pcb`（本裁定**未改**） | `d4e81f647be7f980` |

> **R-CO222-1**：裁定文件/随单内之**工程建议**若涉及几何或工艺动作，须以「**裁定 + 触发（含门限/量化目标）**」落入 boundary；**禁**以散文建议悬置（承 R-CO220-1）。

> **序不变**：本件未改步骤集/序列（承 §82 之 R-CO209-2）。
## 96. CO-223（**L2 自裁 · U6 域 GND via 阵列之「义务时点」对账**）

- **对象**：`L2_RULING_u6_thermal_v1.md` §R4-1 将「U6 域 GND via 阵列补强」列为**既定义务**，与 §95（CO-222）之「rev-19 **不改几何** + 条件动作」构成**口径分歧**（承 R-CO208-1 口径逐处同步）。
- **处置**：对旧件**只加追注、不重写历史正文**（承 CO-213 F-3 之伪史防范）；追注明载「**本节口径以 CO-222 为准**」：阵列不在 rev-19 交付范围（现行板按 O2 达成 Tj 117.0 ℃ ≤ 120），改为条件动作（T1 门限 117.0 ℃ / 量化目标 `θJA_eff ≤ 9.5 ℃/W`；T2 同 rev 一并补阵）。**R-CO223-1**。
- **修后实测**：全 L2 裁定件扫描**不再有**与 §95 冲突之「义务时点」表述；`--check` **36/36 全 True**；序收敛 rc=0 / 2 轮。

| 工件 | sha16 |
|---|---|
| L2 裁定 `L2_RULING_u6_thermal_v1.md` | `2c41056fc3a4de05` |
| L2 裁定 `L2_RULING_u6_thermal_mitigation_v1.md` | `1273cd81a755108b` |
| 随单 `L5/jlc_package/ORDER_NOTES.md` | `baa49660e280b510` |
| 交付板 `k2_v4_8L.l4.kicad_pcb`（本件**未改**） | `d4e81f647be7f980` |
> **R-CO223-1**：同一工程动作之**义务时点**（既定义务 / 条件动作 / 已撤）在**全部裁定件与随单**须**同源一致**；版本升级致口径变更者，须对旧件加**追注**明示以何件为准（禁重写历史正文，承 CO-213 F-3）。

> **序不变**：本件未改步骤集/序列（承 §82 之 R-CO209-2）。
## 97. CO-224（**L2 自裁 · U6 阵列「义务时点」：CO-223 声明↔实现 divergence 补正 + 随单口径同步**）

- **对象（承 R-CO223-1；as-found `d95f719`）**：§96（CO-223）声明「对旧件**只加追注、不重写历史正文**」+「**修后实测**：全 L2 裁定件扫描**不再有**与 §95 冲突之「义务时点」表述」。**本会话实测证伪**：① `L2_RULING_u6_thermal_v1.md` §R4-1 仍载「**既定义务**」（无追注）；② `L2_RULING_u6_thermal_mitigation_v1.md` §R5-3 仍载「由**义务**降为**可选项**」（**第三种**口径，无追注）；③ 随单 `ORDER_NOTES.md` §6 仍载散文「另建议下一轮几何修订补强 U6 域 GND via 阵列」⇒ 声明↔实现漂移，方向 fail-open（承 R-CO208-1 / R-CO213-3 / R-CO217-1 / R-CO221-1）。
- **根因**：①② 两件裁定 md 为**序内生成物**（步 `co148_thermal_ruling` / `co149_thermal_mitigation_derive`）—— 手改**产物**会被下一次收敛覆写；CO-223 未触及**生成器** ⇒ 追注**从未落地**（故 §96「修后实测」当时**不成立**）。
- **处置**：① 追注写入**生成器**（`p3_v57_co148_thermal_ruling.py` / `p3_v57_co149_thermal_mitigation_derive.py`），明载「义务时点**以 CO-222 为准**（条件动作 T1/T2）」；② §25（CO-148 记录）/§26（CO-149 记录）历史正文加**追注**；③ 随单 §6 改述为**条件动作 + 门限**（撤散文建议）；④ 三处自声明面同 commit bump：CO-148.1→**CO-148.2**、CO-149.1→**CO-149.2**、CO146-PKG.10→**CO146-PKG.11**（承 R-CO208-1）。**R-CO224-1**。
- **载明面名集（7 处 = 6 个可 pin 面 + 本件 boundary；R-CO219-1 式枚举 —— 删项即空真，故以名集等式对账）**：
| 载明面 | sha16 |
|---|---|
| L2 裁定件 `L2_RULING_u6_thermal_v1.md`（§R4-1 + CO-224 追注） | `2c41056fc3a4de05` |
| L2 裁定件 `L2_RULING_u6_thermal_mitigation_v1.md`（§R5-3 + CO-224 追注） | `1273cd81a755108b` |
| L2 裁定件 `L2_RULING_u6_gnd_via_array_v1.md`（CO-222 定案件） | `9c74ed4031298084` |
| 随单 `L5/jlc_package/ORDER_NOTES.md` §6（条件动作 + 门限） | `baa49660e280b510` |
| 包内裁定副本 `06_rulings/L2_RULING_u6_thermal_v1.md` | `2c41056fc3a4de05` |
| 包内裁定副本 `06_rulings/L2_RULING_u6_thermal_mitigation_v1.md` | `1273cd81a755108b` |
| 本件 boundary（§25/§26 追注 + §95/§96/§97；自身不 pin sha） | — |

- **追注（CO-225 · F-4）**：上表名集之**域** = 所声明 grep 目标（`L2/*.md` + 随单 + 包内副本 + boundary）—— **不含** `L2/input_defect_register_v1.json`；实测该件 `items[22].disposition` 亦载同一义务时点口径（与 CO-222 一致，**无 fail-open**）⇒ 名集**域**须显式声明；该第 8 面之 pin 见 §98（承 R-CO219-1 名集等式；与 CO-96 F-4「scope 缺口」同族）。

- **修后实测（本会话，命令可复现）**：`grep -rn 'GND via 阵列' pm_gate/artifacts/k2_v4/L2/*.md pm_gate/artifacts/k2_v4/L5/jlc_package/ORDER_NOTES.md pm_gate/artifacts/k2_v4/L5/jlc_package/06_rulings/*.md pm_gate/artifacts/k2_v4/L3/mcio_feas_step2/m13_v57_w3_joint_assignment_boundary_v1_82.md` ⇒ 命中面**恰为上表 7 处**（名集等式：无未登记载明面、无缺项）；逐处皆载「**以 CO-222 为准**」或 T1/T2 门限。`--check` **36/36 全 True**；序收敛 rc=0 / 2 轮；打样包牙齿全 True；交付板 `d4e81f647be7f980` **逐字节未变**。
- **边界（诚实）**：本件只做**口径对账 + 追注**，**不改几何/不改板**（承 CO-220/CO-222 之据）；阵列热-电耦合量化仍属新 rev 前置（见 §95）。

> **R-CO224-1**：声明「已对旧件加追注 / 全件同源」者，其修后证据须为**本会话实测**（承 R-CO213-3）；被声明的载明面若为**序内生成物**，追注须写入**生成器**（不得只改产物），同 commit bump 自声明面（承 R-CO208-1）；载明面须以**名集等式**枚举对账（承 R-CO219-1：不得只遍历已登记项）。

> **序不变**：本件未改步骤集/序列（承 §82 之 R-CO209-2）。
## 98. CO-225（**非执行者对抗复评 CO-219..CO-224 + 同会话处置**）

- **对象（as-found 钉 `3fe75ff`）**：§92..§97（CO-219..CO-224 之记录）+ 三件 L2 裁定件 + 打样包随单 + `--check` 静态齿面。复评者 = **context 归零之非执行者会话**（与 §92..§97 作者谱系无重叠 ⇒ 六节**全部**在对象内，无自评豁免面）。
- **F-1（TOOL_DEFECT · 中）**：§94（CO-221）与 §96（CO-223）**在记录内指纹数 = 0**；boundary 全 **94 节**中带 `| 工件 | sha16 |` 表者 **85**（例外仅 §1..§7 早期节）⇒ 两节为**唯一现代例外**，违 **R-CO212-1**（pin 缺失即 fail-closed）。**根因**：该红线**无机判齿** ⇒ 违例态下 `--check` 仍全绿（同 CO-219 F-1「空真」族）。**本会话实测判别力**：HEAD 版 runner `--check` = **36/36 全 True**（违例不可见）；工作树版（+t35）= **FAIL**，逐臂诊断唯一失败臂 = ① 实件面（`boundary_fp_missing() == [94, 96]`），② 名集等式臂与正/负控皆 True（36 齿 == 声明−t35）⇒ **齿非空真**。**处置** = ① §94/§96 补指纹表；② 入机判 t35。
- **F-2（TOOL_DEFECT · 低）**：§93 §3 备择项「层分配重指派以降 HDI 阶数」**无触发**，不采理由为「**未知项属外部** DFM 答复」= **R-CO220-1** 明文所禁之**悬置**形态；且该表述**同源于手写裁定件** `L2_RULING_cross_page_y_interleave_v1.md`（第 17 行）—— 只补 boundary = 同源只补一半，反蹈 CO-223/224 覆辙。**处置** = ① §93 补 **T3**；② 裁定件加**追注**（T3 + 明示「不构成悬置」）；③ §98 以名集等式对账两处（见下）。
- **F-3（叙述 · 已闭；不入簿）**：§96（CO-223）之「修后实测」当时**不成立**（追注未落生成器）—— 已由 **CO-224**（§97）证伪并闭合；本节不复裁。
- **F-4（TOOL_DEFECT · 低；本会话新发现）**：§97 声明「命中面**恰为上表 7 处**（无未登记载明面）」，但其名集**域** = 所声明 grep 目标（md 件）⇒ **漏** `L2/input_defect_register_v1.json`（`items[22].disposition` 亦载该义务时点口径；实测与 CO-222 一致 ⇒ **无 fail-open**，属**名集域收窄**之「声明强于实测」）。承 R-CO219-1 名集等式 / CO-96 F-4「scope 缺口」同族。**处置** = ① §97 加**追注**明示名集域 + 登记该第 8 面；② §98 以名集等式复核（8 面）。
- **正控（本会话实测）**：§92 pin 逐件对上（runner 动态 pin / co120 `28d6211f32318d9b` / oracle `c24f3e983c31e589` / 复评件 `826b5e625bec0fd9` / 登记簿 `03d0b7455130d319`）；CO-219 F-1 之三处**名集等式**（t34 `FROZEN_SOURCES` / t29 `PROXY_HELPERS_PINNED`+`PROXY_RESIDUAL_EXPLICIT` / co120 `_recs_pinned`）**在场**；oracle 前置 fail-fast（`FAIL_SETTLE_NOT_CONVERGED` + `how_to_recover`，`revision` = `CO-219`）在场；§93 pin 3/3、§95 pin 2/2 与实件一致；§94「记录内不再出现『开放项 CO-53』」**实测成立**（L5 记录命中 **0**；登记簿 `co221:F-1` = CLOSED）；CO-222 门限（T1 **117.0 ℃** / 目标 `θJA_eff ≤ 9.5 ℃/W`）在裁定件在场。
- **处置**：① **补** §94/§96 在记录内指纹表；② §93 **+T3** 且裁定件**追注同步**（F-2）；③ §97 **追注**（F-4）；④ **入机判**：runner 静态齿 **t35_judgment_surface_pinned**（**名集钉定双臂** —— (i) boundary **每节**须带在记录内指纹，缺者须在**显式历史豁免名集** `BOUNDARY_SECTION_FP_EXEMPT = {1..7}`；(ii) runner **静态齿名集**须等于 `STATIC_CHECKS_DECLARED`（防静默删齿）；两臂皆带正/负控）；⑤ 登记簿入册 **`co225:F-1/F-2/F-4`**（TOOL_DEFECT、CLOSED；F-3 为叙述类不入簿）；⑥ report revision → **CO-203.3**。**R-CO225-1**。
- **修后实测（本会话，命令可复现）**：t35 **修前 FAIL / 修后 PASS**；`--check` **37/37 全 True**；序收敛 rc=0 / **2 轮**；oracle PASS（11 齿 / 幂等）；co120 / co124 / L5 签署全绿；打样包 **29/29**（37 payload）；冻结四源 **4/4**；交付板 `d4e81f647be7f980` **逐字节未变**。
- **边界（诚实·残余）**：(i) 臂只判「该节**有** pin 表」—— pin 表**内容**之完备性由各节自身 / co120 / co135 citation 扫描判；(ii) 臂有**自指边界**（删「齿 **及**其声明」仍静默，同 CO-215 惯例）；§94/§96/§98 之 pin 行以 `if _p.exists()` 门控 ⇒ **不可读即静默删行**（非 fail-closed；补偿 = co124 对登记簿/裁定件之缺件机判）。本件**不**声称已覆盖「红线是否被机判」之全部形态，仅覆盖「记录内指纹 + 静态齿名集」两面。

| 工件 | sha16 |
|---|---|
| runner `p3_v57_co164_order_runner.py`（**CO-203.3** / t35 名集钉定） | `db80604b81e805e9` |
| 裁定 `L2_RULING_cross_page_y_interleave_v1.md`（**+F-2 追注 / T3**） | `7d9932dab61508c5` |
| 裁定 `L2_RULING_u6_gnd_via_array_v1.md`（CO-222 定案件；未改） | `9c74ed4031298084` |
| 登记簿 `input_defect_register_v1.json`（+co225:F-1/F-2/F-4） | `b1d8c7130240c4d0` |
| 打样包 `L5/jlc_package/MANIFEST.json` | `61ed16118f13611f` |
| 随单 `L5/jlc_package/ORDER_NOTES.md` | `baa49660e280b510` |
| 交付板 `k2_v4_8L.l4.kicad_pcb`（本件**未改**） | `d4e81f647be7f980` |

- **名集等式（F-2 / F-4 处置之对账面）**：以 `grep -rn '层分配重指派' pm_gate/artifacts/k2_v4/L2/L2_RULING_cross_page_y_interleave_v1.md pm_gate/artifacts/k2_v4/L3/mcio_feas_step2/m13_v57_w3_joint_assignment_boundary_v1_82.md` 判 —— 两处**皆须**载 T3 / 追注（无未登记载明面、无缺项）；本件实测两处皆备。

> **R-CO225-1**：**判定面之完整性须名集钉定** —— ① boundary **每节**须带「在记录内指纹」（承 R-CO212-1「pin 缺失即 fail-closed」），缺者须在**显式历史豁免名集**；② 执行器**静态齿名集**须钉定（防静默删齿 ⇒ 判据面空真）；两臂皆须正/负控。**红线所禁/所要求之形态若无机判齿，即为空真。**

> **序不变**：本件未改步骤集/序列（承 §82 之 R-CO209-2）。
## 99. CO-226（**L2 自裁 · 承 R-CO217-1：跨源判据语义绑定 + 退役显式留存 ⇒ 机判化**）

- **对象/缘起**：R-CO217-1 要求「凡产出判据性 verdict 之工具，其**判据源**须为**现行冻结源**且钉 sha；**退役定值不得以现行口径呈现**」。CO-217 只把 L5 工具之 **SPEC 读取**改为现行源，但 **SI 等长窗口判据**仍**直接消费**共享规则件 `_shared/eda_core/drc_rules.json` 之 `diff_pair.intra_pair_skew_mm`（**副本**）；且该副本把 SPEC **已显式退役**之 legacy `0.875`（`retired_inter_pair_spacing_0p875_v1`，kind=LEGACY_DERIVED）以**现行口径**呈现（副本 `inter_pair_spacing` = 0.875 vs SPEC rev-19 = 0.41）⇒ 两处红线**无机判齿**（属 R-CO225-1 之「空真」族）。
- **机判实测（本会话，判别力）**：① 真源/副本**逐键对照**（键映射名集）：`p_gap` 0.175/0.175、`p_width` 0.205/0.205、`intra_pair_skew_mm` 0.15/0.15、`target_zdiff` 85.0/85.0 **皆等**；`inter_pair_spacing` = **SPEC 0.41 vs 副本 0.875**（**分歧**）⇒ 以**空分歧登记**注入纯判据 = `divergence_unregistered`（**修前 FAIL**，证明齿非空真）；② 副本注入漂移（`intra_pair_skew_mm` 0.99）驱动 L5 工具 ⇒ `SystemExit`（**fail-closed**，且**记录零污染**：实测记录仍 `L5-SI.10` / 0.15/0.15 / PASS）。
- **裁定（L2 自裁）**：① **等长窗口判据源 = SPEC 真源**（`net_classes.PCIe85.intra_pair_skew_mm`，sha 由 `load_spec()` 钉）；`drc_rules` 副本**降为交叉校验面**（分歧 ⇒ fail-closed，禁静默降级）；两者一并入 SI 记录（`skew_rule_mm` / `skew_rule_source` / `skew_rule_copy_mm` / `skew_rule_copy_source`）。② **跨源绑定入机判**（runner 静态齿 **t36_cross_source_semantics_bound**）：键映射**名集钉定**（`CROSS_SOURCE_KEYMAP`）+ 副本键**域钉定**（映射集 ∪ 非判据名集 == 副本实键集 ⇒ 新增/删键即停机）+ **被消费键**（`p_gap` / `p_width` / `intra_pair_skew_mm`）两侧相等 + 其余两侧分歧须入**显式分歧登记**（字段完备且登记值 == 副本现值）。③ **分歧显式留存**：`inter_pair_spacing` 登记为副本漂移（SPEC 已退役 0.875；现行 **0.41 外层 / 0.32 内层**）。④ 自声明面同步：`L5-SI.9 → L5-SI.10`（G7 记录 `L5-G7.9 → L5-G7.10`）/ runner `CO-203.3 → CO-203.4`。**R-CO226-1**。
- **名集等式（实测）**：被消费键名集 `{p_gap, p_width, intra_pair_skew_mm}` 对两侧消费者对应（`l5_signoff` 等长窗口 / `co81` .kicad_pro 网类规则比对）；副本实键集 == 映射名集 ∪ 非判据名集（`cross_source_domain_decision` 实测 `ok`）。
- **边界（诚实·残余）**：① 本件**不改共享件**（`_shared/eda_core/drc_rules.json` 为 **5 工程同字节**冻结件，K2 侧无单方面改动权）；该副本之**单板特判**（含 K2 SPEC 派生量 + `net_prefix=PCIE`）违容器 AGENTS.md §3「共享层零单板特判」⇒ 登记为**容器级**待处置（登记簿 `co226:F-1.next`）。② t36 只判**键级**语义一致（数值相等 / 已登记分歧），不判**同名异义**之语义漂移。③ 分歧登记为**显式白名单**（登记即放行）⇒ 防护依赖「新增分歧必入登记」之自律+ **域钉定**（副本新增键即停机）之机判。

| 工件 | sha16 |
|---|---|
| runner `p3_v57_co164_order_runner.py`（**CO-203.4** / t36 跨源绑定） | `db80604b81e805e9` |
| L5 签署 `tools/p3_v57_l5_signoff.py`（**L5-SI.10** / 等长窗口真源绑定） | `7618070712518194` |
| 真源 `SPEC_k2_v4.spec-rev-19.json` | `5f72182a2616392c` |
| 副本 `_shared/eda_core/drc_rules.json` | `0a459839e15960b8` |
| 登记簿 `input_defect_register_v1.json`（+co226:F-1） | `b1d8c7130240c4d0` |
| 交付板 `k2_v4_8L.l4.kicad_pcb`（本件**未改**） | `d4e81f647be7f980` |

> **R-CO226-1**：判据源与**共享层副本**并存者，须以「**键映射名集 + 副本域钉定 + 被消费键一致性**」机判绑定；真源升级致副本漂移时，副本**须显式登记**（含退役依据与取代者）后方可放行 —— 禁「副本**静默**充当判据源」（承 R-CO217-1「判据源须为现行冻结源」/ R-CO219-1 名集等式 / R-CO225-1 无机判齿即空真）。

> **序不变**：本件未改步骤集/序列（承 §82 之 R-CO209-2）。
## 100. CO-227（**L2 自裁 · 承 R-CO223-1 / R-CO224-1：义务时点跨载明面同源 + 载明面名集等式 ⇒ 机判化**）

- **缘起**：CO-222 之 U6 域 GND via 阵列义务时点，其**载明面枚举**自 CO-224 起以「名集等式」自称（§97 之 7 面），但该等式**无机判齿**；CO-225 F-4 实测证明其域 = 「所声明 grep 目标」= **域收窄**（漏 `L2/input_defect_register_v1.json` 第 8 面）⇒ 承 **R-CO223-1**（同一动作之义务时点须跨件同源）与 **R-CO224-1**（载明面须名集等式枚举）之形态**无机判齿即为空真**（R-CO225-1）。
- **裁定（L2 自裁）**：① 义务载明面**域显式**（`OBLIGATION_DOMAIN_ROOTS` = L2 裁定件+登记簿 / 打样包 / boundary 自身）+ **名集等式**（域内命中集 == `OBLIGATION_MARKERS_DECLARED` ∪ `OBLIGATION_DOMAIN_EXEMPT`，**双向**：既禁未登记载明面，亦禁声明面缺席）；② 每面须命中**同源锚**（`CO-222` ∧ `条件动作`）；③ 入机判 runner 静态齿 **t37_obligation_same_source_bound**（正/负控齐备）；④ 机制**通用**：后续同类义务（条件动作 + 触发）以同一登记表扩展 —— 新增载明面未入表即停机。**R-CO227-1**。
- **实测（判别力，本会话）**：实件域内命中 = **8 面**、逐面同源锚（`CO-222` / `条件动作`）齐备 ⇒ t37 **PASS**；以 CO-224 之**7 面 md 域**（F-4 之形态）驱动纯判据 ⇒ `undeclared_surface`（**修前形态必 FAIL**）；把漏面**显式豁免** ⇒ `ok`（豁免须显式，非静默通过）；声明面缺席 ⇒ `declared_surface_absent`。
- **未做（诚实）**：本件不改几何/板/共享件；亦**不**为其余红线建全量映射（全量 173 条手工映射违「问题回模型」且必流于形式）⇒ 按需逐案机判化，**不**声称红线面已完备覆盖；t37 只判「载明面同源 + 域显式」，**不**判义务本身之工程正确性（由 §95 定案件与 T1/T2 触发承载）。

| 工件 | sha16 |
|---|---|
| runner `p3_v57_co164_order_runner.py`（**CO-203.5** / t37 义务同源齿） | `db80604b81e805e9` |
| 登记簿 `input_defect_register_v1.json`（+co227:F-1） | `b1d8c7130240c4d0` |
| 定案件 `L2_RULING_u6_gnd_via_array_v1.md` | `9c74ed4031298084` |
| 随单 `L5/jlc_package/ORDER_NOTES.md` | `baa49660e280b510` |
| 交付板 `k2_v4_8L.l4.kicad_pcb`（本件**未改**） | `d4e81f647be7f980` |

> **R-CO227-1**：同一工程动作之「义务时点」类记录，其**载明面须域显式 + 名集等式机判**，且每面须命中**同源锚**；后续同类义务以**同一登记表**扩展（承 R-CO223-1 跨件同源 / R-CO224-1 名集等式 / R-CO219-1 枚举完整性 / R-CO225-1 无机判齿即空真）。

> **序不变**：本件未改步骤集/序列（承 §82 之 R-CO209-2）。
## 101. CO-228（**L2 自裁 · 承 R-CO219-1：等长覆盖面名集等式 + kind 词表域钉定 ⇒ 机判化**）

- **发现 F-1（TOOL_DEFECT · low-mid）**：SI 等长判定之**页覆盖面**由 `m13_v57_w3_joint_assignment.json`（**非冻结、非序内 watch** 之 L3 件）之 `kind` 过滤**隐含定义**：① 未识别 kind 一律 `else: continue` ⇒ **静默跳过**；② 该件与**冻结页清单** `m13_v57_s1_page_manifest.json`（`n_pages` = 34）之间**无机判绑定**；③ 两件 kind 词表**不一致**（清单 `refclk_pass` / 图纸 `refclk`）且无声明映射。⇒ 覆盖面可**无声缩水**而 `skew_ok = skew_max ≤ rule` 仍 PASS（方向 fail-open；承 R-CO219-1 名集等式 / R-CO225-1「无机判齿即空真」）。
- **实测（判别力，本会话）**：实件两件 page_id 集**完全相同**（34/34，双向差集空）⇒ t38 **PASS**；**注入**未识别 kind ⇒ l5 `SystemExit`（`未登记 kind ['weird_kind']`）；**注入**删一页 ⇒ `SystemExit`（`冻结清单 34 页 vs 实测覆盖 33 页，清单独有 ['PCIE_REFCLK1/input']`）——两路径皆**记录零污染**。
- **裁定（L2 自裁）**：① **词表域钉定**：`PAGE_KIND_VOCAB_DECLARED`（清单 kind → 图纸 kind）**双向**（键集 == 清单 kind 集 ∧ 值集 == 图纸 kind 集）；② **名集等式**：冻结清单页集 == 图纸页集（**双向**）+ `n_pages` 自述一致；③ **l5 端 fail-closed**：未识别 kind 与名集不等**皆停机**（禁静默跳过 / 禁静默缩水）；④ 记录增 `skew_pages_expected` / `skew_pages_expected_sha16` / `skew_pages_coverage_source`（覆盖源指纹：图纸 sha16 + 清单 sha16 + 词表映射）；⑤ 入机判 runner 静态齿 **t38_page_coverage_bound**（正/负控齐备）。自声明面同步：`L5-SI.10 → L5-SI.11`（G7 `L5-G7.10 → .11`）/ runner `CO-203.5 → CO-203.6`。**R-CO228-1**。
- **边界（诚实·残余）**：① 本件所钉为**两件之一致性**（不变量：图纸页集 == 冻结清单页集）；`m13_v57_w3_joint_assignment.json` 本身**非冻结源、亦不在序内 watch 名单** ⇒ 其**身份**（内容变更而页集不变者）**仍无机判 pin** —— 该 pin 面登记为残余（登记簿 `co228:F-1.next`）。② 覆盖为**页**粒度，不判页内**差对存在性**（页内缺 P/N 会 `KeyError` 而非静默）。

| 工件 | sha16 |
|---|---|
| runner `p3_v57_co164_order_runner.py`（**CO-203.6** / t38 覆盖面齿） | `db80604b81e805e9` |
| L5 签署 `tools/p3_v57_l5_signoff.py`（**L5-SI.11** / 覆盖面 fail-closed） | `7618070712518194` |
| L5 SI 记录 `m13_v57_l5_si_pi_emc_record.json` | `97c867e89fc6df6c` |
| 冻结页清单 `m13_v57_s1_page_manifest.json` | `a8ef3ea8ecff99d7` |
| 覆盖源 `m13_v57_w3_joint_assignment.json`（**非冻结**） | `60cbd331836e52b7` |
| 登记簿 `input_defect_register_v1.json`（+co228:F-1） | `b1d8c7130240c4d0` |
| 交付板 `k2_v4_8L.l4.kicad_pcb`（本件**未改**） | `d4e81f647be7f980` |

> **R-CO228-1**：**覆盖面之枚举面**（页/条目/格）与**其声明源**之间须以**名集等式（双向）+ 词表域钉定（双向）**机判；未识别枚举值**禁静默跳过**（须 fail-closed 或入显式白名单）—— 覆盖面缩水不得使 verdict 仍 PASS（承 R-CO219-1 / R-CO225-1 / R-CO227-1）。

> **序不变**：本件未改步骤集/序列（承 §82 之 R-CO209-2）。
## 102. CO-229（**L2 自裁 · 承 R-CO218-1：等长判定几何源之锚点入规范序机判**）

- **缘起（闭 CO-228 残余）**：§101 记「覆盖源 `m13_v57_w3_joint_assignment.json` **非冻结源、非序内 watch** ⇒ 其**身份**无机判 pin」为**未闭残余**。本件处置之：SI 等长判定之**几何**取自该件，而其身份与上游锚点仅以该件**自述**（`inputs_sha` / `frozen_sha_check`）承载 ⇒ 属 **R-CO218-1** 所指「一次性断言 / 人手复核」形态，漂移不可见（方向 fail-open）。
- **实测（本会话）**：该件自述 **16 项**上游指纹**全部可核**（按其声明 sha256 于 L3 树 / `_shared/eda_core` 反查命中，逐项内容一致）；其 `frozen_sha_check.match` **14/14 全 True**、`drift = []`；**身份 sha16 = `60cbd331836e52b7`**（与 §78 所记「构造器产出与冻结图纸逐字节同」一致）。判别力：篡改声明值 ⇒ `provenance_self_declaration_mismatch`；自述缺一键 ⇒ `provenance_key_drift`；实件内容漂移 ⇒ `provenance_drift`；不可读 ⇒ `provenance_unreadable`。
- **裁定（L2 自裁）**：① **身份 pin**：`SI_GEOM_SOURCE_SHA16 = 60cbd331836e52b7`（漂移即停机）；② **上游锚点逐项独立复算**：`SI_GEOM_PROVENANCE_DECLARED`（**16 项**逻辑键 → 路径 + sha256）与图纸自述做**键集等式 + 自述↔实件一致**（缺件/漂移即停机）；③ **自述诚实性**：`match` 须全 True 且 `drift` 为空；④ 入机判 runner 静态齿 **t39_si_geom_source_anchored**（正/负控齐备，零落盘）。自声明面同步：runner `CO-203.6 → CO-203.7`。**R-CO229-1**。
- **边界（诚实·残余）**：① 本件钉**身份**与**上游锚点**，**不**重算几何正确性（几何由 CO-62/§78 族证据承载）；② 上游 16 项中多数为 L3 早期件（非序内 watch）⇒ 本件使其**内容一致性**机判化，但其**再生/版本**语义仍属 L3 阶段（本件不声称覆盖 L3 全链复现）；③ 该 pin 为 **rev-19 专属**：新 rev 变更该件须**显式**更新 pin 与锚点表（否则 t39 停机）。

| 工件 | sha16 |
|---|---|
| runner `p3_v57_co164_order_runner.py`（**CO-203.7** / t39 几何源锚定） | `db80604b81e805e9` |
| 几何源 `m13_v57_w3_joint_assignment.json`（**身份 pin**） | `60cbd331836e52b7` |
| 上游锚点 `m13_v57_s1_page_manifest.json`（冻结源） | `a8ef3ea8ecff99d7` |
| 上游锚点 `SPEC_k2_v4.spec-rev-19.json`（冻结源） | `5f72182a2616392c` |
| 登记簿 `input_defect_register_v1.json`（+co229:F-1） | `b1d8c7130240c4d0` |
| 交付板 `k2_v4_8L.l4.kicad_pcb`（本件**未改**） | `d4e81f647be7f980` |

> **R-CO229-1**：凡**判定性 verdict** 所消费之工件，若**非冻结源且不在序内 watch**，其**身份**（sha pin）与**上游锚点**（逐项 sha256 独立复算 + 键集等式 + 自述↔实件一致）须**入规范序机判**（fail-closed）—— 禁以工件**自述**（`inputs_sha` / 自检块）充当唯一基据（承 R-CO218-1「判定基据之锚点须入规范序机判」/ R-CO228-1 覆盖面）。

> **序不变**：本件未改步骤集/序列（承 §82 之 R-CO209-2）。
## 103. CO-230（**非执行者对抗复评 CO-225..CO-229 + 同会话处置**）

- **缘起**：handoff z92 §5.5 复评债 =「下一轮复评须覆盖 **CO-225..CO-229**（另一会话，禁自评；as-found 钉 `fdb72a2`）」⇒ 本件承该债并清偿（同 CO-219 / CO-225 之例）。
- **对象（as-found 钉 `fdb72a2`）**：§98..§102（CO-225..CO-229 之记录）+ 三件 L2 裁定件 + 打样包随单 + `--check` 静态齿面（41 齿）。复评者 = **非执行者**（context 归零之**新会话**；**未参与 CO-225..CO-229 之任何撰写**）⇒ 五节**全部**在对象内，无自评豁免面。
- **F-1（TOOL_DEFECT · 中）**：t35 **臂① 之枚举域 = boundary 文档自述之节集**（`boundary_sections_with_fp()` 只返回**实存**节）⇒ **整节删除 / 重编号不被检出**（「删项即空真」；CO-225 F-1 / CO-219 F-1 同族）。**本会话内存实证（零落盘）**：实存 99 节、`missing=[]`；注入删 §95 ⇒ 臂① 仍 `missing=[]`（PASS）；删 §98..§102 五节 ⇒ 仍 PASS。**grep 证实 runner 内无任何齿**声明「应有之节集/节数」；且实测节集 = `{1..7, 11..102}`（**8/9/10 不存在**）而**无声明** ⇒ 该枚举面**从未被钉定**。承 **R-CO219-1**（枚举面须名集等式）/ **R-CO225-1**（判定面完整性须名集钉定）。
- **处置**：① 新增 **`BOUNDARY_SECTIONS_DECLARED`**（100 节 = 实存 99 + 本节 §103）+ 纯判据 **`boundary_section_set_decision()`**（双向等式）并**扩 t35 臂①**（正/负控齐备；**不新增齿**，齿数仍 **41**）；② 登记簿入册 **`co230:F-1`**（TOOL_DEFECT、CLOSED）；③ 自声明面同步：runner report revision → **CO-203.8**；④ **R-CO230-1**。
- **正控（本会话独立实测）**：as-found 逐件 sha16 全对（runner `5dc43f6e3aedd50d` / boundary `e5fe950356777eff` / 登记簿 `ecf2963e9165f6f4` / 几何源 `60cbd331836e52b7` / 交付板 `d4e81f647be7f980`）；冻结四源 **4/4 MATCH**；`--check` **41/41 True**；序收敛 **rc=0 / 2 轮**；oracle **PASS**（11 齿；rc=0、受控件逐字节复原）；co120 **PASS**（19 齿）；co124 **PASS**；L5 签署 FAB/DFM/SI 全 **PASS**（skew 0.1300）；co206 **7/7**（A=FEASIBLE_PENDING_DFM 定案不变）；打样包 29/29 齿 / 37 payload；登记簿 **169 / OPEN 0**。
- **观测（在册项之复核，非本件新发现）**：登记簿已载「boundary **现行态 pin 再对齐**」之标签语义项（写入器只重写 sha、不改同排历史标签）⇒ §98 标签 `CO-203.3` 而 pin = 现行 `5dc43f6e3aedd50d`（该行于 `e4a65f7` 时 = `2a99e5fb3d9b32a6`）属**已知在册形态**，判版本须读该节现行版本注或对应 CO 节。
- **边界（诚实·残余）**：① 本件所钉为「**节集名集等式**」，**不**判节内叙述之完备性（由各节自身 / co120 / co135 citation 扫描承载）；② 新增节须**显式**入 `BOUNDARY_SECTIONS_DECLARED` 方放行（属有意 fail-closed 之人工闸）；③ 本件**不**声称已覆盖「红线是否被机判」之全部形态。

| 工件 | sha16 |
|---|---|
| runner `p3_v57_co164_order_runner.py`（**CO-203.8** / 节集名集钉定） | `db80604b81e805e9` |
| 复评件 `m13_v57_CO230_rev19_co225_co229_review.json` | `3b816ee2247eb7f1` |
| boundary 写入器 `p3_v57_co146_boundary_append.py` | `00fa05ab54fdf13c` |
| 登记簿 `input_defect_register_v1.json`（+co230:F-1） | `b1d8c7130240c4d0` |
| 交付板 `k2_v4_8L.l4.kicad_pcb`（本件**未改**） | `d4e81f647be7f980` |

> **R-CO230-1**：**枚举面之「应有集」须独立声明**（承 R-CO219-1 / R-CO225-1）—— 凡以文档/工件**自述**为其枚举域者（如 boundary 之节集），须另立 `*_DECLARED` 名集做**双向等式**（缺项 ⇒ `*_missing`；未声明之新增 ⇒ `*_undeclared`），否则「删项即空真」；判据面之**域**不得由被判对象自身给出。

> **序不变**：本件未改步骤集/序列（承 §82 之 R-CO209-2）。
## 104. CO-231（**L2 自裁 · 承 R-CO212-1 / R-CO152-1 / R-CO230-1：boundary pin 表之内容入机判**）

- **缘起（闭 §103 残余）**：§103「诚实·残余」自认「本件只钉**节集**，不判 pin 表**内容**」；而 R-CO152-1 明定「现行 sha 一律由 boundary pin 表单一承载」⇒ 该表**内容**之正确性（所列值是否等于实件、指称是否唯一）**无机判齿**（承 R-CO212-1「pin 须可核」/ R-CO230-1「判据面之域不得由被判对象自述给出」）。
- **实测（本会话，只读复核）**：逐行复核 pin 表 **539 行**：**538 行**可解析且所列 sha16 **== 实件**（0 陈旧）；**1 行不可复核** = §87「被消费 L5 记录（DFM/DFT、SI/PI/EMC、G7）| `6632179e1ef63183`」——标签声称**三件**而所列 sha16 实为 `m13_v57_l5_dfm_dft_record.json` **一件** ⇒ ① 该行**名实不符**（指称不唯一 ⇒ 不可复核，$R-CO208-1 同族）；② 就 §87 节而言 SI/PI/EMC 与 G7 两件**未钉**（他节有钉，故非全链缺口）。
- **裁定（L2 自裁）**：① **生成器**拆分该行为三行（各带唯一指称）；② 入机判 runner 静态齿 **t40_boundary_pin_rows_current**：pin 行标签须**恰一个**文件指称（于声明根集 `BOUNDARY_PIN_ROOTS` 唯一解析）且所列 sha16 **== 实件**；不可解析之标签须入**显式豁免名集** `BOUNDARY_PIN_LABEL_EXEMPT`（**名集等式**，现为**空**）；③ 自声明面同步：runner report revision → **CO-203.9**；④ **R-CO231-1**。
- **判别力（本会话实测）**：手改/陈旧值 ⇒ `pin_value_stale`；指称不唯一或无指称而未豁免 ⇒ `pin_reference_unresolved`；实件 539 行 ⇒ `ok`；正/负控皆备。
- **边界（诚实·残余）**：① 本件判「**所列值 == 实件**」与「**指称唯一**」，**不**判 pin 表之**完备性**（哪件**应有** pin 由各节自身 / co120 / co135 citation 扫描承载）；② 解析根集为**显式声明域**，新增根须显式加入（否则该行判 `pin_reference_unresolved`）；③ 本件**不**声称已覆盖「红线是否被机判」之全部形态。

| 工件 | sha16 |
|---|---|
| runner `p3_v57_co164_order_runner.py`（**CO-203.9** / t40 pin 行内容齿） | `db80604b81e805e9` |
| boundary 写入器 `p3_v57_co146_boundary_append.py`（§87 行拆分 + §104） | `00fa05ab54fdf13c` |
| 被消费 L5 记录 `m13_v57_l5_dfm_dft_record.json`（§87 拆行） | `6632179e1ef63183` |
| 被消费 L5 记录 `m13_v57_l5_si_pi_emc_record.json`（§87 拆行） | `97c867e89fc6df6c` |
| 被消费 L5 记录 `m13_v57_l5_g7_record.md`（§87 拆行） | `2ab7a29e745b70ff` |
| 登记簿 `input_defect_register_v1.json`（+co231:F-1） | `b1d8c7130240c4d0` |
| 交付板 `k2_v4_8L.l4.kicad_pcb`（本件**未改**） | `d4e81f647be7f980` |

> **R-CO231-1**：boundary pin 表（R-CO152-1 之**唯一**现行 sha 承载面）**内容须机判**：每行标签须**恰一个**文件指称、且所列 sha16 **等于实件**；不可解析 / 指称不唯一之标签须入**显式豁免名集**（名集等式，禁静默）。—— 「有 pin 表」≠「pin 可核」（承 R-CO212-1 / R-CO152-1 / R-CO230-1）。

> **序不变**：本件未改步骤集/序列（承 §82 之 R-CO209-2）。
## 105. CO-232（**L2 自裁 · 承 R-CO224-1：boundary 之内容权威性入机判**）

- **缘起**：R-CO224-1 要求「序内生成物之追注须写入**生成器**」，但 boundary 之**内容权威性**无机判齿 —— t35/t40 只看「**节集** + **pin 行**」⇒ 生成段内之**散文/表格手改**（含被生成器丢弃之手工追注）**不可见**（承 R-CO208-1「口径逐处同步」/ CO-230/231 同族「无机判齿即空真」）。
- **实测（本会话）**：① 变更生成段内之数值主张（`24/32` → `31/32`）或插入手工追注 ⇒ t35 / t40 **皆 True**（不可见）；② 生成器**只拥有各 § 区段**（`re.sub` 以「MARK + 区段正则」替换该区段，止于下一 `## ` 或 EOF）⇒ 区段**外**之首部/尾部手工内容**不**被取代（实测：前置于首行前之追注在重生成后**存活**）。
- **裁定（L2 自裁）**：① 生成器增 **`--dump`**（**dry-run**，只算不写；输出 `{dry_run, sha16, lines}`）；② 入机判 runner 静态齿 **t41_boundary_is_generator_output**（**双臂**：① 实件 sha16 **== 生成器 dry-run 输出**（覆盖各生成段内手改与**尾部**新增）；② **首行**须为声明之标题形态 `BOUNDARY_HEAD_DECLARED`（覆盖**前置**新增）；正/负控皆备）；③ 自声明面同步：runner report revision → **CO-203.10**；④ **R-CO232-1**。
- **判别力（本会话实测）**：（a）**前置**追注 ⇒ t41 **False**；（b）§104 区段内插入追注 ⇒ t41 **False**；回复（重跑生成器）⇒ **True**（`--check` **43/43**；实件 sha16 回至 `39cb8380dd1c1fc9`）。
- **边界（诚实·残余）**：① 生成器**只拥有**各 § 区段 ⇒ 区段**外**（首部除首行、他工具产出区）内容**不**在本件权威面内；② 本件**不**判节内叙述之**完备性**；③ `--check` 之 t41 须在**生成器已跑**之态评估（序之**末步**即生成器 ⇒ 收敛态成立；落后态即 fail-closed，属有意）；④ t40 亦对同一落后态报警（两者冗余但语义不同：t40 判 pin 行值，t41 判整件内容权威性）。

| 工件 | sha16 |
|---|---|
| runner `p3_v57_co164_order_runner.py`（**CO-203.10** / t41 生成器输出齿） | `db80604b81e805e9` |
| boundary 生成器 `p3_v57_co146_boundary_append.py`（+`--dump` dry-run / +§105） | `00fa05ab54fdf13c` |
| 登记簿 `input_defect_register_v1.json`（+co232:F-1） | `b1d8c7130240c4d0` |
| 交付板 `k2_v4_8L.l4.kicad_pcb`（本件**未改**） | `d4e81f647be7f980` |

> **R-CO232-1**：**序内生成物之内容权威性须机判** —— 凡由生成器产出之正典件（如 boundary），其实件内容须**等于生成器之输出**（`--dump` 式 dry-run 比对，双臂：**整件 sha16** + **首行**形态），否则「生成段内手改 / 区段外前置追注」皆可静默混入正典（承 R-CO224-1「追注须写入生成器」/ R-CO230-1 / R-CO231-1）。

> **序不变**：本件未改步骤集/序列（承 §82 之 R-CO209-2）。
## 106. CO-233（**L2 自裁 · 状态齿与扰动实验协议之相容性**）

- **缘起（新齿引入之相容性缺陷）**：CO-231/CO-232 新增**状态齿**（t40 = pin 行值须 == 实件；t41 = boundary 须 == 生成器输出）—— 二者皆依赖派生件 boundary 之**现行一致态**。而序之**静态前置**含全部齿（`static_ok = all(checks)`）⇒ 扰动受控件即令 pin 与实件不符 ⇒ **序停机 rc=1**。
- **实测（本会话）**：不动点 oracle 之 case A（扰登记簿）⇒ `order_rc=1`、`order_converged=false`、`restored=false` ⇒ oracle **FAIL**（`FAIL_FIXPOINT_PATH_DEPENDENT_OR_ABORT`）——即**新增状态齿与扰动实验协议不相容**；且该不相容**已存在于 `c1a880b`（CO-231）**（当时未复跑 oracle 故未现），本件一并修正。另实测异常路径：`finally` 只复原**受控件**而**未**复原**派生件** ⇒ boundary 留「已 realign 到扰动态」之 stale（t40/t41 随即停机）。
- **裁定（L2 自裁）**：① oracle 每案**注入后**先 **`_realign`**（重跑 boundary 生成器）**再**跑序；② `finally` 复原受控件后**再 realign**（异常/中断路径亦不留 stale）；③ oracle 自声明 revision `CO-219 → CO-232`，与 runner `TOOL_REVISION_DECLARED` **双侧同步**（t33 机判）；④ **R-CO233-1**。
- **判别力（本会话实测）**：修前 oracle **FAIL**（case A rc=1 / restored=false）；修后 **PASS**（5 案 `order_rc=0` 全复原、10 齿全 True、rc=0）。
- **边界（诚实·残余）**：① 本件为**相容性**修正，**不**改 t40/t41 之判据强度（停机语义保留：规范态下违例仍 fail-closed）；② **教训（入红线）**：凡新增**状态齿**（依赖受控件现行值者）须**同 commit 复查**与 oracle 扰动协议之相容性；③ oracle 仍**不**扰动冻结四源/板/SPEC（R-CO195-0 不变）。

| 工件 | sha16 |
|---|---|
| runner `p3_v57_co164_order_runner.py`（CO-203.10 / +oracle revision 绑定 CO-232） | `db80604b81e805e9` |
| oracle `p3_v57_co195_fixpoint_uniqueness_oracle.py`（**CO-232**：扰动后 realign + finally realign） | `585b983de844603d` |
| boundary 生成器 `p3_v57_co146_boundary_append.py`（+§106） | `00fa05ab54fdf13c` |
| 登记簿 `input_defect_register_v1.json`（+co233:F-1 / +co232:F-1） | `b1d8c7130240c4d0` |
| 交付板 `k2_v4_8L.l4.kicad_pcb`（本件**未改**） | `d4e81f647be7f980` |

> **R-CO233-1**：凡**状态齿**（其判据依赖**受控件之现行值**者，如 pin 行现值、生成器输出一致性）——新增/修改时须**同 commit 复查与扰动实验（不动点 oracle）之相容性**：扰动受控件必使派生件（boundary）失同步，故扰动后须先**重跑派生件生成器（realign）**再跑序，**复原路径亦须 realign**（否则派生件留 stale ⇒ 状态齿停机）。禁以「新齿与 oracle 各自皆绿」之**分别**证据代替**相容性**证据（承 R-CO195-0/1、CO-219 F-2、CO-233 实测）。

> **序不变**：本件未改步骤集/序列（承 §82 之 R-CO209-2）。
## 107. CO-234（**L2 自裁 · pin 面对受控集之覆盖面入机判**）

- **缘起**：受控集（`STEP_ARTIFACTS` ∪ `ORDER_MD_PRODUCTS`）已声明，但「哪件**应有** pin」**无机判齿** ⇒ 件可**静默漏钉**（承 R-CO219-1 枚举面名集等式 / R-CO225-1「无机判齿即空真」/ R-CO230-1）。
- **实测（本会话，只读）**：**43 件**受控产物中 **8 件**在 pin 面**无任何 pin** —— 7 枚 `.md` 卡片（CO124 / CO150 / CO159 / CO172 / co146_impedance_table / co146_jlc_dfm_gate / co146_pm_eval）与本件所补之 **`m13_v57_co77_closure_declaration_sweep.json`**（**收口扫描记录**，判定性产物）。
- **裁定（L2 自裁）**：① **域名显式**：覆盖面钉定以「**非 `.md` 受控件**」为域（`.md` 卡片之受控性与种类由 t20 机判 ⇒ 以**显式域名**排除，**非**静默跳过）；② **显式豁免（附理由，非静默）**：`co77` 收口扫描记录 **不可 pin** —— 其内容依赖 boundary 而 boundary 若 pin 其 sha 即构成**自指循环**（实测：首版补钉后序**不收敛**：5 轮 sha 各异；oracle `FAIL_SETTLE_NOT_CONVERGED`）⇒ 列入 `PIN_COVERAGE_EXEMPT`；③ **入机判** runner 静态齿 **t42_pin_face_covers_controlled**（覆盖 + **域下限** `PIN_COVERAGE_FLOOR` 防「删声明即空真」；正/负控齐备）；④ 自声明面同步 runner report revision → **CO-203.11**；⑤ **R-CO234-1**。
- **边界（诚实·残余）**：① 域由 runner **声明**（`STEP_ARTIFACTS`/`ORDER_MD_PRODUCTS`）承载 ⇒ **域缩水**仅由**下限**部分拦阻（非名集等式；完整名集钉定留待后续 CO）；② 本件判**覆盖面**，**不**判各件内容之正确性（可由 t41 类模式逐件扩展）；③ `.md` 卡片面无 pin 判据（其受控性由 t20 承接，非本件域）。

| 工件 | sha16 |
|---|---|
| runner `p3_v57_co164_order_runner.py`（**CO-203.11** / t42 覆盖面齿） | `db80604b81e805e9` |
| 登记簿 `input_defect_register_v1.json`（+co234:F-1） | `b1d8c7130240c4d0` |
| 交付板 `k2_v4_8L.l4.kicad_pcb`（本件**未改**） | `d4e81f647be7f980` |

> **R-CO234-1**：**受控集之 pin 覆盖面须机判** —— 凡序内受控产物（`STEP_ARTIFACTS`/`ORDER_MD_PRODUCTS` 所声明者），除**显式域名**（如 `.md` 卡片：其受控性由 t20 承接）外，须**全部**入 boundary pin 面；且域须设**下限**防「删声明即空真」；**不可 pin 者**（内容依赖 boundary ⇒ 自指循环）须入**显式豁免名集**（名集等式 + 理由）。承 R-CO219-1 / R-CO225-1 / R-CO230-1 / R-CO231-1 / R-CO152-1（避自指）。

> **序不变**：本件未改步骤集/序列（承 §82 之 R-CO209-2）。
## 108. CO-235（**非执行者对抗复评 CO-231..CO-234 + 同会话处置 · pin 行值之判据面/realign 面同域化**）

- **复评者**：context 归零之**新会话**（未参与 CO-231..CO-234 之任何撰写 ⇒ 四节全在对象内，无自评豁免面）；as-found 逐件钉 `03f8d39`（`git show` 重放）；扰动一律**内存注入 + 字节复原**（零残留、零坐标搜索）。
- **复评范围补正（F-2 · RECORD_HYGIENE）**：复评链上一段 = CO-230 覆盖 CO-225..CO-229；其**后**新增 `c1a880b`（CO-231）未入任何复评声明面 —— 而 z96 之复评债声明面**漏 CO-231**（承 R-CO219-1/R-CO230-1：**枚举面之应有集须独立声明**）。本件**补足**：复评范围 = **CO-231..CO-234**（叙述/记录类 ⇒ 不入登记簿，承 CO-213 F-2 先例）。
- **F-1（TOOL_DEFECT · mid · CLOSED）· pin 行「值面」之判据面与 realign 面**各自**由格式隐式给定 ⇒ `**`sha`**` 变体静默逃逸**：
  - **E1（本会话实测）**：内存改 §2 粗体行值（`m13_v57_layer_intent_rev6.json` 之 `**`05009687a3f01583`**` → `deadbeefdeadbeef`）⇒ **t35 / t40 / t41 皆 True**（**不可见**）；**E4 正控**（同法改一枚 2 列 pin 行值）⇒ t40 **False**（可见）。根因：t40 之域 = `_PIN_ROW_RE`（**仅 2 列**）；生成器 `CITE`（realign）亦**不**匹配粗体 `**` ⇒ 该值**两处皆不在**。
  - **同族（E2/E3）**：普通 3 列行值伪造 ⇒ t41 **False**（realign 差分可见，因 `CITE` 命中）；**整行删除**（§1..§22 不在生成器权威面）⇒ t35/t40/t41 **皆 True**（不可见；属 CO-231 已声明之「完备性不判」范畴，本件仅以**格式面名集**拦阻**新形态**）。
  - **裁定（L2 自裁）**：① 生成器 `CITE` 之 sha 组前允许 `(?:\*\*)?` ⇒ realign 面覆盖粗体（值**自愈**，且由 t41 整件比对覆盖）；② runner **声明** `PIN_ROW_FORMATS_DECLARED`（`pin2` = 2 列现状；`pin3` = 3 列 / sha 为第 3 单元格，可粗体、可带尾注），`boundary_pin_rows()` **遍历声明格式** ⇒ **t40 之值核覆盖 §2 全 14 行**（本会话实测 14/14 值 == 实件）；③ 新增静态齿 **t43_pin_row_format_covered**：boundary 内**一切含 backticked 16-hex 之表行**须匹配**恰一**声明格式，否则须入 **`PIN_ROW_FORMAT_EXEMPT`**（**名集等式** + 理由 + **同源锚**（补偿牙齿须实存））⇒ 未声明之**新形态 fail-closed**（域**显式**，承 R-CO230-1）；④ **口径同步**（承 R-CO152-1 现行 sha **单一承载** / R-CO208-1 口径逐处同步）：§3 之 G7/L5 行为 **L5-SI.6 / L5-DFM.6 历史快照**（其值 `6d85160413770fa5` / `73f9b59ed5f6f3ce` / `40445f87be664f31` **全树无对应件**）⇒ 显式标注历史快照 + 指向 §104 pin 面之**现行** L5（**L5-SI.11** `97c867e89fc6df6c` / L5-DFM.8 `6632179e1ef63183` / L5-FAB.2 `791012e88b514faa` / L5-G7.11 `2ab7a29e745b70ff`）；⑤ 自声明面同步：runner report revision → **CO-203.12**；⑥ **R-CO235-1**。
- **判别力（本会话实测）**：修后 E1 同式注入 ⇒ t41 **False**（realign 差分）；§2 之 14 行值皆被 t40 核（值 == 实件）；t43 正控（声明格式行）⇒ `ok`、负控（未声明之 4 列 sha 行）⇒ `pin_row_format_undeclared`。
- **边界（诚实·残余）**：① **行集完备性**仍不判（删一行无人知 —— CO-231 已声明；本件只拦**新形态**）；② `gate3` 族（§3 门禁叙述行）之值**由锚点齿承载**（G4 == t39 几何源 pin；G5/G6 == t40 pin 面同值；G7 = 历史快照）⇒ 本件不重核其字面；③ 生成器**仍只拥有**各 § 区段（§1..§22 为手工面；承 CO-232 残余）；④ 本件为 CO-231..CO-234 之复评处置，**CO-235 自身须下一轮复评**（禁自评）。

| 工件 | sha16 |
|---|---|
| runner `p3_v57_co164_order_runner.py`（**CO-203.12** / t43 pin 行格式面齿 + boundary_pin_rows 遍历声明格式） | `db80604b81e805e9` |
| boundary 生成器 `p3_v57_co146_boundary_append.py`（`CITE` 扩粗体 realign / +§108） | `00fa05ab54fdf13c` |
| 登记簿 `input_defect_register_v1.json`（+co235:F-1） | `b1d8c7130240c4d0` |
| 复评件 `m13_v57_CO235_rev19_co231_co234_review.json`（CO-235） | `d6de768766e927f1` |
| 复评卡 `m13_v57_CO235_rev19_co231_co234_review.md`（CO-235） | `6d96a6589f8fd90b` |
| 交付板 `k2_v4_8L.l4.kicad_pcb`（本件**未改**） | `d4e81f647be7f980` |

> **R-CO235-1**：**判据面与 realign 面须同域** —— 凡以「行的形态」界定判定域者（如 boundary 之 pin 行），须**显式声明格式名集**（非由单一行正则隐式给定），并以**覆盖面臂**保证「域外无 carrying-同语义之对象」（未声明之新形态 ⇒ **fail-closed**）；且**值面**（现行 sha）之 realign 面须与判据面**同域** —— 不得一方覆盖、另一方漏过（漏过即**静默陈旧**）。承 R-CO230-1（判据面之域不得由被判对象自述给出）/ R-CO231-1（pin 须可核）/ R-CO152-1（现行 sha 单一承载）。

> **序不变**：本件未改步骤集/序列（承 §82 之 R-CO209-2）。
## 109. CO-236（**L2 自裁 · 承 R-CO193-3 / R-CO225-1：复评/重出件 as-found 幂等入机判**）

- **缘起**：**R-CO193-3**「证据/复评件只钉**被评对象（as-found）**；处置态/跨件**现行** sha **禁内嵌**；**复评件须幂等**（同命令重跑逐字节相同）」之**形态无机判齿** ⇒ 空真（承 R-CO225-1：红线之形态无机判齿即空真）。
- **F-1（TOOL_DEFECT · mid · CLOSED）**：`tools/p3_v57_co230_rev19_co225_co229_review.py` 与 `p3_v57_co235_rev19_co231_co234_review.py` 之复评件内嵌**现行链派生值**（`n_sections_now`/`declared_n`/`n_static_declared` 读**现行** runner+boundary；`V3_check.{rc,n_teeth}` 跑**现行** `--check`；行普查读**现行** boundary）⇒ **链一成长即漂移**；而该二命令**列于规范复现基线** ⇒ 重跑即**改写被 pin 之记录** ⇒ t40（pin ≠ 实件）+ t41（boundary ≠ 生成器输出）Fail ⇒ 序静态前置停机 rc=1。**实测**：co230 复评件 sha 由 `0302e5d87eb81758` 漂至 `86376b12e4cc9ac8`；co235 于失同步态重跑 ⇒ `ff30672798f5f65c`→`3abec28adc9a2d6c`。
- **处置（L2 自裁）**：① **co230**：节集/缺号自 **as-found（`git show fdb72a2`）重放**；**去链派生计数**（`n_sections_now`→`n_sections_as_found`；`declared_n`→布尔 `as_found_sections_subset_of_declared`；`n_static_declared`→布尔 `static_face_declared`）；控制输入改**合成声明集**（纯）；V2 **不内嵌现行 sha**（只留声明值 + 布尔）。② **co235**：**去现行 `--check` 计数**（`V3_check` 不再内嵌）、行普查自 **as-found 重放**、V2 不内嵌现行 sha。③ 新增静态齿 **t44_reissue_records_as_found_pure**（`REISSUE_RECORDS_DECLARED` **名集钉定** + as-found 绑定（记录 rev ∧ 工具 `AF` 声明）+ **链派生键名集** `REISSUE_CHAIN_DERIVED_KEYS` 不得出现 + 残余 `REISSUE_PURITY_RESIDUAL` **显式** + 合成正/负控）。④ report revision → **CO-203.13**（齿面 45→46）；登记簿 `co236:F-1` CLOSED；**R-CO236-1**。
- **判别力实测（非空真）**：修后二工具**同命令重跑逐字节相同**（co230 `3b816ee2247eb7f1`×2；co235 `d6de768766e927f1`×2），且**重跑 co230 重出**不再失同步（修前 ⇒ t40/t41 Fail）。t44 **负控**：合成记录含 `n_sections_now`/`V3_check` ⇒ 命中（fail-closed）；**正控**：仅 as-found 键 ⇒ 不命中。
- **注入实测**改**移出记录**（同 CO）：以现行 `--check` 评估注入态 ⇒ 记录**被 pin** ⇒ **记录一变即污染下次读数**（自指；CO-234 co77 同族）⇒ 非幂等 ⇒ 本件将 V6 型注入实测移出复评记录（**判别力由 runner 之 t40/t43（含合成正/负控）承载**）。**若**要跑 V6 型注入实测，**须于一致态**运行方为真（本会话实测：失同步态之读数为**污染值**，据此可误判 teeth 判别力）。真残余不变 = **§1..§22 手写面之散文/无 sha 行**删除（行集完备性不判；CO-231 已声明）。
- **残余（显式，承 R-CO215-1 之「代理 + 残余显式」）**：① 禁法为**键名**启发式（更名即逃逸；须先入 `REISSUE_CHAIN_DERIVED_KEYS`）；② 控制输入仍读**冻结/受 pin** 工件、并对**注入态**跑 `--check`（其值在**一致态**下稳定）。

| 工件 | sha16 |
|---|---|
| runner `p3_v57_co164_order_runner.py`（**CO-203.13** / t44 + 声明集/键名集/残余） | `db80604b81e805e9` |
| boundary 生成器 `p3_v57_co146_boundary_append.py`（+§109） | `00fa05ab54fdf13c` |
| 登记簿 `input_defect_register_v1.json`（+co236:F-1） | `b1d8c7130240c4d0` |
| 复评件 `m13_v57_CO230_rev19_co225_co229_review.json`（as-found 幂等化） | `3b816ee2247eb7f1` |
| 复评卡 `m13_v57_CO230_rev19_co225_co229_review.md` | `766be9d18edfdf00` |
| 复评件 `m13_v57_CO235_rev19_co231_co234_review.json`（as-found 幂等化） | `d6de768766e927f1` |
| 复评卡 `m13_v57_CO235_rev19_co231_co234_review.md` | `6d96a6589f8fd90b` |
| 交付板 `k2_v4_8L.l4.kicad_pcb`（本件**未改**） | `d4e81f647be7f980` |

> **R-CO236-1**：**复评/重出件须 as-found 幂等**（承 R-CO193-3）—— 其内容须为**被评对象（as-found）之纯函数**：一切记录值须自 `git show <as-found>` 重放或为**链无关**布尔；**禁**内嵌现行链派生量（计数 / 现行 sha）；**同命令重跑须逐字节相同**。红线之此形态**须有机判齿**（`t44`：声明集名集钉定 + as-found 绑定 + 链派生键名集不得出现 + 残余显式），承 R-CO225-1。

> **序不变**：本件未改步骤集/序列（承 §82 之 R-CO209-2）。
## 110. CO-237（**L2 自裁 · 承 R-CO225-1 / R-CO193-3 / R-CO234-1：复评件覆盖面入机判**）

- **缘起**：CO-236 新增静态齿 **t44**（复评/重出件 as-found 幂等）之**域** = 手写 **2 件**声明 ⇒ **覆盖面无机判** —— 而 boundary pin 面实测受 pin 之 `*_review.json` 共 **14 件** ⇒ 12 件**域外**（无声明臂、无最低覆盖面）⇒ **新增复评件可不经声明而落于 t44 之外**（「域由声明自述给出」= **R-CO230-1** 所禁；「覆盖面须机判 + 域下限」= **R-CO234-1** 所立；「红线之形态无机判齿即空真」= **R-CO225-1**）。
- **F-1（TOOL_DEFECT · mid · CLOSED）**：同上。**同类已实测两次漏项**：z96 之复评债声明面**漏 CO-231**（CO-235 F-2 实测）；复评债之**连续性**无机判齿。
- **处置（L2 自裁）**：① t44 **域显式化** —— 域 = **boundary pin 面**中一切 `*_review.json` 受 pin 件（**非**由声明自述给出，承 R-CO230-1）；② 域成员须 ∈ `REISSUE_RECORDS_DECLARED` ∪ **显式豁免集** `REISSUE_RECORDS_EXEMPT`（**名集等式** = 域 − 声明，防静默缩域/漏项；每项须有 `why` + **同源锚**）；③ **域下限** `REISSUE_DOMAIN_FLOOR = 12`（防「删 pin 行即空真」）；④ 12 件既有复评件（CO-236 前）**显式豁免**并附理由（as-found 内嵌于 `nature`/`as_found` 散文、非 `.rev` 结构；工具经**只读复核无现行链读取**）—— 属**如实登记之残余**；⑤ 扩 **t44** 之覆盖面臂（**不新增齿**，仍 46）；⑥ report revision → **CO-203.14**；登记簿 `co237:F-1` CLOSED；**R-CO237-1**。
- **判别力（实测）**：域 = **14**；声明 **2** + 豁免 **12** ⇒ 名集等式 `set(EXEMPT) == set(domain) − set(DECLARED)` 成立；**负控**：域成员未列 ⇒ 等式不成立 ⇒ t44 Fail（fail-closed）。
- **残余（显式）**：① 域以**文件名形态** `*_review.json` 界定 ⇒ 异名复评件（改命名约定）可逃逸（须先入域规则）；② 豁免之 12 件为**既有**复评件，其 as-found 纯性未逐一入结构臂。

| 工件 | sha16 |
|---|---|
| runner `p3_v57_co164_order_runner.py`（**CO-203.14** / t44 覆盖面臂：域 + 名集等式 + 域下限） | `db80604b81e805e9` |
| boundary 生成器 `p3_v57_co146_boundary_append.py`（+§110） | `00fa05ab54fdf13c` |
| 登记簿 `input_defect_register_v1.json`（+co237:F-1） | `b1d8c7130240c4d0` |
| 复评件 `m13_v57_CO230_rev19_co225_co229_review.json` / 卡 | `3b816ee2247eb7f1` |
| 复评卡 `m13_v57_CO230_rev19_co225_co229_review.md` | `766be9d18edfdf00` |
| 复评件 `m13_v57_CO235_rev19_co231_co234_review.json` / 卡 | `d6de768766e927f1` |
| 复评卡 `m13_v57_CO235_rev19_co231_co234_review.md` | `6d96a6589f8fd90b` |
| 交付板 `k2_v4_8L.l4.kicad_pcb`（本件**未改**） | `d4e81f647be7f980` |

> **R-CO237-1**：**复评件之覆盖面须机判** —— 域须由**受 pin 面**给出（**不得**由声明/自述给出，承 R-CO230-1）；域成员须 ∈ **声明集 ∪ 显式豁免集**（**名集等式** + 理由 + **同源锚**）且设**域下限**（防「删 pin 行即空真」，承 R-CO234-1）；此形态须有机判齿（**t44** 覆盖面臂），承 R-CO225-1。

> **序不变**：本件未改步骤集/序列（承 §82 之 R-CO209-2）。
## 111. CO-238（**非执行者对抗复评 CO-235..CO-237 · L2 自裁 · 承 R-CO202-4 / R-CO236-1**）

- **缘起**：CO-236 之 t44 **工具绑定臂** `_tool_ok[_rel] = (f'AF = "{rev}"' in _tsrc)` 为**原文子串** ⇒ 真绑定可被**注释/散文**替代而不失 pass（本会话纯复算：真绑定→注释 ⇒ 子串判据仍 True）。承 **R-CO202-4**（源内声明之代理判据须 AST 字面量）+ **CO-215**（同源缺陷：子串即可满足）。
- **F-1（TOOL_DEFECT · mid · CLOSED）**：同上（复评覆盖 CO-235..CO-237，as-found 钉 `ab9c421`；非执行者、禁自评）。
- **处置（L2 自裁）**：① 绑定判据改 **AST 赋值**（`AF` 之 `Assign`/`AnnAssign` 值须为 == rev 之**字符串常量**；注释/散文/拼接不满足；`SyntaxError` ⇒ **fail-closed**）；② 合成正/负控 6 项；③ 扩 **t44** 绑定臂（**不新增齿**，仍 46）；④ report revision → **CO-203.15**；登记簿 `co238:F-1` CLOSED；**R-CO238-1**。
- **判别力（实测）**：as-found 子串判据对「真绑定→注释」= **True**（漏洞）；修复判据（AST）对注释/docstring/错值/拼接 = **拒**、对真绑定/AnnAssign = **认**。
- **残余（显式）**：① 绑定认字符串常量赋值 ⇒ 非字面量构造不视为绑定（方向 = fail-closed）；② 键名启发式 / 域以文件名形态界定（承 CO-236/CO-237）。

| 工件 | sha16 |
|---|---|
| runner `p3_v57_co164_order_runner.py`（**CO-203.15** / t44 绑定臂：AST 绑定） | `db80604b81e805e9` |
| boundary 生成器 `p3_v57_co146_boundary_append.py`（+§111） | `00fa05ab54fdf13c` |
| 登记簿 `input_defect_register_v1.json`（+co238:F-1） | `b1d8c7130240c4d0` |
| 复评件 `m13_v57_CO238_rev19_co235_co237_review.json` | `9ed47d8047b06bd4` |
| 复评卡 `m13_v57_CO238_rev19_co235_co237_review.md` | `933c7cb96a981a08` |
| 复评工具 `p3_v57_co238_rev19_co235_co237_review.py` | `7869de9ad1ff8566` |
| 交付板 `k2_v4_8L.l4.kicad_pcb`（本件**未改**） | `d4e81f647be7f980` |

> **R-CO238-1**：**源内声明之代理判据须为 AST 绑定** —— 复评/重出件工具之 as-found 绑定须以 **AST 赋值 + 字符串常量** 机判；**注释/散文/拼接一律不得满足**（承 R-CO202-4）；此形态须有机判齿（t44 绑定臂），承 R-CO225-1。

> **序不变**：本件未改步骤集/序列（承 §82 之 R-CO209-2）。
