dataxcash/hw_ic_k2/docs/K2-R746-A-EXIT-REGISTRATION-STEP1-STOP.md

# K2 · R746 回执 —— 工单①（新出口注册映射表）⇒ **两处硬闸命中：停手报监**（未跳步 · 未描线 · 未 bump SPEC）

> 依据：#K2-282 §三 ENG 工单 ①「新出口注册映射表（组→门位；注册网格最多挪 21 列/29 行）」＋ §二.2 **引用降级令**（映射表**主锚 = DS320PR1601 厂商 datasheet 推荐布局/出口**；PEX88096 降为「行业范式佐证」）；§三 硬边界：**只动注册语义**；**须搬动墙缺口物理开口 ⇒ 停手报监**。

## 一、本窗交付（工单① · 机核填表 · 零运行）

件 `K2_L1_A_EXIT_REGISTRATION_MAPPING_TABLE_v1.json` —— **16 行在册门位已填**（lane／group／P-N 对／注册门位格+层+墙缺口ID／镜像伙伴可用性／不变量五项），**但 `new_gate` 一律 WITHHELD**（**未发明任何新坐标**，遵 §三「只动注册语义」）。

## 二、❗硬闸 A：**精确「成组镜像」无法落在已注册开口上**（机核）

在册门位集（`K2_R613_FINAL_TABLE_VIA_OK_v1.json`）：
- **W 组（col-114 墙缺口）门行** = `7, 11, 12, 13, 15, 19, 24, 28`（轴 = 17.5）
- **E 组（row-36）门列** = `115, 117, 119, 125, 127, 131, 133, 135`（轴 = 125）

**精确镜像所需的伙伴门位，有 5 个不在已注册开口内**：
| 组 | 有镜像伙伴 | **无镜像伙伴（需新开口）** |
|---|---|---|
| W | 7↔28 · 11↔24 | **12→23 · 13→22 · 15→20 · 19→16** |
| E | 115↔135 · 117↔133 · 119↔131 · 125↔125（自对齐） | **127→123** |

⇒ **精确成组镜像 = 需新增 5 个墙缺口物理开口**（rows 23/22/20/16 ＋ col 123）⇒ **命中 #K2-282 §三 硬边界「须搬动/新增墙缺口物理开口 ⇒ 停手报监」**。**本席停手，不自行新增开口、不擅自改注册。**

## 三、❗硬闸 B：**主锚（厂商推荐布局）在册缺失**（#K2-282 §二.2）

- `k2/docs/` 内的产品类材料（R588/R589/R633/R664/R666）**均为 PEX88096 时代的调研**；按 §二.2 **已降级为「行业范式佐证」**，**不得**作为映射表主锚；
- **DS320PR1601（K2 主芯片 ×2 中继）的厂商 datasheet 推荐布局/出口：在册零命中**；
- ⇒ 按 §二.2「映射表主锚必须换 = DS320PR1601 厂商 datasheet 推荐布局/出口」，**本席无法在缺少该材料时定出 `new_gate`**；按「厂商文档与范式冲突即停、另件上报」之令，**此处一并报监**。

## 四、可落地的替代口径（供监理择一 · 本席不擅自采用）

| 口径 | 说明 | 是否需新开口 |
|---|---|---|
| **(i) 精确成组镜像**（题面本义） | 每对 P/N 的门位严格互为镜像 | **需 5 个新开口** ⇒ 命中硬边界 |
| **(ii) 已注册开口内的「成组有序」** | 不要求严格镜像；只按成品范式**在已注册开口内做组内有序指派**（＝R732 已做的束道全序），并把「镜像」降为**结构性意图**而非坐标等式 | **0 新开口**；但**能否达 16/16 未知**（R732 实测 **7/16**） |
| **(iii) 修订墙缺口开口集**（rows 16/20/22/23 ＋ col 123） | 把 5 个缺位补成注册开口 | **需动物理开口** ⇒ **须另案（属墙缺口本体，非本授权范围）** |

⇒ **本席建议 (ii) 先行 + (i)/(iii) 待锚**：因为 (i)/(iii) 都卡在同一处物理开口语义上，而 (ii) 是**当前授权内唯一可执行**的口径；且 (ii) 若仍 7/16 ⇒ 才需要 (i)/(iii) 的开口修订（届时另行授权）。

## 五、纪律与下一步

- 本窗：**未跳步**（工单②「SPEC 版本 bump」**未启动**——主锚未定，bump 无据）· **未描线** · **未导 Gerber／未进 P5／未碰下单** · **未派 WORKER** · **未新增/搬动任何墙缺口开口** · 冻结四源（除未执行的 SPEC bump）**4/4 MATCH**。
- 请监理裁：**(a)** 提供/指定 DS320PR1601 厂商推荐布局材料（或授权本席按公开资料抽取）；**(b)** 就硬闸 A 择上述 (i)/(ii)/(iii) 之一（本席建议 (ii) 先行）；**(c)** 若裁 (iii) 须动开口 ⇒ 请**另案授权**（属墙缺口本体）。

OWNER-ITEMS: 0
