dataxcash/hw_ic_k2/docs/K2-R740-MAKE-WORK-DUAL-BRANCH-SKELETONS.md

# K2 · R740 回执 —— 承 #K2-281 责令造活：双分支预案骨架**做实**（只读 · 零运行）

> 依据：#K2-281 §二.3「执行 #K2-280 §四 双分支预案骨架（只读 · 零运行）：A 支＝出口注册成组镜像映射表骨架（组 → 门位 → 成品对照列；不含坐标求解、不含描线）；B 支＝设计级不可行结题件骨架（证据链索引 ＋ 结论口径）」；§二.3 fail-closed：本窗若出现描线／运行／新前提／越阶段／触冻结四源 ⇒ 打回 ＋ 工序违规计数 +1。

## 一、本窗交付（**零运行 · 零描线 · 未触冻结四源**）

| 件 | 内容 |
|---|---|
| `K2_L1_A_EXIT_REGISTRATION_REMAP_TABLE_v1.json` | **A 支映射表骨架（已含 16 行在册数据）**：每行 = `lane · group(W/E) · pn_pair · gate_registered(格+层+墙缺口ID) · mirror_partner · 成品对照列(REF-CASE-LIBRARY §A.1 + R633 三规矩) · delta(待批) · gate_mirrored_new(待批) · 不变量五项`；**动的只有「从哪个注册门过墙」的语义**；下游链五步（修订件 → 一次成认证 16/16 表 → 验收 → 一次重描+合图 → M2 收口）；**硬边界**：若须搬动墙缺口物理开口 ⇒ 停手报监 |
| `K2_L1_B_INFEASIBILITY_EVIDENCE_INDEX_v1.json` | **B 支结题件骨架（证据链索引已做实）**：七项证据逐条带 **文件路径 + sha16 + 核过的关键读数**（R537 `hard_wall_certificate_found=false`／R545+R533 单线级／R652 `13/16`／R708 `PARTIAL_or_NAMED`·相对基座 UNSAT／R732 `7/16`／R633 成品对照／R696+R710 非镜像注册）＋ **证据强度分层**（已证 vs **未证（缺硬核）**）＋ 结论口径模板 |

## 二、纪律（本窗自查 · 对照 §二.3 fail-closed）

- **零运行**（未加载模型、未跑求解/构造）· **零描线** · **未起新前提**（仅如实标注 A 支待批项为 PENDING）· **未越阶段**（不导 Gerber／不进 P5／不碰下单）· **未触冻结四源**（只读，4/4 MATCH）· 未派 WORKER。

## 三、待 owner 的仍是同一问（#K2-280 不重复立案）

**A 批准东组出口注册成组镜像修订** ／ **B 维持现注册并按设计级不可行结题**。收到任一支批令，按对应骨架**一次执行**。

OWNER-ITEMS: 1
