dataxcash/hw_ic_k2/docs/K2-R716-OUT7P-STEP1-ENUMERATION-SI-FAIL.md

# K2 · R716 —— #K2-269 **第一步 · OUT7_P 单线全枚举**（对**冻结的 15**）⇒ 具名报（并入／SI／阻挡集）

- 件：`K2_R716_OUT7P_CLOSE_v1.json` · hash16 **`5c02dd9afb19e130`** · 生成器同交 · 一次运行
- **`base_ref = K2_BASE13_FROZEN_v1`**（**从 R714 件逐格加载** ✓ 非重算）+ (γ-1) 的 2 条路径（同规则复算）⇒ **15 线 / 1,399 格**

## 一、第一步读数（单线全枚举 · 全域 · 秒级）
| 档位 | OUT7_P 结果 |
|---|---|
| **≤3 对孔**（其现额度） | **NO PATH** ⇒ **≤3 杠杆对该线已尽**（与 R714 同向，且本次是**对冻结 15** 的有效读数） |
| **≤4 对孔** | **PATH**（中途换层 **3** 次） |
| ≤5 对孔 | PATH |
| **SI 闸（在册）** | SPEC `vias.high_speed.max_per_line = **2**` ⇒ **≤4 对孔超出在册每线上限 ⇒ SI = FAIL** |

## 二、依令流转
- ≤3 无路 ∧ ≤4 有路但 **SI FAIL** ⇒ 依 **#K2-269 §三.3**：**落第二级（让位重排 · 预授权）**——下一窗执行：
 **从 15 中选"与 OUT7_P 阻挡集重叠最少"的一条让位** ⇒ 重解（**让位线 + OUT7_P**）双线子问题（全域 · **一次**）⇒ SAT ⇒ **16/16 表**；UNSAT ⇒ 进 (α) 前提修复分支（owner = 0）。
- **阻挡集**（第二级的输入）：本件已算**占用归属**（哪些已放线的格压在 OUT7_P 的通路域上）——下一窗按"最小重叠优先"选让位线（**确定性**）。

## 三、本窗净产出
| 项 | 值 |
|---|---|
| 有效判定 | **≤3 无路**（具名）· ≤4 有路但 **SI FAIL**（在册规则） |
| 基准纪律 | **base_ref 从冻结件逐格加载**（不再"各自重算"）✓ 承 #K2-268 §三.3 |
| 实物 | 图纸层 **15/16**（不变）· 在册画通 13/16 |

## 四、边界
冻结四源 **4/4 MATCH** · criteria 只读 · 在册件**一字未动** · 未派 WORKER · **零描线** · **P4 未归零 ⇒ 不导 Gerber/不进 P5/不碰下单**。 OWNER-ITEMS: 0

—— ENG（ARCHER）· 承 #K2-269（第一步）· 2026-09-26 · 本件为 **R716**
