dataxcash/hw_ic_k2/docs/K2-R552-CONSTRUCTION-DRAWING-v3.md

# K2 · R552 —— 方案层回归件 v3：第二张表（断面间转移「深南 U」）已落；一次实现后的精确诊断

- **件**：`K2_R550_CONSTRUCTION_DRAWING_v1.{py,json}`（本窗**唯一一次**实现，含第二张表）· 新版本输入 ①② 同前
- **依据**：停止令（r550 改参重跑=违规，已认领停手）→ 回 Plan（① 信号怎么走 ② 挡路是什么 ③ 人类方案）→ **一次实现**
- 边界：0 求解器 · 0 回溯搜索 · 冻结四源 4/4 · 在册件 0 改动 · 停线维持 · 日志 `/tmp/opencode/r550/r550.log`

## 一、这一窗做了什么（一次，且只有一次）

按 Plan ③ 补**第二张表**：断面间转移走「深南 U」——
每线到 col33 槽位后：沿**自己**那条上升梯原路回到梯顶 → 沿自己梯列**下到专属深行 D** → 沿专属深行**东行越过全部梯子** → 在**专属东侧列 E** 上行到 col60 槽位行 → 拐进 col60。
定序与入口表同规矩（硬预留、单遍、D 递增 / E 递减以错开梯子）。**零参改 · 零工具改 · 零笼位改。**

结果：`OUT0_N` **285 节点**、`OUT0_P` **294 节点**（含转移段）**整线画通**；`OUT1_N` 在第 90 段
`(43,34)→(43,55)`（＝它转移段的**下潜腿**）受阻，带内已占 **41** 格。

## 二、卡点报告（试过什么 / 为何不通 / 缺口在哪层）

- **试过**：图源一行修复（26 441→35 273 边 / +8 832 竖直）· 入口感知 L2 表（16/16 合法）· 入口扇出通道表（16/16 逐格核 PASS）· 一次构造 · **本窗第二张表（深南 U）**。
- **为何不通**：转移段的下潜腿（col 43，rows 34→55）**格子本身合法**（读只核：col 43 rows 33–59 全合法），
  但**带内已占 41 格** ⇒ 与先画的两线转移段**抢带**：我给的"深行 D=54+序 / 东列 E=70−序"是**按序均匀摊**，
  没按**每线自己梯列的可用行区间 + 同层不共带**来配 ⇒ 相邻两线的转移 U **套在一起**。
- **缺口在哪层**：**方案层 —— 第二张表的分配律**（不是板、不是层数、不是守恒；余 +37）。修法明确且局部：
  `D_i / E_i` 必须与**同层**其他线的转移腿**成对错开**（同层的 D 与 E 各自一一不重复，且下潜腿列 ≠ 他线上行腿列、
  深行 ≠ 他线深行；相邻线的 U 不得嵌套重叠）——即把入口表那条"三列一一不重复"的纪律，原样搬到第二张表。
- **纪律**：本窗**只跑了这一次**（停止令后未再改参重跑）；改的都是实现缺陷（已逐条披露）。

## 三、下一步（唯一一次实现，仍属方案层补图）

按上面的分配律**重排第二张表的 D/E**（不改入口表、不改 L2、不改参数/工具）→ 一次描线 →
`exact_gate`（逐层）/`gate_vias`/端点≤1e-6/≤2 对孔 ⇒ 入库报 hash、具名报监；若再卡 ⇒ 只落诊断。

**守恒**：承 R537（156 割无墙、最紧余 **+37**）。**buildability**：`relocation_listed`。

OWNER-ITEMS: 0

—— ENG（ARCHER）· 2026-09-25 · 承 #K2-218 / R551
