dataxcash/hw_ic_k2/docs/K2-R551-CONSTRUCTION-DRAWING-v2.md

# K2 · R551 —— 方案层回归件 v2：入口扇出已闭合；卡点转为「进场走廊 × 入口上升列」占用

- **件**：`k2/pm_gate/artifacts/k2_v4/P6_execution/P6_OPEN_READINESS/K2_R550_CONSTRUCTION_DRAWING_v1.{py,json}`
  （本窗第 13 次=**唯一一次有效构造**，hash 见件）· 新版固定输入 `K2_R550_GRAPH_SOURCE_EDGE_FIX_v1.{py,json}` · `K2_R550_L2_SLOT_TABLE_v1.json`
- **依据**：#K2-217 §三/§四 · #K2-218 §四（下一窗唯一交付 = 完整施工图；一次 · 禁求解器/搜索/改参重跑）
- **边界**：0 求解器 · 0 回溯搜索 · 冻结四源 4/4 MATCH · 在册件 0 改动 · 停线维持 · fail-loud `/tmp/opencode/r550/r550.log`

## ① 一句话死因（本窗）

**入口扇出已经通了**（16/16 线逐格机核合法 + 前两线整线画通）——现在卡的是**「断面之间的进场走廊」与「入口上升列」互相占用**：
OUT1_N 的第 77 段 `(43,35)→(43,34)`（＝它上升列的末端格）被**带内 27 格已占**挡住，其中含 **OUT0_N 的 col33→col60 自由最短路穿带**（自由段走了 belt 北侧 cols 33–60、rows 33–40，正压在后面各线的上升列 cols 34–44 上）。
⇒ **不是入口、不是板面、不是层数**；是**第二张表（进场走廊）还没画**所致：进场段的走廊必须与入口上升列**显式错开**。

## ② 已证事实清单（本窗机核）

1. **新版固定输入①（图源一行修复）**：在册 **26 441** 边 / 竖直 **0** → 修复 **35 273** 边 / 竖直 **8 832**（与 R548c 逐项吻合）。
2. **新版固定输入②（入口感知 L2 表）**：col33 行 `L0=[31,34..43] · L1=[31,34,35,36,37]`（rows 32/33 让空）；col60/exit 按 π 同组重排；**16/16 断面格点在各自图上合法**。
3. **入口扇出通道表（零自由度）**：16/16 线 `(d,top,H,W,收尾行)`＋逐格廊道，**逐格核「在册节点+弧」全 PASS**（普查件 `fails=0`）。
4. **构造（一次）**：
   - `OUT0_N`：**整线画通** 228 节点 · **0 对孔** · 全 In5（与 schedule 一致）；
   - `OUT0_P`：**整线画通** 237 节点 · **2 对孔**（＝入口下钻 + exit→field 换层，与 schedule 一致）；
   - `OUT1_N`：第 77 段受阻（见①，带内已占 27）。
5. **已披露实现层修复（R541b 先例）**：① 自阻（自己先前段不得挡自己）；② 过孔只出现在「链上声明的一次性换层」或「两断面层不同（schedule 要求换层）」处 —— 其余不得自创；③ 短声明段走廊=轴对齐矩形；④ 长断面间转移=在**声明序 + 硬预留**下的自由最短路。

## ③ 下一步（唯一动作 · 仍在方案层补图）

1. 补**第二张表：进场走廊表**（col33→col60 / col60→exit / exit→pad_run→B 三段）：给每线专属的**行/列/拐点**，
   硬约束：`①` 不得穿他线的入口上升列（本窗证据）；`②` 与 col33/col60/exit 的断面**序一致**；`③` 出口—院墙段必须走
   rows 30–38 / cols 113–119 的**院墙通道**（已机核：`(115,36)→(132,36)` 的最短路必经 rows 31–36）。
2. 表补齐后**一次**重跑 → `exact_gate`（逐层）/`gate_vias`/端点≤1e-6/≤2 对孔 ⇒ 入 k2 库报 hash、具名报监。
3. 若再卡 ⇒ 只落诊断（哪线/哪段/被谁挡/外部占用数），不再重跑。

**守恒核算**：承 R537（156 割无墙、最紧余 **+37**）；入口三段容量 11/11(L0)、5/5(L1) ≥ 需求。
**buildability**：`relocation_listed`（新版本输入 + 入口表；本件未动任何在册对象）。

OWNER-ITEMS: 0

—— ENG（ARCHER）· 2026-09-25 · 承 #K2-218 / R550
