dataxcash/hw_ic_k2/docs/K2-R550-CONSTRUCTION-DRAWING-v1.md

# K2 · R550 —— 方案层回归件：修正输入（新版本件）+ 定序单遍构造 · v1

- **件**：`k2/pm_gate/artifacts/k2_v4/P6_execution/P6_OPEN_READINESS/K2_R550_CONSTRUCTION_DRAWING_v1.{py,json}`
  （hash16 **`025fc91de16963c4`**）· 新版固定输入：`K2_R550_GRAPH_SOURCE_EDGE_FIX_v1.{py,json}`（hash 见件）
  · `K2_R550_L2_SLOT_TABLE_v1.json` · 表普查 `K2_R550_TABLE_CENSUS_v1.json`
- **依据**：#K2-217（定性=方案层缺图；授权落新版本输入；下一窗唯一交付=§16.3 方案层回归件；一次即停、禁求解器/禁改参重跑）
- **边界**：0 求解器 · 0 回溯搜索 · 冻结四源 **4/4 MATCH** · 在册 R540/R529/R498/R499/SPEC/criteria **一字未改** · 停线维持
- **fail-loud 原始日志**：`/tmp/opencode/r550/r550.log` · 图源修复日志 `/tmp/opencode/r550/graph_fix.log`

## ① 一句话死因

**入口扇出已经通了（第 1 根线 OUT0_N 整线画通：228 节点 · 0 对孔），卡点整体后移到「出口 → 焊盘场」那一段**：OUT0_P 在 `(115,36)→(132,36)`（出口门柱 → 落 B 前的 pad_run）被挡，带内他线已占格 **4**，剩下的阻挡来自**墙体/焊盘场自身障碍**（rows 34–36、cols 100–117 那一片）。⇒ **不是入口了，是"最后的院墙"缺一张通道表**。

## ② 已证事实清单（本窗机核）

1. **输入修复 ①（已落新版本件）**：底图源无向边去重一行修复。
   机核：在册图 **26 441** 边、**竖直边 = 0**；修复后 **35 273** 边、**竖直边 = 8 832**（＝R548c 读数，逐项吻合）。
2. **输入修复 ②（已落新版本件）**：入口感知 L2 槽位表（下钻列 d 定序 π；col33 端点行 `[31,34..43]`，rows 32/33 留空；
   col60/exit 沿用 R540 取值、按 π 同组重排 ⇒ 序一致）。
   机核：**16/16 线的断面格点在各自图上合法**（`all_slot_cells_legal_in_lane_graph = true`）· col33 同层互异 · col60/exit 分(断面,层,组)互异。
3. **入口扇出通道表（零自由度，已机核）**：每线四元组 `(下钻列 d, 起钻行 top, 腰带行 H, 上升列 W)`，全部一一不重复；
   逐格核 `在册图节点 + 弧` **16/16 PASS**（`K2_R550_TABLE_CENSUS_v1.json`：fails=0）。
   端点 31 那根线按 R549 证 2 走 row33 收尾（`(33,33)→(33,32)→(33,31)`），rows 32/33 已让空。
4. **单遍构造（1 次）**：按 π 定序、硬预留、逐段矩形廊道内最短路（禁协商/禁回溯）。
   - **OUT0_N：整线画通**（228 节点 · **0 对孔** · 层全 In5，符合其 schedule）。
   - **OUT0_P：在第 102 段受阻**（`(115,36)→(132,36)`，出口门柱 → pad_run；带内他线占格 4）。
5. **R549 证书（承前件）**：同层 `{31,32,33}` 端点不可共存（穷举证）；端点 31 入口割集 = 单格 `(col34,row32)`。

## ③ 施工图（本窗达成/未达成）

- **入口扇出段：达成** —— 16 线逐线 `(d,top,H,W,收尾行)` + 逐格廊道（零自由度），机核合法且两两不重叠（普查件）。
- **整线：1/16 达成** —— 断面连接与出口→焊盘场两段仍缺通道表（本窗只声明了断面值，未声明该两段的走廊；
  现有构造器用"两点矩形廊道"兜，遇墙体/焊盘场自阻 ⇒ 需要在方案层把这**两段**也画成通道表）。
- **守恒核算**：承 R537（156 割无墙、最紧余 **+37**）；入口三段 (d/H/W) 容量 11/11(L0)、5/5(L1) ≥ 需求。
- **buildability**：`relocation_listed`（入口一段 + 新版本输入；本件**未动任何在册对象**）

## ④ 已披露的实现层修复（R541b 先例 · 非改参）

1. 自阻修复：一条线不得被**自己**先前画的段挡住（`occ` 只算他线）——R548b 同类的未竟项。
2. 层忠实：段内**不得自创过孔**，换层只发生在链上声明的 via（保证 schedule 语义）。
3. 廊道声明：两点之间廊道 = 轴对齐**矩形**（rows±1），替代"插值细带"（细带在长斜段必自阻）。
以上皆为**实现缺陷修复**，逐条披露；改后 **1 次**构造（未改任何设计参数、未换算法族）。

## ⑤ 下一步（唯一动作，仍属方案层补图）

1. 按同样的"通道表"手法，为**出口→焊盘场**段补两张表：`(a)` col60→exit 的进场行/列 → `(b)` exit→pad_run→B 的院墙通道；
   数据依据：`g2._nok` 逐线合法节点 + 墙体/焊盘场障碍栅（rows 34–36、cols 100–117 那一片）。
2. 表补齐后**一次**重跑（禁回改 L2/入口表）；过 `exact_gate`（逐层）/`gate_vias`/端点≤1e-6/≤2 对孔 ⇒ 入 k2 库报 hash。

OWNER-ITEMS: 0

—— ENG（ARCHER）· 2026-09-25 · 承 #K2-217 /
