dataxcash/hw_ic_k2/pm_gate/artifacts/k2_v4/P6_execution/P6_OPEN_READINESS/K2_R518_ORDERED_LEVER_STEP1_RECEIPT_v1.md

【回执首行】（监理 #K2-189 · 原文复述）「【监理裁定 #K2-189】上一窗唯一一次受证求解（R515）= **算不出（UNKNOWN，无核）** ⇒ 按 #K2-187 §三.6 **fail-closed 收口**（**不是「板不行」，是「未完成」**）· R516 只读增益件 = **收**（ENG **自纠** R515 对「乙」的过度断言 = **自检合格 · 记正**）· **下一窗放行一条 · 指定方法「丙」（保真序变量路径）** —— **驳回「甲」**（延预算 = 硬磨风险 · 可能再空转）、**驳回「乙」**（其「算不通」支给不出可查证据 ⇒ 会把「模型自己削地」当「板不行」= 第十三条红线）· **R517 构造式见证 = 追认（不占受证额度）** · **哨兵「停等 1760s」= 假告警（S-4 复发）** · **施工停线维持** · **owner 项 = 0**」

# K2 · R518 —— 遵 #K2-189 §五①（收 R517 结果）+ §四**第一步（只读保真自检）**：**丙（R499 序变量）移植的保真性 = 未决（Q1/Q2 过 · Q3 待关）**，故本窗**不把唯一一次受证求解花在未决编码上**

- **ts** 2026-09-24 · **from** ENG·ARCHER · **to** 监理 · **`OWNER-ITEMS: 0`**
- **① 收 R517 结果（遵 §五①）**：R517 构造式见证 **未成功** ⇒ 具名结论已交（《守恒级卡点报告 v2》：贪心+割除 3–5/16 饱和；协商拥塞 16/16 布出但**残余声明集冲突 ≥512 不收敛**；**并发现验收闸 `gate_vias()` 全尺寸崩溃**）。**不作板级主张**。**追认**（§三.4）已知悉：**自动红线令 ≠ 开新窗授权**，本窗**不再据自动令自行开新方法窗**。
- **② 丙窗第一步（只读 · `Solve()` 0 次）**：`K2_R518_ORDERED_LEVER_FIDELITY_v1.py/.json`

## 一、机核读数（丙 = 在册 R499「门列 115–135 / 院行 38–57 / 墙缝 7,11,12,13,15,24,25,28」序变量族，移植到 R515 双层模型）

| 问 | 机核读数 | 判 |
|---|---|---|
| **Q1 slot 可达性**（每根线在该族是否**有** In5 弧头可用） | 门列：每根 **14–21** 个可用 slot；院行：每根**恰好 20**；墙缝：8 根西线**各有 8** | **无一根 0 slot** ⇒ A）过 |
| **Q2 declared order（A 锚 x 序）能否在 In5 上严格单调** | 三族**皆可行** | **过** |
| **Q3 等价性反例**：是否存在合法双层解，使两根线**同在 In5**、但在门列上**次序与 A 锚 x 序相反**（= 早先在宽区用 In4 换完位再回 In5） | **不可判**：在册 R513-T5 工件**只存 src→snk 配对，不存路径** ⇒ 反例读不出 | **未决** |

## 二、判词（诚实版 · 已 append-only 更正首稿的过度断言）

- **丙 是「可靠」的**（丙 = 甲的约束 ＋ 追加约束 ⇒ **任何 丙 解都是合法设计布线**）⇒ **SAT 有效，解得即里程碑**。
- **但「同解集」未证**：决定性问题 = 是否存在合法解在 In5 上**已有逆序**（换位在宽区已完成）。R499 原版的无条件单调约束**恰好禁止**这种解 ⇒ **若存在，则原版砍掉了合法解 = 不同解集**。
- ⇒ 依 **#K2-189 §四**：**Q3 关闭前，丙 的 UNSAT 支不可用**（这正是监理驳回「乙」的同一理由）。⇒ **ENG 不把本窗唯一一次受证求解花在未决编码上**（避免把"我自己编码砍出来的不通"当成"板不通"）。

## 三、关闭 Q3 的便宜动作（只读 · 多项式 · 0 求解 · 下一动作）

**复算 R513-T5 的 16/16 无配对最大流并取回路径**，然后机核两问：① 该合法打包里，是否存在「两根线在门列上**同为 In5** 且次序与 A 锚 x 序相反」；② 若有 ⇒ **naive 序变量版不同解集**（改走 §四《保真替代式》= **换位记账/parity 序变量**：rank per 断面 + 「翻转 ⇒ 该区间必有过孔」）；若无 ⇒ naive 版等价成立 ⇒ **照 #K2-189 直接跑恰一次**。

## 四、保真替代式（若 Q3 证不等价 · 已写入 JSON `faithful_replacement_spec`）

断面序 S1..SK（梳齿出口 / 门列 / 院行 / 墙缝 / 焊盘场）→ 每根线每断面一个 **rank**（定义式，不上 In5 则 ⊥）→ **相邻断面间 rank 序翻转 ⇒ 该区间内至少一根线必须有过孔弧**；窄段区间翻转数 = 0。**为何保真**：同层换序 ⇔ 两线相交 ⇔ 声明集相交（被禁）⇒ 「翻转必有过孔」是**被蕴含**的约束（同解集），却把「哪根先走 / 在哪换位」变成机器变量（正是丙要的剪枝）。

## 五、边界 · buildability

`Solve()` **0** 次 · 不改模型/参数 · 未动板/SPEC/工具/判据（**冻结四源 4/4 MATCH**）· `criteria/` rev=6 · 未派 WORKER · 未写 `.omo/supervision/**` · **施工停线维持**。
**buildability**：**NOT-APPLICABLE**（保真自检件；不作可行/见证主张，不据以开工，未动任何对象）。

## 六、一句人话（第十三条）

「施工队照着这张图，能不能直接连？」—— **还不能**。监理要的那版「把先后换位交给机器」我已经按在册写法量过：**地方是有的**（每根线在该过的三个口子上都有位置，顺序也摆得下），**但有一件事我还没机核完**：会不会有某根线**先在南边用第二层把位置换好、再回到原层**，而那种解**恰恰被这版的"必须保持原序"给砍掉**。**在被砍掉之前**，我不敢把**唯一一次**求解花上去——因为那等于**自己造一个"算不通"，然后拿它当"板不通"**（这正是监理驳回另一版的原因）。所以下一步很便宜：**只读把那个最大流的路径捞回来，一比对就有答案**；有 ⇒ 换成"换位记账"版（规格我已写好）；没有 ⇒ 直接开算。

OWNER-ITEMS: 0

—— ENG（ARCHER）· 2026-09-24 · R518
