dataxcash/hw_ic_k2/pm_gate/artifacts/k2_v4/P6_execution/P6_OPEN_READINESS/K2_R501_ORDERED_CONSTRUCTION_RESULT_AND_DEFECTS_v1.md

【回执首行】「【监理裁定 #K2-178】受理 R498（停手干净·诚实·求解额度未耗）· 纪律：r498 改参重跑＝真瑕疵 1 次（记档·停线维持）· 定性：生产方式遇结构墙（同一堵墙第 4 次）⇒ 属能力缺口 ⇒ 下发《方法教令 #4》换范式（次序变量＋连续位置）· 授权一次实现窗 · 监理自纠 #K2-177 §三 之越权预声明 · owner 项 = 0」

# K2 · R501 —— 《方法教令 #4》**一次实现窗**：**有序构造**（域＝自由栅格弧，非候选族）· 读数 + **两处具名缺陷**（非终局，无终局主张）

- **ts** 2026-09-24 · **from** ENG·ARCHER · **to** 监理 · **owner 闸口 0**
- **authority**：#K2-178 §四/§五（换范式 · 一次实现窗）· §七（非终局处置＝监理生产方式复核，不升 owner）· #K2-177 §一/§三 · handoff-K2-499 §0
- **实现件**：`K2_R501_CHANNEL_ORDERED_CONSTRUCTION_v1.py` · 读数：`K2_R501_CHANNEL_ORDERED_CONSTRUCTION_v1.json`
- **范式**：把「谁先谁后／走哪条通道」当**显式决策**，逐条在**残差自由弧图**上取最短路；最小间距＝**节点容量 1** ＋ **胞内 5 类线性净距形态**（与 R500 §二.2 同族）。**无** `AddAllowedAssignments`／`AddForbiddenAssignments`／候选族。

## 〇、读数（据实 · **本窗求解器 0 次调用**，受证额度 1 仍封存）

| 项 | 读数 | 判 |
|---|---|---|
| 前置硬闸（金样例 · 三类负控 · 闸声度 · **R495 对 R494 须 FAIL**） | `all_pass = True` | **PASS** |
| **执行 #1**（实现件首跑） | 16/16 车道「no legal path」· **0/16** | **退化：实现缺陷 D1** |
| **执行 #2**（修 D1 后，同窗恰跑一次） | **2/16 落位**（`3_P` 63.6mm / `0_N` 77.4mm）· 其余 14 「no legal path」 | **非终局** |
| 独立在册 `exact_gate` | **未跑**（构造未覆盖 16/16 ⇒ 无可核路线）| — |
| 判 | **NON-TERMINAL**（无终局主张；顺序构造不完备 ⇒ 不构成不可行证据）| — |

## 一、具名缺陷（可复现 · 据实）

**D1 = 弧向处理错误（＝ R500 同类缺陷，本窗首跑复现）**
复用的在册生成件 `_build_edges` 对每条格网边**只存一次**（取向＝flat index 递增），其自身 Dijkstra 按**无向**用（`csr` 里放两个方向）。
本窗首跑只把「递增取向」放进**搜索实际使用的邻接表**（反向只塞进了未使用的 `radj`）⇒ 出闸北上的**递减**跳不可达。
**可复现读数**：`3_P` 从 src(682) 仅达 **2795** 节点（无向定义下为 **7087**），snk(6970) 不可达 ⇒ 16/16 报「no legal path」。
**修法**：邻接表两向都放。**本件首跑＝退化执行，非一次实现窗的有效执行**（承 R494「接口修复仅再执行一次」· R499 同类先例）。**已披露、只修一次。**

**D2 = 实现次序与本件自身**冻结规格**不符（**未再跑**，交监理裁）**
本件规格（见实现件 docstring §3）明文：**「先西侧（需墙缝）后东侧」**；
实现却按 `free_around_B` 升序（**最紧者先**）排序 ⇒ **被执行的并不是声明的那个方法**。
⇒ 依单遍纪律，ENG **不再自转第 3 次执行**（禁「改参/改工具 → 重跑」；本窗已用掉一次缺陷修复）；
正确次序已冻结在 §四(1)，**一句话授权即可跑**。

## 二、结构性发现（可复核 · 解释了同一堵墙第 5 次）

1. **两条互相独立的通道**：a) 北西**竖直通道**（列 51–78，行 17–36 自由）；b) **皮带＋门**（行 ≥37 大自由区 → 列 115–137 行 36 东门）。
2. **列 114–115 是一道墙（行 5–37），墙上有 8 个「1 格宽」缝**：自由行＝`{7,11,12,13,15,24,25,28}`（本窗普查 · `wall.py` 读数）。
3. **B 锚按墙分两组，各 8 条**：墙西 8 条（B 列 98.9–109.5，行 5.2–27.2）· 墙东 8 条（B 列 119.5–131.5，行 3.8–27.2）。
4. ⇒ R497-a/b/c、R498、R499 的族（**单皮带行 ＋ 单门位子 ＋ 单街道**）**天然表达不了**「每条车道各自选自己的墙缝／通道」⇒ 族级筛零相容（68/120、64/120）是**族表达力**问题，**不是需求／几何不可行**。**本窗给出具名解释，闭环该 5 次。**

## 三、本窗构造失败之具名根因（＝下一版必须换的东西）

**净距影子 × 顺序构造 ⇒ 残差图碎片化。**
- 节点容量 1 ＋ 胞内 5 类形态 ⇒ 车道每走一步**对角**，即封掉该胞两个**离对角**节点（对**其他**车道）。
- 在册读数：**4 邻域（纯曼哈顿）合法图对 16/16 车道 A→B 不连通**（R500 §〇）⇒ 对角步**必需**。
- ⇒ 每条对角步密集的走线，其**有效足迹≈2 格宽**；而 A 锚簇（列 1–22，行 31.9/34.1，仅 ~4 行高的裙区）与各 B 锚袋口都窄 ⇒ **前两条落位即把后 14 条的残差图切断**。
- ⇒ **顺序（greedy）构造在本问题上结构性不足；必须用「联合（同时）定位」的方法**（非再调次序/斥力）。
- 规模墙（本窗实测）：全格网**联合多商品流 ≈ 639,844 条有向弧 ＋ 113,413 条「车道×节点」占用** ⇒ 单窗 CP-SAT 不可行。

## 四、下一窗（**冻结规格 · 一句话授权即可**）

1. **(1) 先补跑声明方法**：把本件排序改为**声明的西侧组先、东侧组后**（组内按 B x 升序；2 行改动，规格已冻结），**恰跑一次**；
2. **(2) 若仍非终局 ⇒ 联合方法（二通道分解）**：以「通道/墙缝指派」为**序变量**（西 8 车道 → 墙西通道／东 8 车道 → 皮带＋门），联合求解残差饱和，而非逐条贪心；
   或 **两级格网联合 MCF**：门区／迷宫保持 0.435，开放区（皮带／裙区／通道）粗化为 0.87（规模降至 ~1.6e5 弧）。
3. 验收不变：**在册 `exact_gate`**（真最近距 ＋ 真穿越⇒0）＋ R495 要求级闸；缺一 fail-closed。

## 五、一句人话（第十三条）

「施工队照着这张图，能不能直接连？」——**还不能**：本窗没有交出任何可核路线（构造只落位 2/16，未过闸）。
这次的新增量是**两个确定的东西**：① 那堵墙上有 **8 个缝、正对 8 条「墙西」车道**（所以老族的「单门位子」永远配不出来）；② 一旦某条车道走对角步，它会把旁边两个格位一起封掉 ⇒ **逐条贪心必碎**，必须**同时定位**。

## 六、边界

冻结四源 **4/4** 未动 · `criteria/` rev=6 未动 · 未改在册工具/生成器/SPEC/原理图 · 未派 WORKER · 临时仅 `/tmp/opencode` · 未写 `.omo/supervision/**` · **本窗 `Solve()` 调用 0 次 ⇒ 受证额度 1 未耗**。

OWNER-ITEMS: 0

—— ENG（ARCHER）· 2026-09-24 · 复现：`K2_R501_CHANNEL_ORDERED_CONSTRUCTION_v1.py`（前置全绿 → 同窗一次构造）
