dataxcash/hw_ic_k2/pm_gate/artifacts/k2_v4/P6_execution/P6_OPEN_READINESS/K2_R466_ARCHITECTURE_REBUILD_SPEC_V2_NO_RESIDUAL_TEMPLATE_GLOBAL_SINGLE_MODEL_v1.md

# K2 · R466 —— **架构重建规格 v2**（全路径零残余模板 · 全局单模型 · 重设计评审用）

- **ts** 2026-09-24T04:45:48 · **from** ENG·ARCHER · **to** 监理 · **owner 闸口 0**
- **authority**：**#K2-164 §四.2**（v2：全路径零残余模板 · 禁候选集枚举 · 全局单模型 · 评审格加『全路径域非空 ∧ 全局指派存在性』）· #K2-163 · #K2-160 §四.3.d · 教令 §五（承在册 R362 · C-B2UP-1）
- **性质**：只交规格 v2（未改代码 · 未跑见证 · 未启全量 · 停等评审）

## 0. 一句话
**架构重建规格 v2（全路径零残余模板）**：除 `srow/nrow/seat` 外，**锚侧下行/上行走廊列（colIn/colOut）亦为求解器变量**，并新增**枢纽穿越序 `xorder`** 显式编码绕墙 winding（承在册 R362 / R450）⇒ 生成器**无任何写死形状段**；**全局单模型、无候选集枚举**；评审格加「**全路径逐段域非空 ∧ 全局指派存在性**」；负控增至 **①–⑥**。**只交规格 · 停等重设计评审 · 未进入实现 · 额度 1 未耗。**

## 1. 变量（**6 类全为求解器变量**）
- **colIn (i)**（求解器变量）：锚侧**下行走廊列**索引（A 锚 → 长走行的下行发生在哪一列）· 域 = A 侧可用自由列　— **本轮新增**：此前 R1 把下行钉在 A_x（= 残余模板，R465 域空之因）
- **colOut (i)**（求解器变量）：锚侧**上行走廊列**索引（长走行 → B 锚的上行发生在哪一列）· 域 = B 侧可用自由列　— **本轮新增**
- **srow (i)**（求解器变量）：**南带长走行行**索引 · 域 = 南带可用自由行
- **nrow (i)**（求解器变量）：**北带长走行行**索引 · 域 = 北带可用自由行
- **seat (i)**（求解器变量）：**端口穿越列**索引 · 域 = 端口自由列（实测 17–18 槽）
- **xorder_h (h,i)**（求解器变量（**winding/穿越序**））：在**枢纽 h**（端口北口 / 南带西端 / 北带西端 等）处，各线之**穿越先后次序**；用于**显式编码绕墙 winding 与非交叉**（承在册 R362 口径）　— **本轮新增·全局非交叉的显式编码**

**投影函数 f（零自由量）**：给定 (colIn, srow, seat, nrow, colOut) + winding 序，路径点列 = A 锚 → (colIn, A_y) 竖降至 (colIn, SY(srow)) → 横移至 (PX(seat), SY(srow)) → 竖穿至 (PX(seat), NY(nrow)) → 横移至 (colOut, NY(nrow)) → 竖升至 (colOut, B_y) → B 锚。**每段的行/列皆为上述求解器变量**；生成器**无任何写死的形状段**（除「按 winding 序依次通过枢纽」这一**拓扑约定**，其参数亦由变量决定）。

## 2. 规则 R1–R6
### R1 锚侧下行走廊 = 变量
- **规则**：自 A 锚在 x=colIn 竖直下行（colIn 由求解器拍板；**不再固定为 A_x**）。
- **分离义务**：colIn 互异 ⇒ 下行竖线两两 ≥0.435
- **断言**：入口区逐对最小距 ≥0.435
- **负控**：强令两线同 colIn ⇒ 不合格

### R2 南带长走行 = 变量
- **规则**：水平段 y=SY(srow)。
- **分离义务**：srow 互异 ⇒ 行距 ≥0.435
- **断言**：南行集合两两 ≥0.435
- **负控**：同 srow ⇒ 不合格

### R3 端口穿越 = 变量
- **规则**：x=PX(seat) 竖穿南北两行。
- **分离义务**：seat 互异 ⇒ 列距 ≥0.435
- **断言**：端口列两两 ≥0.435
- **负控**：同 seat ⇒ 不合格

### R4 横向段 + winding 序（显式非交叉）
- **规则**：横段端点**均为变量**（colIn/seat/colOut 决定，**无固定端点**）；**枢纽处按 xorder 序依次穿越** ⇒ 非交叉由**次序变量**保证（承 R362 winding 编码）。
- **分离义务**：按 winding 序穿越 ⇒ 折线两两 ≥0.435（含横×竖）
- **断言**：**在册闸** n_lane_pitch_viol==0
- **负控**：注入**反序**穿越 ⇒ 不合格

### R5 北带长走行 + 锚侧上行 = 变量
- **规则**：水平段 y=NY(nrow)；自 (colOut, NY(nrow)) 竖直上行至 B 锚。
- **分离义务**：nrow / colOut 互异 ⇒ ≥0.435
- **断言**：北行集合与出口区逐对 ≥0.435
- **负控**：同 nrow 或同 colOut ⇒ 不合格

### R6 障碍净距（域表达 · 渲染器零调整）
- **规则**：把投影后不满足净距的组合**从各变量域中剔除**（域过滤 ⇒ 非候选集枚举）。
- **分离义务**：净距 ≥ max(0.175, req)（孔到铜 0.25）
- **断言**：**在册闸** n_clearance_viol==0 ∧ clearance_min_mm ≥0
- **负控**：⑤ 可构造形态违约实例 ⇒ 产出前判不合格

## 3. 评审格（四格）
- **(1) 闭合（承 #K2-162 三步）**：每个量有唯一几何定义 ∧ 无口径冲突 ∧ 输入依赖前置断言化
- **(2) **全路径域非空**（承 #K2-163 一格 + 本轮修正）**：**每一类变量的每一个域**皆非空，且**逐段**（含锚侧出入段）在域内存在可通行取值；**逐网非空改为全路径逐段非空**
- **(3) **全局指派存在性**（本轮新增·硬）**：AllDifferent（6 类变量）+ 单调嵌套 + **枢纽穿越序**之**全局可满足性论证**：容量 ≥16（端口 17–18 槽 · 带内行 24）· 各域序区间可对齐 · 枢纽穿越序可行；**充分性之最终判定仍由一次全量受证求解**（跑不通 ⇒ 含核不可行证书）
  - **逐网非空 ≠ 全局可指派** —— R465 之教训
- **(4) 独立复算（承 #K2-163 §四.3.c）**：见证与关键读数走**独立路径**（不使用生成器自身函数；在以册 exact_gate + 直算折线距），并落对照件

## 4. 负控六件
- ① 座(端口列)不足 ⇒ 不合格
- ② 强制两线同端口列 ⇒ 不合格
- ③ 强制两线同长走行（南或北）⇒ 不合格
- ④ 注入渲染器越权（吸附/兜底）⇒ 单射/几何断言必抓
- ⑤ 可构造形态违约实例 ⇒ 产出前判不合格
- ⑥（**本轮新增**）强制两线**同 winding 序位**（即穿越序冲突）⇒ 必不合格

## 5. 为何弃用候选集
**#K2-164 §四.2.b 明令禁用「逐网候选集枚举 + 互斥」**（R463/R465 两次实证其在残余处必出域空）⇒ 本 v2 改为**全局单模型**：6 类序变量 + AllDifferent + 单调嵌套 + 枢纽穿越序；域过滤仅用于**剔除不可行取值**，**不用于枚举候选路径**。

## 6. 残余模板已除
R1 之「下行固定于 A_x」= R465 域空之直接成因（锚侧残余模板）⇒ v2 已将其改为变量 `colIn`（上行同理 `colOut`）。**全路径各段的行/列再无常量**。

## 7. 可核自检计划
- (i) 逐段可通行性：对每类变量的每个取值，检验对应段的净距（确定性几何）⇒ 报各类域之「逐段可用取值数」
- (ii) 全局存在性论证：6 类 AllDifferent 之容量对账（端口 ≥16 · 行 ≥16 · 出入列 ≥16）+ 单调区间对齐 + 枢纽穿越序可行性
- (iii) **独立复算**：以在册 exact_gate + 直算折线距对见证件复算并落对照件

## 8. 序列与额度
① 本 v2 经**重设计评审 PASS**（闭合 ∧ 全路径逐段域非空 ∧ 全局指派存在性有据）→ ② **一次**实现（忠实 v2）→ ③ **一次**小实例见证（可解 + 几何分离 + 单射 + 负控①–⑥全拦）→ ④ **一次**全量受证（产物两件 + **可施工性字段**）→ ⑤ 在册闸 rev=6 全条三项全 0；跑不通 ⇒ **含核不可行证书**；**严禁删约束换 SAT**。**额度 = 1。**

## 9. 边界
**只交规格 v2**：未改代码 · 未跑见证 · 未启全量 · 未动模型/约束/冻结需求/判据 · 冻结四源 4/4 未动 · criteria rev=6 未动 · 未派 WORKER。

## 10. 请监理重设计评审
- ① `colIn/colOut + srow/nrow/seat + xorder` 是否达成『**全路径零残余模板**』（#K2-164 §四.2.a）？
- ② 是否已彻底**弃用候选集枚举**（改全局单模型）？
- ③ 评审格 (3)『全局指派存在性』是否有据、是否达新增硬门槛？
- ④ 负控 ①–⑥（含新增 ⑥ 穿越序冲突）是否齐备可构造？
- ⑤ 独立复算计划是否达标？
- ⑥ 序列与额度是否照准？

---
—— ENG（ARCHER）· 2026-09-24T04:45 · 停等重设计评审 · sha16 `583680a290ec72a7`
