dataxcash/hw_ic_k2/pm_gate/artifacts/k2_v4/P6_execution/P6_OPEN_READINESS/K2_R464_ARCHITECTURE_REBUILD_SPEC_ROUTING_AS_SOLVER_VARIABLES_FOR_REDESIGN_REVIEW_v1.md

# K2 · R464 —— **架构重建规格**（走法也交求解器 · 重设计评审用）

- **ts** 2026-09-24T04:15:27 · **from** ENG·ARCHER · **to** 监理 · **owner 闸口 0**
- **authority**：**#K2-163 §四.3**（产线级架构重建令 · 重建对象=几何生成架构 · 强制重设计评审 · 独立复算）· #K2-160 §四.3.d · R450 · R438 · R446 · R455 · R459/R460
- **性质**：只交规格（未改代码 · 未跑见证 · 未启全量 · 停等评审）

## 0. 一句话
**架构重建规格（重设计）**：**走法也交求解器** —— 南/北**长走行**与**端口列**三类对象全为**求解器变量**（`p_i/s_i/n_i`），生成器**纯投影、零自由量**；新增**评审格「形状族摆得下吗」**（逐网域非空 + 横截面容量 + 单调兼容 + 必要/充分之界）。**只交规格 · 停等重设计评审 · 未进入实现 · 额度 1 未耗。**

## 1. 变量（**三类走法对象全为求解器变量**）+ 投影函数
{
 "seat": "每线：端口穿越列索引 p_i ∈ 0..17（列 x = 135.45 + 0.435·p_i）——**求解器变量**",
 "srow": "每线：**南带长走行**索引 s_i ∈ 0..23（行 y = 57.100 + 0.435·s_i）——**求解器变量**（本轮新增：长走行不再是模板常量）",
 "nrow": "每线：**北带长走行**索引 n_i ∈ 0..23（行 y = 54.900 − 0.435·n_i）——**求解器变量**（本轮新增）",
 "zero_free": "生成器**零自由量**：路径 = f(p_i, s_i, n_i) 的**确定函数**；无吸附/兜底/裁剪/合并/调整量/障碍绕行"
}

**投影函数 f（唯一定义）**：给定 (p_i, s_i, n_i)，点列 = [ (A_x,A_y), (A_x, SY(s)), (PX(p), SY(s)), (PX(p), NY(n)), (B_x, NY(n)), (B_x,B_y) ]；PX(p)=135.45+0.435p · SY(s)=57.100+0.435s · NY(n)=54.900−0.435n。**形状固定，自由度全在三个选址变量上**（承 R450：「映射须是求解器的决定，绝不做事前限制」）。

## 2. 规则 R1–R6（每条：规则 / 分离义务 / 可复现断言 / 对应负控）
### R1 首段 · 只准竖向
- **规则**：(A_x,A_y) 垂直至 (A_x, SY(s_i))。**禁**锚点 y 横移；**无**调整量。
- **分离义务**：|ΔA_x| ≥0.500
- **断言**：入口区逐对最小距 ≥0.435
- **负控**：强令两线首段同列 ⇒ 不合格

### R2 南带长走行 = 求解器变量
- **规则**：水平段位于 y=SY(s_i)（**s_i 由求解器拍板**，非模板常量）。**禁**吸附/对齐。
- **分离义务**：s_i 互异 ⇒ 行距 ≥0.435
- **断言**：南行集合两两 ≥0.435
- **负控**：① 同 s 必不合格；④ 注入吸附 ⇒ 单射/几何断言必抓

### R3 端口穿越列 = 求解器变量
- **规则**：在 x=PX(p_i) 竖向贯穿南北两行。
- **分离义务**：p_i 互异 ⇒ 列距 ≥0.435
- **断言**：端口列两两 ≥0.435
- **负控**：② 同 p ⇒ 不合格

### R4 横向段端点固定 · 单调嵌套
- **规则**：南行横段 x∈[A_x, PX(p_i)]；北行横段 x∈[PX(p_i), B_x]；**端点固定、无调整量**；三坐标随 A 锚 x 序**单调**（方向由求解器选）。
- **分离义务**：单调嵌套 ⇒ 折线两两 ≥0.435（含横×竖）
- **断言**：**在册闸** n_lane_pitch_viol==0
- **负控**：注入非单调 ⇒ 不合格

### R5 北带长走行 = 求解器变量
- **规则**：水平段位于 y=NY(n_i)；至 (B_x, NY(n_i)) 后垂直入 B。
- **分离义务**：n_i 互异 ⇒ 行距 ≥0.435
- **断言**：北行集合两两 ≥0.435；出口区逐对 ≥0.435
- **负控**：③ 同 n ⇒ 不合格

### R6 障碍净距（域表达 · 渲染器零调整）
- **规则**：把投影后不满足净距的 (p,s,n) **从域中剔除**。
- **分离义务**：净距 ≥ max(0.175, req)（孔到铜 0.25）
- **断言**：**在册闸** n_clearance_viol==0 ∧ clearance_min_mm ≥0
- **负控**：⑤ 可构造形态违约实例（产出前判不合格）

## 3. **评审新格**：形状族摆得下吗？（表达力/可解性）
- (1) **逐网域非空**：对每线枚举 18×24×24 组合，按 R6 剔除后 **|D_i| > 0**（确定性可复算；R463 之域空正因此格缺位而未被拦住）
- (2) **横截面容量**：南带/北带可用行数与端口列数 **≥16**（R260 F-4 端口 7.6mm ⇒ 17–18 槽；带内行数 24）⇒ `AllDifferent(行/列)` 可满足
- (3) **单调兼容**：三坐标域在 A 锚 x 序上**同序区间可对齐**（单调赋值存在性论证）
- (4) **必要/充分之界**：以上为**必要前提 + 充分性论证**；**充分性之最终判定仍由一次全量受证求解**（跑不通 ⇒ 含核不可行证书）——本格只保证「不再出现『自洽但摆不下』却到实现才暴露」

交图前**必跑**：闭合自检三步（承 #K2-162）**+ 本格可解性自检**；任一不过 ⇒ 规格判定不合格，**不得进入实现**

## 4. 负控五件
- ① 座位(列)不足 ⇒ 不合格
- ② 强制两线同端口列 ⇒ 不合格
- ③ 强制两线同南/北长走行 ⇒ 不合格
- ④ 注入渲染器越权（吸附/兜底）⇒ 单射断言必抓
- ⑤ 可构造形态违约实例 ⇒ 产出前判不合格

## 5. 独立复算承诺
承 #K2-163 §四.3.c：见证件与关键读数将由**独立路径复算**（不使用生成器自身函数；以在册 `exact_gate` + 直算折线距）并落件对照。

## 6. 序列与额度
① 本规格经**重设计评审 PASS**（闭合 ∧ 表达力/可解性有据）→ ② **一次**实现（忠实规格）→ ③ **一次**小实例见证（可解 + 几何分离 + 单射 + 负控①–⑤全拦）→ ④ **一次**全量受证（产物两件 + **可施工性字段**）→ ⑤ 在册闸 rev=6 全条三项全 0；跑不通 ⇒ **含核不可行证书**；**严禁删约束换 SAT**。**额度 = 1。**

## 7. 边界
**只交规格**：未改代码 · 未跑见证 · 未启全量 · 未动模型/约束/冻结需求/判据 · 冻结四源 4/4 未动 · `criteria/` rev=6 未动 · 未派 WORKER。

## 8. 请监理重设计评审
- ① `p/s/n` 三类对象全为求解器变量 + 生成器零自由量 —— 是否达成 #K2-163 §四.3.a？
- ② 评审格「形状族摆得下吗」之四项是否有据、是否达到新增门槛？
- ③ 负控①–⑤（含 ③ 改为同长走行）是否齐备可构造？
- ④ 独立复算承诺是否达标？
- ⑤ 序列与额度是否照准？

---
—— ENG（ARCHER）· 2026-09-24T04:15 · 停等重设计评审 · sha16 `8a177c413d0a9629`
