dataxcash/hw_ic_k2/pm_gate/artifacts/k2_v4/P6_execution/P6_OPEN_READINESS/K2_R446_BAND_WINDOW_ONION_CONSTRUCTION_14_OF_16_NEEDS_GLOBAL_REASSIGN_v1.md

# K2 · R446 —— 带窗洋葱构造：**14/16** ⇒ 末尾 2 条须全局重派

- **ts** 2026-09-23T21:51:45 · **from** ENG·ARCHER · **to** 监理 · **owner 闸口 0**
- **authority**：#K2-150（求解窗照跑不扰）· 监理停止令 · R442 计划 · #K2-148 裁定②.2 · R401 口径

## 0. 一句话
按 R442 计划第(1)步实现**带窗洋葱构造**（确定性 · 非 solver · 一次）⇒ **14/16 网构造成功**；未成者 **2 条**：`PCIE_UP_OUT0_N_J2`、`PCIE_UP_OUT3_P_J2`（其 A/B 出入落在被分配的带窗之外）。⇒ **构造式到此为止（14/16）**，最后 2 条须**全局重派**（换窗/换座次）——正是 **CP-SAT 一次求解**所要解决者。

## 1. 方法
逐网（A 锚 x 序）分配**南带窗**与**北带窗**（窗随序号由深到浅 = 洋葱嵌套）＋ 其入口/出口列 + 其**门口位子 E_k**（18 槽按序分配 ⇒ 座次单调）⇒ 在窗内自由格点上 BFS 取阶梯；窗宽自 ±1 起、失败则加宽（1,2,3,4,6,8）——**确定性规则 · 无随机 · 无 solver**。

## 2. 结果
{"routed": 14, "total": 16, "fails": ["PCIE_UP_OUT0_N_J2", "PCIE_UP_OUT3_P_J2"], "bands": {"S_rows": 24, "N_rows": 35, "E_slots": 18}, "note": "本轮**未跑 solver**；结果 = 构造式上限。"}

## 3. 为何须全局重派
固定带窗分配下，部分网的出入路径落在他网窗带之外 ⇒ 无路。要闭合必须**跨网重派**（把窗/座次让给需要者）——单遍贪心/固定分配做不到，**全局指派（CP-SAT）**可：候选 = 各网 × 各窗宽（现已生成）· 约束 = 每网恰选一候选 + **不同网候选节点集互斥** + 门口座次随 A 锚 x 序**单调**。

## 4. 下一步（本窗口·唯一）
**本窗口受证求解一次（仍未消耗）**：把上述 per-lane 多窗宽候选喂入 CP-SAT（节点互斥 + 单调座次）→ 金样例 → Validate+负控 → **模型件 sha 登记** → **受证求解一次**（≤900s）→ **R401 预登记口径验收**（三项全 0 · 全 16 条）。

## 5. 边界
冻结四源 4/4 未动 · criteria/ rev=6 未动 · 未改在册工具/生成器/SPEC 设计/原理图 · 未派 WORKER · **本轮未运行求解器**。

---
—— ENG（ARCHER）· 2026-09-23T21:51 · sha16 `b7194c94e1dfd1f4`
