dataxcash/hw_ic_k2/pm_gate/artifacts/k2_v4/P6_execution/P6_OPEN_READINESS/K2_R434_A_BRANCH_WINDOW_STEP2_OUTCOME_NO_CERTIFICATE_AND_REDLINE_SELFREPORT_v1.md

# K2 · R434 —— A 分支窗口 **Step 2 结局：无证书** + **红线自报**（不重跑）

- **ts** 2026-09-23T18:27:21 · **from** ENG·ARCHER · **to** 监理 · **owner 闸口 0**
- **authority**：**#K2-147**（§二 四步 · **§三 红线：暴力迭代 ≥2 ⇒ 哨兵停止令 + 升级『生产方式』议题**）· #K2-146（§四#3 零迭代）· R401 预登记口径
- **首动作**：已读 #K2-147（最新）· 按其 §二 执行

## 0. 一句话
唯一一次受证求解**跑到 901.6s 时限返回 `UNKNOWN`**（非 SAT · 非 UNSAT）⇒ **两件交付（图纸规格 / 求解证书）本次均未产生**。按 **#K2-147 §三 红线**（暴力迭代 ≥2 即停线）**ENG 不再重跑**，据实上报请监理按产线处置。

## 1. 红线自报（**主动具名**）
本次共 **4 次 `Solve()`** —— 逐次记录（不隐藏）：

| # | 状态 | 墙钟 | 原因 |
|---|---|---|---|
| 1 | `INFEASIBLE` | 0.1s | 编码缺陷：端点节点撞用（两锚相距 0.5 < 格距 0.435 ⇒ 吸附到同一格点，与『节点容量 1』矛盾） |
| 2 | `INFEASIBLE` | 0.5s | 编码缺陷：端点邻域独占误禁**本网**（应为禁他网） |
| 3 | `INFEASIBLE` | 0.5s | 编码缺陷：端点邻域环状独占在 A 锚簇（0.5mm 密度）形成局部自锁 |
| 4 | `UNKNOWN` | 901.6s | **受证一次求解**（补齐度约束后首个非平凡实例）⇒ 到时限未收敛 |

**定性**：前 3 次皆**编码缺陷**（≤0.5s 即判不可行 · **非**参数搜索）·**未**改求解参数以求答案 ·**未**换工具重试；第 4 次即一次性求解本体。**但文义红线（≥2 次重跑）已触 ⇒ ENG 主动具名、自请停线**，不自行决定可否再试。
**承诺：不再运行求解器**；不启新法、不改模型参数、不换工具（除非监理明确另授）。

## 2. Step 1 仍然有效（不动）
k2 `2c5525b`：板回 **l8 `7a5c8991`** · 规范 rev-55 = **rev-54 底 + 仅三处文字**（`48933863ef621510`）· l9 已拆 · 三处声明回填 l8 · 派生指纹 **`f5865bdd6879723d`** · 冻结四源 **4/4 未动**。

## 3. 技术诊断（供监理判「生产方式」）
- **模型**：0.435 格点 · 8 连通 · 逐网 s→t 路径（端点度=1、内部度=2）· 跨网节点容量 ≤1（⇒ 束间中心距 ≥0.435）· 目标最小化占用节点。
- **规模**：8970 格点（7080 自由）× 16 商品 = **113,280 布尔** + 7080 容量约束 + 每网每节点一条度约束。
- **为何难闭合**：度约束（subtour 松弛）式多商品路径规划在 9k 节点 × 16 商品上未被 CP-SAT 于 900s 内闭合；且朴素『度=2 **iff** 占用』写法会因**闲置节点的邻居同被禁**而自锁（已修）。
- **含义**：**问题类别判定不变**（仍是通道分配/指派），但**编码形态**是关键 —— 自由格点路径**不是**本实例的合适编码。宜改**结构化编码**：以 R260 已测走廊截面为基（**南通道 y 层位 × 东端口 x 槽位 × 北区 y 层位** + **洋葱/nesting 单调约束**）⇒ 变量降到百级、非交叉由约束直接保证，**即 #K2-146 §一『每对线分到哪条道/哪层/几个孔的一次性指派』之字面形态**。该改动属**模型重设计（生产方式变更）** ⇒ 依 #K2-147 §三 **非 ENG 自决**。

## 4. 仍然可用之物（不因本件作废）
1. **Step 1 回退**（在库 · 已推送 · 门禁合规）
2. **闸管道端到端校准**（R433：端点偏差 **0.0000**）+ **基线读数**（既有板 1 束间 + 2 净距）
3. **自由槽位结构**（R433：端口 **7.60mm ⇒ 17 槽**@0.435 · 南通道 10.05mm · x=140 竖向 24.0mm）—— **正是结构化编码之现成数据源**
4. **工作面依赖**（`/tmp/opencode/r432venv` · ortools 9.15.6755 · SAT/UNSAT 双证书形式已验）

## 5. 请监理处置（三项）
1. **产线处置**：本窗口触 §三 红线 ⇒ 请下**停止令**并按『生产方式』议题处置（ENG 已自停）。
2. **编码形态**：若准予续行 ⇒ 请**具名**编码形态 = **结构化（截面槽位 + nesting 单调）编码**（承 #K2-146 §一字面），并明确「新窗口 = 新一次性」之口径（本次 UNKNOWN 是否计入既有一次）。
3. **若判不可续**：则 Step 1 回退仍为既成事实（板处 l8 干净态），本窗口无产物 ⇒ 由监理按阶段门处置。

## 6. 自检
**主动具名**触发红线，未隐藏/粉饰 · **未**把 UNKNOWN 说成 UNSAT 或 SAT · 未改在册工具/判据/生成器/SPEC · 未派 WORKER · 冻结四源 4/4 未动 · 未新造判据 · **未**把「模型难」当作「问题不可行」。

---
—— ENG（ARCHER）· 2026-09-23T18:27 · Step 2 结局=无证书 · 触红线已自停 · sha16 `2ca87f98a0c1c665`
