dataxcash/hw_ic_k2/pm_gate/artifacts/k2_v4/P6_execution/P6_OPEN_READINESS/K2_R424_L9_DELTA_EXACT_AND_DETERMINISTIC_REVERT_BUILDABILITY_v1.md

# K2 · R424 —— l9 缺陷**文件级差集**核证 + **确定性回退**可施工性（只读）

- **ts** 2026-09-22T23:52+0800 · **from** ENG·ARCHER（续接会话 · context 归零 · 承 handoff R423）· **to** 监理 · **owner 闸口 0**
- **authority**：**#K2-142 §四**（准只读残余测量 · 禁新法/变体/扫描/派工/烙板）· **owner #14⑥**（不 park）· **owner ⑧**（成果须附可施工性 + 搬迁清单）· **#K2-143 §四**（甲分支含「修底图」）· **handoff R423 §8.4**
- **首动作**：已读 `.omo/supervision/ledger/`（含 `sent/`、`outbox/`）全部 `K2-RULING-*` ⇒ 最新 **#K2-144**（23:45 · owner 项 0）· **无更晚裁定 · 无 owner 回件** ⇒ 本轮做 §8.4 允许之只读残余。
- **锚**：l8 **`7a5c89913d6e5d0a`** · l9 **`77aaa63fe016b450`** · pro `c009058005829f09` · 判据 **rev=6 MATCH**（只读）· 冻结四源 **4/4 未动**

## 0. 一句话
**l9 与 l8 的全部差异，就是 C-w 搬迁那一步铜**：切除两板**所有线段/过孔块**后，余下文本**逐字节相同**（sha256[:16] 皆 `c05784bee336c30f`）。差集 = **增 303 线段 + 2 过孔 / 删 27 线段 + 4 过孔**（增集**全部 0.100mm 宽**）。⇒ l9 的 **59 error / 11 段非 45° / 0.100 宽漂移 / 最小铜间距 FAIL**，**无一例外**出自这一个差集；而 **l8 同会话·同仪器·同 pro 实测 error=0**。**⇒ 存在一条零设计、by construction 合法的回退路径。**

## 1. 结论（五项）

| # | 结论 | 证据 |
|---|---|---|
| **1** | **差集只在铜上**：footprint/pad/zone（含铺铜 fill）/drawing/边框**一字节未改** | 切除全部 `(segment…)/(via…)` 块后逐字节比对 ⇒ **identical=true**（各 1,118,129 B · 同 sha256[:16]） |
| **2** | **增集 = 搬迁新铜**：**305 个对象 · 全部宽 0.100mm**（l8 同网 0.200）⇒ 即 R420「303 段 0.10」之全集 | pcbnew 对象级多重集相减；`R424_l9_delta_measure/delta_tracks_added_303.json` |
| **3** | **删集 = R331 在册 neck-window 清单，逐网命中、零外溢** | `PERSTA#` 13/13 段 · `ADDR1_7-0` 11/11 段 + **2/2 孔** · `I2C1_SDA` 3/3 段 + **1/1 孔** · `ADDR0_15-8` **1/1 孔** |
| **4** | **归因闭环**：R411 之 9 个 culprit uuid 与 11 段非 45° uuid **全部 ⊆ 增集**（missing=0）⇒ 缺陷**仅**由该差集产生 | `R424_l9_delta_measure/uuid_crosscheck_R411.txt` |
| **5** | **增集来源 25/303 段在 `/tmp`（非仓内）**：按施加器 ADD 代码静态重建 305 对象 ⇒ **303/303 逐条命中**；`PERSTA#` 278 段来源在仓内（R337），其余 **3 网 25 段**之唯一来源为 `/tmp/opencode/k2r135*/**.json` ⇒ **l9 之这 3 网铜无法仅由仓内状态重新生成** | `R424_l9_delta_measure/provenance_of_added_303.json` |

**独立 DRC A/B（同会话 · 同仪器 · 同 pro）**：l8 = **0 error** / 204 warning / unconn 0 · l9 = **59 error**（shorting 19 · crossing 6 · clearance 21 · hole_clearance 13）/ 208 warning / unconn 0 —— 与在册 R410 逐类一致。
> 自检更正：首轮以**默认规则**（未挂 pro）直跑 l9 得 1108 error，识别为**口径错误**（l9 无同批 pro ⇒ 默认规则把 0.075 环宽/0.20 钻等判错），**已作废、未采信**；正式读数一律挂 l8 pro。

## 2. 两条路，逐个回答宪法第十三条

> **第十三条规定：可行/见证类成果必须附可施工性 —— 要么证明不动任何对象即可施工，要么给出搬迁清单（哪些网/过孔要动、动到哪、谁批的）。**

### 路线 R · **回退（撤销 C-w 搬迁）**
- **动什么**：删 l9 新增之 **305** 个对象；放回 l8 被删之 **31** 个对象（等价实现：受审板取 l8）。
- **动到哪**：**回原位**（原坐标 = l8 位置）。全为**已存在之原文块**，无一个待定几何。
- **谁批的**：监理（`PENDING_RULINGS v62` 之 l9 缺陷处置项）；若与 owner ②-UP 选择联动 ⇒ 随 **#K2-143 §四** 预声明一并落地。
- **可施工性**：**能。零设计。** 由结论 1（两板除线段/过孔外逐字节同）+ 结论 4 之 l8 error=0 ⇒ 回退板几何 **≡ l8** ⇒ **error=0 / 非 45°=0 成立 by construction**。
- **连带**：受审板锚变更 ⇒ SPEC 声明性回填（board_sha16 ×3）与 P4 派生模型指纹**须重锚**；R270 项 11「l9 落 `hw/`」须随之改判。

### 路线 F · **前向修缺陷（保留搬迁）**
- **C0 铺铜回填 18 区 / 11 段 45° 化 / 303 段宽 0.100→网类 0.200** = **规则映射**（可施工）。
- **C1（20 冲突）`DS320_STRAP_B_ADDR1_7-0` In2 4 段须另择路径避开 `PCIE_UP0_N/1_N/2_P/3_P/4_N/5_N` ⇒ 重新布线**；**C2/C3** 同。
- **动到哪：没有。** 在册件（R331）只有「删」清单，**无「改后」目标几何** ⇒ 按宪法第十三条 **判「图纸层缺图」**，不得据以开工。
- **可施工性**：**不能**（正是红线所禁之「需现场搜索/兜底」）。
- **另**：其增集 25/303 段之来源不在仓内（F8）⇒ 即使获批设计，亦应先**把目标几何落回仓内**再施工。
- **谁批的**：须监理放行；动**设计内容**（重新布线）另需获批方案件 +（若属方法变更）新生产窗。

## 3. 对 owner 取舍的意义（不改选项，只补成本下限）
**C-w 搬迁存在的唯一目的**（R331 → #K2-136 §三）= **腾出 In5 窄颈给 16 lane 程序**；而该 16/16 lane 要求**正是 owner 正在取舍的那一条**。
- owner 裁「**甲**（放宽孔数/层数一条）」⇒ 16 lane 程序不再必需 ⇒ **搬迁亦失去理由** ⇒「修底图」可降为 **确定性回退（零设计、零工时）**；#K2-143 §三 之「≈零返工」可再下修。
- owner 裁「**乙**（维持）」⇒ 搬迁须保留 ⇒ **C1 须重新布线（真设计成本）**，且须新生产窗。

## 4. 请监理（**皆属监理自裁面 · 不涉 owner 新项**）
1. **Q1（走廊/搬迁处置）**：owner 裁甲 ⇒ **C-w 搬迁是否仍需保留**？不需 ⇒ 请裁「受审板回 `l8`（或等价确定性回退）」并同步指示声明性回填/指纹重锚；需 ⇒ 见 Q2。
2. **Q2（放行范围）**：若保留 ⇒ C1/C2/C3 之**目标几何由谁产出**？（ENG 未获批不得改设计内容；宪法第一条：监理不替 ENG 写方案 ⇒ 请指定方案件之授权范围与窗口。）
3. **Q3（口径）**：`C-PRO-L9`（l9 无同批 pro）正式口径请钉死。

## 4b. 束间面（对 owner 裁「甲 ⇒ 回退」之补充）
由 F1/F7（16 网 In5 铜两板**逐字节同**）⇒ **任何**间距口径下**束间（lane↔lane）读数 l8 ≡ l9** ⇒ R416 所记 `0.4491 ≥ 0.435` **在 l8 上同值** ⇒ **回退到 l8 在束间面不减分（caliber-free，不依赖任何口径选择）**。
**lane↔非 lane** 面两板**不同**（l8 颈内有 `PERSTA#`/straps 铜 · l9 之读数为 `0.2531`）⇒ 欲在 l8 上复现须**先钉死口径**（R417 §D1 未放行）⇒ **本件不报该面读数**，亦不裁『0.435 是否亦管 lane↔非lane』（口径归属监理 · C-12 不得换口径充绿）。

## 5. 诚实边界
- **回退板未构造、未烙板**：其合法性系「几何 ≡ l8 + l8 实测 0 error」之推得结论，推理链已写明，**未冒充实测见证**。
- 未修复 · 未生成 l9′ · 未变体重跑/参数扫描 · 未改施加器/SPEC/原理图/生成器 · 未派 WORKER · 未写 `.omo/supervision/**`。
- 冻结四源 **4/4 未动** · `criteria/` **只读**（rev=6 MATCH）· 临时仅 `/tmp/opencode`。

## 6. 件
`K2_R424_L9_DELTA_EXACT_AND_DETERMINISTIC_REVERT_BUILDABILITY_v1.json`（sha16 见 `.sha16.txt`）·
`R424_l9_delta_measure/`：`delta_tracks_added_303.json` · `delta_tracks_removed_27.json` · `delta_vias_added2_removed4.json` · `drc_ab_l8_l9_same_pro.json` · `file_level_identity_proof.txt` · `uuid_crosscheck_R411.txt`

---
—— ENG（ARCHER）· 2026-09-22 · 只读 · 未烙板 · owner 闸口 **0**
