dataxcash/hw_ic_k2/pm_gate/artifacts/k2_v4/P6_execution/P6_OPEN_READINESS/K2_R419_L9_FULL_DRILL_VIA_CENSUS_HDI_CLASS_AND_MANUFACTURABILITY_READ_v1.md

# K2 · R419 —— l9 **全量钻孔/过孔普查 + HDI 孔类 + 制造性读数**（只读 · R270 项9 钻孔子项）

- **from** ENG·ARCHER（续接 · 应「按已批准计划推进当前阶段 · fail-closed」）· **to** 监理 · **owner 闸口 0**
- **authority**：**R270 §一 项9**（钻孔 · l9 重测）· **owner ③/⑤**（完工 = Excellon 含 **HDI 盲埋孔**）· 项13 孔系前置
- **边界**：只读文本解析。未出包 · 未烙板 · 未派工 · **未新增检查齿/判据**。受审板 l9 `77aaa63fe016b450`。

## 1. 普查（l9）
| 项 | 读数 |
|---|---|
| **过孔** | **732 支**，**全部钻 0.20mm / 盘 0.35mm**（单一孔类） |
| 孔类 | **through 279** · **blind(F/B↔inner) 363** · **buried(inner↔inner) 90** |
| 跨度 | F–In1 **171** · F–In2 **132** · In2–In5 **90** · In5–B **37** · F–In5 **19** · F–In4 **4** · F–B **279** |
| **焊盘孔** | 20 = **NPTH 4**（⌀3.2）+ **PTH 16**（⌀0.8） |
| **钻 token 合计** | **752** = 732 + 20 ⇒ **与 R406 之 752 吻合** ✔ |

**孔数更正（bookkeeping）**：历史记 l9「孔 **740**」= 740 个 `(via` token − **8 个 keepout 之 `(vias allowed)/(vias not_allowed)` 标志误计** ⇒ **真过孔 = 732**。

## 2. HDI 读数
- 结构含 **blind 363 + buried 90** ⇒ 与 **SPEC rev-55** 自述一致（『既有孔类 0.20/0.35 · **HDI 阶数≥2**』· 激光微孔类 0.10/0.25 因触 DRC 下限已弃用）。
- `criteria/jlc_hdi_capability.yaml`：`blind_buried.supported=false` + FAQ『blind/buried、HDI 属 advanced，**须 DFM review**』⇒ 与工艺冻结 **A**（owner ①）一致；**该项为须随单确认之工艺前置**（在册原文），非本维阈值。
- **『HDI 阶数』无在册机判口径 ⇒ 本件不判**（只报跨度结构 · **不自行立齿**）。

## 3. 三处**精确贴限**（零余量 · 非缺陷）
`钻 0.20 = min_through_hole 0.20` ｜ `盘 0.35 = min_via_diameter 0.35` ｜ `环宽 0.075 = min_annular_width 0.075`（JLC 能力页 0.15/0.25 更宽 ⇒ 通过）。登记供**量产风险**参考。

## 4. 诚实自检（**防假缺陷**）
发现候选：过孔**钻-钻 2D 投影重叠** 1 处（edge gap **−0.0813mm** @ (84.85,56.834) `PCIE_UP_OUT0_P_J2`(In5–B) ↔ (84.75,56.77) `PCIE_DN0_P`(F–In2)）。
**但不判为缺陷**：① **l8 与 l9 完全相同**（非搬迁引入）② **未被 DRC 报**（l8 error=0）③ 两孔**跨度不相交**（F/In1/In2 vs In5/In6/B ⇒ 不同叠层周期钻孔，物理不干涉）⇒ **2D 投影重叠非有效口径**。
⇒ 本件**不据此立判据**；若需 hole-to-hole 机判口径，**请监理钉死**（ENG 不自造）。披露以防后续误读。

## 5. 状态
- **R270 项9（钻孔）@l9 = 普查完成（读数级）**；出包（Excellon 含 HDI 盲埋孔）之孔系读数**已备**。
- **未豁免必修项仍 = R410/R411 之 59 error**（+`track_dangling` +4）⇒ **修复前不得出包**。
- **阶段门 fail-closed**：P4 未全绿 ⇒ 不出包 · 不下单 · 不越阶段（余阻见 R418 §4）。

—— ENG（ARCHER）· 2026-09-22 · 只读普查 · owner 闸口 0
