dataxcash/hw_ic_k2/pm_gate/artifacts/k2_v4/P6_execution/P6_OPEN_READINESS/K2_R320_IN5_JOINT_CONSTRUCTION_13OF16_GATE_PASS_v1.md

# K2 · R320 · ②-UP 单层 In5 **联合构造 13/16（过 `exact_gate`）** —— 附带质量缺陷如实标注

**件**：`K2_R320_IN5_JOINT_CONSTRUCTION_13OF16_GATE_PASS_v1.py`（只读 · 不改生成器 · 不写板）+ 同名 `.json`（约定A **`6ab8507e08e5eb69`**）
**据**：按已批准《K2 整体整改计划》§P4 推进（fail-closed）· 承 R319（卡点= A 侧锚群出线扇出）· 宪法第十三条
**锚**：冻结四源 **4/4 未动** · `criteria` rev=6 MATCH · 受审板 l8 **`7a5c89913d6e5d0a`** · **owner 闸口 0**

---

## 一、相对 R319 的**关键改动**（方法层，非参数扫描）

R319 之失败机制 = 最短路径**横扫本行其余锚**（10/12 未布 lane 之 A 锚被既有封套扫死）。
本件加入**静态协调项**：

> **他 lane 锚孔禁入**：每条 lane 之可行域 = 自由空间 **−（其余 15 条之 A/B 锚 ±0.435 盘）**
> ⇒ 强制「**锚处即刻离行**」；再按 **A.x 降序**（自东向西）序贯布，每条已布 lane 沿折线以 0.435 盘印硬排斥；
> 另加**有限 rip-up 修复**一轮。见证有效性**只由 `exact_gate` 判**。

| 轮次 | 布通 |
|---|---|
| `byAx_desc`（本件主策略） | **13/16** |
| `ripped_repair`（有限 rip-up） | 11/16 |
| **取优** | **13/16** |

## 二、闸读数（BEST = 13/16）

| 闸项 | 读数 | 判 |
|---|---|---|
| 车道互距违例 | **0**（最小 **0.4383** ≥ 0.435；最紧对 `UP_OUT4_N × UP_OUT4_P`） | ✅ |
| 障碍净距违例 | **0**（最小余量 0.0001mm） | ✅ |
| 端点偏差 | **0.0000** | ✅ |

**已布 13 条**：`T7_P T7_N T6_P T6_N T5_P T5_N T4_P T4_N T3_P T2_P T2_N T1_P T1_N`（坐标随件留档）
**未布 3 条**：`T3_N` · `T0_P` · `T0_N`

## 三、⚠ 质量缺陷（如实标注 · **不作交付见证**）

已布 13 条之走线长度差异极大：**`T1_N` = 314.23mm** vs `T1_P` = 92.20mm（同对 skew ≈ 222mm）——
系该 lane 在序贯后段被绕行所致。⇒ **等长 / SI 明显不达标** ⇒ 本件**只作几何可行性证据，不作交付见证、不作里程碑**。

## 四、判（不作过度主张）

| 支 | 判 |
|---|---|
| **(a) 可行见证** | **几何层部分成立：13/16 单层 In5 过闸**；但含超长绕行 ⇒ **不构成可交付见证** |
| **(b) 守恒级不可行证书** | **不成立**（R314 反证 `W_max=8 ⇒ U≤16`；R318 连通 16/16 · 容量 min 29≥16） |
| **残余（两项）** | ① 未布 **3** 条（A 侧锚群西端扇出）② **长度质量**（绕行 ⇒ 等长/SI） ⇒ 需**带长度约束**之联合求解 |

可施工性（宪法13）：已布 13 条 **能**（坐标 + 过闸）；**全板不能** ⇒ 全板图纸层缺图。**不动证明**：本件不搬任何对象。

## 五、复现

```bash
AppDir/usr/bin/python3.11 k2/tools/k2_p4_b2_board_in5_model_dump_v1.py k2/hw/k2_v4_8L.l8.kicad_pcb /tmp/opencode/model_l8.json
python3 K2_R320_IN5_JOINT_CONSTRUCTION_13OF16_GATE_PASS_v1.py /tmp/opencode/model_l8.json /tmp/opencode/r320.json
# 期望: byAx_desc 13/16（失败 T3_N/T0_P/T0_N）· 门 互距违例 0（最小 0.4383）· 净距违例 0 · 端点 0
```

## 六、边界

冻结四源不改 · `criteria/` 只读 · 未烙板 · 未派 WORKER · 未改生成器/SPEC/原理图 · 临时仅 `/tmp/opencode` · 未写 `.omo/supervision/**` · **阶段门 fail-closed 维持**。

—— ENG（ARCHER）· 2026-09-22 · k2 `54f7c52`（本件另提交）· owner 闸口 **0**
