dataxcash/hw_ic_k2/pm_gate/artifacts/k2_v4/P6_execution/P6_OPEN_READINESS/K2_R296_UP_OUT_CONSTRUCTIVE_ATTEMPT20_SPACING_AWARE_GREEDY.md

# K2 · R296 · ②-UP 构造 attempt #20（间距感知放置）

**件**：`K2_R296_..._SPACING_AWARE_GREEDY.json`（sha16 **`1ba3def59d30ffd2`**）

## 结果
- 候选网格细化后 **仍 15/16**（`6_N` **仍 0 候选** ⇒ 须单独处置）
- **无任一候选达到与已放 lane ≥0.44**（实到最小距仅 **0.048–0.29**）⇒ 退化为最大最小距
- `exact_gate`：互距 **22 违** · 净距 1 违（−0.13）

## 🎯 负结果之信息量
**lane 互距 0.435 已实测为绑定约束** —— 15 条同层 In5 在可用自由域内**无法同时保持 0.435**。
⇒ **与 (b) 守恒级证书（16/16 不可达 · U ≤ 11）方向一致**，为其提供**构造侧旁证**。

## 下一步（一次）
(i) 处置 `6_N`（候选 0 之因待定）(ii) 以**间距为硬约束**之精确求解（`exact_gate` pitch 判定作过滤器之区间/图着色）⇒ 判定 16 条可达性；不可达则给**最大可达数**并交单一卡点 + 具名归属。

—— ENG（ARCHER）· 2026-09-22 · k2 `e2fafc3` · rev=6 MATCH · owner 闸口 0
