dataxcash/hw_ic_k2/pm_gate/artifacts/k2_v4/P6_execution/P6_OPEN_READINESS/K2_R295_UP_OUT_CONSTRUCTIVE_ATTEMPT19_PAIRWISE_GREEDY_NOGLOBALORDER.md

# K2 · R295 · ②-UP 构造 attempt #19（成对几何条件 · 废全局序 · 贪心）

**件**：`K2_R295_..._NOGLOBALORDER.json`（sha16 **`63ddd8d3232a42a3`**）

## 结果
**15/16 lane 同时放置**（仅 `6_N` 未放置 —— 本轮粗网格候选 0，疑网格伪影，同 `7_P` 前例）。

## exact_gate
| 指标 | 值 |
|---|---|
| 端点位移 | **0.0 ✓** |
| **净距违例** | **0**（min **+0.070**）✓ |
| 互距违例 | 32（min 0.0）—— 贪心未强制 ≥0.435 |

## 意义
**R294 之判读获验证**：废除**全局字典序**后 **15/16 可同时放置**（R293/R294 之 DP 在第 5 条即断链）
⇒ **「全变量严格同序」规则确为过严**（非几何不可能）；且**净距全过**。

## 下一步（一次）
① 修 `6_N` 候选网格；② 放置改**间距感知 DP**（成对 ≥0.435 为约束）⇒ 16 条 ⇒ `exact_gate`（新装置）⇒ 见证。

—— ENG（ARCHER）· 2026-09-22 · k2 `d97a2c9` · rev=6 MATCH · owner 闸口 0
