dataxcash/hw_ic_k2/pm_gate/artifacts/k2_v4/P6_execution/P6_OPEN_READINESS/K2_R294_UP_OUT_CONSTRUCTIVE_ATTEMPT18_EXACT_DP_VERDICT_BLANKET_ORDER_OVERSTRICT.md

# K2 · R294 · ②-UP 构造 attempt #18 —— `cap` 截断判别（决定性）

**件**：`K2_R294_..._BLANKET_ORDER_OVERSTRICT.json`（sha16 **`95403ca1eb254c78`**）

## 判定：断链为**精确结果**
- lane 0（773 候选 < cap 3000）⇒ 其 Pareto 前沿**精确**（仅 2 态 ⇒ 0_N 候选被支配性极强）
- lane 1–3 之 `new` 规模 ≤2413 < cap ⇒ 前沿亦精确
- lane 4（`2_N` 3631 候选）逐一比对 2 前驱 ⇒ **`new` 为空为精确判定**

⇒ **在「全变量严格同序」规则下，前 5 条 `[0_N,0_P,1_N,1_P,2_N]` 无法联合放置**。

## 读法（倾向 ii）
(i) 真实联合约束；**(ii) 「全变量严格同序」规则过严** —— 正确条件是**成对几何条件**（仅当两 lane **扫掠区域相交**时才需分序），而非对全部 lane 对施全局字典序。

**旁证**：`(0_N, 0_P)` 在 A 序中相邻，但 B 锚分处**两端**（127.01 vs 141.22）、路径族亦异（西组两列 / 东组单列）⇒ 强制其 `c/Y/ye` 同序**无几何必然性**。

## 下一步（一次）
序约束改为**成对几何条件**（扫掠带相交 → 分序 + ≥0.435）⇒ 重作 DP 或逐段贪心+冲突消解 ⇒ 16 条 ⇒ `exact_gate`（新装置）⇒ 见证。

—— ENG（ARCHER）· 2026-09-22 · k2 `aca44eb` · rev=6 MATCH · owner 闸口 0
