dataxcash/hw_ic_k2/pm_gate/artifacts/k2_v4/P6_execution/P6_OPEN_READINESS/K2_R293_UP_OUT_CONSTRUCTIVE_ATTEMPT17_MIXED_FAMILY_EXACT_DP_REFINED.md

# K2 · R293 · ②-UP 构造 attempt #17（混合族精确联合 DP · 细化）

**件**：`K2_R293_..._EXACT_DP_REFINED.json`（sha16 **`30a634159445073f`**）

## 正面
**16/16 lane 候选域全部非空**（10²–10³）：`0_N 773 · 0_P 920 · 1_N 801 · 1_P 2413 · 2_N 3631 · 2_P 3051 · 3_N 3050 · 3_P 3964 · 4_N 4256 · 4_P 3632 · 5_N 3635 · 5_P 4309 · 6_N 4731 · 6_P 4149 · 7_N 4906 · 7_P 4911`。
⇒ **`7_P` 之零候选确系网格伪影（已证并修复）**。

## DP
lane 0→3 通过（**前端点恒为 2**）→ **lane 4 (`2_N`) 断链**。

## ⚠ 两种解释未判别（不得据此判卡点）
① **真实联合约束**（前 5 条不可联合）② **我实现之 `cap=3000` 截断**（对 ≥3000 候选之 lane 丢弃状态）所致**伪不可行**。

## 下一步（一次判别）
去掉 `cap` 截断（精确 Pareto 前沿 / 按 c 分桶之精确 DP）重跑同候选集 ⇒
① 仍断链 ⇒ 真实联合约束 ⇒ **单一卡点 + 具名归属**；② 通过 ⇒ 16 条 ⇒ `exact_gate` ⇒ 见证。

—— ENG（ARCHER）· 2026-09-22 · k2 `1315322` · rev=6 MATCH · owner 闸口 0
