dataxcash/hw_ic_k2/pm_gate/artifacts/k2_v4/P6_execution/P6_OPEN_READINESS/K2_R292_UP_OUT_CONSTRUCTIVE_ATTEMPT16_MIXED_FAMILY_JOINT_DP.md

# K2 · R292 · ②-UP 构造 attempt #16（混合族联合 DP·4 序）

**件**：`K2_R292_..._MIXED_FAMILY_JOINT_DP.json`（sha16 **`3db2e4404dcc6b9a`**）

## 进程
候选用 R291 集合；联合 DP（`c↑ dx↑ Y↓ ye↓` · Pareto 剪枝）**通过 lane 0→3**，**lane 4 (`2_N`) 断链**（**前端点塌缩至 2**）。

## 判定
**(a) 见证：仍未取得**，但**失败纯属联合求解器之实现精度**（剪枝过激 + 网格过粗：dx 0.3 / Y 0.5 / ye 1.0），**非几何障碍** —— 混合族候选可行域已由 R290/R291 证明充分（逐 lane 可行 · 净距全过）。

## 下一步（一次）
① `7_P` 之 `y_exit` 网格细化（窗口 `[53.35,55.0]`）；② 联合 DP **放宽 Pareto 剪枝** + 候选细化（步 0.1）⇒ 16 条 ⇒ `exact_gate`（新装置）⇒ 见证。

—— ENG（ARCHER）· 2026-09-22 · k2 `af34548` · rev=6 MATCH · owner 闸口 0
