dataxcash/hw_ic_k2/pm_gate/artifacts/k2_v4/P6_execution/P6_OPEN_READINESS/K2_R291_UP_OUT_CONSTRUCTIVE_ATTEMPT15_MIXED_FAMILY_JOINT_GREEDY.md

# K2 · R291 · ②-UP 构造 attempt #15（混合族：东单列 + 西两列）

**件**：`K2_R291_..._MIXED_FAMILY_JOINT_GREEDY.json`（sha16 **`88a5a4268d7037d3`**）

## 候选枚举（15/16 lane 非零）
`0_N 238 · 0_P 250 · 1_N 210 · 1_P 720 · 2_N 1080 · 2_P 900 · 3_N 900 · 3_P 1170 · 4_N 1260 · 4_P 1080 · 5_N 1080 · 5_P 1288 · 6_N 1410 · 6_P 1110 · 7_N 1470 · **7_P 0**`
⇒ `7_P` 零候选**系网格伪影**（其 `y_exit` 窗 `[53.35,55.0]` 而本轮步长 1.0）—— **不得据此判无解**。

## 贪心分配不足
贪心「取最小 c」仅得 **4/16** ⇒ **须作联合 DP**（R280/R284 已验证该类 DP 可行）。

## 已布 4 条之 exact_gate
**净距违例 = 0**（min **+0.070**）· 互距 1 违（0.35）· 端点位移 **0.0** ✓ ⇒ **混合族净距全过**。

## 下一步（一次）
**联合 DP**（东组 (c,dx,Y) + 西组 (c,dx,Y,y_exit)，四序 `c↑ dx↑ Y↓ ye↓`）⇒ 16 条 ⇒ `exact_gate`（新装置）⇒ 见证。

—— ENG（ARCHER）· 2026-09-22 · k2 `5cec373` · rev=6 MATCH · owner 闸口 0
