dataxcash/hw_ic_k2/pm_gate/artifacts/k2_v4/P6_execution/P6_OPEN_READINESS/K2_R290_UP_OUT_CONSTRUCTIVE_ATTEMPT14_WEST_TWO_COLUMN_FAMILY_PROBE.md

# K2 · R290 · ②-UP 构造 attempt #14（西组两列路形 · 逐 lane 探针）

**件**：`K2_R290_..._WEST_TWO_COLUMN_FAMILY_PROBE.json`（sha16 **`e69a3fe7c52a7558`**）

## 路形
`A → stub → 下潜至南层 Y → 东行至 gap 列 c → 北上至 y_exit（隔断以北）→ 西行至 x_B 列 → 北上至 B 锚`

## 结果（逐 lane 探针 · disk(0.04) 膨胀）
- `0_N`：**可行组合 105**（例 c=137.625 · dx=84.75 · Y=58.0 · y_exit=51.2）
- `7_P`：**可行组合 630**（例 c=136.32 · dx=92.5 · Y=58.0 · y_exit=54.2）

⇒ **西组两列路形逐 lane 可行** ⇒ **R288 之修正成立**（R286/R287 之「零候选」确系**单列路形族**所限，非无解）。

## 判定
**(a) 见证：仍未取得**（本轮仅逐 lane 探针）。但**已证明** ① 根因（西组需两列）② 修正有效。

## 下一步（一次联合实现）
东组 8 条单列候选 + 西组 8 条两列候选 ⇒ **联合 DP**（序约束 c↑ · dx↑ · Y↓ · 西组 y_exit↓）⇒ 生成 16 条折线 ⇒ `exact_gate`（新装置）⇒ 见证；若仍缺 ⇒ 单一卡点 + 具名归属（四字段）。

—— ENG（ARCHER）· 2026-09-22 · k2 `511b457` · rev=6 MATCH · owner 闸口 0
