dataxcash/hw_ic_k2/pm_gate/artifacts/k2_v4/P6_execution/P6_OPEN_READINESS/K2_R288_UP_OUT_CONSTRUCTIVE_ATTEMPT13_WEST_GROUP_BARRIER_ROOT_CAUSE.md

# K2 · R288 · ②-UP 构造 attempt #13 —— **零候选模式判别 = 西组 8 条**（真实结构性约束）

**件**：`K2_R288_..._WEST_GROUP_BARRIER_ROOT_CAUSE.json`（sha16 **`2c0758686df83f2c`**）

## 判别（细网格渐近）
cell 0.005 · disk(0.04) · Y 步 0.05 · dx 步 0.05：
- `0_N`(B.x=127.01)：**7 列 × 全部 Y ⇒ 可行 Y = 0**（仍全零）
- `0_P`(B.x=141.22)：c≥138.93 时可行 Y = **104–106**

⇒ **非网格 alias**。

## 根因（决定性）
**零候选 8 条 ≡ 8 条「西组」网**（B 锚 x<135.4：`7_P 6_N 5_P 4_N 3_P 2_N 1_P 0_N`）—— 与 R286/R287 零候选集合**完全同一**。

> **连接器通孔列（x≈133.2–136.3 · GND 17 枚）在北区构成东西向「隔断」**（R260 §F-2 在册真墙）
> ⇒ 「单列(gap c) + 末端西行」路形**无法**把西组 lane 送至 x≈127–131.65 的 B 锚（**对全部 c 与全部 y_B 皆阻挡**）。

## 判定
**真实结构性约束**（非 alias）—— 但**仅针对当前 5 段单列路形族**，**不是**「任何布线都不可能」。

## 修正（已指定）
**西组 8 条专用两列路形**（与 l8 实测同构）：`gap 列 → 隔断缺口处西行 → 在 x_B 列北行至 B 锚`；东组 8 条维持单列。⇒ 再作联合 DP（西组增一「西行高度」变量）⇒ `exact_gate`（新装置）⇒ 见证。
该扩展与 R269/R271/R272 之**西组/东区二分同源**，亦解释历史最好仅 12–14/16。

—— ENG（ARCHER）· 2026-09-22 · k2 `72cc272` · rev=6 MATCH · owner 闸口 0
