dataxcash/hw_ic_k2/pm_gate/artifacts/k2_v4/P6_execution/P6_OPEN_READINESS/K2_R287_UP_OUT_CONSTRUCTIVE_ATTEMPT12_PHYSICAL_LADDER_RECHECK.md

# K2 · R287 · ②-UP 构造 attempt #12（R286 零候选模式复核 · 物理列梯）

**件**：`K2_R287_..._PHYSICAL_LADDER_RECHECK.json`（sha16 **`12f427efcfb4e374`**）

## 复核结果
把 `c` 改为 **R277 实测物理列梯**（每 lane 在全高自由的列）后，**零候选模式与 R286 完全一致**：
零候选 = `OUT0_N, OUT1_P, OUT2_N, OUT3_P, OUT4_N, OUT5_P, OUT6_N, OUT7_P`（8/16）⇒ **排除 `c` 网格 alias**。

## ⚠ 仍存疑（红线警戒）
模式呈**精确 8/16 · 奇偶结构化**；在**逐 lane 独立**判定（无跨 lane 约束）中出现如此规则缺失，**仍疑 `dx`/`Y` 网格之奇偶 alias**。
**不得以此充卡点/证书**；**本会话未能判别**。

## 下一步（一次判别）
候选生成**完全连续化**（`dx`/`Y` 亦以**区间**给出，求可行域边界）⇒ ①非空 ⇒ 三维联合 DP ⇒ `exact_gate` ⇒ 见证；②确为空 ⇒ **真实结构性障碍**（每对 `i_N/i_P` 仅一条可布）⇒ 单一卡点 + 具名归属（四字段）。

—— ENG（ARCHER）· 2026-09-22 · k2 `1562249` · rev=6 MATCH · owner 闸口 0
