dataxcash/hw_ic_k2/pm_gate/artifacts/k2_v4/P6_execution/P6_OPEN_READINESS/K2_R286_UP_OUT_CONSTRUCTIVE_ATTEMPT11_THREE_VAR_CANDIDATE_SCAN.md

# K2 · R286 · ②-UP 构造 attempt #11（(c,dx,Y) 三维候选扫描）

**件**：`K2_R286_..._THREE_VAR_CANDIDATE_SCAN.json`（sha16 **`d6d44bdbbd3e25d8`**）

## 量测
每 lane 的 (c,dx,Y) 候选数（全 5 段 · disk(0.05) 膨胀）：
OUT0_N=0, OUT0_P=200, OUT1_N=282, OUT1_P=0, OUT2_N=0, OUT2_P=1000, OUT3_N=1091, OUT3_P=0, OUT4_N=0, OUT4_P=1178, OUT5_N=1175, OUT5_P=0, OUT6_N=0, OUT6_P=1098, OUT7_N=1472, OUT7_P=0

## 零候选 lane
`0_N · 1_P · 2_N · 3_P · 4_N · 5_P · 6_N · 7_P`（**恰 8/16 · 规则 N/P 交替**）

## ⚠ 警戒（红线）
该 8/16 规则模式**高度可疑为网格 alias 伪影**（c 网格 0.435 与 A 锚 y 两种取值之相位）——**不得以抽样伪影充卡点/证书**，须**连续/细化网格复核**。

## 下一步（一次）
连续化候选生成 ⇒ ①零候选消失 ⇒ 作 **(c,dx,Y) 三维联合 DP** ⇒ exact_gate ⇒ 见证；②零候选仍在且规则 ⇒ 为**真实结构性障碍**（每对 N/P 仅一条可布）⇒ 交**单一卡点 + 具名归属**（四字段）。

—— ENG（ARCHER）· 2026-09-22 · k2 `b440854` · rev=6 MATCH · owner 闸口 0
