dataxcash/hw_ic_k2/pm_gate/artifacts/k2_v4/P6_execution/P6_OPEN_READINESS/K2_R285_UP_OUT_CONSTRUCTIVE_ATTEMPT10_FIVE_SEGMENT_JOINT_DP.md

# K2 · R285 · ②-UP 构造 attempt #10（5 段完备联合 DP）

**件**：`K2_R285_..._FIVE_SEGMENT_JOINT_DP.json`（sha16 **`bb306780babc92ce`**）

## 结果：**不可行**
候选判定纳入**全部 5 段**后：`3_P`/`4_N` **候选 = 0**（无任何 (dx,Y) 使 5 段全自由）⇒ 11 条在此形状族 + **R277 固定列分配**下**无法联合实现**。

## 关键读数（本轮首次暴露「耦合」）
前 9 轮解决/排除的（列分配 · 南区层 · A 侧净距 · A 侧走廊）都是**分量**；本轮表明：**列 `c` 由独立贪心固定属「分解决策」**，与 (dx,Y) 存在**耦合**。

## 下一步（一次）
把 **`c` 纳入联合变量** ⇒ **(c,dx,Y) 三维联合 DP**（三序 · 全 5 段 disk 膨胀自由）⇒ 复跑 `exact_gate`（新装置）⇒ 见证；若三变量 DP 亦空 ⇒ 路径族扩展为**单调阶梯**，并交**单一卡点 + 具名归属**。

—— ENG（ARCHER）· 2026-09-22 · k2 `5f2d7f8` · rev=6 MATCH · owner 闸口 0
