dataxcash/hw_ic_k2/pm_gate/artifacts/k2_v4/P6_execution/P6_OPEN_READINESS/K2_R284_UP_OUT_CONSTRUCTIVE_ATTEMPT9_JOINT_2D_DP.md

# K2 · R284 · ②-UP 构造 attempt #9（(dx,Y) 二维联合精确 DP）

**件**：`K2_R284_..._JOINT_2D_DP.json`（sha16 **`6b521650d2bfa5dc`**）

## 正面结果
二维联合 DP（`dx` 序 + `Y` 序 同时施加，候选均在 **disk(0.05) 膨胀**上判定）**成功**：11 条 lane 全入解 ⇒ **A 侧走廊 + 南通道层的联合分配 = 精确可行**。

## 但 exact_gate 仍未过
互距 **17 违（min 0.0）** + 净距 **5 违（−0.18 vs GND）**。

## 根因（已定）
DP 的候选可行性**只覆盖 stub / 下潜 / 南横段 三段**，**未覆盖后两段**（北上段 `(c,Y)→(c,y_B)`、末端平移 `(c,y_B)→B`）。
⇒ 违例恰好落在**未纳入判定的段落**。

## 下一步（一次）
把**全部 5 段**纳入候选判定 ⇒ 二维序 DP ⇒ 复跑 `exact_gate`（新装置）⇒ 见证；若仍缺 ⇒ 单一卡点 + 具名归属（四字段）。

—— ENG（ARCHER）· 2026-09-22 · k2 `52991c2` · rev=6 MATCH · owner 闸口 0
