dataxcash/hw_ic_k2/pm_gate/artifacts/k2_v4/P6_execution/P6_OPEN_READINESS/K2_R279_UP_OUT_CONSTRUCTIVE_ATTEMPT5_JOINT_SOUTH_LAYER.md

# K2 · R279 · ②-UP 构造 attempt #5（南区同层联合分配）

**件**：`K2_R279_..._JOINT_SOUTH_LAYER.json`（sha16 **`a50366f93484ab07`**）

## 读数
- 单 lane 可行率 **11/11**（每条都存在可行的 (A 侧下潜走廊 dx, 南通道层 Y) 组合）
- **联合（全序嵌套）分配：1–2 / 11** ⇒ 强嵌套过严

## 判定
**(a) 见证：仍未取得**。卡点收敛到**唯一子问题**：
> **南区南通道层 Y 的「半序」联合分配** —— 11 条横段须落在互距 ≥0.435 且各自全程自由的层上；
> 仅当两 lane 横段 **x 跨度重叠**时才需分序（而非全序嵌套）。

**仍属构造/实现能力层**（非几何不可能）。

## 下一步
把该子问题精确建模为 **区间图着色/匹配**（半序约束），**一次**精确求解 ⇒ 复跑 `exact_gate`（新装置）⇒ 见证；若仍空 ⇒ 交**单一卡点 + 具名归属**（四字段）。

—— ENG（ARCHER）· 2026-09-22 · k2 `2c4e6e9` · rev=6 MATCH · owner 闸口 0
