dataxcash/hw_ic_k2/pm_gate/artifacts/k2_v4/P6_execution/P6_OPEN_READINESS/K2_R278_UP_OUT_CONSTRUCTIVE_ATTEMPT4_FULL11_ROUTING.md

# K2 · R278 · ②-UP 构造 attempt #4（11 条完整布线）

**件**：`K2_R278_..._FULL11_ROUTING.json`（sha16 **`c93be20934c6200a`**）

## 读数
- 已布 **6**（`no_route` 5）· **端点位移 0.0 ✓**
- **互距 4 违**（min 0.03 vs 需 0.435）· **净距 3 违**（min −0.08 vs 固定 GND 缝合孔）

## 判定
**(a) 见证：仍未取得**。瓶颈已精确到**同层联合布局**：①南通道层 Y 分配（相邻需 ≥0.435 且横向段全程自由）②A 侧下潜走廊选取（锚位附近垂直自由走廊稀缺）—— 二者须**联合**定案。**仍属构造/实现能力层**（非几何不可能）。

## 下一步
以**区间图联合分配**（南通道 16 条互距 ≥0.435 自由水平带 × 相容的下潜垂直带）定案 ⇒ 复跑 exact_gate（新装置）。

—— ENG（ARCHER）· 2026-09-22 · k2 `980f94f` · rev=6 MATCH · owner 闸口 0
