dataxcash/hw_ic_k2/pm_gate/artifacts/k2_v4/P6_execution/P6_OPEN_READINESS/K2_R277_UP_OUT_CONSTRUCTIVE_COLUMN_ALLOCATION_U11_CROSSCHECK.md

# K2 · R277 · ②-UP 构造 attempt #3（逐事件列分配）—— **独立复现 U=11**

**件**：`K2_R277_..._U11_CROSSCHECK.json`（sha16 **`fab6e0450cc98ce9`**）

## 结果
按单调（A 序）以 ≥0.435 间距对每 lane 的**自身攀升区间** `[y_B,56]` 可用列做贪心构造分配：**成功 11 / 16**。
未分配 = `5_N · 6_N · 6_P · 7_N · 7_P`。

## 意义
**构造路径独立复现 `U = 11`** —— 与 R274 之**精确枚举**（单调序 + 物理在场规则）**U=11 完全一致**
⇒ **(b) 守恒级不可行证书获「枚举 + 构造分配」双路印证**。

## 结构性读数
可用列数随 `y_B` 缩短而增：`0_N/0_P`(y_B≈43) **仅 7 列**；`7_N/7_P`(y_B=52.85) **15 列**
⇒ **南锚（长跨度）是真正的瓶颈**（其列须在更高区间也自由）。

## 下一步
① 完成 11 条之 A 侧下潜走廊 + B 锚嵌套降落 ⇒ 复跑 `exact_gate`（新装置）⇒ 见证；
② 监理依 #K2-132 §四 使 **EX-4 自裁生效** ⇒ ②-UP 验收 = **11/16 + EX-4**；③ R4 复闸。

—— ENG（ARCHER）· 2026-09-22 · k2 `d6b2375` · rev=6 MATCH · owner 闸口 0
