dataxcash/hw_ic_k2/pm_gate/artifacts/k2_v4/P6_execution/P6_OPEN_READINESS/K2_R276_UP_OUT_CONSTRUCTIVE_ATTEMPT2_DESIGNED_PLACEMENT.md

# K2 · R276 · ②-UP 构造 attempt #2（设计改进）· 绑定资源量出

**件**：`K2_R276_..._DESIGNED_PLACEMENT.json`（sha16 **`1008d6a0e464f381`**）

## 量出的绑定资源
**gap（东通道）全高自由列 = 仅 7 条**（y∈[43.0,55.6] 全高自由）。
⇒ 16 条车道**不能**各占一条全高列 ⇒ 必须**逐事件（按 y_B 区间）**分配列位 —— 与 R274 之**逐事件横截跨越容量**判定**同源印证**。

## exact_gate 读数（已布 4 条）
| 指标 | 值 |
|---|---|
| 净距违例 | **0**（min 0.005）|
| 端点位移 | **0.0 mm** |
| 互距违例 | 6（min gap 0.0 · **自碰**）|

## 判定
**(a) 见证：仍未取得**；但**几何质量已达标**（净距/端点），瓶颈已精确量化为**列位逐事件分配** ⇒ 与 R274 (b) 证书（16/16 不可达 · U≤11 于单调序）方向一致。

**下一步**：逐事件列分配 + B 锚嵌套降落 ⇒ 复跑 exact_gate（新装置 · 非同参）。

—— ENG（ARCHER）· 2026-09-22 · k2 `b7e99e8` · rev=6 MATCH · owner 闸口 0
