dataxcash/hw_ic_k2/pm_gate/artifacts/k2_v4/L3/mcio_feas_step2/ref/ballmap-04.png

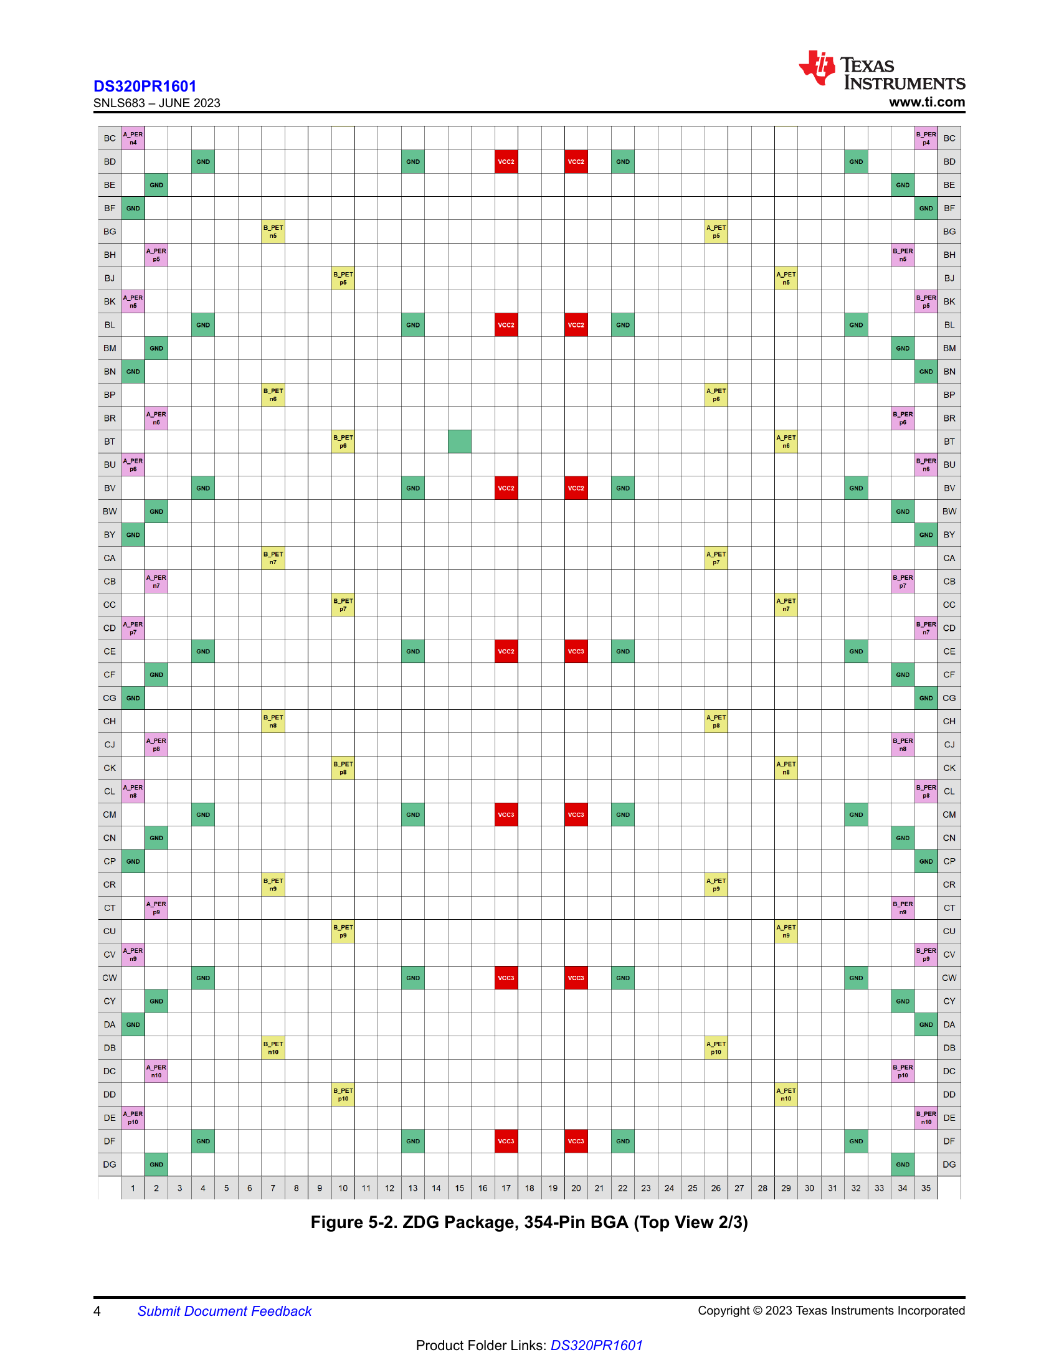
pm_gate/artifacts/k2_v4/L3/mcio_feas_step2/ref/ballmap-04.png
