dataxcash/hw_ic_k2/docs/K2-R664-PRODUCT-INVESTIGATION-RESULT.md

# K2 · R664 —— 《成品调研令》结果件（承 #K2-252 §四）：**免登录路径已证不可得设计源** ⇒ 依令停手报监

- 件：`K2_R664_PRODUCT_SOURCE_INVESTIGATION_v1.json` · hash16 **见件** · **零构造 · 零描线**
- 令中硬序：**先走 AI+WEB 免登录**；**确证不可得 ⇒ 携证据停手报监**；**不预授权**任何 owner 账号/令牌操作 ✓（本席**未**尝试任何登录/令牌动作）

## 一、免登录探活日志（全部带 HTTP/字节）
| 探测 | 结果 |
|---|---|
| 工程页 HTML | **HTTP 200 / 865,826 B** |
| 页内设计源直链（正则 `.epro/.epcb/.kicad*/gerber/*.zip`） | **仅 1 个 zip**：`…/attachments/4c382b1bb55d43858eb452ff0c7ef339.zip`（＝**预配置 SBR 固件件** 17,096 B）——**无原理图/PCB/Gerber 任何直链** |
| 页内 `/download/<id>?preview=false`（提取 13 条，host `fs-web-stream.jlc.com`） | **13/13 = HTTP 404**；页内该字段为 `selectedIconUrl`＝**图标/预览流**，非设计件 |
| 免登录可取集 | 工程页 ＋ **11 份 PDF**（数据手册/时钟/连接器/复位）＋ **SBR.zip** ＋ **146 张渲染图** —— 均 HTTP 200 |

## 二、结论（依令"确证不可得"）
- **可编辑设计源（原理图/PCB 源工程/Gerber）：免登录不可得（已证）**——三条独立证据：① 页面**全文无**设计源链接；② `REF-CASE-LIBRARY §A v2.1` 已机核登记「clone API 返 **104001 未认证**」；③ 唯一工程附件 zip 是**固件配置件**，非设计源。
- ⇒ 依令 **携证据停手报监**；**未做**任何 owner 账号/令牌操作。

## 三、对图纸层的直接后果（请监理一句话）
`#K2-252 §三.3(i)` 允许的"确定性构造式通道分配"**只能是"成品结构在本板上的落地"且每束须挂成品对照证据**。**无设计源**时，对照只能引用：**(a)** 渲染观察（R633：一连接器一束／长段直走／只在焊盘场浅 s 弯／换层在扇出处一次／束间只需不重叠）；**(b)** SBR 分组件（`532709807b07a16f`）作配置侧证据。**逐格照抄成品真实通道几何：无源不可得**。

## 四、请监理择一（一句话）
- **(α)** 受理"**渲染＋在册成品件**"为 (i) 分配器的对照基准（则可继续做"成品结构落地"的表）；或
- **(β)** 按 `#K2-252 §五 升级预案①` **升 owner 取可编辑源**（`LEGAL-ESCALATION: owner-system`）。

## 五、边界
冻结四源 **4/4 MATCH** · criteria 只读 · 在册件/判据/SPEC/原理图**一字未动** · **未派 WORKER** · **零描线** · 临时仅 `/tmp/opencode/ref252` · **P4 未归零 ⇒ 不导 Gerber/不进 P5/不碰下单**。 OWNER-ITEMS: 0

—— ENG（ARCHER）· 承 #K2-252 §四 · 2026-09-26 · 本件为 **R664**
