dataxcash/hw_ic_k2/pm_gate/artifacts/k2_v4/L2/measurements.md

# L2 测量基线 measurements（2026-08-13）

> 宪法第四章 ①测量：只记录实测值，无估计。全部数据来自 k2_v4.kicad_pcb 只读解析（tools_measure_l1.py）与文档实测。

## 板几何

- 板框：x∈[23,143]、y∈[33,71]，120×38mm（k2_v4 实测）
- 板厚 1.6mm，6 层（F.Cu/In1/In2/In3/In4/B.Cu）

## 高速链路器件焊盘盒（实测）

| 器件 | 中心 | 焊盘盒 x | 焊盘盒 y | 脚距 | 说明 |
|---|---|---|---|---|---|
| J2 SlimSAS x8 | (133.82, 53.70) | [132.65, 135.00] | [42.90, 64.50] | 0.6 | 74-pin, rot=0 |
| J3 MCIO 4X 38P | (59.50, 44.50) | [54.10, 64.90] | [43.25, 45.75] | 0.6 | rot=180 |
| J4 MCIO 4X 38P | (59.50, 62.70) | [54.10, 64.90] | [61.45, 63.95] | 0.6 | rot=0 |
| U3 DS160PR810 | (93.83, 44.70) | [88.83, 98.83] | [40.10, 49.30] | 0.4 | WQFN64, rot=0 |
| U4 DS160PR810 | (93.83, 62.70) | [88.83, 98.83] | [58.10, 67.30] | 0.4 | WQFN64, rot=180 |

## AC 电容墙（实测，L1 已裁决修正对角缺陷）

| 侧 | 数量 | x 范围 | y 范围 | L1 冻结要求 |
|---|---|---|---|---|
| MCIO 侧（现布局） | 19 | [75.83, 89.83] | [59.25, 66.05] | 修正：上下两带对称（上带 y≈44~47 / 下带 y≈60~66） |
| J2 侧（现布局） | 18 | [93.62, 127.83] | [42.90, 53.40] | 修正：上下两带对称 |

## 走廊净宽（实测计算）

- J2↔U 走廊：x∈[98.83, 132.65] 净宽 **33.82mm**，y∈[40.10, 64.50]
- U↔MCIO 走廊：x∈[64.90, 88.83] 净宽 **23.93mm**，y∈[40.10, 67.30]（上带 y∈[40.10,49.30]、下带 y∈[58.10,67.30]，中带被 U3/U4 热焊盘区域占用）
- U3↔U4 空隙：y∈[49.30, 58.10] 净高 **8.8mm**（电源去耦区）

## 低速/边带区

- U1 MCU @ (36.00, 52.00) LQFP48；U2 DCDC @ (33.00, 37.00) SOIC8；U5 @ (44.50,52.00)；E2 @ (44.00,60.00)
- 边带排针 x=26.5 列（J6/J9/J11/J12/J13）；电阻阵列 x∈[45.5,53.5]
- 电源去耦 MLCC_0603：C67/C68/C72 @ (91, 49/52/55)（U3/U4 之间空隙）、C73 @ (31,55)

## 版本

- v1.0（2026-08-13 测量基线，L2 G2.1 输入）
