dataxcash/hw_ic_k2/pm_gate/artifacts/k2_v4/P6_execution/P6_OPEN_READINESS/K2_R433_A_BRANCH_WINDOW_STEP1_REVERT_DONE_STEP2_CALIBRATED_v1.md

# K2 · R433 —— A 分支窗口：**Step 1 回退已完成** · Step 2 已开工（只读校准）

- **ts** 2026-09-23T18:06:59 · **from** ENG·ARCHER · **to** 监理 · **owner 闸口 0**
- **authority**：**#K2-147**（owner 裁定 A 之唯一执行令 · 勿再请示）· #K2-145 裁定①/④ · #K2-146 · R401 预登记口径
- **首动作**：已读 #K2-147（最新）· #K2-145 · #K2-146

## 0. 一句话
**Step 1（回退）已完成并推送**（k2 `2c5525b` · 门禁核『PCB 变更 1 项 ↔ SPEC 变更 1 项』）；**Step 2（一次求解）已开工**：闸管道端到端校准通过（端点偏差 **0.0000**）、自由槽位实测与 R260 逐值一致（**端口 7.60mm ⇒ 17 槽**）。

## 1. Step 1 · 回退（DONE · k2 `2c5525b` · push `0 0`）
| 项 | 内容 |
|---|---|
| 拆件 | 删 `hw/k2_v4_8L.l9.kicad_pcb`（`77aaa63f`） |
| 规范 | `SPEC_k2_v4.spec-rev-55.json` := rev-54 底（`f3a48b86`）+ **仅三处文字**（草案 `48933863ef621510`；量化值零改） |
| 指针 | `project.yaml::board_path` → `hw/k2_v4_8L.l8.kicad_pcb` |
| 声明回填 | 三处 `board_sha16` **由构造**回填为 l8 `7a5c89913d6e5d0a` |
| 指纹重锚 | 派生模型指纹 := **`f5865bdd6879723d`** = `canon16(model_l8.json)`；base 件 `c42731c4258ae691` |
| 门禁证据 | 『PCB 变更 1 项对应 SPEC 变更 1 项』· meta-gate + verify 3 项 PASS |
| 红线 | 冻结四源 **4/4 未动** · `criteria/` rev=6 未动 · 未改生成器/原理图 · 未派 WORKER |

> 落点说明：判令『规范指回 rev-54』按『**以 rev-54 为底**』落地 —— 若令 `spec_name` 停在 rev-54，则旧文字仍在效，违 #K2-145④ 之本旨。

## 2. Step 2 · 一次求解（**IN PROGRESS** · 尚未对真实实例求解）
**2a 闸管道校准**（把**在板既有** 16 网 In5 折线喂入在册 `exact_gate`）：
`n_lane_pitch_viol=1`（min 0.200 @ OUT0_N|OUT7_N）· `n_clearance_viol=2`（min −0.165 · 阻塞者 `PERSTA#` seg）· **`endpoint_max_dev_mm=0.0000`** · 障碍场 1072 段 / 347 孔 / 20 盘。
⇒ ① 管道**端到端可用**；② **基线读数证明本窗口确有必要**（既有板过不了闸）。

**2b 自由槽位结构**（只读栅格 · cell 0.03 · 同 main() 之 PAD_EXTRA）：
- 端口 y=56.5：自由 x = [134.25,134.55] + **[135.45, 143.05]（7.60mm）** ⇒ **17 槽 @0.435**（与 R260 F-4 逐值一致）
- 南通道 y=58.5 / 65.0：自由 x 10.05mm ⇒ 宽裕
- 东侧竖向 x=140.0 自由 y 43.95–67.95（24.0mm）
- x=136.0 纵向断裂 ⇒ 与 R260 F-2『连接器通孔列 x≈133.2–136.3』一致

## 3. 下一步（窗口内 · 一次给全）
1. **编码**：16 网 A→B · In5 单层 · 束间 **0.435 中心距** · 净距（`eff`+`HOLE_CLR`）为约束 ⇒ CP-SAT **一次求解**（依赖已就绪：`/tmp/opencode/r432venv` · ortools 9.15.6755 · R432 已验 SAT/UNSAT 双证书形式）
2. **验收**：R401 预登记口径（`n_lane_pitch_viol==0 ∧ n_clearance_viol==0 ∧ endpoint_max_dev_mm==0` · 全 16 条）
3. **两件交付**（缺一不收）：**图纸规格**（每网 （车道 / 层 / 过孔数））+ **求解证书**（SAT 模型件 或 UNSAT 证明）

## 4. 口径备注（如实）
- **车道集 = 16 网 `PCIE_UP_OUT*_J2`**：依 owner 裁定 A 文义 + R401『全 16 条』+ R260『16 车道/17 槽』（#K2-146『32 条线（16 对）』系含 DN 组之并集口径；本窗口以**在册验收口径 16 条**为准）。
- **0.435 = 中心距**（= DRC 0.335 + 余量 0.100 · #K2-143），与 `exact_gate` 内 `_seg_seg_batch`（中心线距）一致 ⇒ 不与对内 ≥0.175 冲突。
- **单层硬条件**：折线全 In5 · 0 换层 · 两端点 = 锚点（`endpoint_max_dev_mm==0`）。

## 5. 自检
Step 1 四处改动**同笔提交**（门禁已核）· 冻结四源 4/4 未动 · Step 2 仅只读校准（未启求解器于真实实例）· **未**把『管道校准通过』写成『已求解/已得证』· 未新造判据。

---
—— ENG（ARCHER）· 2026-09-23T18:06 · window in progress · owner 闸口 0 · sha16 `4c92237847bd5fb0`
