dataxcash/hw_ic_k2/docs/K2-BLOCKER-REPORT-aprime-evaluation-base-20260929.md

# 卡点报告 · 评价基钉死（#K2-399 §二 序步 1）＋ 连贯种子方案（序步 2，待跑）

- 授权：#K2-399 §二（**一窗 · 零考跑**）；本窗**零考跑 · 零板改**
- 件：`L2/EDA_ENG_EVALUATION_BASE_PINNING_v1.json`

## 一、试过什么（序步 1）

1. **机读声明**：闸（`mech_probe_moves`）探的是 **shadow→`gen_v5` 产出的 GEN 板**；链（`wipe_resolve_chain`）跑的是 **`hw/k2_v4_8L.l14.kicad_pcb`**——**按构造就是两个文件**，问题在**布局是否一致**。
2. **机核**（只读 pcbnew）：取闸的**基线 GEN 板**，逐焊盘比对 25 成员的**118 个 pad**：
   **0 个不同**（例：`C88.1 = [29.05,41.5]`、`J13.2 = [29.21,46.54]`，两板相同）。
   ⇒ **基线上两板一致** ⇒ **评价基在基线处是自洽的**（无需"删 shadow 探路"）。

## 二、为何不通（**自我更正**）

- R1096 我把「刚性移位导致 gen 拒写」解释为**"生成器自身布局的真铜重叠"**、并归因于**双板分歧** ⇒ **该归因不成立**（基线 118/118 一致）。
- **真因（未决 · 具名）**：`[S1 PAD_OVERLAP] C88/1（已移）↔ J13/2（未移）` 表明**刚性移位只被应用到了一部分条目** ⇒ 属 **`M-ENG-MOVE-APPLICATION-PARTIAL`**（`edit_placement_at` 改了 `pm_gate/project.yaml` 58 行，但生成器对 J13 的有效放置未变）。
- **补法（本窗登记 · 待建）**：闸在接受一次移位前，须**逐 ref 机核**「该 ref 的放置源确实变了」。

## 三、缺口在哪层

**评价基的「应用完整性」层**（不是容量/判据/闸；基线的双板一致性**已证实**）。

## 四、序步 2（连贯种子逐件推导 · §16 §3 四要素）——**待跑**

- ①**一句话死因**：独立假设的逐件族把 U1 排第 1、他人未动 ⇒ 出不了整簇解（R1094 保留项）；刚性族因**应用不完整**全 GEN_FAIL（本件）。
- ②**已证事实**：基线双板一致（118/118）；逐件 22/25；刚性 dy 0.5–11.0 全 GEN_FAIL；U1 系端点埋压（预检具名）。
- ③**修正后完整施工图**：**连贯种子（joint/coherent）**——**先**按 R1078 让位次序播种连接器（J13/J9/J12/J6…），**再**在同一 `accepted` 集上求簇件（U1/U2/U4/U5…）的**联合可行步**（同一次 `mech_probe_moves` 试探、逐 ref 验应用完整性）＋ 守恒核算（域内余量 vs 需重连量）。
- ④`buildability`：`relocation_listed`（放置已见证；铜由成品生成）。
- **子族定性**：连贯种子＝**登记内第三子族** ⇒ 属 §17.4「**换手段**」，非「同因重跑」（承 #K2-399 §二反空转硬闸：**本子族为本轮最后子族**）。

## 五、纪律

板面冻结 · 四源 4/4 · 判据表一毫米不改 · 禁 WORKER · **本窗零考跑** · 收尾脚本每收执一次。
