dataxcash/hw_ic_k2/docs/K2-BLOCKER-REPORT-testsuite-isolation-20260929.md

# 《卡点报告》· 三处框界补装 —— 卡在**测试台没有隔离**（基建层）

- 日期：2026-09-29 ｜ 提出者：ENG(ARCHER) ｜ 触发：监理停止令（红线：连续错误 2 次）
- 纪律：**即刻停手**（零运行 / 零改参 / 零改工具）；本窗实验**已回退**，树保持**全绿（69/69）**· 零考题跑。

## 一、人类工程师口径（按令三问）

**① 信号怎么走**：左边 25 件器件挪位后，把与那块地相交的铜**全部铲掉**，再**只在那块地内**用仓里的标准流程把它们画回来（这条已经通了：**框外零改动 ＋ 16 条高速线零触碰 ＋ 几何违规比基线还少 7**）。现在要把同一道"**地界**"补到**另外三道工序**上（剪断的那一刀、缝接的那一段、落板前的那一下），确保它们**也写不出界**。

**② 挡路的是什么**：**车间里的测试台是一张共用的大桌子**——所有检查在同一张桌子上做，**只要有一件活儿在桌上动了板子，整张桌子的测量器具就失准**，后面每一项检查都跟着报错，**而报错的地方离出事的活儿很远**（实测：新加的三处检查一放上去，先是 2 次连续红；把检查改成"只读代码"也还是红；**回退全部改动后立刻恢复 69/69 全绿**）。所以**现在补不进这三处检查**，不是因为检查难写，而是**台子没隔离**。

**③ 人类方案（大白话）**：**先把台子分开**——
（a）**凡是要动板子的活儿，一律搬到隔壁小间里做**（子进程），台子上只做读数；
（b）**在台子入口装一个警铃**：谁在台子上偷偷动板子，**当场具名报警**（免得下一个人再踩）；
（c）然后三处地界检查按「**新增开关、默认不改老行为**」的方式补上去（实测教训：**改老工序的早退/返回路径**就会把台子搞脏）。
台子修好、三处检查补齐、**全绿** ⇒ 才**申请**一次新考卷授权（**申请 ≠ 自己开跑**）。

## 二、试过什么（逐条 · 均为实测）

| # | 做法 | 结果 |
|---|---|---|
| 1 | 三处地界：①RIP 切点（`clip_iu` 已在 ∂R 上）②缝合 `--bound-rect` 透传到**正确工具**（已在 R1026 做）③**收尾落板前框外检查**（`apply_routes(bound_rect=…)` ＋ CLI 透传 ＋ 链内 refill 传界）＋ 三处回归件 | **红（第 1 次）**：用例在**同进程**改板 ⇒ 毒化 SWIG 态 ⇒ 后续读板用例级联失败 |
| 2 | 把三处回归件**全部改成只读代码级断言**（不碰板） | **仍红（第 2 次）**：肇因在**实现**（动 `apply_routes` 的早退/返回路径）而非用例 |
| 3 | **全部回退**（`git checkout` 三处实现 ＋ 测试） | **绿：69/69 PASS** ⇒ 肇因确证＝本窗改动路径 |

## 三、为何不通（根因）

**测试套件没有"每个用例一间小间"的隔离**：改板函数（`apply_routes`/`move_block`/`move_parts`）在**测试进程内**被调用即破坏 SWIG 类型态，
**后续所有读板用例级联失败**，而**失败点与肇因不同址** ⇒
（i）**#K2-380 §二 要求的"每道工序一个回归件"补不进去**；（ii）**动老工序的早退/返回路径**即触雷（实测第 2 次红灯）。

## 四、缺口在哪层

| 缺口 | 层 | 依据 |
|---|---|---|
| **测试台无隔离**（回归件改板必须走子进程；需入口哨兵） | **ENG 测试基建（资产层）** | 实测 3 条 → 回退即绿 |
| **三处工序的界未补**（RIP 切点／缝合透传／落笔前检查） | **ENG 工件层**（**被上一行阻塞**） | #K2-380 §二 |
| 判据本身 | **不动** | #K2-379「判卷表一毫米不改」 |

## 五、下一步（**一次实现** · 不试错）

1. **修台子**：套件入口加**哨兵**（用例内直调改板函数 ⇒ 立即具名失败）＋ 新回归件**一律经 `eda_eng.sh` 子进程**；
2. **补三处界**：一律「**新增可选参数、默认不改老行为**」＋ **子进程**回归件（RIP 切点／缝合透传／落笔前检查）；
3. **全绿** ⇒ **申请**一次新考卷授权（**申请 ≠ 自跑**）；获准后按九行 C1–C9 判卷。

## 六、机核（本件零运行）

冻结四源 **4/4**（`0bd52ed48e720b8c`／`a8ef3ea8ecff99d7`／`fb07d25ac426ff84`／`0a459839e15960b8`）· 双仓 0/0 · 套件 **69/69 PASS** · 树净 · 板面零改动。

LEGAL-ESCALATION: none
OWNER-ITEMS: 0

---

## 附录 · 缺陷登记（#K2-382 §二.1）

- **编号**：`M-ENG-TEST-STATE-ISOLATION`（**台架级** · 非引擎级）
- **现象**：回归用例在**测试进程内**调用改板函数 ⇒ pcbnew SWIG 类型态被一次性污染 ⇒ **同进程后续用例全体级联失败**（失败点离肇因很远）。
- **同根规则**：R964 已登记「Add/Remove 污染进程内 SWIG 状态 ⇒ 板操作必须走子进程」（本次红灯与该规则**同根**）。
- **处置（R1044 已实施）**：①入口哨兵（进程内改板 ⇒ 立即具名失败）②两个老惯犯用例改走子进程（`route --apply-batch` / 新增 `move-block`）③三道围栏以**增量参数**重上 ⇒ **71/71 PASS**。
- **关闭判据**：套件入口哨兵在册 ＋ 同类"进程内改板"回归件 **不可能通过**（已达成）；后续同类新增用例**零次级联**。
- **状态**：**已修（R1044）**；遗留 = 维护窗复核（无）。
