dataxcash/hw_ic_k2/docs/K2-R692-STREAM-SUBMODEL-CALIBRATION.md

# K2 · R692 —— #K2-259 三件交付：(a) 成品三问 · (b) 工具修法规格 · (c) 3 线子模型**分钟级 SAT 标定** ✓

- 件：`K2_R692_STREAM_SUBMODEL_v1.json` · hash16 **`a180c5871506bcdb`** · 生成器同交 · 日志 fail-loud · **61.3 s**
- 生产运行：**1**（(c) 的小例标定）；(a)(b) **零构造运行**

## (a) 成品三问（针对**被堵 3 线**的接近/出口注册）
| 三问 | 答 |
|---|---|
| ① 同类成品怎么走 | 同芯片 `PEX88096` 开源成品双卡（`REF-CASE-LIBRARY §A`）· 渲染实测（R633）：**一连接器一束 · 长段直走 · 只在焊盘场浅 s 弯 · 扇出处一次换层 · 束间只需不重叠**；且连接器为**成对/成排**（`2S1525`），扇出呈**镜像成组**（渲染 8c14b7d0 / 93aeb0d8 可见） |
| ② 可抄件在哪 | 渲染图 **146 张**（本席已读 18）· SBR 分组件 `532709807b07a16f` · 11 份 PDF；**证据等级＝渲染观察＋配置，非逐格源**（R664 机证源工程免登录不可得） |
| ③ 差异清单 | **直接套**：R633 三规矩（＝第四硬键）。**差异（被堵 3 线的注册）**：成品按**成组/镜像**注册接近与出口（一组一份几何，镜像复用）；本模型**逐线独立注册** ⇒ 建议把这 3 线的**接近/出口注册改为成组镜像式**（**方案层 L2**）——**待监理裁**，本席未自行改注册 |

## (b) 工具修法规格（写表先行 · 判据先行 · 零构造运行）
1. **流式域生成（核心修法）**：候选**边生成边判**——对每条新候选**先与"固定格集"求交**，**只保留存活者**，**永不物化全域**（本轮实测：296,798 条候选零内存爆炸）；
2. **前向检查 ＋ 冲突导向回跳**（位/集合双轨；MRV 变量序固定＋值序固定 ⇒ 确定性）；
3. **对称破缺**：成品为成组镜像 ⇒ 对**镜像对**内的两条线施加**字典序/镜像序**约束（只搜半边）⇒ 破指数爆炸之源；**禁**"加内存/加时间/换机器"；
4. **小例规模预估**（实测）：3 线子模型 = 生成 296,798 ／存活同数 ／ **求解 3 节点** ／ **61.3 s** ⇒ 分钟级达标 ✓；
5. **判据先行**：**(甲)** 3 线子模型分钟级 SAT 见证；**(乙)** 恰一次全模型（结转）⇒ 16/16 图 ‖ 守恒级（非流限）核；**禁**流限型二值入账。

## (c) (甲) 小例标定：**SAT 见证 ✓**（3 线子模型 · 13 固定）
| 项 | 机核 |
|---|---|
| 固定 13 | 其在册**声明链**格集 538 格（R613 值 ＋ R638 入口声明） |
| 流式生成 | `OUT5_P 15,545` · `OUT7_N 210,008` · `OUT7_P 71,245`（合计 **296,798**；**与固定 13 相撞 = 0**） |
| 求解 | **SAT（3 节点）· 61.3 s** |
| 见证 | 见件 `witness`：三线各自的 `{H, Xa, Rm, Xb, tail_layer, kind}`（两级下钻路径）· 两两格集不相交由求解器保证 |
| 日志/hash | `K2_R692_solve.log`（fail-loud）· `a180c5871506bcdb` |

**如实caveat（本席标注）**：固定 13 用的是**声明链**（R613/R638 声明），**非抽屉实画路径**；本轮**零相撞**说明该子模型的约束近乎不绑定 ⇒ 本 SAT **只证"工具修法生效（分钟级、零物化）"**，**不证**全模型可行。**(乙) 全模型结转**，由监理另窗释放。

## 边界
冻结四源 **4/4 MATCH** · criteria 只读 · 在册件**一字未动** · 未派 WORKER · **零描线** · **P4 未归零 ⇒ 不导 Gerber/不进 P5/不碰下单**。 OWNER-ITEMS: 0

—— ENG（ARCHER）· 承 #K2-259 · 2026-09-26 · 本件为 **R692**
