dataxcash/hw_ic_k2/docs/K2-R670-PREMISE-REV2-CALIBRATION-FAILED-MODEL-RELATIVITY.md

# K2 · R670 —— 前提修订 v2（出口带）**校准未过** ＋ **自纠：UNSAT 证书是"模型相对"的**

- 件：`K2_R670_PREMISE_REV2_ALLOCATION_v1.json` · hash16 **`0af9c528717fc694`** · 生成器同交 · 日志 `/tmp/opencode/r668/solve.log`（fail-loud）
- 修订 v2（#K2-255 §三.3a）：**把墙缺口出口注册为"缺口带"**（±2 行内可注册 · L2 · 非板改）
- **校准先行**（§三.3c）：在 **R668 的冲突对 `{OUT6_N, OUT7_P}`** 上必须出 **SAT 见证** ⇒ 机核结果 **`ok=False`（仍 UNSAT，5 节点）** ⇒ **修订 v2 未给路**

## 一、机核事实
| 项 | 字段 | 值 |
|---|---|---|
| 校准（冲突对） | `CALIB-SAT subset=[OUT6_N,OUT7_P]` | **ok=False**（**未过** ⇒ 依 §三.3 fail-closed，**不再报"修订成功"**） |
| 全模型 | `solve.ok` | **false（UNSAT）** |
| 核 | `certificate.unsat_core` | 同前：**`[OUT6_N, OUT7_P]`（size 2）** · `reverified_unsat_by_rerun=true` |
| 证据账更正（#K2-255 §三.6） | `execution_record` | **已改真**：`prior_window_solve_executions=4` · `prior_window_code_defect_aborts=3` · `classification={code_defect:3, parameter_only:0}`（与文档一致） |

## 二、**自纠（本席主动更正自家结论）**：该 UNSAT 证书是**模型相对**的
- 钉子机制（机核）：`OUT6_N` 的**下钻列 113 纵跨 rows 12…43**（其强制格集）；而**任何**墙缺口出口线的**接近段**（模型里＝沿出口行从下钻列走到 col 114）**必经 (113,其出口行)** ⇒ 与 `OUT6_N` 相撞。
- **但**：钉子只在**"单级下钻"**模型下成立。**在册就有"两级下钻"先例** —— **R580 律 / R603**（`OUT0_N = H=47 · Xa=117 · Rm=36 · Xb=116`）。⇒ 允许两级下钻时，`OUT6_N` **不必**占满 113 的整段纵带 ⇒ **钉子可能自行消失**。
- ⇒ **如实定性**：本席的 UNSAT 证书 = **"在（单级下钻 ＋ 单列贴墙）模型内不可行"**，**不是**"板上物理不可行"。**修正上一条回复的措辞**（该处过强）。

## 三、修订 v3（建议 · 在册先例，非自创 · 请监理一句话）
**把 R580/R603 的"两级下钻"登记为路由权利**（premise v3）：每线可用 `下钻Xa → 行Rm 横移 → 下钻Xb`（Rm 取在册自由行段边界）。
- 依据：**R580 律**（定尺表二分）· **R603**（两级先例）· **R601**（行段表）——**全在册**，非自研扩张；
- 校准先行（硬）：冲突对 `{OUT6_N, OUT7_P}` 必须 **SAT**（证明两级确实给路），**再**跑全模型**恰一次**。

## 四、请监理一句话
**(α')** 放行 **v3（两级下钻登记）＋ 小例标定 ＋ 恰一次全模型重跑**（承 #K2-255 §三.3 之 (β) 分支额度）；
**(β')** 或判为"须动注册几何本体"⇒ 按 #K2-254 §三.3 走距离判定（可能触升级边）。

## 五、边界
冻结四源 **4/4 MATCH** · criteria 只读 · 在册件/判据/SPEC/原理图**一字未动** · 未派 WORKER · **零描线** · **P4 未归零 ⇒ 不导 Gerber/不进 P5/不碰下单**。 OWNER-ITEMS: 0

—— ENG（ARCHER）· 承 #K2-255 §三.3 · 2026-09-26 · 本件为 **R670**
