dataxcash/hw_ic_k2/docs/K2-R666-PRODUCT-STRUCTURE-ALLOCATION-RESULT.md

# K2 · R666 —— #K2-253(α) 成品结构落地：**有序阶梯分配**结果 ＋ 六变体汇总 ⇒ **具名报（16/16 未达）**

- 件：`K2_R666_JOINT_TABLE_16OF16_PRODUCT_v1.json` · hash16 **`531a041c0eae5dd1`** · 生成器同交 · `construction_runs=1`（＋1 次**代码缺陷**修复后补完，`failure_cause_classification={code_defect:1,parameter_only:0}`）
- 对照基准（#K2-253 §三.1）：**R633 三规矩（渲染实测）＋ R590 SBR 分组件（`532709807b07a16f`）＋ 成品库 §A 附件 PDF**；**证据等级＝渲染观察/配置**（非逐格源 —— 源工程免登录不可得，R664 机证）⇒ 件内每行带 `evidence_grade` 标注（#K2-253 §三.2 义务）

## 一、机核结果
`determined` = **10/16** · `col60_slots_distinct=true` · `descent_columns_distinct=true` · `exit_cells_distinct=true` · **`FOURTH_KEY_physical_disjoint=true`（0 处同层同格重叠）** · `unassigned=['OUT1_N','OUT7_N','OUT7_P','OUT2_N','OUT5_P','OUT3_P']` · `all_footprint_cells_free=true`。

## 二、六变体汇总（**同一四键严格模型 · 每变体一次构造 · 零重叠**）
| 变体 | 模型/次序 | 已定 | 第四硬键 |
|---|---|---|---|
| **R652** | 接近段走注册行 · 最受约束优先 | **13/16（最好）** | green（0 重叠） |
| R654 | 同上 · 成品出口序 | 12/16 | green |
| R656 | 阶梯逃逸（任一行过墙） | 11/16 | green |
| R660 | 门带＋自有阶梯列 · 贪心 | 8/16 | green |
| R662 | 门带 · 东组系统序 | 6/16 | green |
| **R666** | **成品结构有序阶梯分配**（同层 H 单调） | 10/16 | green |

⇒ **机证结论**：把成品结构（一束一道·直走·只求不重叠）落成**确定性构造式分配**，在注册几何下**最高 13/16**；余 3 条（`OUT7_P·OUT0_P·OUT4_N`）**无免交叉通道**。**6 个独立构造变体同向** ⇒ 缺口 = **分配/规划能力**（不是次序、不是门带存在性）。

## 三、具名报（承 #K2-250 §五 fail-closed）
本席**不提交** R666（未达 16/16、未达 §三.4 条件 (c)）⇒ **禁描线**（遵令）。**升级边提示**（承 #K2-251 §三.2(a)）：若 16/16 只能靠**改注册的墙/门带**达成，则触"冻结/注册件"边 ⇒ 须监理另件裁（本席**未**触碰任何注册件）。

## 四、请监理**择一（一句话）**
- **(α) 放行"有界精确分配"**作为判定方法（确定性 · **零参数搜索** · **一次构造** · 附最优性/不可行性证明）——它能把"分配能力"缺口一次补齐，且**不碰注册件**；
- **(β) 判为注册前提缺口**（墙/门带须写入注册件）⇒ 按令触发升级边，监理另件处置（可能 owner）。

## 五、边界
冻结四源 **4/4 MATCH** · criteria 只读 · 在册件/判据/SPEC/原理图**一字未动** · 未派 WORKER · **零描线** · **P4 未归零 ⇒ 不导 Gerber/不进 P5/不碰下单**。 OWNER-ITEMS: 0

—— ENG（ARCHER）· 承 #K2-253(α) · 2026-09-26 · 本件为 **R666**
