dataxcash/hw_ic_k2/docs/K2-R638-HUMANPATH-ONE-PASS-RESULT.md

# K2 · R638 —— 遵停止令后的**一次实现**（Plan 已交：R637）· 二值结果

- 件：`K2_R638_HUMANPATH_ONESHOT_v1.{py,json}` · hash16 **`3351549ec9d19349`** · `construction_runs=1`（**一次 · 不试参 · 不重跑**）
- 派生自已入库的 `K2_R620_…ONESHOT_v1.py`；**唯一具名修正** = 把图纸**已声明**的入口换层节点写进作业单（R620 只在 `belt_layer==1` 时写、且只认 `DIVE_via`）。

## 一、结果（二值）
| 读数 | 值 |
|---|---|
| **`n_drawn`** | **13 / 16**（R620 为 11/16 ⇒ **＋2**） |
| 新画通 | **`OUT3_N` · `OUT5_N`**（入口换层声明补全后第 1 段即通 ⇒ R635 §F3 假设**证实**） |
| 具名受阻（3 条 · 各带机核位点） | 见下表 |
| 合并整图碰撞核对（#K2-238 §三.4 硬闸） | **N/A**（未达 16/16，**不得**以逐线读数充整板见证） |

## 二、3 条具名受阻（**不同源** · 机核位点）
| 线 | 受阻段 | 机核位点 | 缺口在哪层 | 对应杠杆 |
|---|---|---|---|---|
| `OUT0_P` | 第 8 段（末段） | 出口格 `(127,36)` → B 端子；该格**不是 via-legal**，而 B 腿在 layer 0 | **图纸层（出口格位置）** | 出口格重指派（**(1a) 已预授权**） |
| `OUT6_N` | **第 7 段** | `(121,47)@L0 → (122,47)@L0` = **墙东纵取列 122 在第 47 行被占 1 格** | **图纸层（走廊列/腰带行选择）** | 换墙东列 `Xe`（120–135，F3 机核可用）或换腰带行 `H`（R601 全幅行） |
| `OUT7_P` | 第 3 段 | `(61,41) → (61,20)` = col 61 纵取不通 | **图纸层（走廊列选择）** | 换列/两段（联合表 V6 的 `H=40/Xe=122` 即为此） |

> 注：`OUT6_N` **已越过第 1 段**（入口声明生效），残余卡点只是**一格**——与 R632 报的"出口候选 = ∅"完全无关。

## 三、与"停止令/纪律"的关系
- 本窗**只跑这一次**（`construction_runs=1`）· **未改参搜索** · **未逐条替换** · **未重跑**。
- 该次实现**没有**做任何"松一档再试"：入口换层声明是**照图纸抄**（节点 `619/944/1139` 均为在册 SPEC 自带），出口 `≥2` 早已由 #K2-242 §三.4(1a) 撤销。
- 受阻三条**全部只读具名上报**，**未**在过去那一轮里再试一次。

## 四、下一步（等监理裁定 · 不自行续版）
`OUT6_N` / `OUT7_P` 两条**同族**（墙东列 `Xe` × 腰带行 `H`）——正是 R629 §V6 结构；`OUT0_P` 一条用已预授权的出口重指派。⇒ 建议下一窗**一次**把这三条一起定死 → **一次**全图重描 → **合并核对** → 16/16 或具名 finding。**不逐条、不改参重跑。**

## 五、边界
冻结四源 **4/4 MATCH** · 在册件/判据/生成器/SPEC/原理图一字未动（本件为**新窗口件**，非改原件）· 未派 WORKER · 临时仅 `/tmp/opencode/r638` · **P4 未归零 ⇒ 不导 Gerber/不进 P5/不碰下单**。 OWNER-ITEMS: 0

—— ENG（ARCHER）· 承**监理停止令** · 2026-09-26 · 本件为 **R638**
