dataxcash/hw_ic_k2/docs/K2-R578-DIMENSION-TABLE-RESULT.md

# K2 · R578（#K2-225 定尺窗）—— **逐线定尺容量表**（③′ 强制项）：东组 8/8 PASS · **西组 8/8 FAIL（数字具名）**

- 件：`K2_R578_DIMENSION_TABLE_v1.{py,json}`（**只读定尺** · 零构造 · 零描线 · 零试参）· hash16 **`3032c99549665ef3`**
- 规则（**推导，非试参**）：`H` = 本线腰带行（S2）；**需求跨度** = 纵腿 `H-1 → Y+1` 的行数；**可用宽度** = 层 0 上 cols 61–113 中**最大连续自由行段**。

## 一、定尺读数（16/16 逐线）

| 组 | 线 | 需求跨度 | 可用宽度 | 余量 | 判 |
|---|---|---|---|---|---|
| 东 | OUT0_P/OUT1_N/OUT2_P/OUT3_N/OUT4_P/OUT5_N/OUT7_N | **22** | **22** | **0** | **PASS** |
| 东 | OUT6_P | 16 | 16 | 0 | **PASS** |
| 西 | OUT0_N | **51** | 27 | **−24** | **FAIL** |
| 西 | OUT1_P | 47 | 24 | −23 | **FAIL** |
| 西 | OUT2_N | 46 | 24 | −22 | **FAIL** |
| 西 | OUT3_P | 43 | 24 | −19 | **FAIL** |
| 西 | OUT4_N | 45 | 24 | −21 | **FAIL** |
| 西 | OUT5_P | 34 | 24 | −10 | **FAIL** |
| 西 | OUT6_N | 33 | 24 | −9 | **FAIL** |
| 西 | OUT7_P | 30 | 24 | −6 | **FAIL** |

**汇总：PASS 8 / FAIL 8。**

## 二、结论（二值·甲 · 具名诊断）

1. **东组定尺达标**（需求 22 = 可用 22，余量 0）⇒ 其**纵腿单列可行**；东组尾段路线**定尺通过**。
2. **西组定尺不达标**（需求 30–51 > 可用 ≤24，余量 −6…−24）⇒ **"一列纵取到底"在尺寸上不可能**（**这是图纸尺寸问题，不是施工问题**）；
   必须**把跨度分段（多级阶梯）**，且**该多级结构的逐段定尺尚未给出**（本窗只完成单列口径）。
3. **不是不可行**：R569 已证西组代表线尾段整条画通（190 格/0 孔）⇒ **不出乙**。

## 三、下一步（唯一路径 · 待放行）

为**西组**给出**分段定尺表**（每段：需求跨度 vs 该段可用宽度，机核 `可用 ≥ 需求`，**段数/段点由规则推导**：按可用自由段长度贪心切分，禁试参）→ 与东组表合并成 **16/16 定尺容量表** → 干跑自检 `fails=0`（R569 两线）→ **一次**融合出图 → `exact_gate` → 入库报 hash ＋ `buildability`；FAIL ⇒ 仍只准二值。

## 四、边界

冻结四源 4/4 MATCH · 在册件/判据/生成器/SPEC/原理图一字未动 · 未派 WORKER · 正式产物非 `/tmp` · 两仓已提交；
**P4 未归零 ⇒ 不导 Gerber · 不进 P5 · 不碰下单**。 OWNER-ITEMS: 0

—— ENG（ARCHER）· 2026-09-25 · 承 #K2-225
