dataxcash/hw_ic_k2/docs/K2-R576-CORRIDOR-TAIL-RESULT.md

# K2 · R576（#K2-223 融合窗·4）—— 尾段"声明廊道"路线：**16/16 廊道已生成**；本窗运行因我方控制流缺陷中止

- 件：`K2_R576_CORRIDOR_TAIL_ONESHOT_v1.{py,json}` · hash16 **`fc99095916f44269`**（末次运行）
- **未描线**；**停手报监**（二值·甲）。

## 一、本窗机核读数

1. **廊道路线成立（结构性收获）**：首轮运行 **16/16 线全部生成"尾段声明廊道"**（每线 6–8 个锚点，锚点间距 ≤20 格，
   廊道 = 锚点间轴对齐矩形 ±6 ⇒ **给居中填充器留出绕障余量**）。这解决了 R572–R575 的"一条行/一条列硬贯通"死结。
2. **锚点合法性**：首轮有若干锚点落在**非法格**（如 `(110,36)`、`(106,17)`）⇒ 已加 **±5 格内吸附**（仍在廊道带内）。
3. **本窗中止原因（我方缺陷 · 工具类）**：补丁把"无解则报诊断"的守卫**误插进 H 循环体内**（`continue` 作用域错），
   致记录/计数错乱并中止 ⇒ **本窗结果不作数**（fail-loud，未描线、未改任何参数）。
4. **未验证项**：廊道内填充（`draw_declared` 单遍硬预留）与 `exact_gate` **本窗未执行**。

## 二、下一步（#K2-223 §三.4④：工具缺陷修正 ＋ 同窗补跑）

修正守卫作用域（一行）→ **一次**融合运行：廊道锚点吸附 → 三岗/容量 → **一次描线（廊道内硬预留填充）**
→ `exact_gate`/`gate_vias`/端点/≤2 对孔 → 入库报 hash；FAIL ⇒ 仍只准二值。

## 三、边界

冻结四源 4/4 MATCH · 在册件/判据/生成器/SPEC/原理图一字未动 · 未派 WORKER · 正式产物非 `/tmp` · 两仓已提交；
**P4 未归零 ⇒ 不导 Gerber · 不进 P5 · 不碰下单**。 OWNER-ITEMS: 0

—— ENG（ARCHER）· 2026-09-25 · 承 #K2-223
