dataxcash/hw_ic_k2/docs/K2-R573-COUPLED-RESULT-EAST-OK-WEST-NEEDS-CORRIDOR.md

# K2 · R573（#K2-223 融合窗·第 2 次）—— **H 耦合成功用于东组；西组需"声明廊道"**（二值·甲）

- 件：`K2_R573_COUPLED_H_TAIL_ONESHOT_v1.{py,json}` · hash16 **`bff77ab4b13b2f5b`** · 同命令运行 1 次（零改参）
- 本窗按 #K2-223 §四做**耦合修复**：**H 与尾段在同一行上联合取用**（`d_i…60…X` 同一行全合法）＋ 西组"两段阶梯"兜底 → 一次描线。

## 一、机核读数

| 判据 | 读数 |
|---|---|
| 中段+尾段耦合指派 | **1/16**（`OUT1_N`：H=59 · X=120 · 尾段 87 格 ⇒ **东组单段法在"H 取全幅行"时成立**） |
| 其余 15 条 | 耗尽 `coupled H/X tail`（具名：lane / Y / east）——**西组 8 条全数未过**、东组另有若干未过 |
| 描线 | **未执行**（未全绿 ⇒ 停手） |

## 二、结论（精确 · 方案层）

1. **正面收获（新增机证律）**：**东组**只要 **H 取自"全幅行"**（F2 的行集），"同一行横贯 + 单段竖直 + 出口行横取"即可分配成功 ⇒ **H 耦合 = 东组的正确写法**（本窗首次得到 1 条完整候选表）。
2. **西组（8 条）**：`(H, X)` 单段 与 `(H, 36, X2)` 两段阶梯**均不成立** ⇒ 西组需要**更丰富的结构**（多级阶梯/声明廊道），**不是**"再调一次列号"。
3. **不是不可行**：R569 已机证 **西组代表线 OUT0_N 的尾段能整条画通（190 节点 · 0 对孔）** ⇒ 存在可行走法，缺的是**有序分配结构** ⇒ **不构成守恒级不可行证书（乙）**。

## 三、下一步（推荐结构 · 仍按 #K2-223：融合 · 二值 · 一次）

对**西组**改为**"声明廊道 + 廊道内一次定序填充"**（与 R550 入口前缀同型、已验证 `fails=0` 的写法）：
`s4 西组 = 声明 2–3 张轴对齐矩形廊道（行 H → 行 36 → 行 exit_row 三段，列区间由 take-and-register 在各段**互斥**取用）
→ 廊道内单遍最短路填充（硬预留）→ 与中段/东组并入同一张表 → 一次描线 → exact_gate`。
**不猜模板**：廊道的**列区间**由 F1–F5 + 本窗读数**直接给出**（西组可用列必须逐段取，段间用出口行/闸行 36 横向联接）。

## 四、边界

冻结四源 4/4 MATCH · 在册件/判据/生成器/SPEC/原理图一字未动 · 未派 WORKER · 正式产物非 `/tmp` · 两仓已提交；
**P4 未归零 ⇒ 不导 Gerber · 不进 P5 · 不碰下单**。

OWNER-ITEMS: 0

—— ENG（ARCHER）· 2026-09-25 · 承 #K2-223
