dataxcash/hw_ic_k2/docs/K2-R569-RESULT-TAIL-NEEDS-ALLOCATION.md

# K2 · R569 —— 前提 v3（S2）第三次一次出图：**三岗+单位闸全绿，2/16 整线画通，尾段在共层竞争上受阻**

- 依据：#K2-222 §四/§五③ · 件 `K2_R569_PREMISE_V3_ONESHOT_v3.{py,json}`（**新命令 1 次 · 单遍 · 零求解器 · 零回溯 · 零改参重跑**）· hash16 = `6c5117da5d9e1fb5`
- 相对 R568 的**唯一**改动：wp 传**位置号**（一行 · `M-ENG-UNIT-LABEL` 第二次）+ 新增**单位闸**（fail-loud：wp 的 `L*NID+nd` 必须 `< TERM_BASE`）。**前提 v3 未动、参数未改**。

## 一、机核读数（本窗一次执行）

| 判据 | 读数 |
|---|---|
| S2 指派 | **16/16**（L0 行 59–49 互异；L1 行 59/58/57/56/53 互异） |
| **单位闸**（新增 · fail-loud） | **PASS（1191 个 wp 全检）** |
| 三岗 (i)域完备 /(ii)在册弧 /(iii)同层互斥 /(iv)容量 | **全 PASS** |
| **描线（一次）** | **OUT0_N 整线 190 节点 · 0 孔**；**OUT0_P 整线 199 节点 · 2 孔** ⇒ **2/16 已画通（层 0 与层 1 各一例）** |
| 其后 | **OUT1_N 在尾段受阻**（具名诊断见 §二）；**停手、未重试** |

## 二、具名诊断（尾段 · 承 #K2-222 §五③）

- 断点：`lane=PCIE_UP_OUT1_N_J2, k=84, from=3958 [col60,row58] @L0 → to=7511 [col115,row36] @L0`，`band=null`，**已占格 318**。
- 事实：OUT1_N 的**尾段（col60 → exit）**在层 0 上被 **OUT0_N 已声明的尾段（硬预留）**切断——
  OUT0_N 的尾段是一条**自由形态长蛇**（(60,59)→(114,7)→B），把层 0 场区切成两块，致后者不可达。
- **归属（按 §五③ 判定）**：**方案层（前提缺"尾段分配律"）**，**不是**施工层现场找路能解决的。
  S4 目前只声明了**两个端点**（col60 槽位、exit），**没有给尾段指定"谁走哪条道/哪一段"的排班** ⇒ 11 条同层线的尾段互相争抢同一片场区。

## 三、结论（一句话）

**中段（S2）已证可画（2/16 整线通 · 含尾段各一例）；尾段（S4）缺的是"排班（分配律）"，不是"空间"。**
尾段必须像入口/腰带那样**先写表**：给每线指定**确定的尾段廊道**（谁从 col60 哪一行 → 走哪条纵向列 → 在哪一行过墙 → 落到自己的 exit/pad），
并给出**容量核算**（层 0/层 1 各自可用纵向列数 ≥ 该层线数）。这是**方案层前提 v4**的活，**不得**在施工层以"自由找路"顶替。

## 四、请求（具名报监 · 不越 L2 自裁）

- **请求另批一窗**：落**前提 v4（S4 尾段分配律）**版本 bump 新件（含证明标签）→ 三岗+容量重跑 → **一次完整出图（16/16 含尾段）** → `exact_gate`/`gate_vias`/端点/≤2 对孔 → 入库报 hash；FAIL ⇒ 仍只落具名诊断。
- 本窗构造 **1 次**、**未改参重跑**；**未**在施工层改任何参数来"绕过"阻断。

## 五、边界

冻结四源 4/4 MATCH · 在册件/判据/生成器/SPEC/原理图一字未动 · 未派 WORKER · 正式产物非 `/tmp` · 两仓已提交；
**P4 未归零 ⇒ 不导 Gerber · 不进 P5 · 不碰下单**。

OWNER-ITEMS: 0

—— ENG（ARCHER）· 2026-09-25 · 承 #K2-222
