dataxcash/hw_ic_k2/docs/K2-R567-RESULT-THREE-GATE-CHECKER-DEFECT.md

# K2 · R567 —— 前提 v3（S2）一次完整出图：**三岗唯一 FAIL = 我方检查器的过严规则**（诊断件 · 未重试）

- 依据：#K2-222 §四（批准：前提 v3 → 三岗 → 一次完整出图（含尾段）；**FAIL ⇒ 只落具名诊断，禁同窗重试**）
- 件：`K2_R567_PREMISE_V3_ONESHOT_v1.{py,json}`（**新命令 · 单遍 · 零求解器 · 零回溯 · 零改参重跑**）· hash16 = `5b561f5d278df4af`
- 前提件：`k2/docs/K2-R567-PREMISE-REVISION-v3.md`（**版本 bump 新件**，含 v2 errata E1–E4 + 证明标签）

## 一、机核读数（本窗一次执行）

| 判据 | 读数 | 结论 |
|---|---|---|
| 指派（S2：`d↑ / H↓ / col60 行 = H`） | **16/16 线全部分配成功**（L0：11/11 行 **59–49** 互异；L1：5/5 行 59/58/57/56/53 互异） | **容量/分配 PASS** |
| `(i)` 域完备（逐格合法） | **PASS**（n=0） | ✓ |
| `(ii)` 相邻在册弧 | **弧判据本身 = 0 失败**（即：**声明线的每一步都是在册弧**） | ✓ |
| `(ii-b)` 我方附加的「轴对齐」附加规则 | **FAIL（n=2）**：OUT6_P 口袋前缀中 `(21,33)→(22,34)`、`(23,34)→(24,33)` 为**在册对角弧** | ✗ **我方过严** |
| `(iii)` 同层两两互斥 | **PASS**（n=0） | ✓ |
| `(iv)` 容量（同行不重复） | **PASS**（L0/L1 `rows_distinct=true`） | ✓ |
| 描线 | **未执行**（三岗未全绿 ⇒ 按 #K2-222 §四 **未描线、未重试**） | 诊断件 |
| `buildability` | `no_witness`（未见证书 ⇒ 按第十三条**不得**认证可行） | — |

## 二、根因（一句话 · 归属：ENG 检查器 · 非前提、非施工）

我为了"格互斥 ⇒ 几何互斥"这条推理**自行附加**了"声明步必须轴对齐"的规则；
而 `R550` 口袋前缀（**已机核件 · fails=0**）里有 **2 步在册对角弧** ⇒ 我的附加规则把它们误判为缺陷，
**在描线前把整条链拦下**。**声明线本身无缺陷**：弧判据 0 失败、格合法 0 失败、互斥 0 失败。

## 三、结论与归属

- **前提 v3（S2）本身：无缺陷证据**——16/16 指派、容量正余量、三岗中 (i)/(iii)/(iv) 全 PASS、弧判据 0 失败。
- **本窗 FAIL 的唯一原因 = `M-ENG-CHECKER-OVERSTRICT`（我方检查器附加规则）**；
  修法**一行**：删去"轴对齐"附加规则，弧判据 = **在册弧**（与 R548b/R550 的口径一致，R550 入口件即以此口径核过 `fails=0`）。
  真实几何越界由**在册闸 `exact_gate`（逐层净距）**兜底，不靠"轴对齐"这条体外规则。

## 四、如实披露（未验证项 · 承 #K2-222 §五③）

**尾段（S4：`col60 → exit → pad_run → B`）本窗仍未验证**：尾段已写入同一次链、纳入同一次描线调用，
但**三岗在描线前 FAIL ⇒ 该次描线未执行** ⇒ 尾段**仍无通例**。**不得**把本件读作"尾段可行"。

## 五、请求（不越 L2 自裁 · 具名报监）

- 本件属**检查器缺陷**（非改参、非前提、非施工）：请求**另批一窗**，按 §三 的"一行修正"重跑同一 S2 链
  （前提 v3 不变、不新增前提、不改任何参数），**一次出图（含尾段）**并报 hash；
- 若监理认定该一行修正仍属"同窗重试"，请**裁示**；本窗按令**已停手**。

## 六、边界

冻结四源 4/4 MATCH · 判据只读 · 未改生成器/SPEC/原理图 · 未派 WORKER · 正式产物非 `/tmp` · 两仓已提交；
**P4 未归零 ⇒ 不导 Gerber · 不进 P5 · 不碰下单**。

OWNER-ITEMS: 0

—— ENG（ARCHER）· 2026-09-25 · 承 #K2-222
