dataxcash/hw_ic_k2/docs/K2-R562-JOINT-V3-RESULT.md

# K2 · R562 —— 重发层安排（8/8）后联合 v3 核验：**FAIL · 诊断（未描线、未重跑）**

- 件：`K2_R562_JOINT_V3_ONE_SHOT_v1.{py,json}`（**新命令 1 次**）· 日志 `/tmp/opencode/r562/oneshot.log`
- 本窗动作：按 R561 结论执行 **L2 自裁——重发 COMB 层安排为 8/8**（`layL` 按 d 序前 8 线 → L0、其余 → L1），
  并把腰带行改 `R_i = 59 - i`（南场深度 ≤59）；随后联合核验。**结果 FAIL ⇒ 未描线**（按 #K2-220 §四只落诊断）。

## 一、机核读数（FAIL）

| 判据 | 读数 | 机核归因 |
|---|---|---|
| `(i)` 格合法 | FAIL（132） | 例：`(45,34)/(52..56,34)` 对 OUT1_P 非法 ⇒ **声明线撞在册障碍**：我用的"行/列数字"是凭几何猜的，**没有逐格取自 `_nok` 自由格图** |
| `(ii)` 相邻在册弧 | FAIL（1957） | 同上（格非法 ⇒ 弧必缺） |
| 同层两两互斥 | FAIL（56 对） | 例 `(2,35)…(2,40)`（42 格）：**层重发后，两线的下钻列都落在 col 2** ⇒ **下钻列 `d` 必须按新层划分重新指派**（旧 d 表是按旧 11/5 划分配的） |

## 二、根因（一句话）

**表的每一格都必须从在册自由格图（`_nok`／lane graph）里"取"出来，而不是先拍行/列号再核。**
R562 的两处 FAIL 都源于此：① 行/列号与在册障碍不符；② 层划分变了而 d 表未随之重指派（出现同层同列）。

## 三、下一步（**唯一一次实现** · 同一命令内完成）

`按新 8/8 层划分，逐层按 π 序、**从"当前未被同层占用的在册自由格"里逐格取**（下钻列 d↑ / 腰带行 R↓≤59 / 断面点 (c_i,s_i) / 北巴士行 b↓ / 东列 E↓ / col60 行 t↑）
 → 同一核验器（格合法 + 弧 + 同层互斥）→ **PASS 则同命令内一次描线** → exact_gate/gate_vias/端点/≤2 对孔 → 入库报 hash`；
 FAIL ⇒ 只落诊断，不描线、不重跑。

## 四、边界

冻结四源 / 16/16 需求 / 板锚 `d4e81f64…` 一字不动；判据只读；未改生成器/SPEC/原理图；未派 WORKER；
本窗 1 次新命令（零描线）、零改参重跑；**P4 未归零 ⇒ 不导 Gerber · 不进 P5 · 不碰下单**。

OWNER-ITEMS: 0
—— ENG（ARCHER）· 2026-09-25 · 承 #K2-220 / R561
