dataxcash/hw_ic_k2/docs/K2-R561-JOINT-V2-ONESHOT-RESULT.md

# K2 · R561 —— 联合 v2（入口重推 + 转移）**前置核验 FAIL · 诊断（未描线、未重跑）**

- 件：`K2_R561_JOINT_V2_ONE_SHOT_v1.{py,json}`（新命令 · 联合核验；因前置 FAIL **未执行描线**）· 日志 `/tmp/opencode/r561/oneshot.log`

## 一、机核读数（FAIL）

| 判据 | 读数 | 归因（机核） |
|---|---|---|
| `(i)` 声明格合法 | FAIL | **row 60 起，南场在 cols 2–5 等列被占** ⇒ 南场可用深度 **≈≤59** ⇒ 腰带行 `R` 必须收在 **≤59** |
| 同层两两互斥 | FAIL（每对 4 格） | 入口东行（rows 50–59）与后线**上升梯**相交：`(42,58)/(42,59)`、`(43,37)…` ⇒ **入口"叠套律"在 11 线/层、行带上限 59 下不可行** |

## 二、根因（一句话）

入口扇出的**叠套律**要求 `R_i > s_{i+1}`（后线梯顶之上）⇒ 11 线须占 **≥ 2×11 行** 的带宽；
而南场可用深度只到 **≈59**、断面行又必须在 belt（≥38）⇒ **11 线/层的行容量不足**（不是板不够，是**每层排的线太多**）。

## 三、修法（L2 · 自裁范围内 · 一次定死）

**重发 COMB 层安排（L2 叠层分配 · #K2-220 已确认属方案层职权）**：每层线数降到 **≤8**（如 **L0=8 / L1=8**）
⇒ 叠套所需行带 = `2n+2 ≤ 18` 行，与"断面行 38–48 + 腰带行 ≤59"完全相容 ⇒ v2 前提**可机核通过**。
（同一命令内：重发层安排 → 联合表 → 核验 → PASS 则一次描线 → 在册闸；FAIL 则只落诊断。）

## 四、边界

冻结四源 / 16/16 需求 / 板锚 `d4e81f64…` 一字不动；判据只读；未改生成器/SPEC/原理图；未派 WORKER；
本窗 **1 次新命令（零描线）**、**零改参重跑**；**P4 未归零 ⇒ 不导 Gerber · 不进 P5 · 不碰下单**。

OWNER-ITEMS: 0
—— ENG（ARCHER）· 2026-09-25 · 承 #K2-220
