dataxcash/hw_ic_k2/docs/K2-R560-PREGATE-v2-RESULT.md

# K2 · R560 —— 前提 v2 前置核验（§三.3(b)）结果：**FAIL（机核·精确）**

- 件：`K2_R560_PREMISE_V2_PREGATE_v1.{py,json}`（**新命令 · 只核不描线**）· 日志 `/tmp/opencode/r560/pregate.log`
- 本窗：**0 构造运行 · 0 改参重跑**（本条命令首次执行；按纪律不重跑）

## 机核读数
- `(i)` 声明格合法：**FAIL** —— 非法格集中在 **rows 61–64 / cols 42–43**（南场在该列区**没有到 64 的深度**）⇒ **腰带行 R 必须收在 ≤60**（板高虽到 64，但该列区被占）。
- `(ii)` 相邻声明格是否在册弧：待 (i) 修正后复核。
- 同层两两互斥：**FAIL** —— 冲突格如 `(42,37)/(42,38)`：**新的转移腿撞上了"旧入口表"的上升梯格**（旧表梯列 cols 34–44、rows 31–53）。
  ⇒ 结论：**前提 v2 生效时，入口表也必须一并重推**（不能复用 R550 的旧入口表）；新入口 = 下钻列 d↑ → 腰带行 `R_i ≤60`↓ → 上升梯列 = 新断面列 `c_i ∈ [42,52]`↑（**无旧梯列残留**）。

## 下一步（唯一一次实现 · 一次命令内完成）
`入口 v2 重推（R≤60） → 与 v2 转移表联合核验（同核验器） → PASS 则同命令内一次描线 → exact_gate/gate_vias/端点/≤2 对孔 → 入库报 hash`；
若仍 FAIL ⇒ 只报表 + 诊断，**不描线、不重跑**。

OWNER-ITEMS: 0
—— ENG（ARCHER）· 2026-09-25 · 承 #K2-220
