dataxcash/hw_ic_k2/pm_gate/artifacts/k2_v4/L1/measurements_raw.txt

# k2_v4.kicad_pcb 测量基线 (只读解析, 80 个器件)
# 格式: ref fp_name at_x at_y rot pads=数

C17 MLCC_0201 at=(75.83,66.05) rot=0 pads=2
C18 MLCC_0201 at=(77.03,66.05) rot=0 pads=2
C19 MLCC_0201 at=(75.83,60.05) rot=0 pads=2
C20 MLCC_0201 at=(77.03,60.05) rot=0 pads=2
C21 MLCC_0201 at=(78.22,60.05) rot=0 pads=2
C22 MLCC_0201 at=(79.42,60.05) rot=0 pads=2
C23 MLCC_0201 at=(80.62,60.05) rot=0 pads=2
C24 MLCC_0201 at=(81.83,60.05) rot=0 pads=2
C25 MLCC_0201 at=(83.03,60.05) rot=0 pads=2
C26 MLCC_0201 at=(84.22,60.05) rot=0 pads=2
C27 MLCC_0201 at=(85.83,59.25) rot=0 pads=2
C28 MLCC_0201 at=(86.62,59.65) rot=0 pads=2
C29 MLCC_0201 at=(87.42,60.45) rot=0 pads=2
C30 MLCC_0201 at=(88.22,60.85) rot=0 pads=2
C31 MLCC_0201 at=(89.03,61.65) rot=0 pads=2
C32 MLCC_0201 at=(89.83,62.05) rot=0 pads=2
C49 MLCC_0201 at=(127.83,53.10) rot=0 pads=2
C50 MLCC_0201 at=(125.83,53.40) rot=0 pads=2
C51 MLCC_0201 at=(121.83,51.90) rot=0 pads=2
C52 MLCC_0201 at=(123.83,52.50) rot=0 pads=2
C53 MLCC_0201 at=(119.83,49.50) rot=0 pads=2
C54 MLCC_0201 at=(117.83,49.80) rot=0 pads=2
C55 MLCC_0201 at=(113.83,48.30) rot=0 pads=2
C56 MLCC_0201 at=(115.83,48.90) rot=0 pads=2
C57 MLCC_0201 at=(111.83,47.70) rot=0 pads=2
C58 MLCC_0201 at=(109.83,48.00) rot=0 pads=2
C59 MLCC_0201 at=(105.83,46.50) rot=0 pads=2
C60 MLCC_0201 at=(107.83,47.10) rot=0 pads=2
C61 MLCC_0201 at=(103.83,44.10) rot=0 pads=2
C62 MLCC_0201 at=(101.83,44.40) rot=0 pads=2
C63 MLCC_0201 at=(98.83,42.90) rot=0 pads=2
C64 MLCC_0201 at=(99.83,43.50) rot=0 pads=2
C65 MLCC_0201 at=(88.83,60.05) rot=0 pads=2
C66 MLCC_0201 at=(89.62,61.25) rot=0 pads=2
C67 MLCC_0603 at=(91.00,49.00) rot=0 pads=2
C68 MLCC_0603 at=(91.00,52.00) rot=0 pads=2
C69 MLCC_0201 at=(93.62,50.20) rot=0 pads=2
C70 MLCC_0201 at=(97.83,46.50) rot=0 pads=2
C71 MLCC_0201 at=(88.83,66.05) rot=0 pads=2
C72 MLCC_0603 at=(91.00,55.00) rot=0 pads=2
C73 MLCC_0603 at=(31.00,55.00) rot=0 pads=2
D1 LED_0603 at=(48.50,66.50) rot=0 pads=2
E2 FRU_EEPROM_SOIC8 at=(44.00,60.00) rot=0 pads=8
J11 PinHeader_1x04 at=(26.50,69.50) rot=90 pads=4
J12 PinHeader_1x02 at=(26.50,37.00) rot=90 pads=2
J13 PinHeader_1x04 at=(26.50,52.00) rot=90 pads=4
J2 CONN_J2 at=(133.82,53.70) rot=0 pads=74 pad_x∈[132.65,135.00] pad_y∈[42.90,64.50]
J3 MCIO_4X_38P_RA at=(59.50,44.50) rot=180 pads=38 pad_x∈[54.10,64.90] pad_y∈[43.25,45.75]
J4 MCIO_4X_38P_RA at=(59.50,62.70) rot=0 pads=38 pad_x∈[54.10,64.90] pad_y∈[61.45,63.95]
J6 PinHeader_1x02 at=(26.50,44.00) rot=90 pads=2
J9 PinHeader_1x04 at=(26.50,61.00) rot=90 pads=4
R1 RES_0603 at=(50.50,37.00) rot=0 pads=2
R10 RES_0603 at=(53.50,57.00) rot=0 pads=2
R11 RES_0603 at=(53.50,60.00) rot=0 pads=2
R12 RES_0603 at=(53.50,63.00) rot=0 pads=2
R17 RES_0603 at=(50.50,66.00) rot=0 pads=2
R18 RES_0603 at=(50.50,69.00) rot=0 pads=2
R19 RES_0603 at=(53.50,66.00) rot=0 pads=2
R20 RES_0603 at=(53.50,69.00) rot=0 pads=2
R21 RES_0603 at=(45.50,66.50) rot=0 pads=2
R22 RES_0603 at=(50.50,45.00) rot=0 pads=2
R23 RES_0603 at=(53.50,45.00) rot=0 pads=2
R24 RES_0603 at=(50.50,48.00) rot=0 pads=2
R25 RES_0603 at=(53.50,48.00) rot=0 pads=2
R26 RES_0603 at=(50.50,51.00) rot=0 pads=2
R27 RES_0603 at=(53.50,51.00) rot=0 pads=2
R28 RES_0603 at=(50.50,41.00) rot=0 pads=2
R29 RES_0603 at=(53.50,41.00) rot=0 pads=2
R3 RES_0603 at=(53.50,37.00) rot=0 pads=2
R4 RES_0603 at=(50.50,54.00) rot=0 pads=2
R5 RES_0603 at=(50.50,57.00) rot=0 pads=2
R6 RES_0603 at=(50.50,60.00) rot=0 pads=2
R7 RES_0603 at=(50.50,63.00) rot=0 pads=2
R9 RES_0603 at=(53.50,54.00) rot=0 pads=2
U1 MCU_STM32G0_LQFP48 at=(36.00,52.00) rot=0 pads=48
U2 DCDC_12V_3V3_SOIC8 at=(33.00,37.00) rot=0 pads=8
U3 DS160PR810_WQFN64 at=(93.83,44.70) rot=0 pads=65 pad_x∈[88.83,98.83] pad_y∈[40.10,49.30]
U4 DS160PR810_WQFN64 at=(93.83,62.70) rot=180 pads=65 pad_x∈[88.83,98.83] pad_y∈[58.10,67.30]
U5 OPTO_LTV356T_SSOP4 at=(44.50,52.00) rot=0 pads=4
U6 BAT54C_SOT23 at=(40.00,37.00) rot=0 pads=3

# ── 高速链路走廊 (x 向) ──
J2: 焊盘盒 x∈[132.65,135.00] y∈[42.90,64.50] (中心 133.82,53.70)
J3: 焊盘盒 x∈[54.10,64.90] y∈[43.25,45.75] (中心 59.50,44.50)
J4: 焊盘盒 x∈[54.10,64.90] y∈[61.45,63.95] (中心 59.50,62.70)
U3: 焊盘盒 x∈[88.83,98.83] y∈[40.10,49.30] (中心 93.83,44.70)
U4: 焊盘盒 x∈[88.83,98.83] y∈[58.10,67.30] (中心 93.83,62.70)

# AC 电容墙: MCIO侧 19 个, J2侧 18 个
MCIO侧: x∈[75.83,89.83] y∈[59.25,66.05] 数量=19
J2侧: x∈[93.62,127.83] y∈[42.9,53.4] 数量=18
