dataxcash/hw_ic_k2/pm_gate/artifacts/k2_v4/L1/measurements_raw_v2.txt

# k2_v4.kicad_pcb 权威坐标事实源 v2 (只读解析, rot 正确处理)
# 器件总数: 80 | 文件: k2_v4.kicad_pcb
# 生成: tools_measure_l1.py (KiCad 标准旋转公式)

## 器件清单
- C17 MLCC_0201 at=(75.83,66.05) rot=0 pads=2
- C18 MLCC_0201 at=(77.03,66.05) rot=0 pads=2
- C19 MLCC_0201 at=(75.83,60.05) rot=0 pads=2
- C20 MLCC_0201 at=(77.03,60.05) rot=0 pads=2
- C21 MLCC_0201 at=(78.22,60.05) rot=0 pads=2
- C22 MLCC_0201 at=(79.42,60.05) rot=0 pads=2
- C23 MLCC_0201 at=(80.62,60.05) rot=0 pads=2
- C24 MLCC_0201 at=(81.83,60.05) rot=0 pads=2
- C25 MLCC_0201 at=(83.03,60.05) rot=0 pads=2
- C26 MLCC_0201 at=(84.22,60.05) rot=0 pads=2
- C27 MLCC_0201 at=(85.83,59.25) rot=0 pads=2
- C28 MLCC_0201 at=(86.62,59.65) rot=0 pads=2
- C29 MLCC_0201 at=(87.42,60.45) rot=0 pads=2
- C30 MLCC_0201 at=(84.00,60.85) rot=0 pads=2
- C31 MLCC_0201 at=(86.00,61.65) rot=0 pads=2
- C32 MLCC_0201 at=(89.83,62.05) rot=0 pads=2
- C49 MLCC_0201 at=(127.83,53.10) rot=0 pads=2
- C50 MLCC_0201 at=(125.83,53.40) rot=0 pads=2
- C51 MLCC_0201 at=(121.83,51.90) rot=0 pads=2
- C52 MLCC_0201 at=(123.83,52.50) rot=0 pads=2
- C53 MLCC_0201 at=(119.83,49.50) rot=0 pads=2
- C54 MLCC_0201 at=(117.83,49.80) rot=0 pads=2
- C55 MLCC_0201 at=(113.83,48.30) rot=0 pads=2
- C56 MLCC_0201 at=(115.83,48.90) rot=0 pads=2
- C57 MLCC_0201 at=(111.83,47.70) rot=0 pads=2
- C58 MLCC_0201 at=(109.83,48.00) rot=0 pads=2
- C59 MLCC_0201 at=(105.83,46.50) rot=0 pads=2
- C60 MLCC_0201 at=(107.83,47.10) rot=0 pads=2
- C61 MLCC_0201 at=(103.83,44.10) rot=0 pads=2
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
  pin52   (135.000,57.900) sz=1.30x0.35 net=PCIE_DN5_N
  pin54   (135.000,58.500) sz=1.30x0.35 net=PCIE_DN4_P
  pin58   (135.000,59.700) sz=1.30x0.35 net=PCIE_DN3_N
  pin60   (135.000,60.300) sz=1.30x0.35 net=PCIE_DN2_P
  pin66   (135.000,62.100) sz=1.30x0.35 net=PCIE_REFCLK1_P
  pin70   (135.000,63.300) sz=1.30x0.35 net=PCIE_DN1_N
  pin72   (135.000,63.900) sz=1.30x0.35 net=PCIE_DN0_P

### J3 (MCIO_4X_38P_RA) at=(59.50,44.50) rot=180 pads=38
  pinB18  (54.700,43.250) sz=0.30x0.70 net=PCIE_DN_OUT3_N_MCIO
  pinA18  (54.700,45.750) sz=0.30x0.70 net=PCIE_UP3_N
  pinB17  (55.300,43.250) sz=0.30x0.70 net=PCIE_DN_OUT3_P_MCIO
  pinA17  (55.300,45.750) sz=0.30x0.70 net=PCIE_UP3_P
  pinB15  (56.500,43.250) sz=0.30x0.70 net=PCIE_DN_OUT2_N_MCIO
  pinA15  (56.500,45.750) sz=0.30x0.70 net=PCIE_UP2_N
  pinB14  (57.100,43.250) sz=0.30x0.70 net=PCIE_DN_OUT2_P_MCIO
  pinA14  (57.100,45.750) sz=0.30x0.70 net=PCIE_UP2_P
  pinA12  (58.300,45.750) sz=0.30x0.70 net=PCIE_REFCLK0_N
  pinA11  (58.900,45.750) sz=0.30x0.70 net=PCIE_REFCLK0_P
  pinB6   (61.900,43.250) sz=0.30x0.70 net=PCIE_DN_OUT1_N_MCIO
  pinA6   (61.900,45.750) sz=0.30x0.70 net=PCIE_UP1_N
  pinB5   (62.500,43.250) sz=0.30x0.70 net=PCIE_DN_OUT1_P_MCIO
  pinA5   (62.500,45.750) sz=0.30x0.70 net=PCIE_UP1_P
  pinB3   (63.700,43.250) sz=0.30x0.70 net=PCIE_DN_OUT0_N_MCIO
  pinA3   (63.700,45.750) sz=0.30x0.70 net=PCIE_UP0_N
  pinB2   (64.300,43.250) sz=0.30x0.70 net=PCIE_DN_OUT0_P_MCIO
  pinA2   (64.300,45.750) sz=0.30x0.70 net=PCIE_UP0_P

### J4 (MCIO_4X_38P_RA) at=(59.50,62.70) rot=0 pads=38
  pinA2   (54.700,61.450) sz=0.30x0.70 net=PCIE_UP4_P
  pinB2   (54.700,63.950) sz=0.30x0.70 net=PCIE_DN_OUT4_P_MCIO
  pinA3   (55.300,61.450) sz=0.30x0.70 net=PCIE_UP4_N
  pinB3   (55.300,63.950) sz=0.30x0.70 net=PCIE_DN_OUT4_N_MCIO
  pinA5   (56.500,61.450) sz=0.30x0.70 net=PCIE_UP5_P
  pinB5   (56.500,63.950) sz=0.30x0.70 net=PCIE_DN_OUT5_P_MCIO
  pinA6   (57.100,61.450) sz=0.30x0.70 net=PCIE_UP5_N
  pinB6   (57.100,63.950) sz=0.30x0.70 net=PCIE_DN_OUT5_N_MCIO
  pinA11  (60.100,61.450) sz=0.30x0.70 net=PCIE_REFCLK1_P
  pinA12  (60.700,61.450) sz=0.30x0.70 net=PCIE_REFCLK1_N
  pinA14  (61.900,61.450) sz=0.30x0.70 net=PCIE_UP6_P
  pinB14  (61.900,63.950) sz=0.30x0.70 net=PCIE_DN_OUT6_P_MCIO
  pinA15  (62.500,61.450) sz=0.30x0.70 net=PCIE_UP6_N
  pinB15  (62.500,63.950) sz=0.30x0.70 net=PCIE_DN_OUT6_N_MCIO
  pinA17  (63.700,61.450) sz=0.30x0.70 net=PCIE_UP7_P
  pinB17  (63.700,63.950) sz=0.30x0.70 net=PCIE_DN_OUT7_P_MCIO
  pinA18  (64.300,61.450) sz=0.30x0.70 net=PCIE_UP7_N
  pinB18  (64.300,63.950) sz=0.30x0.70 net=PCIE_DN_OUT7_N_MCIO

### U3 (DS160PR810_WQFN64) at=(93.83,44.70) rot=0 pads=65
  pin23   (88.825,40.500) sz=0.45x0.25 net=PCIE_UP7_N
  pin22   (88.825,40.900) sz=0.45x0.25 net=PCIE_UP7_P
  pin20   (88.825,41.700) sz=0.45x0.25 net=PCIE_UP6_N
  pin19   (88.825,42.100) sz=0.45x0.25 net=PCIE_UP6_P
  pin17   (88.825,42.900) sz=0.45x0.25 net=PCIE_UP5_N
  pin16   (88.825,43.300) sz=0.45x0.25 net=PCIE_UP5_P
  pin14   (88.825,44.100) sz=0.45x0.25 net=PCIE_UP4_N
  pin13   (88.825,44.500) sz=0.45x0.25 net=PCIE_UP4_P
  pin11   (88.825,45.300) sz=0.45x0.25 net=PCIE_UP3_N
  pin10   (88.825,45.700) sz=0.45x0.25 net=PCIE_UP3_P
  pin8    (88.825,46.500) sz=0.45x0.25 net=PCIE_UP2_N
  pin7    (88.825,46.900) sz=0.45x0.25 net=PCIE_UP2_P
  pin5    (88.825,47.700) sz=0.45x0.25 net=PCIE_UP1_N
  pin4    (88.825,48.100) sz=0.45x0.25 net=PCIE_UP1_P
  pin2    (88.825,48.900) sz=0.45x0.25 net=PCIE_UP0_N
  pin1    (88.825,49.300) sz=0.45x0.25 net=PCIE_UP0_P
  pin33   (98.825,40.100) sz=0.45x0.25 net=PCIE_UP_OUT7_N_U3
  pin34   (98.825,40.500) sz=0.45x0.25 net=PCIE_UP_OUT7_P_U3
  pin36   (98.825,41.300) sz=0.45x0.25 net=PCIE_UP_OUT6_N_U3
  pin37   (98.825,41.700) sz=0.45x0.25 net=PCIE_UP_OUT6_P_U3
  pin39   (98.825,42.500) sz=0.45x0.25 net=PCIE_UP_OUT5_N_U3
  pin40   (98.825,42.900) sz=0.45x0.25 net=PCIE_UP_OUT5_P_U3
  pin42   (98.825,43.700) sz=0.45x0.25 net=PCIE_UP_OUT4_N_U3
  pin43   (98.825,44.100) sz=0.45x0.25 net=PCIE_UP_OUT4_P_U3
  pin45   (98.825,44.900) sz=0.45x0.25 net=PCIE_UP_OUT3_N_U3
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
  pin17   (98.825,64.500) sz=0.45x0.25 net=PCIE_DN5_N
  pin19   (98.825,65.300) sz=0.45x0.25 net=PCIE_DN6_P
  pin20   (98.825,65.700) sz=0.45x0.25 net=PCIE_DN6_N
  pin22   (98.825,66.500) sz=0.45x0.25 net=PCIE_DN7_P
  pin23   (98.825,66.900) sz=0.45x0.25 net=PCIE_DN7_N
