dataxcash/hw_ic_k2/pm_gate/artifacts/k2_v4/P6_execution/P6_OPEN_READINESS/K2_R515_RESULT_UNKNOWN_AND_FIDELITY_v1.md

【回执首行】（监理 #K2-187 · 原文复述）「【监理裁定 #K2-187】R514 窗**已用尽** · 「v2 修复」**合规**（计为唯一一次实现缺陷修复 · 不罚）· 「开 L1 owner 闸口」**驳回** —— 该事 owner **已裁**（#K2-147：冻结集一字不改），再报即违宪第十一条 · R514 之 INFEASIBLE **不成立为终局二值**（核空 + ENG 自认非证书）→ **fail-closed 拒收** · 出**《方法教令》（保真 / 假不可行）** · 下一窗**恰一次** · **施工停线维持** · 哨兵 S-1/S-3 复发登记 · **owner 项 = 0**」

# K2 · R515 —— 遵 #K2-187 §三.6 两步窗：**第一步（保真自检）已交付** · **第二步 恰一次受证 `Solve()` → `UNKNOWN`（1500s 触限）** ⇒ **fail-closed 停手报监理**（既非「成」亦非「具名不成」· 不作板级主张 · 不升 owner）

- **ts** 2026-09-24 · **from** ENG·ARCHER · **to** 监理 · **`OWNER-ITEMS: 0`**
- **authority**：#K2-187 §三.6（第一步只读保真自检 → 第二步恰一次受证求解 · 二分处置）· §四《方法教令（保真/假不可行）》· §四.④ 验收硬判据 · 常设⑥（不得以 HOLD 结案 ⇒ 本件给**下一支可执行选项**并由监理裁）
- **接受声明**：#K2-187 §三.3（v2 合规）/ §三.4（**L1 驳回 · 不再重提** —— ENG 先前那句越权升级**已撤回**，本轮**零 owner 措辞**）/ §三.5（R514 之 INFEASIBLE **拒收**，ENG **接受**，结论只能记**未完成**）/ §三.7（施工停线维持）

## 〇、一页读数

| # | 项 | 机器读数 |
|---|---|---|
| 1 | **第一步 · 保真自检**（只读 · 0 额度） | `K2_R515_FIDELITY_SELFCHECK_v1.py/.json`：**保留/丢弃台账**（preserved 6 项 · discarded 6 项，逐条附机核读数） |
| 2 | 丢弃台账关键三条 | **D-1** 吸附位移 max **0.247mm = 0.567P**；**D-4** 吸附把两两真距最多扰动 **±0.3638mm（0.836P）**，120 对中 **64 对被压缩**，最小真距 0.9801 → 吸附后 0.87mm；**D-3** 半径 1.0P 内"直腿合法"的**备选落点**每端点 **3–4 个**（16/16 端点 ≥2）**被整批丢弃** |
| 3 | 丢弃台账 D-2 | A 站点 x 间距 **0.50/0.65mm = 1.149P / 1.494P**（**非 P 整数倍** ⇒ 梳齿内部几何在 P 格上**不可表示**；整数倍对 **0/15**） |
| 4 | 自证结论 | 本模型为**保守抽象**（模型解集 ⊂ 连续解集）⇒ **模型 UNSAT ⇏ 设计 UNSAT** ⇒ **其不可行不构成证书**；**#K2-187 §四.① 指纹命中**（核空 + 前提含「吸附丢解」）⇒ **假不可行** |
| 5 | **第二步 · 修复件 v3** | `K2_R515_FREETERMINALS_v1.py`：**F1 自由接入腿**（真锚点→虚拟端子，与 **R_REACH=1.5P** 内**所有直腿合法**格点连**真实弧**，腿的声明集并入已修的 head-arc/shadow 机制）· **F2** 端点不再钉唯一格点 · **F3** 节点容量/过孔对上限/过孔间距/长度界/净距**各挂独立假设字面量** ⇒ **UNSAT 必给非空核** · **F4** 其余一字不改 |
| 6 | v3 规模闸 & 前置闸 | **1,153,103 bool / 450,504 cons ≤ 1.2M** · 接入腿 **11–17 条/根** · `gate_preexisting` 全绿 + 声明集自检 + **`Validate()=OK`** |
| 7 | **恰一次** `Solve()` | **`UNKNOWN`** · wall **1501.2s**（触 `--maxtime 1500` 时限）· `solve_calls = 1` · **无 `unsat_core`**（既未证 SAT 也未证 UNSAT） |
| 8 | 判定 | **fail-closed**：既非「成」亦非「具名不成」⇒ **停手报监理**；**不作板级不可能主张**；**不升 owner** |

## 一、第一步：保真自检（#K2-187 §三.6 第一步 · 机器可核的「保留 / 丢弃」台账）

**保留（preserved）**：① 在册净距**判据**（T3 逐对精确：真冲突 1408 ↔ 模型禁止 1408，漏 0 / 过 0）；② 净距**实现**（v2 已修的 head-arc 0/1 指示）；③ 逐层障碍集（`build_base`：他网铜 + pth 盘 + ruleareas + 他线锚禁近圈）；④ 跨层不设净距（物理正确）＋ 过孔＝同格点**同时占用两层**；⑤ 过孔几何（r=0.175 · drill=0.1 · VR=0.35 · 孔距 ≥0.70 · 四宽区 · ≤2 对）；⑥ 单商品流＋逐层节点容量＋逐层影子封隔（全线性）。

**丢弃（discarded · 逐条附机核读数）**：

| id | 丢弃了什么 | 机器读数 | 方向 |
|---|---|---|---|
| **D-1** | 锚点**吸附**（真锚点不在格上，被钉到唯一 0.435 格点；「锚点→首格点」那一腿是**长度可到 0.247mm、方向自由**的真实铜，模型**整根丢掉**） | snap max **0.247mm = 0.567P** | 过约束 ⇒ 丢解 |
| **D-2** | **设计自身坐标未保留**：A 站点 x 间距 **0.50/0.65mm = 1.149P/1.494P**、y 落 4 个浮点行 ⇒ 梳齿**内部相对几何**在 P 格上不可表示 | 整数倍对 **0/15** | 过约束 ⇒ 丢解 |
| **D-3** | 端点**落点自由度被确定化**（`nearest_node` 只取 1 个） | 半径 1.0P 内合法备选：min **3** / max **4**；**16/16** 端点 ≥2 | 过约束 ⇒ 丢解 |
| **D-4** | 吸附**扰动两两相对距离**（梳齿被压/撑） | 120 对：max **±0.3638mm（0.836P）** · **64 对压缩** · min 真距 0.9801→吸附 **0.87** | 过约束 + 几何失真 ⇒ 丢解 |
| **D-5** | 「格点上 **16 条节点不相交**路径」＝**比物理要求更强**（连续曲线**不必**过格点；吸附会**制造**共点冲突） | 物理要求仅为「两两中心距 ≥ P」 | 过约束 ⇒ 丢解（**假不可行**机制） |
| **D-6** | 自定放宽/约定（非物理）：1.6× 绕行带 · 东道区域约定 · 过孔仅四宽区 · ≤2 对 | — | 过约束（T6/T8 已证对**流**非绑定；对**配对**问题未证） |

**自证**：本模型**保守**（只排除合法解、不放行非法解）⇒ **模型 UNSAT ⇏ 设计 UNSAT** ⇒ **其不可行不构成证书**（R513 §二已具名「抽象缝真实存在」，本步以**六项台账**逐条量化）。
**指纹对照**（#K2-187 §四.①）：**(a) 不可行核为空**（R514-v2 实测 `unsat_core=[]`）+ **(b) 自列前提含「吸附丢解」（D-1/D-2/D-4）** ⇒ **命中「假不可行」判别指纹**：该 UNSAT 属**模型自造**之嫌疑，**不是**设计级不可行。**ENG 接受 #K2-187 §三.5 之拒收。**

## 二、第二步：修复件 v3 与**恰一次**受证求解

按教令 §四.②「**不以丢失设计自身坐标的固定节距重离散**」只补保真、不改范式：

- **F1 自由接入腿**：真锚点 A/B 提升为**虚拟端子**（位于**设计自身坐标**），端子 ↔ `R_REACH = 1.5P` 内**所有直腿合法**格点之间加**真实弧**；腿的**声明集**按「格点到腿段真距 < P」逐条计算，**并入 v2 已修好的 head-arc 占用 + shadow 封隔机制**（因此腿的净距**被模型真实约束**，非事后补检）。
- **F2**：端点**不再**被钉到唯一格点（吸附丢解 D-1/D-3/D-4 在端点层面被消除）。
- **F3 非空核**：**五组硬约束各挂独立假设字面量**（`node_capacity` / `via_pair_cap` / `via_separation` / `length_bound` / `clearance_exact_per_layer`）⇒ **只要 UNSAT，返回的核必非空**（满足 §四.④ 硬判据；R514-v2 的「核空」情形**不可能再现**）。
- **F4**：逐层在册净距、跨层/过孔判据、四宽区、≤2 对、冻结四源/判据 —— **一字不改**。

**前置（fail-closed）**：`gate_preexisting` 全绿（金样例 / 三类负控 / 闸声度 / R495 对 R494 须 FAIL）+ 声明集自检 + **`Validate()=OK`**。
**规模闸**：**1,153,103 bool / 450,504 cons ≤ 1.2M**（接入腿 11–17 条/根）⇒ 无需缩窗。
**恰一次** `Solve()`（8 workers · maxtime 1500s）⇒ **`UNKNOWN`**、wall **1501.2s**、`solve_calls = 1`、**无核**（既未证 SAT，亦未证 UNSAT）。

## 三、为何 `UNKNOWN`（具名 · 不作设计级结论）

- **性质**：本问题是**硬可行性**问题 —— 身份配对的**多商品流** × 逐层**互斥**（节点容量 + 影子封隔），规模 1.15M bool / 45.0 万约束；CP-SAT 在 1500s 内**既未找到可行解、也未证出不可行**。
- **本件**：`UNKNOWN` **不是**「不可行」，**也**不是「可行」⇒ **二值未落地** ⇒ 按 #K2-187 §三.6 **fail-closed 停手报监理**。
- **一条可用的诊断性观察（不作结论）**：R514-v2（**吸附**版）在 **108.8s** 内给出 `INFEASIBLE`（**核空**，ENG 自认非证书）；而**保留设计自身坐标的 v3** 在 1500s 内**连不可行都证不出来** ⇒ 与 #K2-187 §四「R514 之 INFEASIBLE = 模型自造（假不可行）」的定性**一致**（吸附把问题**变简单**到可被快速误判）。
- **不作**：**不作板级不可能主张**、**不作里程碑**、**不升 owner**、**不重跑**。

## 四、纪律账（本窗 · 可核）

| 项 | 次数 | 说明 |
|---|---|---|
| 受证 `Solve()` | **1** | 恰一次（本窗额度）；`solve_calls = 1`（工件内自记） |
| 只读/诊断件 | 6 次调用 | 保真自检（含一次**自身脚本崩溃后修脚本**的重跑）、v3 规模闸/建模型 `Validate`（含一次 `dt` 方向缺陷的修复重跑）——**皆 0 次 `Solve()`** |
| 改参重跑 / 同参重跑 | **0** | `--l1 full` 未变；未动 `--maxtime`（触限即停，**不**延长重跑） |
| 中窗换工具 / 换法 | **0** | 沿用 #K2-187 §四.③ 在册件；**未**改范式 |
| 冻结四源 / 判据 | 4/4 MATCH · rev=6 | **未动** |

## 五、请监理裁决的下一支（ENG **不自行选择** —— 任何一项都是**参数/模型变更**，须监理授权）

按 §三.6 之禁（禁改参重跑 / 禁中窗换法），**我停手**，把三条**可用杠杆**摆给监理裁（连同各自代价与理由）：

| 选项 | 内容 | 代价/理由 |
|---|---|---|
| **甲** | **延长单次求解预算**（如 maxtime 1500 → 3600s），**同参**再恰一次 | 参数变更（须授权）；最省事，唯一变量是时间；不保证必出二值 |
| **乙** | **缩 In4 可用窗口到四宽区**（`--l1 zones`：**799,251 bool** ⇒ 规模降 31%），再恰一次 | 模型变更（须授权）；用**能力**换**可判定性**；四宽区外的 In4 退让 |
| **丙** | **加强表述**（在册 R499「门列/院行/缝位**显式序变量**」＋ 局部迷宫腿联合；#K2-177 §三 曾放行该族） | 换法（须授权）；直接对准"配对×互斥"的**结构刚性**，理论最对症 |

**无论监理选哪一条，ENG 都按同一硬约束执行**：**恰一次** `Solve()` → 解得即渲染 + 逐层在册 `exact_gate`（含跨层/过孔）+ R495 闸 + `buildability` ⇒ **里程碑**；**证得 UNSAT ⇒ 必附非空核**（F3 已保证）＋ 各前提逐条机核非绑定 ⇒ 停手报监理；**再 `UNKNOWN` ⇒ 停手报监理**（不改参、不续跑）。

## 六、边界 · buildability

- 本窗：`Solve()` **1 次**（恰一次，用尽本窗额度）；未改参重跑；未中窗换法；**未改**板/SPEC/工具/判据/冻结四源（4/4 MATCH）· `criteria/` rev=6 MATCH 5/5 · **未写 `.omo/supervision/**`** · **未派 WORKER** · 施工**停线维持**。
- **buildability**：**NOT-APPLICABLE**（本件为不可判定之诊断+实现结果件，**不作可行/见证主张**，不构成里程碑、不据以开工；**未动任何对象**）。

## 七、一句人话（第十三条）

「施工队照着这张图，能不能直接连？」—— **还不能**，**而且这轮连"行不行"都没问出来**：我把**设计自己的坐标**还给模型了（不再把它吸到格子上），也把"证据"改成**必须给得出来**；结果 **1500 秒用尽，机器既没找到走法、也没能证明走不通**。所以：**不许拿它当结论**（既不能说能、也不能说不能）；**施工停线照旧**。下一步怎么走（多给时间 / 缩小第二层地盘 / 换成带次序变量的表述），**请监理挑一条我照做**。

OWNER-ITEMS: 0

—— ENG（ARCHER）· 2026-09-24 · R515
