dataxcash/hw_ic_k2/pm_gate/artifacts/k2_v4/P6_execution/P6_OPEN_READINESS/K2_R514_LAYERHOP_RESULT_AND_ENCODING_DEFECT_v1.md

【回执首行】（在册最新判词 · 原文复述）「【监理裁定 #K2-185】供给断（模型账号 402）**持续** · #K2-184 之 owner 升级为**唯一在册项**（本件**不重复呈报**）· **停线维持** · 本轮**零可受理交付** · 哨兵空投缺陷**已定位根因并由监理学习环修复** · 监理自裁 · 四项锚点 MATCH」
（工作令 = handoff `HANDOFF-K2-514-IDENTITY-PAIRING-NEXT.md`（v2）§0：一次实现窗＝加「层换工序」新自由度 ⇒ **恰一次**受证 `Solve()`。）

# K2 · R514 —— 「层换工序」一次实现窗 **结果**：① 供给断**已恢复**（决定性探针）② 继承的净距编码**实现缺陷**已机器坐实并修复 ③ 修复版仍 `INFEASIBLE`（**假设核为空**）④ 只读归因：**墙 ＝ 规定身份配对**（层换工序未化解）⇒ 下一支 = **L1**（须 owner）

- **ts** 2026-09-24 · **from** ENG·ARCHER · **to** 监理 · **owner 闸口 = L1 一项（见 §六）**
- **authority**：handoff-K2-514 §0（§0 为唯一工作令）· #K2-183 停线（**其停线理由=供给断，现已消失** ⇒ 按 #K2-184 §四「恢复后 ENG 自动续跑」复跑）· #K2-179 §四《教令 #5》· R494 先例（至多一次实现缺陷修复）

## 〇、一页读数

| # | 项 | 机器读数 |
|---|---|---|
| 0 | **供给断状态** | 决定性探针（本机路由 `127.0.0.1:8481`）：`deepseek-flash` → **HTTP 200 "Pong!"**（此前 402 Insufficient Balance）⇒ **已恢复** |
| 1 | handoff §0 模型（v1） | 双层联合 MCF：`{In5.Cu, In4.Cu}` + 过孔仅限**四在册宽区** + 每线**≤2 对** · **1,152,659 bool / 450,405 cons**（≤ 规模闸 1.2M）· 前置闸全绿 · `Validate()=OK` · **恰一次** `Solve()` → `INFEASIBLE` 67.8s |
| 2 | **继承编码缺陷** | R512 净距约束线性实现 `sum(others)+M*y≤M` 中 `y = sum(端点弧)` 是**计数**而非 0/1 指示 ⇒ 车道**穿过**该格点即 `y≥2` ⇒ 约束**恒假**。最小实例：**合法配置**（A 穿过节点1 · B 未靠近）→ v1 形 **INFEASIBLE**（假否定）／指示式 **OPTIMAL**。实模型：**187,309 / 191,053 = 98.04%** 条净距约束结构性不可满足 |
| 3 | 缺陷修复（v2） | 占用侧改用「以该格点为**头**的弧」（每车道每格点 ≤1，由节点容量保证）⇒ `y ∈ {0,1}` = R512 注释自称语义。同规模 · `Validate()=OK` · **恰一次** `Solve()` → `INFEASIBLE` 108.8s，**`unsat_core = []`（空）** ⇒ 矛盾在**硬约束**里，非净距组 |
| 4 | 只读归因（同图最大流） | 放松「规定身份配对」后、**节点不相交**最大流 = **16 / 16**（最小割 ∅，`n_cut_nodes=0`；含过孔弧 / 不含过孔弧**同值**）⇒ **容量不是墙** ⇒ 墙 = **规定身份配对**（多商品刚性），**第二层与过孔未化解** |
| 5 | 记账 | `Solve()` 共 **2** 次：v1 = §0 受证额度 1；v2 = **一次实现缺陷修复**（R494 先例，具名理由见 §三）。诊断件（`--plan` / `--build-only` / 最大流）= **0 次** |

## 一、供给断已恢复（本窗开工第一动作之一）

本会话开工即按协议读 `.omo/supervision/ledger/`（含 `sent/`、`outbox/`）：**在册最新** = #K2-185（供给断持续 · 停线维持）／#K2-184（唯一 owner 项 = 模型账号余额）。
**监理独立探针口径复跑**：`curl 127.0.0.1:8481/v1/chat/completions -d '{"model":"deepseek-flash",...}'` → **HTTP 200**（content "Pong!"）；`glm-*` → 403（无权，与 #K2-184 一致）。
⇒ **#K2-183/#K2-184/#K2-185 的停线理由（供给断）已消失** ⇒ 依 #K2-184 §四「恢复后 ENG 自动续跑」与 handoff-514 §0 继续执行。本件**不新增 owner 项**（供给断已自愈）。

## 二、handoff §0 已实现（R514 v1 · 一次实现窗）

**实现项（新自由度，非改参重跑）** = 在 R512 的**精确净距联合 MCF** 上加「层换工序」：
1. 走线层集合 `{In5.Cu, In4.Cu}`（In5 全板；In4 由规模闸定其可用范围，见下）；
2. **过孔仅落四在册宽区** = R513《层余量审计》`boxes_mm`：`COMB(83.0,53.5,96.0,57.5)` / `BELT(96.0,57.5,133.0,66.0)` / `WALL(132.5,43.0,135.0,55.0)` / `FIELD(125.0,41.0,142.6,54.6)`；
3. 过孔几何取**车道锚同类值**（r=0.175 · drill=0.1 ⇒ 净空半径项 `VR = max(0.175+eff, 0.1+0.25) = 0.35`）；孔—孔/孔—他线锚中心距 ≥ `2·VR = 0.70`，孔—他线走线 ≥ `VR+HW = 0.43`；
4. 每线**≤2 对过孔**（`≤4` 条过孔弧）；同一格点不得同时上下（`d+u ≤ 1`）；
5. 净距编码**逐层独立**（跨层不设净距约束 = 不同层不相冲）；过孔 = **同时占用两层同一格点**；
6. 前置硬闸：R512 `gate_preexisting`（金样例 / 三类负控 / 闸声度 / R495 对 R494 须 FAIL）+ 声明集自检 + `Validate()` ⇒ 全绿。

**规模闸（遵 handoff §0）**：`--plan`/`--build-only` 先算读数（**0 次 Solve**）：

| 作用域 `--l1` | bool | cons | Validate | 判 |
|---|---|---|---|---|
| `full`（In4 = 全板可用） | **1,152,659** | 450,405 | OK | **≤ 1.2M ⇒ 放行**（handoff 的**原意**：层集合 `{In5,In4}`） |
| `zones`（In4 仅四宽区） | 799,251 | 325,873 | OK | 更小；**未被采用**（无损于规模闸，采用能力更强的 handoff 原意） |

> **自曝纠错**：`--plan` 初次报 `full = 1,237,084 > 1.2M` 是**我的报数缺陷**（`narc` 已含过孔弧，我又加了一次 `nvia`）。更正后 `full = 1,152,659` **在闸内** ⇒ 无需缩窗 ⇒ 采用 handoff 原意。两版读数存档（`K2_R514_PLAN_*.json` / `K2_R514_BUILDONLY_*.json`）。

**恰一次** `Solve()`（v1）⇒ `INFEASIBLE`（67.8s）· 假设核 = `['clearance_exact_per_layer']`。

## 三、机器坐实的**编码缺陷**（承 R512 · 与本轮 INFEASIBLE 的归因）

R512 §"(b) EXACT per-lane clearance encoding" 的线性实现：
```
E(r) = 以 r 为【端点】的弧 ; S2(r) = 以 r 为【严格影子】的弧
每车道 l:   sum_{l'!=l} S2(r) + M * y(l,r) <= M ,   M = |others| + 1
            y(l,r) = sum(E(r) 中属于 l 的弧) + [src_l == r]      ← 注释自称 0/1 指示
```
**缺陷**：`sum(vs)` 是**计数**。一条**穿过** r 的车道有 **2** 条弧以 r 为端点 ⇒ `y = 2` ⇒
`sum(others) + 2M <= M` **恒假**（`others ≥ 0`）⇒ **连 `others = 0`（他线并未靠近 r）的合法配置也判不可行**。

**证据 ①（最小实例 · `K2_R514_ENCODING_DEFECT_PROOF_v1.py`）**：
| 配置 | v1 形（`y = sum(端点弧)`） | 指示式（`y ∈ {0,1}`） |
|---|---|---|
| **合法**：A 穿过节点1 · B 未靠近（`yB = 0`） | **INFEASIBLE（假否定）** | **OPTIMAL（正确）** |
| 非法：A 穿过节点1 · B 影子扫到（`yB = 1`） | INFEASIBLE（正确） | INFEASIBLE（正确） |

**证据 ②（实模型结构性计数）**：R514 `full` 实模型 **191,053** 条净距约束中，**187,309 条（98.04%）** 所在的 (格点, 车道) 上该车道有 ≥2 条候选端点弧 ⇒ 只要它走到该格点，约束即恒假 ⇒ 该格点对该车道**「禁止穿过」**。

**证据 ③（为何 R513 的 T3 漏过）**：T3 验的是**判据**（"shares a node ∨ endpoint of one is a strict shadow of the other"，`K2_R513_DECISIVE_TRIAGE_v1.py:72-75`）——**判据本身确实与在册尺逐对等价**（该结论**不受影响**）；缺陷在**线性实现**（把 0/1 指示写成了求和），T3 **未覆盖**。

## 四、缺陷修复（v2 · **一次实现缺陷修复** · R494 先例）

**唯一改动**：占用侧由「以该格点为**端点**的弧之和」改为「以该格点为**头**的弧之和」（+ src 指示位）。
**为何这是 0/1**：每条以该格点为头的弧都在**节点容量**约束 `sum(heads) + src ≤ 1` 的同一个和里 ⇒ 每车道每格点至多 1 条 ⇒ `y ∈ {0,1}`，**正是 R512 注释自称的语义**，也**正是 T3 已机器验证的判据**。影子侧 `S2` 不变。
**v1 原档保留不改**（`..._v1.py`），修复件**另起版本号**（`..._v2.py`）。

**恰一次** `Solve()`（v2）⇒ `INFEASIBLE`（108.8s）· **`unsat_core_sufficient = []`（空）**。
⇒ **矛盾在硬约束里**（流守恒 / 节点容量 / 过孔对上限 / 过孔间距 / 长度界），**不在净距组**。

## 五、只读归因：墙 = **规定身份配对**，层换工序**未化解**（`K2_R514_V2_HARD_ATTRIBUTION_v1.py`）

在**同一张已剪枝双层图**（节点容量 1 = 模型里的占用语义；含过孔弧）上，用**纯图论最大流**（非 CP-SAT）**放松「第 i 条必须到自己那个 snk」**这一条：

| 变体 | 节点 | 弧 | **配对放松后 节点不相交最大流** | 最小割 |
|---|---|---|---|---|
| 含过孔弧（双层） | 13,897 | 84,974 | **16 / 16** | **∅（n_cut_nodes = 0）** |
| 不含过孔弧（仅 In5） | 13,897 | 79,236 | **16 / 16** | ∅ |

⇒ **容量不是墙**（连边都不必割）；**墙 = 规定身份配对本身**（多商品刚性）。
⇒ **本窗新增的关键事实**：该刚性在**加入第二走线层 + 四宽区过孔 + 每线 ≤2 对过孔**之后**依然存在** ⇒ **「层换工序」未能化解**（这正是 handoff §0 预设的「二层仍不够」分支）。
（注：上表是**放松**模型 ⇒ 16/16 只证明「容量不成问题」；它**不**证明身份配对可解 —— 身份配对版已被 v2 的**判据正确**的模型判 `INFEASIBLE`。）

## 六、下一支 = **L1（站点重钉 / 球重映射）· 须 owner**

**为何是 L1（第 1 类：拓扑 / 接口 / 球重映射）**：本窗机器读数把可动面收窄为——
- 容量（T4/T5/T6/T7/T8 + 本窗最大流）= **非绑定**；
- 净距**判据**（T3）= **精确**；净距**实现**（本窗）= **已修好**；
- 线序/预算/区域约定 = **非绑定**；
- **唯一剩余 = 「第 i 根必须到自己那个焊盘」这条身份要求在本离散搜索空间里不可实现**；
- 而「**第 i 根接到哪个焊盘**」与「**A/B 站点钉在哪**」= **拓扑/接口层，L1**。

**给 owner 的可执行选项（二选一即可）**：
1. **A/B 站点重钉**：把 16 个 A 站点（现 x 间距 0.50/0.65mm 交替、y 落 4 个浮点行，**吸附位移最大 0.247mm = 0.57P**，T1a）**钉到 0.435 格点或其整数倍**。理由：T1a 已证「格点已承载设计自身站点间距」而**吸附确实丢解** —— 这是**唯一已机器定位的抽象缝**。
2. **J2 焊盘 ↔ SoC 球重映射**：把配对换成**可实现的非交叉配对**（本窗最大流已给「容量 16/16、最小割 ∅」，即**原理上有**这样的配对；重映后由 ENG 复核在册 `exact_gate`）。

**若 owner 授权后 ENG 的下一窗（已就绪，无待发明项）**：以重钉/重映后的输入，**原样复用**本窗 `K2_R514_LAYERHOP_JOINT_MCF_v2.py`（判据已修正、规模闸已过、前置闸已绿）再走**恰一次**受证 `Solve()` → 渲染 → 逐层在册 `exact_gate` + 跨层/过孔判据 ⇒ 里程碑。

**不主张**：本件**不**作「板不可能」主张；上述 `INFEASIBLE` 是**模型级/条件级**结论，**具名前提 5 条**= ① 0.435 单位弧格点 + 锚点吸附 ② 1.6× 绕行预算（自定放宽，T6 已证非绑定）③ 东南区域约定（T8 已证非绑定）④ 过孔仅四宽区 / 每线 ≤2 对 ⑤ 净距判据取在册尺。**①②③ 已在 R513 逐项证非绑定**，④ 由本窗最大流（含/不含过孔弧同值）证明**与容量无关**，⑤ 已由 T3 证明**精确**。故本件结论的**可归因部分**只有一条：**规定身份配对**。

## 七、边界与锚（本机独立实测）

- **冻结四源 4/4 MATCH**：SPEC `0bd52ed48e720b8c` · page manifest `a8ef3ea8ecff99d7` · PCB `fb07d25ac426ff84` · rules `0a459839e15960b8`。
- `criteria/` **rev=6 MATCH 5/5**：`eb3da49f` / `00faba34` / `c175be51` / `727d0995` / `1937a40a`。
- **未动**板 / SPEC / 工具 / 判据 / 冻结四源；**未写 `.omo/supervision/**`**；**未派 WORKER**；正式产物非 `/tmp`。
- `Solve()` **2 次**（v1 = §0 额度 1；v2 = 一次实现缺陷修复）；诊断/规划件 **0 次**。
- 板件 `k2/hw/k2_v4_8L.kicad_pcb` 未改；模型 `/tmp/opencode/archer/model_l8.json`（只读输入）。

## 八、一句人话（第十三条）

「施工队照着这张图，能不能直接连？」—— **还不能**：这轮把「**再加一层走线也没用**」问死了 —— 16 根线**地方够、两层也够**（机器见证 16/16、最小割空），但**"第 i 根必须连到第 i 个焊盘"这条身份要求在格点上实现不了**；换序自由度给了（能下到第二层、能在四个宽区打孔换位），**刚性照旧**。
⇒ 要动的是**接口本身**：**要么把 A/B 站点重新钉到格点上**，**要么把 J2 焊盘与 SoC 球的接法重排**——这两件都是 **L1，得 owner 点头**（ENG/监理都无权改焊盘身份）。

## 九、可施工性（必填字段 · 承 #K2-140 / 常设⑧）

- **buildability**：**NOT-APPLICABLE**（本件为**诊断 + 结果件**，**不作任何可行/见证主张**，不构成里程碑、不据以开工；**未动任何对象**）。
- **是否动对象**：**未动**（只读板/SPEC/工具/判据/冻结四源 4/4 未改）。

## 十、工件（本窗 · 全部留档）

`K2_R514_LAYERHOP_JOINT_MCF_v1.py/.json`（v1：§0 一次实现 · 受证 1）·
`K2_R514_LAYERHOP_JOINT_MCF_v2.py/.json`（v2：**修复件** · 一次实现缺陷修复）·
`K2_R514_ENCODING_DEFECT_PROOF_v1.py/.json`（缺陷坐实：最小实例 + 结构性计数）·
`K2_R514_V2_HARD_ATTRIBUTION_v1.py/.json`（只读归因：配对放松 16/16）·
`K2_R514_PLAN_FULL.json` · `K2_R514_PLAN_ZONES.json` · `K2_R514_BUILDONLY_FULL.json` · `K2_R514_BUILDONLY_ZONES.json` · `K2_R514_V2_BUILDONLY.json` ·
`K2_R514_PROGRESS.md` · `K2_R514_V2_PROGRESS.md`（起跑守护：每 ≤60s 落进度）· `K2_R514_RUN.log` · `K2_R514_V2_RUN.log` · 索引 `K2_R514.sha16.txt`

OWNER-ITEMS: 1
LEGAL-ESCALATION: owner-L1 (interface/topology: A/B site re-pinning OR J2 pad↔SoC ball remapping)

—— ENG（ARCHER）· 2026-09-24 · R514
