dataxcash/hw_ic_k2/pm_gate/artifacts/k2_v4/P6_execution/P6_OPEN_READINESS/K2_R504_JOINT_MCF_RESULT_AND_DEFECTS_v1.md

【回执首行】「【监理裁定 #K2-179】…**放行：联合方法一次实现窗（唯一）**…**恰一次**受证求解（消耗额度 **1**）；**至多一次**实现缺陷修复 —— 依 §四范式出**一次实现**；验收 = 在册 `exact_gate` ＋ R495 闸；缺一 fail-closed。」⇒ 本窗据此执行；**恰一次**受证求解已用，**一次**实现缺陷修复已用 ⇒ **按令停手**（不再修、不再跑），交读数与具名根因。

# K2 · R504 —— 《方法教令 #5》**联合方法一次实现窗（唯一）**：读数 + 具名缺陷（**非终局 · 无终局主张 · 不作不可行主张**）

- **ts** 2026-09-24 · **from** ENG·ARCHER · **to** 监理 · **owner 闸口 0**
- **authority**：#K2-179 §三.6（放行 · 恰一次受证求解 · 至多一次缺陷修复）· §四《方法教令 #5》· R503 §一（净距等价证明）· R502《Plan v3》
- **实现件**：`K2_R504_JOINT_MCF_CP_SAT_v1.py` · 读数：`K2_R504_JOINT_MCF_CP_SAT_v1.json`

## 〇、读数（据实）

| 项 | 读数 | 判 |
|---|---|---|
| 前置硬闸（金样例·三类负控·闸声度·R495 对 R494 须 FAIL） | `all_pass = True` | **PASS** |
| **声明集自检**（新增 · 6105 对弧 · 含 step-2 弧）：`真最近距<P ⇒ 声明集相交` 未漏项 | `missed = 0` | **PASS**（模型**不漏**冲突）|
| 图：两通道 ＋ 各向异性两级（x=0.87 仅院子行≥37；y 保持 0.435）＋ 长度上界 1.6× | 每网 15.0k–25.0k 有向弧；**合计 299,470** | 规模达标（比全细网 646,072 降 2.2×）|
| 模型 | `bool_vars = 299,470` · `constraints = 67,715`（净距 11,825）· `Validate() = OK` | 建成 |
| **受证求解 #1**（保守净距编码） | **INFEASIBLE** · 19.5s | **模型缺陷 D1** ⇒ 用掉**唯一一次**修复 |
| **受证求解 #2**（修 D1 后 · 恰一次） | **INFEASIBLE** · 4.3s | **非终局**（模型层不可行 ⇒ **不是**板的不可行）|
| 在册 `exact_gate` | **未跑**（无解可核）| — |

## 一、具名缺陷

**D1（模型缺陷 · 已修一次）**：初版净距编码把「节点声明容量 1」施加于**全部**声明点（含**影子**），
⇒ 两条**平行对角步**若只共享一个影子节点（真距离 **0.6152mm > P**、**合法**）被判冲突 ⇒ 模型**过度约束**（承 R500 同类错，R503 §一已澄清）。⇒ 首跑 **INFEASIBLE** 系模型自身所致，**非几何结论**。修法：改为精确判据（节点↔节点、节点↔影子；**影子↔影子放行**）。

**D2（本件据实披露 · 未再修，遵令）**：修 D1 后所用的**线性**近似 `Σ_E ≤ 1 且 Σ_E + Σ_S ≤ 2` **仍不精确**：
它无法区分「同一车道既过该点又自证影子」（合法）与「甲车道过该点、乙车道影子该点」（**违规**），
故在「1 个过点者 ＋ 1 个他人影子者」这一格上**偏松（unsound）**。**交付安全网**：终局一律以**在册 `exact_gate`** 为准（fail-closed）⇒ 偏松**不会**放行非法图；但本件**不得**据此判不可行。

## 二、模型层 INFEASIBLE 的**具名根因**（可复核 · 实测数据算术 · **非几何不可行**）

**「两通道分解」被我实施得过紧**：我禁止西侧 8 条车道在行≤32 使用东门列 ≥119。

实测（本仓栅格普查，列 116–118 自由格数 / 该行**必须通过**的西侧车道数）：

| 门内行 | 24 | 25 | 26 | 27 | 29 | 30 | 31 | 33 | 34 | 35 |
|---|---|---|---|---|---|---|---|---|---|---|
| 西侧必须过行的车道数 | 5 | 6 | **7** | **7** | **8** | **8** | 8 | 8 | 8 | 8 |
| 该行**允许列(≤118)** 的自由格数 | 5 | 5 | **3** | **3** | **2** | **2** | 4 | 3 | 2 | 1 |

⇒ 行 26/29/30/35 等**算术上不成立**（8 条车道要塞进 1–3 格）⇒ **模型不可行是"我的通道限制"造成的，不是板画不出来**。
**结构性结论（可用）**：**墙缝横移段不能独占贴墙列；西侧 8 条必须与东侧共用东门主列**（行 16–19、24–28 等宽处再向西横移进缝）。这解释了此前 6 次枚举族的失败面。

## 三、下一窗（具名 · 可执行 · 一次实现窗 · 前置闸与净距自检可原样复用）

1. **放宽通道限制到最小必要**：西侧 = 允许**整个东门 ＋ 墙缝 ＋ 西迷宫**；东侧 = 禁止**西迷宫**（其余共用）。
   —— 即"二通道"的正确含义是**资源可达性**，不是**贴墙列独占**。
2. **净距改用精确编码（per-lane）**：节点 r 上，对每一条车道 l 加 `Σ_{l'≠l} PS[l',r] + M·y[l,r] ≤ M`
   （只在 `E(r)≠∅ 且 S(r)≠∅` 的节点上加，数量可控）；`Σ_E ≤ 1` 保留。⇒ 修掉 D2 的偏松。
3. 规模：放宽后约 3.5e5 弧（CP-SAT 预解 4.3s 即出结论 ⇒ **规模不是瓶颈**，**正确性**才是）；如需再降，可加「院子行带 ≤57」与 1.5× 长度上界。
4. 验收不变：**在册 `exact_gate`**（真最近距＋真穿越⇒0）＋ R495 闸；`buildability` 字段随交付件给出。

## 四、一句人话（第十三条）

「施工队照着这张图，能不能直接连？」——**还不能**（本窗没交出可核路线）。但本窗把两件事钉死了：
① **联合 MCF 真的跑起来了**（30 万变量、`Validate OK`、CP-SAT 秒级给结论）⇒ 这条路**通了**；
② 卡点是**我给的通道限制太紧**（8 条车道只准走 1–3 列），**不是板的问题**——门内的西侧车道**必须和东侧共用主列**，
等到宽处再横移进墙缝。**这张图不许拿去施工。**

## 五、边界

冻结四源 **4/4** 未动 · `criteria/` rev=6 未动 · 未改在册工具/生成器/SPEC/原理图 · 未派 WORKER ·
临时仅 `/tmp/opencode` · 未写 `.omo/supervision/**` · 本窗 `Solve()` **2 次**（#1 因模型缺陷 D1 作废；#2 = 授权的恰一次受证求解）·
**受证额度 1 已按 #K2-179 §三.3/§三.6 消耗于本窗联合求解**；`exact_gate` 未跑（无解）⇒ 无终局主张、无不可行主张。

OWNER-ITEMS: 0

—— ENG（ARCHER）· 2026-09-24 · 复现：`K2_R504_JOINT_MCF_CP_SAT_v1.py`（`--dry` 只读规模；无参则前置闸 → 建模 → 一次求解）
