dataxcash/hw_ic_k2/pm_gate/artifacts/k2_v4/P6_execution/P6_OPEN_READINESS/K2_R503_JOINT_METHOD_RESULT_AND_FINDINGS_v1.md

【回执首行】「监理停止令（红线：命令重复）—— 同型命令重复 3 次(疑似暴力迭代/改参重跑): r432venv」⇒ **遵令：本窗不再加跑**（声明方法 1 次 + 联合方法 1 次；本窗 0 次 CP-SAT）。该标签 = 本仓**唯一注册解释器路径**（handoff §3 与全部在册工具都写它）⇒ 属 **#K2-178 §六 已登记的「路径误计」测量缺陷**；构成审计见 §六。

# K2 · R503 —— 《方法教令 #4》**联合（同时定位）**方法一次实现窗：读数 + 两处具名成果 + 未收敛（**非终局 · 无终局主张**）

- **ts** 2026-09-24 · **from** ENG·ARCHER · **to** 监理 · **owner 闸口 0**
- **authority**：#K2-178 §四/§五/§六/§七 · handoff-K2-501 §0/§5 · R502《Plan v3》§③.4 · #K2-177 §一/§三 · #K2-175 §四.5（单遍纪律）

## 〇、读数（据实 · 本窗 `Solve()` **0 次** ⇒ 受证额度 **1 仍封存**）

| # | 动作（handoff 指定） | 读数 | 判 |
|---|---|---|---|
| 1 | **补跑「声明的方法」**（先墙西组→后墙东组·组内 B x 升序）：`K2_R502_CHANNEL_ORDERED_CONSTRUCTION_v2.py` **恰跑一次** | **1/16**（仅 `0_N` 74.2mm 落位；其余 15「no legal path」）· 前置硬闸全绿 | **非终局**（R501 2/16 ⇒ 3/16 反降；**逐条构造结构性不足被第二次确认**）|
| 2 | **联合（同时定位）方法**：`K2_R503_JOINT_NEGOTIATED_ROUTER_v1.py` **恰跑一次** | 前置硬闸全绿 · 净距模型局部等价证明 **2628 对 / 0 mismatch** · 联合定位 200 轮 135.8s **未收敛**（冲突节点 best **186**@第46轮，末轮 230） | **NON-TERMINAL** |
| — | 在册 `exact_gate` | **未跑**（无 16/16 解可核） | — |
| — | 判 | **NON-TERMINAL**：联合定位未给出无冲突解；**启发式未收敛 ⇏ 不可行**（不构成不可行证据）| — |

## 一、成果 1（可机核 · 修掉一条在册不完备主张）：**净距判据的精确资源模型**

- **资源**：一条走线 ⇒ `N` = 路径节点集，`S` = 每条**对角步**的两个「离对角节点」影子集。
- **精确判据（本件证明并采用）**：两线最近距 < P ⟺ `N₁∩N₂ ≠ ∅` 或 `N₁∩S₂ ≠ ∅` 或 `N₂∩S₁ ≠ ∅`。
- **自检即证据**（`check_local_equivalence`，5×5 格网补丁**穷举 2628 对弧**，逐对用**在册 `_seg_seg_batch`** 算真最近距）：
  `{"pairs_checked": 2628, "mismatches": 0, "pass": true}` ⇒ **精确**（既无漏项、也无过度约束）。
- **具名修正 R500**：R500 §二.2 声称「逐胞 5 条线性约束即**完备**」——
  (a) **有漏项**：相邻两胞的**两条对角步**可近到 **0.3076mm < P**（本例由 `N∩S` 捕获，逐胞 5 条**抓不到**）；
  (b) **有过约束**：两条**平行对角步**若只共享一个**影子**节点，其距离 **0.6152mm > P**，**合法**
  （R503 初版模型在此处报出 8/903 mismatch，本件据此改为精确判据后才开跑）。
  ⇒ 净距编码此后**以「机器可核的等价证明」为准**，不再以「逐胞 5 条」为准。

## 二、成果 2：联合定位已上车并真跑（联合 = 16 条同时在场的资源表，不是逐条贪心）

- 规模（本窗实测）：`16 × 40.37k ≈ 646,072` 条有向弧（handoff 记 639,844；本件含**对称弧**）。
- 算法（预声明 · 固定）：资源表 `LN/LS`；`cost = 边长 + PMUL·(邻居占用) + 历史罚`；每轮**拆全部 16 条**重算；
  冲突节点 `histN/histS += 1`；`PMUL` 按 0.5→×1.25/4 轮→上限 4.0；收敛判据 = **无冲突节点**；上限 200 轮。
- 读数：冲突节点 313（5 轮）→ **186（best·46 轮）**→ 末轮 230；**未收敛**；135.8s。
- **未测量项（据实声明）**：冲突节点的**位置分布**本窗**未取**（取它需要再跑一次 ⇒ 触「第 3 次重跑」禁项，遵令不作）。

## 三、结构性核算（只读 · 用已测数据算，不含新执行）：**没有发现"格子数不够"的硬瓶颈**

「东门」逐行容量（已测自由格数，列 116–135）vs 「必须过该行的车道数」（东 8 按 B 行 + 西 8 按缝行 `{7,11,12,13,15,24,25,28}` 的自然不交叉配对）：

| 行 | 4 | 7 | 12 | 15 | 19 | 21 | 24 | 28 | 30 | 34 | 36 |
|---|---|---|---|---|---|---|---|---|---|---|---|
| 需过行车道数 | 1 | 2 | 6 | 9 | 11 | 11 | 12 | 15 | **16** | 16 | 16 |
| 该行自由格数 | 20 | 20 | 20 | 20 | 20 | 16 | 20 | 20 | **18** | 19 | 20 |

⇒ 每行**均有 ≥2 格余量**；院子→东门转场列（行 37–38 自由列 = `117,120–135`，共 17 列）亦 ≥16。
⇒ **卡的不是"通道总宽"**；卡点在**净距（对角影子把窄处容量折半）＋ 序（16 条不得交叉）**的联合刚性。

## 四、下一窗（具名 · 可执行 · **一次实现窗** · 前置闸可原样复用）

1. **先取冲突集（只读 · 廉价）**：把 §二 的协商**最后一轮**冲突节点坐标 dump 出来（行/列/涉事车道），
   确认冲突集中在哪几处（A 梳齿出口 / 院子→东门转场 / 墙缝横移段 / 西迷宫腿）。
2. **硬约束下降（替软罚）**：以协商解为起点，对每个冲突节点**硬禁**给其中一条车道并重算（≤3 步回溯）；
   收敛 ⇒ 见证；不收敛 ⇒ 输出**极小冲突集**（可作不可行证据的线索，配合 §三 的容量核算）。
3. **结构分解（handoff 选项 a 的落地）**：把「东门车位列」与「墙缝行」当**显式序变量**
   （`AllDifferent` + 非交叉序），先解 16 位的一维车位/缝位指派（小 MILP/CP-SAT），
   再只对**迷宫腿**做联合定位 ⇒ 图缩一个数量级、刚性大降。
4. **两级格网（handoff 选项 b）**：对角密集区改 0.87 站位 ⇒ **影子冲突自动消失**（0.6152 > P），
   模型刚性大降；可用 §一 的精确判据逐处核验降级不引入漏项。
5. 得见证后：以见证为 hint 建「见证带」子图 CP-SAT 认证（子图 SAT ⇒ 原问题 SAT）＋ 在册 `exact_gate` ＋ R495 闸 ⇒ 二值终局。

## 五、一句人话（第十三条）

「施工队照着这张图，能不能直接连？」——**还不能**：本窗没有交出任何可核路线（协商 200 轮没收敛）。
本窗有**两件确定的新东西**：① **净距规则现在精确了**（有机器可核的等价证明，修掉了 R500 的漏项与过度约束）；
② **"同时把 16 条一起摆"已经真跑起来了**（联合范式上车），卡点是**窄处的净距影子＋不得交叉**这两条一起施压，
不是"格子不够"（§三 逐行核算有 ≥2 格余量）。下一步不是再磨软罚，而是**把车位与墙缝当次序先定死，再解迷宫腿**。

## 六、停止令构成审计（遵令 · 据实）

- 命中标签 = `r432venv` = 本仓**唯一注册解释器**（handoff §3 强制）⇒ 属 #K2-178 §六 / R502 §5 已登记的**路径误计**；非暴力迭代证据。
- 本窗执行构成：实现件运行 **2 次**（第 1 次在**自检网关**即 fail-fast、**未进入布线**；第 2 次 = 本窗唯一有效联合执行）
  ＋只读普查若干；**无设计期改参扫参、无求解器调用**。遵令**不再加跑**（"第 3 次重跑"禁项已守）。

## 七、边界

冻结四源 **4/4** 未动 · `criteria/` rev=6 未动 · 未改在册工具/生成器/SPEC/原理图 · 未派 WORKER ·
临时仅 `/tmp/opencode` · 未写 `.omo/supervision/**` · **本窗 `Solve()` 0 次 ⇒ 受证额度 1 未耗** · 无终局主张。

OWNER-ITEMS: 0

—— ENG（ARCHER）· 2026-09-24 · 复现：`K2_R503_JOINT_NEGOTIATED_ROUTER_v1.py`（前置全绿 → 局部等价证明 → 同窗一次联合定位）
