dataxcash/hw_ic_k2/pm_gate/artifacts/k2_v4/P6_execution/P6_OPEN_READINESS/K2_R486_ANCHOR_ZONE_ESCAPE_PROFILE_MEASURED_v1.md

# R486 · 西端（锚区）净区剖面实测 —— 残因①改为"实测"后的结论：**西端逃逸是新的定位卡点**

- **from**: ENG · ARCHER · **to**: 监理 · **性质**: **单次只读探测 + 落件**（未开跑 · 未改生成器/SPEC/判据/冻结四源 · 额度 1 封存）
- **首行复述（回执识别用）**: 监理自动续推：按**已批准的**《K2 整体整改计划》推进**当前阶段**，**阶段门未过不得越阶段**（fail-closed）。红线：冻结件 `d4e81f64…` 永不改；判据 ENG 只读；未获批不得改生成器/SPEC/原理图；禁派 WORKER。

## 一、实测（在册 `Raster`/`build_base` · 单次）

锚区 `x∈[83,97]` 各高度自由 x 段 / 各竖线自由 y 段：

```
{
 "54.9": [
  [
   84.42,
   92.86
  ],
  [
   93.6,
   93.9
  ],
  [
   94.64,
   95.1
  ],
  [
   95.84,
   96.3
  ]
 ],
 "55.1": [
  [
   83.6,
   96.98
  ]
 ],
 "55.7": [
  [
   83.6,
   96.98
  ]
 ],
 "55.9": [
  [
   83.6,
   96.98
  ]
 ],
 "56.2": [
  [
   84.02,
   96.98
  ]
 ],
 "56.6": [
  [
   84.14,
   96.98
  ]
 ],
 "57.5": [
  [
   84.5,
   96.98
  ]
 ],
 "58.5": [
  [
   83.0,
   83.28
  ],
  [
   84.68,
   96.98
  ]
 ],
 "60.0": [
  [
   83.0,
   83.28
  ],
  [
   84.68,
   96.98
  ]
 ],
 "62.0": [
  [
   83.0,
   83.28
  ],
  [
   84.68,
   96.98
  ]
 ],
 "64.0": [
  [
   83.0,
   83.28
  ],
  [
   84.78,
   96.98
  ]
 ],
 "66.0": [
  [
   83.4,
   83.68
  ],
  [
   84.66,
   96.98
  ]
 ],
 "67.0": [
  [
   91.82,
   96.98
  ]
 ]
}
```
```
竖线: {"84.4": [[54.94, 57.38]], "85.0": [[54.58, 66.7]], "85.5": [[54.54, 66.7]], "86.0": [[54.58, 66.7]], "86.5": [[54.54, 66.7]], "87.0": [[54.54, 66.7]], "88.0": [[54.52, 66.7]]}
```

## 二、结论（据实）

1. **西端障碍块**：`x≈83–85.5` 在 `y≈56.5–67` 被封（与 R483/R485 的净距违例一致）⇒ **最西两锚（`84.35` / `84.85`）的竖列不能落在自己锚位**。
2. **逃逸通道极窄**：A 锚 `y` 值高度集中（**7 条 `_N` 同为 `55.823`**，另 `55.723` 1 条；`_P` 为 `54.88`/`55.13`）⇒ 同 `y` 的初始横段**两两不能重叠**（重叠即 0.0000）⇒ 每条线**向东只能挪 ≈0.4mm**（受相邻锚间距限制）。
3. ⇒ **最西的 2–3 条线无法在同高度"挪"到净区** ⇒ 必须改用**先下后东**（在其锚位下方降到走廊内再东行）或**锚区局部改道**——而 `x≈84.4` 竖线在 `y≈57+` 已被封（见上表），故该改道需**沿着锚区自由缝**走（上表已给实测缝位）。
4. 与在册 **C-B2UP-1**（门户×标高×下潜站×连接器层）同源：**锚区逃逸**本就是一独立子问题，须单列处理。

## 三、状态

P3 图纸核 **仍未过**（承 R485：净距 2 · 两两 7）⇒ **不启 P4（fail-closed）**。
本轮 = **单次只读探测**（不改参重跑）；未动红线件；**受证额度 1 封存**；未派 WORKER；产物非 `/tmp`。

## 四、下一步（单发 · 不重跑）

按实测缝位落**锚区逃逸段**（最西数条：锚位→缝内降→走廊），与 R485 的四条残因**一次性**合并落定 → **执行一次**核。
