dataxcash/hw_ic_k2/pm_gate/artifacts/k2_v4/P6_execution/P6_OPEN_READINESS/K2_R349_FORCED_CROSSING_TEST_NEGATIVE_RESULT.md

# K2 · R349 ·（b）证书候选**自证伪** —— 『凸位置+弦交叉 ⇒ 必交叉』不成立（登记 · 免误用）

**件**：`K2_R349_FORCED_CROSSING_TEST_NEGATIVE_RESULT.json`（约定A `58139b685c212685`）

## 测了什么
假设：某 lane 对之 4 端点成**凸位置**且两弦相交 ⇒ Jordan/交错论证 ⇒ 必交叉 ⇒ U≤15（**(b)**）。
计算：120 对中 **107 对凸位置**，其中 **20 对弦相交**（T0_N×T0_P · T0_N×T1_P · T0_P×T1_P · T1_N×T2_P …）。

## 为何**不成立**
该结论仅对**有界/边界受限**之弧成立；本问题弧可**绕行**（上带 y≥56.5 自由 93–98 百分比 = 绕行空间）⇒ 存在反例：4 点凸位置且弦相交，仍可互不相交（(0,0)-(1,0) 与 (0.5,0.1)-(0.5,-1) 之绕行构造）。
⇒ **（b）不成立**；**禁止**据『凸位置+弦交叉』签不可行证书。

## 意义
防以**错误拓扑论证**冒充守恒级证书；并记明『为何 (b) 至今不成立』——区域足够空旷（16/16 单独可路 · 割上界 67≥16）正是绕行可行之条件。

## 边界
纯几何推演 + 只读数据：未烙板 · 未改 `criteria/`/生成器/SPEC/原理图。冻结四源 4/4 未动。

---
—— ENG（ARCHER）· 2026-09-22 · owner 闸口 **0**
