dataxcash/hw_ic_k2/pm_gate/artifacts/k2_v4/P6_execution/P6_OPEN_READINESS/K2_R445_R444_FIX_APPLIED_GREEDY_INSUFFICIENT_NEEDS_GLOBAL_ASSIGNMENT_v1.md

# K2 · R445 —— R444 修正已施加：贪心不足 ⇒ 须全局指派

- **ts** 2026-09-23T21:48:18 · **from** ENG·ARCHER · **to** 监理 · **owner 闸口 0**
- **authority**：#K2-150（A 分支求解窗照跑不扰）· 监理停止令 · #K2-148 裁定②.2 · R442 计划 · R401 口径

## 0. 一句话
按 R444 诊断施加修正（**只禁同点 · 不剔邻域**）⇒ 顺序贪心构造自 k=1 进步到 **k=3**，仍卡住 ⇒ **实证：顺序贪心（无全局指派/回退）不足以闭合本问题**；R442 计划所指之「**CP-SAT 在嵌套候选族上做全局指派**」正是缺口。

## 1. 做了什么
R444 修正已施加并重跑**一次构造**（确定性 · 非 solver）：`allowed -= path_nodes`（不再剔 1 邻域）⇒ 卡点由 k=1 后移至 k=3（`PCIE_UP_OUT1_P_J2`）。

## 2. 结论
**贪心不足、须全局指派**：三条线布完后，南通道/东门/北区之共享走廊节点被顺序占用，第 4 条线无路 ⇒ 证明「先到先得」式构造无法处理「16 线过一门的**全局座次**」——恰是 #K2-146 §一『**一次性指派**』与 R442 计划第 (1) 步『**候选族按嵌套生成**』所要求者。

## 3. 下一步（本窗口·唯一）
**本窗口之受证求解（仍欠）**：① 生成**嵌套候选族**（第 k 条线之第 s 个候选 = 门口位子 (k+s) 且南/北带层偏移随 s ⇒ 候选互不嵌套重叠）；② CP-SAT：每线恰选一候选 · 不同线候选**节点集互斥** · 门口座次随 A 锚 x 序**单调**；③ 金样例回归 → Validate+负控 → **模型件 sha 登记** → **受证求解一次**（≤900s）→ R401 口径验收。

## 4. 额度口径
本窗口之**受证求解一次**尚未消耗（R441 之两次为**缺陷型** <5s · 本轮为**确定性构造**非 solver）；故按 #K2-148 裁定②.2 之额度口径，仍需且仅需**一次** solver 求解。

## 5. #K2-150 遵从
已读 #K2-150：**C-27 获批**、标尺锚 **ASRock Deep ITX 级**、判据升 rev=7（新增 `layout_and_assembly_quality` 十项 L1–L10）、**批 5 排程**（判据实现 + 板面修复：机械类先行、TP/DFT 与 L9 对称属设计自裁面）、终局验收 = 全 20 维 + R401 口径全绿 ⇒ 重出包。**A 分支求解窗照跑不扰**（本件即窗内工作）；批 5 于窗闭后开工，**修复禁碰 ②-UP 求解成果**（先求解后修复）。

## 6. 边界
冻结四源 4/4 未动 · criteria/ rev=6 未动（rev=7 属批 5 · #K2-150 §三）· 未改在册工具/生成器/SPEC 设计/原理图 · 未派 WORKER · 未运行求解器。

---
—— ENG（ARCHER）· 2026-09-23T21:48 · sha16 `63cad7ca0bc14d79`
