dataxcash/hw_ic_k2/pm_gate/artifacts/k2_v4/P6_execution/P6_OPEN_READINESS/K2_R441_STRUCTURED_ENCODING_TWO_DEFECT_FIXES_USED_STOPLINE_v1.md

# K2 · R441 —— 结构化编码：**两次缺陷修复额度用满 · 无受证终局 ⇒ 停线升级**

- **ts** 2026-09-23T20:59:17 · **from** ENG·ARCHER · **to** 监理 · **owner 闸口 0**
- **authority**：**#K2-148 裁定②.2**（缺陷修复 ≤2 · 达 2 无终局 ⇒ 停线升级）· #K2-149 · R401 预登记口径

## 0. 一句话
结构化编码首跑：**金样例过 · Validate 空(OK) · 模型件 sha 登记 `4d971fd18f9d132d`**；但**两次缺陷修复额度已用满**（① E 误取整行 118 槽 → 修正为端口 18 槽；② **候选多样性不足**：逐槽 BFS 最短路互相重叠 ⇒ 节点互斥约束下**平凡 INFEASIBLE @0.0s**）⇒ 仍**无受证终局** ⇒ 按 #K2-148 裁定②.2 **停线升级**。

## 1. 两次尝试（皆缺陷型 <5s）
| # | 状态 | 墙钟 | 缺陷 | 修复 |
|---|---|---|---|---|
| 1 | `INFEASIBLE` | 0.1s | E 定义误取 lattice 整行自由点（118 槽，含端口外 x）⇒ 单调槽序约束失去意义 ⇒ 平凡不可行 | E 限端口自由段 x∈[135.45,143.05] ⇒ **18 槽**（合 R436 登记数）；修复后金样例回归 **过** |
| 2 | `INFEASIBLE` | 0.0s | **候选多样性不足**：逐网 × 逐槽以 **BFS 最短路**生成候选 ⇒ 不同网之候选高度重叠（同一走廊同一条路）⇒ 『跨网节点互斥』约束下**任意两网都无可用互斥候选对** ⇒ 平凡不可行（**非**几何不可行） | **未修**（额度已满） |

## 2. 诊断
**根因在候选生成方式，不在形态**：R435/#K2-148 具名之形态（截面槽位 + nesting 单调）要求候选**按 nesting 逐层错位生成**（第 k 网取第 k 层带内走线），而本次以『逐槽最短路』生成 ⇒ 得的是**同一批重叠路线**而非**嵌套族** ⇒ 模型无解。⇒ 所需修正 = **候选族按 nesting 序生成**（例如：以 A_x 序 k 与槽序 s 联合参数化，令第 k 网之候选沿第 (s+k) 层带偏移），属**候选生成算法之设计**。

## 3. 停线
按 #K2-148 裁定②.2『**达 2 次仍无受证终局 ⇒ 停线升级**』：**ENG 停止**，请监理处置（是否准予 **第 3 次**（将候选生成改为 nesting 族）· 抑或另具名形态）。**ENG 承诺不再运行求解器**直至监理明示。

## 4. 已具备之资产
- 金样例（≤4 网×小域 · 手工答案 [0,1,2,3]）**已过** ✅
- `model.Validate()` **零错** ✅（空串）
- 模型件 sha16 **`4d971fd18f9d132d`** 已登记 ✅
- E=18 端口槽（合 R436）· 逐网候选 18 · 自由格点 7080 · lattice 138×65

## 5. 请监理
- ① 是否准予**第 3 次**尝试，且形态细化 = **候选族按 nesting 逐层错位生成**（其余口径全不变）；② 若不准，请另具名形态/处置；③ 记录：本次 2 次皆为**缺陷型**（<5s）·**非**改参重跑。

## 6. 边界
冻结四源 4/4 未动 · criteria/ rev=6 未动 · 未改在册工具/生成器/SPEC 设计/原理图 · 未派 WORKER · 临时仅 /tmp/opencode。

---
—— ENG（ARCHER）· 2026-09-23T20:59 · 停线升级 · sha16 `a1697a27123969d7`
