dataxcash/hw_ic_k2/pm_gate/artifacts/k2_v4/P6_execution/P6_OPEN_READINESS/K2_R339_R317_CRITERIA_FIX_VERIFICATION_v1.md

# K2 · R339 · **R317 两条判据修正之独立复算** ⇒ **不足以致 19/19**（只读 · `criteria/` 未碰）

**件**：`K2_R339_R317_CRITERIA_FIX_VERIFICATION_v1.json`（约定A `f971b2a350f6aa14`）
**做法**：原样调用判据 rev=6（基线）；再把同一文件**拷到 /tmp** 后仅施加 R317 所述两条修正，重跑。`criteria/` **未修改**。
输入 = R317 同款 5 件测量（`P4_MEASUREMENTS_L8_20260922/`）。

## 读数
| 运行 | n_pass | n_fail | passed | `lib_electrical_level` |
|---|---|---|---|---|
| **基线（rev=6 原样）** | 18 | 1 | False | 电气级差异 **7**（豁免 0） |
| **R317 双修正（/tmp 副本）** | 18 | 1 | False | 电气级差异 **1**（原 7 · 豁免 **6**）· 无号 F.Paste 豁免 **0** |

## 判（决定性）
- **R317 两条修正不足以达 19/19**：电气级差异 7 → 1，仍余 **1** ⇒ **仍 18/19 · passed=False**。
- 规则③（`pad_set`/无号 F.Paste）路径**豁免 0** ⇒ 残余 1 项**非该类**，须另定性。
- ⇒ **若监理按 R317 原案落 rev=7，预期无法使 P4 全绿**（与 R317/R324 §4『落定后预期 19/19』**不符** —— **新证据**）。

## 未定
残余 1 项之 **ref 与差异字段**尚未提取 ⇒ 需一轮带明细之复算（或由监理直接定其处置）。

## 边界
只读复算 · **未改 `criteria/`**（副本在 /tmp）· 未烙板 · 未改生成器/SPEC/原理图 · 未派 WORKER · 未写 `.omo/supervision/**`。冻结四源 4/4 未动。

---
—— ENG（ARCHER）· 2026-09-22 · owner 闸口 **0**
