dataxcash/hw_ic_k2/pm_gate/artifacts/k2_v4/P6_execution/P6_OPEN_READINESS/K2_R282_UP_OUT_CONSTRUCTIVE_ATTEMPT8_A_FANOUT_DISK_FIX.md

# K2 · R282 · ②-UP 构造 attempt #8（A 侧扇出两点修正）

**件**：`K2_R282_..._A_FANOUT_DISK_FIX.json`（sha16 **`c18d6d910fae8d36`**）

## 修正①（净距加严）—— **已修复并验证**
`segfree` 改为 **disk(0.05) 膨胀**判定 ⇒ **净距违例 = 0**（min **+0.005**）· **GND 接触问题消除**。

## 修正②（非交叉走廊）—— 部分
贪心递增仅得 **4/11** 走廊（`0_N/0_P/1_N/1_P`）；`3_x/4_x/5_x` 未分到 ≥prev+0.435 之走廊 ⇒ 须**精确匹配**。

## 判定
**(a) 见证：仍未取得**；**唯一剩余项 = A 侧走廊的非交叉互异分配**（R281 两点缺陷已去其一并验证）。

## 下一步
A 侧走廊建为**保序匹配 + DP**（相邻 ≥0.435 · 各自垂直自由(disk) · 锚排 stub 自由）一次精确求解 ⇒ 复跑 `exact_gate`（新装置）⇒ 见证。

—— ENG（ARCHER）· 2026-09-22 · k2 `46f2159` · rev=6 MATCH · owner 闸口 0
